Datamuseum-DK/R1000.HwDoc/BackgroundImages/FIU/0029/projected_75_light.png

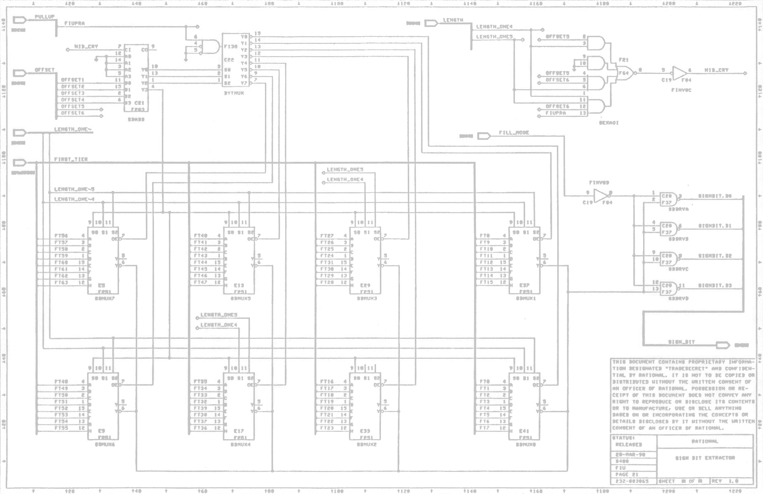
BackgroundImages/FIU/0029/projected_75_light.png
