Datamuseum-DK/R1000.HwDoc/BackgroundImages/FIU/0073/projected_75_light.png

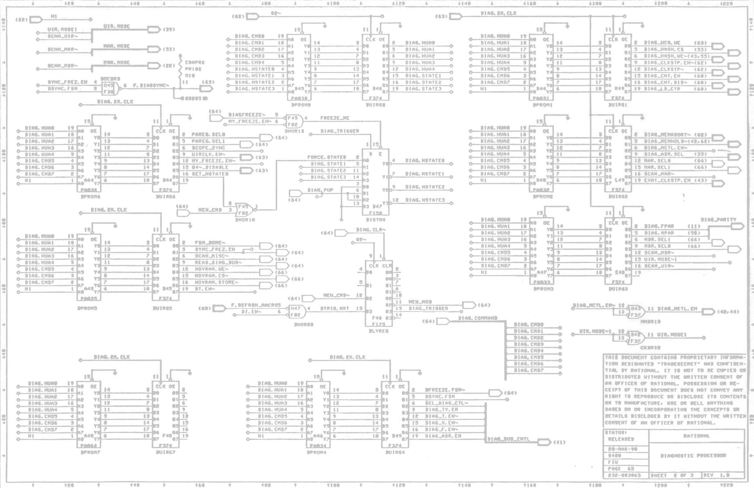
BackgroundImages/FIU/0073/projected_75_light.png
