Datamuseum-DK/R1000.HwDoc/BackgroundImages/IOC/0033/projected_75_light.png

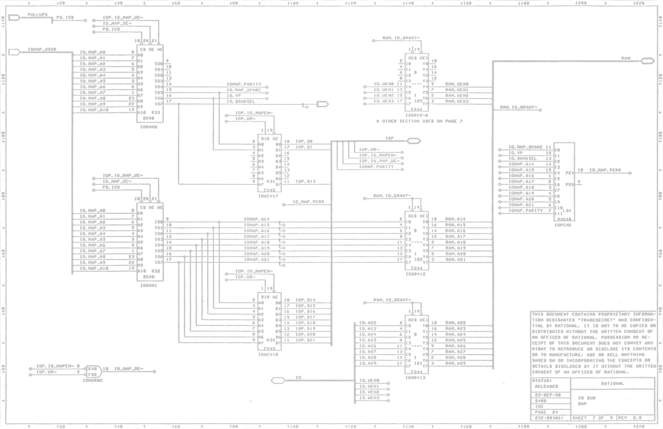
BackgroundImages/IOC/0033/projected_75_light.png
