Datamuseum-DK/R1000.HwDoc/BackgroundImages/IOC/0056/projected_75_light.png

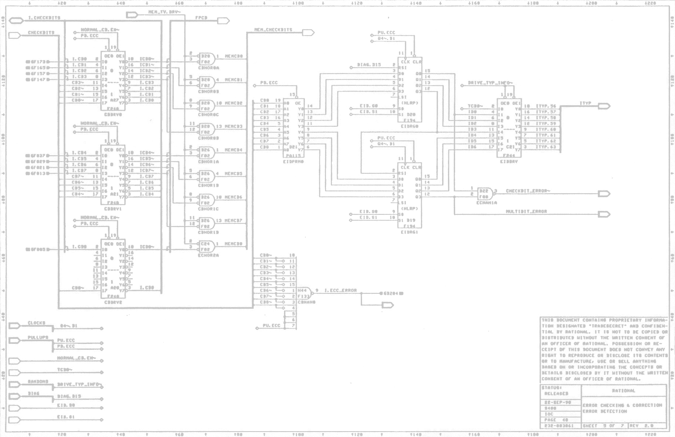
BackgroundImages/IOC/0056/projected_75_light.png
