Datamuseum-DK/R1000.HwDoc/BackgroundImages/MEM32/0014/projected_75_light.png

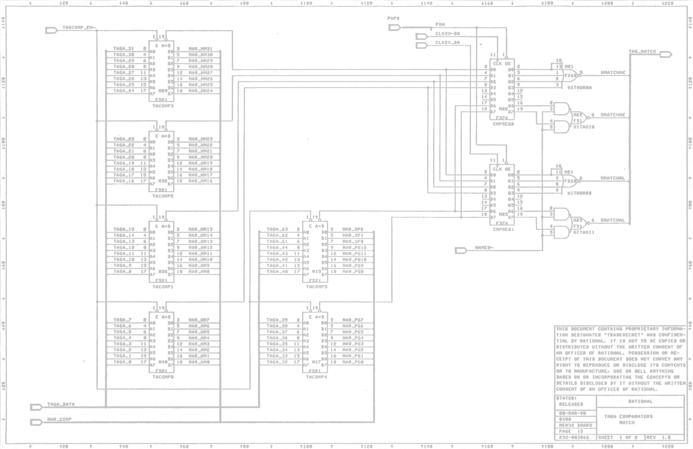
BackgroundImages/MEM32/0014/projected_75_light.png
