Datamuseum-DK/R1000.HwDoc/BackgroundImages/RESHA/0002/projected_75_light.png

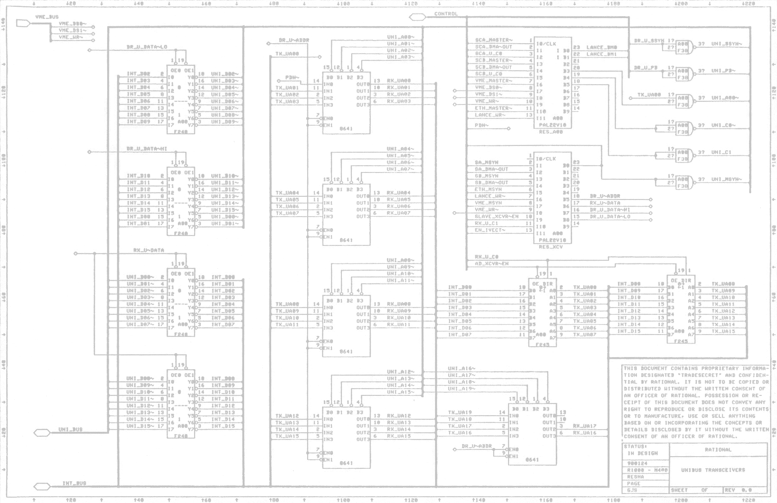
BackgroundImages/RESHA/0002/projected_75_light.png
