Datamuseum-DK/R1000.HwDoc/BackgroundImages/RESHA/0003/projected_75_light.png

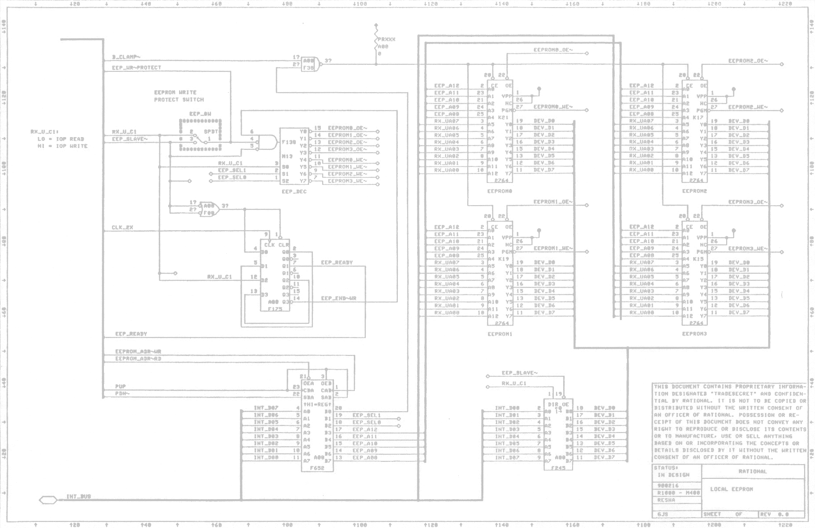
BackgroundImages/RESHA/0003/projected_75_light.png
