Datamuseum-DK/R1000.HwDoc/BackgroundImages/SEQ/0014/projected_75_light.png

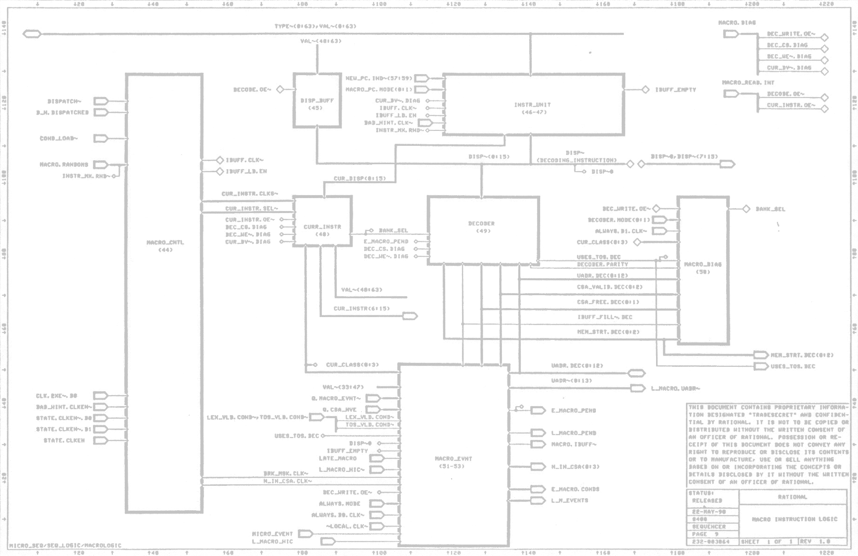
BackgroundImages/SEQ/0014/projected_75_light.png
