Datamuseum-DK/R1000.HwDoc/BackgroundImages/TYP/0014/projected_75_light.png

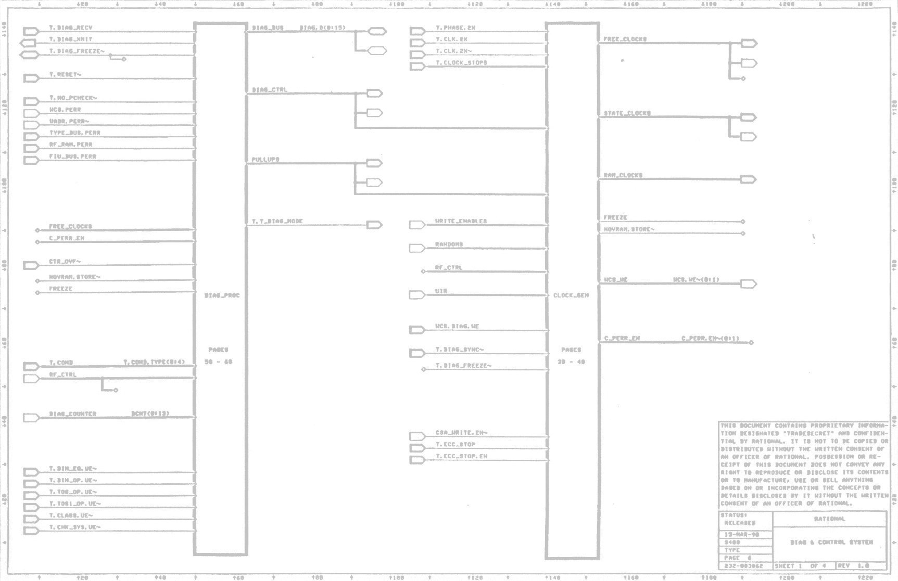
BackgroundImages/TYP/0014/projected_75_light.png
