Datamuseum-DK/R1000.HwDoc/BackgroundImages/TYP/0031/projected_75_light.png

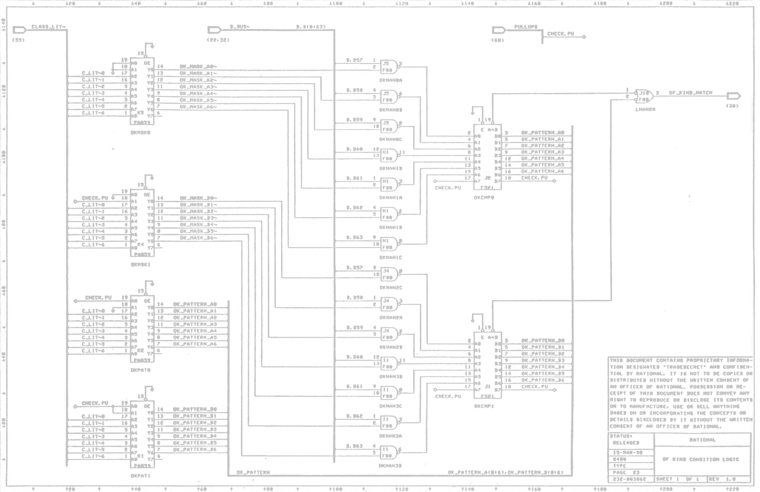
BackgroundImages/TYP/0031/projected_75_light.png
