Datamuseum-DK/R1000.HwDoc/BackgroundImages/VAL/0010/projected_75_light.png

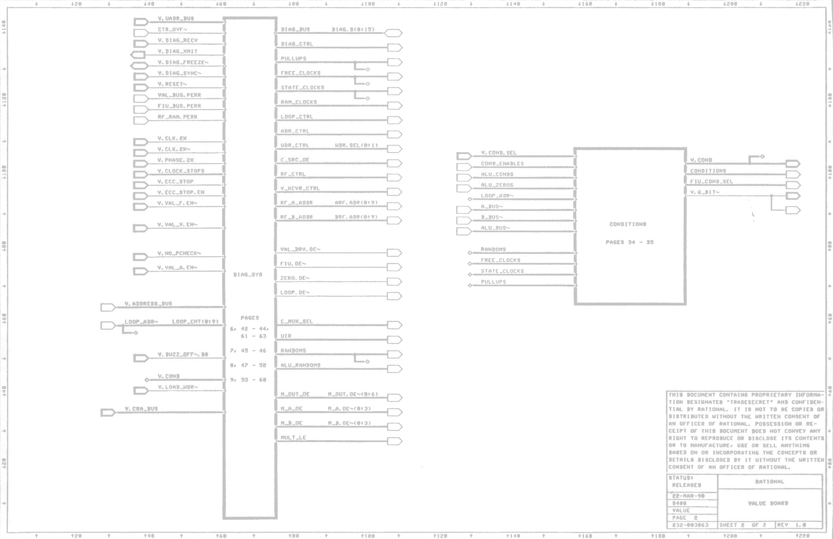
BackgroundImages/VAL/0010/projected_75_light.png
