Datamuseum-DK/R1000.HwDoc/Schematics/EMU/EMU.kicad_sch

## KiCad design Schematics/EMU/EMU.kicad_sch (2022-07-08)

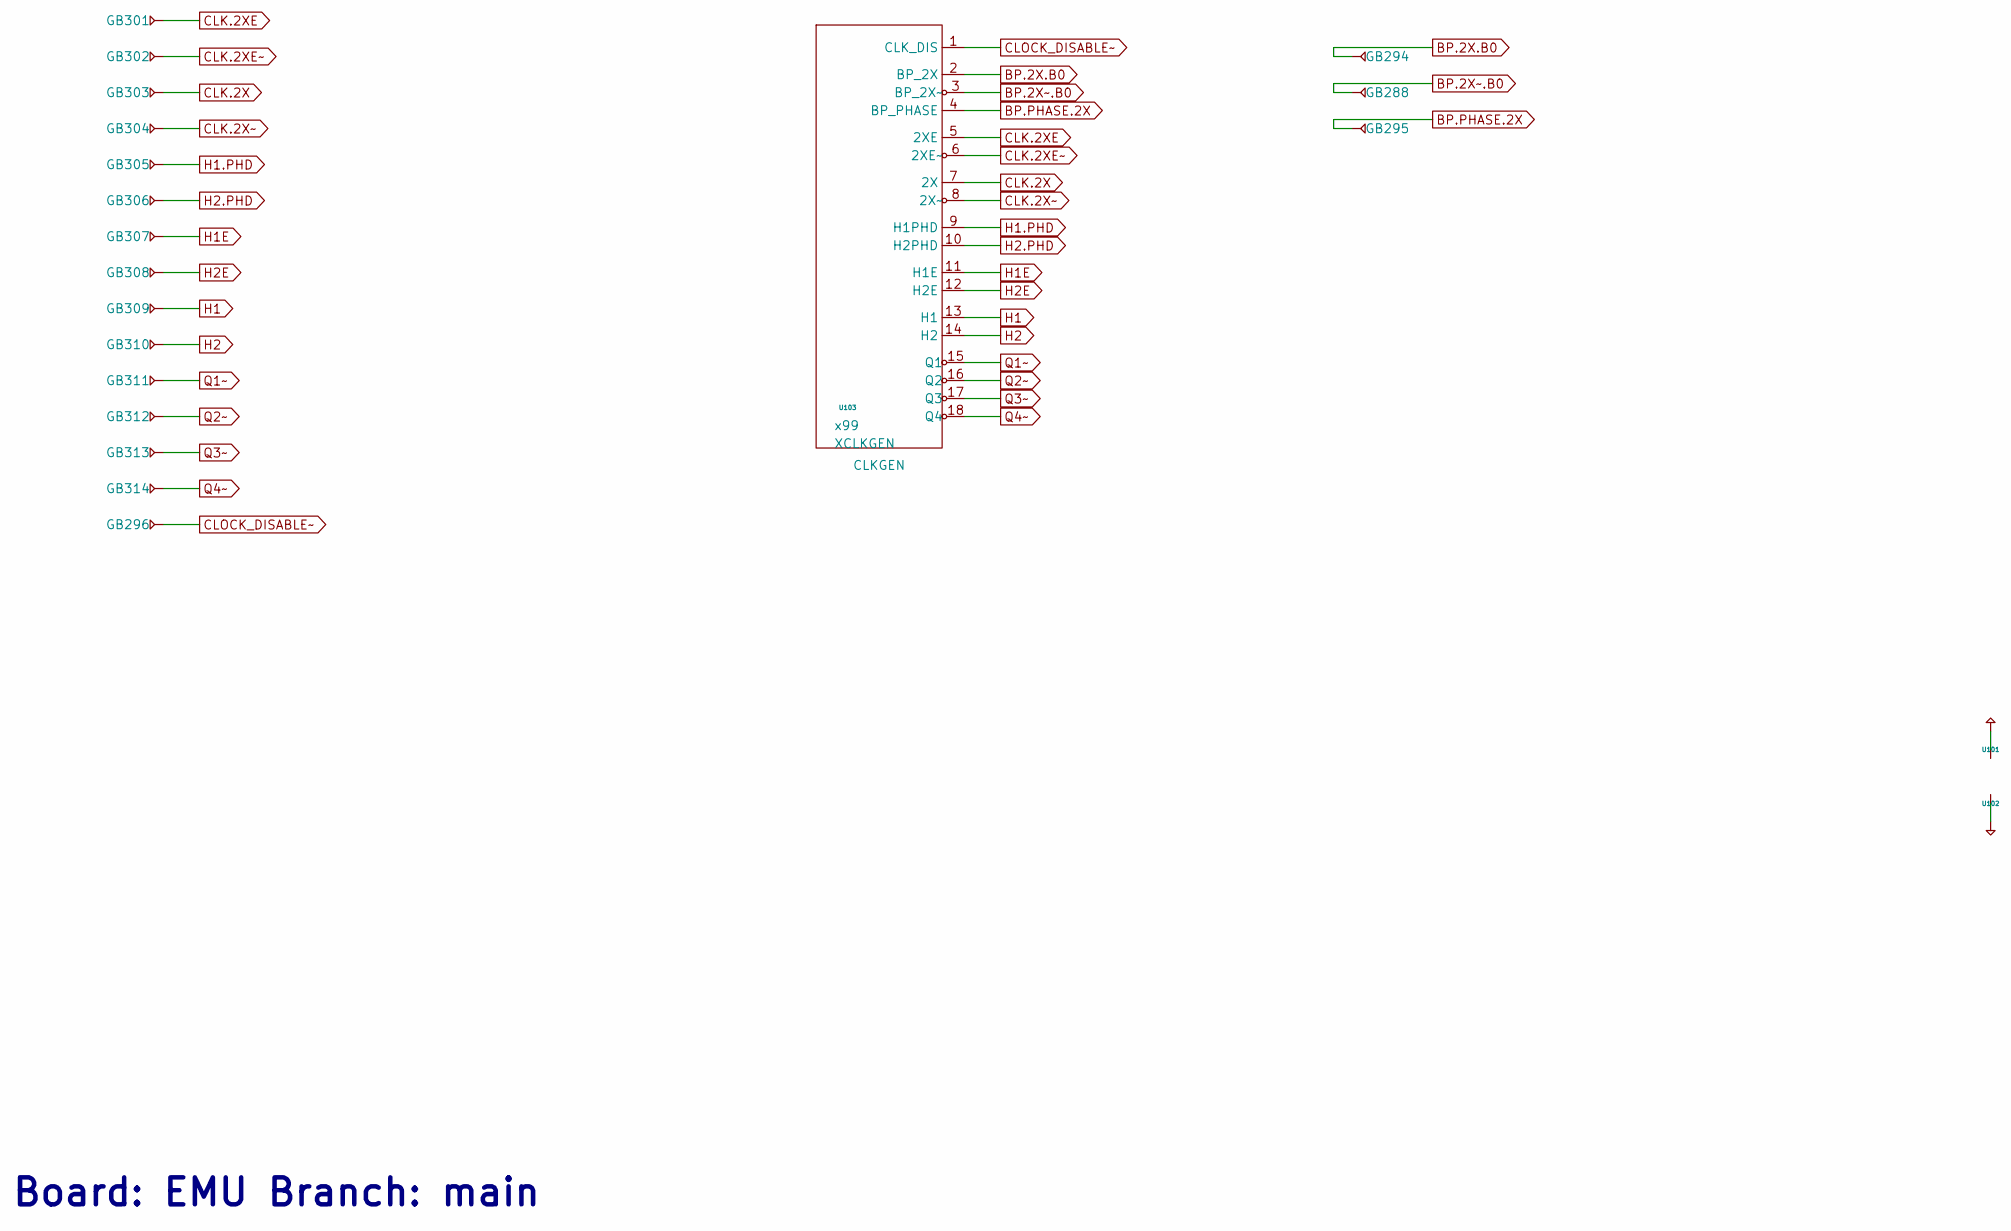
[picture p290: schematic EMU.kicad_sch]

Parts:
GB288, GB294, GB295, GB296, GB301, GB302, GB303, GB304, GB305, GB306, GB307, GB308, GB309, GB310, GB311, GB312, GB313, GB314: GB
U101, U102: (no value)
U103: XCLKGEN

Connections:
BP.2X.B0: GB294.1, U103.2 (BP_2X)
BP.2X~.B0: GB288.1, U103.3 (BP_2X~)
BP.PHASE.2X: GB295.1, U103.4 (BP_PHASE)
CLK.2X: GB303.1, U103.7 (2X)
CLK.2XE: GB301.1, U103.5 (2XE)
CLK.2XE~: GB302.1, U103.6 (2XE~)
CLK.2X~: GB304.1, U103.8 (2X~)
CLOCK_DISABLE~: GB296.1, U103.1 (CLK_DIS)
H1: GB309.1, U103.13 (H1)
H1.PHD: GB305.1, U103.9 (H1PHD)
H1E: GB307.1, U103.11 (H1E)
H2: GB310.1, U103.14 (H2)
H2.PHD: GB306.1, U103.10 (H2PHD)
H2E: GB308.1, U103.12 (H2E)
Q1~: GB311.1, U103.15 (Q1)
Q2~: GB312.1, U103.16 (Q2)
Q3~: GB313.1, U103.17 (Q3)
Q4~: GB314.1, U103.18 (Q4)
~: U101.1, U102.1

Notes on the sheet:
Board: EMU Branch: main
