Datamuseum-DK/R1000.HwDoc/Schematics/FIU/FIU.kicad_sch

## KiCad design Schematics/FIU/FIU.kicad_sch (2023-01-10)

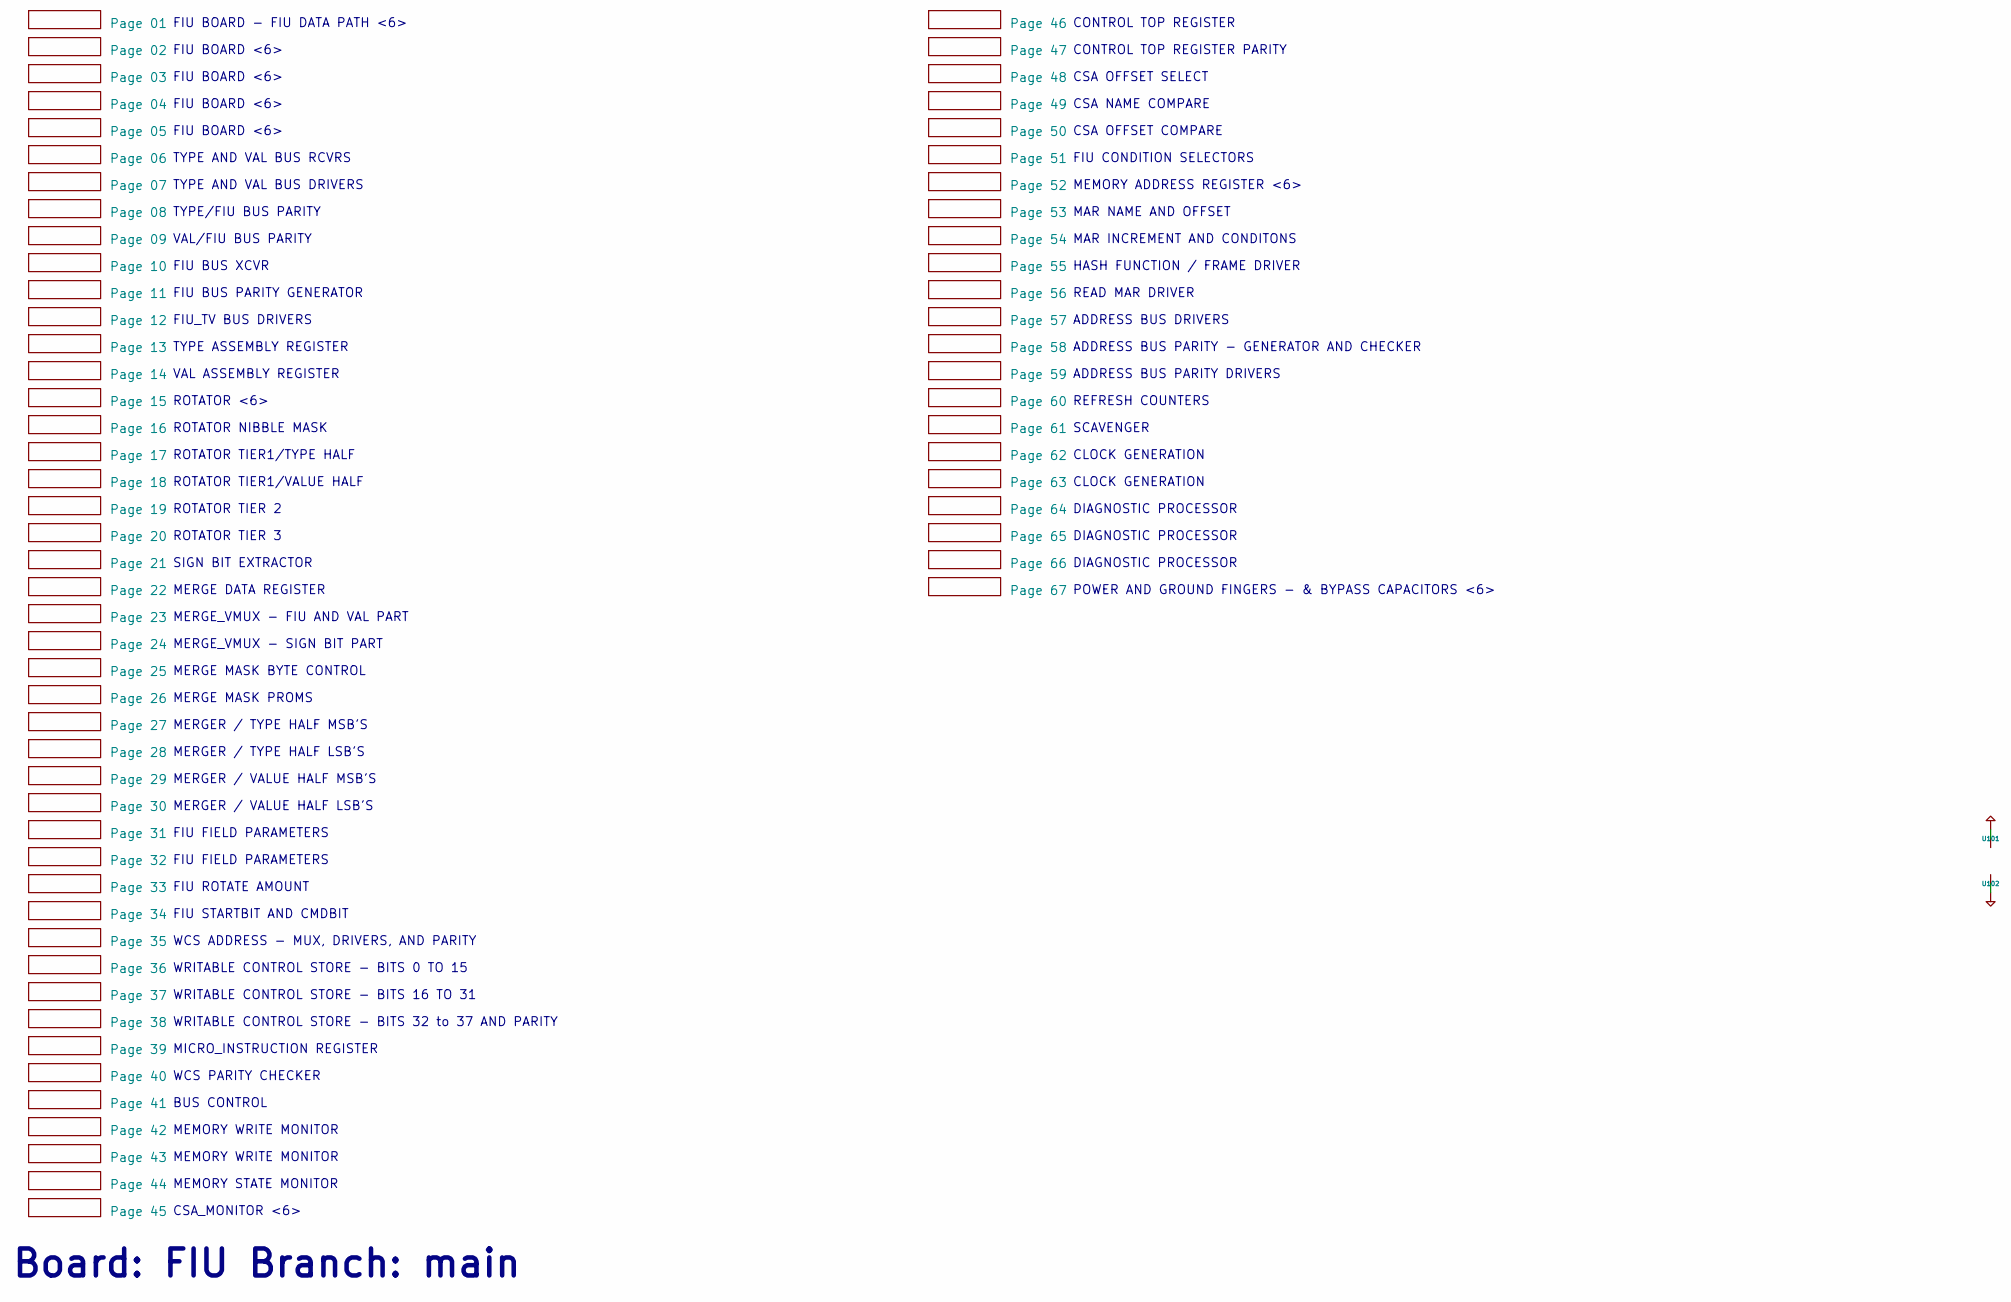
[picture p291: schematic FIU.kicad_sch]

Parts:
U101, U102: (no value)

Connections:
~: U101.1, U102.1

Notes on the sheet:
DIAGNOSTIC PROCESSOR
Board: FIU Branch: main
FIU ROTATE AMOUNT
FIU BOARD <6>
MERGE_VMUX - FIU AND VAL PART
ROTATOR <6>
WRITABLE CONTROL STORE - BITS 32 to 37 AND PARITY
MERGE_VMUX - SIGN BIT PART
MERGER / TYPE HALF LSB'S
MERGER / VALUE HALF LSB'S
REFRESH COUNTERS
FIU BUS PARITY GENERATOR
TYPE AND VAL BUS DRIVERS
WRITABLE CONTROL STORE - BITS 0 TO 15
CSA NAME COMPARE
ROTATOR TIER 2
FIU FIELD PARAMETERS
ROTATOR TIER 3
CSA OFFSET COMPARE
MEMORY WRITE MONITOR
POWER AND GROUND FINGERS - & BYPASS CAPACITORS <6>
HASH FUNCTION / FRAME DRIVER
READ MAR DRIVER
SIGN BIT EXTRACTOR
ADDRESS BUS DRIVERS
CSA OFFSET SELECT
MICRO_INSTRUCTION REGISTER
FIU BOARD - FIU DATA PATH <6>
MERGE MASK BYTE CONTROL
MAR INCREMENT AND CONDITONS
WCS ADDRESS - MUX, DRIVERS, AND PARITY
MERGE MASK PROMS
TYPE/FIU BUS PARITY
FIU BUS XCVR
CLOCK GENERATION
CSA_MONITOR <6>
TYPE ASSEMBLY REGISTER
ROTATOR TIER1/VALUE HALF
WCS PARITY CHECKER
ROTATOR NIBBLE MASK
MERGER / VALUE HALF MSB'S
TYPE AND VAL BUS RCVRS
MEMORY STATE MONITOR
FIU_TV BUS DRIVERS
MERGER / TYPE HALF MSB'S
CONTROL TOP REGISTER
ROTATOR TIER1/TYPE HALF
MAR NAME AND OFFSET
VAL/FIU BUS PARITY
WRITABLE CONTROL STORE - BITS 16 TO 31
MERGE DATA REGISTER
ADDRESS BUS PARITY DRIVERS
CONTROL TOP REGISTER PARITY
VAL ASSEMBLY REGISTER
SCAVENGER
ADDRESS BUS PARITY - GENERATOR AND CHECKER
FIU CONDITION SELECTORS
BUS CONTROL
MEMORY ADDRESS REGISTER <6>
FIU STARTBIT AND CMDBIT
