Datamuseum-DK/R1000.HwDoc/Schematics/FIU/pg_06.kicad_sch

## KiCad design Schematics/FIU/pg_06.kicad_sch (2023-01-10)

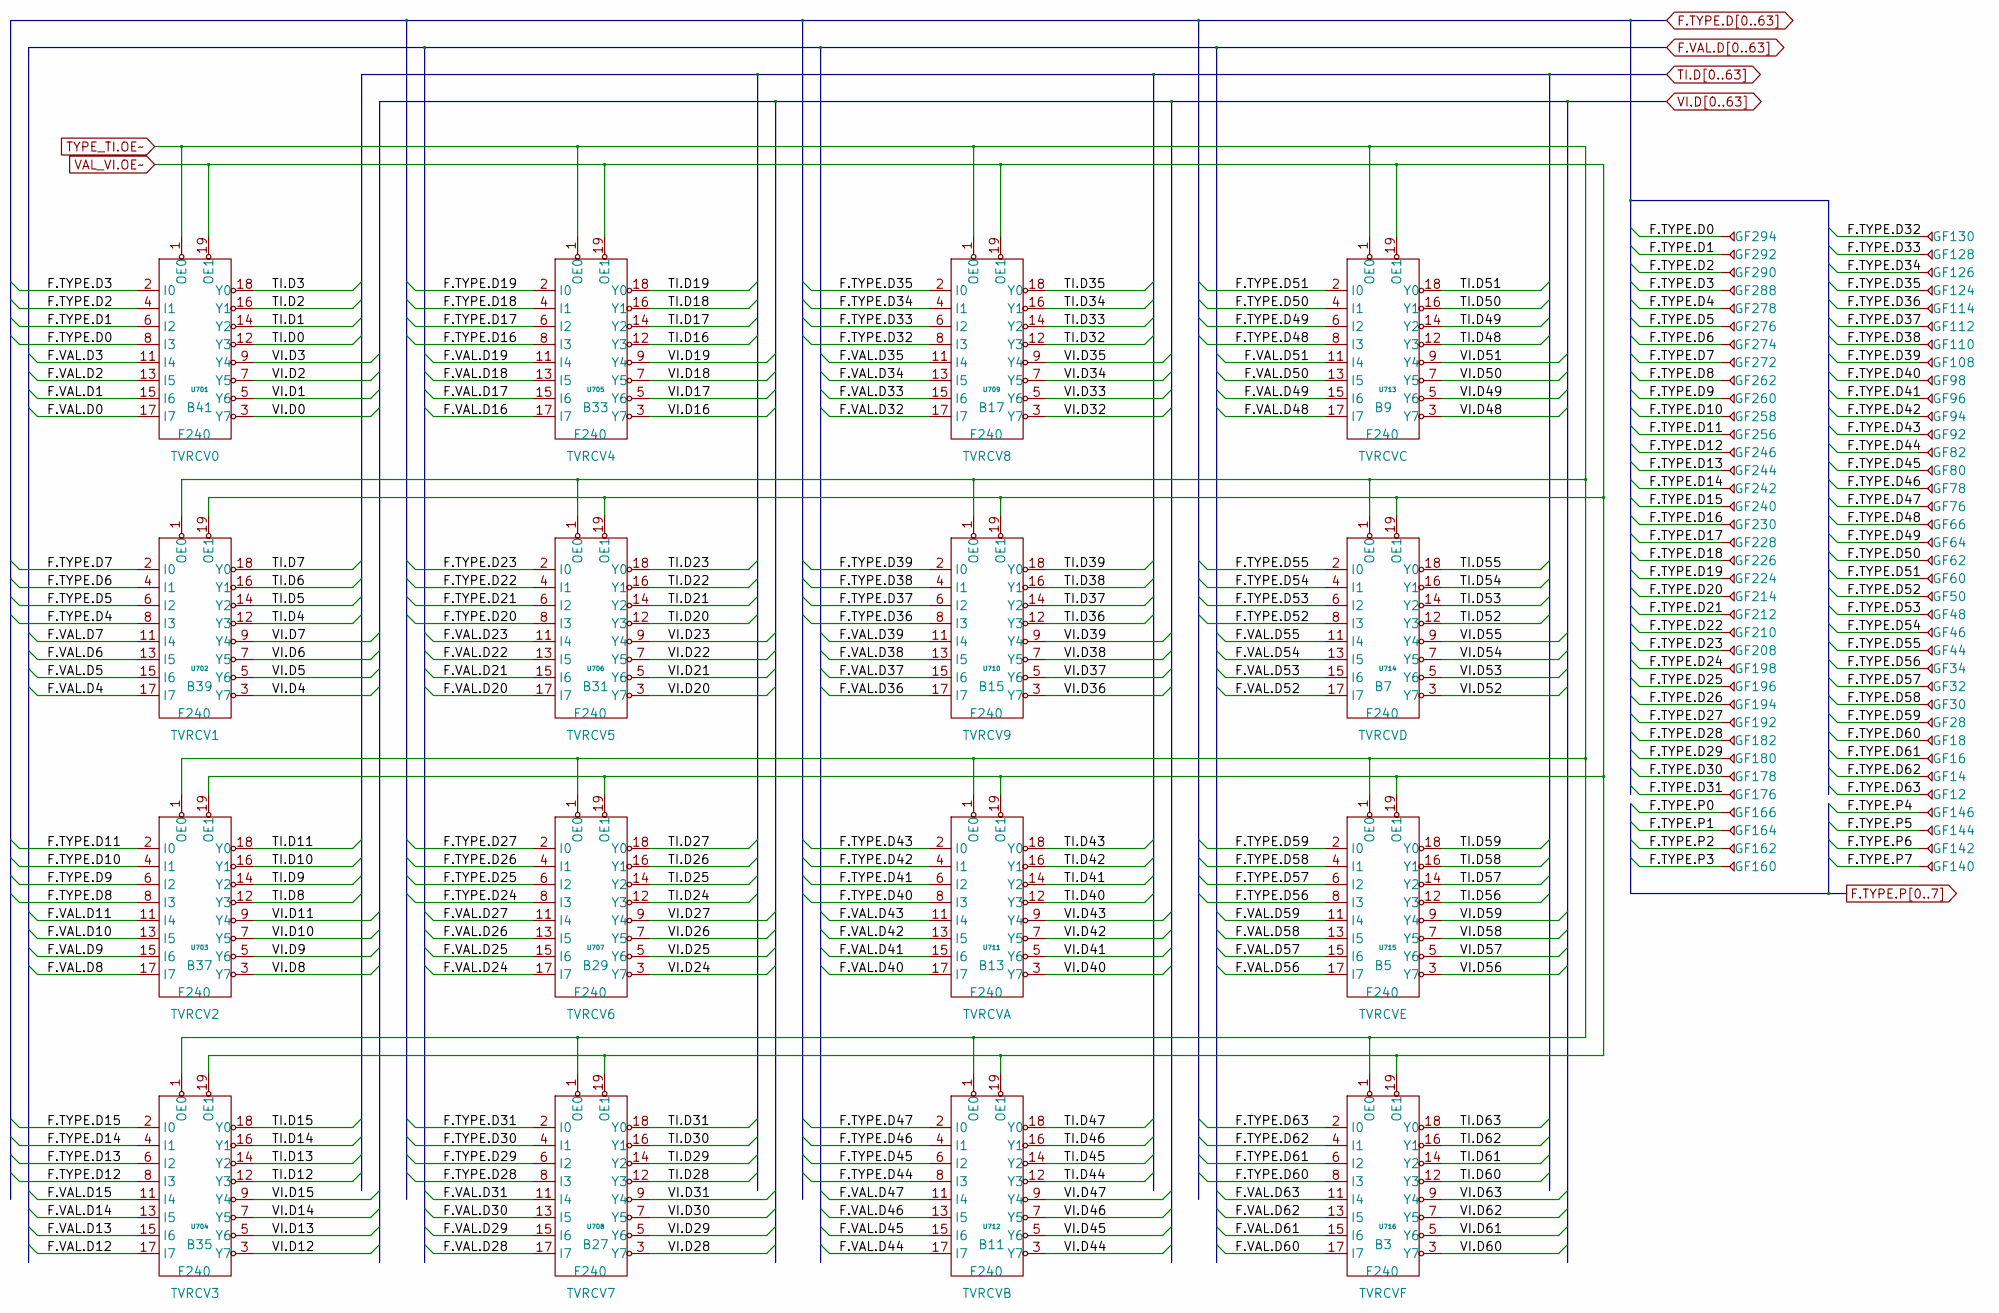
[picture p292: schematic pg_06.kicad_sch]

Parts:
GF12, GF14, GF16, GF18, GF28, GF30, GF32, GF34, GF44, GF46, GF48, GF50, GF60, GF62, GF64, GF66, GF76, GF78, GF80, GF82, GF92, GF94, GF96, GF98, GF108, GF110, GF112, GF114, GF124, GF126, GF128, GF130, GF140, GF142, GF144, GF146, GF160, GF162, GF164, GF166, GF176, GF178, GF180, GF182, GF192, GF194, GF196, GF198, GF208, GF210, GF212, GF214, GF224, GF226, GF228, GF230, GF240, GF242, GF244, GF246, GF256, GF258, GF260, GF262, GF272, GF274, GF276, GF278, GF288, GF290, GF292, GF294: GF
U701, U702, U703, U704, U705, U706, U707, U708, U709, U710, U711, U712, U713, U714, U715, U716: F240

Connections:
F.TYPE.D0: GF294.1, U701.8 (I3)
F.TYPE.D1: GF292.1, U701.6 (I2)
F.TYPE.D2: GF290.1, U701.4 (I1)
F.TYPE.D3: GF288.1, U701.2 (I0)
F.TYPE.D4: GF278.1, U702.8 (I3)
F.TYPE.D5: GF276.1, U702.6 (I2)
F.TYPE.D6: GF274.1, U702.4 (I1)
F.TYPE.D7: GF272.1, U702.2 (I0)
F.TYPE.D8: GF262.1, U703.8 (I3)
F.TYPE.D9: GF260.1, U703.6 (I2)
F.TYPE.D10: GF258.1, U703.4 (I1)
F.TYPE.D11: GF256.1, U703.2 (I0)
F.TYPE.D12: GF246.1, U704.8 (I3)
F.TYPE.D13: GF244.1, U704.6 (I2)
F.TYPE.D14: GF242.1, U704.4 (I1)
F.TYPE.D15: GF240.1, U704.2 (I0)
F.TYPE.D16: GF230.1, U705.8 (I3)
F.TYPE.D17: GF228.1, U705.6 (I2)
F.TYPE.D18: GF226.1, U705.4 (I1)
F.TYPE.D19: GF224.1, U705.2 (I0)
F.TYPE.D20: GF214.1, U706.8 (I3)
F.TYPE.D21: GF212.1, U706.6 (I2)
F.TYPE.D22: GF210.1, U706.4 (I1)
F.TYPE.D23: GF208.1, U706.2 (I0)
F.TYPE.D24: GF198.1, U707.8 (I3)
F.TYPE.D25: GF196.1, U707.6 (I2)
F.TYPE.D26: GF194.1, U707.4 (I1)
F.TYPE.D27: GF192.1, U707.2 (I0)
F.TYPE.D28: GF182.1, U708.8 (I3)
F.TYPE.D29: GF180.1, U708.6 (I2)
F.TYPE.D30: GF178.1, U708.4 (I1)
F.TYPE.D31: GF176.1, U708.2 (I0)
F.TYPE.D32: GF130.1, U709.8 (I3)
F.TYPE.D33: GF128.1, U709.6 (I2)
F.TYPE.D34: GF126.1, U709.4 (I1)
F.TYPE.D35: GF124.1, U709.2 (I0)
F.TYPE.D36: GF114.1, U710.8 (I3)
F.TYPE.D37: GF112.1, U710.6 (I2)
F.TYPE.D38: GF110.1, U710.4 (I1)
F.TYPE.D39: GF108.1, U710.2 (I0)
F.TYPE.D40: GF98.1, U711.8 (I3)
F.TYPE.D41: GF96.1, U711.6 (I2)
F.TYPE.D42: GF94.1, U711.4 (I1)
F.TYPE.D43: GF92.1, U711.2 (I0)
F.TYPE.D44: GF82.1, U712.8 (I3)
F.TYPE.D45: GF80.1, U712.6 (I2)
F.TYPE.D46: GF78.1, U712.4 (I1)
F.TYPE.D47: GF76.1, U712.2 (I0)
F.TYPE.D48: GF66.1, U713.8 (I3)
F.TYPE.D49: GF64.1, U713.6 (I2)
F.TYPE.D50: GF62.1, U713.4 (I1)
F.TYPE.D51: GF60.1, U713.2 (I0)
F.TYPE.D52: GF50.1, U714.8 (I3)
F.TYPE.D53: GF48.1, U714.6 (I2)
F.TYPE.D54: GF46.1, U714.4 (I1)
F.TYPE.D55: GF44.1, U714.2 (I0)
F.TYPE.D56: GF34.1, U715.8 (I3)
F.TYPE.D57: GF32.1, U715.6 (I2)
F.TYPE.D58: GF30.1, U715.4 (I1)
F.TYPE.D59: GF28.1, U715.2 (I0)
F.TYPE.D60: GF18.1, U716.8 (I3)
F.TYPE.D61: GF16.1, U716.6 (I2)
F.TYPE.D62: GF14.1, U716.4 (I1)
F.TYPE.D63: GF12.1, U716.2 (I0)
F.TYPE.P0: GF166.1
F.TYPE.P1: GF164.1
F.TYPE.P2: GF162.1
F.TYPE.P3: GF160.1
F.TYPE.P4: GF146.1
F.TYPE.P5: GF144.1
F.TYPE.P6: GF142.1
F.TYPE.P7: GF140.1
F.VAL.D0: U701.17 (I7)
F.VAL.D1: U701.15 (I6)
F.VAL.D2: U701.13 (I5)
F.VAL.D3: U701.11 (I4)
F.VAL.D4: U702.17 (I7)
F.VAL.D5: U702.15 (I6)
F.VAL.D6: U702.13 (I5)
F.VAL.D7: U702.11 (I4)
F.VAL.D8: U703.17 (I7)
F.VAL.D9: U703.15 (I6)
F.VAL.D10: U703.13 (I5)
F.VAL.D11: U703.11 (I4)
F.VAL.D12: U704.17 (I7)
F.VAL.D13: U704.15 (I6)
F.VAL.D14: U704.13 (I5)
F.VAL.D15: U704.11 (I4)
F.VAL.D16: U705.17 (I7)
F.VAL.D17: U705.15 (I6)
F.VAL.D18: U705.13 (I5)
F.VAL.D19: U705.11 (I4)
F.VAL.D20: U706.17 (I7)
F.VAL.D21: U706.15 (I6)
F.VAL.D22: U706.13 (I5)
F.VAL.D23: U706.11 (I4)
F.VAL.D24: U707.17 (I7)
F.VAL.D25: U707.15 (I6)
F.VAL.D26: U707.13 (I5)
F.VAL.D27: U707.11 (I4)
F.VAL.D28: U708.17 (I7)
F.VAL.D29: U708.15 (I6)
F.VAL.D30: U708.13 (I5)
F.VAL.D31: U708.11 (I4)
F.VAL.D32: U709.17 (I7)
F.VAL.D33: U709.15 (I6)
F.VAL.D34: U709.13 (I5)
F.VAL.D35: U709.11 (I4)
F.VAL.D36: U710.17 (I7)
F.VAL.D37: U710.15 (I6)
F.VAL.D38: U710.13 (I5)
F.VAL.D39: U710.11 (I4)
F.VAL.D40: U711.17 (I7)
F.VAL.D41: U711.15 (I6)
F.VAL.D42: U711.13 (I5)
F.VAL.D43: U711.11 (I4)
F.VAL.D44: U712.17 (I7)
F.VAL.D45: U712.15 (I6)
F.VAL.D46: U712.13 (I5)
F.VAL.D47: U712.11 (I4)
F.VAL.D48: U713.17 (I7)
F.VAL.D49: U713.15 (I6)
F.VAL.D50: U713.13 (I5)
F.VAL.D51: U713.11 (I4)
F.VAL.D52: U714.17 (I7)
F.VAL.D53: U714.15 (I6)
F.VAL.D54: U714.13 (I5)
F.VAL.D55: U714.11 (I4)
F.VAL.D56: U715.17 (I7)
F.VAL.D57: U715.15 (I6)
F.VAL.D58: U715.13 (I5)
F.VAL.D59: U715.11 (I4)
F.VAL.D60: U716.17 (I7)
F.VAL.D61: U716.15 (I6)
F.VAL.D62: U716.13 (I5)
F.VAL.D63: U716.11 (I4)
TI.D0: U701.12 (Y3)
TI.D1: U701.14 (Y2)
TI.D2: U701.16 (Y1)
TI.D3: U701.18 (Y0)
TI.D4: U702.12 (Y3)
TI.D5: U702.14 (Y2)
TI.D6: U702.16 (Y1)
TI.D7: U702.18 (Y0)
TI.D8: U703.12 (Y3)
TI.D9: U703.14 (Y2)
TI.D10: U703.16 (Y1)
TI.D11: U703.18 (Y0)
TI.D12: U704.12 (Y3)
TI.D13: U704.14 (Y2)
TI.D14: U704.16 (Y1)
TI.D15: U704.18 (Y0)
TI.D16: U705.12 (Y3)
TI.D17: U705.14 (Y2)
TI.D18: U705.16 (Y1)
TI.D19: U705.18 (Y0)
TI.D20: U706.12 (Y3)
TI.D21: U706.14 (Y2)
TI.D22: U706.16 (Y1)
TI.D23: U706.18 (Y0)
TI.D24: U707.12 (Y3)
TI.D25: U707.14 (Y2)
TI.D26: U707.16 (Y1)
TI.D27: U707.18 (Y0)
TI.D28: U708.12 (Y3)
TI.D29: U708.14 (Y2)
TI.D30: U708.16 (Y1)
TI.D31: U708.18 (Y0)
TI.D32: U709.12 (Y3)
TI.D33: U709.14 (Y2)
TI.D34: U709.16 (Y1)
TI.D35: U709.18 (Y0)
TI.D36: U710.12 (Y3)
TI.D37: U710.14 (Y2)
TI.D38: U710.16 (Y1)
TI.D39: U710.18 (Y0)
TI.D40: U711.12 (Y3)
TI.D41: U711.14 (Y2)
TI.D42: U711.16 (Y1)
TI.D43: U711.18 (Y0)
TI.D44: U712.12 (Y3)
TI.D45: U712.14 (Y2)
TI.D46: U712.16 (Y1)
TI.D47: U712.18 (Y0)
TI.D48: U713.12 (Y3)
TI.D49: U713.14 (Y2)
TI.D50: U713.16 (Y1)
TI.D51: U713.18 (Y0)
TI.D52: U714.12 (Y3)
TI.D53: U714.14 (Y2)
TI.D54: U714.16 (Y1)
TI.D55: U714.18 (Y0)
TI.D56: U715.12 (Y3)
TI.D57: U715.14 (Y2)
TI.D58: U715.16 (Y1)
TI.D59: U715.18 (Y0)
TI.D60: U716.12 (Y3)
TI.D61: U716.14 (Y2)
TI.D62: U716.16 (Y1)
TI.D63: U716.18 (Y0)
TYPE_TI.OE~: U701.1 (OE0), U702.1 (OE0), U703.1 (OE0), U704.1 (OE0), U705.1 (OE0), U706.1 (OE0), U707.1 (OE0), U708.1 (OE0), U709.1 (OE0), U710.1 (OE0), U711.1 (OE0), U712.1 (OE0), U713.1 (OE0), U714.1 (OE0), U715.1 (OE0), U716.1 (OE0)
VAL_VI.OE~: U701.19 (OE1), U702.19 (OE1), U703.19 (OE1), U704.19 (OE1), U705.19 (OE1), U706.19 (OE1), U707.19 (OE1), U708.19 (OE1), U709.19 (OE1), U710.19 (OE1), U711.19 (OE1), U712.19 (OE1), U713.19 (OE1), U714.19 (OE1), U715.19 (OE1), U716.19 (OE1)
VI.D0: U701.3 (Y7)
VI.D1: U701.5 (Y6)
VI.D2: U701.7 (Y5)
VI.D3: U701.9 (Y4)
VI.D4: U702.3 (Y7)
VI.D5: U702.5 (Y6)
VI.D6: U702.7 (Y5)
VI.D7: U702.9 (Y4)
VI.D8: U703.3 (Y7)
VI.D9: U703.5 (Y6)
VI.D10: U703.7 (Y5)
VI.D11: U703.9 (Y4)
VI.D12: U704.3 (Y7)
VI.D13: U704.5 (Y6)
VI.D14: U704.7 (Y5)
VI.D15: U704.9 (Y4)
VI.D16: U705.3 (Y7)
VI.D17: U705.5 (Y6)
VI.D18: U705.7 (Y5)
VI.D19: U705.9 (Y4)
VI.D20: U706.3 (Y7)
VI.D21: U706.5 (Y6)
VI.D22: U706.7 (Y5)
VI.D23: U706.9 (Y4)
VI.D24: U707.3 (Y7)
VI.D25: U707.5 (Y6)
VI.D26: U707.7 (Y5)
VI.D27: U707.9 (Y4)
VI.D28: U708.3 (Y7)
VI.D29: U708.5 (Y6)
VI.D30: U708.7 (Y5)
VI.D31: U708.9 (Y4)
VI.D32: U709.3 (Y7)
VI.D33: U709.5 (Y6)
VI.D34: U709.7 (Y5)
VI.D35: U709.9 (Y4)
VI.D36: U710.3 (Y7)
VI.D37: U710.5 (Y6)
VI.D38: U710.7 (Y5)
VI.D39: U710.9 (Y4)
VI.D40: U711.3 (Y7)
VI.D41: U711.5 (Y6)
VI.D42: U711.7 (Y5)
VI.D43: U711.9 (Y4)
VI.D44: U712.3 (Y7)
VI.D45: U712.5 (Y6)
VI.D46: U712.7 (Y5)
VI.D47: U712.9 (Y4)
VI.D48: U713.3 (Y7)
VI.D49: U713.5 (Y6)
VI.D50: U713.7 (Y5)
VI.D51: U713.9 (Y4)
VI.D52: U714.3 (Y7)
VI.D53: U714.5 (Y6)
VI.D54: U714.7 (Y5)
VI.D55: U714.9 (Y4)
VI.D56: U715.3 (Y7)
VI.D57: U715.5 (Y6)
VI.D58: U715.7 (Y5)
VI.D59: U715.9 (Y4)
VI.D60: U716.3 (Y7)
VI.D61: U716.5 (Y6)
VI.D62: U716.7 (Y5)
VI.D63: U716.9 (Y4)
