Datamuseum-DK/R1000.HwDoc/Schematics/FIU/pg_07.kicad_sch

## KiCad design Schematics/FIU/pg_07.kicad_sch (2023-01-10)

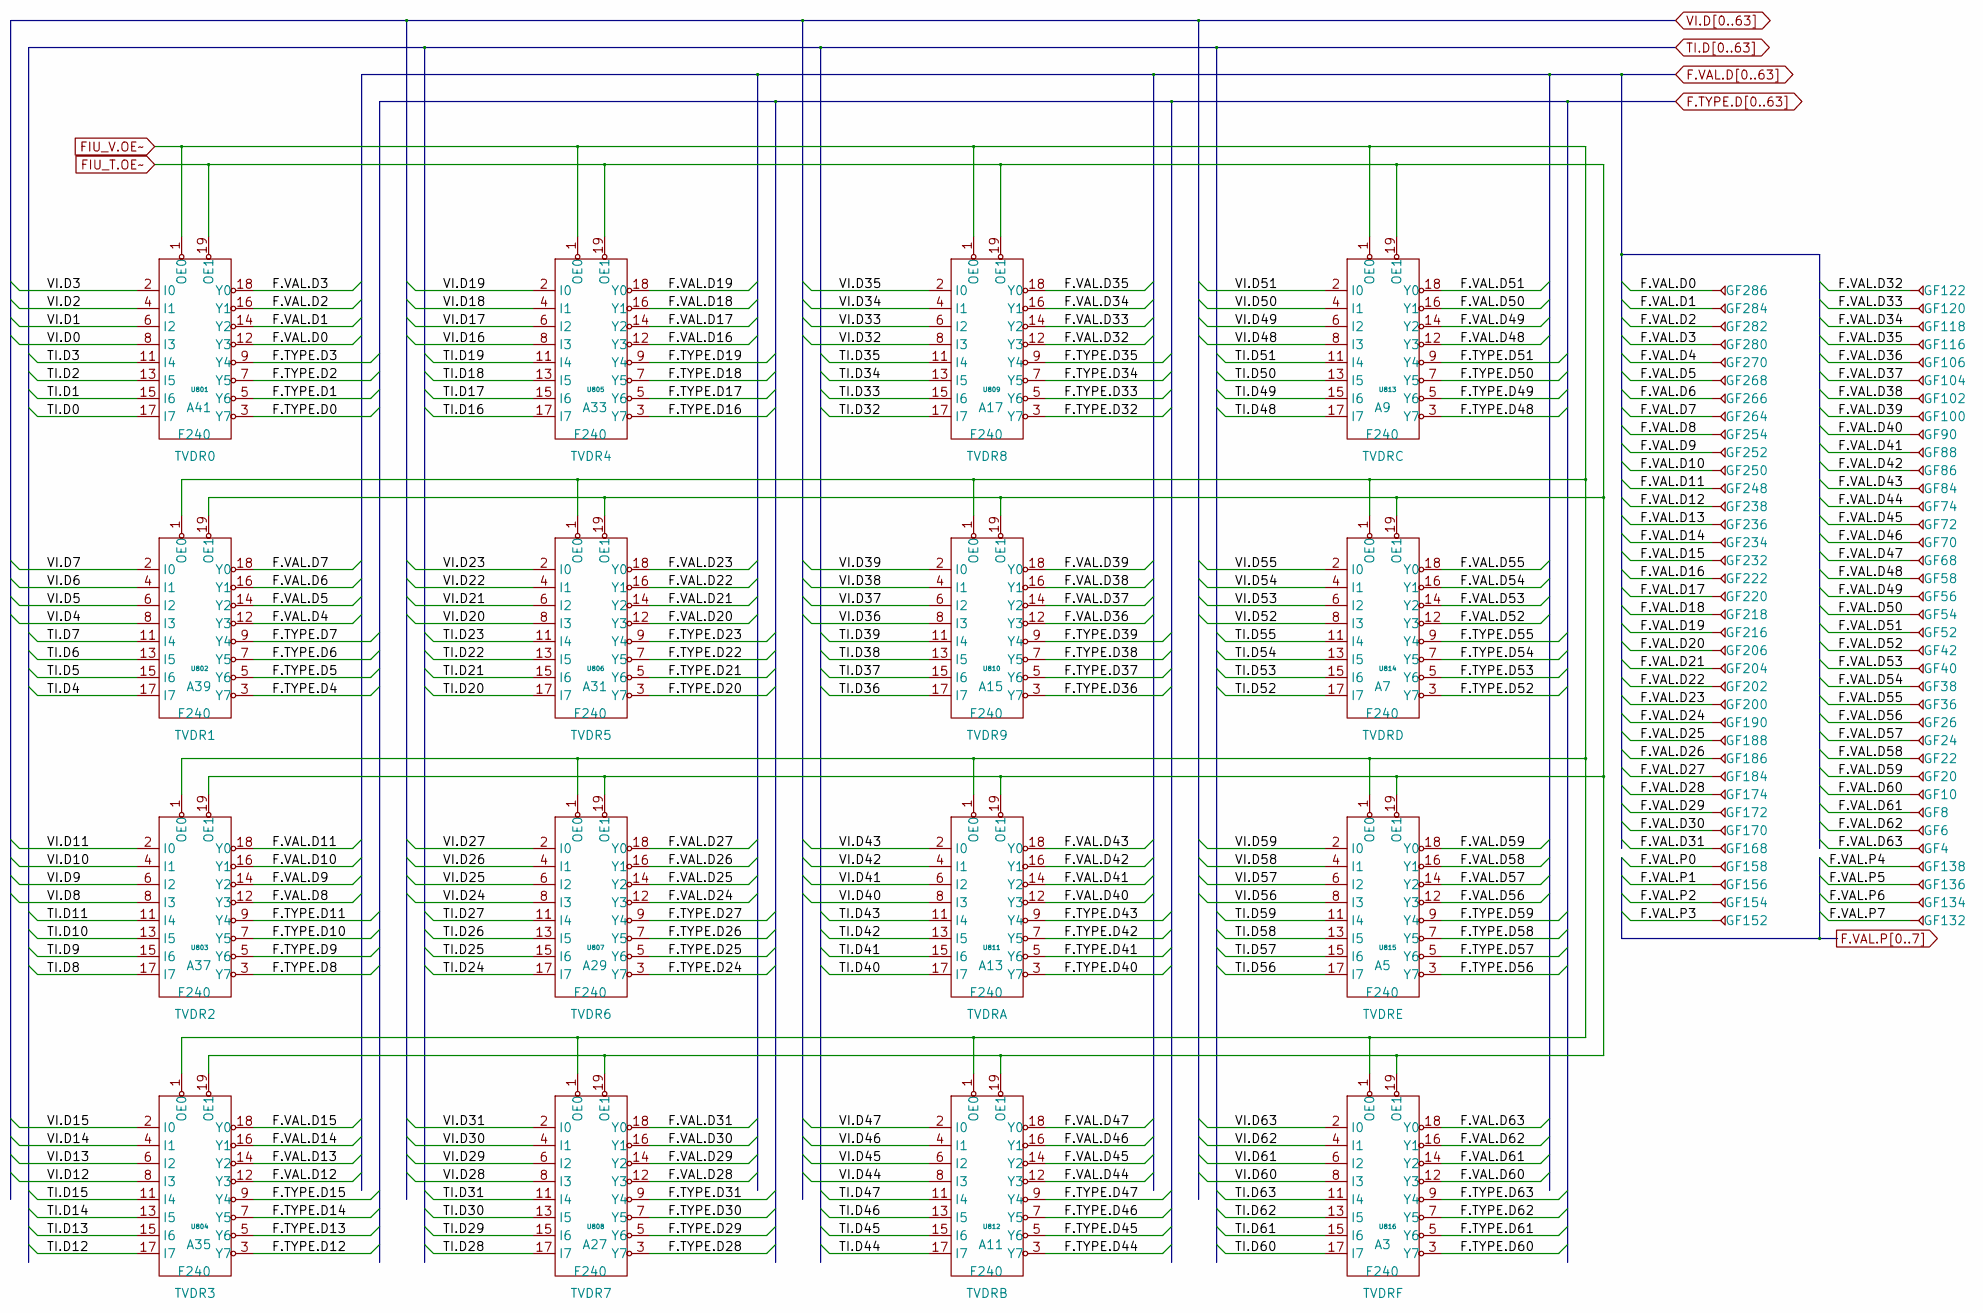
[picture p293: schematic pg_07.kicad_sch]

Parts:
GF4, GF6, GF8, GF10, GF20, GF22, GF24, GF26, GF36, GF38, GF40, GF42, GF52, GF54, GF56, GF58, GF68, GF70, GF72, GF74, GF84, GF86, GF88, GF90, GF100, GF102, GF104, GF106, GF116, GF118, GF120, GF122, GF132, GF134, GF136, GF138, GF152, GF154, GF156, GF158, GF168, GF170, GF172, GF174, GF184, GF186, GF188, GF190, GF200, GF202, GF204, GF206, GF216, GF218, GF220, GF222, GF232, GF234, GF236, GF238, GF248, GF250, GF252, GF254, GF264, GF266, GF268, GF270, GF280, GF282, GF284, GF286: GF
U801, U802, U803, U804, U805, U806, U807, U808, U809, U810, U811, U812, U813, U814, U815, U816: F240

Connections:
F.TYPE.D0: U801.3 (Y7)
F.TYPE.D1: U801.5 (Y6)
F.TYPE.D2: U801.7 (Y5)
F.TYPE.D3: U801.9 (Y4)
F.TYPE.D4: U802.3 (Y7)
F.TYPE.D5: U802.5 (Y6)
F.TYPE.D6: U802.7 (Y5)
F.TYPE.D7: U802.9 (Y4)
F.TYPE.D8: U803.3 (Y7)
F.TYPE.D9: U803.5 (Y6)
F.TYPE.D10: U803.7 (Y5)
F.TYPE.D11: U803.9 (Y4)
F.TYPE.D12: U804.3 (Y7)
F.TYPE.D13: U804.5 (Y6)
F.TYPE.D14: U804.7 (Y5)
F.TYPE.D15: U804.9 (Y4)
F.TYPE.D16: U805.3 (Y7)
F.TYPE.D17: U805.5 (Y6)
F.TYPE.D18: U805.7 (Y5)
F.TYPE.D19: U805.9 (Y4)
F.TYPE.D20: U806.3 (Y7)
F.TYPE.D21: U806.5 (Y6)
F.TYPE.D22: U806.7 (Y5)
F.TYPE.D23: U806.9 (Y4)
F.TYPE.D24: U807.3 (Y7)
F.TYPE.D25: U807.5 (Y6)
F.TYPE.D26: U807.7 (Y5)
F.TYPE.D27: U807.9 (Y4)
F.TYPE.D28: U808.3 (Y7)
F.TYPE.D29: U808.5 (Y6)
F.TYPE.D30: U808.7 (Y5)
F.TYPE.D31: U808.9 (Y4)
F.TYPE.D32: U809.3 (Y7)
F.TYPE.D33: U809.5 (Y6)
F.TYPE.D34: U809.7 (Y5)
F.TYPE.D35: U809.9 (Y4)
F.TYPE.D36: U810.3 (Y7)
F.TYPE.D37: U810.5 (Y6)
F.TYPE.D38: U810.7 (Y5)
F.TYPE.D39: U810.9 (Y4)
F.TYPE.D40: U811.3 (Y7)
F.TYPE.D41: U811.5 (Y6)
F.TYPE.D42: U811.7 (Y5)
F.TYPE.D43: U811.9 (Y4)
F.TYPE.D44: U812.3 (Y7)
F.TYPE.D45: U812.5 (Y6)
F.TYPE.D46: U812.7 (Y5)
F.TYPE.D47: U812.9 (Y4)
F.TYPE.D48: U813.3 (Y7)
F.TYPE.D49: U813.5 (Y6)
F.TYPE.D50: U813.7 (Y5)
F.TYPE.D51: U813.9 (Y4)
F.TYPE.D52: U814.3 (Y7)
F.TYPE.D53: U814.5 (Y6)
F.TYPE.D54: U814.7 (Y5)
F.TYPE.D55: U814.9 (Y4)
F.TYPE.D56: U815.3 (Y7)
F.TYPE.D57: U815.5 (Y6)
F.TYPE.D58: U815.7 (Y5)
F.TYPE.D59: U815.9 (Y4)
F.TYPE.D60: U816.3 (Y7)
F.TYPE.D61: U816.5 (Y6)
F.TYPE.D62: U816.7 (Y5)
F.TYPE.D63: U816.9 (Y4)
F.VAL.D0: GF286.1, U801.12 (Y3)
F.VAL.D1: GF284.1, U801.14 (Y2)
F.VAL.D2: GF282.1, U801.16 (Y1)
F.VAL.D3: GF280.1, U801.18 (Y0)
F.VAL.D4: GF270.1, U802.12 (Y3)
F.VAL.D5: GF268.1, U802.14 (Y2)
F.VAL.D6: GF266.1, U802.16 (Y1)
F.VAL.D7: GF264.1, U802.18 (Y0)
F.VAL.D8: GF254.1, U803.12 (Y3)
F.VAL.D9: GF252.1, U803.14 (Y2)
F.VAL.D10: GF250.1, U803.16 (Y1)
F.VAL.D11: GF248.1, U803.18 (Y0)
F.VAL.D12: GF238.1, U804.12 (Y3)
F.VAL.D13: GF236.1, U804.14 (Y2)
F.VAL.D14: GF234.1, U804.16 (Y1)
F.VAL.D15: GF232.1, U804.18 (Y0)
F.VAL.D16: GF222.1, U805.12 (Y3)
F.VAL.D17: GF220.1, U805.14 (Y2)
F.VAL.D18: GF218.1, U805.16 (Y1)
F.VAL.D19: GF216.1, U805.18 (Y0)
F.VAL.D20: GF206.1, U806.12 (Y3)
F.VAL.D21: GF204.1, U806.14 (Y2)
F.VAL.D22: GF202.1, U806.16 (Y1)
F.VAL.D23: GF200.1, U806.18 (Y0)
F.VAL.D24: GF190.1, U807.12 (Y3)
F.VAL.D25: GF188.1, U807.14 (Y2)
F.VAL.D26: GF186.1, U807.16 (Y1)
F.VAL.D27: GF184.1, U807.18 (Y0)
F.VAL.D28: GF174.1, U808.12 (Y3)
F.VAL.D29: GF172.1, U808.14 (Y2)
F.VAL.D30: GF170.1, U808.16 (Y1)
F.VAL.D31: GF168.1, U808.18 (Y0)
F.VAL.D32: GF122.1, U809.12 (Y3)
F.VAL.D33: GF120.1, U809.14 (Y2)
F.VAL.D34: GF118.1, U809.16 (Y1)
F.VAL.D35: GF116.1, U809.18 (Y0)
F.VAL.D36: GF106.1, U810.12 (Y3)
F.VAL.D37: GF104.1, U810.14 (Y2)
F.VAL.D38: GF102.1, U810.16 (Y1)
F.VAL.D39: GF100.1, U810.18 (Y0)
F.VAL.D40: GF90.1, U811.12 (Y3)
F.VAL.D41: GF88.1, U811.14 (Y2)
F.VAL.D42: GF86.1, U811.16 (Y1)
F.VAL.D43: GF84.1, U811.18 (Y0)
F.VAL.D44: GF74.1, U812.12 (Y3)
F.VAL.D45: GF72.1, U812.14 (Y2)
F.VAL.D46: GF70.1, U812.16 (Y1)
F.VAL.D47: GF68.1, U812.18 (Y0)
F.VAL.D48: GF58.1, U813.12 (Y3)
F.VAL.D49: GF56.1, U813.14 (Y2)
F.VAL.D50: GF54.1, U813.16 (Y1)
F.VAL.D51: GF52.1, U813.18 (Y0)
F.VAL.D52: GF42.1, U814.12 (Y3)
F.VAL.D53: GF40.1, U814.14 (Y2)
F.VAL.D54: GF38.1, U814.16 (Y1)
F.VAL.D55: GF36.1, U814.18 (Y0)
F.VAL.D56: GF26.1, U815.12 (Y3)
F.VAL.D57: GF24.1, U815.14 (Y2)
F.VAL.D58: GF22.1, U815.16 (Y1)
F.VAL.D59: GF20.1, U815.18 (Y0)
F.VAL.D60: GF10.1, U816.12 (Y3)
F.VAL.D61: GF8.1, U816.14 (Y2)
F.VAL.D62: GF6.1, U816.16 (Y1)
F.VAL.D63: GF4.1, U816.18 (Y0)
F.VAL.P0: GF158.1
F.VAL.P1: GF156.1
F.VAL.P2: GF154.1
F.VAL.P3: GF152.1
F.VAL.P4: GF138.1
F.VAL.P5: GF136.1
F.VAL.P6: GF134.1
F.VAL.P7: GF132.1
FIU_T.OE~: U801.19 (OE1), U802.19 (OE1), U803.19 (OE1), U804.19 (OE1), U805.19 (OE1), U806.19 (OE1), U807.19 (OE1), U808.19 (OE1), U809.19 (OE1), U810.19 (OE1), U811.19 (OE1), U812.19 (OE1), U813.19 (OE1), U814.19 (OE1), U815.19 (OE1), U816.19 (OE1)
FIU_V.OE~: U801.1 (OE0), U802.1 (OE0), U803.1 (OE0), U804.1 (OE0), U805.1 (OE0), U806.1 (OE0), U807.1 (OE0), U808.1 (OE0), U809.1 (OE0), U810.1 (OE0), U811.1 (OE0), U812.1 (OE0), U813.1 (OE0), U814.1 (OE0), U815.1 (OE0), U816.1 (OE0)
TI.D0: U801.17 (I7)
TI.D1: U801.15 (I6)
TI.D2: U801.13 (I5)
TI.D3: U801.11 (I4)
TI.D4: U802.17 (I7)
TI.D5: U802.15 (I6)
TI.D6: U802.13 (I5)
TI.D7: U802.11 (I4)
TI.D8: U803.17 (I7)
TI.D9: U803.15 (I6)
TI.D10: U803.13 (I5)
TI.D11: U803.11 (I4)
TI.D12: U804.17 (I7)
TI.D13: U804.15 (I6)
TI.D14: U804.13 (I5)
TI.D15: U804.11 (I4)
TI.D16: U805.17 (I7)
TI.D17: U805.15 (I6)
TI.D18: U805.13 (I5)
TI.D19: U805.11 (I4)
TI.D20: U806.17 (I7)
TI.D21: U806.15 (I6)
TI.D22: U806.13 (I5)
TI.D23: U806.11 (I4)
TI.D24: U807.17 (I7)
TI.D25: U807.15 (I6)
TI.D26: U807.13 (I5)
TI.D27: U807.11 (I4)
TI.D28: U808.17 (I7)
TI.D29: U808.15 (I6)
TI.D30: U808.13 (I5)
TI.D31: U808.11 (I4)
TI.D32: U809.17 (I7)
TI.D33: U809.15 (I6)
TI.D34: U809.13 (I5)
TI.D35: U809.11 (I4)
TI.D36: U810.17 (I7)
TI.D37: U810.15 (I6)
TI.D38: U810.13 (I5)
TI.D39: U810.11 (I4)
TI.D40: U811.17 (I7)
TI.D41: U811.15 (I6)
TI.D42: U811.13 (I5)
TI.D43: U811.11 (I4)
TI.D44: U812.17 (I7)
TI.D45: U812.15 (I6)
TI.D46: U812.13 (I5)
TI.D47: U812.11 (I4)
TI.D48: U813.17 (I7)
TI.D49: U813.15 (I6)
TI.D50: U813.13 (I5)
TI.D51: U813.11 (I4)
TI.D52: U814.17 (I7)
TI.D53: U814.15 (I6)
TI.D54: U814.13 (I5)
TI.D55: U814.11 (I4)
TI.D56: U815.17 (I7)
TI.D57: U815.15 (I6)
TI.D58: U815.13 (I5)
TI.D59: U815.11 (I4)
TI.D60: U816.17 (I7)
TI.D61: U816.15 (I6)
TI.D62: U816.13 (I5)
TI.D63: U816.11 (I4)
VI.D0: U801.8 (I3)
VI.D1: U801.6 (I2)
VI.D2: U801.4 (I1)
VI.D3: U801.2 (I0)
VI.D4: U802.8 (I3)
VI.D5: U802.6 (I2)
VI.D6: U802.4 (I1)
VI.D7: U802.2 (I0)
VI.D8: U803.8 (I3)
VI.D9: U803.6 (I2)
VI.D10: U803.4 (I1)
VI.D11: U803.2 (I0)
VI.D12: U804.8 (I3)
VI.D13: U804.6 (I2)
VI.D14: U804.4 (I1)
VI.D15: U804.2 (I0)
VI.D16: U805.8 (I3)
VI.D17: U805.6 (I2)
VI.D18: U805.4 (I1)
VI.D19: U805.2 (I0)
VI.D20: U806.8 (I3)
VI.D21: U806.6 (I2)
VI.D22: U806.4 (I1)
VI.D23: U806.2 (I0)
VI.D24: U807.8 (I3)
VI.D25: U807.6 (I2)
VI.D26: U807.4 (I1)
VI.D27: U807.2 (I0)
VI.D28: U808.8 (I3)
VI.D29: U808.6 (I2)
VI.D30: U808.4 (I1)
VI.D31: U808.2 (I0)
VI.D32: U809.8 (I3)
VI.D33: U809.6 (I2)
VI.D34: U809.4 (I1)
VI.D35: U809.2 (I0)
VI.D36: U810.8 (I3)
VI.D37: U810.6 (I2)
VI.D38: U810.4 (I1)
VI.D39: U810.2 (I0)
VI.D40: U811.8 (I3)
VI.D41: U811.6 (I2)
VI.D42: U811.4 (I1)
VI.D43: U811.2 (I0)
VI.D44: U812.8 (I3)
VI.D45: U812.6 (I2)
VI.D46: U812.4 (I1)
VI.D47: U812.2 (I0)
VI.D48: U813.8 (I3)
VI.D49: U813.6 (I2)
VI.D50: U813.4 (I1)
VI.D51: U813.2 (I0)
VI.D52: U814.8 (I3)
VI.D53: U814.6 (I2)
VI.D54: U814.4 (I1)
VI.D55: U814.2 (I0)
VI.D56: U815.8 (I3)
VI.D57: U815.6 (I2)
VI.D58: U815.4 (I1)
VI.D59: U815.2 (I0)
VI.D60: U816.8 (I3)
VI.D61: U816.6 (I2)
VI.D62: U816.4 (I1)
VI.D63: U816.2 (I0)
