Datamuseum-DK/R1000.HwDoc/Schematics/FIU/pg_08.kicad_sch

## KiCad design Schematics/FIU/pg_08.kicad_sch (2023-01-10)

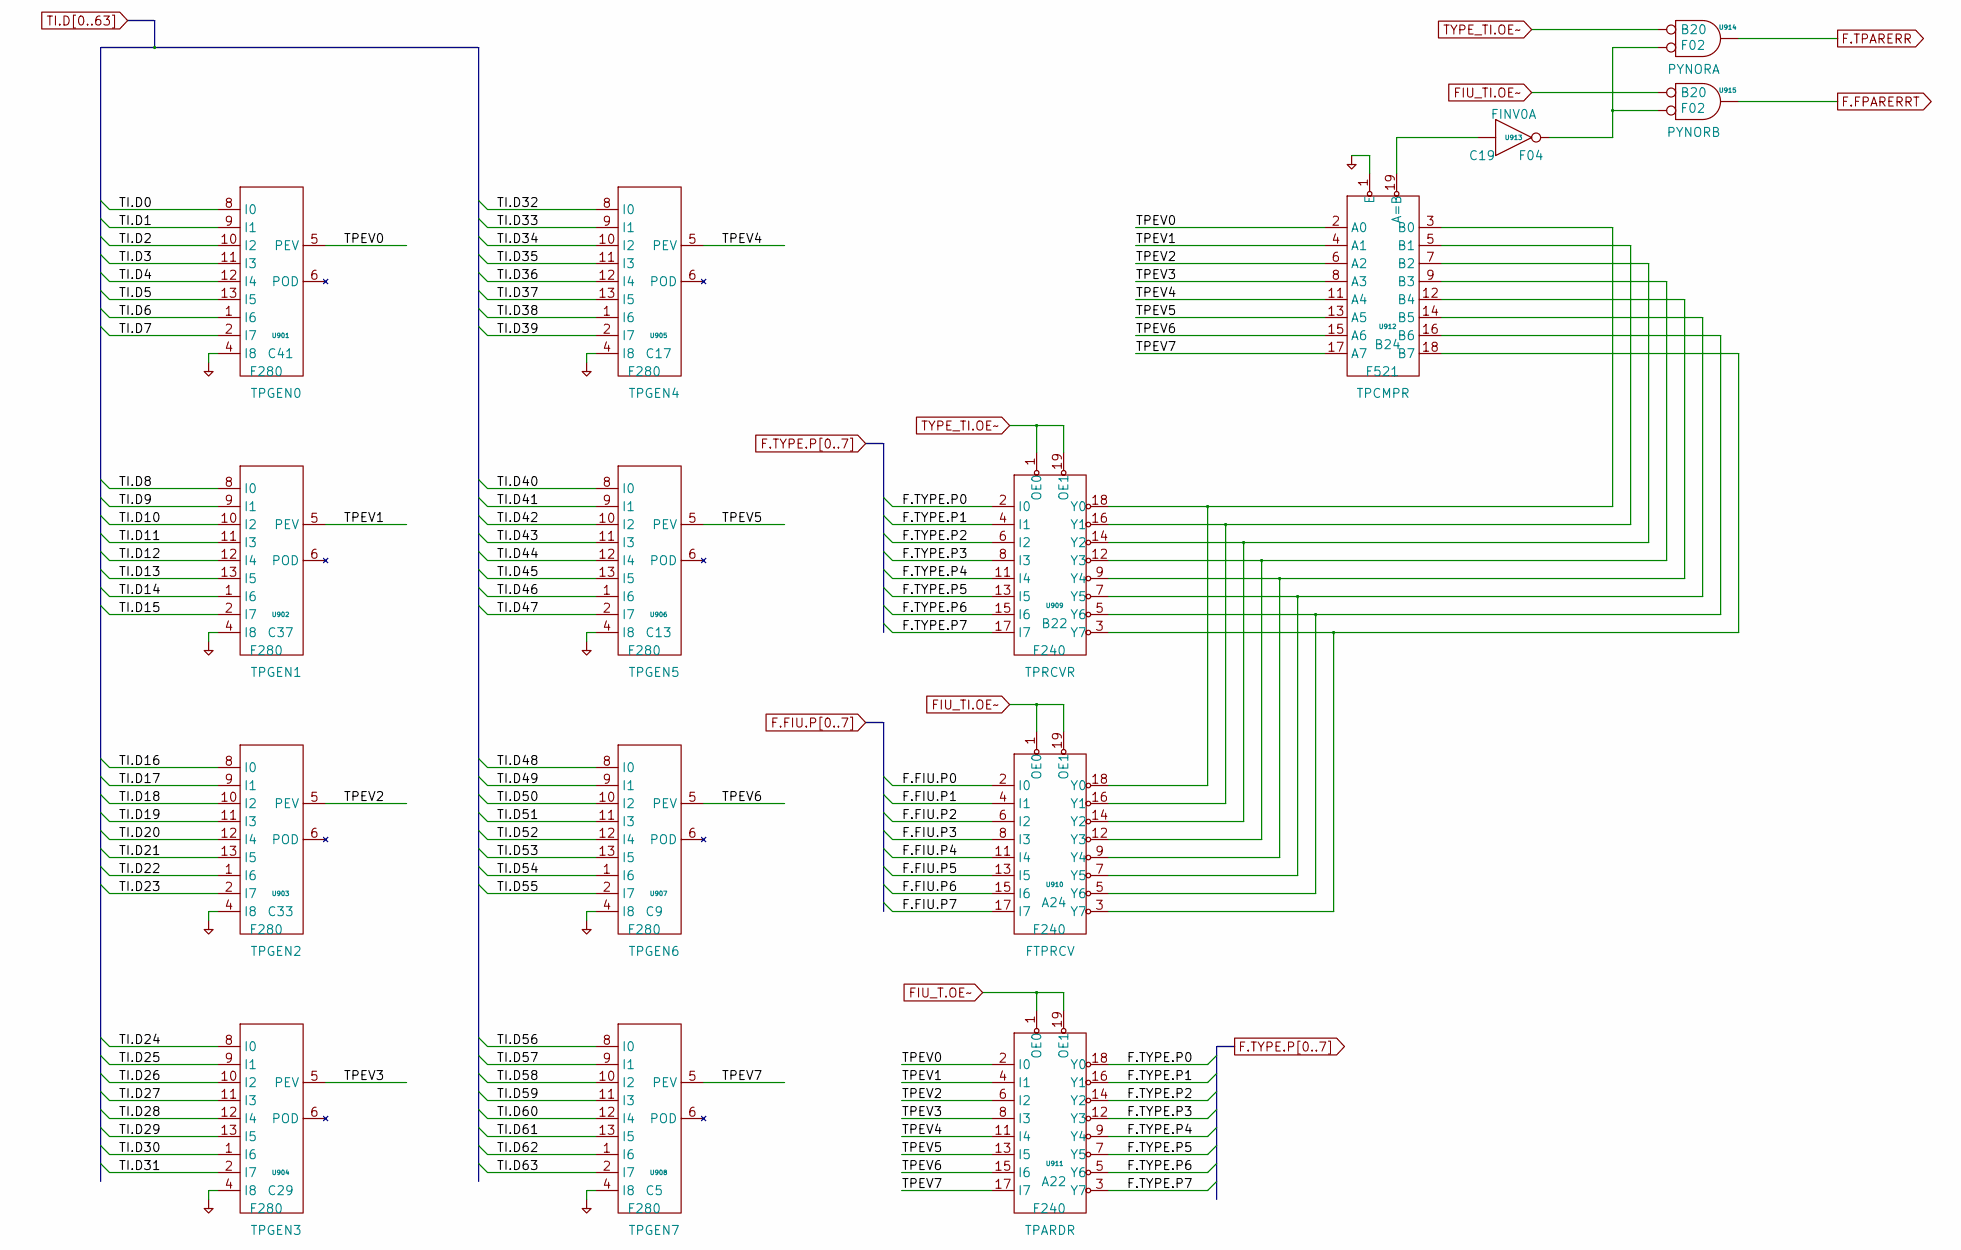
[picture p294: schematic pg_08.kicad_sch]

Parts:
U901, U902, U903, U904, U905, U906, U907, U908: F280
U909, U910, U911: F240
U912: F521
U913: F04
U914, U915: F02

Connections:
F.FIU.P0: U910.2 (I0)
F.FIU.P1: U910.4 (I1)
F.FIU.P2: U910.6 (I2)
F.FIU.P3: U910.8 (I3)
F.FIU.P4: U910.11 (I4)
F.FIU.P5: U910.13 (I5)
F.FIU.P6: U910.15 (I6)
F.FIU.P7: U910.17 (I7)
F.FPARERRT: U915.3 (Q)
F.TPARERR: U914.3 (Q)
F.TYPE.P0: U909.2 (I0), U911.18 (Y0)
F.TYPE.P1: U909.4 (I1), U911.16 (Y1)
F.TYPE.P2: U909.6 (I2), U911.14 (Y2)
F.TYPE.P3: U909.8 (I3), U911.12 (Y3)
F.TYPE.P4: U909.11 (I4), U911.9 (Y4)
F.TYPE.P5: U909.13 (I5), U911.7 (Y5)
F.TYPE.P6: U909.15 (I6), U911.5 (Y6)
F.TYPE.P7: U909.17 (I7), U911.3 (Y7)
FIU_T.OE~: U911.1 (OE0), U911.19 (OE1)
FIU_TI.OE~: U910.1 (OE0), U910.19 (OE1), U915.1 (D0)
unnamed: U909.3 (Y7), U910.3 (Y7), U912.18 (B7)
unnamed: U909.5 (Y6), U910.5 (Y6), U912.16 (B6)
unnamed: U909.7 (Y5), U910.7 (Y5), U912.14 (B5)
unnamed: U909.9 (Y4), U910.9 (Y4), U912.12 (B4)
unnamed: U909.12 (Y3), U910.12 (Y3), U912.9 (B3)
unnamed: U909.14 (Y2), U910.14 (Y2), U912.7 (B2)
unnamed: U909.16 (Y1), U910.16 (Y1), U912.5 (B1)
unnamed: U909.18 (Y0), U910.18 (Y0), U912.3 (B0)
unnamed: U912.19 (A=B), U913.1 (D0)
unnamed: U913.2 (Q), U914.2 (D1), U915.2 (D1)
PD: U901.4 (I8), U902.4 (I8), U903.4 (I8), U904.4 (I8), U905.4 (I8), U906.4 (I8), U907.4 (I8), U908.4 (I8), U912.1 (E)
TI.D0: U901.8 (I0)
TI.D1: U901.9 (I1)
TI.D2: U901.10 (I2)
TI.D3: U901.11 (I3)
TI.D4: U901.12 (I4)
TI.D5: U901.13 (I5)
TI.D6: U901.1 (I6)
TI.D7: U901.2 (I7)
TI.D8: U902.8 (I0)
TI.D9: U902.9 (I1)
TI.D10: U902.10 (I2)
TI.D11: U902.11 (I3)
TI.D12: U902.12 (I4)
TI.D13: U902.13 (I5)
TI.D14: U902.1 (I6)
TI.D15: U902.2 (I7)
TI.D16: U903.8 (I0)
TI.D17: U903.9 (I1)
TI.D18: U903.10 (I2)
TI.D19: U903.11 (I3)
TI.D20: U903.12 (I4)
TI.D21: U903.13 (I5)
TI.D22: U903.1 (I6)
TI.D23: U903.2 (I7)
TI.D24: U904.8 (I0)
TI.D25: U904.9 (I1)
TI.D26: U904.10 (I2)
TI.D27: U904.11 (I3)
TI.D28: U904.12 (I4)
TI.D29: U904.13 (I5)
TI.D30: U904.1 (I6)
TI.D31: U904.2 (I7)
TI.D32: U905.8 (I0)
TI.D33: U905.9 (I1)
TI.D34: U905.10 (I2)
TI.D35: U905.11 (I3)
TI.D36: U905.12 (I4)
TI.D37: U905.13 (I5)
TI.D38: U905.1 (I6)
TI.D39: U905.2 (I7)
TI.D40: U906.8 (I0)
TI.D41: U906.9 (I1)
TI.D42: U906.10 (I2)
TI.D43: U906.11 (I3)
TI.D44: U906.12 (I4)
TI.D45: U906.13 (I5)
TI.D46: U906.1 (I6)
TI.D47: U906.2 (I7)
TI.D48: U907.8 (I0)
TI.D49: U907.9 (I1)
TI.D50: U907.10 (I2)
TI.D51: U907.11 (I3)
TI.D52: U907.12 (I4)
TI.D53: U907.13 (I5)
TI.D54: U907.1 (I6)
TI.D55: U907.2 (I7)
TI.D56: U908.8 (I0)
TI.D57: U908.9 (I1)
TI.D58: U908.10 (I2)
TI.D59: U908.11 (I3)
TI.D60: U908.12 (I4)
TI.D61: U908.13 (I5)
TI.D62: U908.1 (I6)
TI.D63: U908.2 (I7)
TPEV0: U901.5 (PEV), U911.2 (I0), U912.2 (A0)
TPEV1: U902.5 (PEV), U911.4 (I1), U912.4 (A1)
TPEV2: U903.5 (PEV), U911.6 (I2), U912.6 (A2)
TPEV3: U904.5 (PEV), U911.8 (I3), U912.8 (A3)
TPEV4: U905.5 (PEV), U911.11 (I4), U912.11 (A4)
TPEV5: U906.5 (PEV), U911.13 (I5), U912.13 (A5)
TPEV6: U907.5 (PEV), U911.15 (I6), U912.15 (A6)
TPEV7: U908.5 (PEV), U911.17 (I7), U912.17 (A7)
TYPE_TI.OE~: U909.1 (OE0), U909.19 (OE1), U914.1 (D0)
