Datamuseum-DK/R1000.HwDoc/Schematics/FIU/pg_09.kicad_sch

## KiCad design Schematics/FIU/pg_09.kicad_sch (2023-01-10)

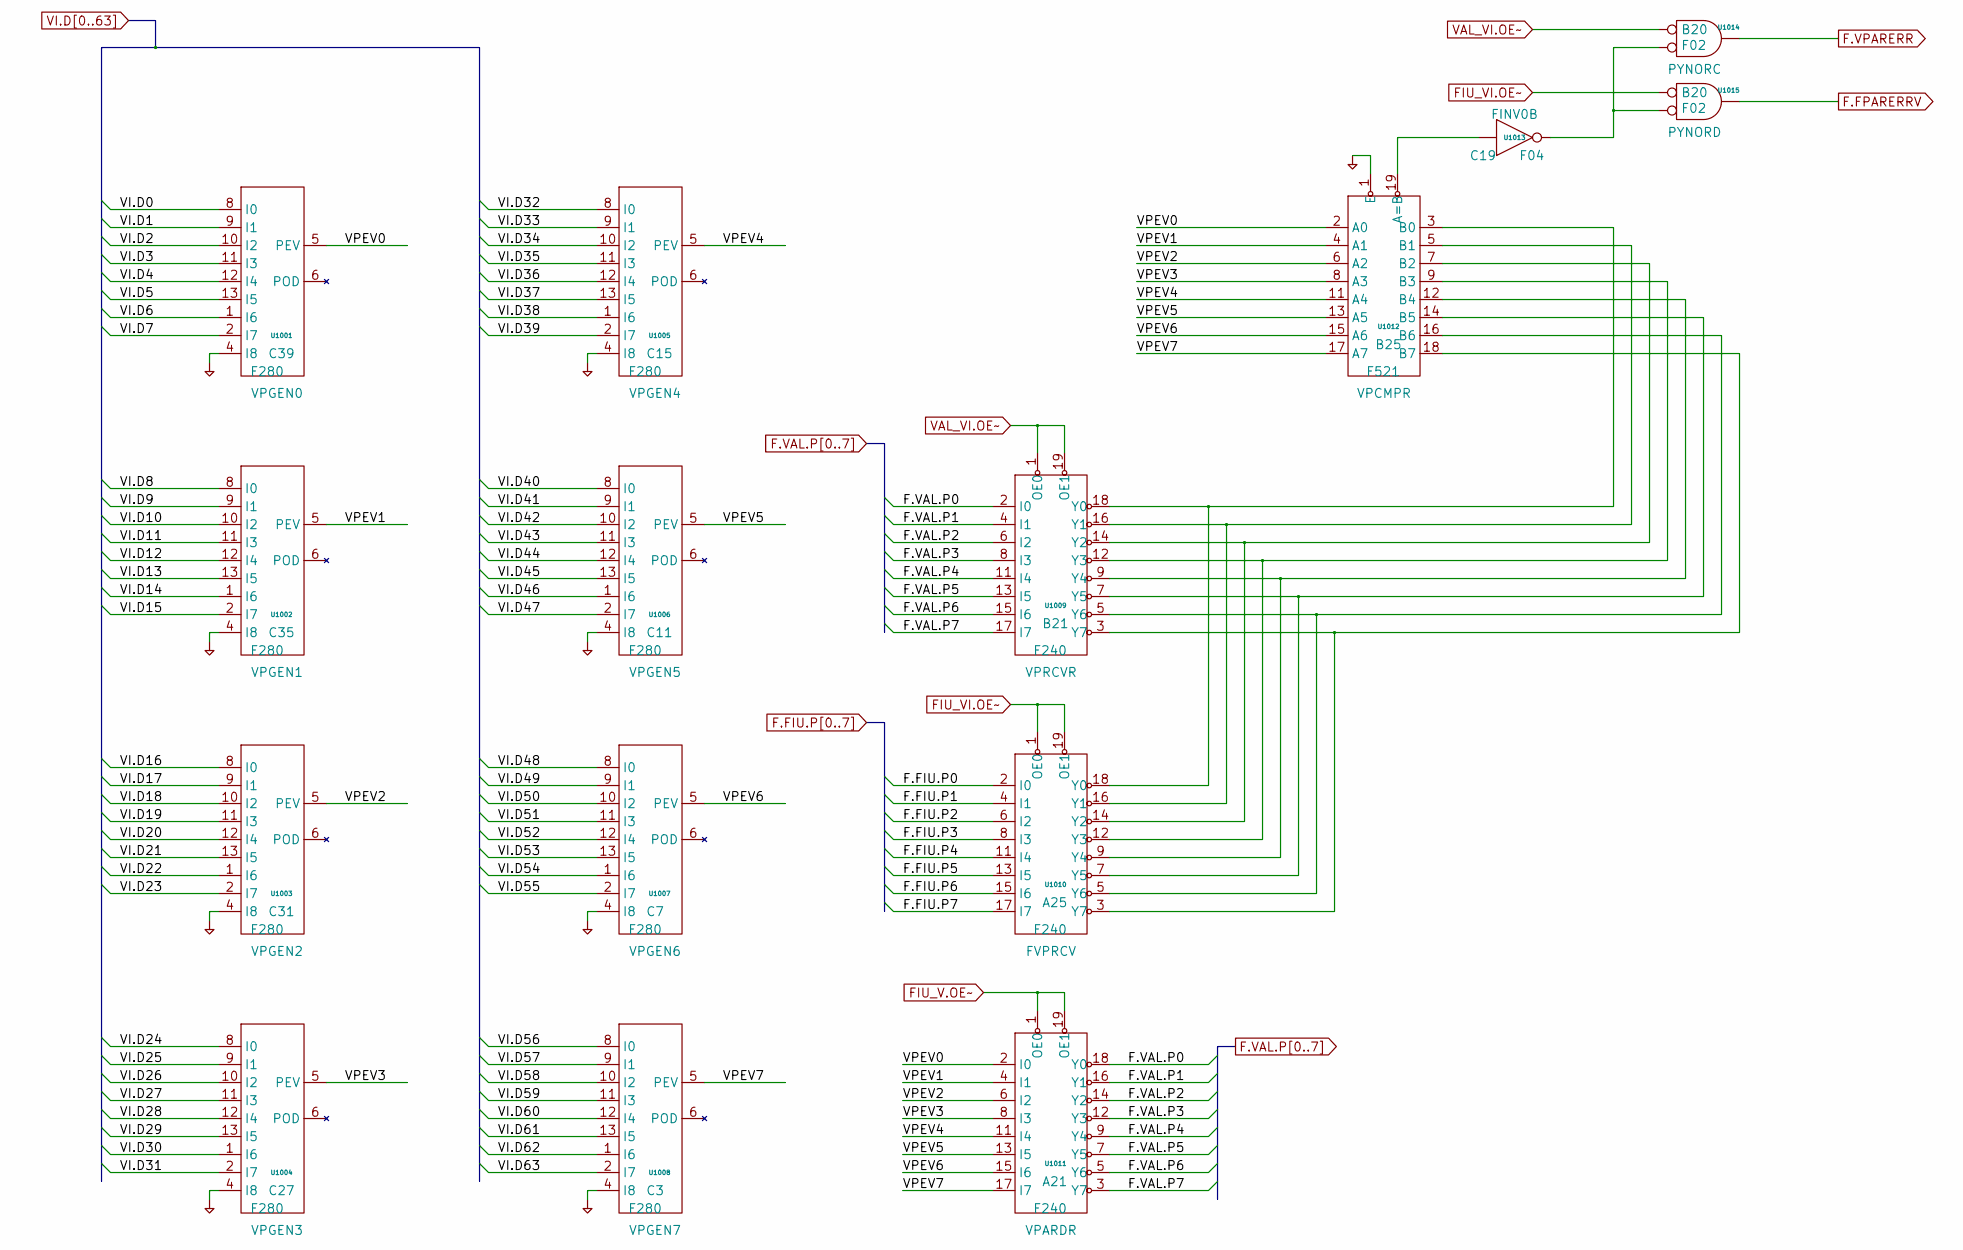
[picture p295: schematic pg_09.kicad_sch]

Parts:
U1001, U1002, U1003, U1004, U1005, U1006, U1007, U1008: F280
U1009, U1010, U1011: F240
U1012: F521
U1013: F04
U1014, U1015: F02

Connections:
F.FIU.P0: U1010.2 (I0)
F.FIU.P1: U1010.4 (I1)
F.FIU.P2: U1010.6 (I2)
F.FIU.P3: U1010.8 (I3)
F.FIU.P4: U1010.11 (I4)
F.FIU.P5: U1010.13 (I5)
F.FIU.P6: U1010.15 (I6)
F.FIU.P7: U1010.17 (I7)
F.FPARERRV: U1015.3 (Q)
F.VAL.P0: U1009.2 (I0), U1011.18 (Y0)
F.VAL.P1: U1009.4 (I1), U1011.16 (Y1)
F.VAL.P2: U1009.6 (I2), U1011.14 (Y2)
F.VAL.P3: U1009.8 (I3), U1011.12 (Y3)
F.VAL.P4: U1009.11 (I4), U1011.9 (Y4)
F.VAL.P5: U1009.13 (I5), U1011.7 (Y5)
F.VAL.P6: U1009.15 (I6), U1011.5 (Y6)
F.VAL.P7: U1009.17 (I7), U1011.3 (Y7)
F.VPARERR: U1014.3 (Q)
FIU_V.OE~: U1011.1 (OE0), U1011.19 (OE1)
FIU_VI.OE~: U1010.1 (OE0), U1010.19 (OE1), U1015.1 (D0)
unnamed: U1009.3 (Y7), U1010.3 (Y7), U1012.18 (B7)
unnamed: U1009.5 (Y6), U1010.5 (Y6), U1012.16 (B6)
unnamed: U1009.7 (Y5), U1010.7 (Y5), U1012.14 (B5)
unnamed: U1009.9 (Y4), U1010.9 (Y4), U1012.12 (B4)
unnamed: U1009.12 (Y3), U1010.12 (Y3), U1012.9 (B3)
unnamed: U1009.14 (Y2), U1010.14 (Y2), U1012.7 (B2)
unnamed: U1009.16 (Y1), U1010.16 (Y1), U1012.5 (B1)
unnamed: U1009.18 (Y0), U1010.18 (Y0), U1012.3 (B0)
unnamed: U1012.19 (A=B), U1013.1 (D0)
unnamed: U1013.2 (Q), U1014.2 (D1), U1015.2 (D1)
PD: U1001.4 (I8), U1002.4 (I8), U1003.4 (I8), U1004.4 (I8), U1005.4 (I8), U1006.4 (I8), U1007.4 (I8), U1008.4 (I8), U1012.1 (E)
VAL_VI.OE~: U1009.1 (OE0), U1009.19 (OE1), U1014.1 (D0)
VI.D0: U1001.8 (I0)
VI.D1: U1001.9 (I1)
VI.D2: U1001.10 (I2)
VI.D3: U1001.11 (I3)
VI.D4: U1001.12 (I4)
VI.D5: U1001.13 (I5)
VI.D6: U1001.1 (I6)
VI.D7: U1001.2 (I7)
VI.D8: U1002.8 (I0)
VI.D9: U1002.9 (I1)
VI.D10: U1002.10 (I2)
VI.D11: U1002.11 (I3)
VI.D12: U1002.12 (I4)
VI.D13: U1002.13 (I5)
VI.D14: U1002.1 (I6)
VI.D15: U1002.2 (I7)
VI.D16: U1003.8 (I0)
VI.D17: U1003.9 (I1)
VI.D18: U1003.10 (I2)
VI.D19: U1003.11 (I3)
VI.D20: U1003.12 (I4)
VI.D21: U1003.13 (I5)
VI.D22: U1003.1 (I6)
VI.D23: U1003.2 (I7)
VI.D24: U1004.8 (I0)
VI.D25: U1004.9 (I1)
VI.D26: U1004.10 (I2)
VI.D27: U1004.11 (I3)
VI.D28: U1004.12 (I4)
VI.D29: U1004.13 (I5)
VI.D30: U1004.1 (I6)
VI.D31: U1004.2 (I7)
VI.D32: U1005.8 (I0)
VI.D33: U1005.9 (I1)
VI.D34: U1005.10 (I2)
VI.D35: U1005.11 (I3)
VI.D36: U1005.12 (I4)
VI.D37: U1005.13 (I5)
VI.D38: U1005.1 (I6)
VI.D39: U1005.2 (I7)
VI.D40: U1006.8 (I0)
VI.D41: U1006.9 (I1)
VI.D42: U1006.10 (I2)
VI.D43: U1006.11 (I3)
VI.D44: U1006.12 (I4)
VI.D45: U1006.13 (I5)
VI.D46: U1006.1 (I6)
VI.D47: U1006.2 (I7)
VI.D48: U1007.8 (I0)
VI.D49: U1007.9 (I1)
VI.D50: U1007.10 (I2)
VI.D51: U1007.11 (I3)
VI.D52: U1007.12 (I4)
VI.D53: U1007.13 (I5)
VI.D54: U1007.1 (I6)
VI.D55: U1007.2 (I7)
VI.D56: U1008.8 (I0)
VI.D57: U1008.9 (I1)
VI.D58: U1008.10 (I2)
VI.D59: U1008.11 (I3)
VI.D60: U1008.12 (I4)
VI.D61: U1008.13 (I5)
VI.D62: U1008.1 (I6)
VI.D63: U1008.2 (I7)
VPEV0: U1001.5 (PEV), U1011.2 (I0), U1012.2 (A0)
VPEV1: U1002.5 (PEV), U1011.4 (I1), U1012.4 (A1)
VPEV2: U1003.5 (PEV), U1011.6 (I2), U1012.6 (A2)
VPEV3: U1004.5 (PEV), U1011.8 (I3), U1012.8 (A3)
VPEV4: U1005.5 (PEV), U1011.11 (I4), U1012.11 (A4)
VPEV5: U1006.5 (PEV), U1011.13 (I5), U1012.13 (A5)
VPEV6: U1007.5 (PEV), U1011.15 (I6), U1012.15 (A6)
VPEV7: U1008.5 (PEV), U1011.17 (I7), U1012.17 (A7)
