Datamuseum-DK/R1000.HwDoc/Schematics/FIU/pg_10.kicad_sch

## KiCad design Schematics/FIU/pg_10.kicad_sch (2023-01-10)

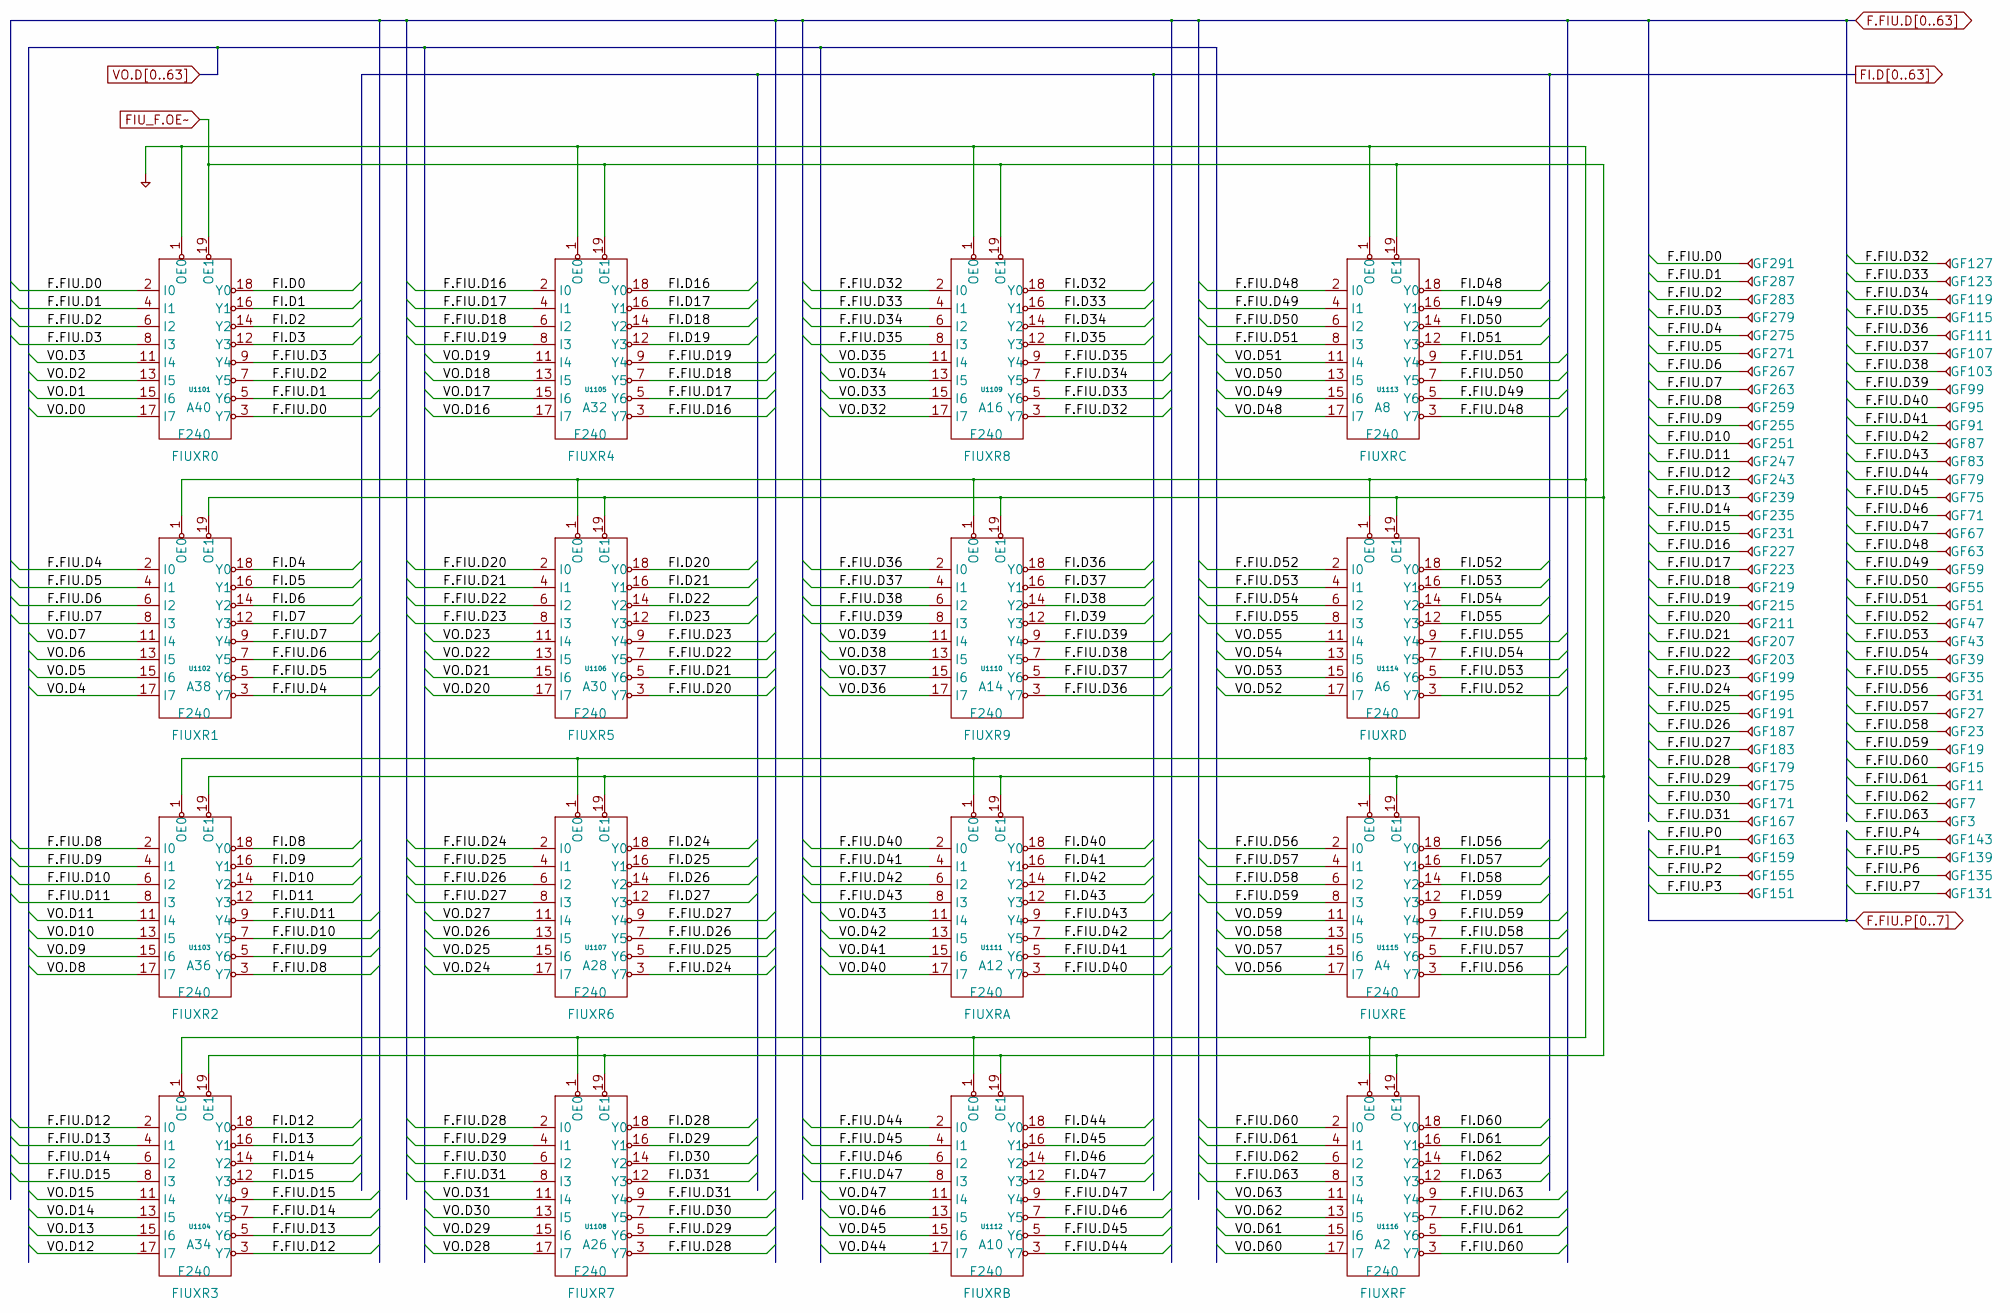
[picture p296: schematic pg_10.kicad_sch]

Parts:
GF3, GF7, GF11, GF15, GF19, GF23, GF27, GF31, GF35, GF39, GF43, GF47, GF51, GF55, GF59, GF63, GF67, GF71, GF75, GF79, GF83, GF87, GF91, GF95, GF99, GF103, GF107, GF111, GF115, GF119, GF123, GF127, GF131, GF135, GF139, GF143, GF151, GF155, GF159, GF163, GF167, GF171, GF175, GF179, GF183, GF187, GF191, GF195, GF199, GF203, GF207, GF211, GF215, GF219, GF223, GF227, GF231, GF235, GF239, GF243, GF247, GF251, GF255, GF259, GF263, GF267, GF271, GF275, GF279, GF283, GF287, GF291: GF
U1101, U1102, U1103, U1104, U1105, U1106, U1107, U1108, U1109, U1110, U1111, U1112, U1113, U1114, U1115, U1116: F240

Connections:
F.FIU.D0: GF291.1, U1101.2 (I0), U1101.3 (Y7)
F.FIU.D1: GF287.1, U1101.4 (I1), U1101.5 (Y6)
F.FIU.D2: GF283.1, U1101.6 (I2), U1101.7 (Y5)
F.FIU.D3: GF279.1, U1101.8 (I3), U1101.9 (Y4)
F.FIU.D4: GF275.1, U1102.2 (I0), U1102.3 (Y7)
F.FIU.D5: GF271.1, U1102.4 (I1), U1102.5 (Y6)
F.FIU.D6: GF267.1, U1102.6 (I2), U1102.7 (Y5)
F.FIU.D7: GF263.1, U1102.8 (I3), U1102.9 (Y4)
F.FIU.D8: GF259.1, U1103.2 (I0), U1103.3 (Y7)
F.FIU.D9: GF255.1, U1103.4 (I1), U1103.5 (Y6)
F.FIU.D10: GF251.1, U1103.6 (I2), U1103.7 (Y5)
F.FIU.D11: GF247.1, U1103.8 (I3), U1103.9 (Y4)
F.FIU.D12: GF243.1, U1104.2 (I0), U1104.3 (Y7)
F.FIU.D13: GF239.1, U1104.4 (I1), U1104.5 (Y6)
F.FIU.D14: GF235.1, U1104.6 (I2), U1104.7 (Y5)
F.FIU.D15: GF231.1, U1104.8 (I3), U1104.9 (Y4)
F.FIU.D16: GF227.1, U1105.2 (I0), U1105.3 (Y7)
F.FIU.D17: GF223.1, U1105.4 (I1), U1105.5 (Y6)
F.FIU.D18: GF219.1, U1105.6 (I2), U1105.7 (Y5)
F.FIU.D19: GF215.1, U1105.8 (I3), U1105.9 (Y4)
F.FIU.D20: GF211.1, U1106.2 (I0), U1106.3 (Y7)
F.FIU.D21: GF207.1, U1106.4 (I1), U1106.5 (Y6)
F.FIU.D22: GF203.1, U1106.6 (I2), U1106.7 (Y5)
F.FIU.D23: GF199.1, U1106.8 (I3), U1106.9 (Y4)
F.FIU.D24: GF195.1, U1107.2 (I0), U1107.3 (Y7)
F.FIU.D25: GF191.1, U1107.4 (I1), U1107.5 (Y6)
F.FIU.D26: GF187.1, U1107.6 (I2), U1107.7 (Y5)
F.FIU.D27: GF183.1, U1107.8 (I3), U1107.9 (Y4)
F.FIU.D28: GF179.1, U1108.2 (I0), U1108.3 (Y7)
F.FIU.D29: GF175.1, U1108.4 (I1), U1108.5 (Y6)
F.FIU.D30: GF171.1, U1108.6 (I2), U1108.7 (Y5)
F.FIU.D31: GF167.1, U1108.8 (I3), U1108.9 (Y4)
F.FIU.D32: GF127.1, U1109.2 (I0), U1109.3 (Y7)
F.FIU.D33: GF123.1, U1109.4 (I1), U1109.5 (Y6)
F.FIU.D34: GF119.1, U1109.6 (I2), U1109.7 (Y5)
F.FIU.D35: GF115.1, U1109.8 (I3), U1109.9 (Y4)
F.FIU.D36: GF111.1, U1110.2 (I0), U1110.3 (Y7)
F.FIU.D37: GF107.1, U1110.4 (I1), U1110.5 (Y6)
F.FIU.D38: GF103.1, U1110.6 (I2), U1110.7 (Y5)
F.FIU.D39: GF99.1, U1110.8 (I3), U1110.9 (Y4)
F.FIU.D40: GF95.1, U1111.2 (I0), U1111.3 (Y7)
F.FIU.D41: GF91.1, U1111.4 (I1), U1111.5 (Y6)
F.FIU.D42: GF87.1, U1111.6 (I2), U1111.7 (Y5)
F.FIU.D43: GF83.1, U1111.8 (I3), U1111.9 (Y4)
F.FIU.D44: GF79.1, U1112.2 (I0), U1112.3 (Y7)
F.FIU.D45: GF75.1, U1112.4 (I1), U1112.5 (Y6)
F.FIU.D46: GF71.1, U1112.6 (I2), U1112.7 (Y5)
F.FIU.D47: GF67.1, U1112.8 (I3), U1112.9 (Y4)
F.FIU.D48: GF63.1, U1113.2 (I0), U1113.3 (Y7)
F.FIU.D49: GF59.1, U1113.4 (I1), U1113.5 (Y6)
F.FIU.D50: GF55.1, U1113.6 (I2), U1113.7 (Y5)
F.FIU.D51: GF51.1, U1113.8 (I3), U1113.9 (Y4)
F.FIU.D52: GF47.1, U1114.2 (I0), U1114.3 (Y7)
F.FIU.D53: GF43.1, U1114.4 (I1), U1114.5 (Y6)
F.FIU.D54: GF39.1, U1114.6 (I2), U1114.7 (Y5)
F.FIU.D55: GF35.1, U1114.8 (I3), U1114.9 (Y4)
F.FIU.D56: GF31.1, U1115.2 (I0), U1115.3 (Y7)
F.FIU.D57: GF27.1, U1115.4 (I1), U1115.5 (Y6)
F.FIU.D58: GF23.1, U1115.6 (I2), U1115.7 (Y5)
F.FIU.D59: GF19.1, U1115.8 (I3), U1115.9 (Y4)
F.FIU.D60: GF15.1, U1116.2 (I0), U1116.3 (Y7)
F.FIU.D61: GF11.1, U1116.4 (I1), U1116.5 (Y6)
F.FIU.D62: GF7.1, U1116.6 (I2), U1116.7 (Y5)
F.FIU.D63: GF3.1, U1116.8 (I3), U1116.9 (Y4)
F.FIU.P0: GF163.1
F.FIU.P1: GF159.1
F.FIU.P2: GF155.1
F.FIU.P3: GF151.1
F.FIU.P4: GF143.1
F.FIU.P5: GF139.1
F.FIU.P6: GF135.1
F.FIU.P7: GF131.1
FI.D0: U1101.18 (Y0)
FI.D1: U1101.16 (Y1)
FI.D2: U1101.14 (Y2)
FI.D3: U1101.12 (Y3)
FI.D4: U1102.18 (Y0)
FI.D5: U1102.16 (Y1)
FI.D6: U1102.14 (Y2)
FI.D7: U1102.12 (Y3)
FI.D8: U1103.18 (Y0)
FI.D9: U1103.16 (Y1)
FI.D10: U1103.14 (Y2)
FI.D11: U1103.12 (Y3)
FI.D12: U1104.18 (Y0)
FI.D13: U1104.16 (Y1)
FI.D14: U1104.14 (Y2)
FI.D15: U1104.12 (Y3)
FI.D16: U1105.18 (Y0)
FI.D17: U1105.16 (Y1)
FI.D18: U1105.14 (Y2)
FI.D19: U1105.12 (Y3)
FI.D20: U1106.18 (Y0)
FI.D21: U1106.16 (Y1)
FI.D22: U1106.14 (Y2)
FI.D23: U1106.12 (Y3)
FI.D24: U1107.18 (Y0)
FI.D25: U1107.16 (Y1)
FI.D26: U1107.14 (Y2)
FI.D27: U1107.12 (Y3)
FI.D28: U1108.18 (Y0)
FI.D29: U1108.16 (Y1)
FI.D30: U1108.14 (Y2)
FI.D31: U1108.12 (Y3)
FI.D32: U1109.18 (Y0)
FI.D33: U1109.16 (Y1)
FI.D34: U1109.14 (Y2)
FI.D35: U1109.12 (Y3)
FI.D36: U1110.18 (Y0)
FI.D37: U1110.16 (Y1)
FI.D38: U1110.14 (Y2)
FI.D39: U1110.12 (Y3)
FI.D40: U1111.18 (Y0)
FI.D41: U1111.16 (Y1)
FI.D42: U1111.14 (Y2)
FI.D43: U1111.12 (Y3)
FI.D44: U1112.18 (Y0)
FI.D45: U1112.16 (Y1)
FI.D46: U1112.14 (Y2)
FI.D47: U1112.12 (Y3)
FI.D48: U1113.18 (Y0)
FI.D49: U1113.16 (Y1)
FI.D50: U1113.14 (Y2)
FI.D51: U1113.12 (Y3)
FI.D52: U1114.18 (Y0)
FI.D53: U1114.16 (Y1)
FI.D54: U1114.14 (Y2)
FI.D55: U1114.12 (Y3)
FI.D56: U1115.18 (Y0)
FI.D57: U1115.16 (Y1)
FI.D58: U1115.14 (Y2)
FI.D59: U1115.12 (Y3)
FI.D60: U1116.18 (Y0)
FI.D61: U1116.16 (Y1)
FI.D62: U1116.14 (Y2)
FI.D63: U1116.12 (Y3)
FIU_F.OE~: U1101.19 (OE1), U1102.19 (OE1), U1103.19 (OE1), U1104.19 (OE1), U1105.19 (OE1), U1106.19 (OE1), U1107.19 (OE1), U1108.19 (OE1), U1109.19 (OE1), U1110.19 (OE1), U1111.19 (OE1), U1112.19 (OE1), U1113.19 (OE1), U1114.19 (OE1), U1115.19 (OE1), U1116.19 (OE1)
PD: U1101.1 (OE0), U1102.1 (OE0), U1103.1 (OE0), U1104.1 (OE0), U1105.1 (OE0), U1106.1 (OE0), U1107.1 (OE0), U1108.1 (OE0), U1109.1 (OE0), U1110.1 (OE0), U1111.1 (OE0), U1112.1 (OE0), U1113.1 (OE0), U1114.1 (OE0), U1115.1 (OE0), U1116.1 (OE0)
VO.D0: U1101.17 (I7)
VO.D1: U1101.15 (I6)
VO.D2: U1101.13 (I5)
VO.D3: U1101.11 (I4)
VO.D4: U1102.17 (I7)
VO.D5: U1102.15 (I6)
VO.D6: U1102.13 (I5)
VO.D7: U1102.11 (I4)
VO.D8: U1103.17 (I7)
VO.D9: U1103.15 (I6)
VO.D10: U1103.13 (I5)
VO.D11: U1103.11 (I4)
VO.D12: U1104.17 (I7)
VO.D13: U1104.15 (I6)
VO.D14: U1104.13 (I5)
VO.D15: U1104.11 (I4)
VO.D16: U1105.17 (I7)
VO.D17: U1105.15 (I6)
VO.D18: U1105.13 (I5)
VO.D19: U1105.11 (I4)
VO.D20: U1106.17 (I7)
VO.D21: U1106.15 (I6)
VO.D22: U1106.13 (I5)
VO.D23: U1106.11 (I4)
VO.D24: U1107.17 (I7)
VO.D25: U1107.15 (I6)
VO.D26: U1107.13 (I5)
VO.D27: U1107.11 (I4)
VO.D28: U1108.17 (I7)
VO.D29: U1108.15 (I6)
VO.D30: U1108.13 (I5)
VO.D31: U1108.11 (I4)
VO.D32: U1109.17 (I7)
VO.D33: U1109.15 (I6)
VO.D34: U1109.13 (I5)
VO.D35: U1109.11 (I4)
VO.D36: U1110.17 (I7)
VO.D37: U1110.15 (I6)
VO.D38: U1110.13 (I5)
VO.D39: U1110.11 (I4)
VO.D40: U1111.17 (I7)
VO.D41: U1111.15 (I6)
VO.D42: U1111.13 (I5)
VO.D43: U1111.11 (I4)
VO.D44: U1112.17 (I7)
VO.D45: U1112.15 (I6)
VO.D46: U1112.13 (I5)
VO.D47: U1112.11 (I4)
VO.D48: U1113.17 (I7)
VO.D49: U1113.15 (I6)
VO.D50: U1113.13 (I5)
VO.D51: U1113.11 (I4)
VO.D52: U1114.17 (I7)
VO.D53: U1114.15 (I6)
VO.D54: U1114.13 (I5)
VO.D55: U1114.11 (I4)
VO.D56: U1115.17 (I7)
VO.D57: U1115.15 (I6)
VO.D58: U1115.13 (I5)
VO.D59: U1115.11 (I4)
VO.D60: U1116.17 (I7)
VO.D61: U1116.15 (I6)
VO.D62: U1116.13 (I5)
VO.D63: U1116.11 (I4)
