Datamuseum-DK/R1000.HwDoc/Schematics/FIU/pg_11.kicad_sch

## KiCad design Schematics/FIU/pg_11.kicad_sch (2023-01-10)

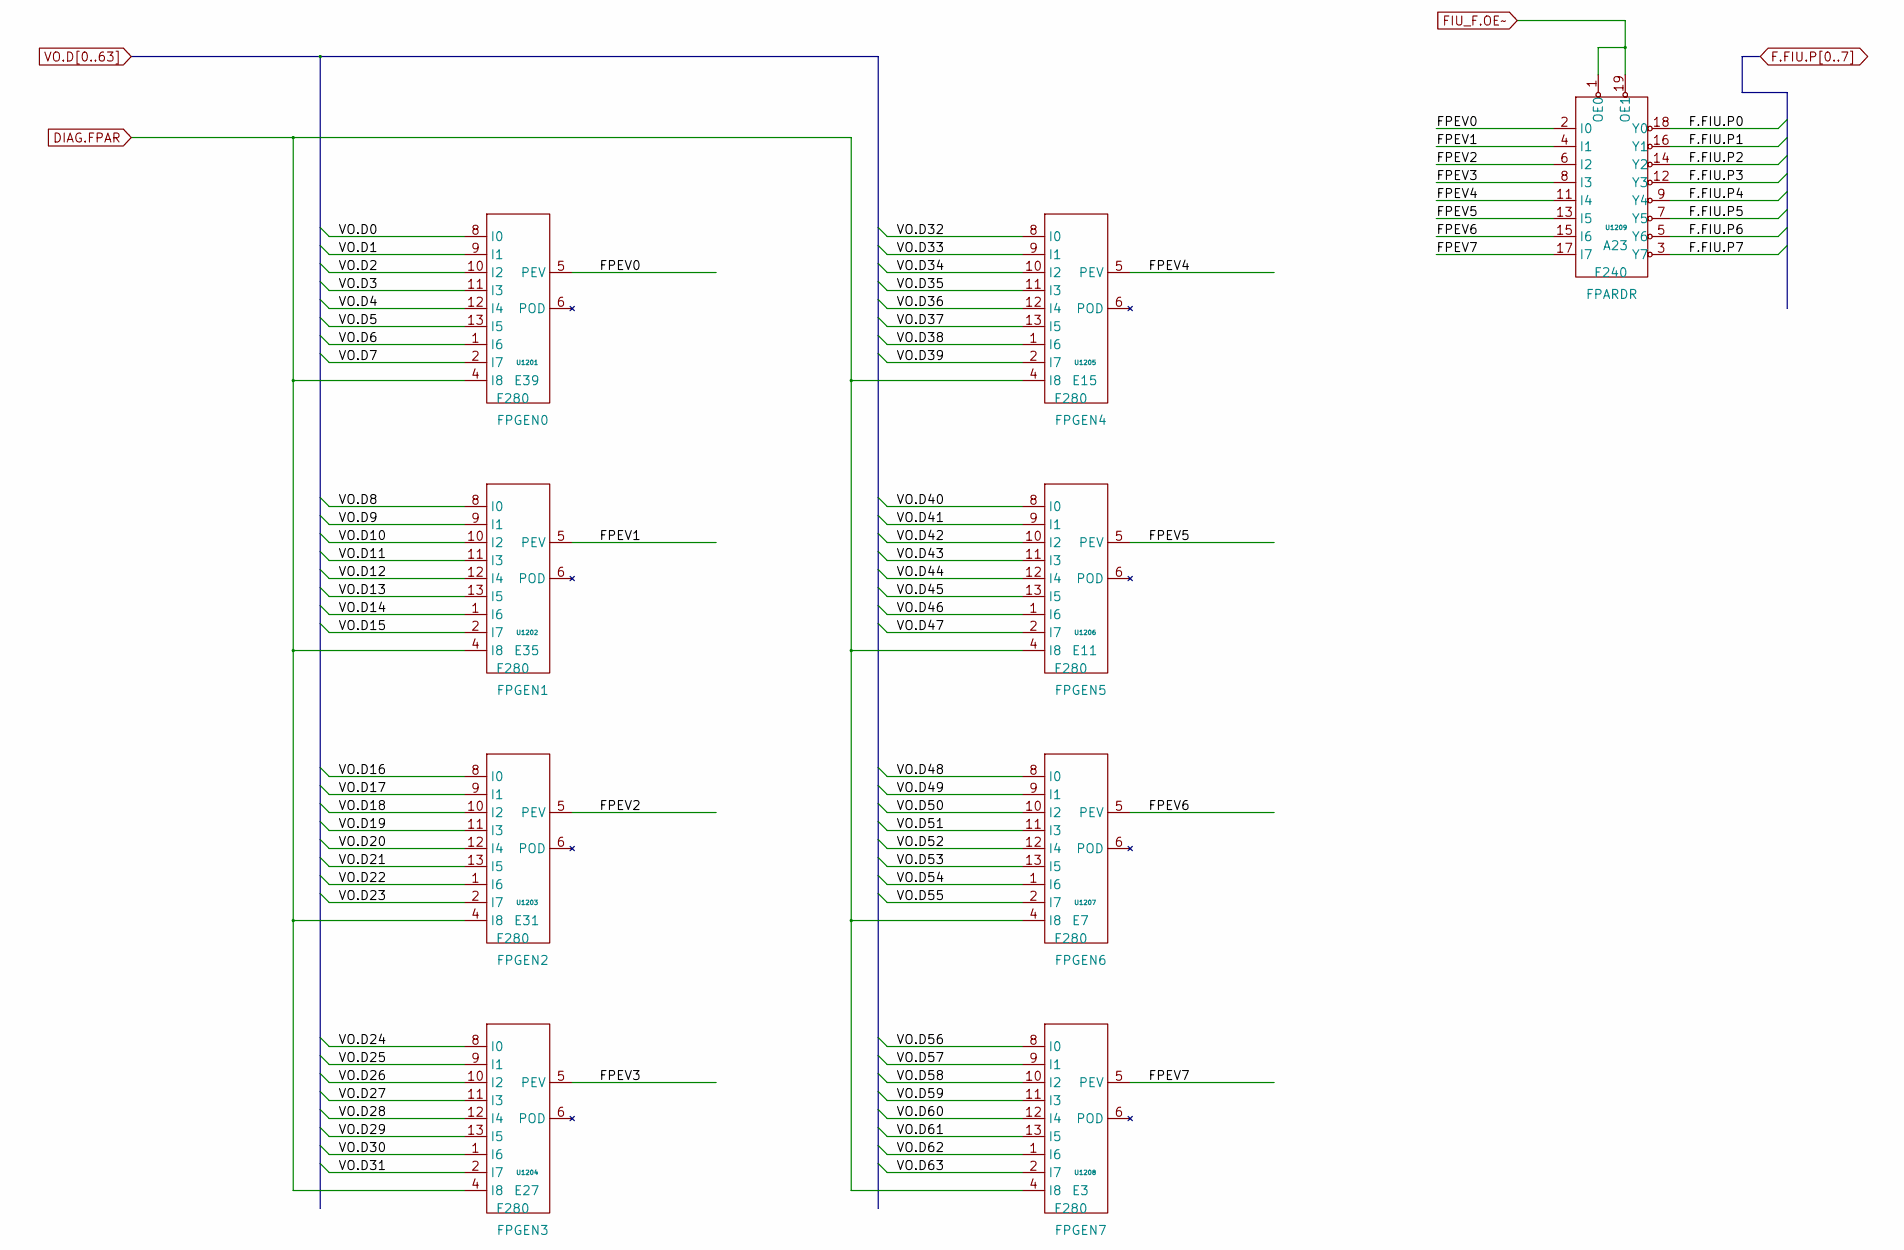
[picture p297: schematic pg_11.kicad_sch]

Parts:
U1201, U1202, U1203, U1204, U1205, U1206, U1207, U1208: F280
U1209: F240

Connections:
DIAG.FPAR: U1201.4 (I8), U1202.4 (I8), U1203.4 (I8), U1204.4 (I8), U1205.4 (I8), U1206.4 (I8), U1207.4 (I8), U1208.4 (I8)
F.FIU.P0: U1209.18 (Y0)
F.FIU.P1: U1209.16 (Y1)
F.FIU.P2: U1209.14 (Y2)
F.FIU.P3: U1209.12 (Y3)
F.FIU.P4: U1209.9 (Y4)
F.FIU.P5: U1209.7 (Y5)
F.FIU.P6: U1209.5 (Y6)
F.FIU.P7: U1209.3 (Y7)
FIU_F.OE~: U1209.1 (OE0), U1209.19 (OE1)
FPEV0: U1201.5 (PEV), U1209.2 (I0)
FPEV1: U1202.5 (PEV), U1209.4 (I1)
FPEV2: U1203.5 (PEV), U1209.6 (I2)
FPEV3: U1204.5 (PEV), U1209.8 (I3)
FPEV4: U1205.5 (PEV), U1209.11 (I4)
FPEV5: U1206.5 (PEV), U1209.13 (I5)
FPEV6: U1207.5 (PEV), U1209.15 (I6)
FPEV7: U1208.5 (PEV), U1209.17 (I7)
VO.D0: U1201.8 (I0)
VO.D1: U1201.9 (I1)
VO.D2: U1201.10 (I2)
VO.D3: U1201.11 (I3)
VO.D4: U1201.12 (I4)
VO.D5: U1201.13 (I5)
VO.D6: U1201.1 (I6)
VO.D7: U1201.2 (I7)
VO.D8: U1202.8 (I0)
VO.D9: U1202.9 (I1)
VO.D10: U1202.10 (I2)
VO.D11: U1202.11 (I3)
VO.D12: U1202.12 (I4)
VO.D13: U1202.13 (I5)
VO.D14: U1202.1 (I6)
VO.D15: U1202.2 (I7)
VO.D16: U1203.8 (I0)
VO.D17: U1203.9 (I1)
VO.D18: U1203.10 (I2)
VO.D19: U1203.11 (I3)
VO.D20: U1203.12 (I4)
VO.D21: U1203.13 (I5)
VO.D22: U1203.1 (I6)
VO.D23: U1203.2 (I7)
VO.D24: U1204.8 (I0)
VO.D25: U1204.9 (I1)
VO.D26: U1204.10 (I2)
VO.D27: U1204.11 (I3)
VO.D28: U1204.12 (I4)
VO.D29: U1204.13 (I5)
VO.D30: U1204.1 (I6)
VO.D31: U1204.2 (I7)
VO.D32: U1205.8 (I0)
VO.D33: U1205.9 (I1)
VO.D34: U1205.10 (I2)
VO.D35: U1205.11 (I3)
VO.D36: U1205.12 (I4)
VO.D37: U1205.13 (I5)
VO.D38: U1205.1 (I6)
VO.D39: U1205.2 (I7)
VO.D40: U1206.8 (I0)
VO.D41: U1206.9 (I1)
VO.D42: U1206.10 (I2)
VO.D43: U1206.11 (I3)
VO.D44: U1206.12 (I4)
VO.D45: U1206.13 (I5)
VO.D46: U1206.1 (I6)
VO.D47: U1206.2 (I7)
VO.D48: U1207.8 (I0)
VO.D49: U1207.9 (I1)
VO.D50: U1207.10 (I2)
VO.D51: U1207.11 (I3)
VO.D52: U1207.12 (I4)
VO.D53: U1207.13 (I5)
VO.D54: U1207.1 (I6)
VO.D55: U1207.2 (I7)
VO.D56: U1208.8 (I0)
VO.D57: U1208.9 (I1)
VO.D58: U1208.10 (I2)
VO.D59: U1208.11 (I3)
VO.D60: U1208.12 (I4)
VO.D61: U1208.13 (I5)
VO.D62: U1208.1 (I6)
VO.D63: U1208.2 (I7)
