Datamuseum-DK/R1000.HwDoc/Schematics/FIU/pg_12.kicad_sch

## KiCad design Schematics/FIU/pg_12.kicad_sch (2023-01-10)

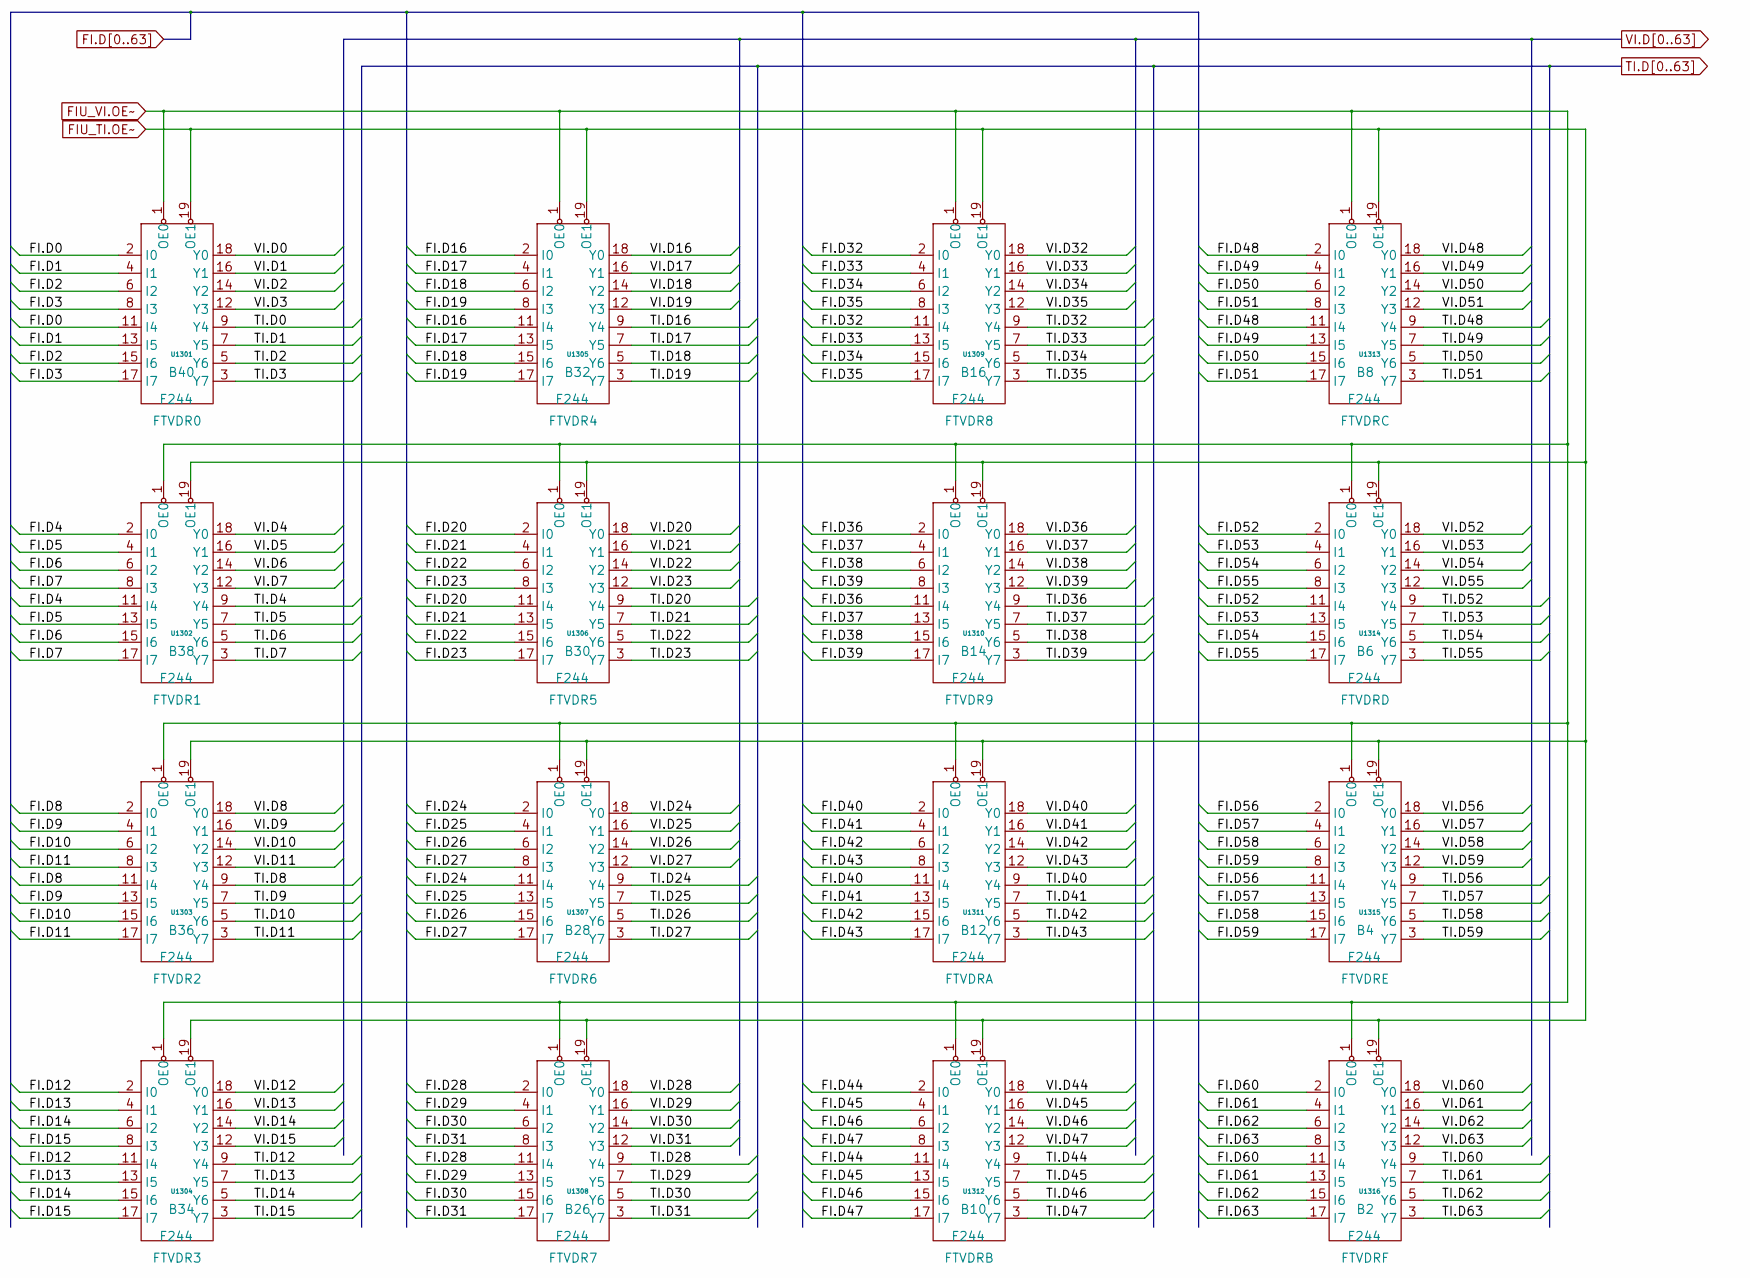
[picture p298: schematic pg_12.kicad_sch]

Parts:
U1301, U1302, U1303, U1304, U1305, U1306, U1307, U1308, U1309, U1310, U1311, U1312, U1313, U1314, U1315, U1316: F244

Connections:
FI.D0: U1301.2 (I0), U1301.11 (I4)
FI.D1: U1301.4 (I1), U1301.13 (I5)
FI.D2: U1301.6 (I2), U1301.15 (I6)
FI.D3: U1301.8 (I3), U1301.17 (I7)
FI.D4: U1302.2 (I0), U1302.11 (I4)
FI.D5: U1302.4 (I1), U1302.13 (I5)
FI.D6: U1302.6 (I2), U1302.15 (I6)
FI.D7: U1302.8 (I3), U1302.17 (I7)
FI.D8: U1303.2 (I0), U1303.11 (I4)
FI.D9: U1303.4 (I1), U1303.13 (I5)
FI.D10: U1303.6 (I2), U1303.15 (I6)
FI.D11: U1303.8 (I3), U1303.17 (I7)
FI.D12: U1304.2 (I0), U1304.11 (I4)
FI.D13: U1304.4 (I1), U1304.13 (I5)
FI.D14: U1304.6 (I2), U1304.15 (I6)
FI.D15: U1304.8 (I3), U1304.17 (I7)
FI.D16: U1305.2 (I0), U1305.11 (I4)
FI.D17: U1305.4 (I1), U1305.13 (I5)
FI.D18: U1305.6 (I2), U1305.15 (I6)
FI.D19: U1305.8 (I3), U1305.17 (I7)
FI.D20: U1306.2 (I0), U1306.11 (I4)
FI.D21: U1306.4 (I1), U1306.13 (I5)
FI.D22: U1306.6 (I2), U1306.15 (I6)
FI.D23: U1306.8 (I3), U1306.17 (I7)
FI.D24: U1307.2 (I0), U1307.11 (I4)
FI.D25: U1307.4 (I1), U1307.13 (I5)
FI.D26: U1307.6 (I2), U1307.15 (I6)
FI.D27: U1307.8 (I3), U1307.17 (I7)
FI.D28: U1308.2 (I0), U1308.11 (I4)
FI.D29: U1308.4 (I1), U1308.13 (I5)
FI.D30: U1308.6 (I2), U1308.15 (I6)
FI.D31: U1308.8 (I3), U1308.17 (I7)
FI.D32: U1309.2 (I0), U1309.11 (I4)
FI.D33: U1309.4 (I1), U1309.13 (I5)
FI.D34: U1309.6 (I2), U1309.15 (I6)
FI.D35: U1309.8 (I3), U1309.17 (I7)
FI.D36: U1310.2 (I0), U1310.11 (I4)
FI.D37: U1310.4 (I1), U1310.13 (I5)
FI.D38: U1310.6 (I2), U1310.15 (I6)
FI.D39: U1310.8 (I3), U1310.17 (I7)
FI.D40: U1311.2 (I0), U1311.11 (I4)
FI.D41: U1311.4 (I1), U1311.13 (I5)
FI.D42: U1311.6 (I2), U1311.15 (I6)
FI.D43: U1311.8 (I3), U1311.17 (I7)
FI.D44: U1312.2 (I0), U1312.11 (I4)
FI.D45: U1312.4 (I1), U1312.13 (I5)
FI.D46: U1312.6 (I2), U1312.15 (I6)
FI.D47: U1312.8 (I3), U1312.17 (I7)
FI.D48: U1313.2 (I0), U1313.11 (I4)
FI.D49: U1313.4 (I1), U1313.13 (I5)
FI.D50: U1313.6 (I2), U1313.15 (I6)
FI.D51: U1313.8 (I3), U1313.17 (I7)
FI.D52: U1314.2 (I0), U1314.11 (I4)
FI.D53: U1314.4 (I1), U1314.13 (I5)
FI.D54: U1314.6 (I2), U1314.15 (I6)
FI.D55: U1314.8 (I3), U1314.17 (I7)
FI.D56: U1315.2 (I0), U1315.11 (I4)
FI.D57: U1315.4 (I1), U1315.13 (I5)
FI.D58: U1315.6 (I2), U1315.15 (I6)
FI.D59: U1315.8 (I3), U1315.17 (I7)
FI.D60: U1316.2 (I0), U1316.11 (I4)
FI.D61: U1316.4 (I1), U1316.13 (I5)
FI.D62: U1316.6 (I2), U1316.15 (I6)
FI.D63: U1316.8 (I3), U1316.17 (I7)
FIU_TI.OE~: U1301.19 (OE1), U1302.19 (OE1), U1303.19 (OE1), U1304.19 (OE1), U1305.19 (OE1), U1306.19 (OE1), U1307.19 (OE1), U1308.19 (OE1), U1309.19 (OE1), U1310.19 (OE1), U1311.19 (OE1), U1312.19 (OE1), U1313.19 (OE1), U1314.19 (OE1), U1315.19 (OE1), U1316.19 (OE1)
FIU_VI.OE~: U1301.1 (OE0), U1302.1 (OE0), U1303.1 (OE0), U1304.1 (OE0), U1305.1 (OE0), U1306.1 (OE0), U1307.1 (OE0), U1308.1 (OE0), U1309.1 (OE0), U1310.1 (OE0), U1311.1 (OE0), U1312.1 (OE0), U1313.1 (OE0), U1314.1 (OE0), U1315.1 (OE0), U1316.1 (OE0)
TI.D0: U1301.9 (Y4)
TI.D1: U1301.7 (Y5)
TI.D2: U1301.5 (Y6)
TI.D3: U1301.3 (Y7)
TI.D4: U1302.9 (Y4)
TI.D5: U1302.7 (Y5)
TI.D6: U1302.5 (Y6)
TI.D7: U1302.3 (Y7)
TI.D8: U1303.9 (Y4)
TI.D9: U1303.7 (Y5)
TI.D10: U1303.5 (Y6)
TI.D11: U1303.3 (Y7)
TI.D12: U1304.9 (Y4)
TI.D13: U1304.7 (Y5)
TI.D14: U1304.5 (Y6)
TI.D15: U1304.3 (Y7)
TI.D16: U1305.9 (Y4)
TI.D17: U1305.7 (Y5)
TI.D18: U1305.5 (Y6)
TI.D19: U1305.3 (Y7)
TI.D20: U1306.9 (Y4)
TI.D21: U1306.7 (Y5)
TI.D22: U1306.5 (Y6)
TI.D23: U1306.3 (Y7)
TI.D24: U1307.9 (Y4)
TI.D25: U1307.7 (Y5)
TI.D26: U1307.5 (Y6)
TI.D27: U1307.3 (Y7)
TI.D28: U1308.9 (Y4)
TI.D29: U1308.7 (Y5)
TI.D30: U1308.5 (Y6)
TI.D31: U1308.3 (Y7)
TI.D32: U1309.9 (Y4)
TI.D33: U1309.7 (Y5)
TI.D34: U1309.5 (Y6)
TI.D35: U1309.3 (Y7)
TI.D36: U1310.9 (Y4)
TI.D37: U1310.7 (Y5)
TI.D38: U1310.5 (Y6)
TI.D39: U1310.3 (Y7)
TI.D40: U1311.9 (Y4)
TI.D41: U1311.7 (Y5)
TI.D42: U1311.5 (Y6)
TI.D43: U1311.3 (Y7)
TI.D44: U1312.9 (Y4)
TI.D45: U1312.7 (Y5)
TI.D46: U1312.5 (Y6)
TI.D47: U1312.3 (Y7)
TI.D48: U1313.9 (Y4)
TI.D49: U1313.7 (Y5)
TI.D50: U1313.5 (Y6)
TI.D51: U1313.3 (Y7)
TI.D52: U1314.9 (Y4)
TI.D53: U1314.7 (Y5)
TI.D54: U1314.5 (Y6)
TI.D55: U1314.3 (Y7)
TI.D56: U1315.9 (Y4)
TI.D57: U1315.7 (Y5)
TI.D58: U1315.5 (Y6)
TI.D59: U1315.3 (Y7)
TI.D60: U1316.9 (Y4)
TI.D61: U1316.7 (Y5)
TI.D62: U1316.5 (Y6)
TI.D63: U1316.3 (Y7)
VI.D0: U1301.18 (Y0)
VI.D1: U1301.16 (Y1)
VI.D2: U1301.14 (Y2)
VI.D3: U1301.12 (Y3)
VI.D4: U1302.18 (Y0)
VI.D5: U1302.16 (Y1)
VI.D6: U1302.14 (Y2)
VI.D7: U1302.12 (Y3)
VI.D8: U1303.18 (Y0)
VI.D9: U1303.16 (Y1)
VI.D10: U1303.14 (Y2)
VI.D11: U1303.12 (Y3)
VI.D12: U1304.18 (Y0)
VI.D13: U1304.16 (Y1)
VI.D14: U1304.14 (Y2)
VI.D15: U1304.12 (Y3)
VI.D16: U1305.18 (Y0)
VI.D17: U1305.16 (Y1)
VI.D18: U1305.14 (Y2)
VI.D19: U1305.12 (Y3)
VI.D20: U1306.18 (Y0)
VI.D21: U1306.16 (Y1)
VI.D22: U1306.14 (Y2)
VI.D23: U1306.12 (Y3)
VI.D24: U1307.18 (Y0)
VI.D25: U1307.16 (Y1)
VI.D26: U1307.14 (Y2)
VI.D27: U1307.12 (Y3)
VI.D28: U1308.18 (Y0)
VI.D29: U1308.16 (Y1)
VI.D30: U1308.14 (Y2)
VI.D31: U1308.12 (Y3)
VI.D32: U1309.18 (Y0)
VI.D33: U1309.16 (Y1)
VI.D34: U1309.14 (Y2)
VI.D35: U1309.12 (Y3)
VI.D36: U1310.18 (Y0)
VI.D37: U1310.16 (Y1)
VI.D38: U1310.14 (Y2)
VI.D39: U1310.12 (Y3)
VI.D40: U1311.18 (Y0)
VI.D41: U1311.16 (Y1)
VI.D42: U1311.14 (Y2)
VI.D43: U1311.12 (Y3)
VI.D44: U1312.18 (Y0)
VI.D45: U1312.16 (Y1)
VI.D46: U1312.14 (Y2)
VI.D47: U1312.12 (Y3)
VI.D48: U1313.18 (Y0)
VI.D49: U1313.16 (Y1)
VI.D50: U1313.14 (Y2)
VI.D51: U1313.12 (Y3)
VI.D52: U1314.18 (Y0)
VI.D53: U1314.16 (Y1)
VI.D54: U1314.14 (Y2)
VI.D55: U1314.12 (Y3)
VI.D56: U1315.18 (Y0)
VI.D57: U1315.16 (Y1)
VI.D58: U1315.14 (Y2)
VI.D59: U1315.12 (Y3)
VI.D60: U1316.18 (Y0)
VI.D61: U1316.16 (Y1)
VI.D62: U1316.14 (Y2)
VI.D63: U1316.12 (Y3)
