Datamuseum-DK/R1000.HwDoc/Schematics/FIU/pg_13.kicad_sch

## KiCad design Schematics/FIU/pg_13.kicad_sch (2023-01-10)

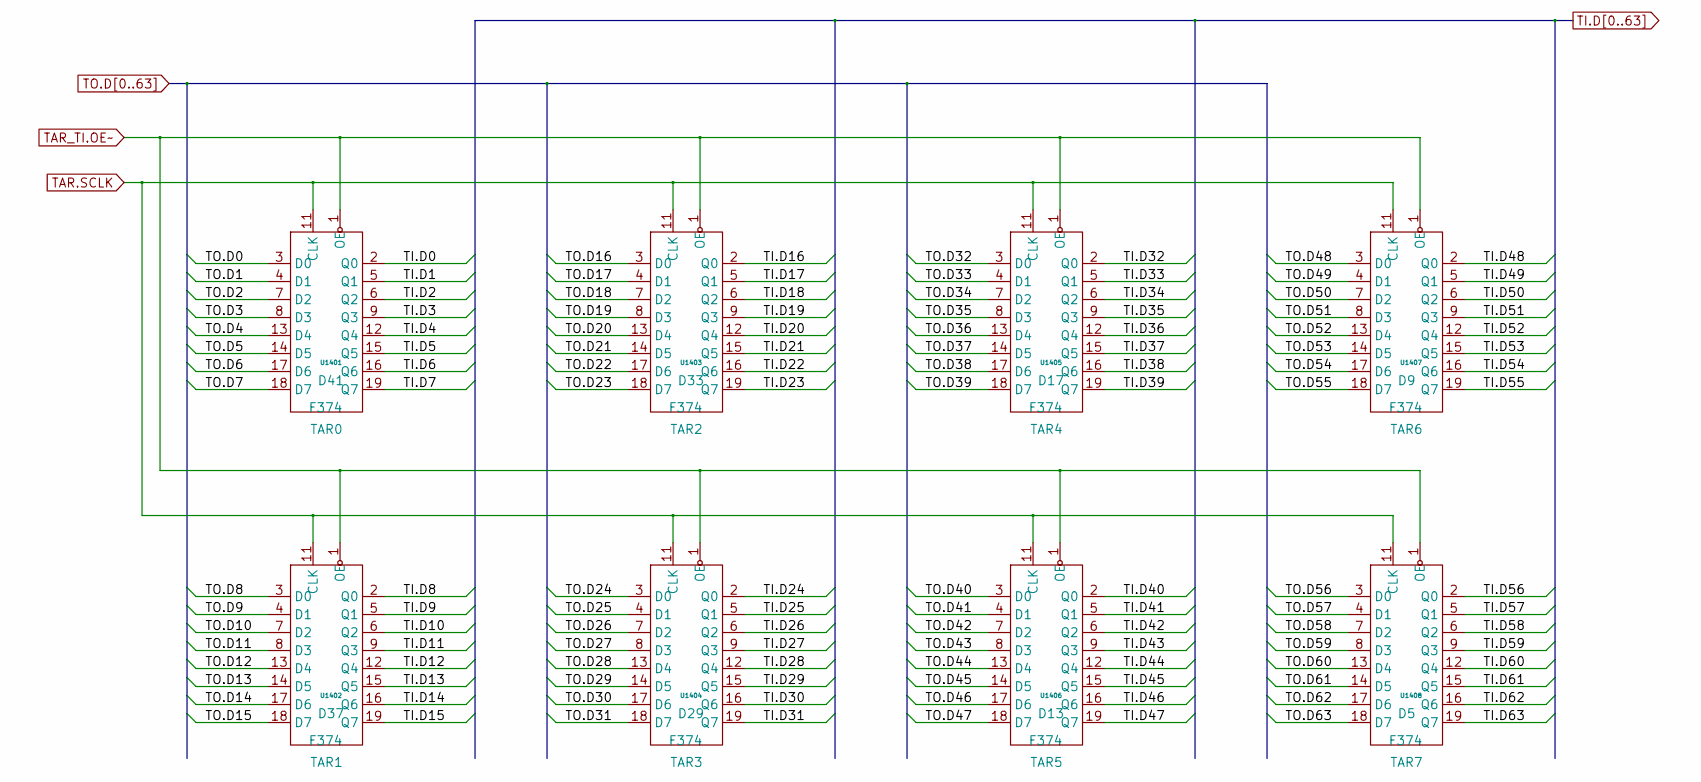
[picture p299: schematic pg_13.kicad_sch]

Parts:
U1401, U1402, U1403, U1404, U1405, U1406, U1407, U1408: F374

Connections:
TAR.SCLK: U1401.11 (CLK), U1402.11 (CLK), U1403.11 (CLK), U1404.11 (CLK), U1405.11 (CLK), U1406.11 (CLK), U1407.11 (CLK), U1408.11 (CLK)
TAR_TI.OE~: U1401.1 (OE), U1402.1 (OE), U1403.1 (OE), U1404.1 (OE), U1405.1 (OE), U1406.1 (OE), U1407.1 (OE), U1408.1 (OE)
TI.D0: U1401.2 (Q0)
TI.D1: U1401.5 (Q1)
TI.D2: U1401.6 (Q2)
TI.D3: U1401.9 (Q3)
TI.D4: U1401.12 (Q4)
TI.D5: U1401.15 (Q5)
TI.D6: U1401.16 (Q6)
TI.D7: U1401.19 (Q7)
TI.D8: U1402.2 (Q0)
TI.D9: U1402.5 (Q1)
TI.D10: U1402.6 (Q2)
TI.D11: U1402.9 (Q3)
TI.D12: U1402.12 (Q4)
TI.D13: U1402.15 (Q5)
TI.D14: U1402.16 (Q6)
TI.D15: U1402.19 (Q7)
TI.D16: U1403.2 (Q0)
TI.D17: U1403.5 (Q1)
TI.D18: U1403.6 (Q2)
TI.D19: U1403.9 (Q3)
TI.D20: U1403.12 (Q4)
TI.D21: U1403.15 (Q5)
TI.D22: U1403.16 (Q6)
TI.D23: U1403.19 (Q7)
TI.D24: U1404.2 (Q0)
TI.D25: U1404.5 (Q1)
TI.D26: U1404.6 (Q2)
TI.D27: U1404.9 (Q3)
TI.D28: U1404.12 (Q4)
TI.D29: U1404.15 (Q5)
TI.D30: U1404.16 (Q6)
TI.D31: U1404.19 (Q7)
TI.D32: U1405.2 (Q0)
TI.D33: U1405.5 (Q1)
TI.D34: U1405.6 (Q2)
TI.D35: U1405.9 (Q3)
TI.D36: U1405.12 (Q4)
TI.D37: U1405.15 (Q5)
TI.D38: U1405.16 (Q6)
TI.D39: U1405.19 (Q7)
TI.D40: U1406.2 (Q0)
TI.D41: U1406.5 (Q1)
TI.D42: U1406.6 (Q2)
TI.D43: U1406.9 (Q3)
TI.D44: U1406.12 (Q4)
TI.D45: U1406.15 (Q5)
TI.D46: U1406.16 (Q6)
TI.D47: U1406.19 (Q7)
TI.D48: U1407.2 (Q0)
TI.D49: U1407.5 (Q1)
TI.D50: U1407.6 (Q2)
TI.D51: U1407.9 (Q3)
TI.D52: U1407.12 (Q4)
TI.D53: U1407.15 (Q5)
TI.D54: U1407.16 (Q6)
TI.D55: U1407.19 (Q7)
TI.D56: U1408.2 (Q0)
TI.D57: U1408.5 (Q1)
TI.D58: U1408.6 (Q2)
TI.D59: U1408.9 (Q3)
TI.D60: U1408.12 (Q4)
TI.D61: U1408.15 (Q5)
TI.D62: U1408.16 (Q6)
TI.D63: U1408.19 (Q7)
TO.D0: U1401.3 (D0)
TO.D1: U1401.4 (D1)
TO.D2: U1401.7 (D2)
TO.D3: U1401.8 (D3)
TO.D4: U1401.13 (D4)
TO.D5: U1401.14 (D5)
TO.D6: U1401.17 (D6)
TO.D7: U1401.18 (D7)
TO.D8: U1402.3 (D0)
TO.D9: U1402.4 (D1)
TO.D10: U1402.7 (D2)
TO.D11: U1402.8 (D3)
TO.D12: U1402.13 (D4)
TO.D13: U1402.14 (D5)
TO.D14: U1402.17 (D6)
TO.D15: U1402.18 (D7)
TO.D16: U1403.3 (D0)
TO.D17: U1403.4 (D1)
TO.D18: U1403.7 (D2)
TO.D19: U1403.8 (D3)
TO.D20: U1403.13 (D4)
TO.D21: U1403.14 (D5)
TO.D22: U1403.17 (D6)
TO.D23: U1403.18 (D7)
TO.D24: U1404.3 (D0)
TO.D25: U1404.4 (D1)
TO.D26: U1404.7 (D2)
TO.D27: U1404.8 (D3)
TO.D28: U1404.13 (D4)
TO.D29: U1404.14 (D5)
TO.D30: U1404.17 (D6)
TO.D31: U1404.18 (D7)
TO.D32: U1405.3 (D0)
TO.D33: U1405.4 (D1)
TO.D34: U1405.7 (D2)
TO.D35: U1405.8 (D3)
TO.D36: U1405.13 (D4)
TO.D37: U1405.14 (D5)
TO.D38: U1405.17 (D6)
TO.D39: U1405.18 (D7)
TO.D40: U1406.3 (D0)
TO.D41: U1406.4 (D1)
TO.D42: U1406.7 (D2)
TO.D43: U1406.8 (D3)
TO.D44: U1406.13 (D4)
TO.D45: U1406.14 (D5)
TO.D46: U1406.17 (D6)
TO.D47: U1406.18 (D7)
TO.D48: U1407.3 (D0)
TO.D49: U1407.4 (D1)
TO.D50: U1407.7 (D2)
TO.D51: U1407.8 (D3)
TO.D52: U1407.13 (D4)
TO.D53: U1407.14 (D5)
TO.D54: U1407.17 (D6)
TO.D55: U1407.18 (D7)
TO.D56: U1408.3 (D0)
TO.D57: U1408.4 (D1)
TO.D58: U1408.7 (D2)
TO.D59: U1408.8 (D3)
TO.D60: U1408.13 (D4)
TO.D61: U1408.14 (D5)
TO.D62: U1408.17 (D6)
TO.D63: U1408.18 (D7)
