Datamuseum-DK/R1000.HwDoc/Schematics/FIU/pg_14.kicad_sch

## KiCad design Schematics/FIU/pg_14.kicad_sch (2023-01-10)

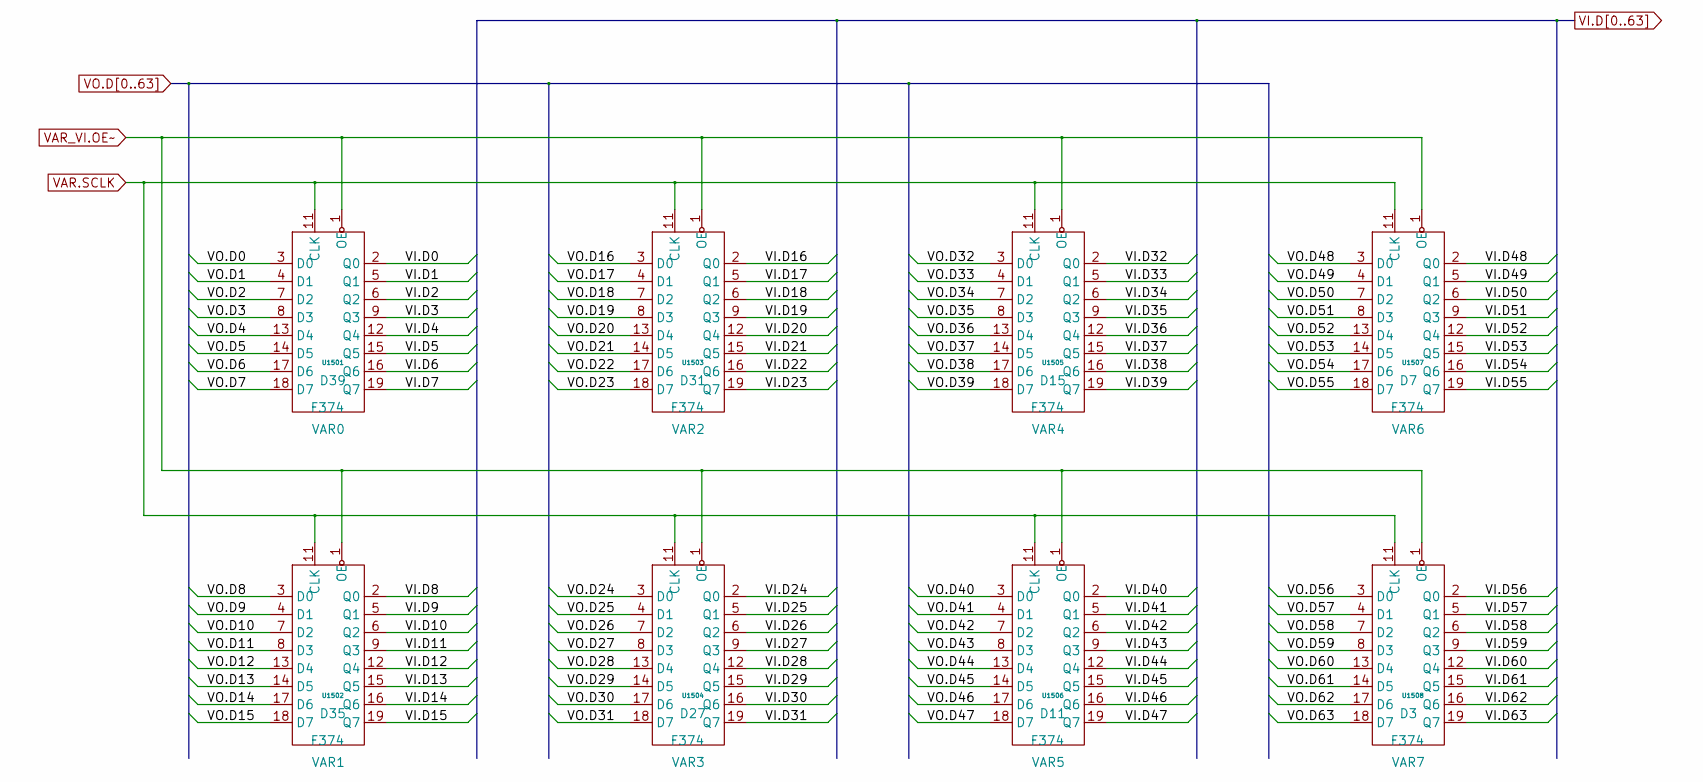
[picture p300: schematic pg_14.kicad_sch]

Parts:
U1501, U1502, U1503, U1504, U1505, U1506, U1507, U1508: F374

Connections:
VAR.SCLK: U1501.11 (CLK), U1502.11 (CLK), U1503.11 (CLK), U1504.11 (CLK), U1505.11 (CLK), U1506.11 (CLK), U1507.11 (CLK), U1508.11 (CLK)
VAR_VI.OE~: U1501.1 (OE), U1502.1 (OE), U1503.1 (OE), U1504.1 (OE), U1505.1 (OE), U1506.1 (OE), U1507.1 (OE), U1508.1 (OE)
VI.D0: U1501.2 (Q0)
VI.D1: U1501.5 (Q1)
VI.D2: U1501.6 (Q2)
VI.D3: U1501.9 (Q3)
VI.D4: U1501.12 (Q4)
VI.D5: U1501.15 (Q5)
VI.D6: U1501.16 (Q6)
VI.D7: U1501.19 (Q7)
VI.D8: U1502.2 (Q0)
VI.D9: U1502.5 (Q1)
VI.D10: U1502.6 (Q2)
VI.D11: U1502.9 (Q3)
VI.D12: U1502.12 (Q4)
VI.D13: U1502.15 (Q5)
VI.D14: U1502.16 (Q6)
VI.D15: U1502.19 (Q7)
VI.D16: U1503.2 (Q0)
VI.D17: U1503.5 (Q1)
VI.D18: U1503.6 (Q2)
VI.D19: U1503.9 (Q3)
VI.D20: U1503.12 (Q4)
VI.D21: U1503.15 (Q5)
VI.D22: U1503.16 (Q6)
VI.D23: U1503.19 (Q7)
VI.D24: U1504.2 (Q0)
VI.D25: U1504.5 (Q1)
VI.D26: U1504.6 (Q2)
VI.D27: U1504.9 (Q3)
VI.D28: U1504.12 (Q4)
VI.D29: U1504.15 (Q5)
VI.D30: U1504.16 (Q6)
VI.D31: U1504.19 (Q7)
VI.D32: U1505.2 (Q0)
VI.D33: U1505.5 (Q1)
VI.D34: U1505.6 (Q2)
VI.D35: U1505.9 (Q3)
VI.D36: U1505.12 (Q4)
VI.D37: U1505.15 (Q5)
VI.D38: U1505.16 (Q6)
VI.D39: U1505.19 (Q7)
VI.D40: U1506.2 (Q0)
VI.D41: U1506.5 (Q1)
VI.D42: U1506.6 (Q2)
VI.D43: U1506.9 (Q3)
VI.D44: U1506.12 (Q4)
VI.D45: U1506.15 (Q5)
VI.D46: U1506.16 (Q6)
VI.D47: U1506.19 (Q7)
VI.D48: U1507.2 (Q0)
VI.D49: U1507.5 (Q1)
VI.D50: U1507.6 (Q2)
VI.D51: U1507.9 (Q3)
VI.D52: U1507.12 (Q4)
VI.D53: U1507.15 (Q5)
VI.D54: U1507.16 (Q6)
VI.D55: U1507.19 (Q7)
VI.D56: U1508.2 (Q0)
VI.D57: U1508.5 (Q1)
VI.D58: U1508.6 (Q2)
VI.D59: U1508.9 (Q3)
VI.D60: U1508.12 (Q4)
VI.D61: U1508.15 (Q5)
VI.D62: U1508.16 (Q6)
VI.D63: U1508.19 (Q7)
VO.D0: U1501.3 (D0)
VO.D1: U1501.4 (D1)
VO.D2: U1501.7 (D2)
VO.D3: U1501.8 (D3)
VO.D4: U1501.13 (D4)
VO.D5: U1501.14 (D5)
VO.D6: U1501.17 (D6)
VO.D7: U1501.18 (D7)
VO.D8: U1502.3 (D0)
VO.D9: U1502.4 (D1)
VO.D10: U1502.7 (D2)
VO.D11: U1502.8 (D3)
VO.D12: U1502.13 (D4)
VO.D13: U1502.14 (D5)
VO.D14: U1502.17 (D6)
VO.D15: U1502.18 (D7)
VO.D16: U1503.3 (D0)
VO.D17: U1503.4 (D1)
VO.D18: U1503.7 (D2)
VO.D19: U1503.8 (D3)
VO.D20: U1503.13 (D4)
VO.D21: U1503.14 (D5)
VO.D22: U1503.17 (D6)
VO.D23: U1503.18 (D7)
VO.D24: U1504.3 (D0)
VO.D25: U1504.4 (D1)
VO.D26: U1504.7 (D2)
VO.D27: U1504.8 (D3)
VO.D28: U1504.13 (D4)
VO.D29: U1504.14 (D5)
VO.D30: U1504.17 (D6)
VO.D31: U1504.18 (D7)
VO.D32: U1505.3 (D0)
VO.D33: U1505.4 (D1)
VO.D34: U1505.7 (D2)
VO.D35: U1505.8 (D3)
VO.D36: U1505.13 (D4)
VO.D37: U1505.14 (D5)
VO.D38: U1505.17 (D6)
VO.D39: U1505.18 (D7)
VO.D40: U1506.3 (D0)
VO.D41: U1506.4 (D1)
VO.D42: U1506.7 (D2)
VO.D43: U1506.8 (D3)
VO.D44: U1506.13 (D4)
VO.D45: U1506.14 (D5)
VO.D46: U1506.17 (D6)
VO.D47: U1506.18 (D7)
VO.D48: U1507.3 (D0)
VO.D49: U1507.4 (D1)
VO.D50: U1507.7 (D2)
VO.D51: U1507.8 (D3)
VO.D52: U1507.13 (D4)
VO.D53: U1507.14 (D5)
VO.D54: U1507.17 (D6)
VO.D55: U1507.18 (D7)
VO.D56: U1508.3 (D0)
VO.D57: U1508.4 (D1)
VO.D58: U1508.7 (D2)
VO.D59: U1508.8 (D3)
VO.D60: U1508.13 (D4)
VO.D61: U1508.14 (D5)
VO.D62: U1508.17 (D6)
VO.D63: U1508.18 (D7)
