Datamuseum-DK/R1000.HwDoc/Schematics/FIU/pg_16.kicad_sch

## KiCad design Schematics/FIU/pg_16.kicad_sch (2023-01-10)

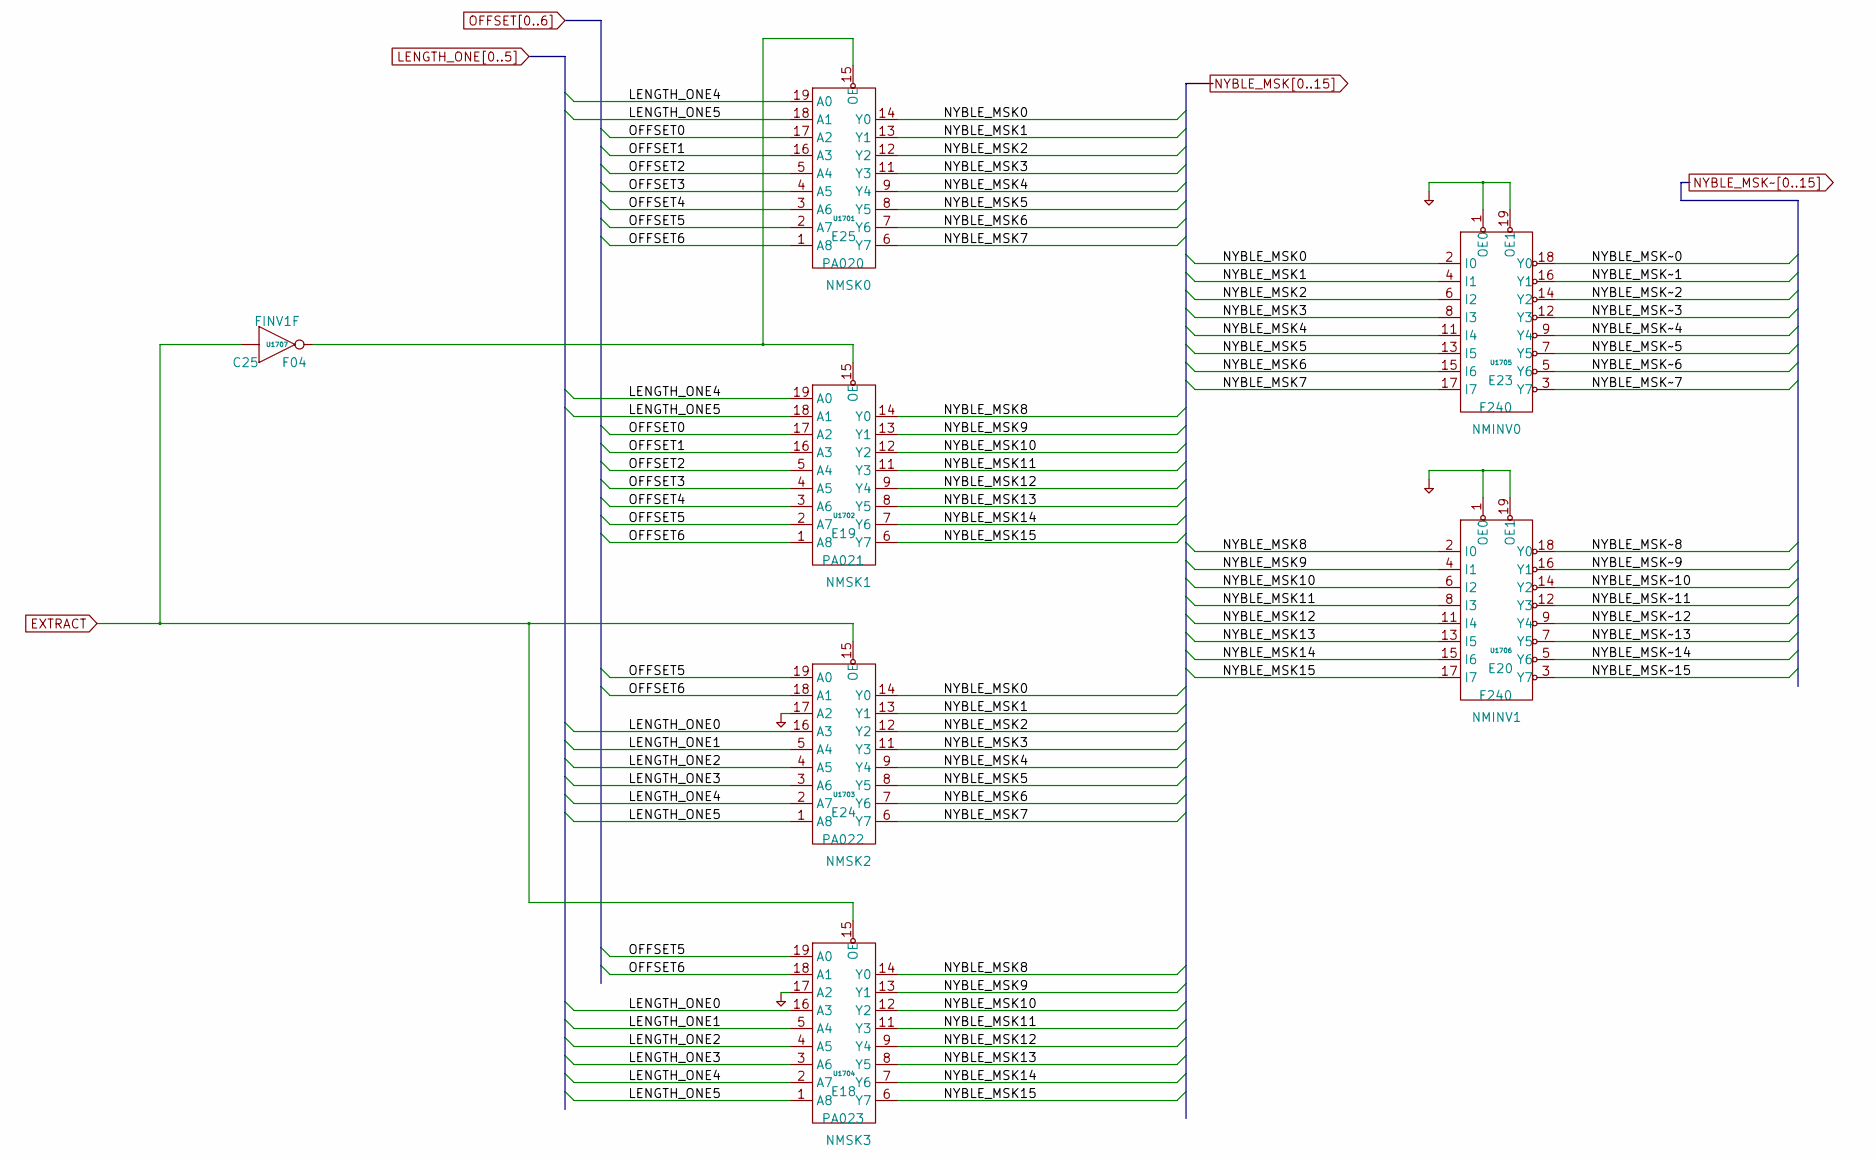
[picture p301: schematic pg_16.kicad_sch]

Parts:
U1701: PA020
U1702: PA021
U1703: PA022
U1704: PA023
U1705, U1706: F240
U1707: F04

Connections:
EXTRACT: U1703.15 (OE), U1704.15 (OE), U1707.1 (D0)
LENGTH_ONE0: U1703.16 (A3), U1704.16 (A3)
LENGTH_ONE1: U1703.5 (A4), U1704.5 (A4)
LENGTH_ONE2: U1703.4 (A5), U1704.4 (A5)
LENGTH_ONE3: U1703.3 (A6), U1704.3 (A6)
LENGTH_ONE4: U1701.19 (A0), U1702.19 (A0), U1703.2 (A7), U1704.2 (A7)
LENGTH_ONE5: U1701.18 (A1), U1702.18 (A1), U1703.1 (A8), U1704.1 (A8)
NYBLE_MSK0: U1701.14 (Y0), U1703.14 (Y0), U1705.2 (I0)
NYBLE_MSK1: U1701.13 (Y1), U1703.13 (Y1), U1705.4 (I1)
NYBLE_MSK2: U1701.12 (Y2), U1703.12 (Y2), U1705.6 (I2)
NYBLE_MSK3: U1701.11 (Y3), U1703.11 (Y3), U1705.8 (I3)
NYBLE_MSK4: U1701.9 (Y4), U1703.9 (Y4), U1705.11 (I4)
NYBLE_MSK5: U1701.8 (Y5), U1703.8 (Y5), U1705.13 (I5)
NYBLE_MSK6: U1701.7 (Y6), U1703.7 (Y6), U1705.15 (I6)
NYBLE_MSK7: U1701.6 (Y7), U1703.6 (Y7), U1705.17 (I7)
NYBLE_MSK8: U1702.14 (Y0), U1704.14 (Y0), U1706.2 (I0)
NYBLE_MSK9: U1702.13 (Y1), U1704.13 (Y1), U1706.4 (I1)
NYBLE_MSK10: U1702.12 (Y2), U1704.12 (Y2), U1706.6 (I2)
NYBLE_MSK11: U1702.11 (Y3), U1704.11 (Y3), U1706.8 (I3)
NYBLE_MSK12: U1702.9 (Y4), U1704.9 (Y4), U1706.11 (I4)
NYBLE_MSK13: U1702.8 (Y5), U1704.8 (Y5), U1706.13 (I5)
NYBLE_MSK14: U1702.7 (Y6), U1704.7 (Y6), U1706.15 (I6)
NYBLE_MSK15: U1702.6 (Y7), U1704.6 (Y7), U1706.17 (I7)
NYBLE_MSK~0: U1705.18 (Y0)
NYBLE_MSK~1: U1705.16 (Y1)
NYBLE_MSK~2: U1705.14 (Y2)
NYBLE_MSK~3: U1705.12 (Y3)
NYBLE_MSK~4: U1705.9 (Y4)
NYBLE_MSK~5: U1705.7 (Y5)
NYBLE_MSK~6: U1705.5 (Y6)
NYBLE_MSK~7: U1705.3 (Y7)
NYBLE_MSK~8: U1706.18 (Y0)
NYBLE_MSK~9: U1706.16 (Y1)
NYBLE_MSK~10: U1706.14 (Y2)
NYBLE_MSK~11: U1706.12 (Y3)
NYBLE_MSK~12: U1706.9 (Y4)
NYBLE_MSK~13: U1706.7 (Y5)
NYBLE_MSK~14: U1706.5 (Y6)
NYBLE_MSK~15: U1706.3 (Y7)
unnamed: U1701.15 (OE), U1702.15 (OE), U1707.2 (Q)
OFFSET0: U1701.17 (A2), U1702.17 (A2)
OFFSET1: U1701.16 (A3), U1702.16 (A3)
OFFSET2: U1701.5 (A4), U1702.5 (A4)
OFFSET3: U1701.4 (A5), U1702.4 (A5)
OFFSET4: U1701.3 (A6), U1702.3 (A6)
OFFSET5: U1701.2 (A7), U1702.2 (A7), U1703.19 (A0), U1704.19 (A0)
OFFSET6: U1701.1 (A8), U1702.1 (A8), U1703.18 (A1), U1704.18 (A1)
PD: U1703.17 (A2), U1704.17 (A2), U1705.1 (OE0), U1705.19 (OE1), U1706.1 (OE0), U1706.19 (OE1)
