Datamuseum-DK/R1000.HwDoc/Schematics/FIU/pg_17.kicad_sch

## KiCad design Schematics/FIU/pg_17.kicad_sch (2023-01-10)

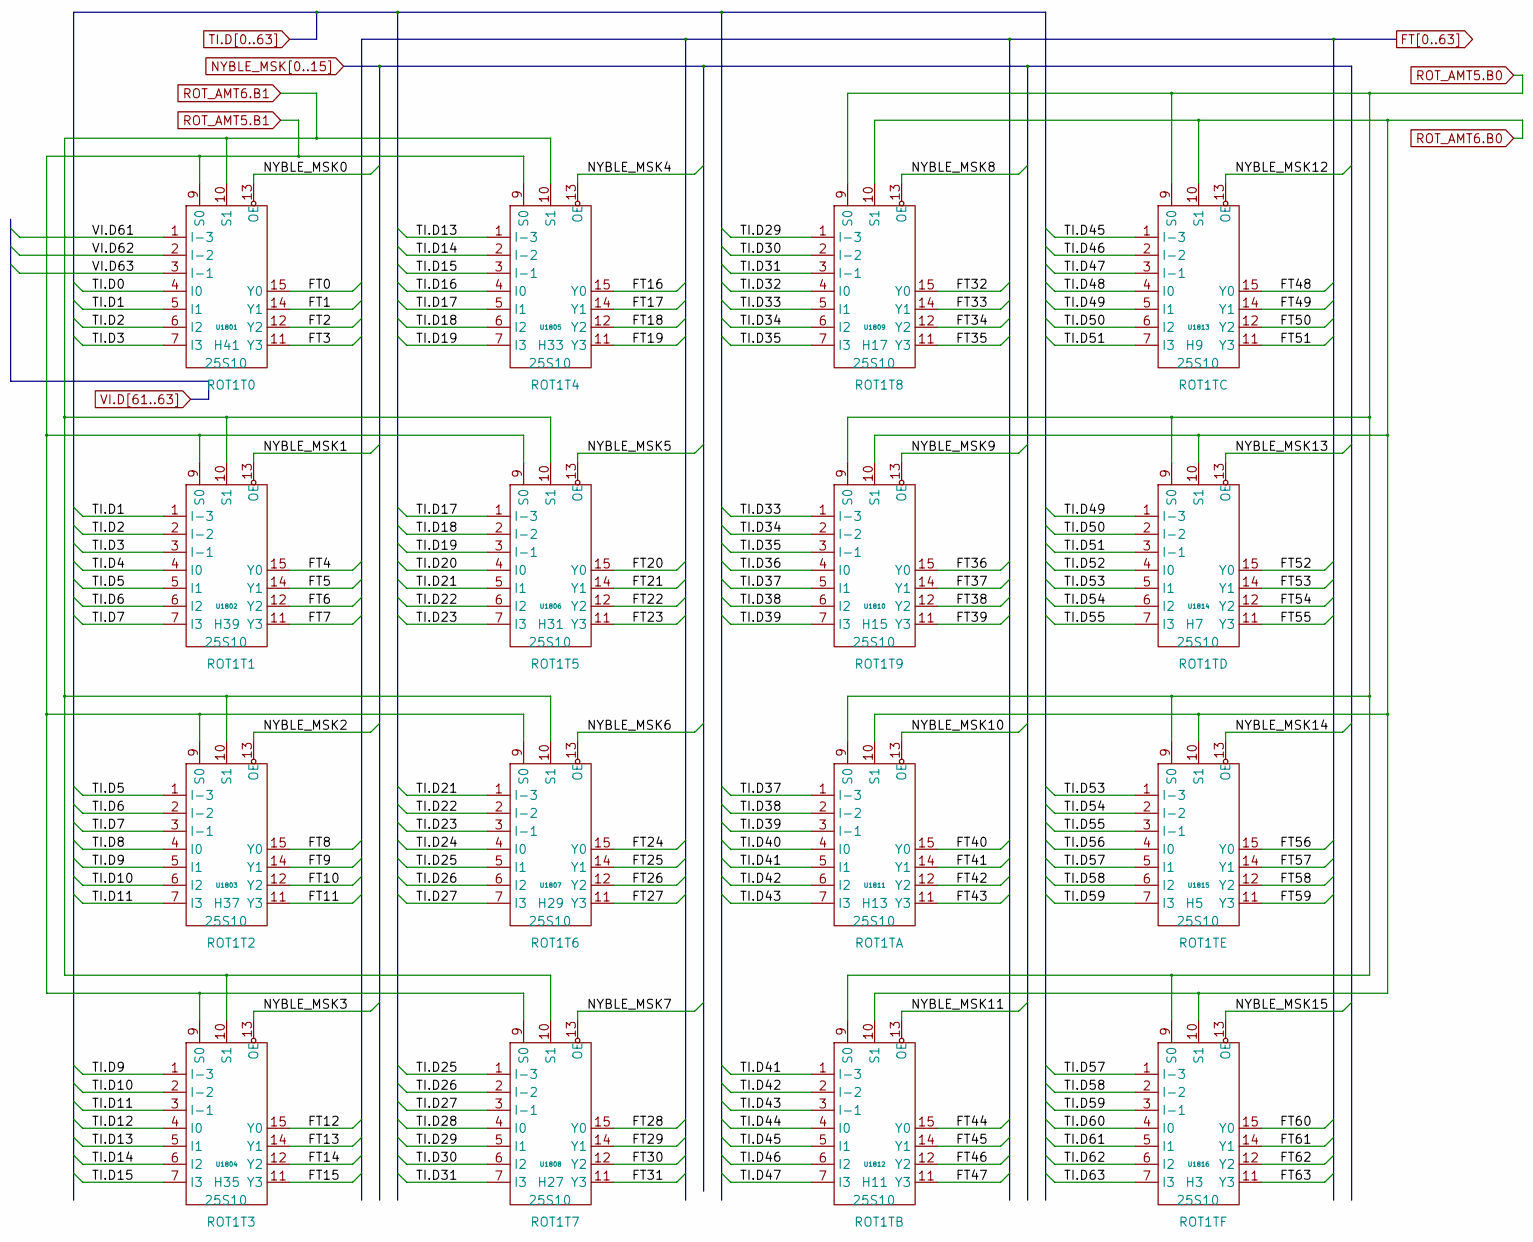
[picture p302: schematic pg_17.kicad_sch]

Parts:
U1801, U1802, U1803, U1804, U1805, U1806, U1807, U1808, U1809, U1810, U1811, U1812, U1813, U1814, U1815, U1816: 25S10

Connections:
FT0: U1801.15 (Y0)
FT1: U1801.14 (Y1)
FT2: U1801.12 (Y2)
FT3: U1801.11 (Y3)
FT4: U1802.15 (Y0)
FT5: U1802.14 (Y1)
FT6: U1802.12 (Y2)
FT7: U1802.11 (Y3)
FT8: U1803.15 (Y0)
FT9: U1803.14 (Y1)
FT10: U1803.12 (Y2)
FT11: U1803.11 (Y3)
FT12: U1804.15 (Y0)
FT13: U1804.14 (Y1)
FT14: U1804.12 (Y2)
FT15: U1804.11 (Y3)
FT16: U1805.15 (Y0)
FT17: U1805.14 (Y1)
FT18: U1805.12 (Y2)
FT19: U1805.11 (Y3)
FT20: U1806.15 (Y0)
FT21: U1806.14 (Y1)
FT22: U1806.12 (Y2)
FT23: U1806.11 (Y3)
FT24: U1807.15 (Y0)
FT25: U1807.14 (Y1)
FT26: U1807.12 (Y2)
FT27: U1807.11 (Y3)
FT28: U1808.15 (Y0)
FT29: U1808.14 (Y1)
FT30: U1808.12 (Y2)
FT31: U1808.11 (Y3)
FT32: U1809.15 (Y0)
FT33: U1809.14 (Y1)
FT34: U1809.12 (Y2)
FT35: U1809.11 (Y3)
FT36: U1810.15 (Y0)
FT37: U1810.14 (Y1)
FT38: U1810.12 (Y2)
FT39: U1810.11 (Y3)
FT40: U1811.15 (Y0)
FT41: U1811.14 (Y1)
FT42: U1811.12 (Y2)
FT43: U1811.11 (Y3)
FT44: U1812.15 (Y0)
FT45: U1812.14 (Y1)
FT46: U1812.12 (Y2)
FT47: U1812.11 (Y3)
FT48: U1813.15 (Y0)
FT49: U1813.14 (Y1)
FT50: U1813.12 (Y2)
FT51: U1813.11 (Y3)
FT52: U1814.15 (Y0)
FT53: U1814.14 (Y1)
FT54: U1814.12 (Y2)
FT55: U1814.11 (Y3)
FT56: U1815.15 (Y0)
FT57: U1815.14 (Y1)
FT58: U1815.12 (Y2)
FT59: U1815.11 (Y3)
FT60: U1816.15 (Y0)
FT61: U1816.14 (Y1)
FT62: U1816.12 (Y2)
FT63: U1816.11 (Y3)
NYBLE_MSK0: U1801.13 (OE)
NYBLE_MSK1: U1802.13 (OE)
NYBLE_MSK2: U1803.13 (OE)
NYBLE_MSK3: U1804.13 (OE)
NYBLE_MSK4: U1805.13 (OE)
NYBLE_MSK5: U1806.13 (OE)
NYBLE_MSK6: U1807.13 (OE)
NYBLE_MSK7: U1808.13 (OE)
NYBLE_MSK8: U1809.13 (OE)
NYBLE_MSK9: U1810.13 (OE)
NYBLE_MSK10: U1811.13 (OE)
NYBLE_MSK11: U1812.13 (OE)
NYBLE_MSK12: U1813.13 (OE)
NYBLE_MSK13: U1814.13 (OE)
NYBLE_MSK14: U1815.13 (OE)
NYBLE_MSK15: U1816.13 (OE)
ROT_AMT5.B0: U1809.9 (S0), U1810.9 (S0), U1811.9 (S0), U1812.9 (S0), U1813.9 (S0), U1814.9 (S0), U1815.9 (S0), U1816.9 (S0)
ROT_AMT5.B1: U1801.9 (S0), U1802.9 (S0), U1803.9 (S0), U1804.9 (S0), U1805.9 (S0), U1806.9 (S0), U1807.9 (S0), U1808.9 (S0)
ROT_AMT6.B0: U1809.10 (S1), U1810.10 (S1), U1811.10 (S1), U1812.10 (S1), U1813.10 (S1), U1814.10 (S1), U1815.10 (S1), U1816.10 (S1)
ROT_AMT6.B1: U1801.10 (S1), U1802.10 (S1), U1803.10 (S1), U1804.10 (S1), U1805.10 (S1), U1806.10 (S1), U1807.10 (S1), U1808.10 (S1)
TI.D0: U1801.4 (I0)
TI.D1: U1801.5 (I1), U1802.1 (I-3)
TI.D2: U1801.6 (I2), U1802.2 (I-2)
TI.D3: U1801.7 (I3), U1802.3 (I-1)
TI.D4: U1802.4 (I0)
TI.D5: U1802.5 (I1), U1803.1 (I-3)
TI.D6: U1802.6 (I2), U1803.2 (I-2)
TI.D7: U1802.7 (I3), U1803.3 (I-1)
TI.D8: U1803.4 (I0)
TI.D9: U1803.5 (I1), U1804.1 (I-3)
TI.D10: U1803.6 (I2), U1804.2 (I-2)
TI.D11: U1803.7 (I3), U1804.3 (I-1)
TI.D12: U1804.4 (I0)
TI.D13: U1804.5 (I1), U1805.1 (I-3)
TI.D14: U1804.6 (I2), U1805.2 (I-2)
TI.D15: U1804.7 (I3), U1805.3 (I-1)
TI.D16: U1805.4 (I0)
TI.D17: U1805.5 (I1), U1806.1 (I-3)
TI.D18: U1805.6 (I2), U1806.2 (I-2)
TI.D19: U1805.7 (I3), U1806.3 (I-1)
TI.D20: U1806.4 (I0)
TI.D21: U1806.5 (I1), U1807.1 (I-3)
TI.D22: U1806.6 (I2), U1807.2 (I-2)
TI.D23: U1806.7 (I3), U1807.3 (I-1)
TI.D24: U1807.4 (I0)
TI.D25: U1807.5 (I1), U1808.1 (I-3)
TI.D26: U1807.6 (I2), U1808.2 (I-2)
TI.D27: U1807.7 (I3), U1808.3 (I-1)
TI.D28: U1808.4 (I0)
TI.D29: U1808.5 (I1), U1809.1 (I-3)
TI.D30: U1808.6 (I2), U1809.2 (I-2)
TI.D31: U1808.7 (I3), U1809.3 (I-1)
TI.D32: U1809.4 (I0)
TI.D33: U1809.5 (I1), U1810.1 (I-3)
TI.D34: U1809.6 (I2), U1810.2 (I-2)
TI.D35: U1809.7 (I3), U1810.3 (I-1)
TI.D36: U1810.4 (I0)
TI.D37: U1810.5 (I1), U1811.1 (I-3)
TI.D38: U1810.6 (I2), U1811.2 (I-2)
TI.D39: U1810.7 (I3), U1811.3 (I-1)
TI.D40: U1811.4 (I0)
TI.D41: U1811.5 (I1), U1812.1 (I-3)
TI.D42: U1811.6 (I2), U1812.2 (I-2)
TI.D43: U1811.7 (I3), U1812.3 (I-1)
TI.D44: U1812.4 (I0)
TI.D45: U1812.5 (I1), U1813.1 (I-3)
TI.D46: U1812.6 (I2), U1813.2 (I-2)
TI.D47: U1812.7 (I3), U1813.3 (I-1)
TI.D48: U1813.4 (I0)
TI.D49: U1813.5 (I1), U1814.1 (I-3)
TI.D50: U1813.6 (I2), U1814.2 (I-2)
TI.D51: U1813.7 (I3), U1814.3 (I-1)
TI.D52: U1814.4 (I0)
TI.D53: U1814.5 (I1), U1815.1 (I-3)
TI.D54: U1814.6 (I2), U1815.2 (I-2)
TI.D55: U1814.7 (I3), U1815.3 (I-1)
TI.D56: U1815.4 (I0)
TI.D57: U1815.5 (I1), U1816.1 (I-3)
TI.D58: U1815.6 (I2), U1816.2 (I-2)
TI.D59: U1815.7 (I3), U1816.3 (I-1)
TI.D60: U1816.4 (I0)
TI.D61: U1816.5 (I1)
TI.D62: U1816.6 (I2)
TI.D63: U1816.7 (I3)
VI.D61: U1801.1 (I-3)
VI.D62: U1801.2 (I-2)
VI.D63: U1801.3 (I-1)
