Datamuseum-DK/R1000.HwDoc/Schematics/FIU/pg_18.kicad_sch

## KiCad design Schematics/FIU/pg_18.kicad_sch (2023-01-10)

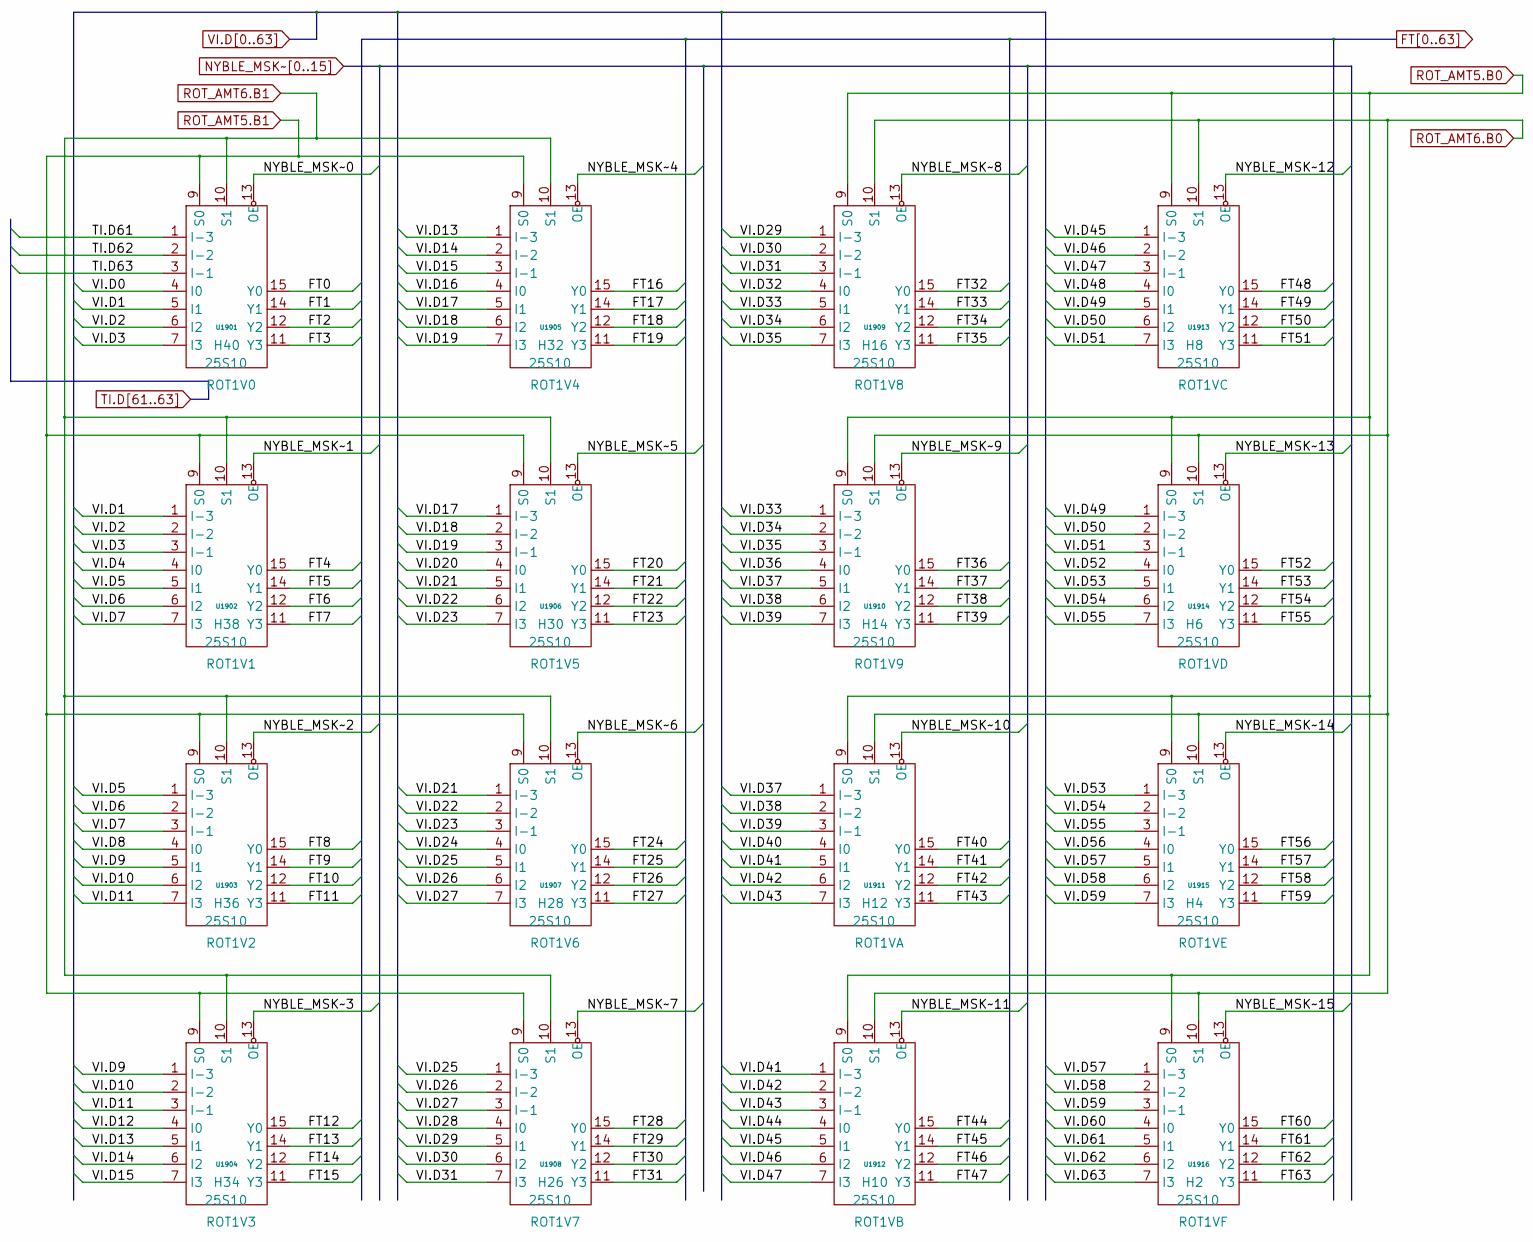
[picture p303: schematic pg_18.kicad_sch]

Parts:
U1901, U1902, U1903, U1904, U1905, U1906, U1907, U1908, U1909, U1910, U1911, U1912, U1913, U1914, U1915, U1916: 25S10

Connections:
FT0: U1901.15 (Y0)
FT1: U1901.14 (Y1)
FT2: U1901.12 (Y2)
FT3: U1901.11 (Y3)
FT4: U1902.15 (Y0)
FT5: U1902.14 (Y1)
FT6: U1902.12 (Y2)
FT7: U1902.11 (Y3)
FT8: U1903.15 (Y0)
FT9: U1903.14 (Y1)
FT10: U1903.12 (Y2)
FT11: U1903.11 (Y3)
FT12: U1904.15 (Y0)
FT13: U1904.14 (Y1)
FT14: U1904.12 (Y2)
FT15: U1904.11 (Y3)
FT16: U1905.15 (Y0)
FT17: U1905.14 (Y1)
FT18: U1905.12 (Y2)
FT19: U1905.11 (Y3)
FT20: U1906.15 (Y0)
FT21: U1906.14 (Y1)
FT22: U1906.12 (Y2)
FT23: U1906.11 (Y3)
FT24: U1907.15 (Y0)
FT25: U1907.14 (Y1)
FT26: U1907.12 (Y2)
FT27: U1907.11 (Y3)
FT28: U1908.15 (Y0)
FT29: U1908.14 (Y1)
FT30: U1908.12 (Y2)
FT31: U1908.11 (Y3)
FT32: U1909.15 (Y0)
FT33: U1909.14 (Y1)
FT34: U1909.12 (Y2)
FT35: U1909.11 (Y3)
FT36: U1910.15 (Y0)
FT37: U1910.14 (Y1)
FT38: U1910.12 (Y2)
FT39: U1910.11 (Y3)
FT40: U1911.15 (Y0)
FT41: U1911.14 (Y1)
FT42: U1911.12 (Y2)
FT43: U1911.11 (Y3)
FT44: U1912.15 (Y0)
FT45: U1912.14 (Y1)
FT46: U1912.12 (Y2)
FT47: U1912.11 (Y3)
FT48: U1913.15 (Y0)
FT49: U1913.14 (Y1)
FT50: U1913.12 (Y2)
FT51: U1913.11 (Y3)
FT52: U1914.15 (Y0)
FT53: U1914.14 (Y1)
FT54: U1914.12 (Y2)
FT55: U1914.11 (Y3)
FT56: U1915.15 (Y0)
FT57: U1915.14 (Y1)
FT58: U1915.12 (Y2)
FT59: U1915.11 (Y3)
FT60: U1916.15 (Y0)
FT61: U1916.14 (Y1)
FT62: U1916.12 (Y2)
FT63: U1916.11 (Y3)
NYBLE_MSK~0: U1901.13 (OE)
NYBLE_MSK~1: U1902.13 (OE)
NYBLE_MSK~2: U1903.13 (OE)
NYBLE_MSK~3: U1904.13 (OE)
NYBLE_MSK~4: U1905.13 (OE)
NYBLE_MSK~5: U1906.13 (OE)
NYBLE_MSK~6: U1907.13 (OE)
NYBLE_MSK~7: U1908.13 (OE)
NYBLE_MSK~8: U1909.13 (OE)
NYBLE_MSK~9: U1910.13 (OE)
NYBLE_MSK~10: U1911.13 (OE)
NYBLE_MSK~11: U1912.13 (OE)
NYBLE_MSK~12: U1913.13 (OE)
NYBLE_MSK~13: U1914.13 (OE)
NYBLE_MSK~14: U1915.13 (OE)
NYBLE_MSK~15: U1916.13 (OE)
ROT_AMT5.B0: U1909.9 (S0), U1910.9 (S0), U1911.9 (S0), U1912.9 (S0), U1913.9 (S0), U1914.9 (S0), U1915.9 (S0), U1916.9 (S0)
ROT_AMT5.B1: U1901.9 (S0), U1902.9 (S0), U1903.9 (S0), U1904.9 (S0), U1905.9 (S0), U1906.9 (S0), U1907.9 (S0), U1908.9 (S0)
ROT_AMT6.B0: U1909.10 (S1), U1910.10 (S1), U1911.10 (S1), U1912.10 (S1), U1913.10 (S1), U1914.10 (S1), U1915.10 (S1), U1916.10 (S1)
ROT_AMT6.B1: U1901.10 (S1), U1902.10 (S1), U1903.10 (S1), U1904.10 (S1), U1905.10 (S1), U1906.10 (S1), U1907.10 (S1), U1908.10 (S1)
TI.D61: U1901.1 (I-3)
TI.D62: U1901.2 (I-2)
TI.D63: U1901.3 (I-1)
VI.D0: U1901.4 (I0)
VI.D1: U1901.5 (I1), U1902.1 (I-3)
VI.D2: U1901.6 (I2), U1902.2 (I-2)
VI.D3: U1901.7 (I3), U1902.3 (I-1)
VI.D4: U1902.4 (I0)
VI.D5: U1902.5 (I1), U1903.1 (I-3)
VI.D6: U1902.6 (I2), U1903.2 (I-2)
VI.D7: U1902.7 (I3), U1903.3 (I-1)
VI.D8: U1903.4 (I0)
VI.D9: U1903.5 (I1), U1904.1 (I-3)
VI.D10: U1903.6 (I2), U1904.2 (I-2)
VI.D11: U1903.7 (I3), U1904.3 (I-1)
VI.D12: U1904.4 (I0)
VI.D13: U1904.5 (I1), U1905.1 (I-3)
VI.D14: U1904.6 (I2), U1905.2 (I-2)
VI.D15: U1904.7 (I3), U1905.3 (I-1)
VI.D16: U1905.4 (I0)
VI.D17: U1905.5 (I1), U1906.1 (I-3)
VI.D18: U1905.6 (I2), U1906.2 (I-2)
VI.D19: U1905.7 (I3), U1906.3 (I-1)
VI.D20: U1906.4 (I0)
VI.D21: U1906.5 (I1), U1907.1 (I-3)
VI.D22: U1906.6 (I2), U1907.2 (I-2)
VI.D23: U1906.7 (I3), U1907.3 (I-1)
VI.D24: U1907.4 (I0)
VI.D25: U1907.5 (I1), U1908.1 (I-3)
VI.D26: U1907.6 (I2), U1908.2 (I-2)
VI.D27: U1907.7 (I3), U1908.3 (I-1)
VI.D28: U1908.4 (I0)
VI.D29: U1908.5 (I1), U1909.1 (I-3)
VI.D30: U1908.6 (I2), U1909.2 (I-2)
VI.D31: U1908.7 (I3), U1909.3 (I-1)
VI.D32: U1909.4 (I0)
VI.D33: U1909.5 (I1), U1910.1 (I-3)
VI.D34: U1909.6 (I2), U1910.2 (I-2)
VI.D35: U1909.7 (I3), U1910.3 (I-1)
VI.D36: U1910.4 (I0)
VI.D37: U1910.5 (I1), U1911.1 (I-3)
VI.D38: U1910.6 (I2), U1911.2 (I-2)
VI.D39: U1910.7 (I3), U1911.3 (I-1)
VI.D40: U1911.4 (I0)
VI.D41: U1911.5 (I1), U1912.1 (I-3)
VI.D42: U1911.6 (I2), U1912.2 (I-2)
VI.D43: U1911.7 (I3), U1912.3 (I-1)
VI.D44: U1912.4 (I0)
VI.D45: U1912.5 (I1), U1913.1 (I-3)
VI.D46: U1912.6 (I2), U1913.2 (I-2)
VI.D47: U1912.7 (I3), U1913.3 (I-1)
VI.D48: U1913.4 (I0)
VI.D49: U1913.5 (I1), U1914.1 (I-3)
VI.D50: U1913.6 (I2), U1914.2 (I-2)
VI.D51: U1913.7 (I3), U1914.3 (I-1)
VI.D52: U1914.4 (I0)
VI.D53: U1914.5 (I1), U1915.1 (I-3)
VI.D54: U1914.6 (I2), U1915.2 (I-2)
VI.D55: U1914.7 (I3), U1915.3 (I-1)
VI.D56: U1915.4 (I0)
VI.D57: U1915.5 (I1), U1916.1 (I-3)
VI.D58: U1915.6 (I2), U1916.2 (I-2)
VI.D59: U1915.7 (I3), U1916.3 (I-1)
VI.D60: U1916.4 (I0)
VI.D61: U1916.5 (I1)
VI.D62: U1916.6 (I2)
VI.D63: U1916.7 (I3)
