Datamuseum-DK/R1000.HwDoc/Schematics/FIU/pg_19.kicad_sch

## KiCad design Schematics/FIU/pg_19.kicad_sch (2023-01-10)

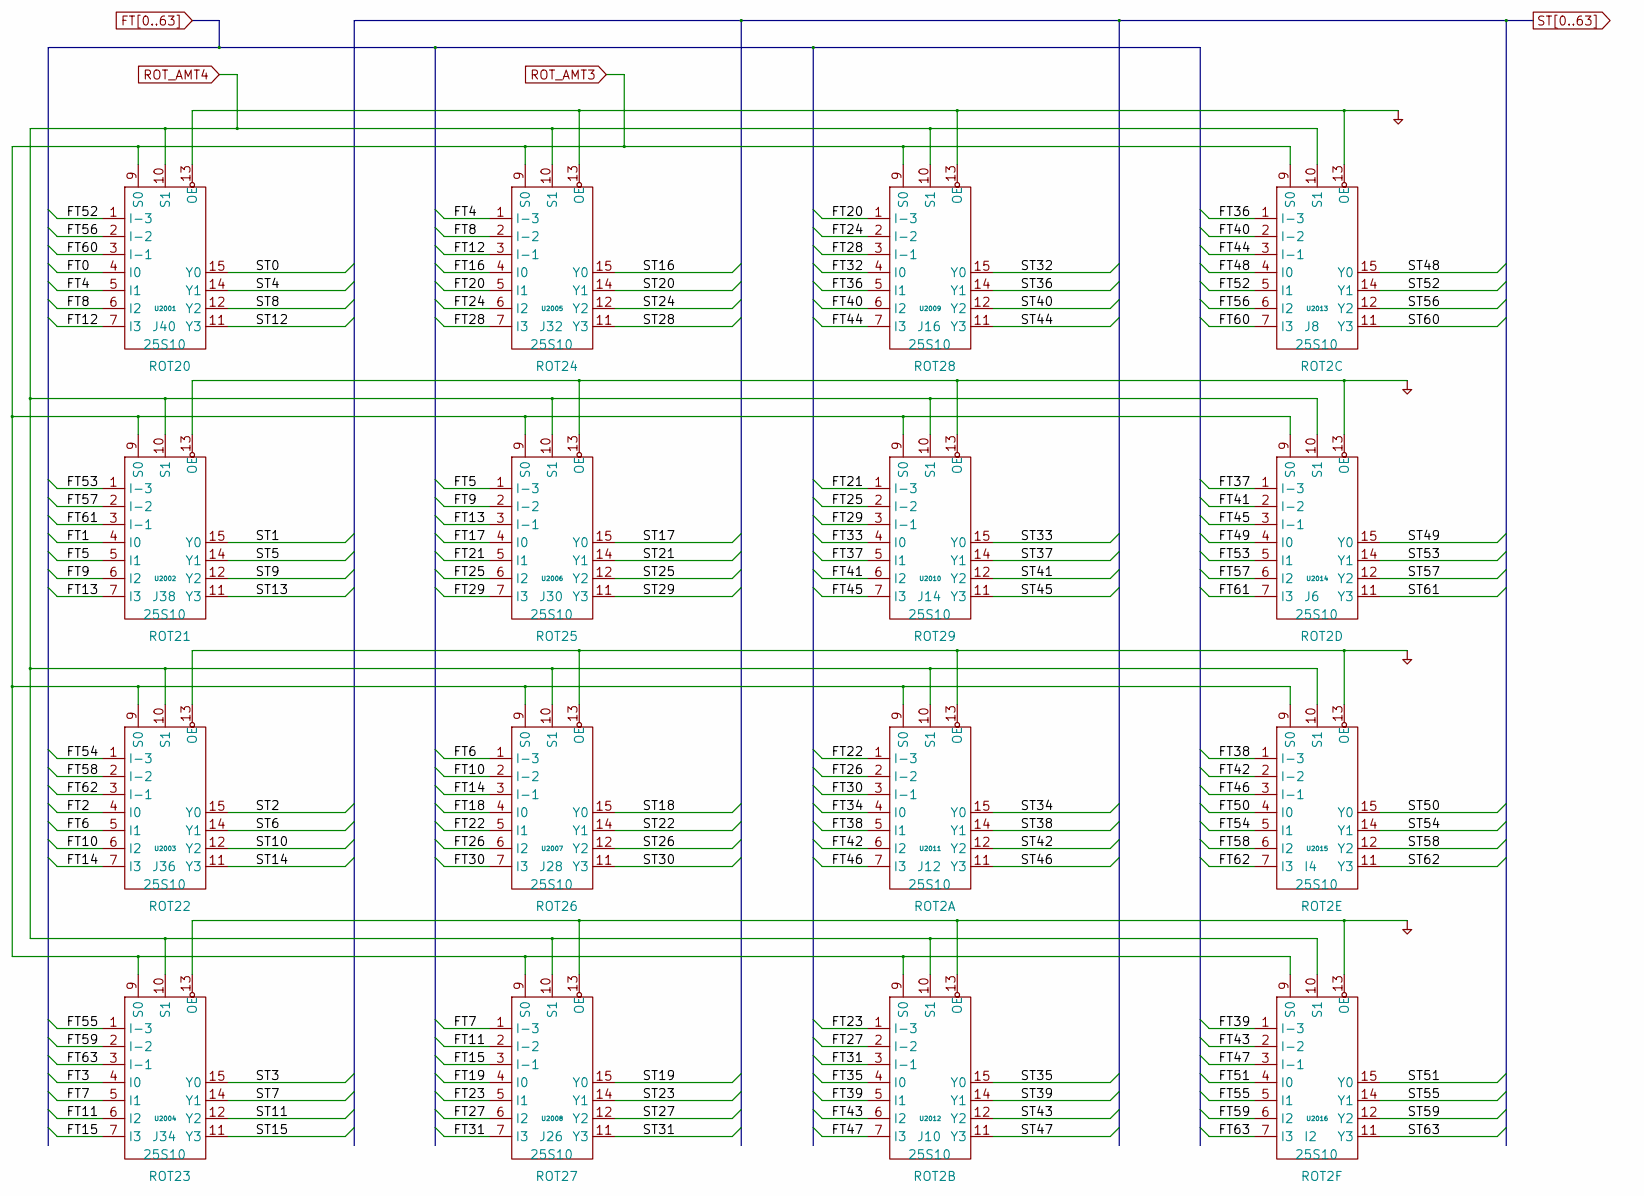
[picture p304: schematic pg_19.kicad_sch]

Parts:
U2001, U2002, U2003, U2004, U2005, U2006, U2007, U2008, U2009, U2010, U2011, U2012, U2013, U2014, U2015, U2016: 25S10

Connections:
FT0: U2001.4 (I0)
FT1: U2002.4 (I0)
FT2: U2003.4 (I0)
FT3: U2004.4 (I0)
FT4: U2001.5 (I1), U2005.1 (I-3)
FT5: U2002.5 (I1), U2006.1 (I-3)
FT6: U2003.5 (I1), U2007.1 (I-3)
FT7: U2004.5 (I1), U2008.1 (I-3)
FT8: U2001.6 (I2), U2005.2 (I-2)
FT9: U2002.6 (I2), U2006.2 (I-2)
FT10: U2003.6 (I2), U2007.2 (I-2)
FT11: U2004.6 (I2), U2008.2 (I-2)
FT12: U2001.7 (I3), U2005.3 (I-1)
FT13: U2002.7 (I3), U2006.3 (I-1)
FT14: U2003.7 (I3), U2007.3 (I-1)
FT15: U2004.7 (I3), U2008.3 (I-1)
FT16: U2005.4 (I0)
FT17: U2006.4 (I0)
FT18: U2007.4 (I0)
FT19: U2008.4 (I0)
FT20: U2005.5 (I1), U2009.1 (I-3)
FT21: U2006.5 (I1), U2010.1 (I-3)
FT22: U2007.5 (I1), U2011.1 (I-3)
FT23: U2008.5 (I1), U2012.1 (I-3)
FT24: U2005.6 (I2), U2009.2 (I-2)
FT25: U2006.6 (I2), U2010.2 (I-2)
FT26: U2007.6 (I2), U2011.2 (I-2)
FT27: U2008.6 (I2), U2012.2 (I-2)
FT28: U2005.7 (I3), U2009.3 (I-1)
FT29: U2006.7 (I3), U2010.3 (I-1)
FT30: U2007.7 (I3), U2011.3 (I-1)
FT31: U2008.7 (I3), U2012.3 (I-1)
FT32: U2009.4 (I0)
FT33: U2010.4 (I0)
FT34: U2011.4 (I0)
FT35: U2012.4 (I0)
FT36: U2009.5 (I1), U2013.1 (I-3)
FT37: U2010.5 (I1), U2014.1 (I-3)
FT38: U2011.5 (I1), U2015.1 (I-3)
FT39: U2012.5 (I1), U2016.1 (I-3)
FT40: U2009.6 (I2), U2013.2 (I-2)
FT41: U2010.6 (I2), U2014.2 (I-2)
FT42: U2011.6 (I2), U2015.2 (I-2)
FT43: U2012.6 (I2), U2016.2 (I-2)
FT44: U2009.7 (I3), U2013.3 (I-1)
FT45: U2010.7 (I3), U2014.3 (I-1)
FT46: U2011.7 (I3), U2015.3 (I-1)
FT47: U2012.7 (I3), U2016.3 (I-1)
FT48: U2013.4 (I0)
FT49: U2014.4 (I0)
FT50: U2015.4 (I0)
FT51: U2016.4 (I0)
FT52: U2001.1 (I-3), U2013.5 (I1)
FT53: U2002.1 (I-3), U2014.5 (I1)
FT54: U2003.1 (I-3), U2015.5 (I1)
FT55: U2004.1 (I-3), U2016.5 (I1)
FT56: U2001.2 (I-2), U2013.6 (I2)
FT57: U2002.2 (I-2), U2014.6 (I2)
FT58: U2003.2 (I-2), U2015.6 (I2)
FT59: U2004.2 (I-2), U2016.6 (I2)
FT60: U2001.3 (I-1), U2013.7 (I3)
FT61: U2002.3 (I-1), U2014.7 (I3)
FT62: U2003.3 (I-1), U2015.7 (I3)
FT63: U2004.3 (I-1), U2016.7 (I3)
PD: U2001.13 (OE), U2002.13 (OE), U2003.13 (OE), U2004.13 (OE), U2005.13 (OE), U2006.13 (OE), U2007.13 (OE), U2008.13 (OE), U2009.13 (OE), U2010.13 (OE), U2011.13 (OE), U2012.13 (OE), U2013.13 (OE), U2014.13 (OE), U2015.13 (OE), U2016.13 (OE)
ROT_AMT3: U2001.9 (S0), U2002.9 (S0), U2003.9 (S0), U2004.9 (S0), U2005.9 (S0), U2006.9 (S0), U2007.9 (S0), U2008.9 (S0), U2009.9 (S0), U2010.9 (S0), U2011.9 (S0), U2012.9 (S0), U2013.9 (S0), U2014.9 (S0), U2015.9 (S0), U2016.9 (S0)
ROT_AMT4: U2001.10 (S1), U2002.10 (S1), U2003.10 (S1), U2004.10 (S1), U2005.10 (S1), U2006.10 (S1), U2007.10 (S1), U2008.10 (S1), U2009.10 (S1), U2010.10 (S1), U2011.10 (S1), U2012.10 (S1), U2013.10 (S1), U2014.10 (S1), U2015.10 (S1), U2016.10 (S1)
ST0: U2001.15 (Y0)
ST1: U2002.15 (Y0)
ST2: U2003.15 (Y0)
ST3: U2004.15 (Y0)
ST4: U2001.14 (Y1)
ST5: U2002.14 (Y1)
ST6: U2003.14 (Y1)
ST7: U2004.14 (Y1)
ST8: U2001.12 (Y2)
ST9: U2002.12 (Y2)
ST10: U2003.12 (Y2)
ST11: U2004.12 (Y2)
ST12: U2001.11 (Y3)
ST13: U2002.11 (Y3)
ST14: U2003.11 (Y3)
ST15: U2004.11 (Y3)
ST16: U2005.15 (Y0)
ST17: U2006.15 (Y0)
ST18: U2007.15 (Y0)
ST19: U2008.15 (Y0)
ST20: U2005.14 (Y1)
ST21: U2006.14 (Y1)
ST22: U2007.14 (Y1)
ST23: U2008.14 (Y1)
ST24: U2005.12 (Y2)
ST25: U2006.12 (Y2)
ST26: U2007.12 (Y2)
ST27: U2008.12 (Y2)
ST28: U2005.11 (Y3)
ST29: U2006.11 (Y3)
ST30: U2007.11 (Y3)
ST31: U2008.11 (Y3)
ST32: U2009.15 (Y0)
ST33: U2010.15 (Y0)
ST34: U2011.15 (Y0)
ST35: U2012.15 (Y0)
ST36: U2009.14 (Y1)
ST37: U2010.14 (Y1)
ST38: U2011.14 (Y1)
ST39: U2012.14 (Y1)
ST40: U2009.12 (Y2)
ST41: U2010.12 (Y2)
ST42: U2011.12 (Y2)
ST43: U2012.12 (Y2)
ST44: U2009.11 (Y3)
ST45: U2010.11 (Y3)
ST46: U2011.11 (Y3)
ST47: U2012.11 (Y3)
ST48: U2013.15 (Y0)
ST49: U2014.15 (Y0)
ST50: U2015.15 (Y0)
ST51: U2016.15 (Y0)
ST52: U2013.14 (Y1)
ST53: U2014.14 (Y1)
ST54: U2015.14 (Y1)
ST55: U2016.14 (Y1)
ST56: U2013.12 (Y2)
ST57: U2014.12 (Y2)
ST58: U2015.12 (Y2)
ST59: U2016.12 (Y2)
ST60: U2013.11 (Y3)
ST61: U2014.11 (Y3)
ST62: U2015.11 (Y3)
ST63: U2016.11 (Y3)
