Datamuseum-DK/R1000.HwDoc/Schematics/FIU/pg_20.kicad_sch

## KiCad design Schematics/FIU/pg_20.kicad_sch (2023-01-10)

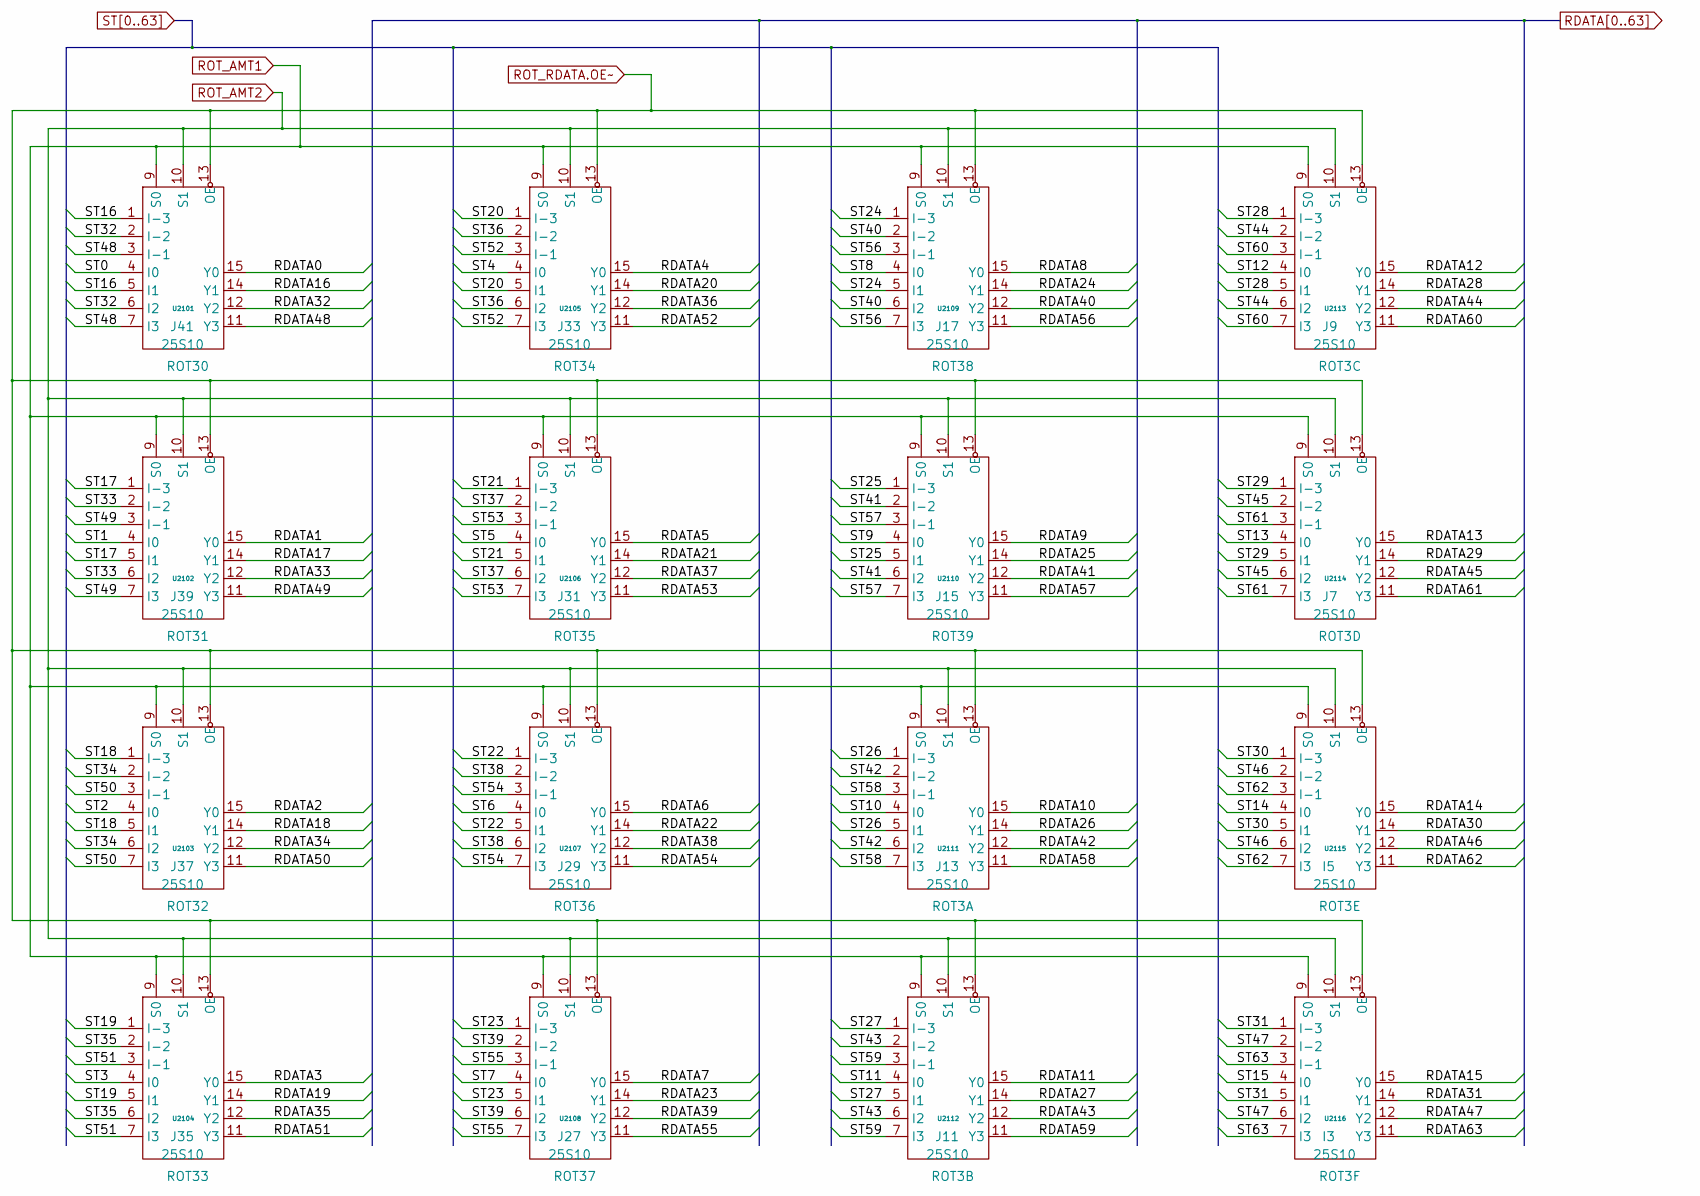
[picture p305: schematic pg_20.kicad_sch]

Parts:
U2101, U2102, U2103, U2104, U2105, U2106, U2107, U2108, U2109, U2110, U2111, U2112, U2113, U2114, U2115, U2116: 25S10

Connections:
RDATA0: U2101.15 (Y0)
RDATA1: U2102.15 (Y0)
RDATA2: U2103.15 (Y0)
RDATA3: U2104.15 (Y0)
RDATA4: U2105.15 (Y0)
RDATA5: U2106.15 (Y0)
RDATA6: U2107.15 (Y0)
RDATA7: U2108.15 (Y0)
RDATA8: U2109.15 (Y0)
RDATA9: U2110.15 (Y0)
RDATA10: U2111.15 (Y0)
RDATA11: U2112.15 (Y0)
RDATA12: U2113.15 (Y0)
RDATA13: U2114.15 (Y0)
RDATA14: U2115.15 (Y0)
RDATA15: U2116.15 (Y0)
RDATA16: U2101.14 (Y1)
RDATA17: U2102.14 (Y1)
RDATA18: U2103.14 (Y1)
RDATA19: U2104.14 (Y1)
RDATA20: U2105.14 (Y1)
RDATA21: U2106.14 (Y1)
RDATA22: U2107.14 (Y1)
RDATA23: U2108.14 (Y1)
RDATA24: U2109.14 (Y1)
RDATA25: U2110.14 (Y1)
RDATA26: U2111.14 (Y1)
RDATA27: U2112.14 (Y1)
RDATA28: U2113.14 (Y1)
RDATA29: U2114.14 (Y1)
RDATA30: U2115.14 (Y1)
RDATA31: U2116.14 (Y1)
RDATA32: U2101.12 (Y2)
RDATA33: U2102.12 (Y2)
RDATA34: U2103.12 (Y2)
RDATA35: U2104.12 (Y2)
RDATA36: U2105.12 (Y2)
RDATA37: U2106.12 (Y2)
RDATA38: U2107.12 (Y2)
RDATA39: U2108.12 (Y2)
RDATA40: U2109.12 (Y2)
RDATA41: U2110.12 (Y2)
RDATA42: U2111.12 (Y2)
RDATA43: U2112.12 (Y2)
RDATA44: U2113.12 (Y2)
RDATA45: U2114.12 (Y2)
RDATA46: U2115.12 (Y2)
RDATA47: U2116.12 (Y2)
RDATA48: U2101.11 (Y3)
RDATA49: U2102.11 (Y3)
RDATA50: U2103.11 (Y3)
RDATA51: U2104.11 (Y3)
RDATA52: U2105.11 (Y3)
RDATA53: U2106.11 (Y3)
RDATA54: U2107.11 (Y3)
RDATA55: U2108.11 (Y3)
RDATA56: U2109.11 (Y3)
RDATA57: U2110.11 (Y3)
RDATA58: U2111.11 (Y3)
RDATA59: U2112.11 (Y3)
RDATA60: U2113.11 (Y3)
RDATA61: U2114.11 (Y3)
RDATA62: U2115.11 (Y3)
RDATA63: U2116.11 (Y3)
ROT_AMT1: U2101.9 (S0), U2102.9 (S0), U2103.9 (S0), U2104.9 (S0), U2105.9 (S0), U2106.9 (S0), U2107.9 (S0), U2108.9 (S0), U2109.9 (S0), U2110.9 (S0), U2111.9 (S0), U2112.9 (S0), U2113.9 (S0), U2114.9 (S0), U2115.9 (S0), U2116.9 (S0)
ROT_AMT2: U2101.10 (S1), U2102.10 (S1), U2103.10 (S1), U2104.10 (S1), U2105.10 (S1), U2106.10 (S1), U2107.10 (S1), U2108.10 (S1), U2109.10 (S1), U2110.10 (S1), U2111.10 (S1), U2112.10 (S1), U2113.10 (S1), U2114.10 (S1), U2115.10 (S1), U2116.10 (S1)
ROT_RDATA.OE~: U2101.13 (OE), U2102.13 (OE), U2103.13 (OE), U2104.13 (OE), U2105.13 (OE), U2106.13 (OE), U2107.13 (OE), U2108.13 (OE), U2109.13 (OE), U2110.13 (OE), U2111.13 (OE), U2112.13 (OE), U2113.13 (OE), U2114.13 (OE), U2115.13 (OE), U2116.13 (OE)
ST0: U2101.4 (I0)
ST1: U2102.4 (I0)
ST2: U2103.4 (I0)
ST3: U2104.4 (I0)
ST4: U2105.4 (I0)
ST5: U2106.4 (I0)
ST6: U2107.4 (I0)
ST7: U2108.4 (I0)
ST8: U2109.4 (I0)
ST9: U2110.4 (I0)
ST10: U2111.4 (I0)
ST11: U2112.4 (I0)
ST12: U2113.4 (I0)
ST13: U2114.4 (I0)
ST14: U2115.4 (I0)
ST15: U2116.4 (I0)
ST16: U2101.1 (I-3), U2101.5 (I1)
ST17: U2102.1 (I-3), U2102.5 (I1)
ST18: U2103.1 (I-3), U2103.5 (I1)
ST19: U2104.1 (I-3), U2104.5 (I1)
ST20: U2105.1 (I-3), U2105.5 (I1)
ST21: U2106.1 (I-3), U2106.5 (I1)
ST22: U2107.1 (I-3), U2107.5 (I1)
ST23: U2108.1 (I-3), U2108.5 (I1)
ST24: U2109.1 (I-3), U2109.5 (I1)
ST25: U2110.1 (I-3), U2110.5 (I1)
ST26: U2111.1 (I-3), U2111.5 (I1)
ST27: U2112.1 (I-3), U2112.5 (I1)
ST28: U2113.1 (I-3), U2113.5 (I1)
ST29: U2114.1 (I-3), U2114.5 (I1)
ST30: U2115.1 (I-3), U2115.5 (I1)
ST31: U2116.1 (I-3), U2116.5 (I1)
ST32: U2101.2 (I-2), U2101.6 (I2)
ST33: U2102.2 (I-2), U2102.6 (I2)
ST34: U2103.2 (I-2), U2103.6 (I2)
ST35: U2104.2 (I-2), U2104.6 (I2)
ST36: U2105.2 (I-2), U2105.6 (I2)
ST37: U2106.2 (I-2), U2106.6 (I2)
ST38: U2107.2 (I-2), U2107.6 (I2)
ST39: U2108.2 (I-2), U2108.6 (I2)
ST40: U2109.2 (I-2), U2109.6 (I2)
ST41: U2110.2 (I-2), U2110.6 (I2)
ST42: U2111.2 (I-2), U2111.6 (I2)
ST43: U2112.2 (I-2), U2112.6 (I2)
ST44: U2113.2 (I-2), U2113.6 (I2)
ST45: U2114.2 (I-2), U2114.6 (I2)
ST46: U2115.2 (I-2), U2115.6 (I2)
ST47: U2116.2 (I-2), U2116.6 (I2)
ST48: U2101.3 (I-1), U2101.7 (I3)
ST49: U2102.3 (I-1), U2102.7 (I3)
ST50: U2103.3 (I-1), U2103.7 (I3)
ST51: U2104.3 (I-1), U2104.7 (I3)
ST52: U2105.3 (I-1), U2105.7 (I3)
ST53: U2106.3 (I-1), U2106.7 (I3)
ST54: U2107.3 (I-1), U2107.7 (I3)
ST55: U2108.3 (I-1), U2108.7 (I3)
ST56: U2109.3 (I-1), U2109.7 (I3)
ST57: U2110.3 (I-1), U2110.7 (I3)
ST58: U2111.3 (I-1), U2111.7 (I3)
ST59: U2112.3 (I-1), U2112.7 (I3)
ST60: U2113.3 (I-1), U2113.7 (I3)
ST61: U2114.3 (I-1), U2114.7 (I3)
ST62: U2115.3 (I-1), U2115.7 (I3)
ST63: U2116.3 (I-1), U2116.7 (I3)
