Datamuseum-DK/R1000.HwDoc/Schematics/FIU/pg_21.kicad_sch

## KiCad design Schematics/FIU/pg_21.kicad_sch (2023-01-10)

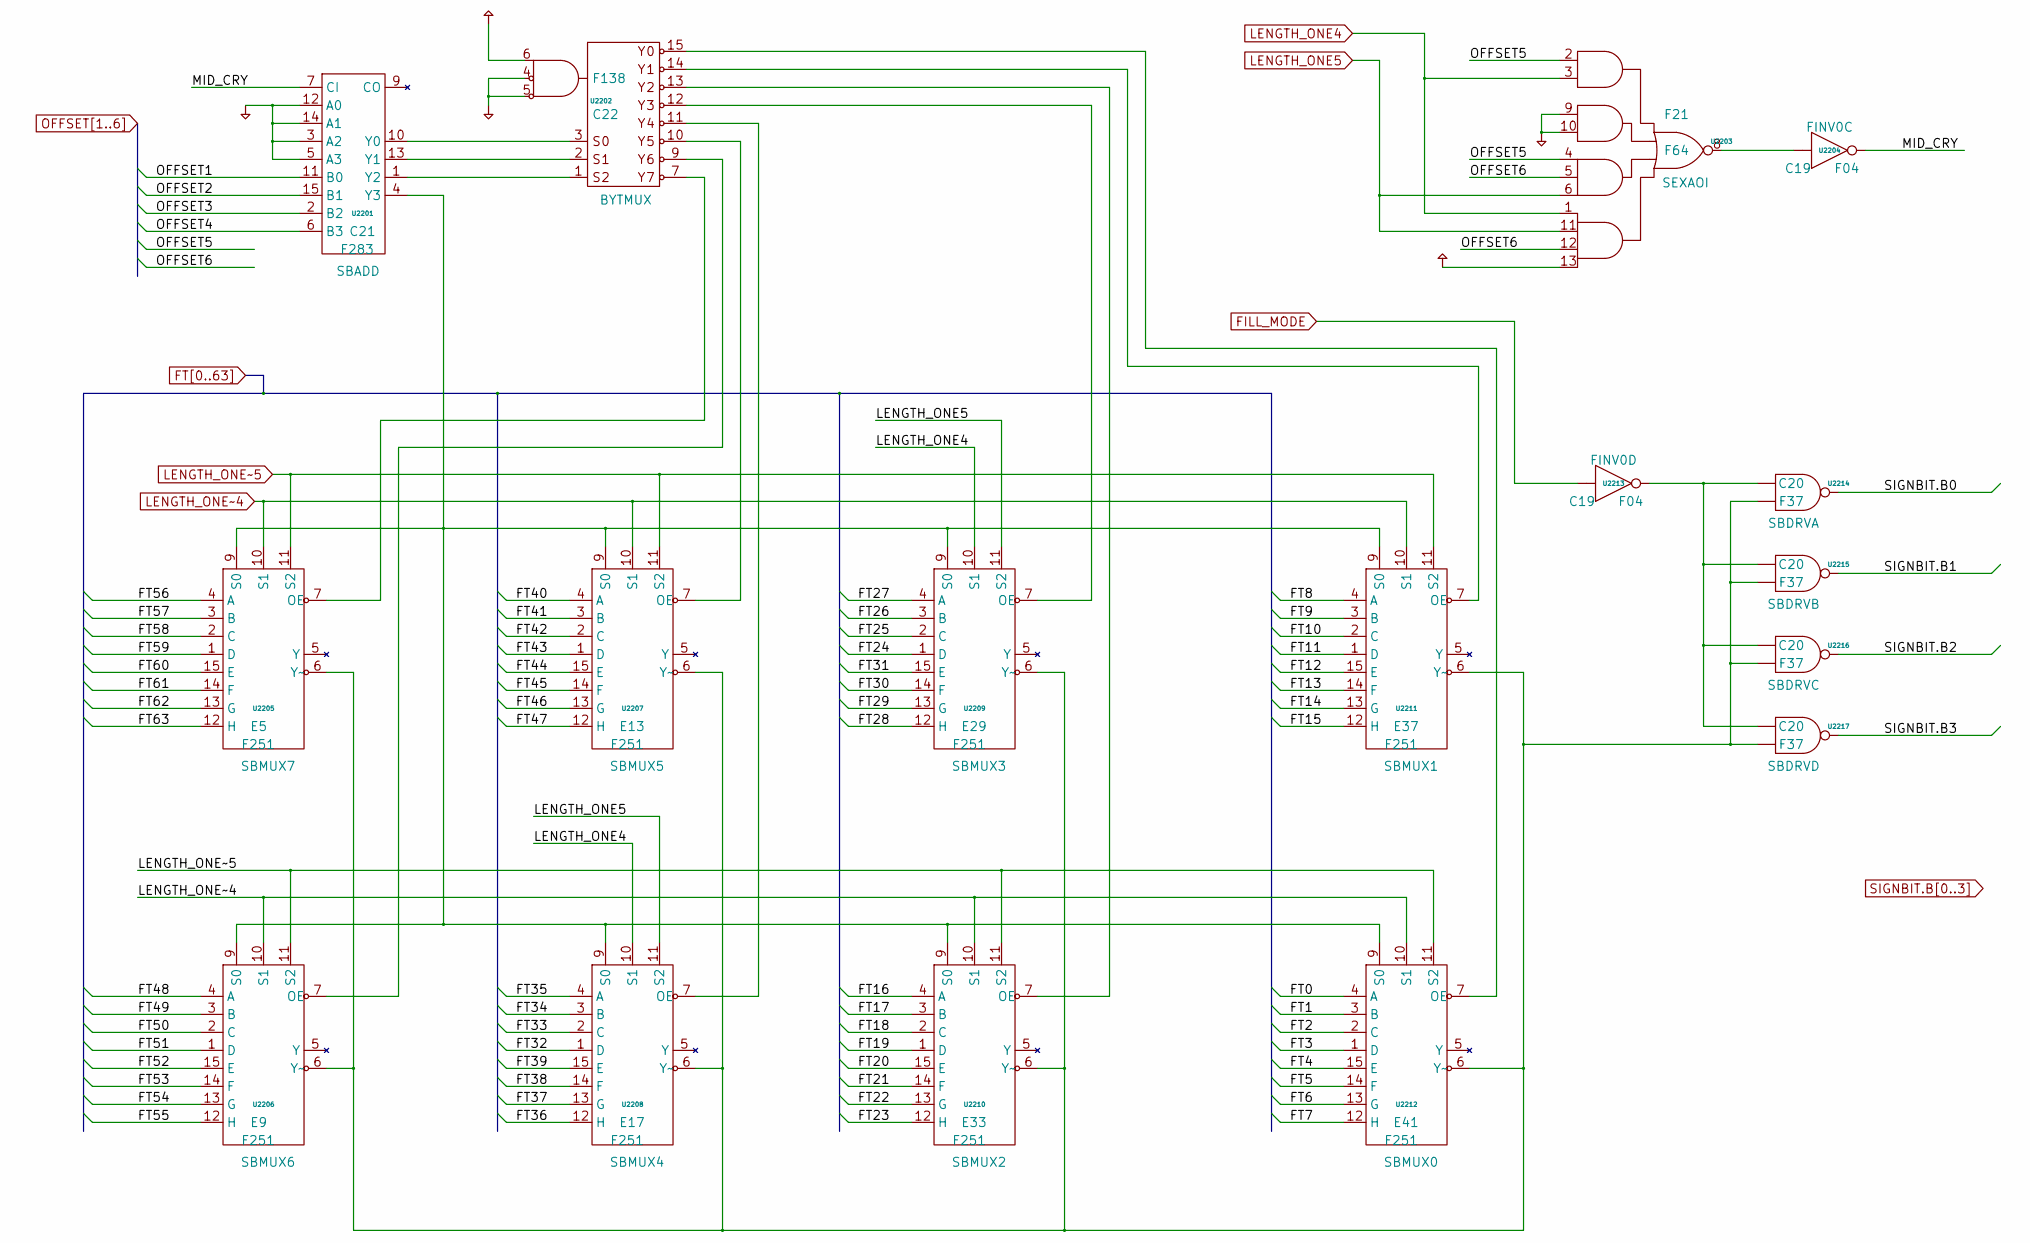
[picture p306: schematic pg_21.kicad_sch]

Parts:
U2201: F283
U2202: F138
U2203: F64
U2204, U2213: F04
U2205, U2206, U2207, U2208, U2209, U2210, U2211, U2212: F251
U2214, U2215, U2216, U2217: F37

Connections:
FILL_MODE: U2213.1 (D0)
FT0: U2212.4 (A)
FT1: U2212.3 (B)
FT2: U2212.2 (C)
FT3: U2212.1 (D)
FT4: U2212.15 (E)
FT5: U2212.14 (F)
FT6: U2212.13 (G)
FT7: U2212.12 (H)
FT8: U2211.4 (A)
FT9: U2211.3 (B)
FT10: U2211.2 (C)
FT11: U2211.1 (D)
FT12: U2211.15 (E)
FT13: U2211.14 (F)
FT14: U2211.13 (G)
FT15: U2211.12 (H)
FT16: U2210.4 (A)
FT17: U2210.3 (B)
FT18: U2210.2 (C)
FT19: U2210.1 (D)
FT20: U2210.15 (E)
FT21: U2210.14 (F)
FT22: U2210.13 (G)
FT23: U2210.12 (H)
FT24: U2209.1 (D)
FT25: U2209.2 (C)
FT26: U2209.3 (B)
FT27: U2209.4 (A)
FT28: U2209.12 (H)
FT29: U2209.13 (G)
FT30: U2209.14 (F)
FT31: U2209.15 (E)
FT32: U2208.1 (D)
FT33: U2208.2 (C)
FT34: U2208.3 (B)
FT35: U2208.4 (A)
FT36: U2208.12 (H)
FT37: U2208.13 (G)
FT38: U2208.14 (F)
FT39: U2208.15 (E)
FT40: U2207.4 (A)
FT41: U2207.3 (B)
FT42: U2207.2 (C)
FT43: U2207.1 (D)
FT44: U2207.15 (E)
FT45: U2207.14 (F)
FT46: U2207.13 (G)
FT47: U2207.12 (H)
FT48: U2206.4 (A)
FT49: U2206.3 (B)
FT50: U2206.2 (C)
FT51: U2206.1 (D)
FT52: U2206.15 (E)
FT53: U2206.14 (F)
FT54: U2206.13 (G)
FT55: U2206.12 (H)
FT56: U2205.4 (A)
FT57: U2205.3 (B)
FT58: U2205.2 (C)
FT59: U2205.1 (D)
FT60: U2205.15 (E)
FT61: U2205.14 (F)
FT62: U2205.13 (G)
FT63: U2205.12 (H)
LENGTH_ONE4: U2203.1 (D0), U2203.3 (A1), U2208.10 (S1), U2209.10 (S1)
LENGTH_ONE5: U2203.6 (C2), U2203.11 (D1), U2208.11 (S2), U2209.11 (S2)
LENGTH_ONE~4: U2205.10 (S1), U2206.10 (S1), U2207.10 (S1), U2210.10 (S1), U2211.10 (S1), U2212.10 (S1)
LENGTH_ONE~5: U2205.11 (S2), U2206.11 (S2), U2207.11 (S2), U2210.11 (S2), U2211.11 (S2), U2212.11 (S2)
MID_CRY: U2201.7 (CI), U2204.2 (Q)
unnamed: U2201.1 (Y2), U2202.1 (S2)
unnamed: U2201.4 (Y3), U2205.9 (S0), U2206.9 (S0), U2207.9 (S0), U2208.9 (S0), U2209.9 (S0), U2210.9 (S0), U2211.9 (S0), U2212.9 (S0)
unnamed: U2201.10 (Y0), U2202.3 (S0)
unnamed: U2201.13 (Y1), U2202.2 (S1)
unnamed: U2202.7 (Y7_), U2205.7 (OE)
unnamed: U2202.9 (Y6_), U2206.7 (OE)
unnamed: U2202.10 (Y5_), U2207.7 (OE)
unnamed: U2202.11 (Y4_), U2208.7 (OE)
unnamed: U2202.12 (Y3_), U2209.7 (OE)
unnamed: U2202.13 (Y2_), U2210.7 (OE)
unnamed: U2202.14 (Y1_), U2211.7 (OE)
unnamed: U2202.15 (Y0_), U2212.7 (OE)
unnamed: U2203.8 (Q), U2204.1 (D0)
unnamed: U2205.6 (Y~), U2206.6 (Y~), U2207.6 (Y~), U2208.6 (Y~), U2209.6 (Y~), U2210.6 (Y~), U2211.6 (Y~), U2212.6 (Y~), U2214.2 (D1), U2215.2 (D1), U2216.2 (D1), U2217.2 (D1)
unnamed: U2213.2 (Q), U2214.1 (D0), U2215.1 (D0), U2216.1 (D0), U2217.1 (D0)
OFFSET1: U2201.11 (B0)
OFFSET2: U2201.15 (B1)
OFFSET3: U2201.2 (B2)
OFFSET4: U2201.6 (B3)
OFFSET5: U2203.2 (A0), U2203.4 (C0)
OFFSET6: U2203.5 (C1), U2203.12 (D2)
PD: U2201.3 (A2), U2201.5 (A3), U2201.12 (A0), U2201.14 (A1), U2202.4 (D1), U2202.5 (D2), U2203.9 (B0), U2203.10 (B1)
PU: U2202.6 (D0), U2203.13 (D3)
SIGNBIT.B0: U2214.3 (Q)
SIGNBIT.B1: U2215.3 (Q)
SIGNBIT.B2: U2216.3 (Q)
SIGNBIT.B3: U2217.3 (Q)
