Datamuseum-DK/R1000.HwDoc/Schematics/FIU/pg_22.kicad_sch

## KiCad design Schematics/FIU/pg_22.kicad_sch (2023-01-10)

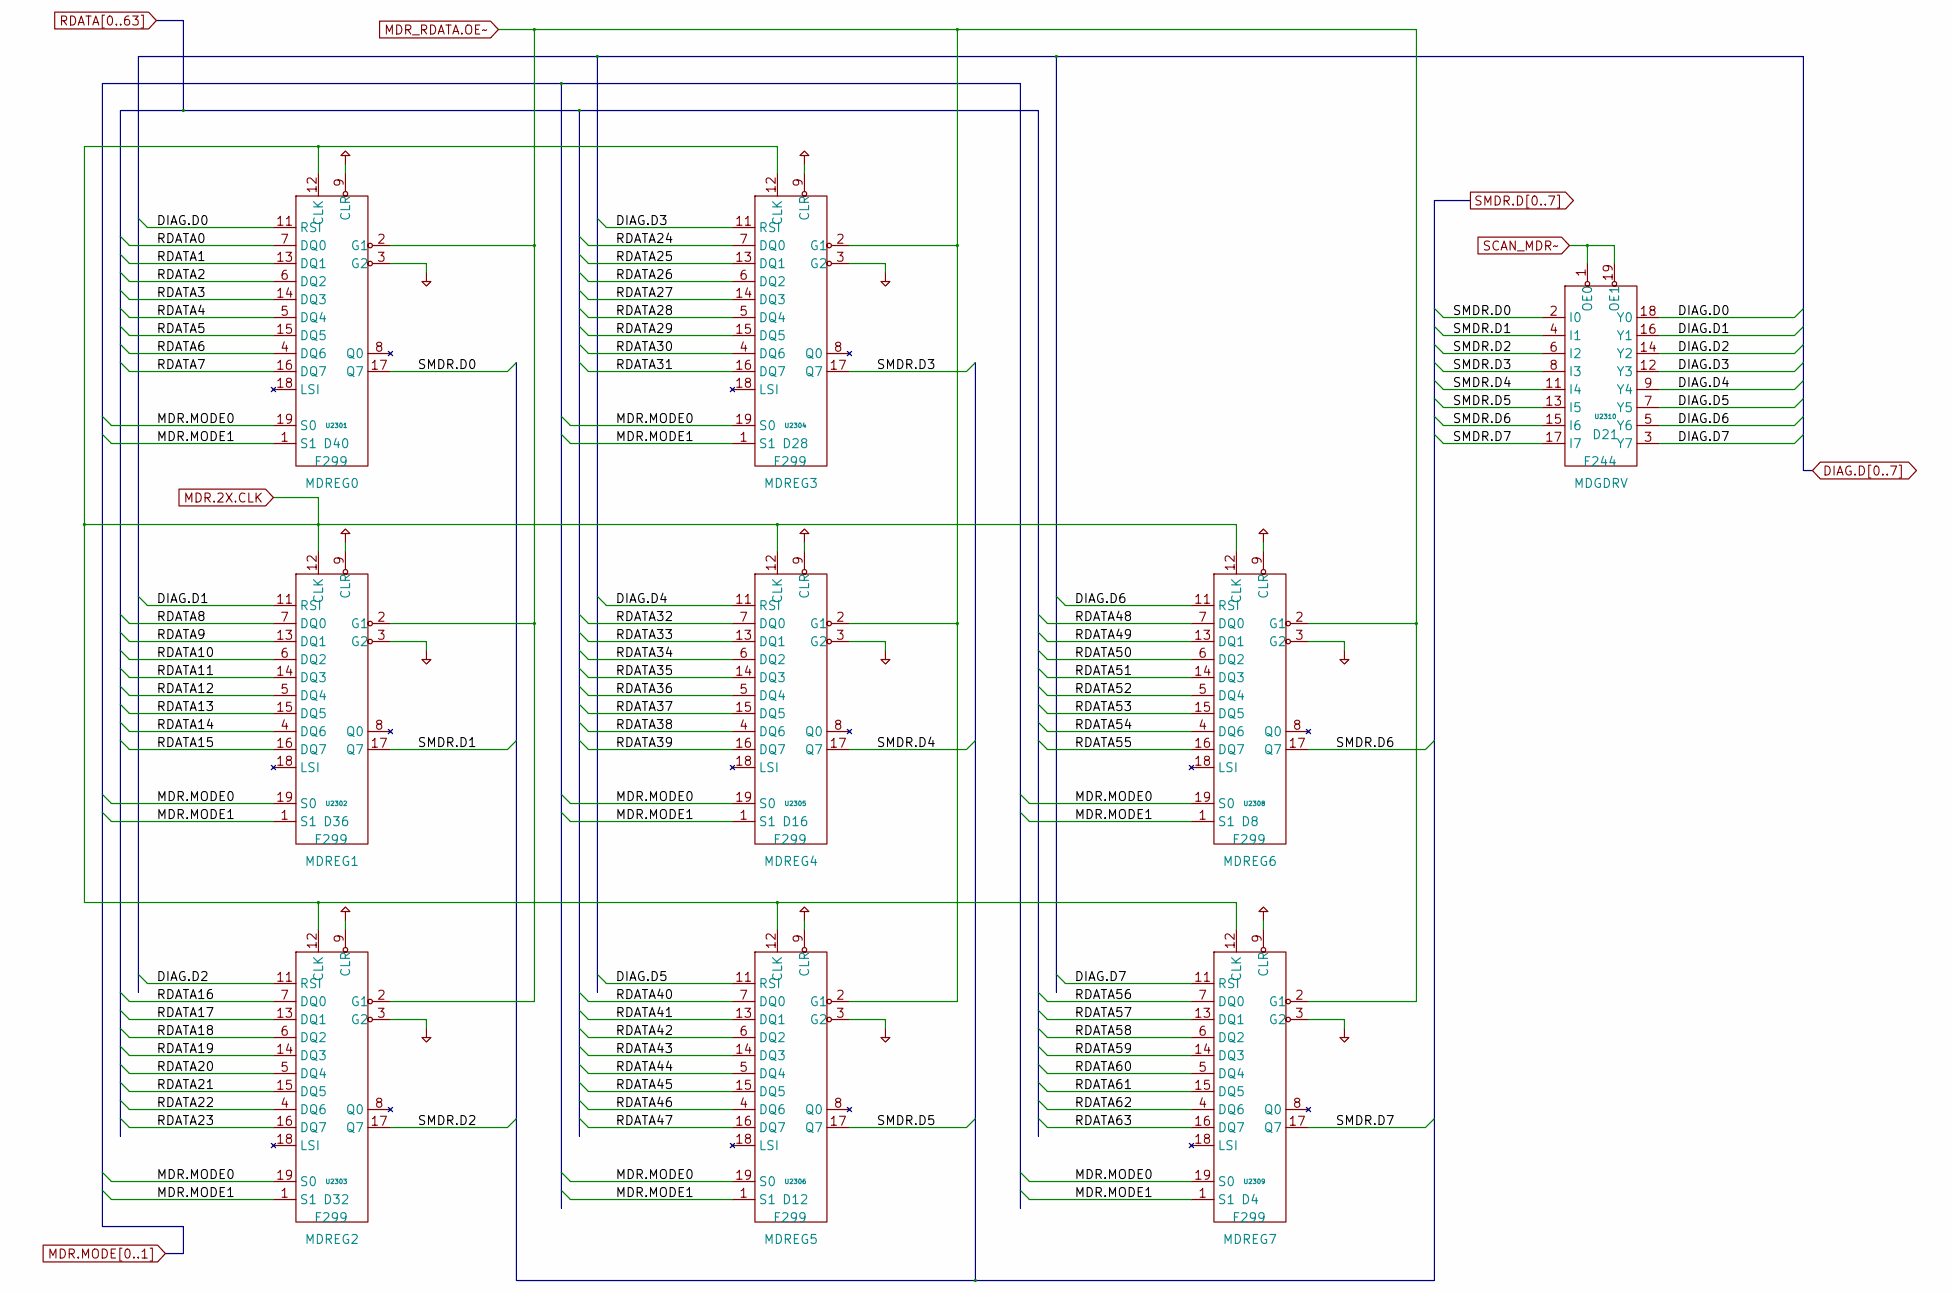
[picture p307: schematic pg_22.kicad_sch]

Parts:
U2301, U2302, U2303, U2304, U2305, U2306, U2308, U2309: F299
U2310: F244

Connections:
DIAG.D0: U2301.11 (RSI), U2310.18 (Y0)
DIAG.D1: U2302.11 (RSI), U2310.16 (Y1)
DIAG.D2: U2303.11 (RSI), U2310.14 (Y2)
DIAG.D3: U2304.11 (RSI), U2310.12 (Y3)
DIAG.D4: U2305.11 (RSI), U2310.9 (Y4)
DIAG.D5: U2306.11 (RSI), U2310.7 (Y5)
DIAG.D6: U2308.11 (RSI), U2310.5 (Y6)
DIAG.D7: U2309.11 (RSI), U2310.3 (Y7)
MDR.2X.CLK: U2301.12 (CLK), U2302.12 (CLK), U2303.12 (CLK), U2304.12 (CLK), U2305.12 (CLK), U2306.12 (CLK), U2308.12 (CLK), U2309.12 (CLK)
MDR.MODE0: U2301.19 (S0), U2302.19 (S0), U2303.19 (S0), U2304.19 (S0), U2305.19 (S0), U2306.19 (S0), U2308.19 (S0), U2309.19 (S0)
MDR.MODE1: U2301.1 (S1), U2302.1 (S1), U2303.1 (S1), U2304.1 (S1), U2305.1 (S1), U2306.1 (S1), U2308.1 (S1), U2309.1 (S1)
MDR_RDATA.OE~: U2301.2 (G1), U2302.2 (G1), U2303.2 (G1), U2304.2 (G1), U2305.2 (G1), U2306.2 (G1), U2308.2 (G1), U2309.2 (G1)
PD: U2301.3 (G2), U2302.3 (G2), U2303.3 (G2), U2304.3 (G2), U2305.3 (G2), U2306.3 (G2), U2308.3 (G2), U2309.3 (G2)
PU: U2301.9 (CLR), U2302.9 (CLR), U2303.9 (CLR), U2304.9 (CLR), U2305.9 (CLR), U2306.9 (CLR), U2308.9 (CLR), U2309.9 (CLR)
RDATA0: U2301.7 (DQ0)
RDATA1: U2301.13 (DQ1)
RDATA2: U2301.6 (DQ2)
RDATA3: U2301.14 (DQ3)
RDATA4: U2301.5 (DQ4)
RDATA5: U2301.15 (DQ5)
RDATA6: U2301.4 (DQ6)
RDATA7: U2301.16 (DQ7)
RDATA8: U2302.7 (DQ0)
RDATA9: U2302.13 (DQ1)
RDATA10: U2302.6 (DQ2)
RDATA11: U2302.14 (DQ3)
RDATA12: U2302.5 (DQ4)
RDATA13: U2302.15 (DQ5)
RDATA14: U2302.4 (DQ6)
RDATA15: U2302.16 (DQ7)
RDATA16: U2303.7 (DQ0)
RDATA17: U2303.13 (DQ1)
RDATA18: U2303.6 (DQ2)
RDATA19: U2303.14 (DQ3)
RDATA20: U2303.5 (DQ4)
RDATA21: U2303.15 (DQ5)
RDATA22: U2303.4 (DQ6)
RDATA23: U2303.16 (DQ7)
RDATA24: U2304.7 (DQ0)
RDATA25: U2304.13 (DQ1)
RDATA26: U2304.6 (DQ2)
RDATA27: U2304.14 (DQ3)
RDATA28: U2304.5 (DQ4)
RDATA29: U2304.15 (DQ5)
RDATA30: U2304.4 (DQ6)
RDATA31: U2304.16 (DQ7)
RDATA32: U2305.7 (DQ0)
RDATA33: U2305.13 (DQ1)
RDATA34: U2305.6 (DQ2)
RDATA35: U2305.14 (DQ3)
RDATA36: U2305.5 (DQ4)
RDATA37: U2305.15 (DQ5)
RDATA38: U2305.4 (DQ6)
RDATA39: U2305.16 (DQ7)
RDATA40: U2306.7 (DQ0)
RDATA41: U2306.13 (DQ1)
RDATA42: U2306.6 (DQ2)
RDATA43: U2306.14 (DQ3)
RDATA44: U2306.5 (DQ4)
RDATA45: U2306.15 (DQ5)
RDATA46: U2306.4 (DQ6)
RDATA47: U2306.16 (DQ7)
RDATA48: U2308.7 (DQ0)
RDATA49: U2308.13 (DQ1)
RDATA50: U2308.6 (DQ2)
RDATA51: U2308.14 (DQ3)
RDATA52: U2308.5 (DQ4)
RDATA53: U2308.15 (DQ5)
RDATA54: U2308.4 (DQ6)
RDATA55: U2308.16 (DQ7)
RDATA56: U2309.7 (DQ0)
RDATA57: U2309.13 (DQ1)
RDATA58: U2309.6 (DQ2)
RDATA59: U2309.14 (DQ3)
RDATA60: U2309.5 (DQ4)
RDATA61: U2309.15 (DQ5)
RDATA62: U2309.4 (DQ6)
RDATA63: U2309.16 (DQ7)
SCAN_MDR~: U2310.1 (OE0), U2310.19 (OE1)
SMDR.D0: U2301.17 (Q7), U2310.2 (I0)
SMDR.D1: U2302.17 (Q7), U2310.4 (I1)
SMDR.D2: U2303.17 (Q7), U2310.6 (I2)
SMDR.D3: U2304.17 (Q7), U2310.8 (I3)
SMDR.D4: U2305.17 (Q7), U2310.11 (I4)
SMDR.D5: U2306.17 (Q7), U2310.13 (I5)
SMDR.D6: U2308.17 (Q7), U2310.15 (I6)
SMDR.D7: U2309.17 (Q7), U2310.17 (I7)
