Datamuseum-DK/R1000.HwDoc/Schematics/FIU/pg_23.kicad_sch

## KiCad design Schematics/FIU/pg_23.kicad_sch (2023-01-10)

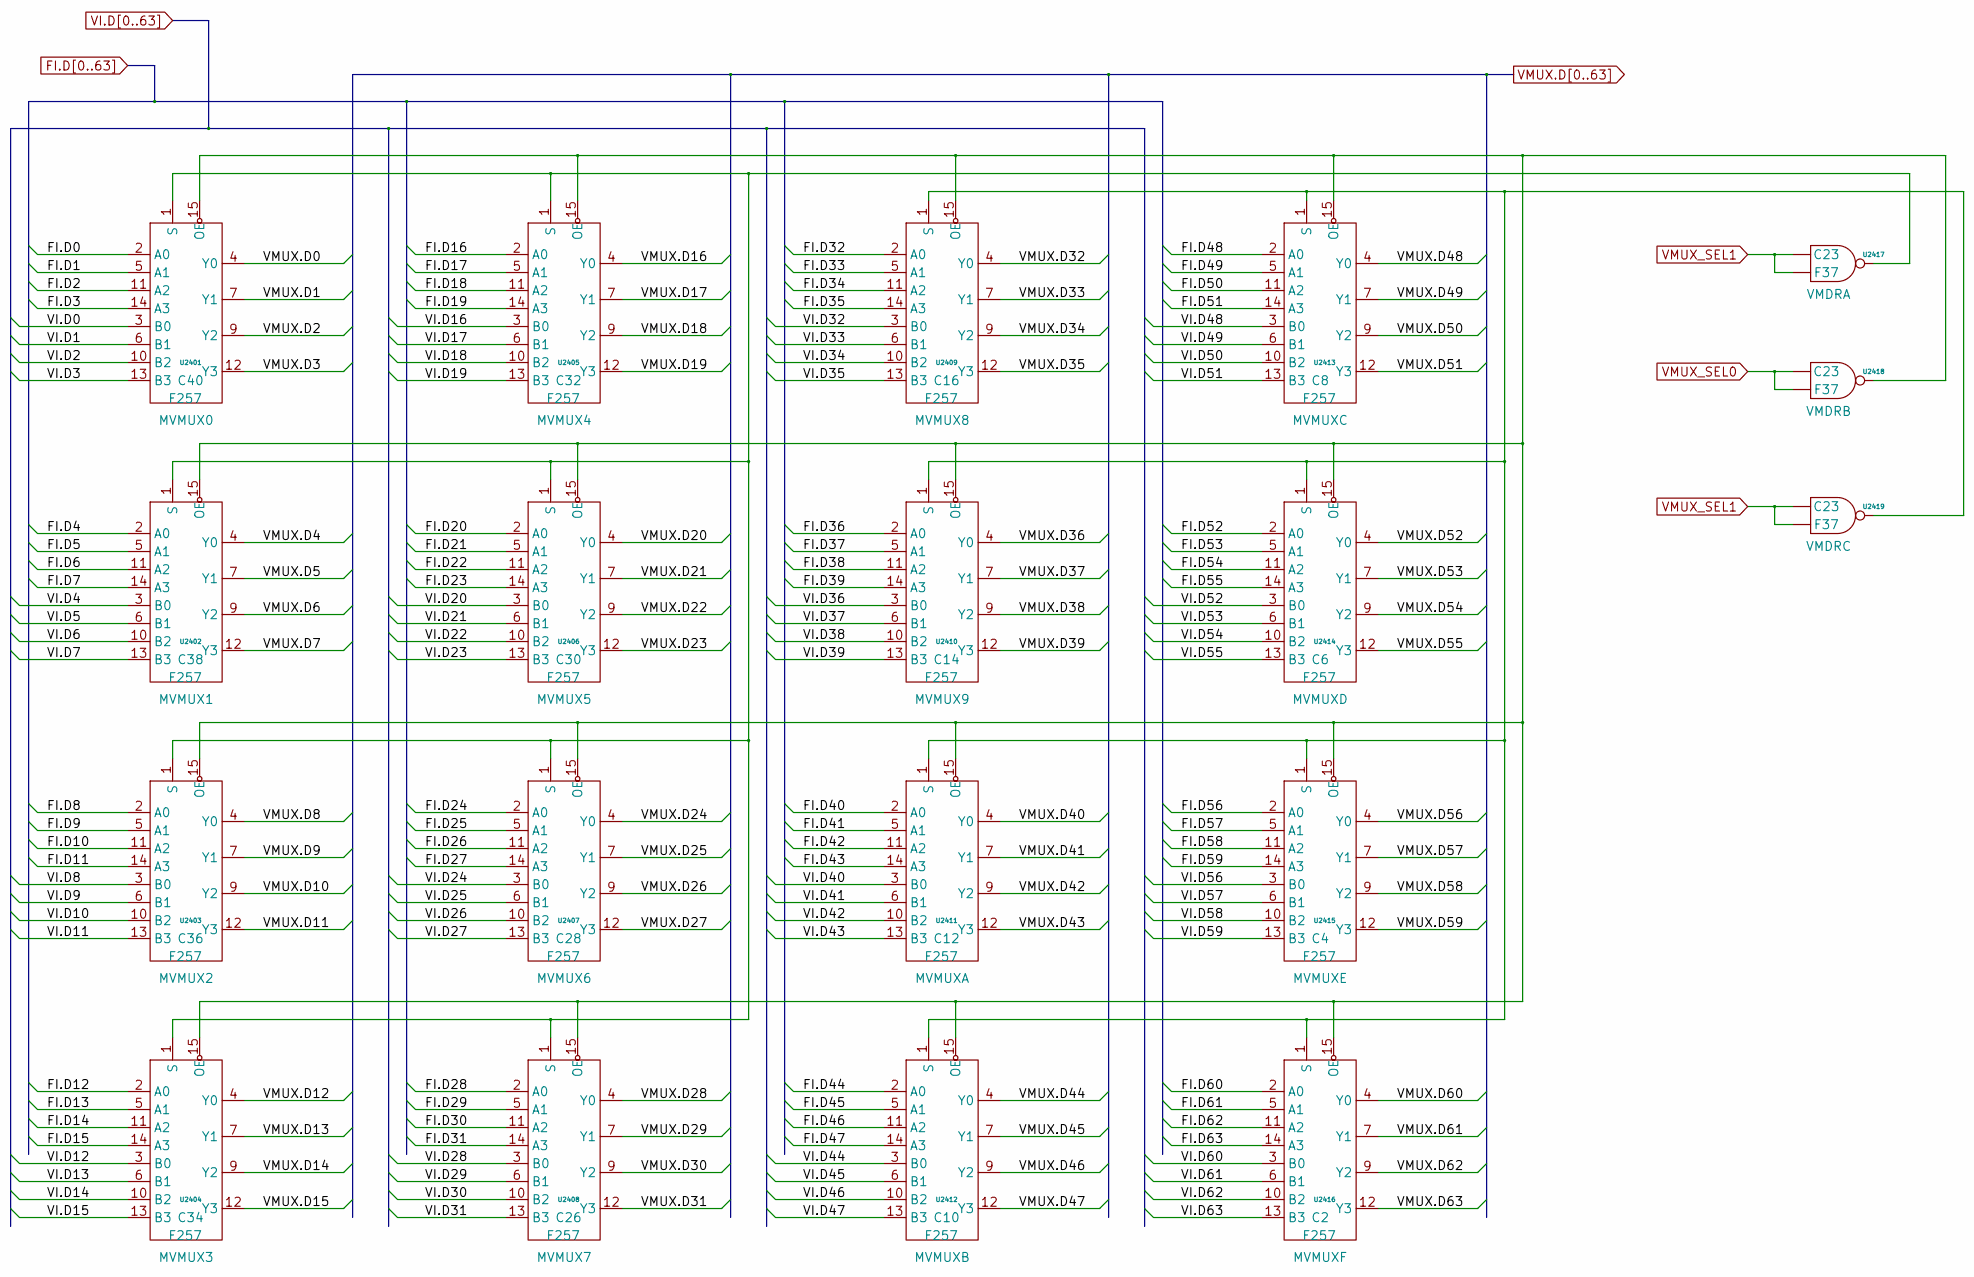
[picture p308: schematic pg_23.kicad_sch]

Parts:
U2401, U2402, U2403, U2404, U2405, U2406, U2407, U2408, U2409, U2410, U2411, U2412, U2413, U2414, U2415, U2416: F257
U2417, U2418, U2419: F37

Connections:
FI.D0: U2401.2 (A0)
FI.D1: U2401.5 (A1)
FI.D2: U2401.11 (A2)
FI.D3: U2401.14 (A3)
FI.D4: U2402.2 (A0)
FI.D5: U2402.5 (A1)
FI.D6: U2402.11 (A2)
FI.D7: U2402.14 (A3)
FI.D8: U2403.2 (A0)
FI.D9: U2403.5 (A1)
FI.D10: U2403.11 (A2)
FI.D11: U2403.14 (A3)
FI.D12: U2404.2 (A0)
FI.D13: U2404.5 (A1)
FI.D14: U2404.11 (A2)
FI.D15: U2404.14 (A3)
FI.D16: U2405.2 (A0)
FI.D17: U2405.5 (A1)
FI.D18: U2405.11 (A2)
FI.D19: U2405.14 (A3)
FI.D20: U2406.2 (A0)
FI.D21: U2406.5 (A1)
FI.D22: U2406.11 (A2)
FI.D23: U2406.14 (A3)
FI.D24: U2407.2 (A0)
FI.D25: U2407.5 (A1)
FI.D26: U2407.11 (A2)
FI.D27: U2407.14 (A3)
FI.D28: U2408.2 (A0)
FI.D29: U2408.5 (A1)
FI.D30: U2408.11 (A2)
FI.D31: U2408.14 (A3)
FI.D32: U2409.2 (A0)
FI.D33: U2409.5 (A1)
FI.D34: U2409.11 (A2)
FI.D35: U2409.14 (A3)
FI.D36: U2410.2 (A0)
FI.D37: U2410.5 (A1)
FI.D38: U2410.11 (A2)
FI.D39: U2410.14 (A3)
FI.D40: U2411.2 (A0)
FI.D41: U2411.5 (A1)
FI.D42: U2411.11 (A2)
FI.D43: U2411.14 (A3)
FI.D44: U2412.2 (A0)
FI.D45: U2412.5 (A1)
FI.D46: U2412.11 (A2)
FI.D47: U2412.14 (A3)
FI.D48: U2413.2 (A0)
FI.D49: U2413.5 (A1)
FI.D50: U2413.11 (A2)
FI.D51: U2413.14 (A3)
FI.D52: U2414.2 (A0)
FI.D53: U2414.5 (A1)
FI.D54: U2414.11 (A2)
FI.D55: U2414.14 (A3)
FI.D56: U2415.2 (A0)
FI.D57: U2415.5 (A1)
FI.D58: U2415.11 (A2)
FI.D59: U2415.14 (A3)
FI.D60: U2416.2 (A0)
FI.D61: U2416.5 (A1)
FI.D62: U2416.11 (A2)
FI.D63: U2416.14 (A3)
unnamed: U2401.1 (S), U2402.1 (S), U2403.1 (S), U2404.1 (S), U2405.1 (S), U2406.1 (S), U2407.1 (S), U2408.1 (S), U2417.3 (Q)
unnamed: U2401.15 (OE), U2402.15 (OE), U2403.15 (OE), U2404.15 (OE), U2405.15 (OE), U2406.15 (OE), U2407.15 (OE), U2408.15 (OE), U2409.15 (OE), U2410.15 (OE), U2411.15 (OE), U2412.15 (OE), U2413.15 (OE), U2414.15 (OE), U2415.15 (OE), U2416.15 (OE), U2418.3 (Q)
unnamed: U2409.1 (S), U2410.1 (S), U2411.1 (S), U2412.1 (S), U2413.1 (S), U2414.1 (S), U2415.1 (S), U2416.1 (S), U2419.3 (Q)
VI.D0: U2401.3 (B0)
VI.D1: U2401.6 (B1)
VI.D2: U2401.10 (B2)
VI.D3: U2401.13 (B3)
VI.D4: U2402.3 (B0)
VI.D5: U2402.6 (B1)
VI.D6: U2402.10 (B2)
VI.D7: U2402.13 (B3)
VI.D8: U2403.3 (B0)
VI.D9: U2403.6 (B1)
VI.D10: U2403.10 (B2)
VI.D11: U2403.13 (B3)
VI.D12: U2404.3 (B0)
VI.D13: U2404.6 (B1)
VI.D14: U2404.10 (B2)
VI.D15: U2404.13 (B3)
VI.D16: U2405.3 (B0)
VI.D17: U2405.6 (B1)
VI.D18: U2405.10 (B2)
VI.D19: U2405.13 (B3)
VI.D20: U2406.3 (B0)
VI.D21: U2406.6 (B1)
VI.D22: U2406.10 (B2)
VI.D23: U2406.13 (B3)
VI.D24: U2407.3 (B0)
VI.D25: U2407.6 (B1)
VI.D26: U2407.10 (B2)
VI.D27: U2407.13 (B3)
VI.D28: U2408.3 (B0)
VI.D29: U2408.6 (B1)
VI.D30: U2408.10 (B2)
VI.D31: U2408.13 (B3)
VI.D32: U2409.3 (B0)
VI.D33: U2409.6 (B1)
VI.D34: U2409.10 (B2)
VI.D35: U2409.13 (B3)
VI.D36: U2410.3 (B0)
VI.D37: U2410.6 (B1)
VI.D38: U2410.10 (B2)
VI.D39: U2410.13 (B3)
VI.D40: U2411.3 (B0)
VI.D41: U2411.6 (B1)
VI.D42: U2411.10 (B2)
VI.D43: U2411.13 (B3)
VI.D44: U2412.3 (B0)
VI.D45: U2412.6 (B1)
VI.D46: U2412.10 (B2)
VI.D47: U2412.13 (B3)
VI.D48: U2413.3 (B0)
VI.D49: U2413.6 (B1)
VI.D50: U2413.10 (B2)
VI.D51: U2413.13 (B3)
VI.D52: U2414.3 (B0)
VI.D53: U2414.6 (B1)
VI.D54: U2414.10 (B2)
VI.D55: U2414.13 (B3)
VI.D56: U2415.3 (B0)
VI.D57: U2415.6 (B1)
VI.D58: U2415.10 (B2)
VI.D59: U2415.13 (B3)
VI.D60: U2416.3 (B0)
VI.D61: U2416.6 (B1)
VI.D62: U2416.10 (B2)
VI.D63: U2416.13 (B3)
VMUX.D0: U2401.4 (Y0)
VMUX.D1: U2401.7 (Y1)
VMUX.D2: U2401.9 (Y2)
VMUX.D3: U2401.12 (Y3)
VMUX.D4: U2402.4 (Y0)
VMUX.D5: U2402.7 (Y1)
VMUX.D6: U2402.9 (Y2)
VMUX.D7: U2402.12 (Y3)
VMUX.D8: U2403.4 (Y0)
VMUX.D9: U2403.7 (Y1)
VMUX.D10: U2403.9 (Y2)
VMUX.D11: U2403.12 (Y3)
VMUX.D12: U2404.4 (Y0)
VMUX.D13: U2404.7 (Y1)
VMUX.D14: U2404.9 (Y2)
VMUX.D15: U2404.12 (Y3)
VMUX.D16: U2405.4 (Y0)
VMUX.D17: U2405.7 (Y1)
VMUX.D18: U2405.9 (Y2)
VMUX.D19: U2405.12 (Y3)
VMUX.D20: U2406.4 (Y0)
VMUX.D21: U2406.7 (Y1)
VMUX.D22: U2406.9 (Y2)
VMUX.D23: U2406.12 (Y3)
VMUX.D24: U2407.4 (Y0)
VMUX.D25: U2407.7 (Y1)
VMUX.D26: U2407.9 (Y2)
VMUX.D27: U2407.12 (Y3)
VMUX.D28: U2408.4 (Y0)
VMUX.D29: U2408.7 (Y1)
VMUX.D30: U2408.9 (Y2)
VMUX.D31: U2408.12 (Y3)
VMUX.D32: U2409.4 (Y0)
VMUX.D33: U2409.7 (Y1)
VMUX.D34: U2409.9 (Y2)
VMUX.D35: U2409.12 (Y3)
VMUX.D36: U2410.4 (Y0)
VMUX.D37: U2410.7 (Y1)
VMUX.D38: U2410.9 (Y2)
VMUX.D39: U2410.12 (Y3)
VMUX.D40: U2411.4 (Y0)
VMUX.D41: U2411.7 (Y1)
VMUX.D42: U2411.9 (Y2)
VMUX.D43: U2411.12 (Y3)
VMUX.D44: U2412.4 (Y0)
VMUX.D45: U2412.7 (Y1)
VMUX.D46: U2412.9 (Y2)
VMUX.D47: U2412.12 (Y3)
VMUX.D48: U2413.4 (Y0)
VMUX.D49: U2413.7 (Y1)
VMUX.D50: U2413.9 (Y2)
VMUX.D51: U2413.12 (Y3)
VMUX.D52: U2414.4 (Y0)
VMUX.D53: U2414.7 (Y1)
VMUX.D54: U2414.9 (Y2)
VMUX.D55: U2414.12 (Y3)
VMUX.D56: U2415.4 (Y0)
VMUX.D57: U2415.7 (Y1)
VMUX.D58: U2415.9 (Y2)
VMUX.D59: U2415.12 (Y3)
VMUX.D60: U2416.4 (Y0)
VMUX.D61: U2416.7 (Y1)
VMUX.D62: U2416.9 (Y2)
VMUX.D63: U2416.12 (Y3)
VMUX_SEL0: U2418.1 (D0), U2418.2 (D1)
VMUX_SEL1: U2417.1 (D0), U2417.2 (D1), U2419.1 (D0), U2419.2 (D1)
