Datamuseum-DK/R1000.HwDoc/Schematics/FIU/pg_24.kicad_sch

## KiCad design Schematics/FIU/pg_24.kicad_sch (2023-01-10)

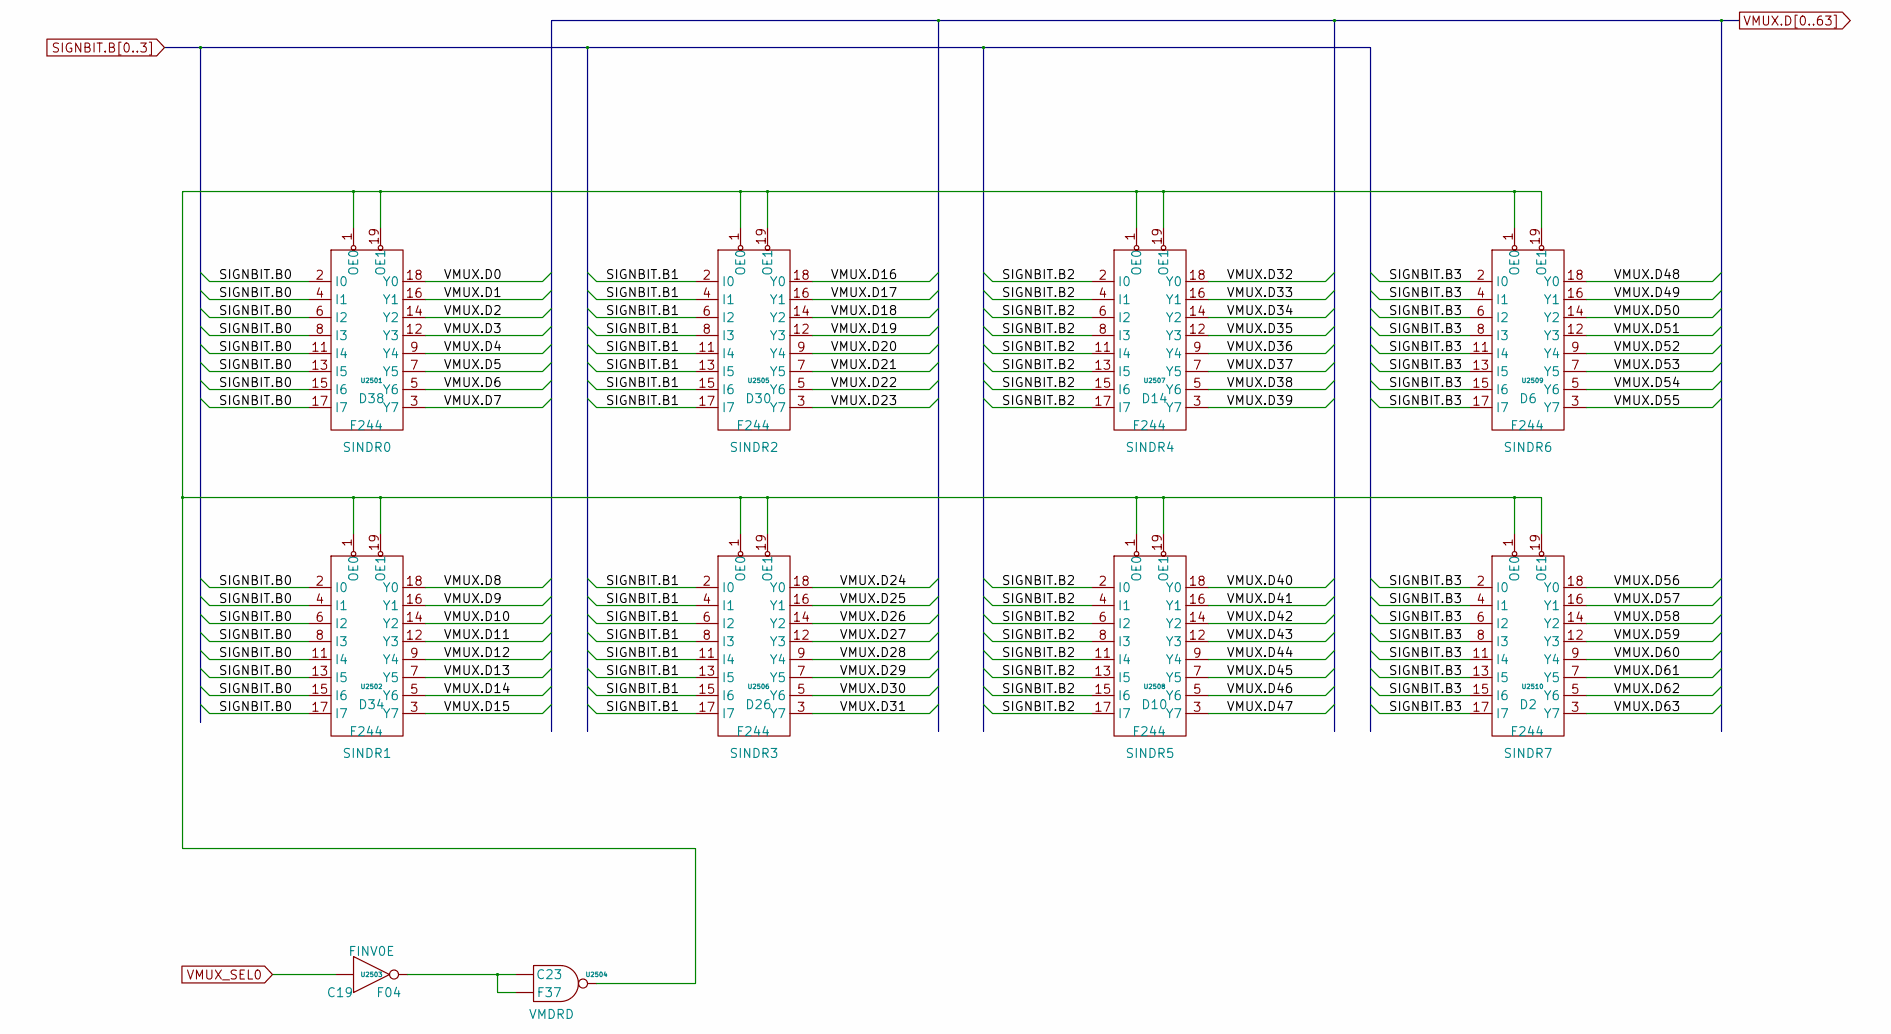
[picture p309: schematic pg_24.kicad_sch]

Parts:
U2501, U2502, U2505, U2506, U2507, U2508, U2509, U2510: F244
U2503: F04
U2504: F37

Connections:
unnamed: U2501.1 (OE0), U2501.19 (OE1), U2502.1 (OE0), U2502.19 (OE1), U2504.3 (Q), U2505.1 (OE0), U2505.19 (OE1), U2506.1 (OE0), U2506.19 (OE1), U2507.1 (OE0), U2507.19 (OE1), U2508.1 (OE0), U2508.19 (OE1), U2509.1 (OE0), U2509.19 (OE1), U2510.1 (OE0), U2510.19 (OE1)
unnamed: U2503.2 (Q), U2504.1 (D0), U2504.2 (D1)
SIGNBIT.B0: U2501.2 (I0), U2501.4 (I1), U2501.6 (I2), U2501.8 (I3), U2501.11 (I4), U2501.13 (I5), U2501.15 (I6), U2501.17 (I7), U2502.2 (I0), U2502.4 (I1), U2502.6 (I2), U2502.8 (I3), U2502.11 (I4), U2502.13 (I5), U2502.15 (I6), U2502.17 (I7)
SIGNBIT.B1: U2505.2 (I0), U2505.4 (I1), U2505.6 (I2), U2505.8 (I3), U2505.11 (I4), U2505.13 (I5), U2505.15 (I6), U2505.17 (I7), U2506.2 (I0), U2506.4 (I1), U2506.6 (I2), U2506.8 (I3), U2506.11 (I4), U2506.13 (I5), U2506.15 (I6), U2506.17 (I7)
SIGNBIT.B2: U2507.2 (I0), U2507.4 (I1), U2507.6 (I2), U2507.8 (I3), U2507.11 (I4), U2507.13 (I5), U2507.15 (I6), U2507.17 (I7), U2508.2 (I0), U2508.4 (I1), U2508.6 (I2), U2508.8 (I3), U2508.11 (I4), U2508.13 (I5), U2508.15 (I6), U2508.17 (I7)
SIGNBIT.B3: U2509.2 (I0), U2509.4 (I1), U2509.6 (I2), U2509.8 (I3), U2509.11 (I4), U2509.13 (I5), U2509.15 (I6), U2509.17 (I7), U2510.2 (I0), U2510.4 (I1), U2510.6 (I2), U2510.8 (I3), U2510.11 (I4), U2510.13 (I5), U2510.15 (I6), U2510.17 (I7)
VMUX.D0: U2501.18 (Y0)
VMUX.D1: U2501.16 (Y1)
VMUX.D2: U2501.14 (Y2)
VMUX.D3: U2501.12 (Y3)
VMUX.D4: U2501.9 (Y4)
VMUX.D5: U2501.7 (Y5)
VMUX.D6: U2501.5 (Y6)
VMUX.D7: U2501.3 (Y7)
VMUX.D8: U2502.18 (Y0)
VMUX.D9: U2502.16 (Y1)
VMUX.D10: U2502.14 (Y2)
VMUX.D11: U2502.12 (Y3)
VMUX.D12: U2502.9 (Y4)
VMUX.D13: U2502.7 (Y5)
VMUX.D14: U2502.5 (Y6)
VMUX.D15: U2502.3 (Y7)
VMUX.D16: U2505.18 (Y0)
VMUX.D17: U2505.16 (Y1)
VMUX.D18: U2505.14 (Y2)
VMUX.D19: U2505.12 (Y3)
VMUX.D20: U2505.9 (Y4)
VMUX.D21: U2505.7 (Y5)
VMUX.D22: U2505.5 (Y6)
VMUX.D23: U2505.3 (Y7)
VMUX.D24: U2506.18 (Y0)
VMUX.D25: U2506.16 (Y1)
VMUX.D26: U2506.14 (Y2)
VMUX.D27: U2506.12 (Y3)
VMUX.D28: U2506.9 (Y4)
VMUX.D29: U2506.7 (Y5)
VMUX.D30: U2506.5 (Y6)
VMUX.D31: U2506.3 (Y7)
VMUX.D32: U2507.18 (Y0)
VMUX.D33: U2507.16 (Y1)
VMUX.D34: U2507.14 (Y2)
VMUX.D35: U2507.12 (Y3)
VMUX.D36: U2507.9 (Y4)
VMUX.D37: U2507.7 (Y5)
VMUX.D38: U2507.5 (Y6)
VMUX.D39: U2507.3 (Y7)
VMUX.D40: U2508.18 (Y0)
VMUX.D41: U2508.16 (Y1)
VMUX.D42: U2508.14 (Y2)
VMUX.D43: U2508.12 (Y3)
VMUX.D44: U2508.9 (Y4)
VMUX.D45: U2508.7 (Y5)
VMUX.D46: U2508.5 (Y6)
VMUX.D47: U2508.3 (Y7)
VMUX.D48: U2509.18 (Y0)
VMUX.D49: U2509.16 (Y1)
VMUX.D50: U2509.14 (Y2)
VMUX.D51: U2509.12 (Y3)
VMUX.D52: U2509.9 (Y4)
VMUX.D53: U2509.7 (Y5)
VMUX.D54: U2509.5 (Y6)
VMUX.D55: U2509.3 (Y7)
VMUX.D56: U2510.18 (Y0)
VMUX.D57: U2510.16 (Y1)
VMUX.D58: U2510.14 (Y2)
VMUX.D59: U2510.12 (Y3)
VMUX.D60: U2510.9 (Y4)
VMUX.D61: U2510.7 (Y5)
VMUX.D62: U2510.5 (Y6)
VMUX.D63: U2510.3 (Y7)
VMUX_SEL0: U2503.1 (D0)
