Datamuseum-DK/R1000.HwDoc/Schematics/FIU/pg_25.kicad_sch

## KiCad design Schematics/FIU/pg_25.kicad_sch (2023-01-10)

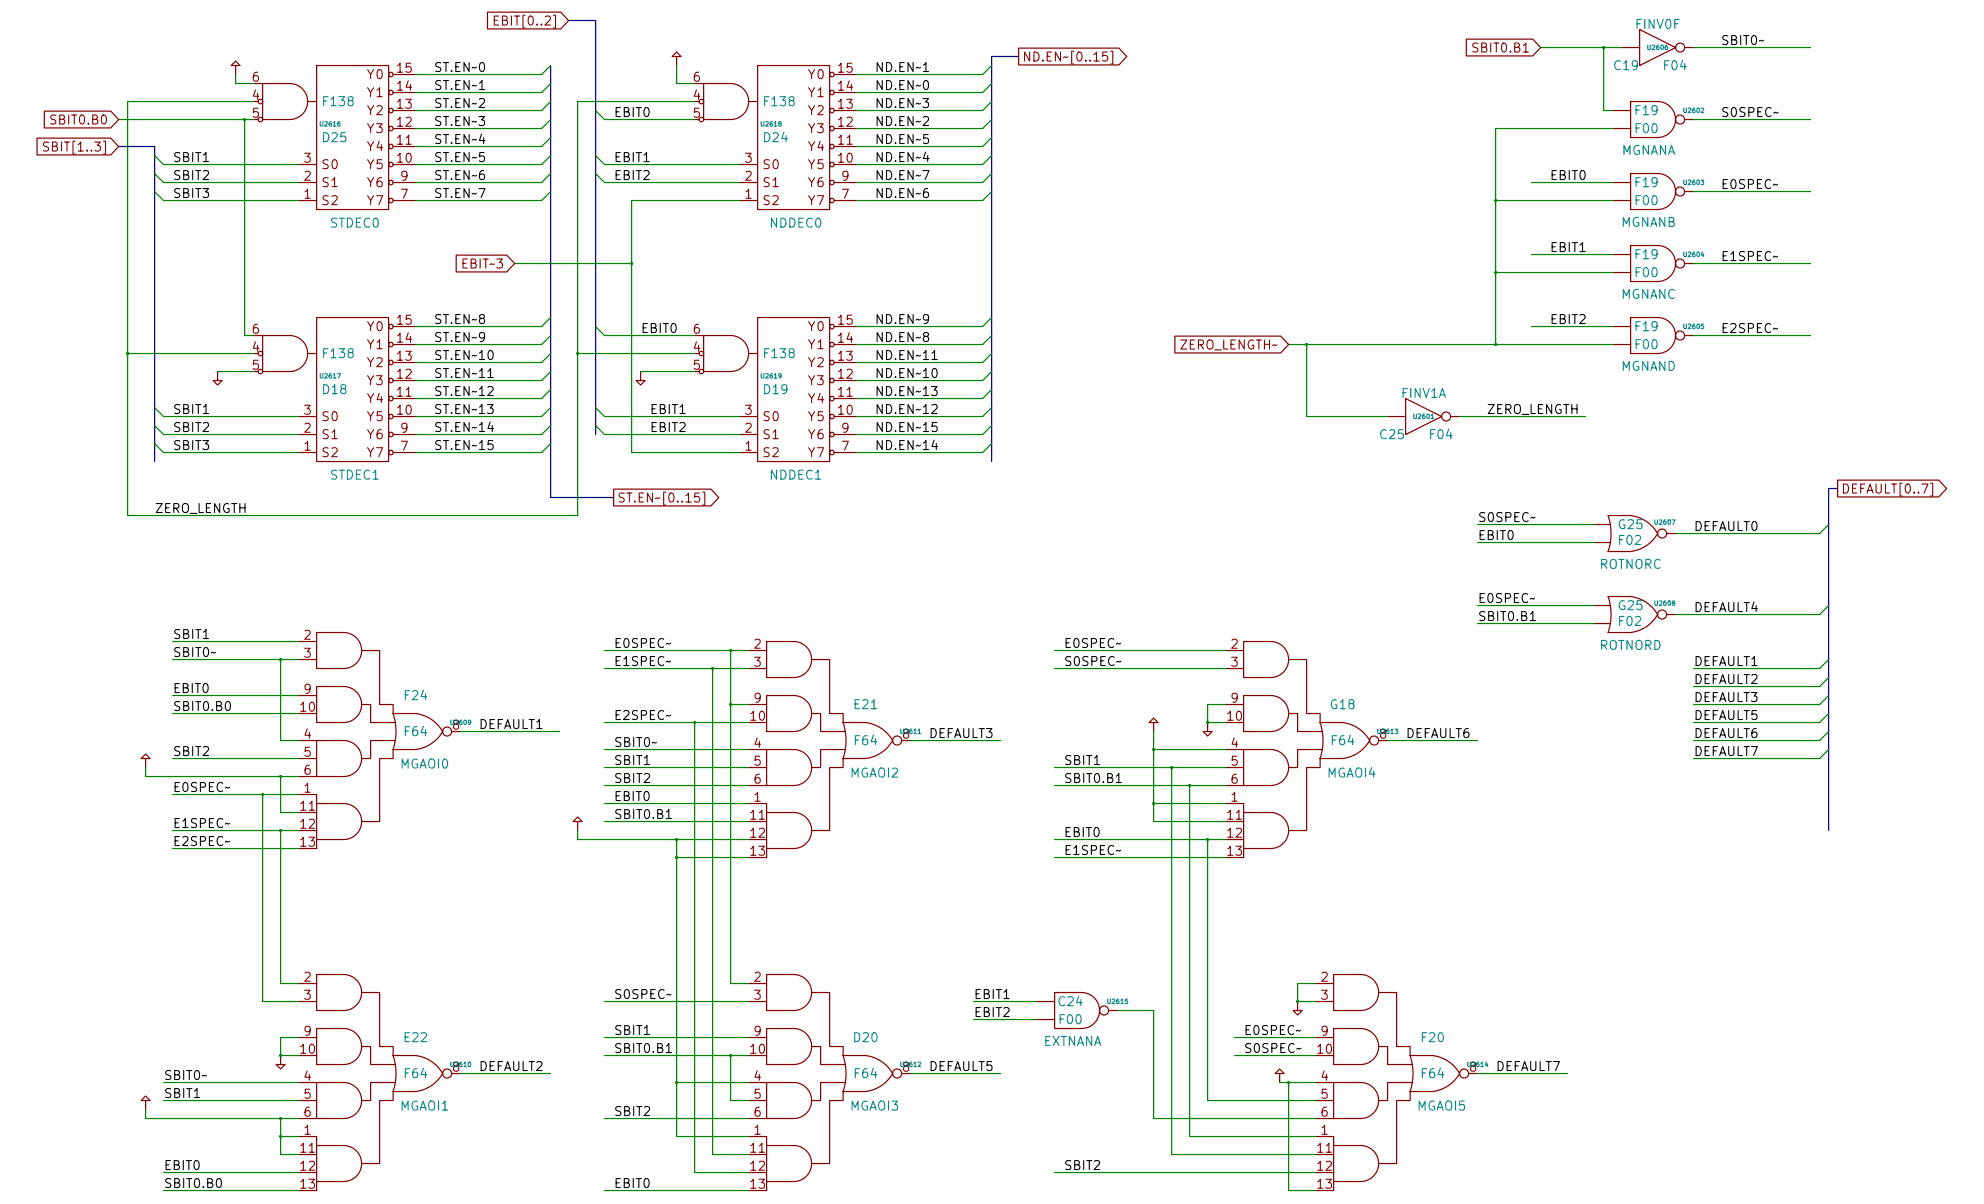
[picture p310: schematic pg_25.kicad_sch]

Parts:
U2601, U2606: F04
U2602, U2603, U2604, U2605, U2615: F00
U2607, U2608: F02
U2609, U2610, U2611, U2612, U2613, U2614: F64
U2616, U2617, U2618, U2619: F138

Connections:
DEFAULT0: U2607.3 (Q)
DEFAULT1: U2609.8 (Q)
DEFAULT2: U2610.8 (Q)
DEFAULT3: U2611.8 (Q)
DEFAULT4: U2608.3 (Q)
DEFAULT5: U2612.8 (Q)
DEFAULT6: U2613.8 (Q)
DEFAULT7: U2614.8 (Q)
E0SPEC~: U2603.3 (Q), U2608.1 (D0), U2609.1 (D0), U2610.3 (A1), U2611.2 (A0), U2611.9 (B0), U2612.2 (A0), U2613.2 (A0), U2614.9 (B0)
E1SPEC~: U2604.3 (Q), U2609.12 (D2), U2610.2 (A0), U2611.3 (A1), U2612.11 (D1), U2613.13 (D3)
E2SPEC~: U2605.3 (Q), U2609.13 (D3), U2611.10 (B1), U2612.12 (D2)
EBIT0: U2603.1 (D0), U2607.2 (D1), U2609.9 (B0), U2610.12 (D2), U2611.1 (D0), U2612.13 (D3), U2613.12 (D2), U2614.5 (C1), U2618.5 (D2), U2619.6 (D0)
EBIT1: U2604.1 (D0), U2615.1 (D0), U2618.3 (S0), U2619.3 (S0)
EBIT2: U2605.1 (D0), U2615.2 (D1), U2618.2 (S1), U2619.2 (S1)
EBIT~3: U2618.1 (S2), U2619.1 (S2)
ND.EN~0: U2618.14 (Y1_)
ND.EN~1: U2618.15 (Y0_)
ND.EN~2: U2618.12 (Y3_)
ND.EN~3: U2618.13 (Y2_)
ND.EN~4: U2618.10 (Y5_)
ND.EN~5: U2618.11 (Y4_)
ND.EN~6: U2618.7 (Y7_)
ND.EN~7: U2618.9 (Y6_)
ND.EN~8: U2619.14 (Y1_)
ND.EN~9: U2619.15 (Y0_)
ND.EN~10: U2619.12 (Y3_)
ND.EN~11: U2619.13 (Y2_)
ND.EN~12: U2619.10 (Y5_)
ND.EN~13: U2619.11 (Y4_)
ND.EN~14: U2619.7 (Y7_)
ND.EN~15: U2619.9 (Y6_)
unnamed: U2614.6 (C2), U2615.3 (Q)
PD: U2610.9 (B0), U2610.10 (B1), U2613.9 (B0), U2613.10 (B1), U2614.2 (A0), U2614.3 (A1), U2617.5 (D2), U2619.5 (D2)
PU: U2609.6 (C2), U2609.11 (D1), U2610.1 (D0), U2610.6 (C2), U2610.11 (D1), U2611.12 (D2), U2611.13 (D3), U2612.1 (D0), U2612.4 (C0), U2613.1 (D0), U2613.4 (C0), U2613.11 (D1), U2614.4 (C0), U2614.13 (D3), U2616.6 (D0), U2618.6 (D0)
S0SPEC~: U2602.3 (Q), U2607.1 (D0), U2612.3 (A1), U2613.3 (A1), U2614.10 (B1)
SBIT0.B0: U2609.10 (B1), U2610.13 (D3), U2616.5 (D2), U2617.6 (D0)
SBIT0.B1: U2602.1 (D0), U2606.1 (D0), U2608.2 (D1), U2611.11 (D1), U2612.5 (C1), U2612.10 (B1), U2613.6 (C2), U2614.1 (D0)
SBIT0~: U2606.2 (Q), U2609.3 (A1), U2609.4 (C0), U2610.4 (C0), U2611.4 (C0)
SBIT1: U2609.2 (A0), U2610.5 (C1), U2611.5 (C1), U2612.9 (B0), U2613.5 (C1), U2614.11 (D1), U2616.3 (S0), U2617.3 (S0)
SBIT2: U2609.5 (C1), U2611.6 (C2), U2612.6 (C2), U2614.12 (D2), U2616.2 (S1), U2617.2 (S1)
SBIT3: U2616.1 (S2), U2617.1 (S2)
ST.EN~0: U2616.15 (Y0_)
ST.EN~1: U2616.14 (Y1_)
ST.EN~2: U2616.13 (Y2_)
ST.EN~3: U2616.12 (Y3_)
ST.EN~4: U2616.11 (Y4_)
ST.EN~5: U2616.10 (Y5_)
ST.EN~6: U2616.9 (Y6_)
ST.EN~7: U2616.7 (Y7_)
ST.EN~8: U2617.15 (Y0_)
ST.EN~9: U2617.14 (Y1_)
ST.EN~10: U2617.13 (Y2_)
ST.EN~11: U2617.12 (Y3_)
ST.EN~12: U2617.11 (Y4_)
ST.EN~13: U2617.10 (Y5_)
ST.EN~14: U2617.9 (Y6_)
ST.EN~15: U2617.7 (Y7_)
ZERO_LENGTH: U2601.2 (Q), U2616.4 (D1), U2617.4 (D1), U2618.4 (D1), U2619.4 (D1)
ZERO_LENGTH~: U2601.1 (D0), U2602.2 (D1), U2603.2 (D1), U2604.2 (D1), U2605.2 (D1)
