Datamuseum-DK/R1000.HwDoc/Schematics/FIU/pg_26.kicad_sch

## KiCad design Schematics/FIU/pg_26.kicad_sch (2023-01-10)

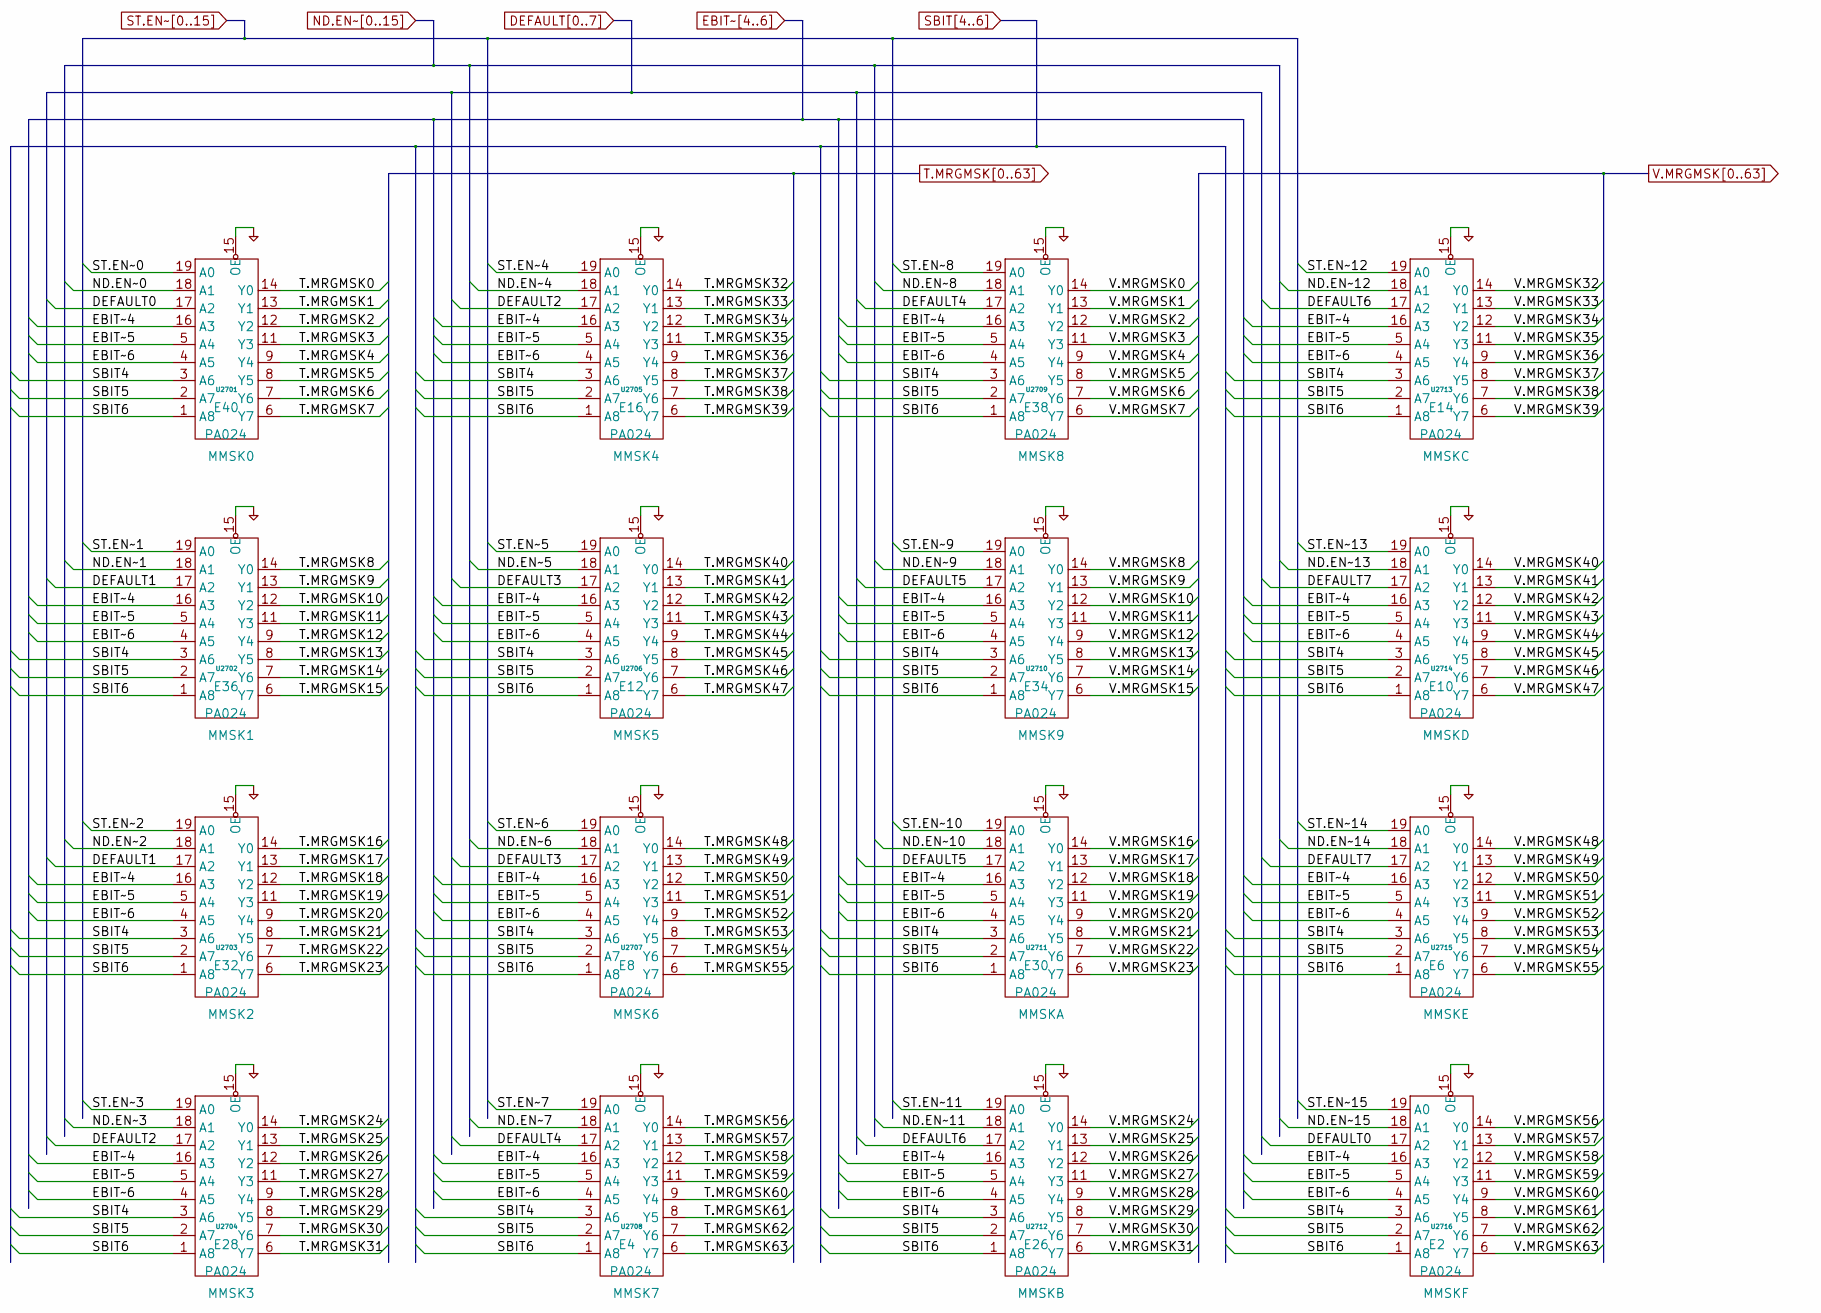
[picture p311: schematic pg_26.kicad_sch]

Parts:
U2701, U2702, U2703, U2704, U2705, U2706, U2707, U2708, U2709, U2710, U2711, U2712, U2713, U2714, U2715, U2716: PA024

Connections:
DEFAULT0: U2701.17 (A2), U2716.17 (A2)
DEFAULT1: U2702.17 (A2), U2703.17 (A2)
DEFAULT2: U2704.17 (A2), U2705.17 (A2)
DEFAULT3: U2706.17 (A2), U2707.17 (A2)
DEFAULT4: U2708.17 (A2), U2709.17 (A2)
DEFAULT5: U2710.17 (A2), U2711.17 (A2)
DEFAULT6: U2712.17 (A2), U2713.17 (A2)
DEFAULT7: U2714.17 (A2), U2715.17 (A2)
EBIT~4: U2701.16 (A3), U2702.16 (A3), U2703.16 (A3), U2704.16 (A3), U2705.16 (A3), U2706.16 (A3), U2707.16 (A3), U2708.16 (A3), U2709.16 (A3), U2710.16 (A3), U2711.16 (A3), U2712.16 (A3), U2713.16 (A3), U2714.16 (A3), U2715.16 (A3), U2716.16 (A3)
EBIT~5: U2701.5 (A4), U2702.5 (A4), U2703.5 (A4), U2704.5 (A4), U2705.5 (A4), U2706.5 (A4), U2707.5 (A4), U2708.5 (A4), U2709.5 (A4), U2710.5 (A4), U2711.5 (A4), U2712.5 (A4), U2713.5 (A4), U2714.5 (A4), U2715.5 (A4), U2716.5 (A4)
EBIT~6: U2701.4 (A5), U2702.4 (A5), U2703.4 (A5), U2704.4 (A5), U2705.4 (A5), U2706.4 (A5), U2707.4 (A5), U2708.4 (A5), U2709.4 (A5), U2710.4 (A5), U2711.4 (A5), U2712.4 (A5), U2713.4 (A5), U2714.4 (A5), U2715.4 (A5), U2716.4 (A5)
ND.EN~0: U2701.18 (A1)
ND.EN~1: U2702.18 (A1)
ND.EN~2: U2703.18 (A1)
ND.EN~3: U2704.18 (A1)
ND.EN~4: U2705.18 (A1)
ND.EN~5: U2706.18 (A1)
ND.EN~6: U2707.18 (A1)
ND.EN~7: U2708.18 (A1)
ND.EN~8: U2709.18 (A1)
ND.EN~9: U2710.18 (A1)
ND.EN~10: U2711.18 (A1)
ND.EN~11: U2712.18 (A1)
ND.EN~12: U2713.18 (A1)
ND.EN~13: U2714.18 (A1)
ND.EN~14: U2715.18 (A1)
ND.EN~15: U2716.18 (A1)
PD: U2701.15 (OE), U2702.15 (OE), U2703.15 (OE), U2704.15 (OE), U2705.15 (OE), U2706.15 (OE), U2707.15 (OE), U2708.15 (OE), U2709.15 (OE), U2710.15 (OE), U2711.15 (OE), U2712.15 (OE), U2713.15 (OE), U2714.15 (OE), U2715.15 (OE), U2716.15 (OE)
SBIT4: U2701.3 (A6), U2702.3 (A6), U2703.3 (A6), U2704.3 (A6), U2705.3 (A6), U2706.3 (A6), U2707.3 (A6), U2708.3 (A6), U2709.3 (A6), U2710.3 (A6), U2711.3 (A6), U2712.3 (A6), U2713.3 (A6), U2714.3 (A6), U2715.3 (A6), U2716.3 (A6)
SBIT5: U2701.2 (A7), U2702.2 (A7), U2703.2 (A7), U2704.2 (A7), U2705.2 (A7), U2706.2 (A7), U2707.2 (A7), U2708.2 (A7), U2709.2 (A7), U2710.2 (A7), U2711.2 (A7), U2712.2 (A7), U2713.2 (A7), U2714.2 (A7), U2715.2 (A7), U2716.2 (A7)
SBIT6: U2701.1 (A8), U2702.1 (A8), U2703.1 (A8), U2704.1 (A8), U2705.1 (A8), U2706.1 (A8), U2707.1 (A8), U2708.1 (A8), U2709.1 (A8), U2710.1 (A8), U2711.1 (A8), U2712.1 (A8), U2713.1 (A8), U2714.1 (A8), U2715.1 (A8), U2716.1 (A8)
ST.EN~0: U2701.19 (A0)
ST.EN~1: U2702.19 (A0)
ST.EN~2: U2703.19 (A0)
ST.EN~3: U2704.19 (A0)
ST.EN~4: U2705.19 (A0)
ST.EN~5: U2706.19 (A0)
ST.EN~6: U2707.19 (A0)
ST.EN~7: U2708.19 (A0)
ST.EN~8: U2709.19 (A0)
ST.EN~9: U2710.19 (A0)
ST.EN~10: U2711.19 (A0)
ST.EN~11: U2712.19 (A0)
ST.EN~12: U2713.19 (A0)
ST.EN~13: U2714.19 (A0)
ST.EN~14: U2715.19 (A0)
ST.EN~15: U2716.19 (A0)
T.MRGMSK0: U2701.14 (Y0)
T.MRGMSK1: U2701.13 (Y1)
T.MRGMSK2: U2701.12 (Y2)
T.MRGMSK3: U2701.11 (Y3)
T.MRGMSK4: U2701.9 (Y4)
T.MRGMSK5: U2701.8 (Y5)
T.MRGMSK6: U2701.7 (Y6)
T.MRGMSK7: U2701.6 (Y7)
T.MRGMSK8: U2702.14 (Y0)
T.MRGMSK9: U2702.13 (Y1)
T.MRGMSK10: U2702.12 (Y2)
T.MRGMSK11: U2702.11 (Y3)
T.MRGMSK12: U2702.9 (Y4)
T.MRGMSK13: U2702.8 (Y5)
T.MRGMSK14: U2702.7 (Y6)
T.MRGMSK15: U2702.6 (Y7)
T.MRGMSK16: U2703.14 (Y0)
T.MRGMSK17: U2703.13 (Y1)
T.MRGMSK18: U2703.12 (Y2)
T.MRGMSK19: U2703.11 (Y3)
T.MRGMSK20: U2703.9 (Y4)
T.MRGMSK21: U2703.8 (Y5)
T.MRGMSK22: U2703.7 (Y6)
T.MRGMSK23: U2703.6 (Y7)
T.MRGMSK24: U2704.14 (Y0)
T.MRGMSK25: U2704.13 (Y1)
T.MRGMSK26: U2704.12 (Y2)
T.MRGMSK27: U2704.11 (Y3)
T.MRGMSK28: U2704.9 (Y4)
T.MRGMSK29: U2704.8 (Y5)
T.MRGMSK30: U2704.7 (Y6)
T.MRGMSK31: U2704.6 (Y7)
T.MRGMSK32: U2705.14 (Y0)
T.MRGMSK33: U2705.13 (Y1)
T.MRGMSK34: U2705.12 (Y2)
T.MRGMSK35: U2705.11 (Y3)
T.MRGMSK36: U2705.9 (Y4)
T.MRGMSK37: U2705.8 (Y5)
T.MRGMSK38: U2705.7 (Y6)
T.MRGMSK39: U2705.6 (Y7)
T.MRGMSK40: U2706.14 (Y0)
T.MRGMSK41: U2706.13 (Y1)
T.MRGMSK42: U2706.12 (Y2)
T.MRGMSK43: U2706.11 (Y3)
T.MRGMSK44: U2706.9 (Y4)
T.MRGMSK45: U2706.8 (Y5)
T.MRGMSK46: U2706.7 (Y6)
T.MRGMSK47: U2706.6 (Y7)
T.MRGMSK48: U2707.14 (Y0)
T.MRGMSK49: U2707.13 (Y1)
T.MRGMSK50: U2707.12 (Y2)
T.MRGMSK51: U2707.11 (Y3)
T.MRGMSK52: U2707.9 (Y4)
T.MRGMSK53: U2707.8 (Y5)
T.MRGMSK54: U2707.7 (Y6)
T.MRGMSK55: U2707.6 (Y7)
T.MRGMSK56: U2708.14 (Y0)
T.MRGMSK57: U2708.13 (Y1)
T.MRGMSK58: U2708.12 (Y2)
T.MRGMSK59: U2708.11 (Y3)
T.MRGMSK60: U2708.9 (Y4)
T.MRGMSK61: U2708.8 (Y5)
T.MRGMSK62: U2708.7 (Y6)
T.MRGMSK63: U2708.6 (Y7)
V.MRGMSK0: U2709.14 (Y0)
V.MRGMSK1: U2709.13 (Y1)
V.MRGMSK2: U2709.12 (Y2)
V.MRGMSK3: U2709.11 (Y3)
V.MRGMSK4: U2709.9 (Y4)
V.MRGMSK5: U2709.8 (Y5)
V.MRGMSK6: U2709.7 (Y6)
V.MRGMSK7: U2709.6 (Y7)
V.MRGMSK8: U2710.14 (Y0)
V.MRGMSK9: U2710.13 (Y1)
V.MRGMSK10: U2710.12 (Y2)
V.MRGMSK11: U2710.11 (Y3)
V.MRGMSK12: U2710.9 (Y4)
V.MRGMSK13: U2710.8 (Y5)
V.MRGMSK14: U2710.7 (Y6)
V.MRGMSK15: U2710.6 (Y7)
V.MRGMSK16: U2711.14 (Y0)
V.MRGMSK17: U2711.13 (Y1)
V.MRGMSK18: U2711.12 (Y2)
V.MRGMSK19: U2711.11 (Y3)
V.MRGMSK20: U2711.9 (Y4)
V.MRGMSK21: U2711.8 (Y5)
V.MRGMSK22: U2711.7 (Y6)
V.MRGMSK23: U2711.6 (Y7)
V.MRGMSK24: U2712.14 (Y0)
V.MRGMSK25: U2712.13 (Y1)
V.MRGMSK26: U2712.12 (Y2)
V.MRGMSK27: U2712.11 (Y3)
V.MRGMSK28: U2712.9 (Y4)
V.MRGMSK29: U2712.8 (Y5)
V.MRGMSK30: U2712.7 (Y6)
V.MRGMSK31: U2712.6 (Y7)
V.MRGMSK32: U2713.14 (Y0)
V.MRGMSK33: U2713.13 (Y1)
V.MRGMSK34: U2713.12 (Y2)
V.MRGMSK35: U2713.11 (Y3)
V.MRGMSK36: U2713.9 (Y4)
V.MRGMSK37: U2713.8 (Y5)
V.MRGMSK38: U2713.7 (Y6)
V.MRGMSK39: U2713.6 (Y7)
V.MRGMSK40: U2714.14 (Y0)
V.MRGMSK41: U2714.13 (Y1)
V.MRGMSK42: U2714.12 (Y2)
V.MRGMSK43: U2714.11 (Y3)
V.MRGMSK44: U2714.9 (Y4)
V.MRGMSK45: U2714.8 (Y5)
V.MRGMSK46: U2714.7 (Y6)
V.MRGMSK47: U2714.6 (Y7)
V.MRGMSK48: U2715.14 (Y0)
V.MRGMSK49: U2715.13 (Y1)
V.MRGMSK50: U2715.12 (Y2)
V.MRGMSK51: U2715.11 (Y3)
V.MRGMSK52: U2715.9 (Y4)
V.MRGMSK53: U2715.8 (Y5)
V.MRGMSK54: U2715.7 (Y6)
V.MRGMSK55: U2715.6 (Y7)
V.MRGMSK56: U2716.14 (Y0)
V.MRGMSK57: U2716.13 (Y1)
V.MRGMSK58: U2716.12 (Y2)
V.MRGMSK59: U2716.11 (Y3)
V.MRGMSK60: U2716.9 (Y4)
V.MRGMSK61: U2716.8 (Y5)
V.MRGMSK62: U2716.7 (Y6)
V.MRGMSK63: U2716.6 (Y7)
