Datamuseum-DK/R1000.HwDoc/Schematics/FIU/pg_27.kicad_sch

## KiCad design Schematics/FIU/pg_27.kicad_sch (2023-01-10)

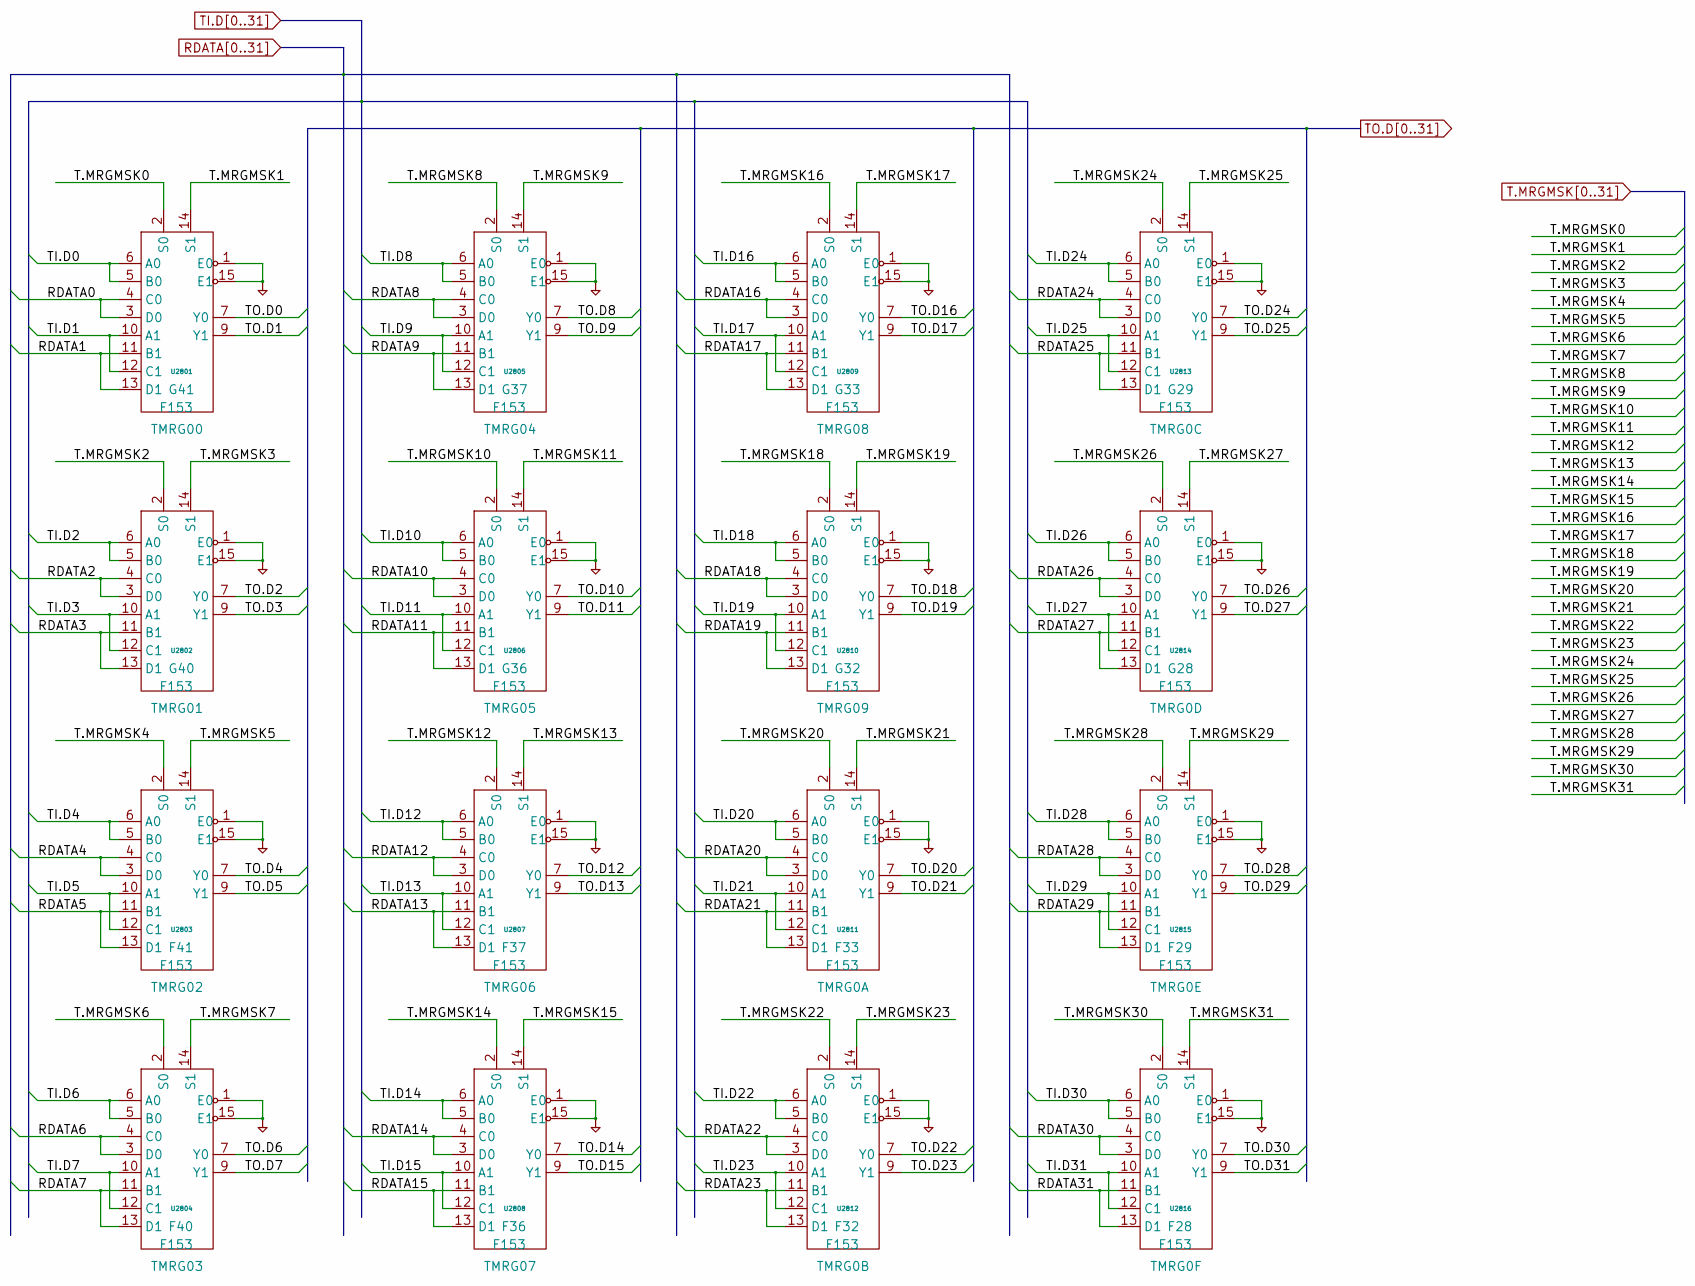
[picture p312: schematic pg_27.kicad_sch]

Parts:
U2801, U2802, U2803, U2804, U2805, U2806, U2807, U2808, U2809, U2810, U2811, U2812, U2813, U2814, U2815, U2816: F153

Connections:
PD: U2801.1 (E0), U2801.15 (E1), U2802.1 (E0), U2802.15 (E1), U2803.1 (E0), U2803.15 (E1), U2804.1 (E0), U2804.15 (E1), U2805.1 (E0), U2805.15 (E1), U2806.1 (E0), U2806.15 (E1), U2807.1 (E0), U2807.15 (E1), U2808.1 (E0), U2808.15 (E1), U2809.1 (E0), U2809.15 (E1), U2810.1 (E0), U2810.15 (E1), U2811.1 (E0), U2811.15 (E1), U2812.1 (E0), U2812.15 (E1), U2813.1 (E0), U2813.15 (E1), U2814.1 (E0), U2814.15 (E1), U2815.1 (E0), U2815.15 (E1), U2816.1 (E0), U2816.15 (E1)
RDATA0: U2801.3 (D0), U2801.4 (C0)
RDATA1: U2801.11 (B1), U2801.13 (D1)
RDATA2: U2802.3 (D0), U2802.4 (C0)
RDATA3: U2802.11 (B1), U2802.13 (D1)
RDATA4: U2803.3 (D0), U2803.4 (C0)
RDATA5: U2803.11 (B1), U2803.13 (D1)
RDATA6: U2804.3 (D0), U2804.4 (C0)
RDATA7: U2804.11 (B1), U2804.13 (D1)
RDATA8: U2805.3 (D0), U2805.4 (C0)
RDATA9: U2805.11 (B1), U2805.13 (D1)
RDATA10: U2806.3 (D0), U2806.4 (C0)
RDATA11: U2806.11 (B1), U2806.13 (D1)
RDATA12: U2807.3 (D0), U2807.4 (C0)
RDATA13: U2807.11 (B1), U2807.13 (D1)
RDATA14: U2808.3 (D0), U2808.4 (C0)
RDATA15: U2808.11 (B1), U2808.13 (D1)
RDATA16: U2809.3 (D0), U2809.4 (C0)
RDATA17: U2809.11 (B1), U2809.13 (D1)
RDATA18: U2810.3 (D0), U2810.4 (C0)
RDATA19: U2810.11 (B1), U2810.13 (D1)
RDATA20: U2811.3 (D0), U2811.4 (C0)
RDATA21: U2811.11 (B1), U2811.13 (D1)
RDATA22: U2812.3 (D0), U2812.4 (C0)
RDATA23: U2812.11 (B1), U2812.13 (D1)
RDATA24: U2813.3 (D0), U2813.4 (C0)
RDATA25: U2813.11 (B1), U2813.13 (D1)
RDATA26: U2814.3 (D0), U2814.4 (C0)
RDATA27: U2814.11 (B1), U2814.13 (D1)
RDATA28: U2815.3 (D0), U2815.4 (C0)
RDATA29: U2815.11 (B1), U2815.13 (D1)
RDATA30: U2816.3 (D0), U2816.4 (C0)
RDATA31: U2816.11 (B1), U2816.13 (D1)
T.MRGMSK0: U2801.2 (S0)
T.MRGMSK1: U2801.14 (S1)
T.MRGMSK2: U2802.2 (S0)
T.MRGMSK3: U2802.14 (S1)
T.MRGMSK4: U2803.2 (S0)
T.MRGMSK5: U2803.14 (S1)
T.MRGMSK6: U2804.2 (S0)
T.MRGMSK7: U2804.14 (S1)
T.MRGMSK8: U2805.2 (S0)
T.MRGMSK9: U2805.14 (S1)
T.MRGMSK10: U2806.2 (S0)
T.MRGMSK11: U2806.14 (S1)
T.MRGMSK12: U2807.2 (S0)
T.MRGMSK13: U2807.14 (S1)
T.MRGMSK14: U2808.2 (S0)
T.MRGMSK15: U2808.14 (S1)
T.MRGMSK16: U2809.2 (S0)
T.MRGMSK17: U2809.14 (S1)
T.MRGMSK18: U2810.2 (S0)
T.MRGMSK19: U2810.14 (S1)
T.MRGMSK20: U2811.2 (S0)
T.MRGMSK21: U2811.14 (S1)
T.MRGMSK22: U2812.2 (S0)
T.MRGMSK23: U2812.14 (S1)
T.MRGMSK24: U2813.2 (S0)
T.MRGMSK25: U2813.14 (S1)
T.MRGMSK26: U2814.2 (S0)
T.MRGMSK27: U2814.14 (S1)
T.MRGMSK28: U2815.2 (S0)
T.MRGMSK29: U2815.14 (S1)
T.MRGMSK30: U2816.2 (S0)
T.MRGMSK31: U2816.14 (S1)
TI.D0: U2801.5 (B0), U2801.6 (A0)
TI.D1: U2801.10 (A1), U2801.12 (C1)
TI.D2: U2802.5 (B0), U2802.6 (A0)
TI.D3: U2802.10 (A1), U2802.12 (C1)
TI.D4: U2803.5 (B0), U2803.6 (A0)
TI.D5: U2803.10 (A1), U2803.12 (C1)
TI.D6: U2804.5 (B0), U2804.6 (A0)
TI.D7: U2804.10 (A1), U2804.12 (C1)
TI.D8: U2805.5 (B0), U2805.6 (A0)
TI.D9: U2805.10 (A1), U2805.12 (C1)
TI.D10: U2806.5 (B0), U2806.6 (A0)
TI.D11: U2806.10 (A1), U2806.12 (C1)
TI.D12: U2807.5 (B0), U2807.6 (A0)
TI.D13: U2807.10 (A1), U2807.12 (C1)
TI.D14: U2808.5 (B0), U2808.6 (A0)
TI.D15: U2808.10 (A1), U2808.12 (C1)
TI.D16: U2809.5 (B0), U2809.6 (A0)
TI.D17: U2809.10 (A1), U2809.12 (C1)
TI.D18: U2810.5 (B0), U2810.6 (A0)
TI.D19: U2810.10 (A1), U2810.12 (C1)
TI.D20: U2811.5 (B0), U2811.6 (A0)
TI.D21: U2811.10 (A1), U2811.12 (C1)
TI.D22: U2812.5 (B0), U2812.6 (A0)
TI.D23: U2812.10 (A1), U2812.12 (C1)
TI.D24: U2813.5 (B0), U2813.6 (A0)
TI.D25: U2813.10 (A1), U2813.12 (C1)
TI.D26: U2814.5 (B0), U2814.6 (A0)
TI.D27: U2814.10 (A1), U2814.12 (C1)
TI.D28: U2815.5 (B0), U2815.6 (A0)
TI.D29: U2815.10 (A1), U2815.12 (C1)
TI.D30: U2816.5 (B0), U2816.6 (A0)
TI.D31: U2816.10 (A1), U2816.12 (C1)
TO.D0: U2801.7 (Y0)
TO.D1: U2801.9 (Y1)
TO.D2: U2802.7 (Y0)
TO.D3: U2802.9 (Y1)
TO.D4: U2803.7 (Y0)
TO.D5: U2803.9 (Y1)
TO.D6: U2804.7 (Y0)
TO.D7: U2804.9 (Y1)
TO.D8: U2805.7 (Y0)
TO.D9: U2805.9 (Y1)
TO.D10: U2806.7 (Y0)
TO.D11: U2806.9 (Y1)
TO.D12: U2807.7 (Y0)
TO.D13: U2807.9 (Y1)
TO.D14: U2808.7 (Y0)
TO.D15: U2808.9 (Y1)
TO.D16: U2809.7 (Y0)
TO.D17: U2809.9 (Y1)
TO.D18: U2810.7 (Y0)
TO.D19: U2810.9 (Y1)
TO.D20: U2811.7 (Y0)
TO.D21: U2811.9 (Y1)
TO.D22: U2812.7 (Y0)
TO.D23: U2812.9 (Y1)
TO.D24: U2813.7 (Y0)
TO.D25: U2813.9 (Y1)
TO.D26: U2814.7 (Y0)
TO.D27: U2814.9 (Y1)
TO.D28: U2815.7 (Y0)
TO.D29: U2815.9 (Y1)
TO.D30: U2816.7 (Y0)
TO.D31: U2816.9 (Y1)
