Datamuseum-DK/R1000.HwDoc/Schematics/FIU/pg_28.kicad_sch

## KiCad design Schematics/FIU/pg_28.kicad_sch (2023-01-10)

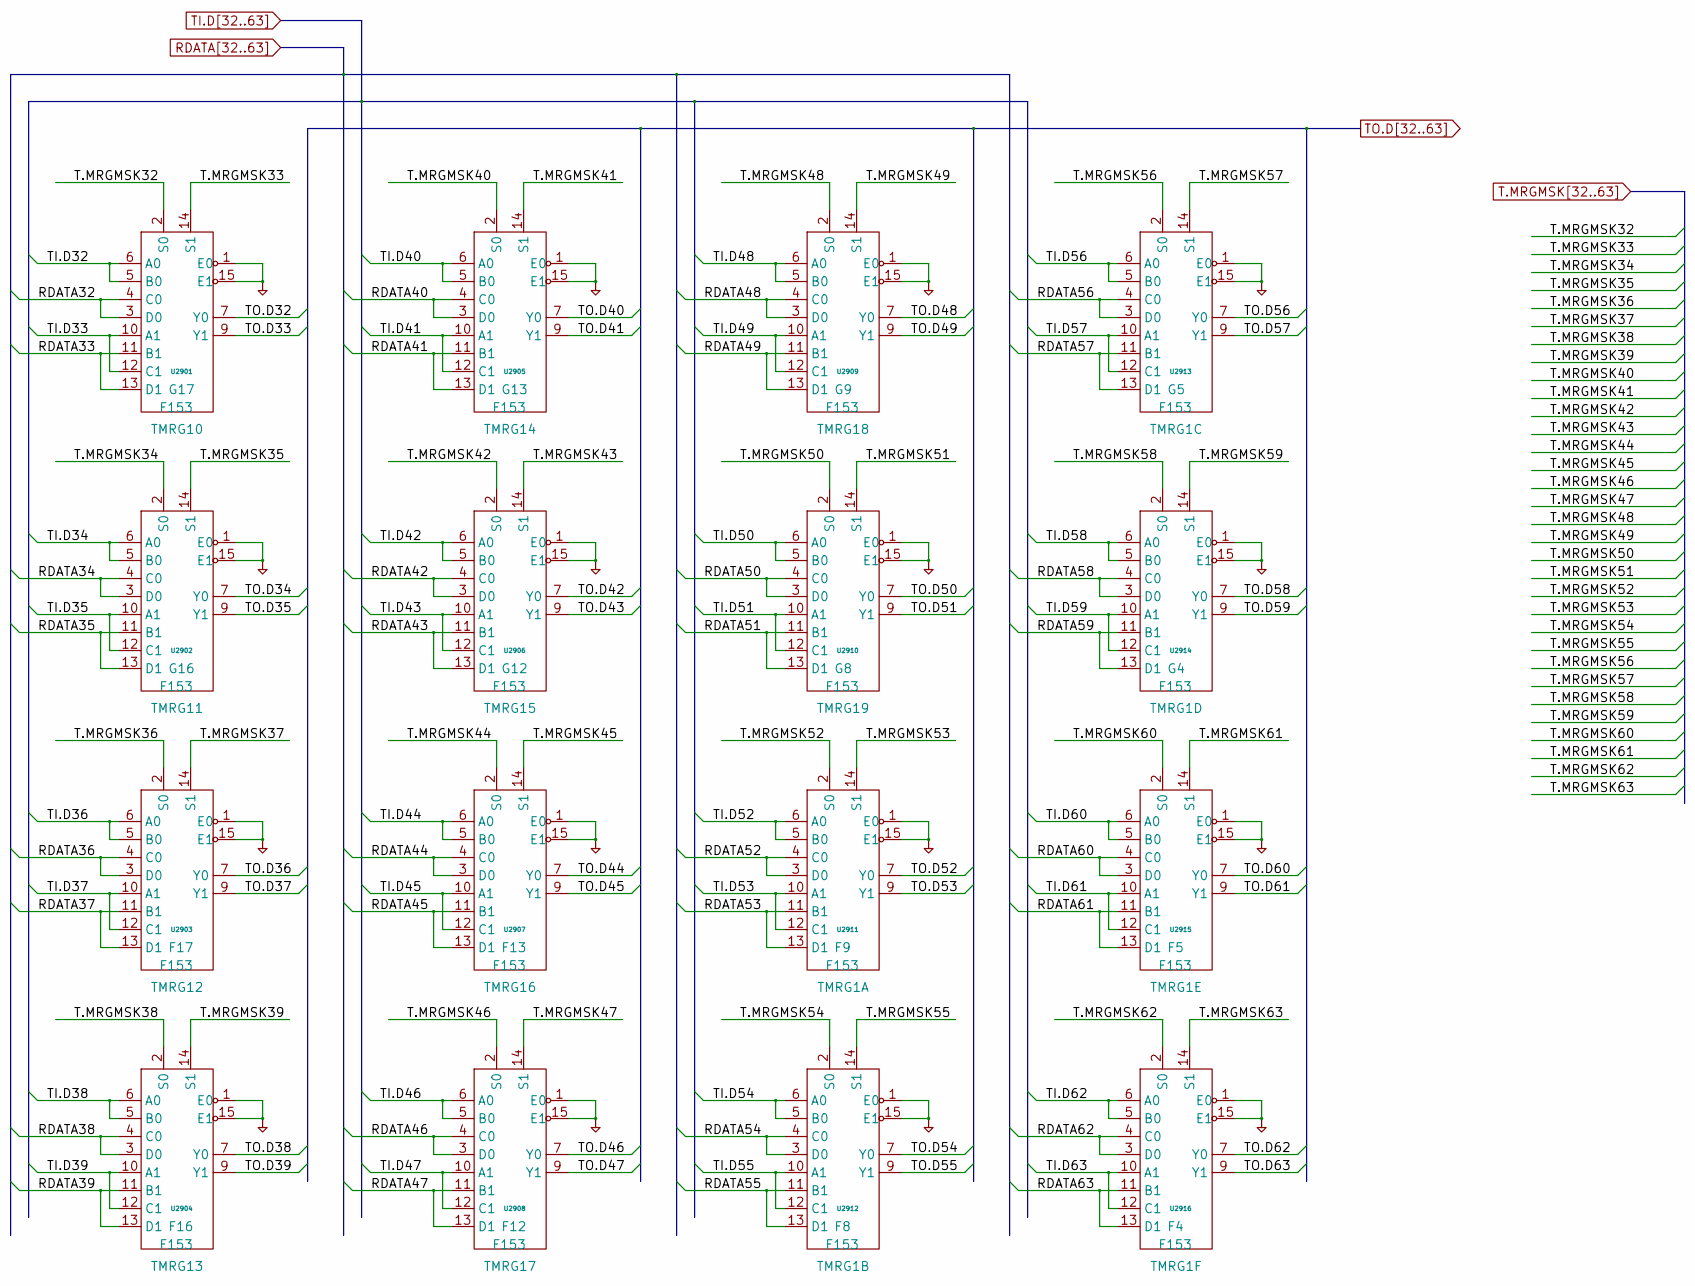
[picture p313: schematic pg_28.kicad_sch]

Parts:
U2901, U2902, U2903, U2904, U2905, U2906, U2907, U2908, U2909, U2910, U2911, U2912, U2913, U2914, U2915, U2916: F153

Connections:
PD: U2901.1 (E0), U2901.15 (E1), U2902.1 (E0), U2902.15 (E1), U2903.1 (E0), U2903.15 (E1), U2904.1 (E0), U2904.15 (E1), U2905.1 (E0), U2905.15 (E1), U2906.1 (E0), U2906.15 (E1), U2907.1 (E0), U2907.15 (E1), U2908.1 (E0), U2908.15 (E1), U2909.1 (E0), U2909.15 (E1), U2910.1 (E0), U2910.15 (E1), U2911.1 (E0), U2911.15 (E1), U2912.1 (E0), U2912.15 (E1), U2913.1 (E0), U2913.15 (E1), U2914.1 (E0), U2914.15 (E1), U2915.1 (E0), U2915.15 (E1), U2916.1 (E0), U2916.15 (E1)
RDATA32: U2901.3 (D0), U2901.4 (C0)
RDATA33: U2901.11 (B1), U2901.13 (D1)
RDATA34: U2902.3 (D0), U2902.4 (C0)
RDATA35: U2902.11 (B1), U2902.13 (D1)
RDATA36: U2903.3 (D0), U2903.4 (C0)
RDATA37: U2903.11 (B1), U2903.13 (D1)
RDATA38: U2904.3 (D0), U2904.4 (C0)
RDATA39: U2904.11 (B1), U2904.13 (D1)
RDATA40: U2905.3 (D0), U2905.4 (C0)
RDATA41: U2905.11 (B1), U2905.13 (D1)
RDATA42: U2906.3 (D0), U2906.4 (C0)
RDATA43: U2906.11 (B1), U2906.13 (D1)
RDATA44: U2907.3 (D0), U2907.4 (C0)
RDATA45: U2907.11 (B1), U2907.13 (D1)
RDATA46: U2908.3 (D0), U2908.4 (C0)
RDATA47: U2908.11 (B1), U2908.13 (D1)
RDATA48: U2909.3 (D0), U2909.4 (C0)
RDATA49: U2909.11 (B1), U2909.13 (D1)
RDATA50: U2910.3 (D0), U2910.4 (C0)
RDATA51: U2910.11 (B1), U2910.13 (D1)
RDATA52: U2911.3 (D0), U2911.4 (C0)
RDATA53: U2911.11 (B1), U2911.13 (D1)
RDATA54: U2912.3 (D0), U2912.4 (C0)
RDATA55: U2912.11 (B1), U2912.13 (D1)
RDATA56: U2913.3 (D0), U2913.4 (C0)
RDATA57: U2913.11 (B1), U2913.13 (D1)
RDATA58: U2914.3 (D0), U2914.4 (C0)
RDATA59: U2914.11 (B1), U2914.13 (D1)
RDATA60: U2915.3 (D0), U2915.4 (C0)
RDATA61: U2915.11 (B1), U2915.13 (D1)
RDATA62: U2916.3 (D0), U2916.4 (C0)
RDATA63: U2916.11 (B1), U2916.13 (D1)
T.MRGMSK32: U2901.2 (S0)
T.MRGMSK33: U2901.14 (S1)
T.MRGMSK34: U2902.2 (S0)
T.MRGMSK35: U2902.14 (S1)
T.MRGMSK36: U2903.2 (S0)
T.MRGMSK37: U2903.14 (S1)
T.MRGMSK38: U2904.2 (S0)
T.MRGMSK39: U2904.14 (S1)
T.MRGMSK40: U2905.2 (S0)
T.MRGMSK41: U2905.14 (S1)
T.MRGMSK42: U2906.2 (S0)
T.MRGMSK43: U2906.14 (S1)
T.MRGMSK44: U2907.2 (S0)
T.MRGMSK45: U2907.14 (S1)
T.MRGMSK46: U2908.2 (S0)
T.MRGMSK47: U2908.14 (S1)
T.MRGMSK48: U2909.2 (S0)
T.MRGMSK49: U2909.14 (S1)
T.MRGMSK50: U2910.2 (S0)
T.MRGMSK51: U2910.14 (S1)
T.MRGMSK52: U2911.2 (S0)
T.MRGMSK53: U2911.14 (S1)
T.MRGMSK54: U2912.2 (S0)
T.MRGMSK55: U2912.14 (S1)
T.MRGMSK56: U2913.2 (S0)
T.MRGMSK57: U2913.14 (S1)
T.MRGMSK58: U2914.2 (S0)
T.MRGMSK59: U2914.14 (S1)
T.MRGMSK60: U2915.2 (S0)
T.MRGMSK61: U2915.14 (S1)
T.MRGMSK62: U2916.2 (S0)
T.MRGMSK63: U2916.14 (S1)
TI.D32: U2901.5 (B0), U2901.6 (A0)
TI.D33: U2901.10 (A1), U2901.12 (C1)
TI.D34: U2902.5 (B0), U2902.6 (A0)
TI.D35: U2902.10 (A1), U2902.12 (C1)
TI.D36: U2903.5 (B0), U2903.6 (A0)
TI.D37: U2903.10 (A1), U2903.12 (C1)
TI.D38: U2904.5 (B0), U2904.6 (A0)
TI.D39: U2904.10 (A1), U2904.12 (C1)
TI.D40: U2905.5 (B0), U2905.6 (A0)
TI.D41: U2905.10 (A1), U2905.12 (C1)
TI.D42: U2906.5 (B0), U2906.6 (A0)
TI.D43: U2906.10 (A1), U2906.12 (C1)
TI.D44: U2907.5 (B0), U2907.6 (A0)
TI.D45: U2907.10 (A1), U2907.12 (C1)
TI.D46: U2908.5 (B0), U2908.6 (A0)
TI.D47: U2908.10 (A1), U2908.12 (C1)
TI.D48: U2909.5 (B0), U2909.6 (A0)
TI.D49: U2909.10 (A1), U2909.12 (C1)
TI.D50: U2910.5 (B0), U2910.6 (A0)
TI.D51: U2910.10 (A1), U2910.12 (C1)
TI.D52: U2911.5 (B0), U2911.6 (A0)
TI.D53: U2911.10 (A1), U2911.12 (C1)
TI.D54: U2912.5 (B0), U2912.6 (A0)
TI.D55: U2912.10 (A1), U2912.12 (C1)
TI.D56: U2913.5 (B0), U2913.6 (A0)
TI.D57: U2913.10 (A1), U2913.12 (C1)
TI.D58: U2914.5 (B0), U2914.6 (A0)
TI.D59: U2914.10 (A1), U2914.12 (C1)
TI.D60: U2915.5 (B0), U2915.6 (A0)
TI.D61: U2915.10 (A1), U2915.12 (C1)
TI.D62: U2916.5 (B0), U2916.6 (A0)
TI.D63: U2916.10 (A1), U2916.12 (C1)
TO.D32: U2901.7 (Y0)
TO.D33: U2901.9 (Y1)
TO.D34: U2902.7 (Y0)
TO.D35: U2902.9 (Y1)
TO.D36: U2903.7 (Y0)
TO.D37: U2903.9 (Y1)
TO.D38: U2904.7 (Y0)
TO.D39: U2904.9 (Y1)
TO.D40: U2905.7 (Y0)
TO.D41: U2905.9 (Y1)
TO.D42: U2906.7 (Y0)
TO.D43: U2906.9 (Y1)
TO.D44: U2907.7 (Y0)
TO.D45: U2907.9 (Y1)
TO.D46: U2908.7 (Y0)
TO.D47: U2908.9 (Y1)
TO.D48: U2909.7 (Y0)
TO.D49: U2909.9 (Y1)
TO.D50: U2910.7 (Y0)
TO.D51: U2910.9 (Y1)
TO.D52: U2911.7 (Y0)
TO.D53: U2911.9 (Y1)
TO.D54: U2912.7 (Y0)
TO.D55: U2912.9 (Y1)
TO.D56: U2913.7 (Y0)
TO.D57: U2913.9 (Y1)
TO.D58: U2914.7 (Y0)
TO.D59: U2914.9 (Y1)
TO.D60: U2915.7 (Y0)
TO.D61: U2915.9 (Y1)
TO.D62: U2916.7 (Y0)
TO.D63: U2916.9 (Y1)
