Datamuseum-DK/R1000.HwDoc/Schematics/FIU/pg_29.kicad_sch

## KiCad design Schematics/FIU/pg_29.kicad_sch (2023-01-10)

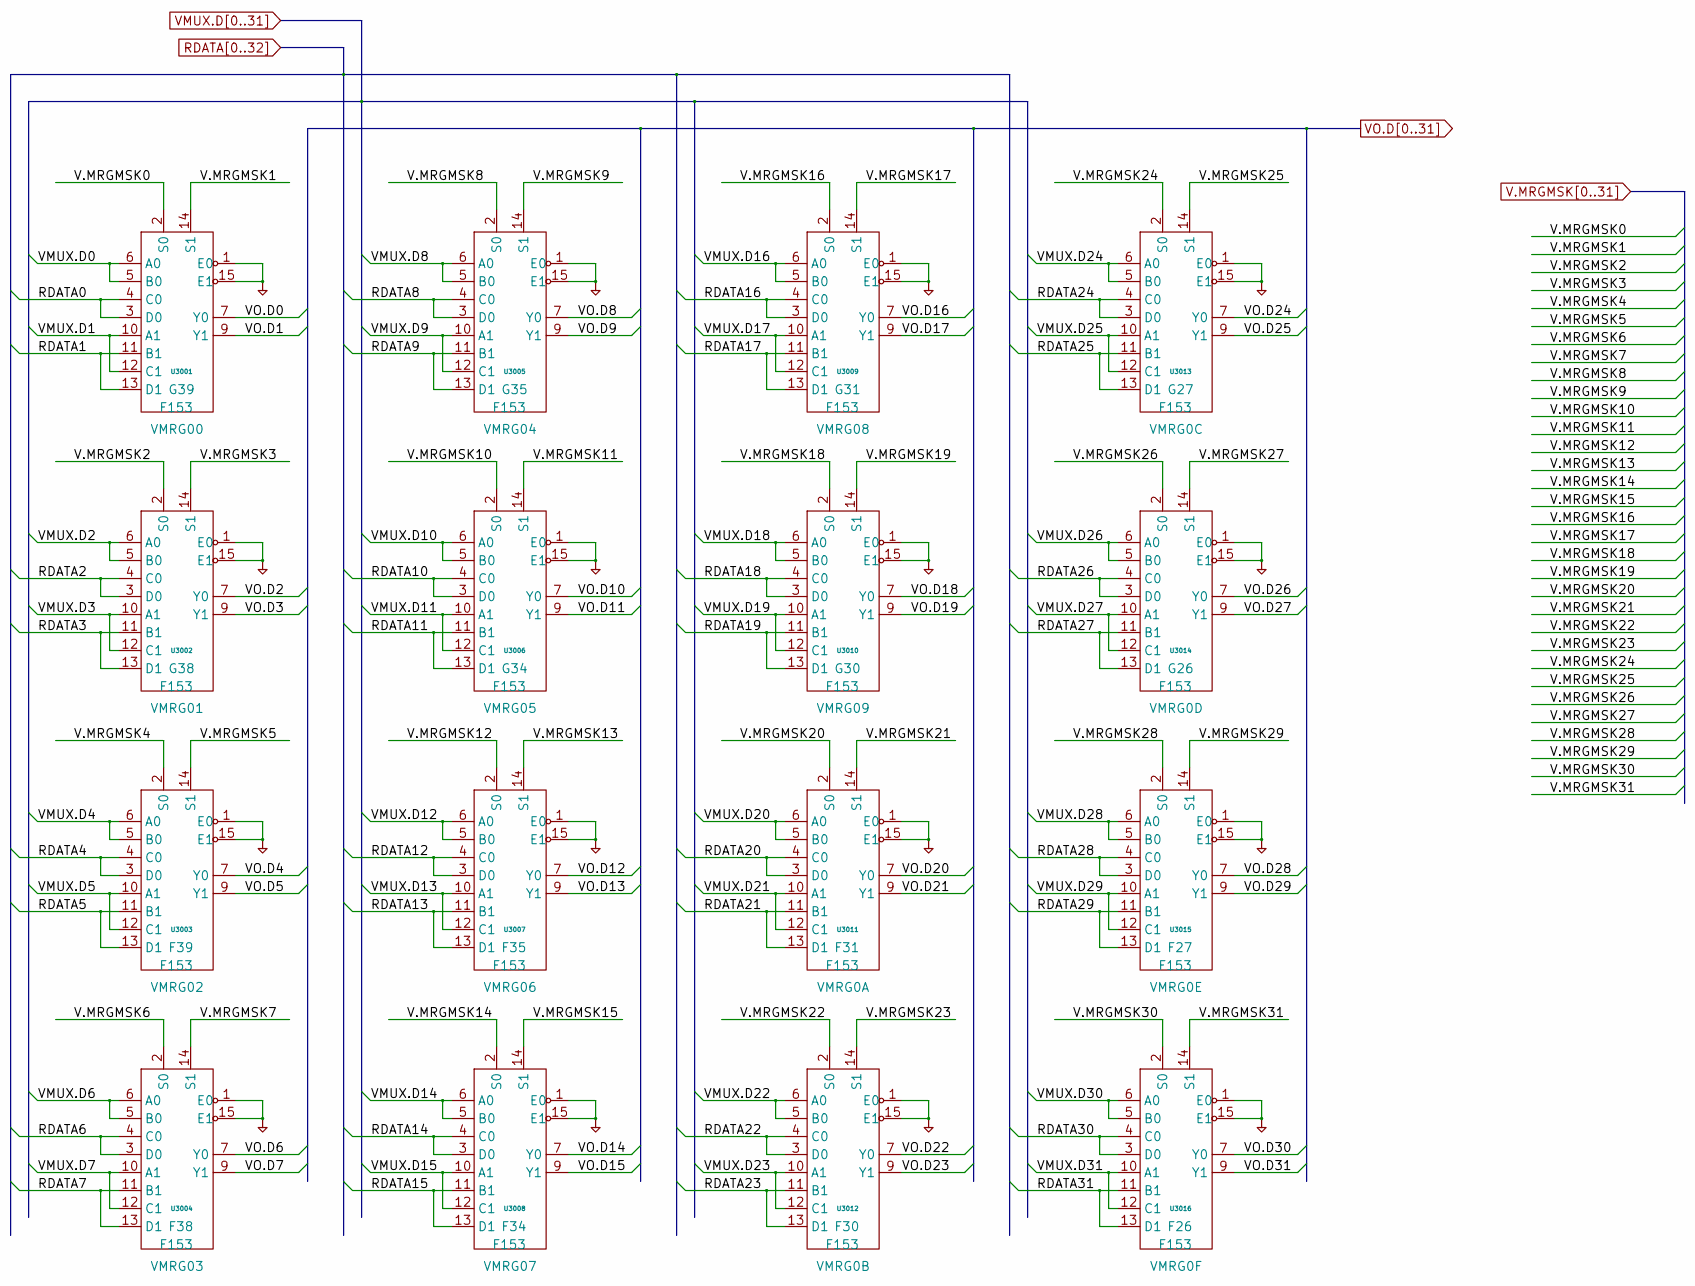
[picture p314: schematic pg_29.kicad_sch]

Parts:
U3001, U3002, U3003, U3004, U3005, U3006, U3007, U3008, U3009, U3010, U3011, U3012, U3013, U3014, U3015, U3016: F153

Connections:
PD: U3001.1 (E0), U3001.15 (E1), U3002.1 (E0), U3002.15 (E1), U3003.1 (E0), U3003.15 (E1), U3004.1 (E0), U3004.15 (E1), U3005.1 (E0), U3005.15 (E1), U3006.1 (E0), U3006.15 (E1), U3007.1 (E0), U3007.15 (E1), U3008.1 (E0), U3008.15 (E1), U3009.1 (E0), U3009.15 (E1), U3010.1 (E0), U3010.15 (E1), U3011.1 (E0), U3011.15 (E1), U3012.1 (E0), U3012.15 (E1), U3013.1 (E0), U3013.15 (E1), U3014.1 (E0), U3014.15 (E1), U3015.1 (E0), U3015.15 (E1), U3016.1 (E0), U3016.15 (E1)
RDATA0: U3001.3 (D0), U3001.4 (C0)
RDATA1: U3001.11 (B1), U3001.13 (D1)
RDATA2: U3002.3 (D0), U3002.4 (C0)
RDATA3: U3002.11 (B1), U3002.13 (D1)
RDATA4: U3003.3 (D0), U3003.4 (C0)
RDATA5: U3003.11 (B1), U3003.13 (D1)
RDATA6: U3004.3 (D0), U3004.4 (C0)
RDATA7: U3004.11 (B1), U3004.13 (D1)
RDATA8: U3005.3 (D0), U3005.4 (C0)
RDATA9: U3005.11 (B1), U3005.13 (D1)
RDATA10: U3006.3 (D0), U3006.4 (C0)
RDATA11: U3006.11 (B1), U3006.13 (D1)
RDATA12: U3007.3 (D0), U3007.4 (C0)
RDATA13: U3007.11 (B1), U3007.13 (D1)
RDATA14: U3008.3 (D0), U3008.4 (C0)
RDATA15: U3008.11 (B1), U3008.13 (D1)
RDATA16: U3009.3 (D0), U3009.4 (C0)
RDATA17: U3009.11 (B1), U3009.13 (D1)
RDATA18: U3010.3 (D0), U3010.4 (C0)
RDATA19: U3010.11 (B1), U3010.13 (D1)
RDATA20: U3011.3 (D0), U3011.4 (C0)
RDATA21: U3011.11 (B1), U3011.13 (D1)
RDATA22: U3012.3 (D0), U3012.4 (C0)
RDATA23: U3012.11 (B1), U3012.13 (D1)
RDATA24: U3013.3 (D0), U3013.4 (C0)
RDATA25: U3013.11 (B1), U3013.13 (D1)
RDATA26: U3014.3 (D0), U3014.4 (C0)
RDATA27: U3014.11 (B1), U3014.13 (D1)
RDATA28: U3015.3 (D0), U3015.4 (C0)
RDATA29: U3015.11 (B1), U3015.13 (D1)
RDATA30: U3016.3 (D0), U3016.4 (C0)
RDATA31: U3016.11 (B1), U3016.13 (D1)
V.MRGMSK0: U3001.2 (S0)
V.MRGMSK1: U3001.14 (S1)
V.MRGMSK2: U3002.2 (S0)
V.MRGMSK3: U3002.14 (S1)
V.MRGMSK4: U3003.2 (S0)
V.MRGMSK5: U3003.14 (S1)
V.MRGMSK6: U3004.2 (S0)
V.MRGMSK7: U3004.14 (S1)
V.MRGMSK8: U3005.2 (S0)
V.MRGMSK9: U3005.14 (S1)
V.MRGMSK10: U3006.2 (S0)
V.MRGMSK11: U3006.14 (S1)
V.MRGMSK12: U3007.2 (S0)
V.MRGMSK13: U3007.14 (S1)
V.MRGMSK14: U3008.2 (S0)
V.MRGMSK15: U3008.14 (S1)
V.MRGMSK16: U3009.2 (S0)
V.MRGMSK17: U3009.14 (S1)
V.MRGMSK18: U3010.2 (S0)
V.MRGMSK19: U3010.14 (S1)
V.MRGMSK20: U3011.2 (S0)
V.MRGMSK21: U3011.14 (S1)
V.MRGMSK22: U3012.2 (S0)
V.MRGMSK23: U3012.14 (S1)
V.MRGMSK24: U3013.2 (S0)
V.MRGMSK25: U3013.14 (S1)
V.MRGMSK26: U3014.2 (S0)
V.MRGMSK27: U3014.14 (S1)
V.MRGMSK28: U3015.2 (S0)
V.MRGMSK29: U3015.14 (S1)
V.MRGMSK30: U3016.2 (S0)
V.MRGMSK31: U3016.14 (S1)
VMUX.D0: U3001.5 (B0), U3001.6 (A0)
VMUX.D1: U3001.10 (A1), U3001.12 (C1)
VMUX.D2: U3002.5 (B0), U3002.6 (A0)
VMUX.D3: U3002.10 (A1), U3002.12 (C1)
VMUX.D4: U3003.5 (B0), U3003.6 (A0)
VMUX.D5: U3003.10 (A1), U3003.12 (C1)
VMUX.D6: U3004.5 (B0), U3004.6 (A0)
VMUX.D7: U3004.10 (A1), U3004.12 (C1)
VMUX.D8: U3005.5 (B0), U3005.6 (A0)
VMUX.D9: U3005.10 (A1), U3005.12 (C1)
VMUX.D10: U3006.5 (B0), U3006.6 (A0)
VMUX.D11: U3006.10 (A1), U3006.12 (C1)
VMUX.D12: U3007.5 (B0), U3007.6 (A0)
VMUX.D13: U3007.10 (A1), U3007.12 (C1)
VMUX.D14: U3008.5 (B0), U3008.6 (A0)
VMUX.D15: U3008.10 (A1), U3008.12 (C1)
VMUX.D16: U3009.5 (B0), U3009.6 (A0)
VMUX.D17: U3009.10 (A1), U3009.12 (C1)
VMUX.D18: U3010.5 (B0), U3010.6 (A0)
VMUX.D19: U3010.10 (A1), U3010.12 (C1)
VMUX.D20: U3011.5 (B0), U3011.6 (A0)
VMUX.D21: U3011.10 (A1), U3011.12 (C1)
VMUX.D22: U3012.5 (B0), U3012.6 (A0)
VMUX.D23: U3012.10 (A1), U3012.12 (C1)
VMUX.D24: U3013.5 (B0), U3013.6 (A0)
VMUX.D25: U3013.10 (A1), U3013.12 (C1)
VMUX.D26: U3014.5 (B0), U3014.6 (A0)
VMUX.D27: U3014.10 (A1), U3014.12 (C1)
VMUX.D28: U3015.5 (B0), U3015.6 (A0)
VMUX.D29: U3015.10 (A1), U3015.12 (C1)
VMUX.D30: U3016.5 (B0), U3016.6 (A0)
VMUX.D31: U3016.10 (A1), U3016.12 (C1)
VO.D0: U3001.7 (Y0)
VO.D1: U3001.9 (Y1)
VO.D2: U3002.7 (Y0)
VO.D3: U3002.9 (Y1)
VO.D4: U3003.7 (Y0)
VO.D5: U3003.9 (Y1)
VO.D6: U3004.7 (Y0)
VO.D7: U3004.9 (Y1)
VO.D8: U3005.7 (Y0)
VO.D9: U3005.9 (Y1)
VO.D10: U3006.7 (Y0)
VO.D11: U3006.9 (Y1)
VO.D12: U3007.7 (Y0)
VO.D13: U3007.9 (Y1)
VO.D14: U3008.7 (Y0)
VO.D15: U3008.9 (Y1)
VO.D16: U3009.7 (Y0)
VO.D17: U3009.9 (Y1)
VO.D18: U3010.7 (Y0)
VO.D19: U3010.9 (Y1)
VO.D20: U3011.7 (Y0)
VO.D21: U3011.9 (Y1)
VO.D22: U3012.7 (Y0)
VO.D23: U3012.9 (Y1)
VO.D24: U3013.7 (Y0)
VO.D25: U3013.9 (Y1)
VO.D26: U3014.7 (Y0)
VO.D27: U3014.9 (Y1)
VO.D28: U3015.7 (Y0)
VO.D29: U3015.9 (Y1)
VO.D30: U3016.7 (Y0)
VO.D31: U3016.9 (Y1)
