Datamuseum-DK/R1000.HwDoc/Schematics/FIU/pg_30.kicad_sch

## KiCad design Schematics/FIU/pg_30.kicad_sch (2023-01-10)

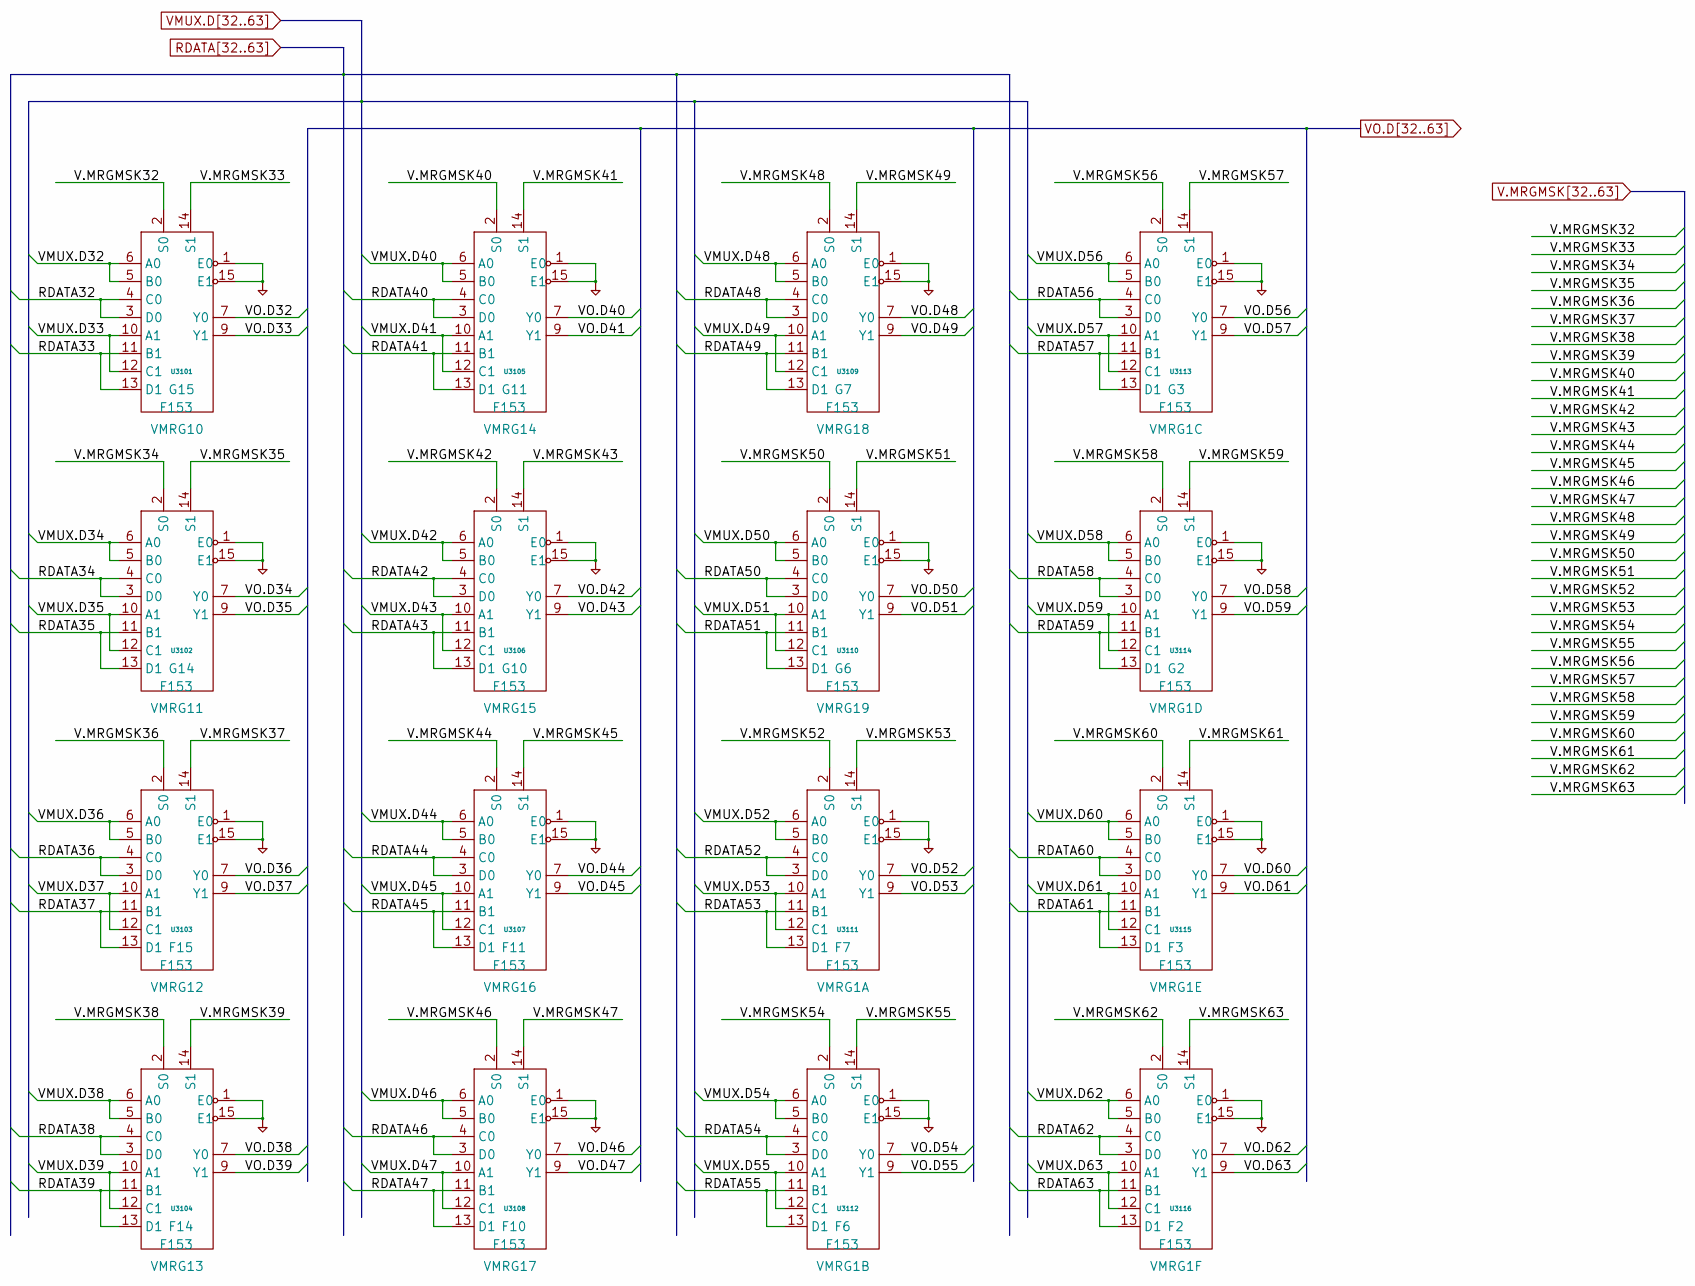
[picture p315: schematic pg_30.kicad_sch]

Parts:
U3101, U3102, U3103, U3104, U3105, U3106, U3107, U3108, U3109, U3110, U3111, U3112, U3113, U3114, U3115, U3116: F153

Connections:
PD: U3101.1 (E0), U3101.15 (E1), U3102.1 (E0), U3102.15 (E1), U3103.1 (E0), U3103.15 (E1), U3104.1 (E0), U3104.15 (E1), U3105.1 (E0), U3105.15 (E1), U3106.1 (E0), U3106.15 (E1), U3107.1 (E0), U3107.15 (E1), U3108.1 (E0), U3108.15 (E1), U3109.1 (E0), U3109.15 (E1), U3110.1 (E0), U3110.15 (E1), U3111.1 (E0), U3111.15 (E1), U3112.1 (E0), U3112.15 (E1), U3113.1 (E0), U3113.15 (E1), U3114.1 (E0), U3114.15 (E1), U3115.1 (E0), U3115.15 (E1), U3116.1 (E0), U3116.15 (E1)
RDATA32: U3101.3 (D0), U3101.4 (C0)
RDATA33: U3101.11 (B1), U3101.13 (D1)
RDATA34: U3102.3 (D0), U3102.4 (C0)
RDATA35: U3102.11 (B1), U3102.13 (D1)
RDATA36: U3103.3 (D0), U3103.4 (C0)
RDATA37: U3103.11 (B1), U3103.13 (D1)
RDATA38: U3104.3 (D0), U3104.4 (C0)
RDATA39: U3104.11 (B1), U3104.13 (D1)
RDATA40: U3105.3 (D0), U3105.4 (C0)
RDATA41: U3105.11 (B1), U3105.13 (D1)
RDATA42: U3106.3 (D0), U3106.4 (C0)
RDATA43: U3106.11 (B1), U3106.13 (D1)
RDATA44: U3107.3 (D0), U3107.4 (C0)
RDATA45: U3107.11 (B1), U3107.13 (D1)
RDATA46: U3108.3 (D0), U3108.4 (C0)
RDATA47: U3108.11 (B1), U3108.13 (D1)
RDATA48: U3109.3 (D0), U3109.4 (C0)
RDATA49: U3109.11 (B1), U3109.13 (D1)
RDATA50: U3110.3 (D0), U3110.4 (C0)
RDATA51: U3110.11 (B1), U3110.13 (D1)
RDATA52: U3111.3 (D0), U3111.4 (C0)
RDATA53: U3111.11 (B1), U3111.13 (D1)
RDATA54: U3112.3 (D0), U3112.4 (C0)
RDATA55: U3112.11 (B1), U3112.13 (D1)
RDATA56: U3113.3 (D0), U3113.4 (C0)
RDATA57: U3113.11 (B1), U3113.13 (D1)
RDATA58: U3114.3 (D0), U3114.4 (C0)
RDATA59: U3114.11 (B1), U3114.13 (D1)
RDATA60: U3115.3 (D0), U3115.4 (C0)
RDATA61: U3115.11 (B1), U3115.13 (D1)
RDATA62: U3116.3 (D0), U3116.4 (C0)
RDATA63: U3116.11 (B1), U3116.13 (D1)
V.MRGMSK32: U3101.2 (S0)
V.MRGMSK33: U3101.14 (S1)
V.MRGMSK34: U3102.2 (S0)
V.MRGMSK35: U3102.14 (S1)
V.MRGMSK36: U3103.2 (S0)
V.MRGMSK37: U3103.14 (S1)
V.MRGMSK38: U3104.2 (S0)
V.MRGMSK39: U3104.14 (S1)
V.MRGMSK40: U3105.2 (S0)
V.MRGMSK41: U3105.14 (S1)
V.MRGMSK42: U3106.2 (S0)
V.MRGMSK43: U3106.14 (S1)
V.MRGMSK44: U3107.2 (S0)
V.MRGMSK45: U3107.14 (S1)
V.MRGMSK46: U3108.2 (S0)
V.MRGMSK47: U3108.14 (S1)
V.MRGMSK48: U3109.2 (S0)
V.MRGMSK49: U3109.14 (S1)
V.MRGMSK50: U3110.2 (S0)
V.MRGMSK51: U3110.14 (S1)
V.MRGMSK52: U3111.2 (S0)
V.MRGMSK53: U3111.14 (S1)
V.MRGMSK54: U3112.2 (S0)
V.MRGMSK55: U3112.14 (S1)
V.MRGMSK56: U3113.2 (S0)
V.MRGMSK57: U3113.14 (S1)
V.MRGMSK58: U3114.2 (S0)
V.MRGMSK59: U3114.14 (S1)
V.MRGMSK60: U3115.2 (S0)
V.MRGMSK61: U3115.14 (S1)
V.MRGMSK62: U3116.2 (S0)
V.MRGMSK63: U3116.14 (S1)
VMUX.D32: U3101.5 (B0), U3101.6 (A0)
VMUX.D33: U3101.10 (A1), U3101.12 (C1)
VMUX.D34: U3102.5 (B0), U3102.6 (A0)
VMUX.D35: U3102.10 (A1), U3102.12 (C1)
VMUX.D36: U3103.5 (B0), U3103.6 (A0)
VMUX.D37: U3103.10 (A1), U3103.12 (C1)
VMUX.D38: U3104.5 (B0), U3104.6 (A0)
VMUX.D39: U3104.10 (A1), U3104.12 (C1)
VMUX.D40: U3105.5 (B0), U3105.6 (A0)
VMUX.D41: U3105.10 (A1), U3105.12 (C1)
VMUX.D42: U3106.5 (B0), U3106.6 (A0)
VMUX.D43: U3106.10 (A1), U3106.12 (C1)
VMUX.D44: U3107.5 (B0), U3107.6 (A0)
VMUX.D45: U3107.10 (A1), U3107.12 (C1)
VMUX.D46: U3108.5 (B0), U3108.6 (A0)
VMUX.D47: U3108.10 (A1), U3108.12 (C1)
VMUX.D48: U3109.5 (B0), U3109.6 (A0)
VMUX.D49: U3109.10 (A1), U3109.12 (C1)
VMUX.D50: U3110.5 (B0), U3110.6 (A0)
VMUX.D51: U3110.10 (A1), U3110.12 (C1)
VMUX.D52: U3111.5 (B0), U3111.6 (A0)
VMUX.D53: U3111.10 (A1), U3111.12 (C1)
VMUX.D54: U3112.5 (B0), U3112.6 (A0)
VMUX.D55: U3112.10 (A1), U3112.12 (C1)
VMUX.D56: U3113.5 (B0), U3113.6 (A0)
VMUX.D57: U3113.10 (A1), U3113.12 (C1)
VMUX.D58: U3114.5 (B0), U3114.6 (A0)
VMUX.D59: U3114.10 (A1), U3114.12 (C1)
VMUX.D60: U3115.5 (B0), U3115.6 (A0)
VMUX.D61: U3115.10 (A1), U3115.12 (C1)
VMUX.D62: U3116.5 (B0), U3116.6 (A0)
VMUX.D63: U3116.10 (A1), U3116.12 (C1)
VO.D32: U3101.7 (Y0)
VO.D33: U3101.9 (Y1)
VO.D34: U3102.7 (Y0)
VO.D35: U3102.9 (Y1)
VO.D36: U3103.7 (Y0)
VO.D37: U3103.9 (Y1)
VO.D38: U3104.7 (Y0)
VO.D39: U3104.9 (Y1)
VO.D40: U3105.7 (Y0)
VO.D41: U3105.9 (Y1)
VO.D42: U3106.7 (Y0)
VO.D43: U3106.9 (Y1)
VO.D44: U3107.7 (Y0)
VO.D45: U3107.9 (Y1)
VO.D46: U3108.7 (Y0)
VO.D47: U3108.9 (Y1)
VO.D48: U3109.7 (Y0)
VO.D49: U3109.9 (Y1)
VO.D50: U3110.7 (Y0)
VO.D51: U3110.9 (Y1)
VO.D52: U3111.7 (Y0)
VO.D53: U3111.9 (Y1)
VO.D54: U3112.7 (Y0)
VO.D55: U3112.9 (Y1)
VO.D56: U3113.7 (Y0)
VO.D57: U3113.9 (Y1)
VO.D58: U3114.7 (Y0)
VO.D59: U3114.9 (Y1)
VO.D60: U3115.7 (Y0)
VO.D61: U3115.9 (Y1)
VO.D62: U3116.7 (Y0)
VO.D63: U3116.9 (Y1)
