Datamuseum-DK/R1000.HwDoc/Schematics/FIU/pg_31.kicad_sch

## KiCad design Schematics/FIU/pg_31.kicad_sch (2023-01-10)

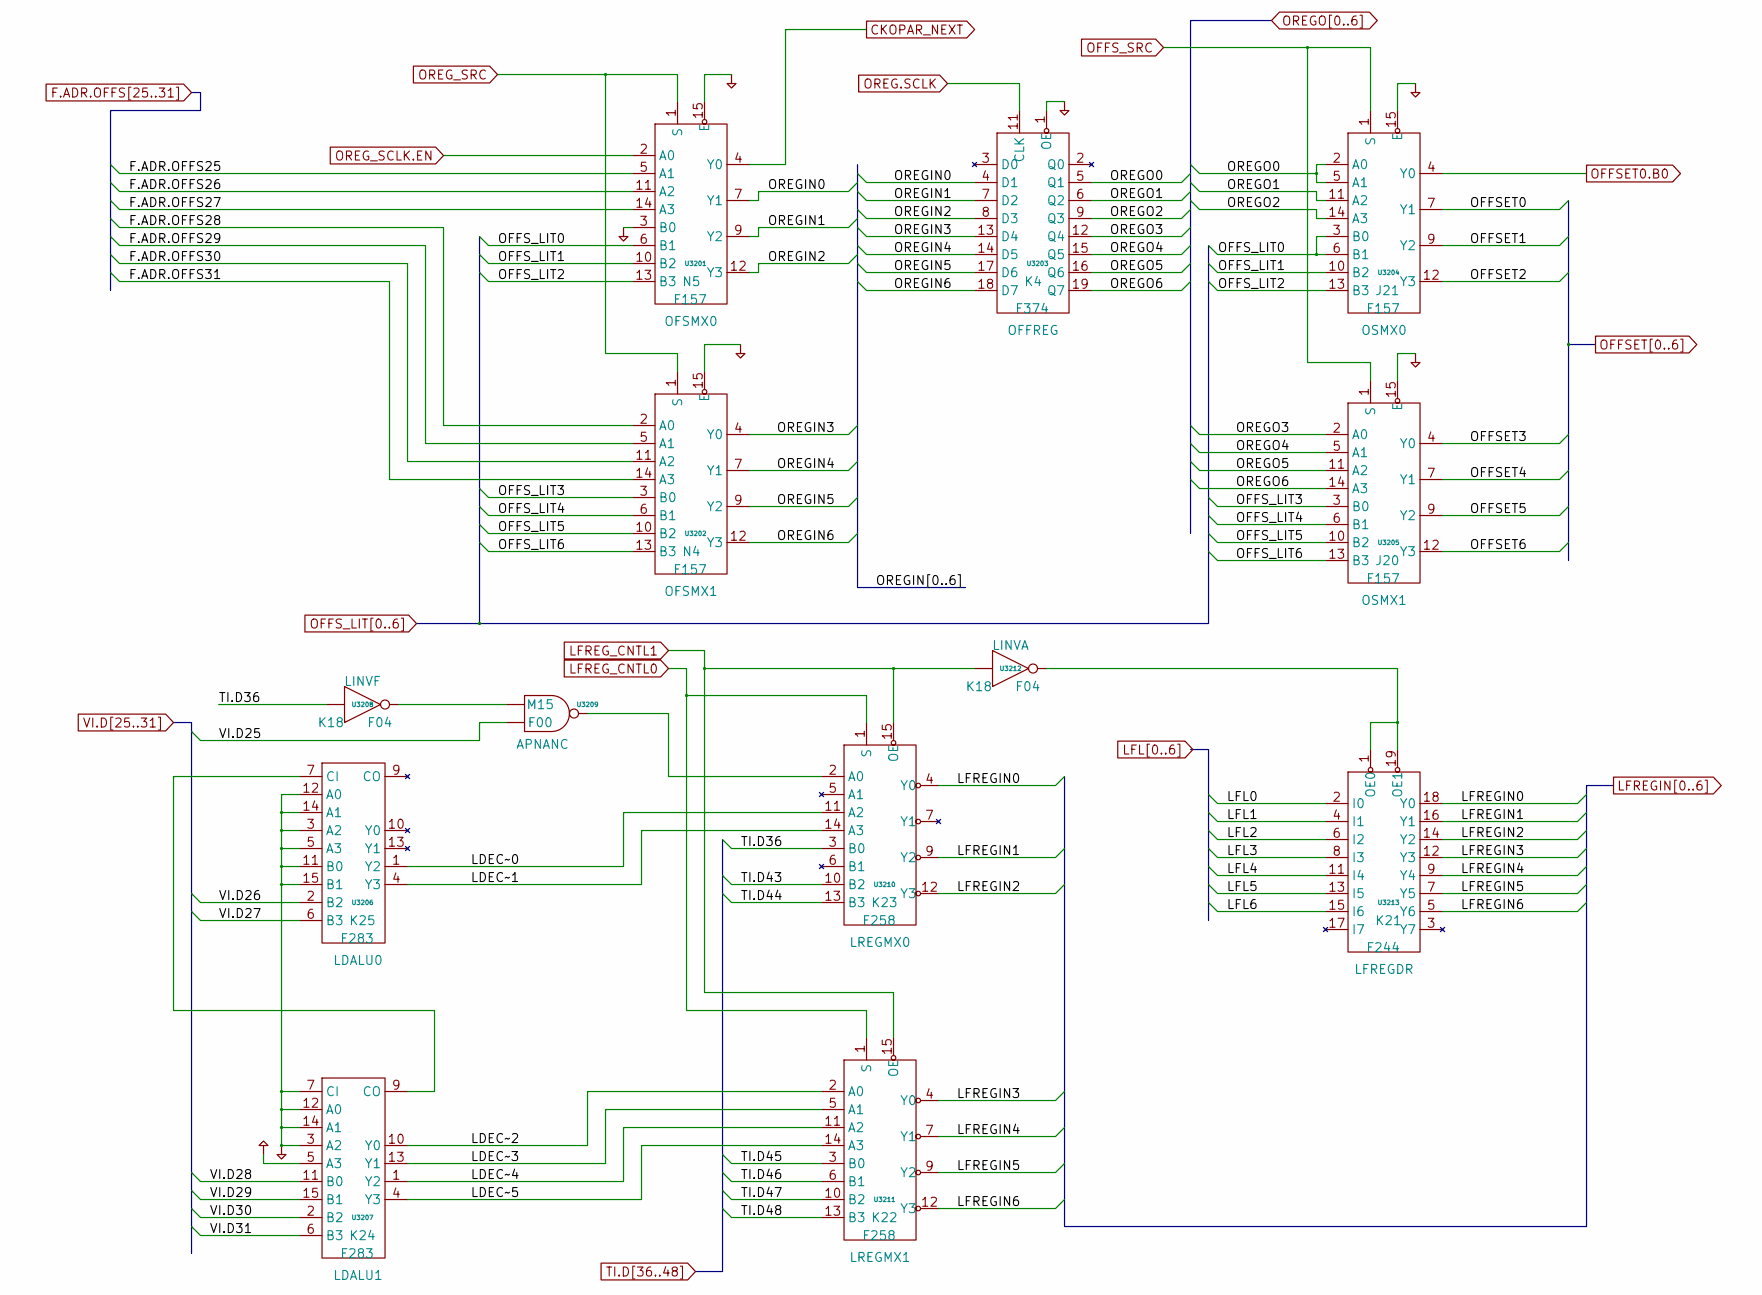
[picture p316: schematic pg_31.kicad_sch]

Parts:
U3201, U3202, U3204, U3205: F157
U3203: F374
U3206, U3207: F283
U3208, U3212: F04
U3209: F00
U3210, U3211: F258
U3213: F244

Connections:
CKOPAR_NEXT: U3201.4 (Y0)
F.ADR.OFFS25: U3201.5 (A1)
F.ADR.OFFS26: U3201.11 (A2)
F.ADR.OFFS27: U3201.14 (A3)
F.ADR.OFFS28: U3202.2 (A0)
F.ADR.OFFS29: U3202.5 (A1)
F.ADR.OFFS30: U3202.11 (A2)
F.ADR.OFFS31: U3202.14 (A3)
LDEC~0: U3206.1 (Y2), U3210.11 (A2)
LDEC~1: U3206.4 (Y3), U3210.14 (A3)
LDEC~2: U3207.10 (Y0), U3211.2 (A0)
LDEC~3: U3207.13 (Y1), U3211.5 (A1)
LDEC~4: U3207.1 (Y2), U3211.11 (A2)
LDEC~5: U3207.4 (Y3), U3211.14 (A3)
LFL0: U3213.2 (I0)
LFL1: U3213.4 (I1)
LFL2: U3213.6 (I2)
LFL3: U3213.8 (I3)
LFL4: U3213.11 (I4)
LFL5: U3213.13 (I5)
LFL6: U3213.15 (I6)
LFREGIN0: U3210.4 (Y0), U3213.18 (Y0)
LFREGIN1: U3210.9 (Y2), U3213.16 (Y1)
LFREGIN2: U3210.12 (Y3), U3213.14 (Y2)
LFREGIN3: U3211.4 (Y0), U3213.12 (Y3)
LFREGIN4: U3211.7 (Y1), U3213.9 (Y4)
LFREGIN5: U3211.9 (Y2), U3213.7 (Y5)
LFREGIN6: U3211.12 (Y3), U3213.5 (Y6)
LFREG_CNTL0: U3210.1 (S), U3211.1 (S)
LFREG_CNTL1: U3210.15 (OE), U3211.15 (OE), U3212.1 (D0)
unnamed: U3206.7 (CI), U3207.9 (CO)
unnamed: U3208.2 (Q), U3209.1 (D0)
unnamed: U3209.3 (Q), U3210.2 (A0)
unnamed: U3212.2 (Q), U3213.1 (OE0), U3213.19 (OE1)
OFFSET0: U3204.7 (Y1)
OFFSET0.B0: U3204.4 (Y0)
OFFSET1: U3204.9 (Y2)
OFFSET2: U3204.12 (Y3)
OFFSET3: U3205.4 (Y0)
OFFSET4: U3205.7 (Y1)
OFFSET5: U3205.9 (Y2)
OFFSET6: U3205.12 (Y3)
OFFS_LIT0: U3201.6 (B1), U3204.3 (B0), U3204.6 (B1)
OFFS_LIT1: U3201.10 (B2), U3204.10 (B2)
OFFS_LIT2: U3201.13 (B3), U3204.13 (B3)
OFFS_LIT3: U3202.3 (B0), U3205.3 (B0)
OFFS_LIT4: U3202.6 (B1), U3205.6 (B1)
OFFS_LIT5: U3202.10 (B2), U3205.10 (B2)
OFFS_LIT6: U3202.13 (B3), U3205.13 (B3)
OFFS_SRC: U3204.1 (S), U3205.1 (S)
OREG.SCLK: U3203.11 (CLK)
OREGIN0: U3201.7 (Y1), U3203.4 (D1)
OREGIN1: U3201.9 (Y2), U3203.7 (D2)
OREGIN2: U3201.12 (Y3), U3203.8 (D3)
OREGIN3: U3202.4 (Y0), U3203.13 (D4)
OREGIN4: U3202.7 (Y1), U3203.14 (D5)
OREGIN5: U3202.9 (Y2), U3203.17 (D6)
OREGIN6: U3202.12 (Y3), U3203.18 (D7)
OREGO0: U3203.5 (Q1), U3204.2 (A0), U3204.5 (A1)
OREGO1: U3203.6 (Q2), U3204.11 (A2)
OREGO2: U3203.9 (Q3), U3204.14 (A3)
OREGO3: U3203.12 (Q4), U3205.2 (A0)
OREGO4: U3203.15 (Q5), U3205.5 (A1)
OREGO5: U3203.16 (Q6), U3205.11 (A2)
OREGO6: U3203.19 (Q7), U3205.14 (A3)
OREG_SCLK.EN: U3201.2 (A0)
OREG_SRC: U3201.1 (S), U3202.1 (S)
PD: U3201.3 (B0), U3201.15 (E), U3202.15 (E), U3203.1 (OE), U3204.15 (E), U3205.15 (E), U3206.3 (A2), U3206.5 (A3), U3206.11 (B0), U3206.12 (A0), U3206.14 (A1), U3206.15 (B1), U3207.3 (A2), U3207.7 (CI), U3207.12 (A0), U3207.14 (A1)
PU: U3207.5 (A3)
TI.D36: U3208.1 (D0), U3210.3 (B0)
TI.D43: U3210.10 (B2)
TI.D44: U3210.13 (B3)
TI.D45: U3211.3 (B0)
TI.D46: U3211.6 (B1)
TI.D47: U3211.10 (B2)
TI.D48: U3211.13 (B3)
VI.D25: U3209.2 (D1)
VI.D26: U3206.2 (B2)
VI.D27: U3206.6 (B3)
VI.D28: U3207.11 (B0)
VI.D29: U3207.15 (B1)
VI.D30: U3207.2 (B2)
VI.D31: U3207.6 (B3)
