Datamuseum-DK/R1000.HwDoc/Schematics/FIU/pg_32.kicad_sch

## KiCad design Schematics/FIU/pg_32.kicad_sch (2023-01-10)

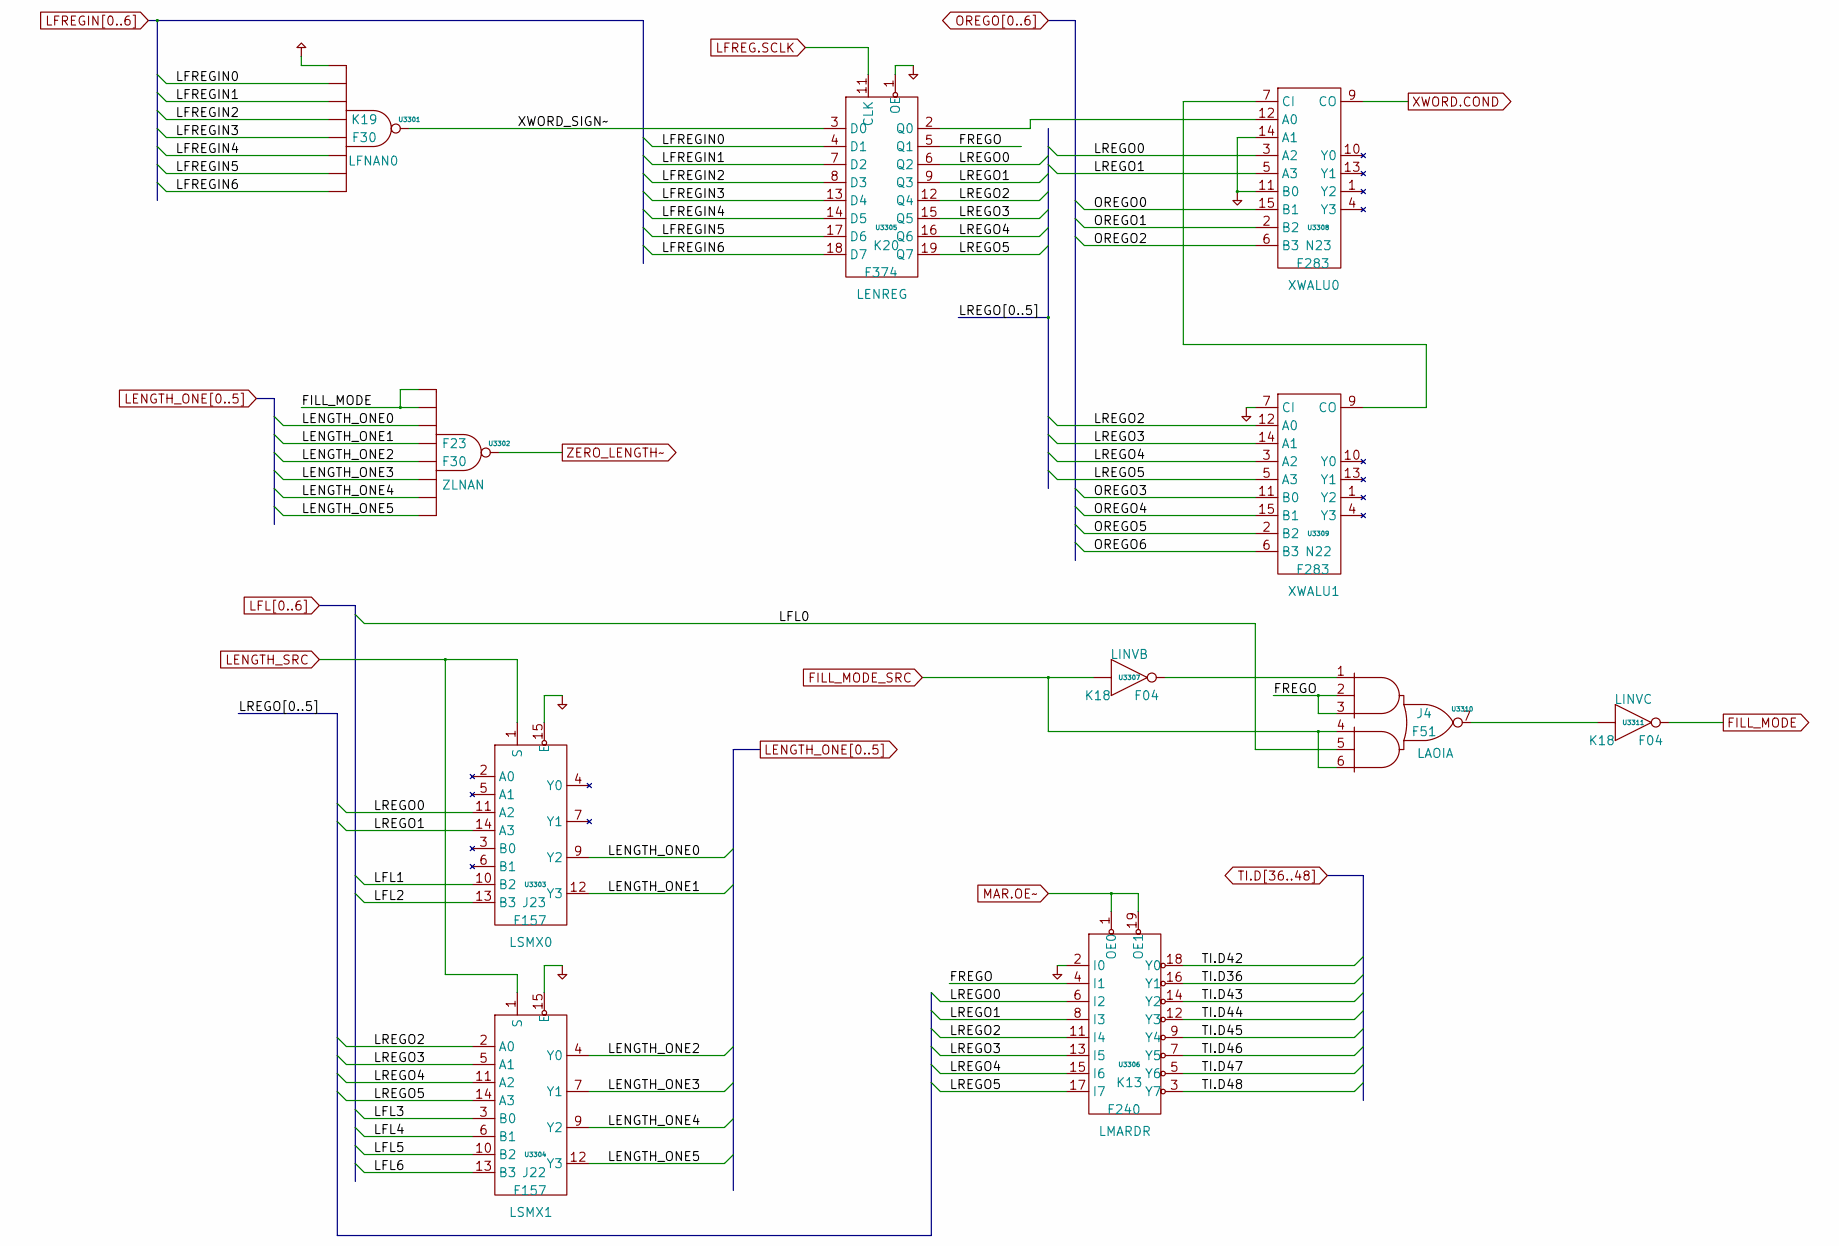
[picture p317: schematic pg_32.kicad_sch]

Parts:
U3301, U3302: F30
U3303, U3304: F157
U3305: F374
U3306: F240
U3307, U3311: F04
U3308, U3309: F283
U3310: F51

Connections:
FILL_MODE: U3302.11 (D0), U3302.12 (D1), U3311.2 (Q)
FILL_MODE_SRC: U3307.1 (D0), U3310.4 (B1), U3310.6 (B3)
FREGO: U3305.5 (Q1), U3306.4 (I1), U3310.2 (A2), U3310.3 (A3)
LENGTH_ONE0: U3302.1 (D2), U3303.9 (Y2)
LENGTH_ONE1: U3302.2 (D3), U3303.12 (Y3)
LENGTH_ONE2: U3302.3 (D4), U3304.4 (Y0)
LENGTH_ONE3: U3302.4 (D5), U3304.7 (Y1)
LENGTH_ONE4: U3302.5 (D6), U3304.9 (Y2)
LENGTH_ONE5: U3302.6 (D7), U3304.12 (Y3)
LENGTH_SRC: U3303.1 (S), U3304.1 (S)
LFL0: U3310.5 (B2)
LFL1: U3303.10 (B2)
LFL2: U3303.13 (B3)
LFL3: U3304.3 (B0)
LFL4: U3304.6 (B1)
LFL5: U3304.10 (B2)
LFL6: U3304.13 (B3)
LFREG.SCLK: U3305.11 (CLK)
LFREGIN0: U3301.12 (D1), U3305.4 (D1)
LFREGIN1: U3301.1 (D2), U3305.7 (D2)
LFREGIN2: U3301.2 (D3), U3305.8 (D3)
LFREGIN3: U3301.3 (D4), U3305.13 (D4)
LFREGIN4: U3301.4 (D5), U3305.14 (D5)
LFREGIN5: U3301.5 (D6), U3305.17 (D6)
LFREGIN6: U3301.6 (D7), U3305.18 (D7)
LREGO0: U3303.11 (A2), U3305.6 (Q2), U3306.6 (I2), U3308.3 (A2)
LREGO1: U3303.14 (A3), U3305.9 (Q3), U3306.8 (I3), U3308.5 (A3)
LREGO2: U3304.2 (A0), U3305.12 (Q4), U3306.11 (I4), U3309.12 (A0)
LREGO3: U3304.5 (A1), U3305.15 (Q5), U3306.13 (I5), U3309.14 (A1)
LREGO4: U3304.11 (A2), U3305.16 (Q6), U3306.15 (I6), U3309.3 (A2)
LREGO5: U3304.14 (A3), U3305.19 (Q7), U3306.17 (I7), U3309.5 (A3)
MAR.OE~: U3306.1 (OE0), U3306.19 (OE1)
unnamed: U3305.2 (Q0), U3308.12 (A0)
unnamed: U3307.2 (Q), U3310.1 (A1)
unnamed: U3308.7 (CI), U3309.9 (CO)
unnamed: U3310.7 (Q), U3311.1 (D0)
OREGO0: U3308.15 (B1)
OREGO1: U3308.2 (B2)
OREGO2: U3308.6 (B3)
OREGO3: U3309.11 (B0)
OREGO4: U3309.15 (B1)
OREGO5: U3309.2 (B2)
OREGO6: U3309.6 (B3)
PD: U3303.15 (E), U3304.15 (E), U3305.1 (OE), U3306.2 (I0), U3308.11 (B0), U3308.14 (A1), U3309.7 (CI)
PU: U3301.11 (D0)
TI.D36: U3306.16 (Y1)
TI.D42: U3306.18 (Y0)
TI.D43: U3306.14 (Y2)
TI.D44: U3306.12 (Y3)
TI.D45: U3306.9 (Y4)
TI.D46: U3306.7 (Y5)
TI.D47: U3306.5 (Y6)
TI.D48: U3306.3 (Y7)
XWORD.COND: U3308.9 (CO)
XWORD_SIGN~: U3301.8 (Q), U3305.3 (D0)
ZERO_LENGTH~: U3302.8 (Q)
