Datamuseum-DK/R1000.HwDoc/Schematics/FIU/pg_33.kicad_sch

## KiCad design Schematics/FIU/pg_33.kicad_sch (2023-01-10)

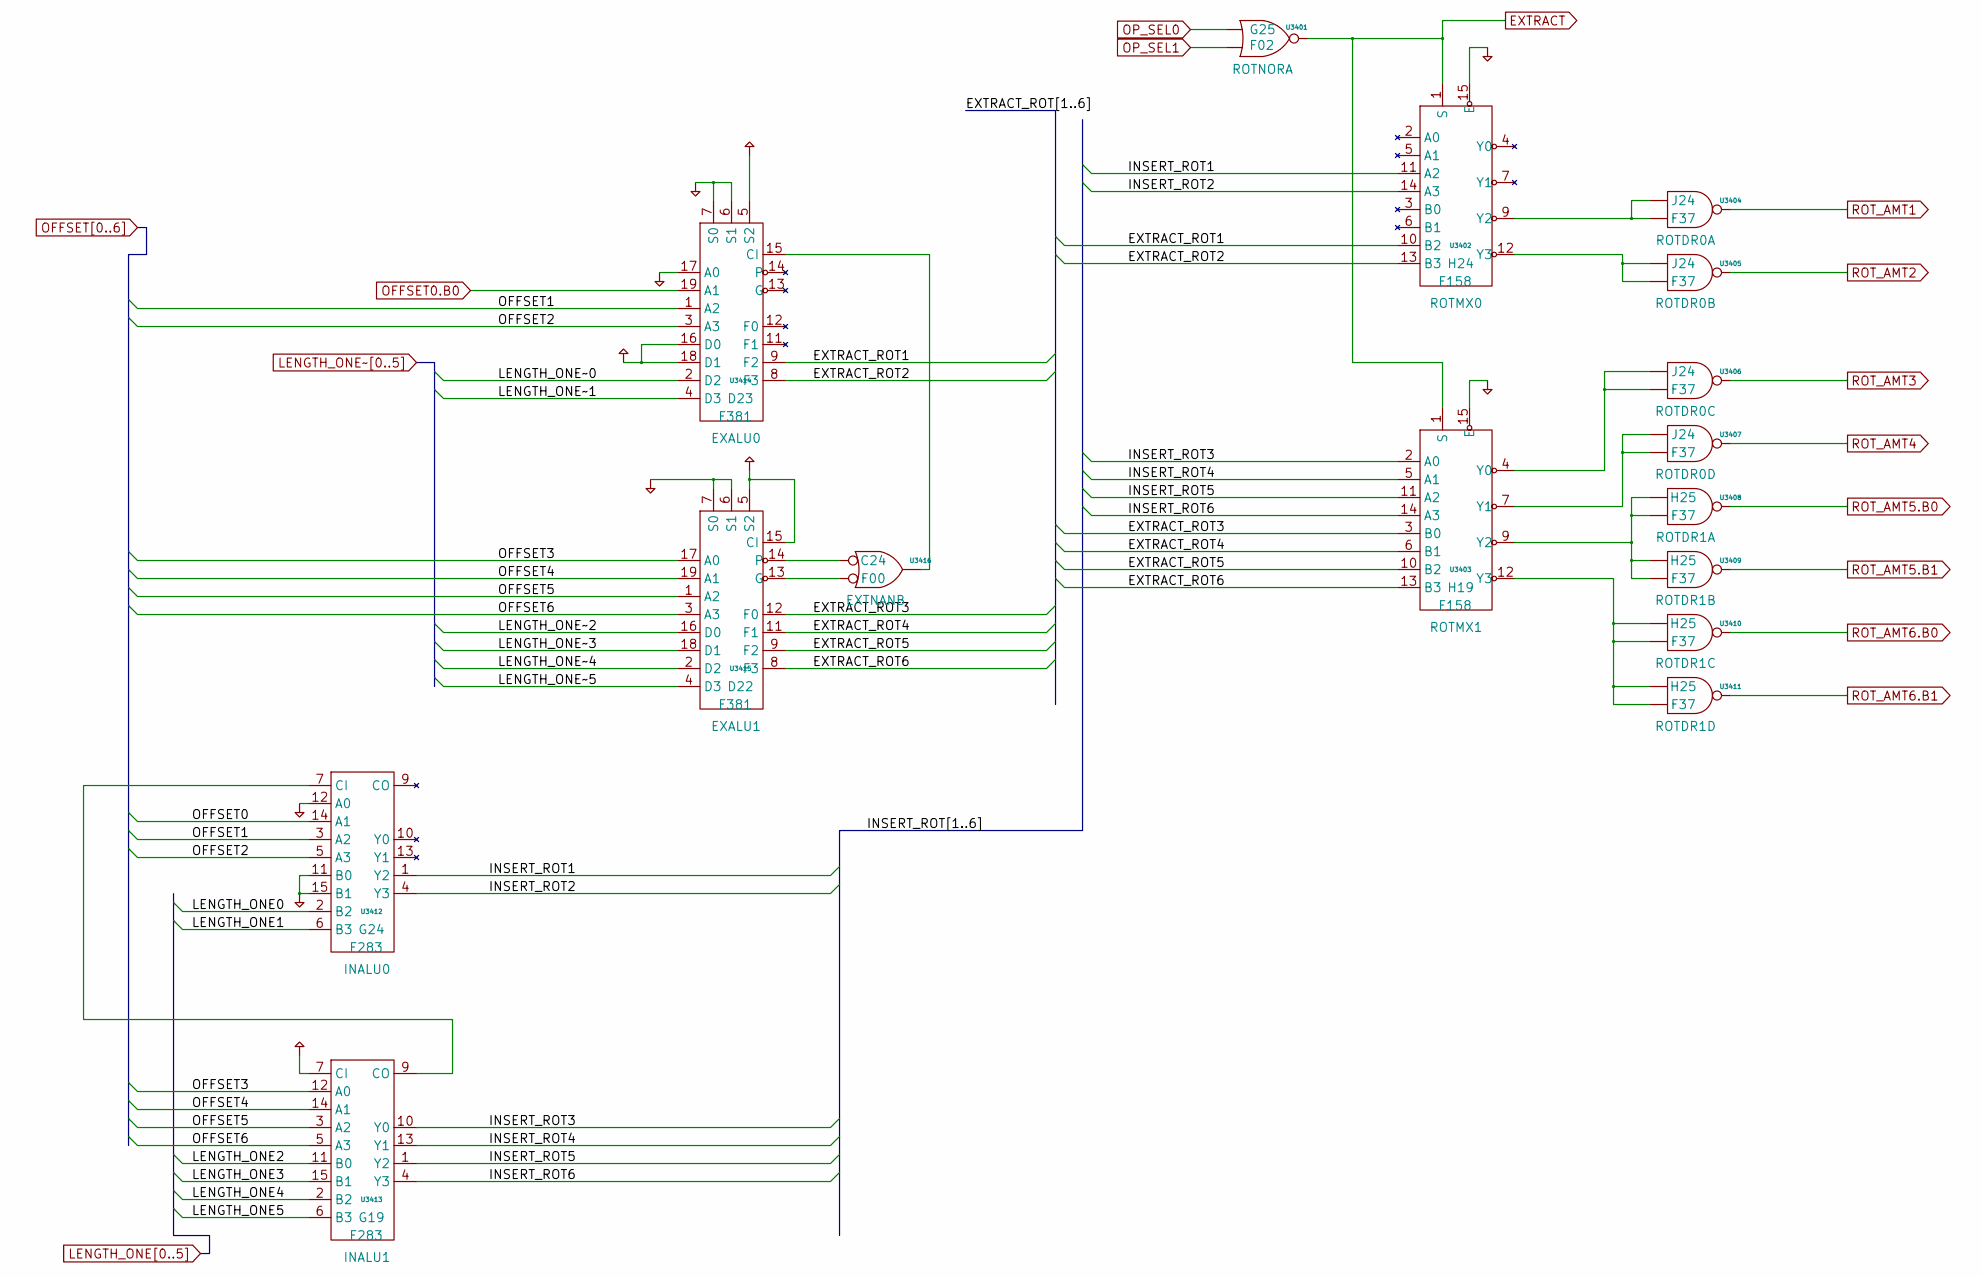
[picture p318: schematic pg_33.kicad_sch]

Parts:
U3401: F02
U3402, U3403: F158
U3404, U3405, U3406, U3407, U3408, U3409, U3410, U3411: F37
U3412, U3413: F283
U3414, U3415: F381
U3416: F00

Connections:
EXTRACT: U3401.3 (Q), U3402.1 (S), U3403.1 (S)
EXTRACT_ROT1: U3402.10 (B2), U3414.9 (F2)
EXTRACT_ROT2: U3402.13 (B3), U3414.8 (F3)
EXTRACT_ROT3: U3403.3 (B0), U3415.12 (F0)
EXTRACT_ROT4: U3403.6 (B1), U3415.11 (F1)
EXTRACT_ROT5: U3403.10 (B2), U3415.9 (F2)
EXTRACT_ROT6: U3403.13 (B3), U3415.8 (F3)
INSERT_ROT1: U3402.11 (A2), U3412.1 (Y2)
INSERT_ROT2: U3402.14 (A3), U3412.4 (Y3)
INSERT_ROT3: U3403.2 (A0), U3413.10 (Y0)
INSERT_ROT4: U3403.5 (A1), U3413.13 (Y1)
INSERT_ROT5: U3403.11 (A2), U3413.1 (Y2)
INSERT_ROT6: U3403.14 (A3), U3413.4 (Y3)
LENGTH_ONE0: U3412.2 (B2)
LENGTH_ONE1: U3412.6 (B3)
LENGTH_ONE2: U3413.11 (B0)
LENGTH_ONE3: U3413.15 (B1)
LENGTH_ONE4: U3413.2 (B2)
LENGTH_ONE5: U3413.6 (B3)
LENGTH_ONE~0: U3414.2 (D2)
LENGTH_ONE~1: U3414.4 (D3)
LENGTH_ONE~2: U3415.16 (D0)
LENGTH_ONE~3: U3415.18 (D1)
LENGTH_ONE~4: U3415.2 (D2)
LENGTH_ONE~5: U3415.4 (D3)
unnamed: U3402.9 (Y2), U3404.1 (D0), U3404.2 (D1)
unnamed: U3402.12 (Y3), U3405.1 (D0), U3405.2 (D1)
unnamed: U3403.4 (Y0), U3406.1 (D0), U3406.2 (D1)
unnamed: U3403.7 (Y1), U3407.1 (D0), U3407.2 (D1)
unnamed: U3403.9 (Y2), U3408.1 (D0), U3408.2 (D1), U3409.1 (D0), U3409.2 (D1)
unnamed: U3403.12 (Y3), U3410.1 (D0), U3410.2 (D1), U3411.1 (D0), U3411.2 (D1)
unnamed: U3412.7 (CI), U3413.9 (CO)
unnamed: U3414.15 (CI), U3416.3 (Q)
unnamed: U3415.13 (G), U3416.2 (D1)
unnamed: U3415.14, U3416.1 (D0)
OFFSET0: U3412.14 (A1)
OFFSET0.B0: U3414.19 (A1)
OFFSET1: U3412.3 (A2), U3414.1 (A2)
OFFSET2: U3412.5 (A3), U3414.3 (A3)
OFFSET3: U3413.12 (A0), U3415.17 (A0)
OFFSET4: U3413.14 (A1), U3415.19 (A1)
OFFSET5: U3413.3 (A2), U3415.1 (A2)
OFFSET6: U3413.5 (A3), U3415.3 (A3)
OP_SEL0: U3401.1 (D0)
OP_SEL1: U3401.2 (D1)
PD: U3402.15 (E), U3403.15 (E), U3412.11 (B0), U3412.12 (A0), U3412.15 (B1), U3414.6 (S1), U3414.7 (S0), U3414.17 (A0), U3415.6 (S1), U3415.7 (S0)
PU: U3413.7 (CI), U3414.5 (S2), U3414.16 (D0), U3414.18 (D1), U3415.5 (S2), U3415.15 (CI)
ROT_AMT1: U3404.3 (Q)
ROT_AMT2: U3405.3 (Q)
ROT_AMT3: U3406.3 (Q)
ROT_AMT4: U3407.3 (Q)
ROT_AMT5.B0: U3408.3 (Q)
ROT_AMT5.B1: U3409.3 (Q)
ROT_AMT6.B0: U3410.3 (Q)
ROT_AMT6.B1: U3411.3 (Q)
