Datamuseum-DK/R1000.HwDoc/Schematics/FIU/pg_34.kicad_sch

## KiCad design Schematics/FIU/pg_34.kicad_sch (2023-01-10)

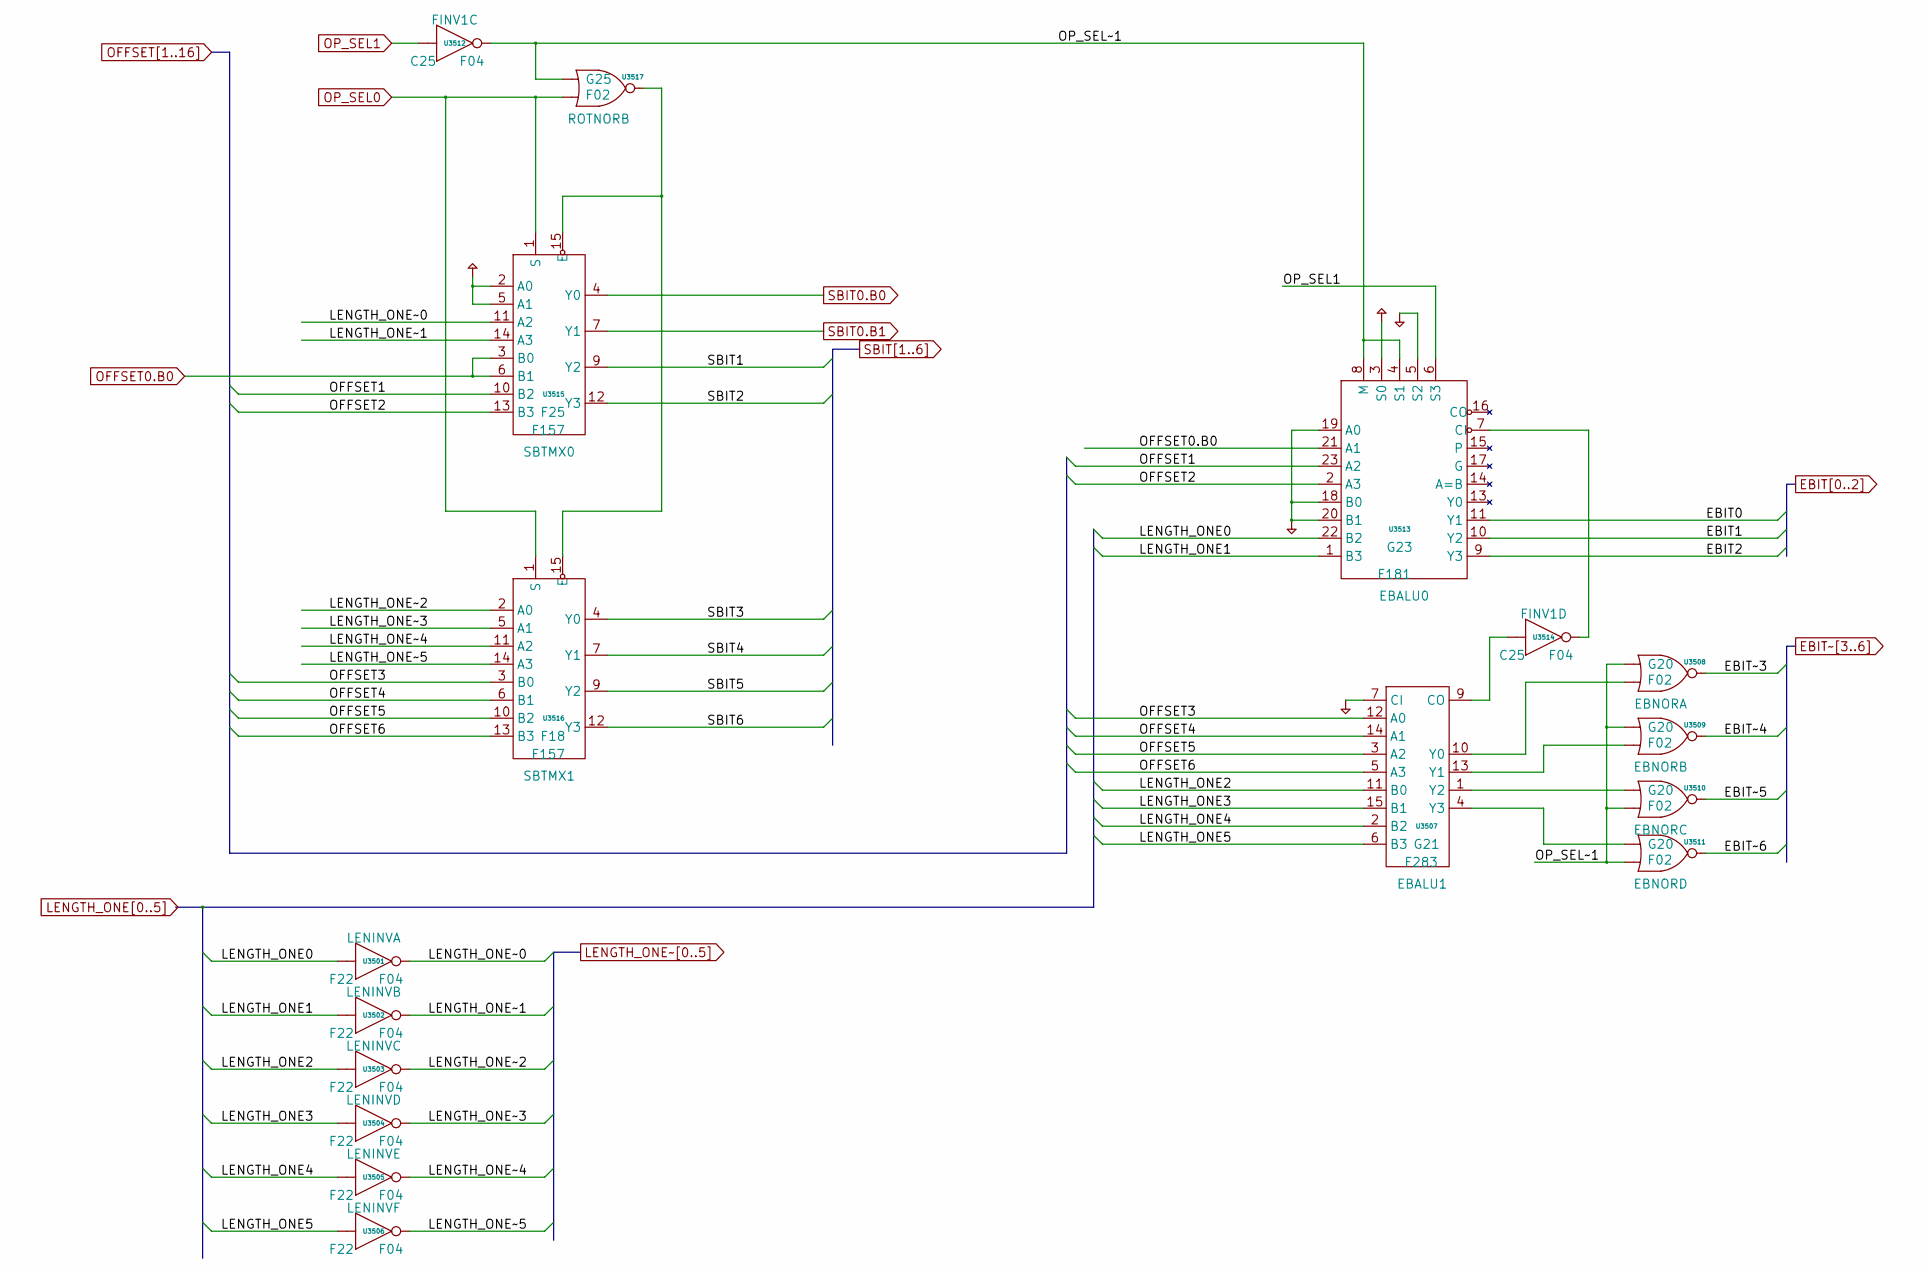
[picture p319: schematic pg_34.kicad_sch]

Parts:
U3501, U3502, U3503, U3504, U3505, U3506, U3512, U3514: F04
U3507: F283
U3508, U3509, U3510, U3511, U3517: F02
U3513: F181
U3515, U3516: F157

Connections:
EBIT0: U3513.11 (Y1)
EBIT1: U3513.10 (Y2)
EBIT2: U3513.9 (Y3)
EBIT~3: U3508.3 (Q)
EBIT~4: U3509.3 (Q)
EBIT~5: U3510.3 (Q)
EBIT~6: U3511.3 (Q)
LENGTH_ONE0: U3501.1 (D0), U3513.22 (B2)
LENGTH_ONE1: U3502.1 (D0), U3513.1 (B3)
LENGTH_ONE2: U3503.1 (D0), U3507.11 (B0)
LENGTH_ONE3: U3504.1 (D0), U3507.15 (B1)
LENGTH_ONE4: U3505.1 (D0), U3507.2 (B2)
LENGTH_ONE5: U3506.1 (D0), U3507.6 (B3)
LENGTH_ONE~0: U3501.2 (Q), U3515.11 (A2)
LENGTH_ONE~1: U3502.2 (Q), U3515.14 (A3)
LENGTH_ONE~2: U3503.2 (Q), U3516.2 (A0)
LENGTH_ONE~3: U3504.2 (Q), U3516.5 (A1)
LENGTH_ONE~4: U3505.2 (Q), U3516.11 (A2)
LENGTH_ONE~5: U3506.2 (Q), U3516.14 (A3)
unnamed: U3507.1 (Y2), U3510.1 (D0)
unnamed: U3507.4 (Y3), U3511.1 (D0)
unnamed: U3507.9 (CO), U3514.1 (D0)
unnamed: U3507.10 (Y0), U3508.2 (D1)
unnamed: U3507.13 (Y1), U3509.2 (D1)
unnamed: U3513.7 (CI), U3514.2 (Q)
unnamed: U3515.15 (E), U3516.15 (E), U3517.3 (Q)
OFFSET0.B0: U3513.21 (A1), U3515.3 (B0), U3515.6 (B1)
OFFSET1: U3513.23 (A2), U3515.10 (B2)
OFFSET2: U3513.2 (A3), U3515.13 (B3)
OFFSET3: U3507.12 (A0), U3516.3 (B0)
OFFSET4: U3507.14 (A1), U3516.6 (B1)
OFFSET5: U3507.3 (A2), U3516.10 (B2)
OFFSET6: U3507.5 (A3), U3516.13 (B3)
OP_SEL0: U3515.1 (S), U3516.1 (S), U3517.2 (D1)
OP_SEL1: U3512.1 (D0), U3513.6 (S3)
OP_SEL~1: U3508.1 (D0), U3509.1 (D0), U3510.2 (D1), U3511.2 (D1), U3512.2 (Q), U3513.4 (S1), U3513.8 (M), U3517.1 (D0)
PD: U3507.7 (CI), U3513.5 (S2), U3513.18 (B0), U3513.19 (A0), U3513.20 (B1)
PU: U3513.3 (S0), U3515.2 (A0), U3515.5 (A1)
SBIT0.B0: U3515.4 (Y0)
SBIT0.B1: U3515.7 (Y1)
SBIT1: U3515.9 (Y2)
SBIT2: U3515.12 (Y3)
SBIT3: U3516.4 (Y0)
SBIT4: U3516.7 (Y1)
SBIT5: U3516.9 (Y2)
SBIT6: U3516.12 (Y3)
