Datamuseum-DK/R1000.HwDoc/Schematics/FIU/pg_35.kicad_sch

## KiCad design Schematics/FIU/pg_35.kicad_sch (2023-01-10)

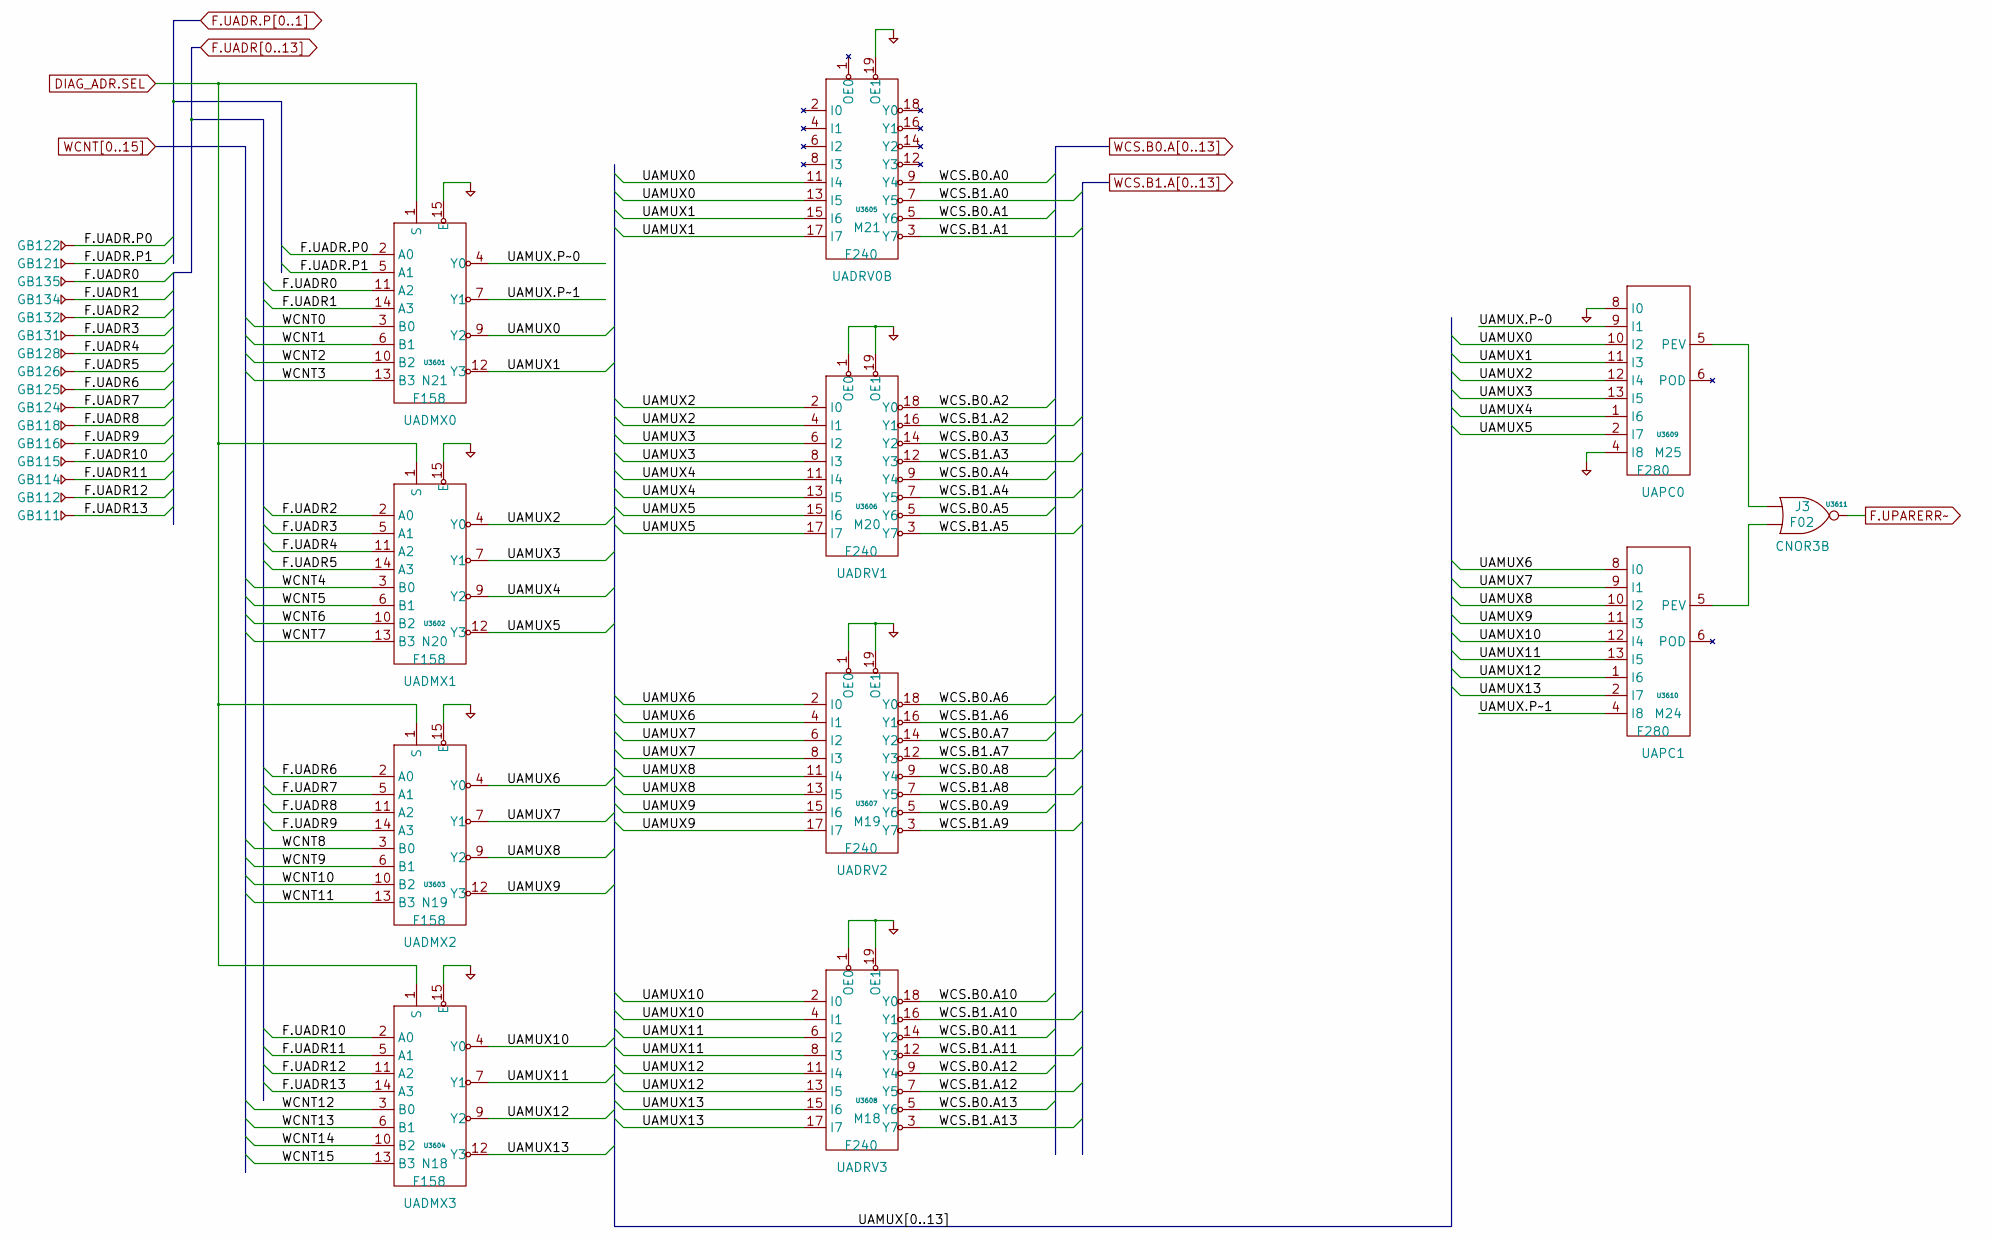
[picture p320: schematic pg_35.kicad_sch]

Parts:
GB111, GB112, GB114, GB115, GB116, GB118, GB121, GB122, GB124, GB125, GB126, GB128, GB131, GB132, GB134, GB135: GB
U3601, U3602, U3603, U3604: F158
U3605, U3606, U3607, U3608: F240
U3609, U3610: F280
U3611: F02

Connections:
DIAG_ADR.SEL: U3601.1 (S), U3602.1 (S), U3603.1 (S), U3604.1 (S)
F.UADR0: GB135.1, U3601.11 (A2)
F.UADR1: GB134.1, U3601.14 (A3)
F.UADR2: GB132.1, U3602.2 (A0)
F.UADR3: GB131.1, U3602.5 (A1)
F.UADR4: GB128.1, U3602.11 (A2)
F.UADR5: GB126.1, U3602.14 (A3)
F.UADR6: GB125.1, U3603.2 (A0)
F.UADR7: GB124.1, U3603.5 (A1)
F.UADR8: GB118.1, U3603.11 (A2)
F.UADR9: GB116.1, U3603.14 (A3)
F.UADR10: GB115.1, U3604.2 (A0)
F.UADR11: GB114.1, U3604.5 (A1)
F.UADR12: GB112.1, U3604.11 (A2)
F.UADR13: GB111.1, U3604.14 (A3)
F.UADR.P0: GB122.1, U3601.2 (A0)
F.UADR.P1: GB121.1, U3601.5 (A1)
F.UPARERR~: U3611.3 (Q)
unnamed: U3609.5 (PEV), U3611.1 (D0)
unnamed: U3610.5 (PEV), U3611.2 (D1)
PD: U3601.15 (E), U3602.15 (E), U3603.15 (E), U3604.15 (E), U3605.19 (OE1), U3606.1 (OE0), U3606.19 (OE1), U3607.1 (OE0), U3607.19 (OE1), U3608.1 (OE0), U3608.19 (OE1), U3609.4 (I8), U3609.8 (I0)
UAMUX0: U3601.9 (Y2), U3605.11 (I4), U3605.13 (I5), U3609.10 (I2)
UAMUX1: U3601.12 (Y3), U3605.15 (I6), U3605.17 (I7), U3609.11 (I3)
UAMUX2: U3602.4 (Y0), U3606.2 (I0), U3606.4 (I1), U3609.12 (I4)
UAMUX3: U3602.7 (Y1), U3606.6 (I2), U3606.8 (I3), U3609.13 (I5)
UAMUX4: U3602.9 (Y2), U3606.11 (I4), U3606.13 (I5), U3609.1 (I6)
UAMUX5: U3602.12 (Y3), U3606.15 (I6), U3606.17 (I7), U3609.2 (I7)
UAMUX6: U3603.4 (Y0), U3607.2 (I0), U3607.4 (I1), U3610.8 (I0)
UAMUX7: U3603.7 (Y1), U3607.6 (I2), U3607.8 (I3), U3610.9 (I1)
UAMUX8: U3603.9 (Y2), U3607.11 (I4), U3607.13 (I5), U3610.10 (I2)
UAMUX9: U3603.12 (Y3), U3607.15 (I6), U3607.17 (I7), U3610.11 (I3)
UAMUX10: U3604.4 (Y0), U3608.2 (I0), U3608.4 (I1), U3610.12 (I4)
UAMUX11: U3604.7 (Y1), U3608.6 (I2), U3608.8 (I3), U3610.13 (I5)
UAMUX12: U3604.9 (Y2), U3608.11 (I4), U3608.13 (I5), U3610.1 (I6)
UAMUX13: U3604.12 (Y3), U3608.15 (I6), U3608.17 (I7), U3610.2 (I7)
UAMUX.P~0: U3601.4 (Y0), U3609.9 (I1)
UAMUX.P~1: U3601.7 (Y1), U3610.4 (I8)
WCNT0: U3601.3 (B0)
WCNT1: U3601.6 (B1)
WCNT2: U3601.10 (B2)
WCNT3: U3601.13 (B3)
WCNT4: U3602.3 (B0)
WCNT5: U3602.6 (B1)
WCNT6: U3602.10 (B2)
WCNT7: U3602.13 (B3)
WCNT8: U3603.3 (B0)
WCNT9: U3603.6 (B1)
WCNT10: U3603.10 (B2)
WCNT11: U3603.13 (B3)
WCNT12: U3604.3 (B0)
WCNT13: U3604.6 (B1)
WCNT14: U3604.10 (B2)
WCNT15: U3604.13 (B3)
WCS.B0.A0: U3605.9 (Y4)
WCS.B0.A1: U3605.5 (Y6)
WCS.B0.A2: U3606.18 (Y0)
WCS.B0.A3: U3606.14 (Y2)
WCS.B0.A4: U3606.9 (Y4)
WCS.B0.A5: U3606.5 (Y6)
WCS.B0.A6: U3607.18 (Y0)
WCS.B0.A7: U3607.14 (Y2)
WCS.B0.A8: U3607.9 (Y4)
WCS.B0.A9: U3607.5 (Y6)
WCS.B0.A10: U3608.18 (Y0)
WCS.B0.A11: U3608.14 (Y2)
WCS.B0.A12: U3608.9 (Y4)
WCS.B0.A13: U3608.5 (Y6)
WCS.B1.A0: U3605.7 (Y5)
WCS.B1.A1: U3605.3 (Y7)
WCS.B1.A2: U3606.16 (Y1)
WCS.B1.A3: U3606.12 (Y3)
WCS.B1.A4: U3606.7 (Y5)
WCS.B1.A5: U3606.3 (Y7)
WCS.B1.A6: U3607.16 (Y1)
WCS.B1.A7: U3607.12 (Y3)
WCS.B1.A8: U3607.7 (Y5)
WCS.B1.A9: U3607.3 (Y7)
WCS.B1.A10: U3608.16 (Y1)
WCS.B1.A11: U3608.12 (Y3)
WCS.B1.A12: U3608.7 (Y5)
WCS.B1.A13: U3608.3 (Y7)
