Datamuseum-DK/R1000.HwDoc/Schematics/FIU/pg_36.kicad_sch

## KiCad design Schematics/FIU/pg_36.kicad_sch (2023-01-10)

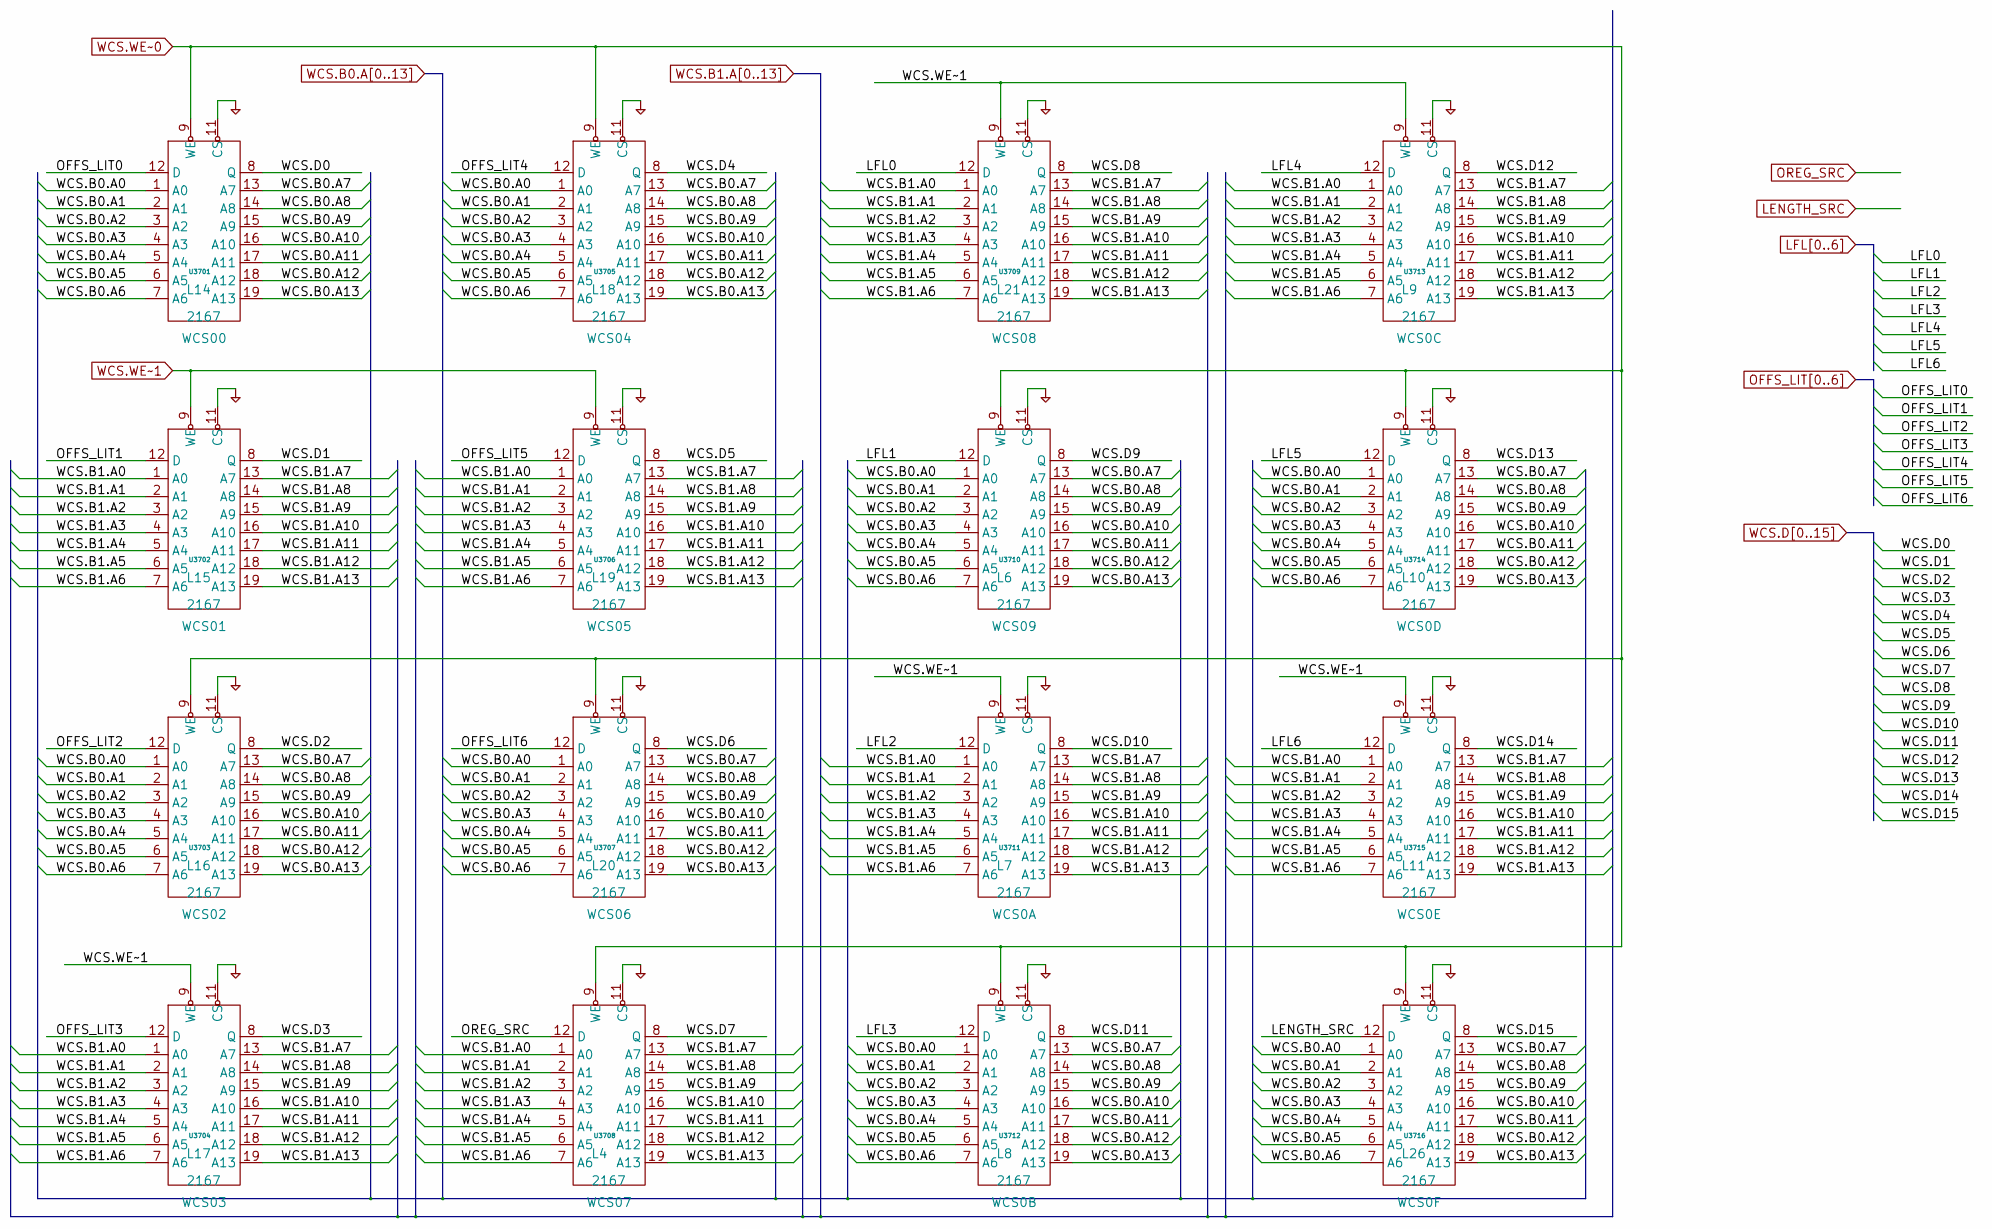
[picture p321: schematic pg_36.kicad_sch]

Parts:
U3701, U3702, U3703, U3704, U3705, U3706, U3707, U3708, U3709, U3710, U3711, U3712, U3713, U3714, U3715, U3716: 2167

Connections:
LENGTH_SRC: U3716.12 (D)
LFL0: U3709.12 (D)
LFL1: U3710.12 (D)
LFL2: U3711.12 (D)
LFL3: U3712.12 (D)
LFL4: U3713.12 (D)
LFL5: U3714.12 (D)
LFL6: U3715.12 (D)
OFFS_LIT0: U3701.12 (D)
OFFS_LIT1: U3702.12 (D)
OFFS_LIT2: U3703.12 (D)
OFFS_LIT3: U3704.12 (D)
OFFS_LIT4: U3705.12 (D)
OFFS_LIT5: U3706.12 (D)
OFFS_LIT6: U3707.12 (D)
OREG_SRC: U3708.12 (D)
PD: U3701.11 (CS), U3702.11 (CS), U3703.11 (CS), U3704.11 (CS), U3705.11 (CS), U3706.11 (CS), U3707.11 (CS), U3708.11 (CS), U3709.11 (CS), U3710.11 (CS), U3711.11 (CS), U3712.11 (CS), U3713.11 (CS), U3714.11 (CS), U3715.11 (CS), U3716.11 (CS)
WCS.B0.A0: U3701.1 (A0), U3703.1 (A0), U3705.1 (A0), U3707.1 (A0), U3710.1 (A0), U3712.1 (A0), U3714.1 (A0), U3716.1 (A0)
WCS.B0.A1: U3701.2 (A1), U3703.2 (A1), U3705.2 (A1), U3707.2 (A1), U3710.2 (A1), U3712.2 (A1), U3714.2 (A1), U3716.2 (A1)
WCS.B0.A2: U3701.3 (A2), U3703.3 (A2), U3705.3 (A2), U3707.3 (A2), U3710.3 (A2), U3712.3 (A2), U3714.3 (A2), U3716.3 (A2)
WCS.B0.A3: U3701.4 (A3), U3703.4 (A3), U3705.4 (A3), U3707.4 (A3), U3710.4 (A3), U3712.4 (A3), U3714.4 (A3), U3716.4 (A3)
WCS.B0.A4: U3701.5 (A4), U3703.5 (A4), U3705.5 (A4), U3707.5 (A4), U3710.5 (A4), U3712.5 (A4), U3714.5 (A4), U3716.5 (A4)
WCS.B0.A5: U3701.6 (A5), U3703.6 (A5), U3705.6 (A5), U3707.6 (A5), U3710.6 (A5), U3712.6 (A5), U3714.6 (A5), U3716.6 (A5)
WCS.B0.A6: U3701.7 (A6), U3703.7 (A6), U3705.7 (A6), U3707.7 (A6), U3710.7 (A6), U3712.7 (A6), U3714.7 (A6), U3716.7 (A6)
WCS.B0.A7: U3701.13 (A7), U3703.13 (A7), U3705.13 (A7), U3707.13 (A7), U3710.13 (A7), U3712.13 (A7), U3714.13 (A7), U3716.13 (A7)
WCS.B0.A8: U3701.14 (A8), U3703.14 (A8), U3705.14 (A8), U3707.14 (A8), U3710.14 (A8), U3712.14 (A8), U3714.14 (A8), U3716.14 (A8)
WCS.B0.A9: U3701.15 (A9), U3703.15 (A9), U3705.15 (A9), U3707.15 (A9), U3710.15 (A9), U3712.15 (A9), U3714.15 (A9), U3716.15 (A9)
WCS.B0.A10: U3701.16 (A10), U3703.16 (A10), U3705.16 (A10), U3707.16 (A10), U3710.16 (A10), U3712.16 (A10), U3714.16 (A10), U3716.16 (A10)
WCS.B0.A11: U3701.17 (A11), U3703.17 (A11), U3705.17 (A11), U3707.17 (A11), U3710.17 (A11), U3712.17 (A11), U3714.17 (A11), U3716.17 (A11)
WCS.B0.A12: U3701.18 (A12), U3703.18 (A12), U3705.18 (A12), U3707.18 (A12), U3710.18 (A12), U3712.18 (A12), U3714.18 (A12), U3716.18 (A12)
WCS.B0.A13: U3701.19 (A13), U3703.19 (A13), U3705.19 (A13), U3707.19 (A13), U3710.19 (A13), U3712.19 (A13), U3714.19 (A13), U3716.19 (A13)
WCS.B1.A0: U3702.1 (A0), U3704.1 (A0), U3706.1 (A0), U3708.1 (A0), U3709.1 (A0), U3711.1 (A0), U3713.1 (A0), U3715.1 (A0)
WCS.B1.A1: U3702.2 (A1), U3704.2 (A1), U3706.2 (A1), U3708.2 (A1), U3709.2 (A1), U3711.2 (A1), U3713.2 (A1), U3715.2 (A1)
WCS.B1.A2: U3702.3 (A2), U3704.3 (A2), U3706.3 (A2), U3708.3 (A2), U3709.3 (A2), U3711.3 (A2), U3713.3 (A2), U3715.3 (A2)
WCS.B1.A3: U3702.4 (A3), U3704.4 (A3), U3706.4 (A3), U3708.4 (A3), U3709.4 (A3), U3711.4 (A3), U3713.4 (A3), U3715.4 (A3)
WCS.B1.A4: U3702.5 (A4), U3704.5 (A4), U3706.5 (A4), U3708.5 (A4), U3709.5 (A4), U3711.5 (A4), U3713.5 (A4), U3715.5 (A4)
WCS.B1.A5: U3702.6 (A5), U3704.6 (A5), U3706.6 (A5), U3708.6 (A5), U3709.6 (A5), U3711.6 (A5), U3713.6 (A5), U3715.6 (A5)
WCS.B1.A6: U3702.7 (A6), U3704.7 (A6), U3706.7 (A6), U3708.7 (A6), U3709.7 (A6), U3711.7 (A6), U3713.7 (A6), U3715.7 (A6)
WCS.B1.A7: U3702.13 (A7), U3704.13 (A7), U3706.13 (A7), U3708.13 (A7), U3709.13 (A7), U3711.13 (A7), U3713.13 (A7), U3715.13 (A7)
WCS.B1.A8: U3702.14 (A8), U3704.14 (A8), U3706.14 (A8), U3708.14 (A8), U3709.14 (A8), U3711.14 (A8), U3713.14 (A8), U3715.14 (A8)
WCS.B1.A9: U3702.15 (A9), U3704.15 (A9), U3706.15 (A9), U3708.15 (A9), U3709.15 (A9), U3711.15 (A9), U3713.15 (A9), U3715.15 (A9)
WCS.B1.A10: U3702.16 (A10), U3704.16 (A10), U3706.16 (A10), U3708.16 (A10), U3709.16 (A10), U3711.16 (A10), U3713.16 (A10), U3715.16 (A10)
WCS.B1.A11: U3702.17 (A11), U3704.17 (A11), U3706.17 (A11), U3708.17 (A11), U3709.17 (A11), U3711.17 (A11), U3713.17 (A11), U3715.17 (A11)
WCS.B1.A12: U3702.18 (A12), U3704.18 (A12), U3706.18 (A12), U3708.18 (A12), U3709.18 (A12), U3711.18 (A12), U3713.18 (A12), U3715.18 (A12)
WCS.B1.A13: U3702.19 (A13), U3704.19 (A13), U3706.19 (A13), U3708.19 (A13), U3709.19 (A13), U3711.19 (A13), U3713.19 (A13), U3715.19 (A13)
WCS.D0: U3701.8 (Q)
WCS.D1: U3702.8 (Q)
WCS.D2: U3703.8 (Q)
WCS.D3: U3704.8 (Q)
WCS.D4: U3705.8 (Q)
WCS.D5: U3706.8 (Q)
WCS.D6: U3707.8 (Q)
WCS.D7: U3708.8 (Q)
WCS.D8: U3709.8 (Q)
WCS.D9: U3710.8 (Q)
WCS.D10: U3711.8 (Q)
WCS.D11: U3712.8 (Q)
WCS.D12: U3713.8 (Q)
WCS.D13: U3714.8 (Q)
WCS.D14: U3715.8 (Q)
WCS.D15: U3716.8 (Q)
WCS.WE~0: U3701.9 (WE), U3703.9 (WE), U3705.9 (WE), U3707.9 (WE), U3708.9 (WE), U3710.9 (WE), U3712.9 (WE), U3714.9 (WE), U3716.9 (WE)
WCS.WE~1: U3702.9 (WE), U3704.9 (WE), U3706.9 (WE), U3709.9 (WE), U3711.9 (WE), U3713.9 (WE), U3715.9 (WE)
