Datamuseum-DK/R1000.HwDoc/Schematics/FIU/pg_37.kicad_sch

## KiCad design Schematics/FIU/pg_37.kicad_sch (2023-01-10)

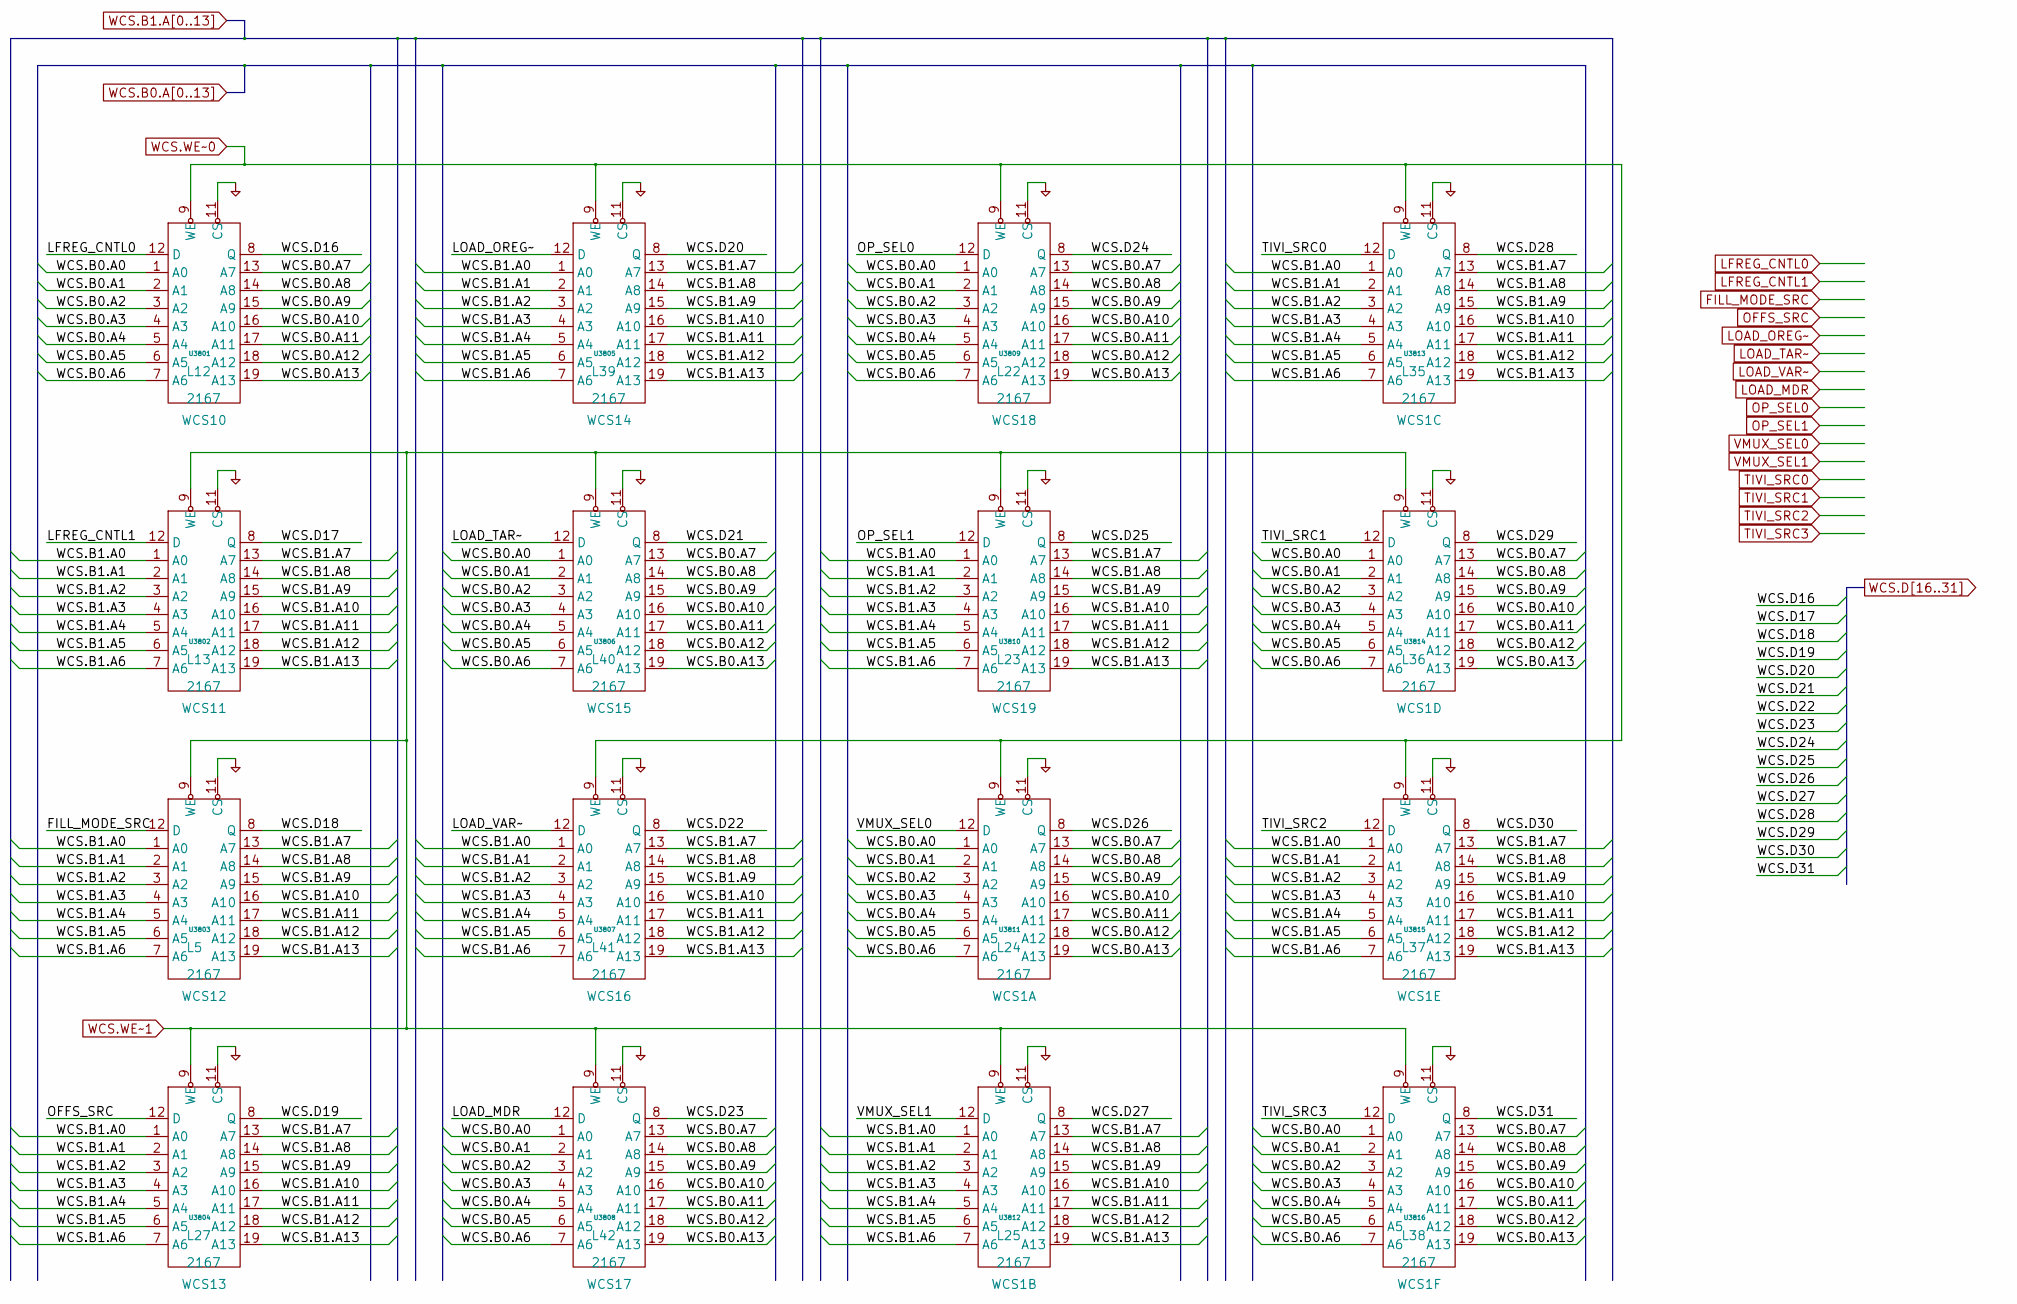
[picture p322: schematic pg_37.kicad_sch]

Parts:
U3801, U3802, U3803, U3804, U3805, U3806, U3807, U3808, U3809, U3810, U3811, U3812, U3813, U3814, U3815, U3816: 2167

Connections:
FILL_MODE_SRC: U3803.12 (D)
LFREG_CNTL0: U3801.12 (D)
LFREG_CNTL1: U3802.12 (D)
LOAD_MDR: U3808.12 (D)
LOAD_OREG~: U3805.12 (D)
LOAD_TAR~: U3806.12 (D)
LOAD_VAR~: U3807.12 (D)
OFFS_SRC: U3804.12 (D)
OP_SEL0: U3809.12 (D)
OP_SEL1: U3810.12 (D)
PD: U3801.11 (CS), U3802.11 (CS), U3803.11 (CS), U3804.11 (CS), U3805.11 (CS), U3806.11 (CS), U3807.11 (CS), U3808.11 (CS), U3809.11 (CS), U3810.11 (CS), U3811.11 (CS), U3812.11 (CS), U3813.11 (CS), U3814.11 (CS), U3815.11 (CS), U3816.11 (CS)
TIVI_SRC0: U3813.12 (D)
TIVI_SRC1: U3814.12 (D)
TIVI_SRC2: U3815.12 (D)
TIVI_SRC3: U3816.12 (D)
VMUX_SEL0: U3811.12 (D)
VMUX_SEL1: U3812.12 (D)
WCS.B0.A0: U3801.1 (A0), U3806.1 (A0), U3808.1 (A0), U3809.1 (A0), U3811.1 (A0), U3814.1 (A0), U3816.1 (A0)
WCS.B0.A1: U3801.2 (A1), U3806.2 (A1), U3808.2 (A1), U3809.2 (A1), U3811.2 (A1), U3814.2 (A1), U3816.2 (A1)
WCS.B0.A2: U3801.3 (A2), U3806.3 (A2), U3808.3 (A2), U3809.3 (A2), U3811.3 (A2), U3814.3 (A2), U3816.3 (A2)
WCS.B0.A3: U3801.4 (A3), U3806.4 (A3), U3808.4 (A3), U3809.4 (A3), U3811.4 (A3), U3814.4 (A3), U3816.4 (A3)
WCS.B0.A4: U3801.5 (A4), U3806.5 (A4), U3808.5 (A4), U3809.5 (A4), U3811.5 (A4), U3814.5 (A4), U3816.5 (A4)
WCS.B0.A5: U3801.6 (A5), U3806.6 (A5), U3808.6 (A5), U3809.6 (A5), U3811.6 (A5), U3814.6 (A5), U3816.6 (A5)
WCS.B0.A6: U3801.7 (A6), U3806.7 (A6), U3808.7 (A6), U3809.7 (A6), U3811.7 (A6), U3814.7 (A6), U3816.7 (A6)
WCS.B0.A7: U3801.13 (A7), U3806.13 (A7), U3808.13 (A7), U3809.13 (A7), U3811.13 (A7), U3814.13 (A7), U3816.13 (A7)
WCS.B0.A8: U3801.14 (A8), U3806.14 (A8), U3808.14 (A8), U3809.14 (A8), U3811.14 (A8), U3814.14 (A8), U3816.14 (A8)
WCS.B0.A9: U3801.15 (A9), U3806.15 (A9), U3808.15 (A9), U3809.15 (A9), U3811.15 (A9), U3814.15 (A9), U3816.15 (A9)
WCS.B0.A10: U3801.16 (A10), U3806.16 (A10), U3808.16 (A10), U3809.16 (A10), U3811.16 (A10), U3814.16 (A10), U3816.16 (A10)
WCS.B0.A11: U3801.17 (A11), U3806.17 (A11), U3808.17 (A11), U3809.17 (A11), U3811.17 (A11), U3814.17 (A11), U3816.17 (A11)
WCS.B0.A12: U3801.18 (A12), U3806.18 (A12), U3808.18 (A12), U3809.18 (A12), U3811.18 (A12), U3814.18 (A12), U3816.18 (A12)
WCS.B0.A13: U3801.19 (A13), U3806.19 (A13), U3808.19 (A13), U3809.19 (A13), U3811.19 (A13), U3814.19 (A13), U3816.19 (A13)
WCS.B1.A0: U3802.1 (A0), U3803.1 (A0), U3804.1 (A0), U3805.1 (A0), U3807.1 (A0), U3810.1 (A0), U3812.1 (A0), U3813.1 (A0), U3815.1 (A0)
WCS.B1.A1: U3802.2 (A1), U3803.2 (A1), U3804.2 (A1), U3805.2 (A1), U3807.2 (A1), U3810.2 (A1), U3812.2 (A1), U3813.2 (A1), U3815.2 (A1)
WCS.B1.A2: U3802.3 (A2), U3803.3 (A2), U3804.3 (A2), U3805.3 (A2), U3807.3 (A2), U3810.3 (A2), U3812.3 (A2), U3813.3 (A2), U3815.3 (A2)
WCS.B1.A3: U3802.4 (A3), U3803.4 (A3), U3804.4 (A3), U3805.4 (A3), U3807.4 (A3), U3810.4 (A3), U3812.4 (A3), U3813.4 (A3), U3815.4 (A3)
WCS.B1.A4: U3802.5 (A4), U3803.5 (A4), U3804.5 (A4), U3805.5 (A4), U3807.5 (A4), U3810.5 (A4), U3812.5 (A4), U3813.5 (A4), U3815.5 (A4)
WCS.B1.A5: U3802.6 (A5), U3803.6 (A5), U3804.6 (A5), U3805.6 (A5), U3807.6 (A5), U3810.6 (A5), U3812.6 (A5), U3813.6 (A5), U3815.6 (A5)
WCS.B1.A6: U3802.7 (A6), U3803.7 (A6), U3804.7 (A6), U3805.7 (A6), U3807.7 (A6), U3810.7 (A6), U3812.7 (A6), U3813.7 (A6), U3815.7 (A6)
WCS.B1.A7: U3802.13 (A7), U3803.13 (A7), U3804.13 (A7), U3805.13 (A7), U3807.13 (A7), U3810.13 (A7), U3812.13 (A7), U3813.13 (A7), U3815.13 (A7)
WCS.B1.A8: U3802.14 (A8), U3803.14 (A8), U3804.14 (A8), U3805.14 (A8), U3807.14 (A8), U3810.14 (A8), U3812.14 (A8), U3813.14 (A8), U3815.14 (A8)
WCS.B1.A9: U3802.15 (A9), U3803.15 (A9), U3804.15 (A9), U3805.15 (A9), U3807.15 (A9), U3810.15 (A9), U3812.15 (A9), U3813.15 (A9), U3815.15 (A9)
WCS.B1.A10: U3802.16 (A10), U3803.16 (A10), U3804.16 (A10), U3805.16 (A10), U3807.16 (A10), U3810.16 (A10), U3812.16 (A10), U3813.16 (A10), U3815.16 (A10)
WCS.B1.A11: U3802.17 (A11), U3803.17 (A11), U3804.17 (A11), U3805.17 (A11), U3807.17 (A11), U3810.17 (A11), U3812.17 (A11), U3813.17 (A11), U3815.17 (A11)
WCS.B1.A12: U3802.18 (A12), U3803.18 (A12), U3804.18 (A12), U3805.18 (A12), U3807.18 (A12), U3810.18 (A12), U3812.18 (A12), U3813.18 (A12), U3815.18 (A12)
WCS.B1.A13: U3802.19 (A13), U3803.19 (A13), U3804.19 (A13), U3805.19 (A13), U3807.19 (A13), U3810.19 (A13), U3812.19 (A13), U3813.19 (A13), U3815.19 (A13)
WCS.D16: U3801.8 (Q)
WCS.D17: U3802.8 (Q)
WCS.D18: U3803.8 (Q)
WCS.D19: U3804.8 (Q)
WCS.D20: U3805.8 (Q)
WCS.D21: U3806.8 (Q)
WCS.D22: U3807.8 (Q)
WCS.D23: U3808.8 (Q)
WCS.D24: U3809.8 (Q)
WCS.D25: U3810.8 (Q)
WCS.D26: U3811.8 (Q)
WCS.D27: U3812.8 (Q)
WCS.D28: U3813.8 (Q)
WCS.D29: U3814.8 (Q)
WCS.D30: U3815.8 (Q)
WCS.D31: U3816.8 (Q)
WCS.WE~0: U3801.9 (WE), U3805.9 (WE), U3807.9 (WE), U3809.9 (WE), U3811.9 (WE), U3813.9 (WE), U3815.9 (WE)
WCS.WE~1: U3802.9 (WE), U3803.9 (WE), U3804.9 (WE), U3806.9 (WE), U3808.9 (WE), U3810.9 (WE), U3812.9 (WE), U3814.9 (WE), U3816.9 (WE)
