Datamuseum-DK/R1000.HwDoc/Schematics/FIU/pg_38.kicad_sch

## KiCad design Schematics/FIU/pg_38.kicad_sch (2023-01-10)

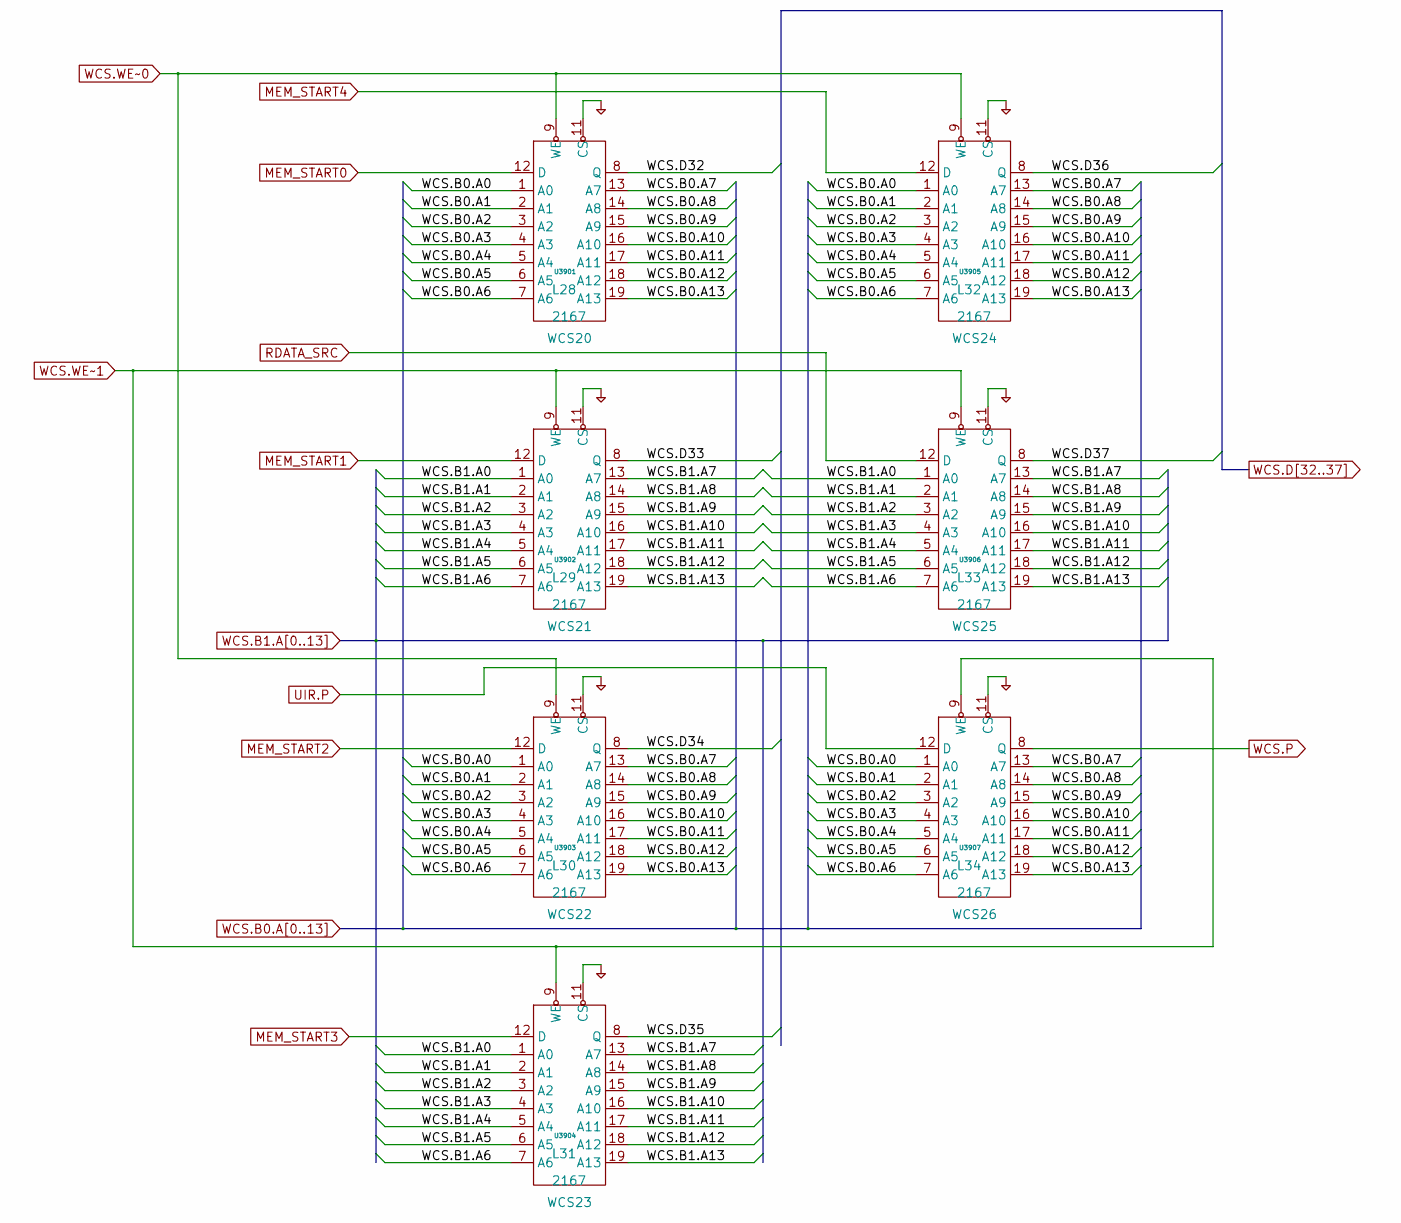
[picture p323: schematic pg_38.kicad_sch]

Parts:
U3901, U3902, U3903, U3904, U3905, U3906, U3907: 2167

Connections:
MEM_START0: U3901.12 (D)
MEM_START1: U3902.12 (D)
MEM_START2: U3903.12 (D)
MEM_START3: U3904.12 (D)
MEM_START4: U3905.12 (D)
PD: U3901.11 (CS), U3902.11 (CS), U3903.11 (CS), U3904.11 (CS), U3905.11 (CS), U3906.11 (CS), U3907.11 (CS)
RDATA_SRC: U3906.12 (D)
UIR.P: U3907.12 (D)
WCS.B0.A0: U3901.1 (A0), U3903.1 (A0), U3905.1 (A0), U3907.1 (A0)
WCS.B0.A1: U3901.2 (A1), U3903.2 (A1), U3905.2 (A1), U3907.2 (A1)
WCS.B0.A2: U3901.3 (A2), U3903.3 (A2), U3905.3 (A2), U3907.3 (A2)
WCS.B0.A3: U3901.4 (A3), U3903.4 (A3), U3905.4 (A3), U3907.4 (A3)
WCS.B0.A4: U3901.5 (A4), U3903.5 (A4), U3905.5 (A4), U3907.5 (A4)
WCS.B0.A5: U3901.6 (A5), U3903.6 (A5), U3905.6 (A5), U3907.6 (A5)
WCS.B0.A6: U3901.7 (A6), U3903.7 (A6), U3905.7 (A6), U3907.7 (A6)
WCS.B0.A7: U3901.13 (A7), U3903.13 (A7), U3905.13 (A7), U3907.13 (A7)
WCS.B0.A8: U3901.14 (A8), U3903.14 (A8), U3905.14 (A8), U3907.14 (A8)
WCS.B0.A9: U3901.15 (A9), U3903.15 (A9), U3905.15 (A9), U3907.15 (A9)
WCS.B0.A10: U3901.16 (A10), U3903.16 (A10), U3905.16 (A10), U3907.16 (A10)
WCS.B0.A11: U3901.17 (A11), U3903.17 (A11), U3905.17 (A11), U3907.17 (A11)
WCS.B0.A12: U3901.18 (A12), U3903.18 (A12), U3905.18 (A12), U3907.18 (A12)
WCS.B0.A13: U3901.19 (A13), U3903.19 (A13), U3905.19 (A13), U3907.19 (A13)
WCS.B1.A0: U3902.1 (A0), U3904.1 (A0), U3906.1 (A0)
WCS.B1.A1: U3902.2 (A1), U3904.2 (A1), U3906.2 (A1)
WCS.B1.A2: U3902.3 (A2), U3904.3 (A2), U3906.3 (A2)
WCS.B1.A3: U3902.4 (A3), U3904.4 (A3), U3906.4 (A3)
WCS.B1.A4: U3902.5 (A4), U3904.5 (A4), U3906.5 (A4)
WCS.B1.A5: U3902.6 (A5), U3904.6 (A5), U3906.6 (A5)
WCS.B1.A6: U3902.7 (A6), U3904.7 (A6), U3906.7 (A6)
WCS.B1.A7: U3902.13 (A7), U3904.13 (A7), U3906.13 (A7)
WCS.B1.A8: U3902.14 (A8), U3904.14 (A8), U3906.14 (A8)
WCS.B1.A9: U3902.15 (A9), U3904.15 (A9), U3906.15 (A9)
WCS.B1.A10: U3902.16 (A10), U3904.16 (A10), U3906.16 (A10)
WCS.B1.A11: U3902.17 (A11), U3904.17 (A11), U3906.17 (A11)
WCS.B1.A12: U3902.18 (A12), U3904.18 (A12), U3906.18 (A12)
WCS.B1.A13: U3902.19 (A13), U3904.19 (A13), U3906.19 (A13)
WCS.D32: U3901.8 (Q)
WCS.D33: U3902.8 (Q)
WCS.D34: U3903.8 (Q)
WCS.D35: U3904.8 (Q)
WCS.D36: U3905.8 (Q)
WCS.D37: U3906.8 (Q)
WCS.P: U3907.8 (Q)
WCS.WE~0: U3901.9 (WE), U3903.9 (WE), U3905.9 (WE)
WCS.WE~1: U3902.9 (WE), U3904.9 (WE), U3906.9 (WE), U3907.9 (WE)
