Datamuseum-DK/R1000.HwDoc/Schematics/FIU/pg_39.kicad_sch

## KiCad design Schematics/FIU/pg_39.kicad_sch (2023-01-10)

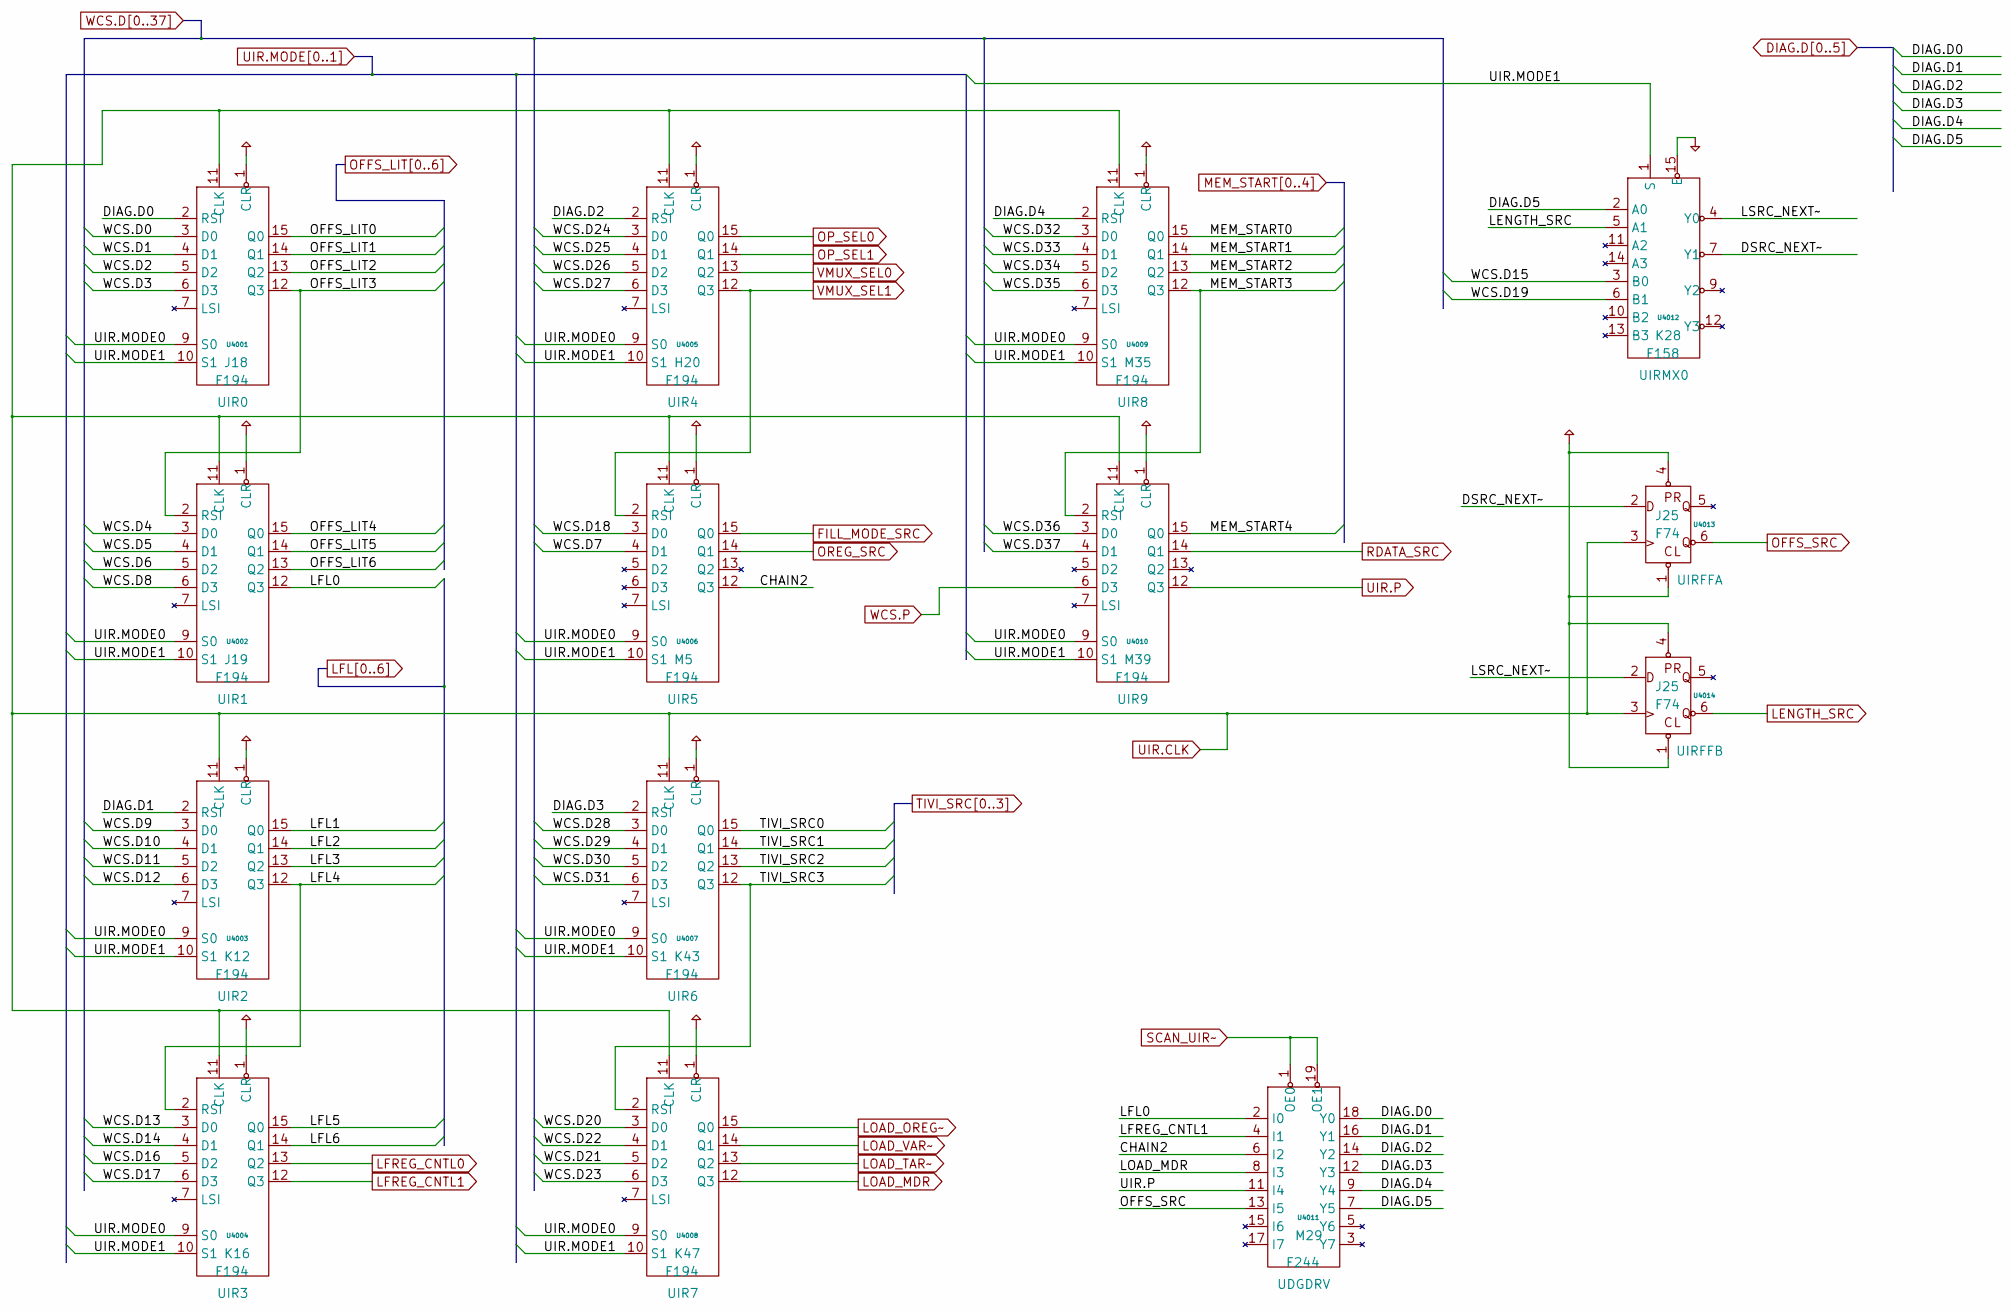
[picture p324: schematic pg_39.kicad_sch]

Parts:
U4001, U4002, U4003, U4004, U4005, U4006, U4007, U4008, U4009, U4010: F194
U4011: F244
U4012: F158
U4013, U4014: F74

Connections:
CHAIN2: U4006.12 (Q3), U4011.6 (I2)
DIAG.D0: U4001.2 (RSI), U4011.18 (Y0)
DIAG.D1: U4003.2 (RSI), U4011.16 (Y1)
DIAG.D2: U4005.2 (RSI), U4011.14 (Y2)
DIAG.D3: U4007.2 (RSI), U4011.12 (Y3)
DIAG.D4: U4009.2 (RSI), U4011.9 (Y4)
DIAG.D5: U4011.7 (Y5), U4012.2 (A0)
DSRC_NEXT~: U4012.7 (Y1), U4013.2 (D)
FILL_MODE_SRC: U4006.15 (Q0)
LENGTH_SRC: U4012.5 (A1), U4014.6 (Q_)
LFL0: U4002.12 (Q3), U4011.2 (I0)
LFL1: U4003.15 (Q0)
LFL2: U4003.14 (Q1)
LFL3: U4003.13 (Q2)
LFL4: U4003.12 (Q3), U4004.2 (RSI)
LFL5: U4004.15 (Q0)
LFL6: U4004.14 (Q1)
LFREG_CNTL0: U4004.13 (Q2)
LFREG_CNTL1: U4004.12 (Q3), U4011.4 (I1)
LOAD_MDR: U4008.12 (Q3), U4011.8 (I3)
LOAD_OREG~: U4008.15 (Q0)
LOAD_TAR~: U4008.13 (Q2)
LOAD_VAR~: U4008.14 (Q1)
LSRC_NEXT~: U4012.4 (Y0), U4014.2 (D)
MEM_START0: U4009.15 (Q0)
MEM_START1: U4009.14 (Q1)
MEM_START2: U4009.13 (Q2)
MEM_START3: U4009.12 (Q3), U4010.2 (RSI)
MEM_START4: U4010.15 (Q0)
OFFS_LIT0: U4001.15 (Q0)
OFFS_LIT1: U4001.14 (Q1)
OFFS_LIT2: U4001.13 (Q2)
OFFS_LIT3: U4001.12 (Q3), U4002.2 (RSI)
OFFS_LIT4: U4002.15 (Q0)
OFFS_LIT5: U4002.14 (Q1)
OFFS_LIT6: U4002.13 (Q2)
OFFS_SRC: U4011.13 (I5), U4013.6 (Q_)
OP_SEL0: U4005.15 (Q0)
OP_SEL1: U4005.14 (Q1)
OREG_SRC: U4006.14 (Q1)
PD: U4012.15 (E)
PU: U4001.1 (CLR), U4002.1 (CLR), U4003.1 (CLR), U4004.1 (CLR), U4005.1 (CLR), U4006.1 (CLR), U4007.1 (CLR), U4008.1 (CLR), U4009.1 (CLR), U4010.1 (CLR), U4013.1 (CL_), U4013.4 (PR_), U4014.1 (CL_), U4014.4 (PR_)
RDATA_SRC: U4010.14 (Q1)
SCAN_UIR~: U4011.1 (OE0), U4011.19 (OE1)
TIVI_SRC0: U4007.15 (Q0)
TIVI_SRC1: U4007.14 (Q1)
TIVI_SRC2: U4007.13 (Q2)
TIVI_SRC3: U4007.12 (Q3), U4008.2 (RSI)
UIR.CLK: U4001.11 (CLK), U4002.11 (CLK), U4003.11 (CLK), U4004.11 (CLK), U4005.11 (CLK), U4006.11 (CLK), U4007.11 (CLK), U4008.11 (CLK), U4009.11 (CLK), U4010.11 (CLK), U4013.3 (CLK), U4014.3 (CLK)
UIR.MODE0: U4001.9 (S0), U4002.9 (S0), U4003.9 (S0), U4004.9 (S0), U4005.9 (S0), U4006.9 (S0), U4007.9 (S0), U4008.9 (S0), U4009.9 (S0), U4010.9 (S0)
UIR.MODE1: U4001.10 (S1), U4002.10 (S1), U4003.10 (S1), U4004.10 (S1), U4005.10 (S1), U4006.10 (S1), U4007.10 (S1), U4008.10 (S1), U4009.10 (S1), U4010.10 (S1), U4012.1 (S)
UIR.P: U4010.12 (Q3), U4011.11 (I4)
VMUX_SEL0: U4005.13 (Q2)
VMUX_SEL1: U4005.12 (Q3), U4006.2 (RSI)
WCS.D0: U4001.3 (D0)
WCS.D1: U4001.4 (D1)
WCS.D2: U4001.5 (D2)
WCS.D3: U4001.6 (D3)
WCS.D4: U4002.3 (D0)
WCS.D5: U4002.4 (D1)
WCS.D6: U4002.5 (D2)
WCS.D7: U4006.4 (D1)
WCS.D8: U4002.6 (D3)
WCS.D9: U4003.3 (D0)
WCS.D10: U4003.4 (D1)
WCS.D11: U4003.5 (D2)
WCS.D12: U4003.6 (D3)
WCS.D13: U4004.3 (D0)
WCS.D14: U4004.4 (D1)
WCS.D15: U4012.3 (B0)
WCS.D16: U4004.5 (D2)
WCS.D17: U4004.6 (D3)
WCS.D18: U4006.3 (D0)
WCS.D19: U4012.6 (B1)
WCS.D20: U4008.3 (D0)
WCS.D21: U4008.5 (D2)
WCS.D22: U4008.4 (D1)
WCS.D23: U4008.6 (D3)
WCS.D24: U4005.3 (D0)
WCS.D25: U4005.4 (D1)
WCS.D26: U4005.5 (D2)
WCS.D27: U4005.6 (D3)
WCS.D28: U4007.3 (D0)
WCS.D29: U4007.4 (D1)
WCS.D30: U4007.5 (D2)
WCS.D31: U4007.6 (D3)
WCS.D32: U4009.3 (D0)
WCS.D33: U4009.4 (D1)
WCS.D34: U4009.5 (D2)
WCS.D35: U4009.6 (D3)
WCS.D36: U4010.3 (D0)
WCS.D37: U4010.4 (D1)
WCS.P: U4010.6 (D3)
