Datamuseum-DK/R1000.HwDoc/Schematics/FIU/pg_40.kicad_sch

## KiCad design Schematics/FIU/pg_40.kicad_sch (2023-01-10)

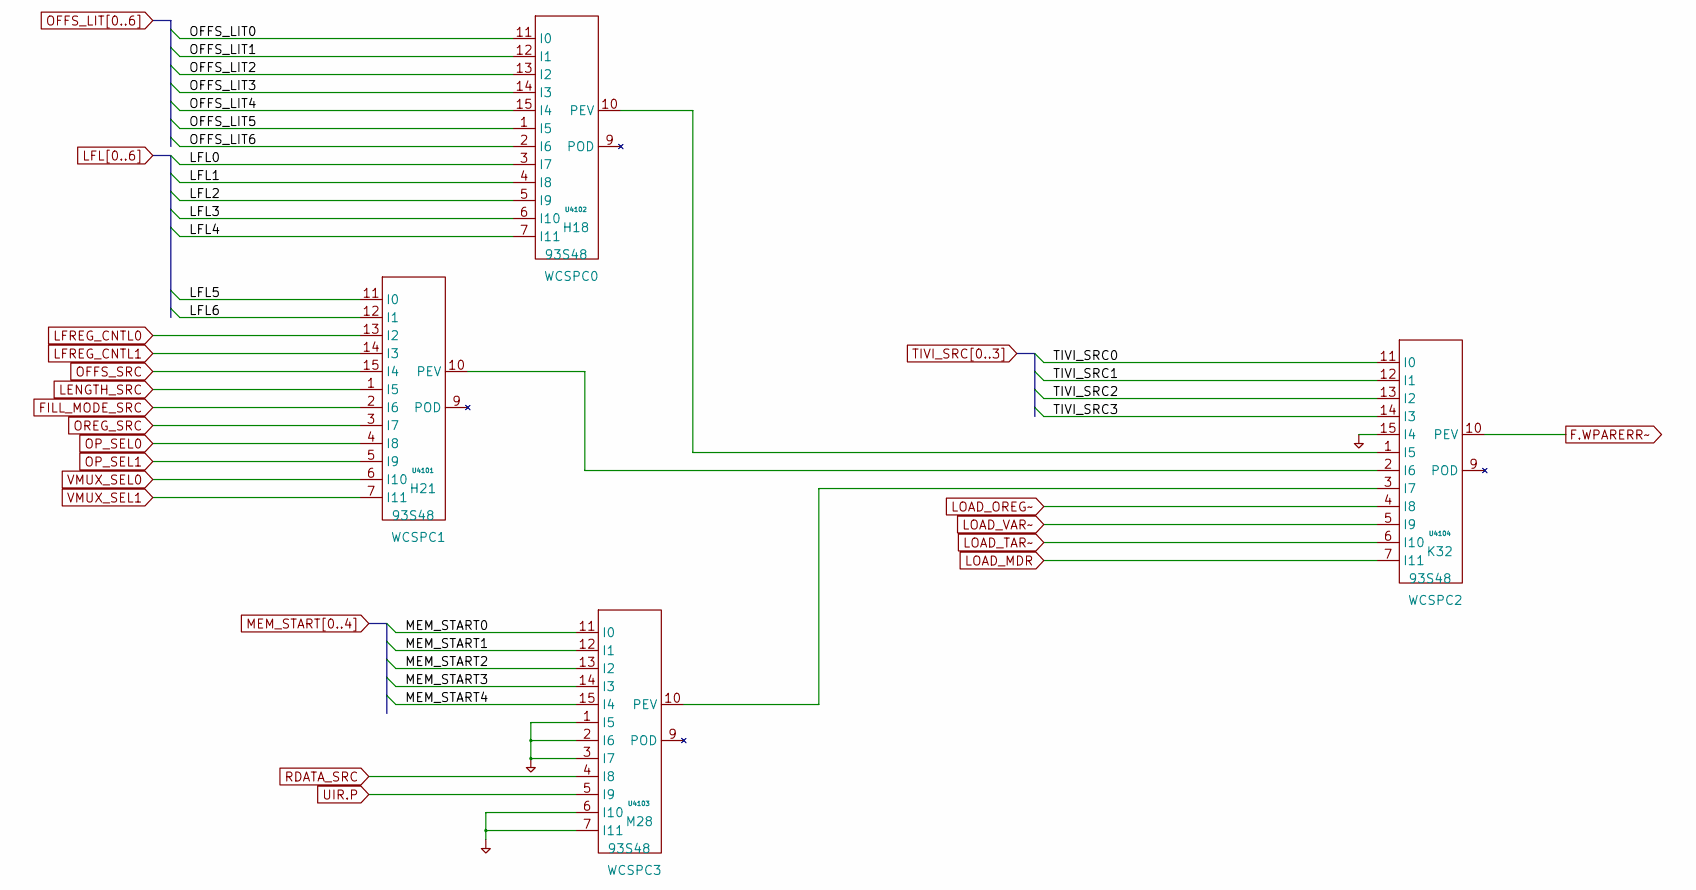
[picture p325: schematic pg_40.kicad_sch]

Parts:
U4101, U4102, U4103, U4104: 93S48

Connections:
F.WPARERR~: U4104.10 (PEV)
FILL_MODE_SRC: U4101.2 (I6)
LENGTH_SRC: U4101.1 (I5)
LFL0: U4102.3 (I7)
LFL1: U4102.4 (I8)
LFL2: U4102.5 (I9)
LFL3: U4102.6 (I10)
LFL4: U4102.7 (I11)
LFL5: U4101.11 (I0)
LFL6: U4101.12 (I1)
LFREG_CNTL0: U4101.13 (I2)
LFREG_CNTL1: U4101.14 (I3)
LOAD_MDR: U4104.7 (I11)
LOAD_OREG~: U4104.4 (I8)
LOAD_TAR~: U4104.6 (I10)
LOAD_VAR~: U4104.5 (I9)
MEM_START0: U4103.11 (I0)
MEM_START1: U4103.12 (I1)
MEM_START2: U4103.13 (I2)
MEM_START3: U4103.14 (I3)
MEM_START4: U4103.15 (I4)
unnamed: U4101.10 (PEV), U4104.2 (I6)
unnamed: U4102.10 (PEV), U4104.1 (I5)
unnamed: U4103.10 (PEV), U4104.3 (I7)
OFFS_LIT0: U4102.11 (I0)
OFFS_LIT1: U4102.12 (I1)
OFFS_LIT2: U4102.13 (I2)
OFFS_LIT3: U4102.14 (I3)
OFFS_LIT4: U4102.15 (I4)
OFFS_LIT5: U4102.1 (I5)
OFFS_LIT6: U4102.2 (I6)
OFFS_SRC: U4101.15 (I4)
OP_SEL0: U4101.4 (I8)
OP_SEL1: U4101.5 (I9)
OREG_SRC: U4101.3 (I7)
PD: U4103.1 (I5), U4103.2 (I6), U4103.3 (I7), U4103.6 (I10), U4103.7 (I11), U4104.15 (I4)
RDATA_SRC: U4103.4 (I8)
TIVI_SRC0: U4104.11 (I0)
TIVI_SRC1: U4104.12 (I1)
TIVI_SRC2: U4104.13 (I2)
TIVI_SRC3: U4104.14 (I3)
UIR.P: U4103.5 (I9)
VMUX_SEL0: U4101.6 (I10)
VMUX_SEL1: U4101.7 (I11)
