Datamuseum-DK/R1000.HwDoc/Schematics/FIU/pg_41.kicad_sch

## KiCad design Schematics/FIU/pg_41.kicad_sch (2023-01-10)

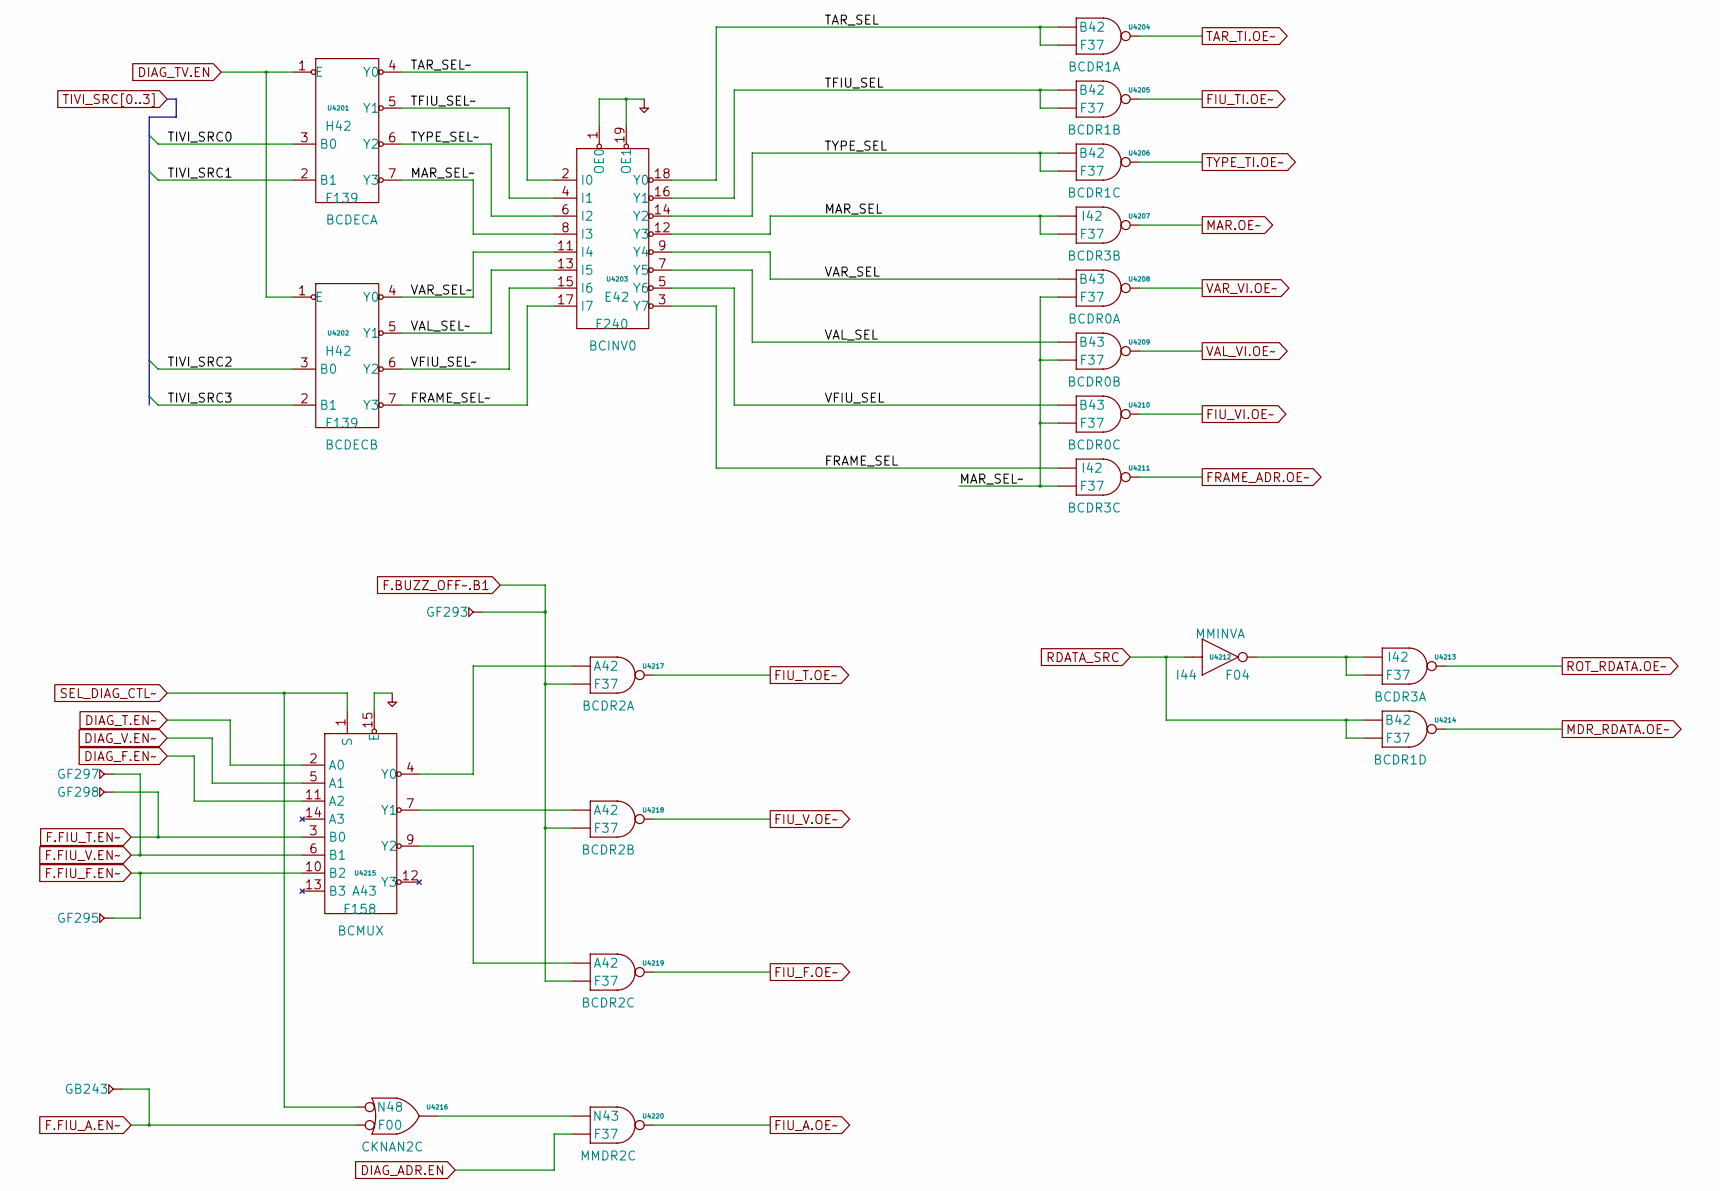
[picture p326: schematic pg_41.kicad_sch]

Parts:
GB243: GB
GF293, GF295, GF297, GF298: GF
U4201, U4202: F139
U4203: F240
U4204, U4205, U4206, U4207, U4208, U4209, U4210, U4211, U4213, U4214, U4217, U4218, U4219, U4220: F37
U4212: F04
U4215: F158
U4216: F00

Connections:
DIAG_ADR.EN: U4220.2 (D1)
DIAG_F.EN~: U4215.11 (A2)
DIAG_T.EN~: U4215.2 (A0)
DIAG_TV.EN: U4201.1 (E), U4202.1 (E)
DIAG_V.EN~: U4215.5 (A1)
F.BUZZ_OFF~.B1: GF293.1, U4217.2 (D1), U4218.2 (D1), U4219.2 (D1)
F.FIU_A.EN~: GB243.1, U4216.2 (D1)
F.FIU_F.EN~: GF295.1, U4215.10 (B2)
F.FIU_T.EN~: GF298.1, U4215.3 (B0)
F.FIU_V.EN~: GF297.1, U4215.6 (B1)
FIU_A.OE~: U4220.3 (Q)
FIU_F.OE~: U4219.3 (Q)
FIU_T.OE~: U4217.3 (Q)
FIU_TI.OE~: U4205.3 (Q)
FIU_V.OE~: U4218.3 (Q)
FIU_VI.OE~: U4210.3 (Q)
FRAME_ADR.OE~: U4211.3 (Q)
FRAME_SEL: U4203.3 (Y7), U4211.1 (D0)
FRAME_SEL~: U4202.7 (Y3), U4203.17 (I7)
MAR.OE~: U4207.3 (Q)
MAR_SEL: U4203.12 (Y3), U4207.1 (D0), U4207.2 (D1)
MAR_SEL~: U4201.7 (Y3), U4203.8 (I3), U4208.2 (D1), U4209.2 (D1), U4210.2 (D1), U4211.2 (D1)
MDR_RDATA.OE~: U4214.3 (Q)
unnamed: U4212.2 (Q), U4213.1 (D0), U4213.2 (D1)
unnamed: U4215.4 (Y0), U4217.1 (D0)
unnamed: U4215.7 (Y1), U4218.1 (D0)
unnamed: U4215.9 (Y2), U4219.1 (D0)
unnamed: U4216.3 (Q), U4220.1 (D0)
PD: U4203.1 (OE0), U4203.19 (OE1), U4215.15 (E)
RDATA_SRC: U4212.1 (D0), U4214.1 (D0), U4214.2 (D1)
ROT_RDATA.OE~: U4213.3 (Q)
SEL_DIAG_CTL~: U4215.1 (S), U4216.1 (D0)
TAR_SEL: U4203.18 (Y0), U4204.1 (D0), U4204.2 (D1)
TAR_SEL~: U4201.4 (Y0), U4203.2 (I0)
TAR_TI.OE~: U4204.3 (Q)
TFIU_SEL: U4203.16 (Y1), U4205.1 (D0), U4205.2 (D1)
TFIU_SEL~: U4201.5 (Y1), U4203.4 (I1)
TIVI_SRC0: U4201.3 (B0)
TIVI_SRC1: U4201.2 (B1)
TIVI_SRC2: U4202.3 (B0)
TIVI_SRC3: U4202.2 (B1)
TYPE_SEL: U4203.14 (Y2), U4206.1 (D0), U4206.2 (D1)
TYPE_SEL~: U4201.6 (Y2), U4203.6 (I2)
TYPE_TI.OE~: U4206.3 (Q)
VAL_SEL: U4203.7 (Y5), U4209.1 (D0)
VAL_SEL~: U4202.5 (Y1), U4203.13 (I5)
VAL_VI.OE~: U4209.3 (Q)
VAR_SEL: U4203.9 (Y4), U4208.1 (D0)
VAR_SEL~: U4202.4 (Y0), U4203.11 (I4)
VAR_VI.OE~: U4208.3 (Q)
VFIU_SEL: U4203.5 (Y6), U4210.1 (D0)
VFIU_SEL~: U4202.6 (Y2), U4203.15 (I6)
