Datamuseum-DK/R1000.HwDoc/Schematics/FIU/pg_42.kicad_sch

## KiCad design Schematics/FIU/pg_42.kicad_sch (2023-01-10)

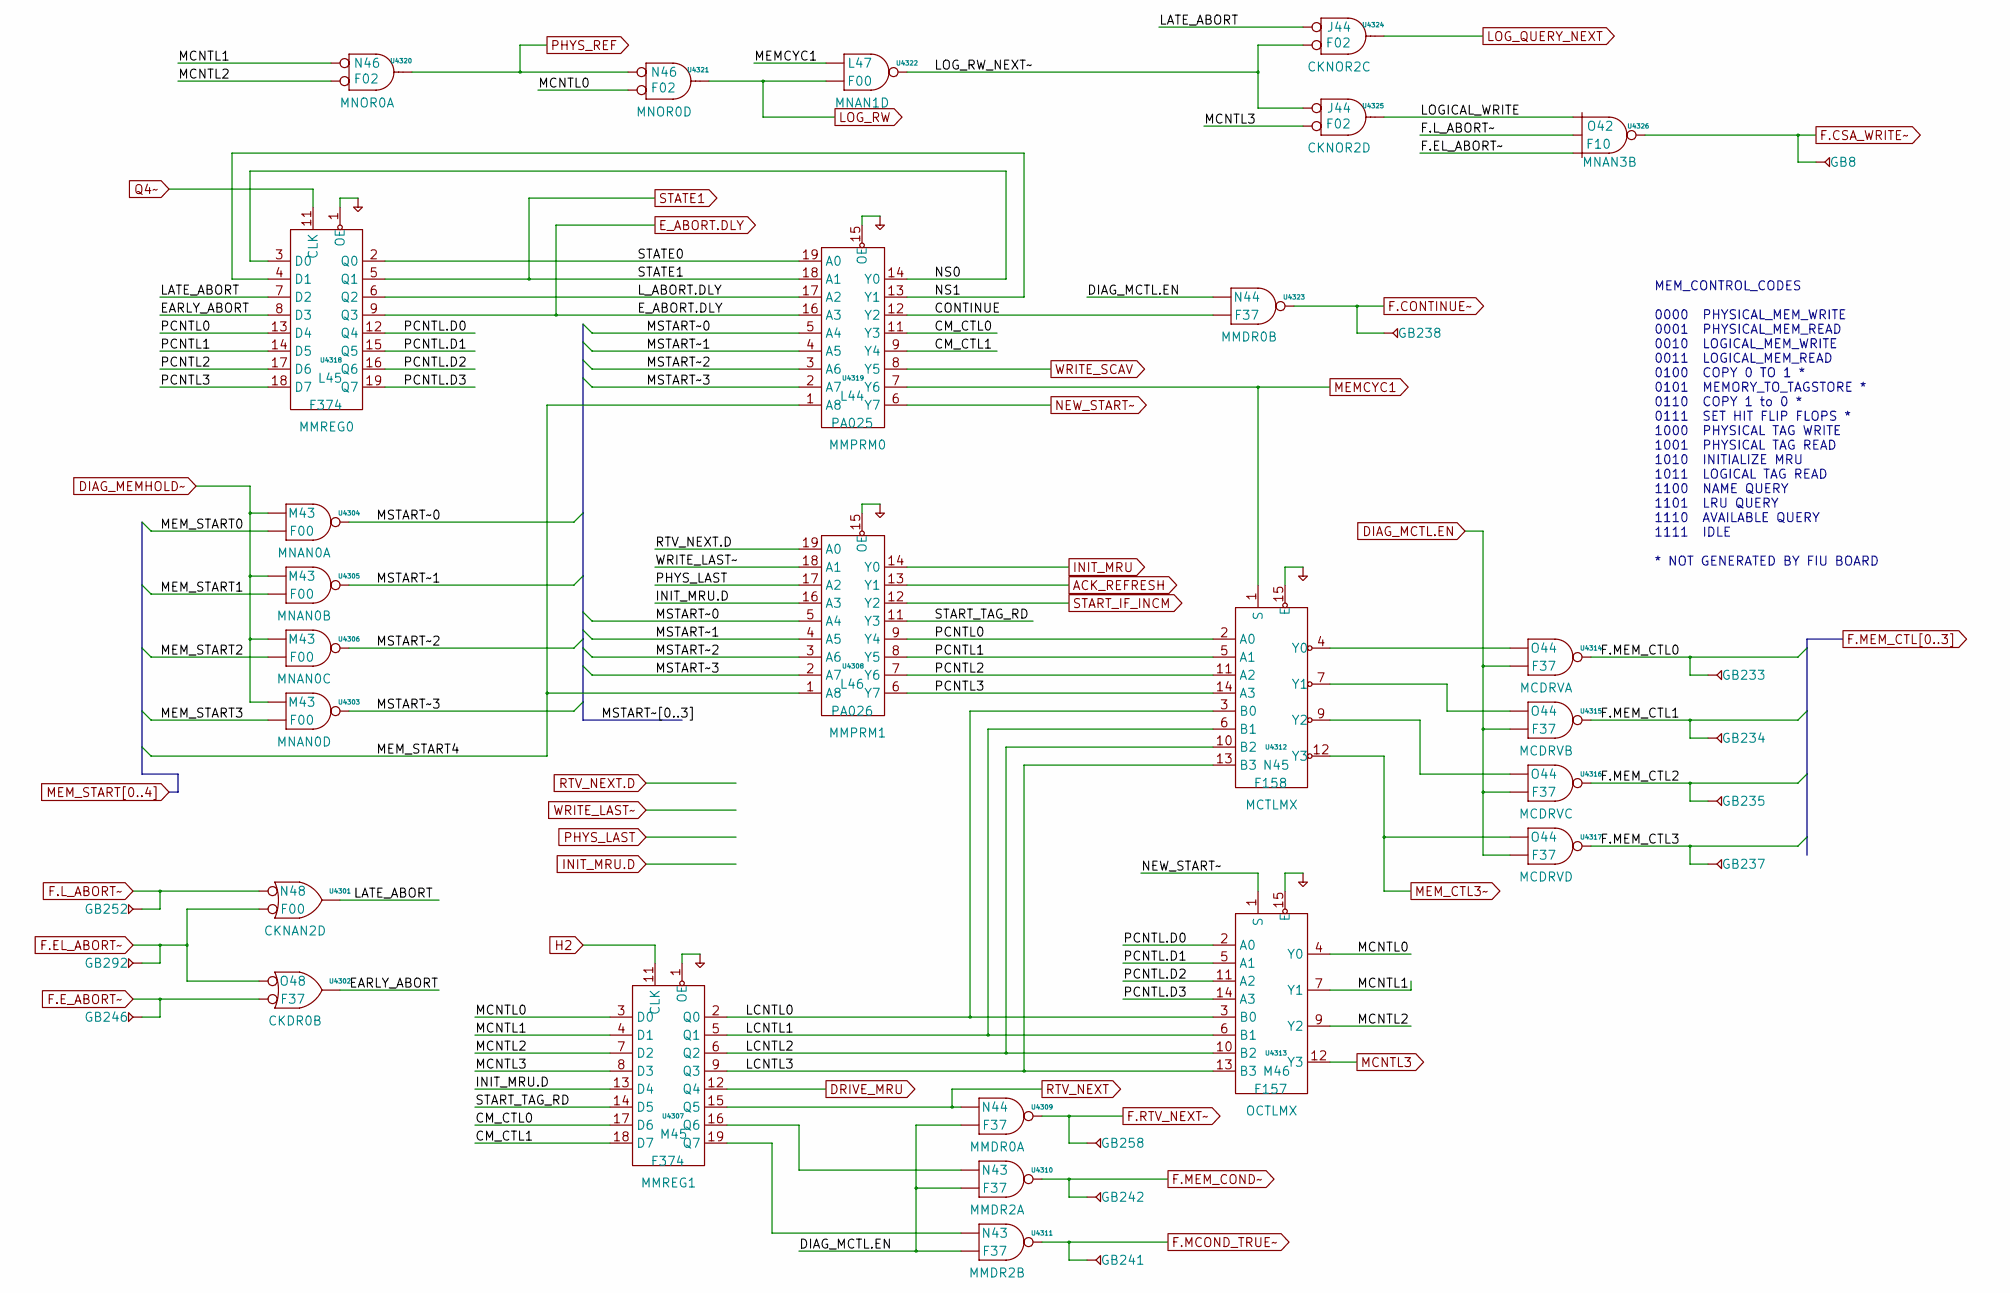
[picture p327: schematic pg_42.kicad_sch]

Parts:
GB8, GB233, GB234, GB235, GB237, GB238, GB241, GB242, GB246, GB252, GB258, GB292: GB
U4301, U4303, U4304, U4305, U4306, U4322: F00
U4302, U4309, U4310, U4311, U4314, U4315, U4316, U4317, U4323: F37
U4307, U4318: F374
U4308: PA026
U4312: F158
U4313: F157
U4319: PA025
U4320, U4321, U4324, U4325: F02
U4326: F10

Connections:
ACK_REFRESH: U4308.13 (Y1)
CM_CTL0: U4307.17 (D6), U4319.11 (Y3)
CM_CTL1: U4307.18 (D7), U4319.9 (Y4)
CONTINUE: U4319.12 (Y2), U4323.2 (D1)
DIAG_MCTL.EN: U4309.2 (D1), U4310.2 (D1), U4311.2 (D1), U4314.2 (D1), U4315.2 (D1), U4316.2 (D1), U4317.2 (D1), U4323.1 (D0)
DIAG_MEMHOLD~: U4303.1 (D0), U4304.1 (D0), U4305.1 (D0), U4306.1 (D0)
DRIVE_MRU: U4307.12 (Q4)
EARLY_ABORT: U4302.3 (Q), U4318.8 (D3)
E_ABORT.DLY: U4318.9 (Q3), U4319.16 (A3)
F.CONTINUE~: GB238.1, U4323.3 (Q)
F.CSA_WRITE~: GB8.1, U4326.4 (Q)
F.EL_ABORT~: GB292.1, U4301.2 (D1), U4302.1 (D0), U4326.3 (D2)
F.E_ABORT~: GB246.1, U4302.2 (D1)
F.L_ABORT~: GB252.1, U4301.1 (D0), U4326.2 (D1)
F.MCOND_TRUE~: GB241.1, U4311.3 (Q)
F.MEM_COND~: GB242.1, U4310.3 (Q)
F.MEM_CTL0: GB233.1, U4314.3 (Q)
F.MEM_CTL1: GB234.1, U4315.3 (Q)
F.MEM_CTL2: GB235.1, U4316.3 (Q)
F.MEM_CTL3: GB237.1, U4317.3 (Q)
F.RTV_NEXT~: GB258.1, U4309.3 (Q)
H2: U4307.11 (CLK)
INIT_MRU: U4308.14 (Y0)
INIT_MRU.D: U4307.13 (D4), U4308.16 (A3)
LATE_ABORT: U4301.3 (Q), U4318.7 (D2), U4324.1 (D0)
LCNTL0: U4307.2 (Q0), U4312.3 (B0), U4313.3 (B0)
LCNTL1: U4307.5 (Q1), U4312.6 (B1), U4313.6 (B1)
LCNTL2: U4307.6 (Q2), U4312.10 (B2), U4313.10 (B2)
LCNTL3: U4307.9 (Q3), U4312.13 (B3), U4313.13 (B3)
LOGICAL_WRITE: U4325.3 (Q), U4326.1 (D0)
LOG_QUERY_NEXT: U4324.3 (Q)
LOG_RW: U4321.3 (Q), U4322.2 (D1)
LOG_RW_NEXT~: U4322.3 (Q), U4324.2 (D1), U4325.1 (D0)
L_ABORT.DLY: U4318.6 (Q2), U4319.17 (A2)
MCNTL0: U4307.3 (D0), U4313.4 (Y0), U4321.2 (D1)
MCNTL1: U4307.4 (D1), U4313.7 (Y1), U4320.1 (D0)
MCNTL2: U4307.7 (D2), U4313.9 (Y2), U4320.2 (D1)
MCNTL3: U4307.8 (D3), U4313.12 (Y3), U4325.2 (D1)
MEMCYC1: U4312.1 (S), U4319.7 (Y6), U4322.1 (D0)
MEM_CTL3~: U4312.12 (Y3), U4317.1 (D0)
MEM_START0: U4304.2 (D1)
MEM_START1: U4305.2 (D1)
MEM_START2: U4306.2 (D1)
MEM_START3: U4303.2 (D1)
MEM_START4: U4308.1 (A8), U4319.1 (A8)
MSTART~0: U4304.3 (Q), U4308.5 (A4), U4319.5 (A4)
MSTART~1: U4305.3 (Q), U4308.4 (A5), U4319.4 (A5)
MSTART~2: U4306.3 (Q), U4308.3 (A6), U4319.3 (A6)
MSTART~3: U4303.3 (Q), U4308.2 (A7), U4319.2 (A7)
NEW_START~: U4313.1 (S), U4319.6 (Y7)
NS0: U4318.3 (D0), U4319.14 (Y0)
NS1: U4318.4 (D1), U4319.13 (Y1)
unnamed: U4307.16 (Q6), U4310.1 (D0)
unnamed: U4307.19 (Q7), U4311.1 (D0)
unnamed: U4312.4 (Y0), U4314.1 (D0)
unnamed: U4312.7 (Y1), U4315.1 (D0)
unnamed: U4312.9 (Y2), U4316.1 (D0)
PCNTL0: U4308.9 (Y4), U4312.2 (A0), U4318.13 (D4)
PCNTL1: U4308.8 (Y5), U4312.5 (A1), U4318.14 (D5)
PCNTL2: U4308.7 (Y6), U4312.11 (A2), U4318.17 (D6)
PCNTL3: U4308.6 (Y7), U4312.14 (A3), U4318.18 (D7)
PCNTL.D0: U4313.2 (A0), U4318.12 (Q4)
PCNTL.D1: U4313.5 (A1), U4318.15 (Q5)
PCNTL.D2: U4313.11 (A2), U4318.16 (Q6)
PCNTL.D3: U4313.14 (A3), U4318.19 (Q7)
PD: U4307.1 (OE), U4308.15 (OE), U4312.15 (E), U4313.15 (E), U4318.1 (OE), U4319.15 (OE)
PHYS_LAST: U4308.17 (A2)
PHYS_REF: U4320.3 (Q), U4321.1 (D0)
Q4~: U4318.11 (CLK)
RTV_NEXT: U4307.15 (Q5), U4309.1 (D0)
RTV_NEXT.D: U4308.19 (A0)
START_IF_INCM: U4308.12 (Y2)
START_TAG_RD: U4307.14 (D5), U4308.11 (Y3)
STATE0: U4318.2 (Q0), U4319.19 (A0)
STATE1: U4318.5 (Q1), U4319.18 (A1)
WRITE_LAST~: U4308.18 (A1)
WRITE_SCAV: U4319.8 (Y5)

Notes on the sheet:
MEM_CONTROL_CODES 0000 PHYSICAL_MEM_WRITE 0001 PHYSICAL_MEM_READ 0010 LOGICAL_MEM_WRITE 0011 LOGICAL_MEM_READ 0100 COPY 0 TO 1 * 0101 MEMORY_TO_TAGSTORE * 0110 COPY 1 to 0 * 0111 SET HIT FLIP FLOPS * 1000 PHYSICAL TAG WRITE 1001 PHYSICAL TAG READ 1010 INITIALIZE MRU 1011 LOGICAL TAG READ 1100 NAME 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
