Datamuseum-DK/R1000.HwDoc/Schematics/FIU/pg_43.kicad_sch

## KiCad design Schematics/FIU/pg_43.kicad_sch (2023-01-10)

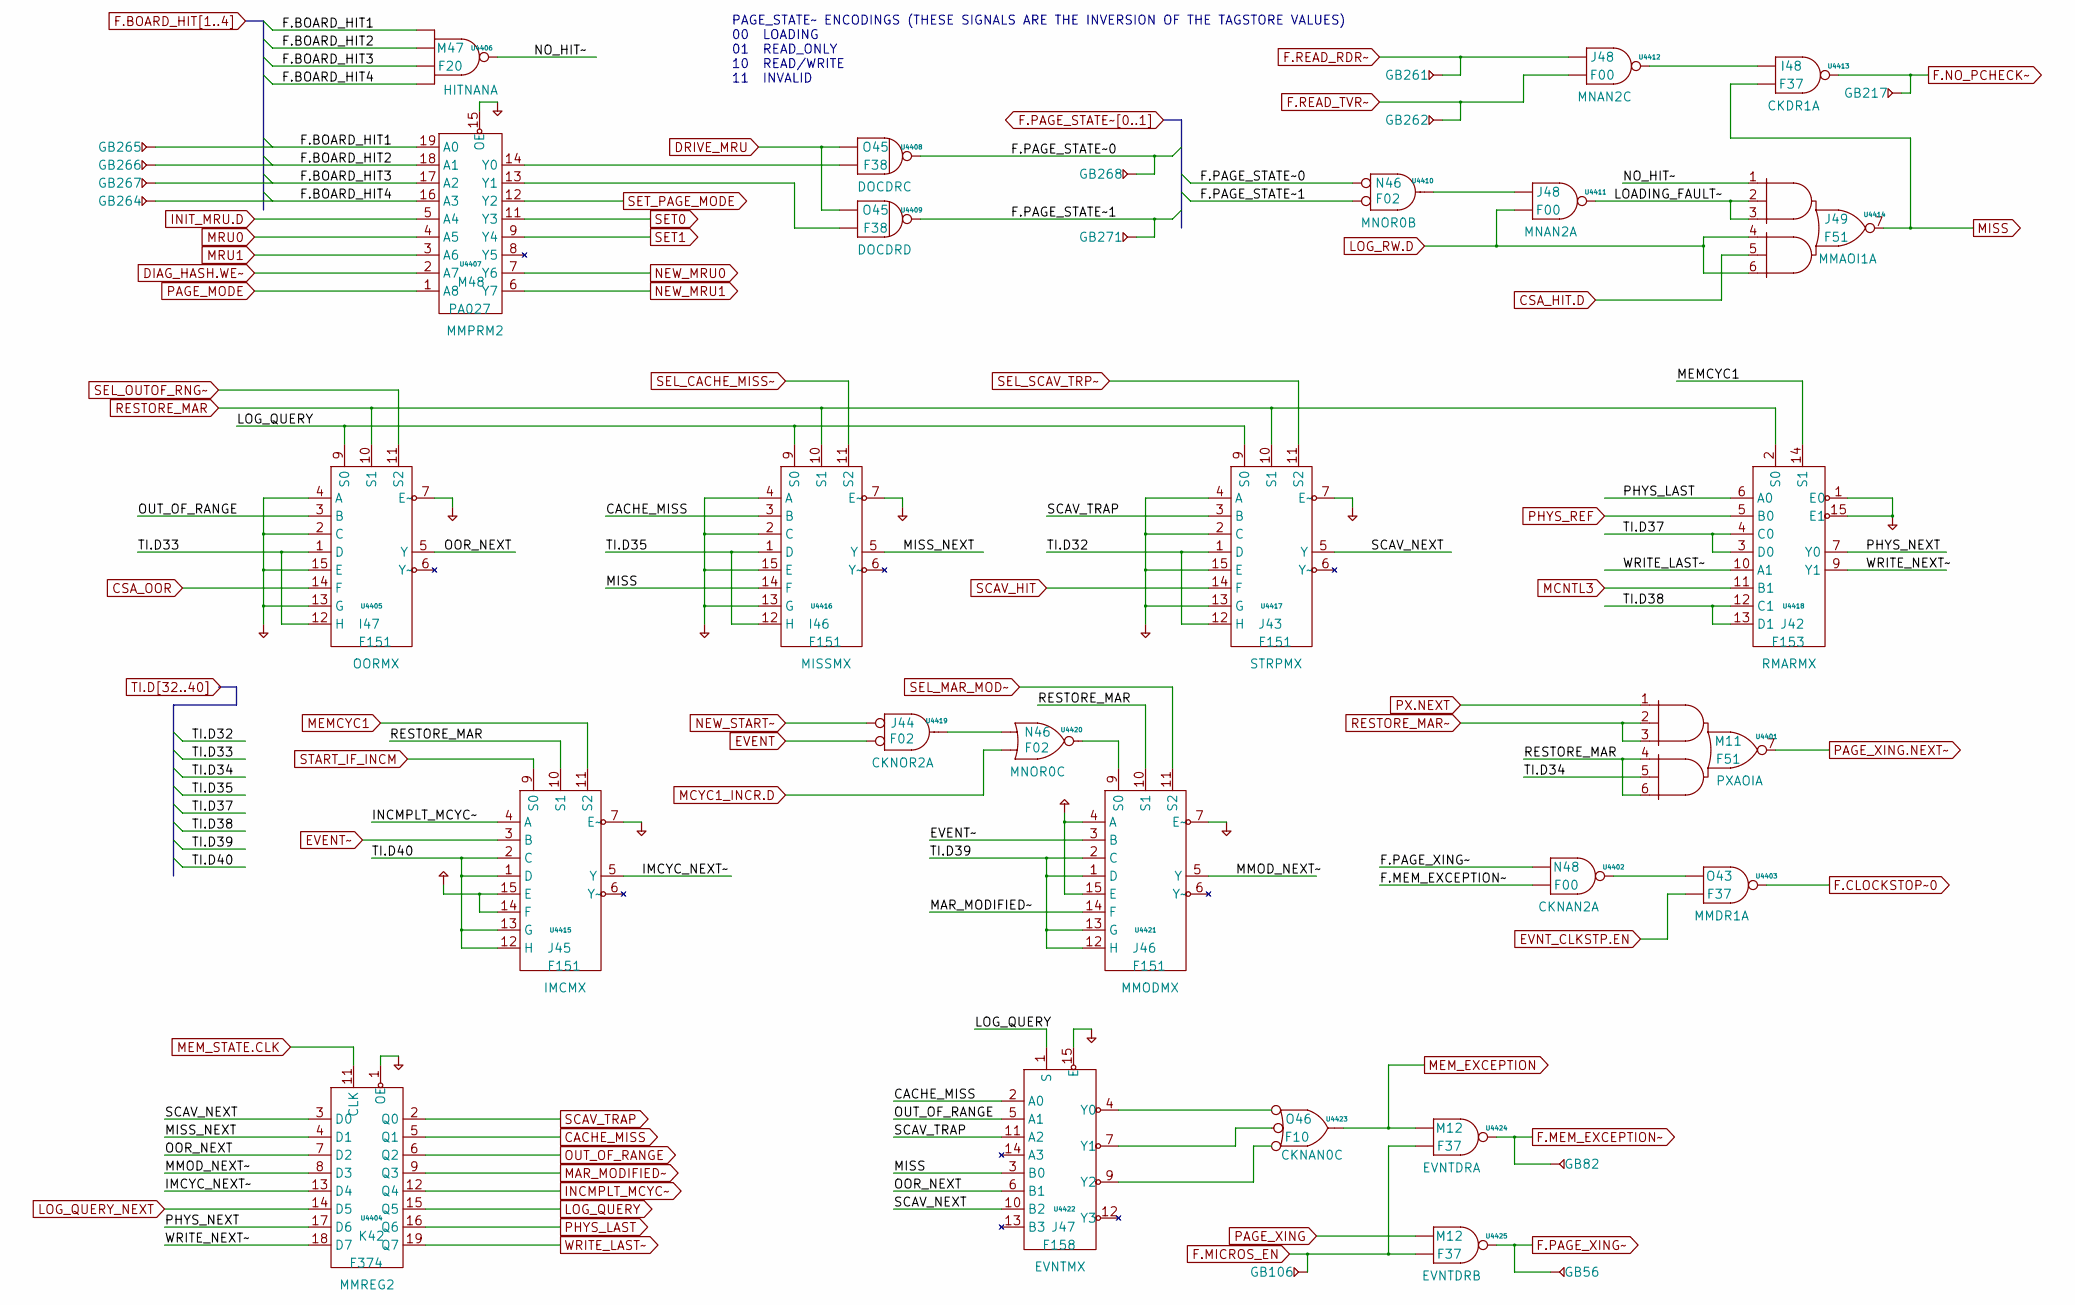
[picture p328: schematic pg_43.kicad_sch]

Parts:
GB56, GB82, GB106, GB217, GB261, GB262, GB264, GB265, GB266, GB267, GB268, GB271: GB
U4401, U4414: F51
U4402, U4411, U4412: F00
U4403, U4413, U4424, U4425: F37
U4404: F374
U4405, U4415, U4416, U4417, U4421: F151
U4406: F20
U4407: PA027
U4408, U4409: F38
U4410, U4419, U4420: F02
U4418: F153
U4422: F158
U4423: F10

Connections:
CACHE_MISS: U4404.5 (Q1), U4416.3 (B), U4422.2 (A0)
CSA_HIT.D: U4414.5 (B2)
CSA_OOR: U4405.14 (F)
DIAG_HASH.WE~: U4407.2 (A7)
DRIVE_MRU: U4408.1 (D0), U4409.1 (D0)
EVENT: U4419.2 (D1)
EVENT~: U4415.3 (B), U4421.3 (B)
EVNT_CLKSTP.EN: U4403.2 (D1)
F.BOARD_HIT1: GB265.1, U4406.1 (D0), U4407.19 (A0)
F.BOARD_HIT2: GB266.1, U4406.2 (D1), U4407.18 (A1)
F.BOARD_HIT3: GB267.1, U4406.4 (D2), U4407.17 (A2)
F.BOARD_HIT4: GB264.1, U4406.5 (D3), U4407.16 (A3)
F.CLOCKSTOP~0: U4403.3 (Q)
F.MEM_EXCEPTION~: GB82.1, U4402.2 (D1), U4424.3 (Q)
F.MICROS_EN: GB106.1, U4424.2 (D1), U4425.2 (D1)
F.NO_PCHECK~: GB217.1, U4413.3 (Q)
F.PAGE_STATE~0: GB268.1, U4408.3 (Q), U4410.1 (D0)
F.PAGE_STATE~1: GB271.1, U4409.3 (Q), U4410.2 (D1)
F.PAGE_XING~: GB56.1, U4402.1 (D0), U4425.3 (Q)
F.READ_RDR~: GB261.1, U4412.1 (D0)
F.READ_TVR~: GB262.1, U4412.2 (D1)
IMCYC_NEXT~: U4404.13 (D4), U4415.5 (Y)
INCMPLT_MCYC~: U4404.12 (Q4), U4415.4 (A)
INIT_MRU.D: U4407.5 (A4)
LOADING_FAULT~: U4411.3 (Q), U4414.2 (A2), U4414.3 (A3)
LOG_QUERY: U4404.15 (Q5), U4405.9 (S0), U4416.9 (S0), U4417.9 (S0), U4422.1 (S)
LOG_QUERY_NEXT: U4404.14 (D5)
LOG_RW.D: U4411.2 (D1), U4414.4 (B1), U4414.6 (B3)
MAR_MODIFIED~: U4404.9 (Q3), U4421.14 (F)
MCNTL3: U4418.11 (B1)
MCYC1_INCR.D: U4420.2 (D1)
MEMCYC1: U4415.11 (S2), U4418.14 (S1)
MEM_EXCEPTION: U4423.4 (Q), U4424.1 (D0)
MEM_STATE.CLK: U4404.11 (CLK)
MISS: U4413.2 (D1), U4414.7 (Q), U4416.14 (F), U4422.3 (B0)
MISS_NEXT: U4404.4 (D1), U4416.5 (Y)
MMOD_NEXT~: U4404.8 (D3), U4421.5 (Y)
MRU0: U4407.4 (A5)
MRU1: U4407.3 (A6)
NEW_MRU0: U4407.7 (Y6)
NEW_MRU1: U4407.6 (Y7)
NEW_START~: U4419.1 (D0)
NO_HIT~: U4406.6 (Q), U4414.1 (A1)
unnamed: U4402.3 (Q), U4403.1 (D0)
unnamed: U4407.13 (Y1), U4409.2 (D1)
unnamed: U4407.14 (Y0), U4408.2 (D1)
unnamed: U4410.3 (Q), U4411.1 (D0)
unnamed: U4412.3 (Q), U4413.1 (D0)
unnamed: U4419.3 (Q), U4420.1 (D0)
unnamed: U4420.3 (Q), U4421.9 (S0)
unnamed: U4422.4 (Y0), U4423.1 (D0)
unnamed: U4422.7 (Y1), U4423.2 (D1)
unnamed: U4422.9 (Y2), U4423.3 (D2)
OOR_NEXT: U4404.7 (D2), U4405.5 (Y), U4422.6 (B1)
OUT_OF_RANGE: U4404.6 (Q2), U4405.3 (B), U4422.5 (A1)
PAGE_MODE: U4407.1 (A8)
PAGE_XING: U4425.1 (D0)
PAGE_XING.NEXT~: U4401.7 (Q)
PD: U4404.1 (OE), U4405.2 (C), U4405.4 (A), U4405.7 (E~), U4405.13 (G), U4405.15 (E), U4407.15 (OE), U4415.7 (E~), U4416.2 (C), U4416.4 (A), U4416.7 (E~), U4416.13 (G), U4416.15 (E), U4417.2 (C), U4417.4 (A), U4417.7 (E~), U4417.13 (G), U4417.15 (E), U4418.1 (E0), U4418.15 (E1), U4421.7 (E~), U4422.15 (E)
PHYS_LAST: U4404.16 (Q6), U4418.6 (A0)
PHYS_NEXT: U4404.17 (D6), U4418.7 (Y0)
PHYS_REF: U4418.5 (B0)
PU: U4415.14 (F), U4415.15 (E), U4421.4 (A), U4421.15 (E)
PX.NEXT: U4401.1 (A1)
RESTORE_MAR: U4401.4 (B1), U4401.6 (B3), U4405.10 (S1), U4415.10 (S1), U4416.10 (S1), U4417.10 (S1), U4418.2 (S0), U4421.10 (S1)
RESTORE_MAR~: U4401.2 (A2), U4401.3 (A3)
SCAV_HIT: U4417.14 (F)
SCAV_NEXT: U4404.3 (D0), U4417.5 (Y), U4422.10 (B2)
SCAV_TRAP: U4404.2 (Q0), U4417.3 (B), U4422.11 (A2)
SEL_CACHE_MISS~: U4416.11 (S2)
SEL_MAR_MOD~: U4421.11 (S2)
SEL_OUTOF_RNG~: U4405.11 (S2)
SEL_SCAV_TRP~: U4417.11 (S2)
SET0: U4407.11 (Y3)
SET1: U4407.9 (Y4)
SET_PAGE_MODE: U4407.12 (Y2)
START_IF_INCM: U4415.9 (S0)
TI.D32: U4417.1 (D), U4417.12 (H)
TI.D33: U4405.1 (D), U4405.12 (H)
TI.D34: U4401.5 (B2)
TI.D35: U4416.1 (D), U4416.12 (H)
TI.D37: U4418.3 (D0), U4418.4 (C0)
TI.D38: U4418.12 (C1), U4418.13 (D1)
TI.D39: U4421.1 (D), U4421.2 (C), U4421.12 (H), U4421.13 (G)
TI.D40: U4415.1 (D), U4415.2 (C), U4415.12 (H), U4415.13 (G)
WRITE_LAST~: U4404.19 (Q7), U4418.10 (A1)
WRITE_NEXT~: U4404.18 (D7), U4418.9 (Y1)

Notes on the sheet:
PAGE_STATE~ ENCODINGS (THESE SIGNALS ARE THE INVERSION OF THE TAGSTORE VALUES) 00 LOADING 01 READ_ONLY 10 READ/WRITE 11 INVALID
