Datamuseum-DK/R1000.HwDoc/Schematics/FIU/pg_44.kicad_sch

## KiCad design Schematics/FIU/pg_44.kicad_sch (2023-01-10)

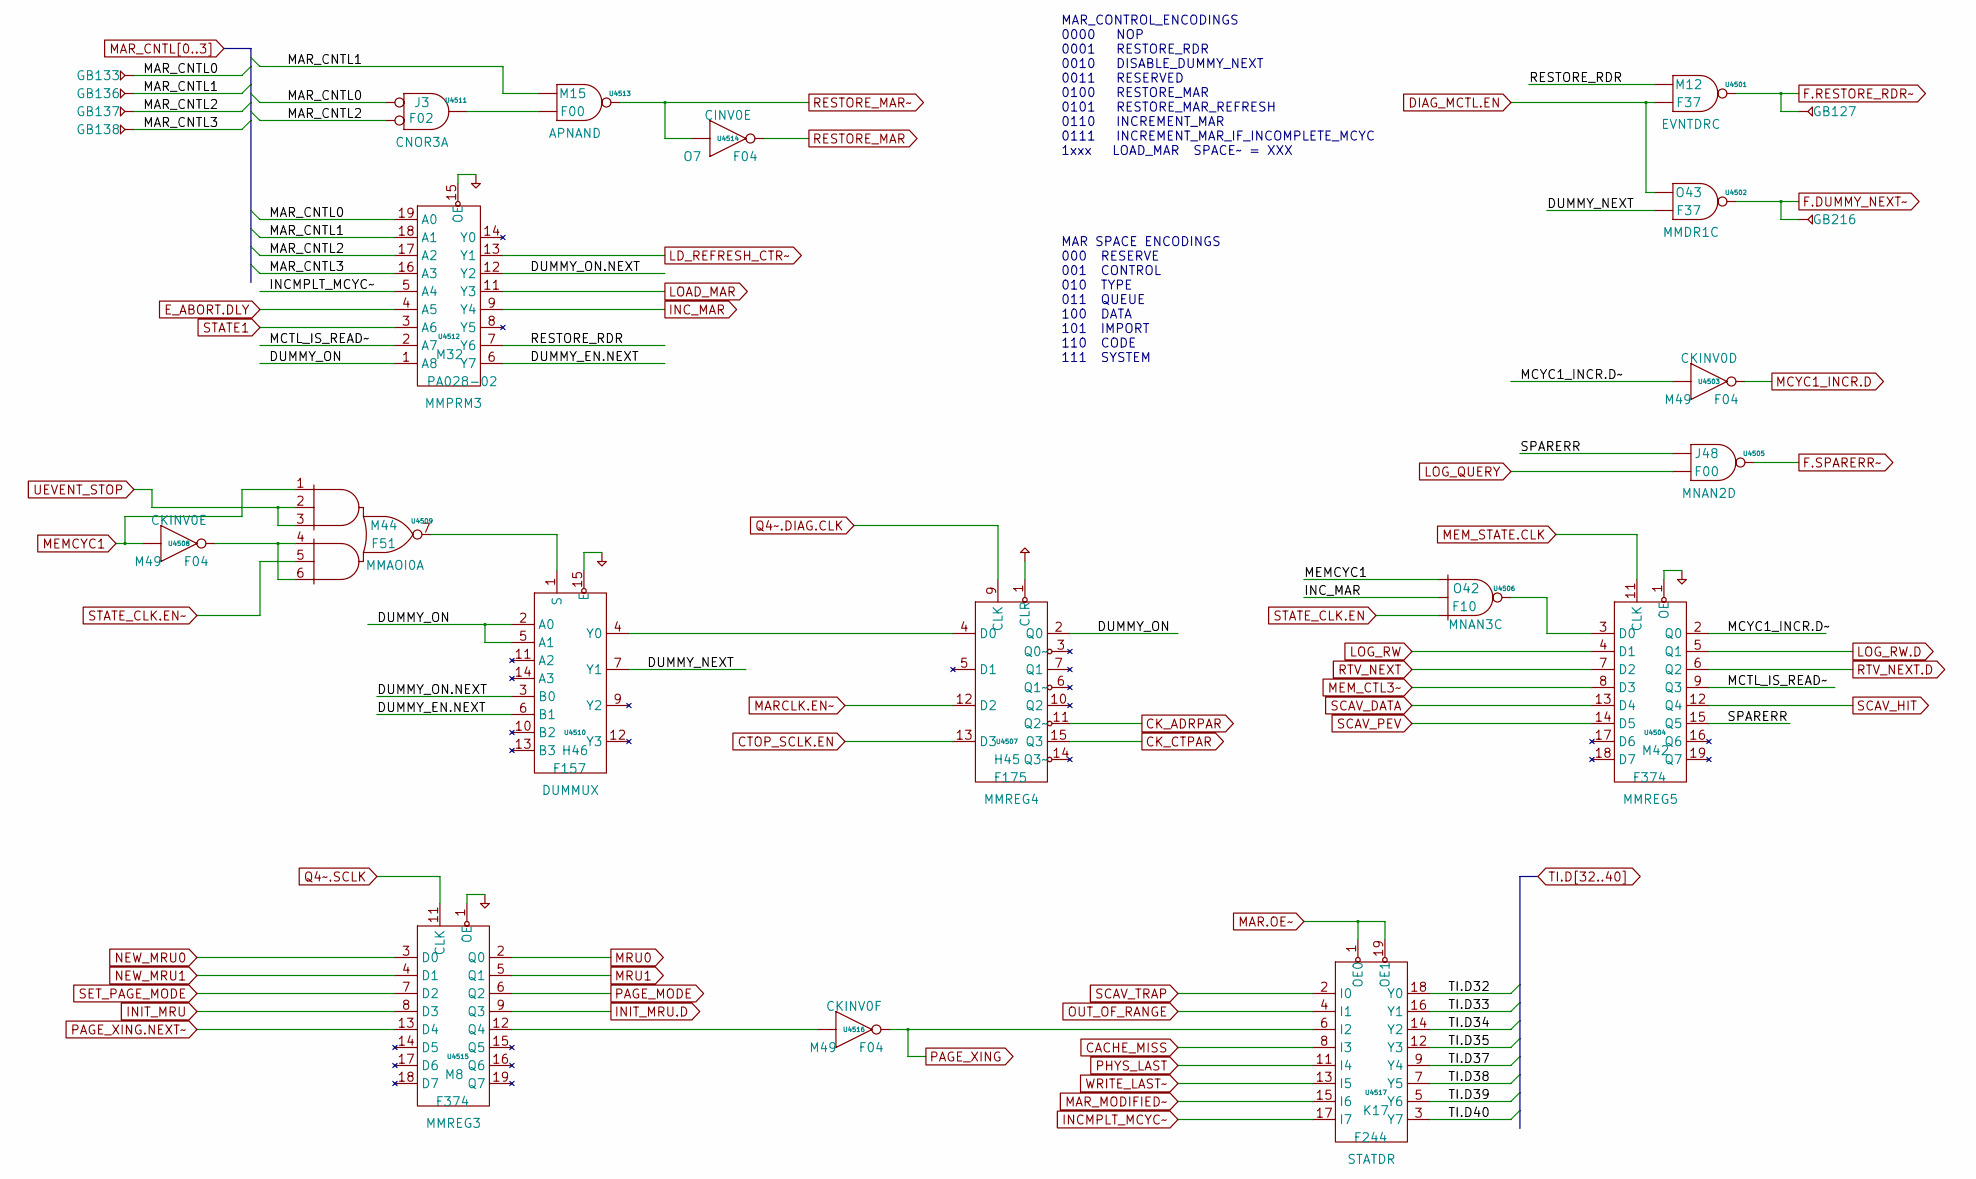
[picture p329: schematic pg_44.kicad_sch]

Parts:
GB127, GB133, GB136, GB137, GB138, GB216: GB
U4501, U4502: F37
U4503, U4508, U4514, U4516: F04
U4504, U4515: F374
U4505, U4513: F00
U4506: F10
U4507: F175
U4509: F51
U4510: F157
U4511: F02
U4512: PA028-02
U4517: F244

Connections:
CACHE_MISS: U4517.8 (I3)
CK_ADRPAR: U4507.11 (Q2~)
CK_CTPAR: U4507.15 (Q3)
CTOP_SCLK.EN: U4507.13 (D3)
DIAG_MCTL.EN: U4501.2 (D1), U4502.1 (D0)
DUMMY_EN.NEXT: U4510.6 (B1), U4512.6 (Y7)
DUMMY_NEXT: U4502.2 (D1), U4510.7 (Y1)
DUMMY_ON: U4507.2 (Q0), U4510.2 (A0), U4510.5 (A1), U4512.1 (A8)
DUMMY_ON.NEXT: U4510.3 (B0), U4512.12 (Y2)
E_ABORT.DLY: U4512.4 (A5)
F.DUMMY_NEXT~: GB216.1, U4502.3 (Q)
F.RESTORE_RDR~: GB127.1, U4501.3 (Q)
F.SPARERR~: U4505.3 (Q)
INCMPLT_MCYC~: U4512.5 (A4), U4517.17 (I7)
INC_MAR: U4506.2 (D1), U4512.9 (Y4)
INIT_MRU: U4515.8 (D3)
INIT_MRU.D: U4515.9 (Q3)
LD_REFRESH_CTR~: U4512.13 (Y1)
LOAD_MAR: U4512.11 (Y3)
LOG_QUERY: U4505.2 (D1)
LOG_RW: U4504.4 (D1)
LOG_RW.D: U4504.5 (Q1)
MAR.OE~: U4517.1 (OE0), U4517.19 (OE1)
MARCLK.EN~: U4507.12 (D2)
MAR_CNTL0: GB133.1, U4511.1 (D0), U4512.19 (A0)
MAR_CNTL1: GB136.1, U4512.18 (A1), U4513.1 (D0)
MAR_CNTL2: GB137.1, U4511.2 (D1), U4512.17 (A2)
MAR_CNTL3: GB138.1, U4512.16 (A3)
MAR_MODIFIED~: U4517.15 (I6)
MCTL_IS_READ~: U4504.9 (Q3), U4512.2 (A7)
MCYC1_INCR.D: U4503.2 (Q)
MCYC1_INCR.D~: U4503.1 (D0), U4504.2 (Q0)
MEMCYC1: U4506.1 (D0), U4508.1 (D0), U4509.1 (A1)
MEM_CTL3~: U4504.8 (D3)
MEM_STATE.CLK: U4504.11 (CLK)
MRU0: U4515.2 (Q0)
MRU1: U4515.5 (Q1)
NEW_MRU0: U4515.3 (D0)
NEW_MRU1: U4515.4 (D1)
unnamed: U4504.3 (D0), U4506.4 (Q)
unnamed: U4507.4 (D0), U4510.4 (Y0)
unnamed: U4508.2 (Q), U4509.4 (B1), U4509.6 (B3)
unnamed: U4509.7 (Q), U4510.1 (S)
unnamed: U4511.3 (Q), U4513.2 (D1)
unnamed: U4515.12 (Q4), U4516.1 (D0)
OUT_OF_RANGE: U4517.4 (I1)
PAGE_MODE: U4515.6 (Q2)
PAGE_XING: U4516.2 (Q), U4517.6 (I2)
PAGE_XING.NEXT~: U4515.13 (D4)
PD: U4504.1 (OE), U4510.15 (E), U4512.15 (OE), U4515.1 (OE)
PHYS_LAST: U4517.11 (I4)
PU: U4507.1 (CLR)
Q4~.DIAG.CLK: U4507.9 (CLK)
Q4~.SCLK: U4515.11 (CLK)
RESTORE_MAR: U4514.2 (Q)
RESTORE_MAR~: U4513.3 (Q), U4514.1 (D0)
RESTORE_RDR: U4501.1 (D0), U4512.7 (Y6)
RTV_NEXT: U4504.7 (D2)
RTV_NEXT.D: U4504.6 (Q2)
SCAV_DATA: U4504.13 (D4)
SCAV_HIT: U4504.12 (Q4)
SCAV_PEV: U4504.14 (D5)
SCAV_TRAP: U4517.2 (I0)
SET_PAGE_MODE: U4515.7 (D2)
SPARERR: U4504.15 (Q5), U4505.1 (D0)
STATE1: U4512.3 (A6)
STATE_CLK.EN: U4506.3 (D2)
STATE_CLK.EN~: U4509.5 (B2)
TI.D32: U4517.18 (Y0)
TI.D33: U4517.16 (Y1)
TI.D34: U4517.14 (Y2)
TI.D35: U4517.12 (Y3)
TI.D37: U4517.9 (Y4)
TI.D38: U4517.7 (Y5)
TI.D39: U4517.5 (Y6)
TI.D40: U4517.3 (Y7)
UEVENT_STOP: U4509.2 (A2), U4509.3 (A3)
WRITE_LAST~: U4517.13 (I5)

Notes on the sheet:
MAR_CONTROL_ENCODINGS 0000 NOP 0001 RESTORE_RDR 0010 DISABLE_DUMMY_NEXT 0011 RESERVED 0100 RESTORE_MAR 0101 RESTORE_MAR_REFRESH 0110 INCREMENT_MAR 0111 INCREMENT_MAR_IF_INCOMPLETE_MCYC 1xxx LOAD_MAR SPACE~ = XXX
MAR SPACE ENCODINGS 000 RESERVE 001 CONTROL 010 TYPE 011 QUEUE 100 DATA 101 IMPORT 110 CODE 111 SYSTEM
