Datamuseum-DK/R1000.HwDoc/Schematics/FIU/pg_46.kicad_sch

## KiCad design Schematics/FIU/pg_46.kicad_sch (2023-01-10)

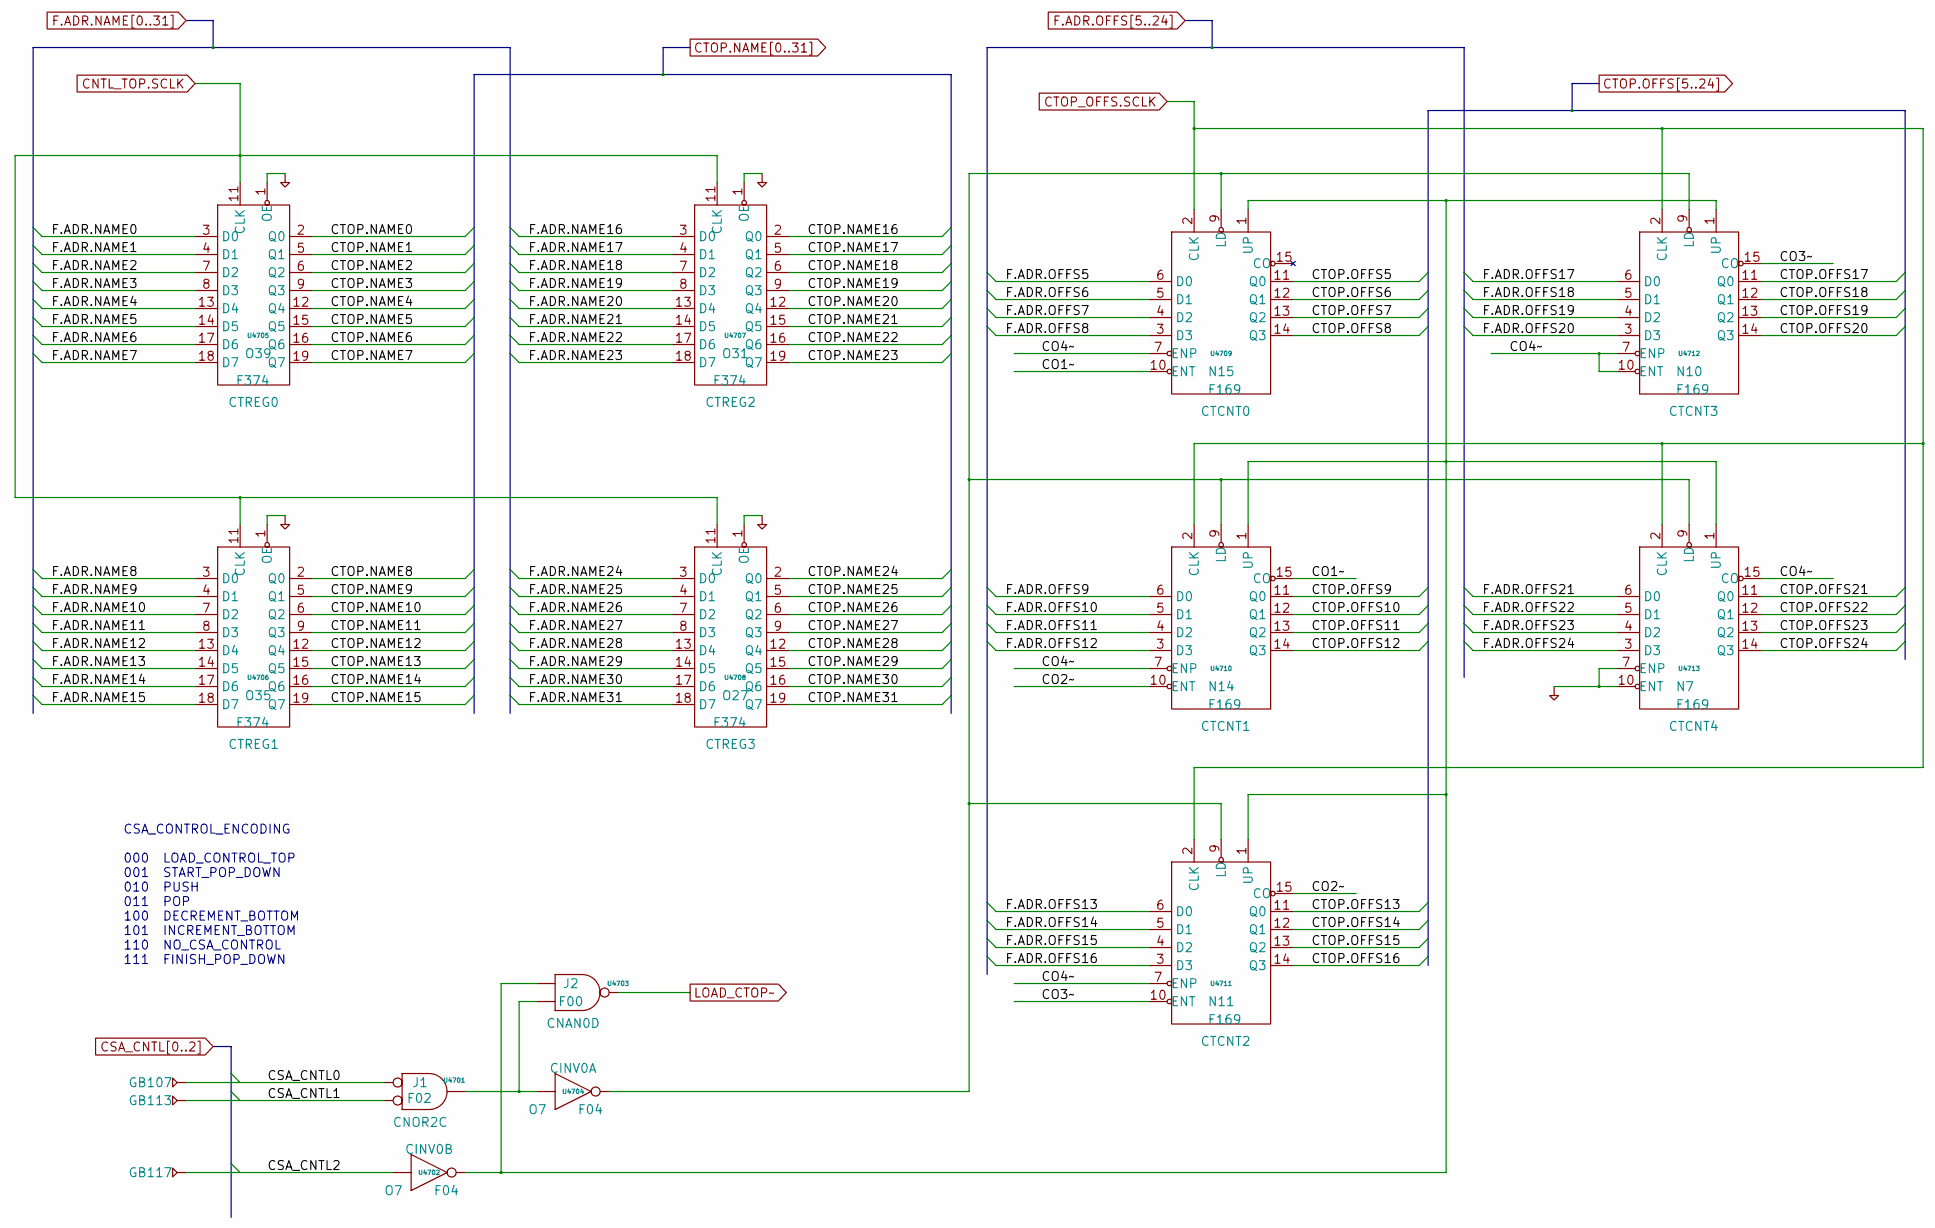
[picture p330: schematic pg_46.kicad_sch]

Parts:
GB107, GB113, GB117: GB
U4701: F02
U4702, U4704: F04
U4703: F00
U4705, U4706, U4707, U4708: F374
U4709, U4710, U4711, U4712, U4713: F169

Connections:
CNTL_TOP.SCLK: U4705.11 (CLK), U4706.11 (CLK), U4707.11 (CLK), U4708.11 (CLK)
CO1~: U4709.10 (ENT), U4710.15 (CO)
CO2~: U4710.10 (ENT), U4711.15 (CO)
CO3~: U4711.10 (ENT), U4712.15 (CO)
CO4~: U4709.7 (ENP), U4710.7 (ENP), U4711.7 (ENP), U4712.7 (ENP), U4712.10 (ENT), U4713.15 (CO)
CSA_CNTL0: GB107.1, U4701.1 (D0)
CSA_CNTL1: GB113.1, U4701.2 (D1)
CSA_CNTL2: GB117.1, U4702.1 (D0)
CTOP.NAME0: U4705.2 (Q0)
CTOP.NAME1: U4705.5 (Q1)
CTOP.NAME2: U4705.6 (Q2)
CTOP.NAME3: U4705.9 (Q3)
CTOP.NAME4: U4705.12 (Q4)
CTOP.NAME5: U4705.15 (Q5)
CTOP.NAME6: U4705.16 (Q6)
CTOP.NAME7: U4705.19 (Q7)
CTOP.NAME8: U4706.2 (Q0)
CTOP.NAME9: U4706.5 (Q1)
CTOP.NAME10: U4706.6 (Q2)
CTOP.NAME11: U4706.9 (Q3)
CTOP.NAME12: U4706.12 (Q4)
CTOP.NAME13: U4706.15 (Q5)
CTOP.NAME14: U4706.16 (Q6)
CTOP.NAME15: U4706.19 (Q7)
CTOP.NAME16: U4707.2 (Q0)
CTOP.NAME17: U4707.5 (Q1)
CTOP.NAME18: U4707.6 (Q2)
CTOP.NAME19: U4707.9 (Q3)
CTOP.NAME20: U4707.12 (Q4)
CTOP.NAME21: U4707.15 (Q5)
CTOP.NAME22: U4707.16 (Q6)
CTOP.NAME23: U4707.19 (Q7)
CTOP.NAME24: U4708.2 (Q0)
CTOP.NAME25: U4708.5 (Q1)
CTOP.NAME26: U4708.6 (Q2)
CTOP.NAME27: U4708.9 (Q3)
CTOP.NAME28: U4708.12 (Q4)
CTOP.NAME29: U4708.15 (Q5)
CTOP.NAME30: U4708.16 (Q6)
CTOP.NAME31: U4708.19 (Q7)
CTOP.OFFS5: U4709.11 (Q0)
CTOP.OFFS6: U4709.12 (Q1)
CTOP.OFFS7: U4709.13 (Q2)
CTOP.OFFS8: U4709.14 (Q3)
CTOP.OFFS9: U4710.11 (Q0)
CTOP.OFFS10: U4710.12 (Q1)
CTOP.OFFS11: U4710.13 (Q2)
CTOP.OFFS12: U4710.14 (Q3)
CTOP.OFFS13: U4711.11 (Q0)
CTOP.OFFS14: U4711.12 (Q1)
CTOP.OFFS15: U4711.13 (Q2)
CTOP.OFFS16: U4711.14 (Q3)
CTOP.OFFS17: U4712.11 (Q0)
CTOP.OFFS18: U4712.12 (Q1)
CTOP.OFFS19: U4712.13 (Q2)
CTOP.OFFS20: U4712.14 (Q3)
CTOP.OFFS21: U4713.11 (Q0)
CTOP.OFFS22: U4713.12 (Q1)
CTOP.OFFS23: U4713.13 (Q2)
CTOP.OFFS24: U4713.14 (Q3)
CTOP_OFFS.SCLK: U4709.2 (CLK), U4710.2 (CLK), U4711.2 (CLK), U4712.2 (CLK), U4713.2 (CLK)
F.ADR.NAME0: U4705.3 (D0)
F.ADR.NAME1: U4705.4 (D1)
F.ADR.NAME2: U4705.7 (D2)
F.ADR.NAME3: U4705.8 (D3)
F.ADR.NAME4: U4705.13 (D4)
F.ADR.NAME5: U4705.14 (D5)
F.ADR.NAME6: U4705.17 (D6)
F.ADR.NAME7: U4705.18 (D7)
F.ADR.NAME8: U4706.3 (D0)
F.ADR.NAME9: U4706.4 (D1)
F.ADR.NAME10: U4706.7 (D2)
F.ADR.NAME11: U4706.8 (D3)
F.ADR.NAME12: U4706.13 (D4)
F.ADR.NAME13: U4706.14 (D5)
F.ADR.NAME14: U4706.17 (D6)
F.ADR.NAME15: U4706.18 (D7)
F.ADR.NAME16: U4707.3 (D0)
F.ADR.NAME17: U4707.4 (D1)
F.ADR.NAME18: U4707.7 (D2)
F.ADR.NAME19: U4707.8 (D3)
F.ADR.NAME20: U4707.13 (D4)
F.ADR.NAME21: U4707.14 (D5)
F.ADR.NAME22: U4707.17 (D6)
F.ADR.NAME23: U4707.18 (D7)
F.ADR.NAME24: U4708.3 (D0)
F.ADR.NAME25: U4708.4 (D1)
F.ADR.NAME26: U4708.7 (D2)
F.ADR.NAME27: U4708.8 (D3)
F.ADR.NAME28: U4708.13 (D4)
F.ADR.NAME29: U4708.14 (D5)
F.ADR.NAME30: U4708.17 (D6)
F.ADR.NAME31: U4708.18 (D7)
F.ADR.OFFS5: U4709.6 (D0)
F.ADR.OFFS6: U4709.5 (D1)
F.ADR.OFFS7: U4709.4 (D2)
F.ADR.OFFS8: U4709.3 (D3)
F.ADR.OFFS9: U4710.6 (D0)
F.ADR.OFFS10: U4710.5 (D1)
F.ADR.OFFS11: U4710.4 (D2)
F.ADR.OFFS12: U4710.3 (D3)
F.ADR.OFFS13: U4711.6 (D0)
F.ADR.OFFS14: U4711.5 (D1)
F.ADR.OFFS15: U4711.4 (D2)
F.ADR.OFFS16: U4711.3 (D3)
F.ADR.OFFS17: U4712.6 (D0)
F.ADR.OFFS18: U4712.5 (D1)
F.ADR.OFFS19: U4712.4 (D2)
F.ADR.OFFS20: U4712.3 (D3)
F.ADR.OFFS21: U4713.6 (D0)
F.ADR.OFFS22: U4713.5 (D1)
F.ADR.OFFS23: U4713.4 (D2)
F.ADR.OFFS24: U4713.3 (D3)
LOAD_CTOP~: U4703.3 (Q)
unnamed: U4701.3 (Q), U4703.2 (D1), U4704.1 (D0)
unnamed: U4702.2 (Q), U4703.1 (D0), U4709.1 (UP), U4710.1 (UP), U4711.1 (UP), U4712.1 (UP), U4713.1 (UP)
unnamed: U4704.2 (Q), U4709.9 (LD), U4710.9 (LD), U4711.9 (LD), U4712.9 (LD), U4713.9 (LD)
PD: U4705.1 (OE), U4706.1 (OE), U4707.1 (OE), U4708.1 (OE), U4713.7 (ENP), U4713.10 (ENT)

Notes on the sheet:
CSA_CONTROL_ENCODING 000 LOAD_CONTROL_TOP 001 START_POP_DOWN 010 PUSH 011 POP 100 DECREMENT_BOTTOM 101 INCREMENT_BOTTOM 110 NO_CSA_CONTROL 111 FINISH_POP_DOWN
