Datamuseum-DK/R1000.HwDoc/Schematics/FIU/pg_47.kicad_sch

## KiCad design Schematics/FIU/pg_47.kicad_sch (2023-01-10)

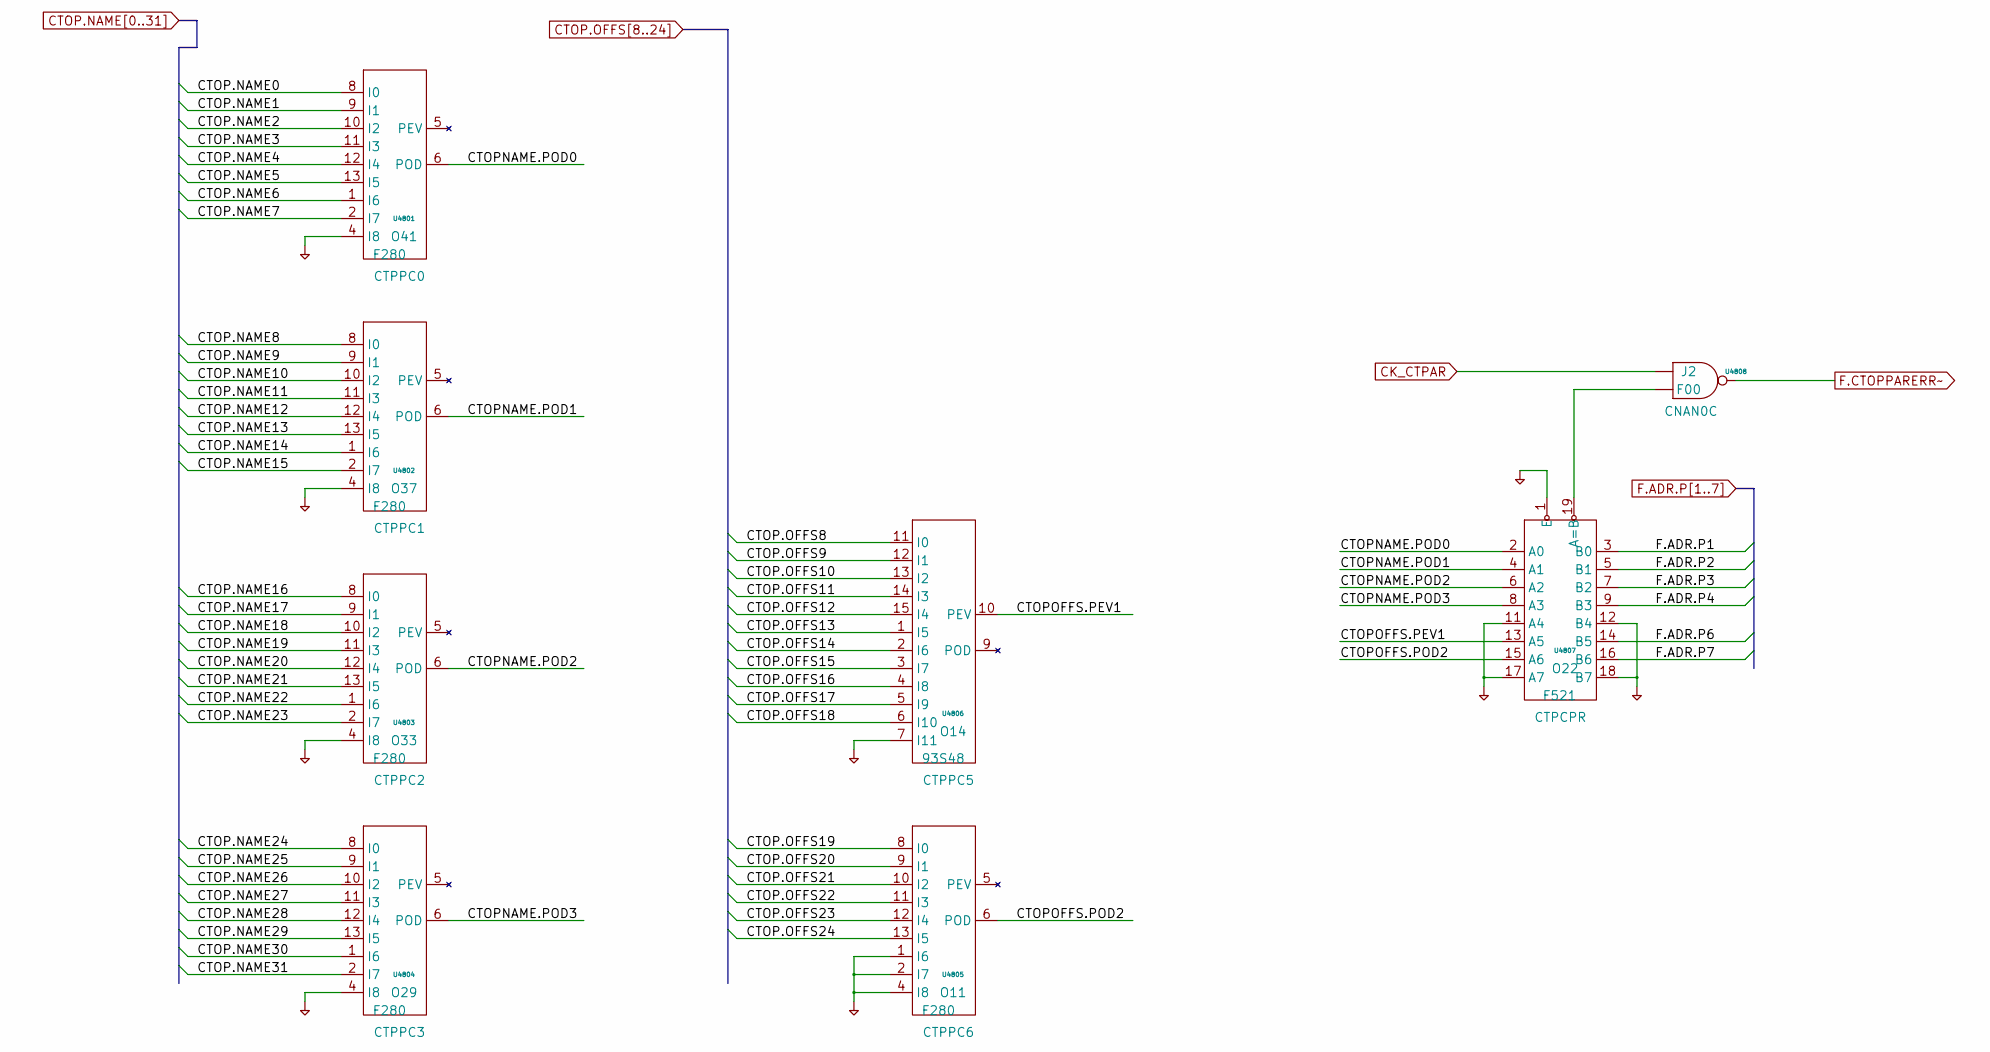
[picture p331: schematic pg_47.kicad_sch]

Parts:
U4801, U4802, U4803, U4804, U4805: F280
U4806: 93S48
U4807: F521
U4808: F00

Connections:
CK_CTPAR: U4808.1 (D0)
CTOP.NAME0: U4801.8 (I0)
CTOP.NAME1: U4801.9 (I1)
CTOP.NAME2: U4801.10 (I2)
CTOP.NAME3: U4801.11 (I3)
CTOP.NAME4: U4801.12 (I4)
CTOP.NAME5: U4801.13 (I5)
CTOP.NAME6: U4801.1 (I6)
CTOP.NAME7: U4801.2 (I7)
CTOP.NAME8: U4802.8 (I0)
CTOP.NAME9: U4802.9 (I1)
CTOP.NAME10: U4802.10 (I2)
CTOP.NAME11: U4802.11 (I3)
CTOP.NAME12: U4802.12 (I4)
CTOP.NAME13: U4802.13 (I5)
CTOP.NAME14: U4802.1 (I6)
CTOP.NAME15: U4802.2 (I7)
CTOP.NAME16: U4803.8 (I0)
CTOP.NAME17: U4803.9 (I1)
CTOP.NAME18: U4803.10 (I2)
CTOP.NAME19: U4803.11 (I3)
CTOP.NAME20: U4803.12 (I4)
CTOP.NAME21: U4803.13 (I5)
CTOP.NAME22: U4803.1 (I6)
CTOP.NAME23: U4803.2 (I7)
CTOP.NAME24: U4804.8 (I0)
CTOP.NAME25: U4804.9 (I1)
CTOP.NAME26: U4804.10 (I2)
CTOP.NAME27: U4804.11 (I3)
CTOP.NAME28: U4804.12 (I4)
CTOP.NAME29: U4804.13 (I5)
CTOP.NAME30: U4804.1 (I6)
CTOP.NAME31: U4804.2 (I7)
CTOP.OFFS8: U4806.11 (I0)
CTOP.OFFS9: U4806.12 (I1)
CTOP.OFFS10: U4806.13 (I2)
CTOP.OFFS11: U4806.14 (I3)
CTOP.OFFS12: U4806.15 (I4)
CTOP.OFFS13: U4806.1 (I5)
CTOP.OFFS14: U4806.2 (I6)
CTOP.OFFS15: U4806.3 (I7)
CTOP.OFFS16: U4806.4 (I8)
CTOP.OFFS17: U4806.5 (I9)
CTOP.OFFS18: U4806.6 (I10)
CTOP.OFFS19: U4805.8 (I0)
CTOP.OFFS20: U4805.9 (I1)
CTOP.OFFS21: U4805.10 (I2)
CTOP.OFFS22: U4805.11 (I3)
CTOP.OFFS23: U4805.12 (I4)
CTOP.OFFS24: U4805.13 (I5)
CTOPNAME.POD0: U4801.6 (POD), U4807.2 (A0)
CTOPNAME.POD1: U4802.6 (POD), U4807.4 (A1)
CTOPNAME.POD2: U4803.6 (POD), U4807.6 (A2)
CTOPNAME.POD3: U4804.6 (POD), U4807.8 (A3)
CTOPOFFS.PEV1: U4806.10 (PEV), U4807.13 (A5)
CTOPOFFS.POD2: U4805.6 (POD), U4807.15 (A6)
F.ADR.P1: U4807.3 (B0)
F.ADR.P2: U4807.5 (B1)
F.ADR.P3: U4807.7 (B2)
F.ADR.P4: U4807.9 (B3)
F.ADR.P6: U4807.14 (B5)
F.ADR.P7: U4807.16 (B6)
F.CTOPPARERR~: U4808.3 (Q)
unnamed: U4807.19 (A=B), U4808.2 (D1)
PD: U4801.4 (I8), U4802.4 (I8), U4803.4 (I8), U4804.4 (I8), U4805.1 (I6), U4805.2 (I7), U4805.4 (I8), U4806.7 (I11), U4807.1 (E), U4807.11 (A4), U4807.12 (B4), U4807.17 (A7), U4807.18 (B7)
