Datamuseum-DK/R1000.HwDoc/Schematics/FIU/pg_48.kicad_sch

## KiCad design Schematics/FIU/pg_48.kicad_sch (2023-01-10)

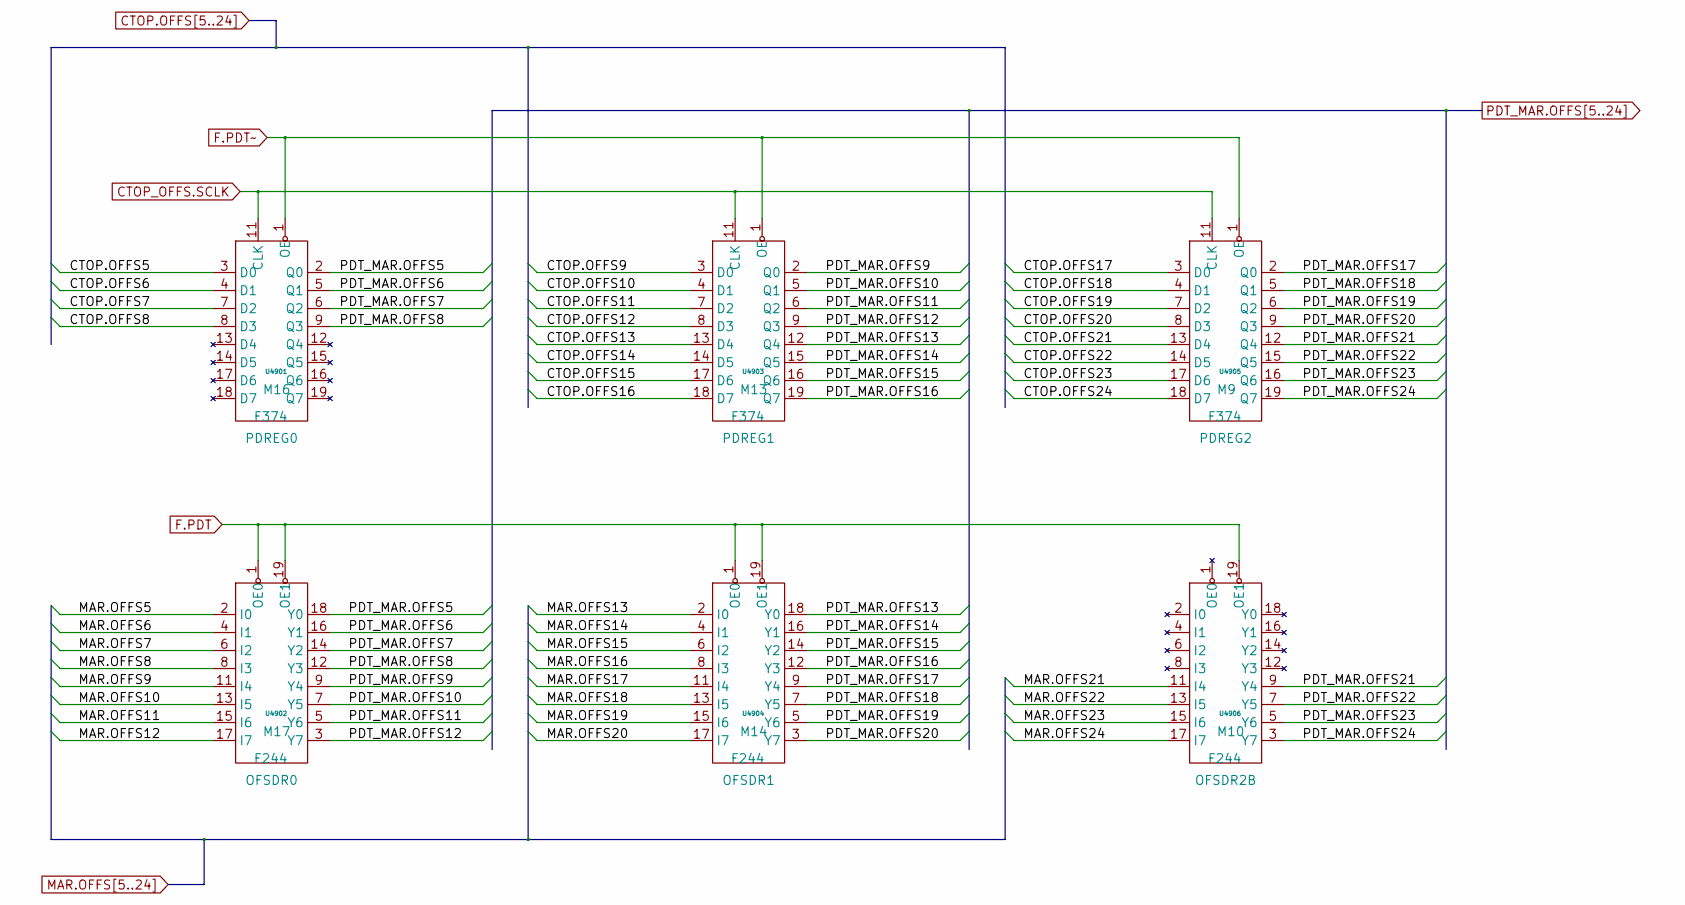
[picture p332: schematic pg_48.kicad_sch]

Parts:
U4901, U4903, U4905: F374
U4902, U4904, U4906: F244

Connections:
CTOP.OFFS5: U4901.3 (D0)
CTOP.OFFS6: U4901.4 (D1)
CTOP.OFFS7: U4901.7 (D2)
CTOP.OFFS8: U4901.8 (D3)
CTOP.OFFS9: U4903.3 (D0)
CTOP.OFFS10: U4903.4 (D1)
CTOP.OFFS11: U4903.7 (D2)
CTOP.OFFS12: U4903.8 (D3)
CTOP.OFFS13: U4903.13 (D4)
CTOP.OFFS14: U4903.14 (D5)
CTOP.OFFS15: U4903.17 (D6)
CTOP.OFFS16: U4903.18 (D7)
CTOP.OFFS17: U4905.3 (D0)
CTOP.OFFS18: U4905.4 (D1)
CTOP.OFFS19: U4905.7 (D2)
CTOP.OFFS20: U4905.8 (D3)
CTOP.OFFS21: U4905.13 (D4)
CTOP.OFFS22: U4905.14 (D5)
CTOP.OFFS23: U4905.17 (D6)
CTOP.OFFS24: U4905.18 (D7)
CTOP_OFFS.SCLK: U4901.11 (CLK), U4903.11 (CLK), U4905.11 (CLK)
F.PDT: U4902.1 (OE0), U4902.19 (OE1), U4904.1 (OE0), U4904.19 (OE1), U4906.19 (OE1)
F.PDT~: U4901.1 (OE), U4903.1 (OE), U4905.1 (OE)
MAR.OFFS5: U4902.2 (I0)
MAR.OFFS6: U4902.4 (I1)
MAR.OFFS7: U4902.6 (I2)
MAR.OFFS8: U4902.8 (I3)
MAR.OFFS9: U4902.11 (I4)
MAR.OFFS10: U4902.13 (I5)
MAR.OFFS11: U4902.15 (I6)
MAR.OFFS12: U4902.17 (I7)
MAR.OFFS13: U4904.2 (I0)
MAR.OFFS14: U4904.4 (I1)
MAR.OFFS15: U4904.6 (I2)
MAR.OFFS16: U4904.8 (I3)
MAR.OFFS17: U4904.11 (I4)
MAR.OFFS18: U4904.13 (I5)
MAR.OFFS19: U4904.15 (I6)
MAR.OFFS20: U4904.17 (I7)
MAR.OFFS21: U4906.11 (I4)
MAR.OFFS22: U4906.13 (I5)
MAR.OFFS23: U4906.15 (I6)
MAR.OFFS24: U4906.17 (I7)
PDT_MAR.OFFS5: U4901.2 (Q0), U4902.18 (Y0)
PDT_MAR.OFFS6: U4901.5 (Q1), U4902.16 (Y1)
PDT_MAR.OFFS7: U4901.6 (Q2), U4902.14 (Y2)
PDT_MAR.OFFS8: U4901.9 (Q3), U4902.12 (Y3)
PDT_MAR.OFFS9: U4902.9 (Y4), U4903.2 (Q0)
PDT_MAR.OFFS10: U4902.7 (Y5), U4903.5 (Q1)
PDT_MAR.OFFS11: U4902.5 (Y6), U4903.6 (Q2)
PDT_MAR.OFFS12: U4902.3 (Y7), U4903.9 (Q3)
PDT_MAR.OFFS13: U4903.12 (Q4), U4904.18 (Y0)
PDT_MAR.OFFS14: U4903.15 (Q5), U4904.16 (Y1)
PDT_MAR.OFFS15: U4903.16 (Q6), U4904.14 (Y2)
PDT_MAR.OFFS16: U4903.19 (Q7), U4904.12 (Y3)
PDT_MAR.OFFS17: U4904.9 (Y4), U4905.2 (Q0)
PDT_MAR.OFFS18: U4904.7 (Y5), U4905.5 (Q1)
PDT_MAR.OFFS19: U4904.5 (Y6), U4905.6 (Q2)
PDT_MAR.OFFS20: U4904.3 (Y7), U4905.9 (Q3)
PDT_MAR.OFFS21: U4905.12 (Q4), U4906.9 (Y4)
PDT_MAR.OFFS22: U4905.15 (Q5), U4906.7 (Y5)
PDT_MAR.OFFS23: U4905.16 (Q6), U4906.5 (Y6)
PDT_MAR.OFFS24: U4905.19 (Q7), U4906.3 (Y7)
