Datamuseum-DK/R1000.HwDoc/Schematics/FIU/pg_49.kicad_sch

## KiCad design Schematics/FIU/pg_49.kicad_sch (2023-01-10)

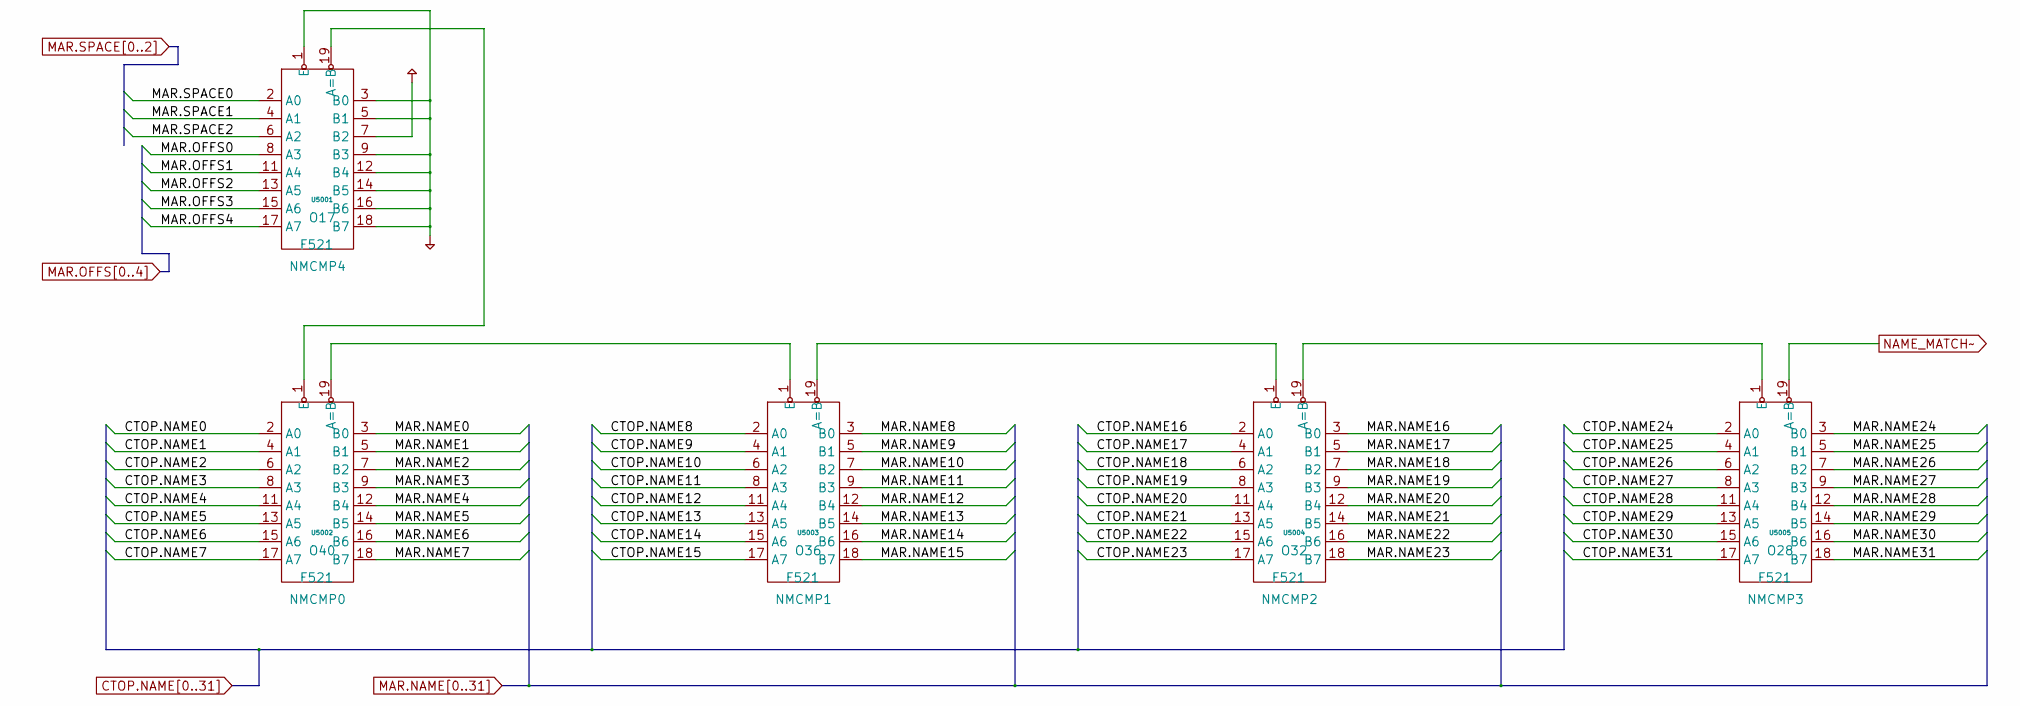
[picture p333: schematic pg_49.kicad_sch]

Parts:
U5001, U5002, U5003, U5004, U5005: F521

Connections:
CTOP.NAME0: U5002.2 (A0)
CTOP.NAME1: U5002.4 (A1)
CTOP.NAME2: U5002.6 (A2)
CTOP.NAME3: U5002.8 (A3)
CTOP.NAME4: U5002.11 (A4)
CTOP.NAME5: U5002.13 (A5)
CTOP.NAME6: U5002.15 (A6)
CTOP.NAME7: U5002.17 (A7)
CTOP.NAME8: U5003.2 (A0)
CTOP.NAME9: U5003.4 (A1)
CTOP.NAME10: U5003.6 (A2)
CTOP.NAME11: U5003.8 (A3)
CTOP.NAME12: U5003.11 (A4)
CTOP.NAME13: U5003.13 (A5)
CTOP.NAME14: U5003.15 (A6)
CTOP.NAME15: U5003.17 (A7)
CTOP.NAME16: U5004.2 (A0)
CTOP.NAME17: U5004.4 (A1)
CTOP.NAME18: U5004.6 (A2)
CTOP.NAME19: U5004.8 (A3)
CTOP.NAME20: U5004.11 (A4)
CTOP.NAME21: U5004.13 (A5)
CTOP.NAME22: U5004.15 (A6)
CTOP.NAME23: U5004.17 (A7)
CTOP.NAME24: U5005.2 (A0)
CTOP.NAME25: U5005.4 (A1)
CTOP.NAME26: U5005.6 (A2)
CTOP.NAME27: U5005.8 (A3)
CTOP.NAME28: U5005.11 (A4)
CTOP.NAME29: U5005.13 (A5)
CTOP.NAME30: U5005.15 (A6)
CTOP.NAME31: U5005.17 (A7)
MAR.NAME0: U5002.3 (B0)
MAR.NAME1: U5002.5 (B1)
MAR.NAME2: U5002.7 (B2)
MAR.NAME3: U5002.9 (B3)
MAR.NAME4: U5002.12 (B4)
MAR.NAME5: U5002.14 (B5)
MAR.NAME6: U5002.16 (B6)
MAR.NAME7: U5002.18 (B7)
MAR.NAME8: U5003.3 (B0)
MAR.NAME9: U5003.5 (B1)
MAR.NAME10: U5003.7 (B2)
MAR.NAME11: U5003.9 (B3)
MAR.NAME12: U5003.12 (B4)
MAR.NAME13: U5003.14 (B5)
MAR.NAME14: U5003.16 (B6)
MAR.NAME15: U5003.18 (B7)
MAR.NAME16: U5004.3 (B0)
MAR.NAME17: U5004.5 (B1)
MAR.NAME18: U5004.7 (B2)
MAR.NAME19: U5004.9 (B3)
MAR.NAME20: U5004.12 (B4)
MAR.NAME21: U5004.14 (B5)
MAR.NAME22: U5004.16 (B6)
MAR.NAME23: U5004.18 (B7)
MAR.NAME24: U5005.3 (B0)
MAR.NAME25: U5005.5 (B1)
MAR.NAME26: U5005.7 (B2)
MAR.NAME27: U5005.9 (B3)
MAR.NAME28: U5005.12 (B4)
MAR.NAME29: U5005.14 (B5)
MAR.NAME30: U5005.16 (B6)
MAR.NAME31: U5005.18 (B7)
MAR.OFFS0: U5001.8 (A3)
MAR.OFFS1: U5001.11 (A4)
MAR.OFFS2: U5001.13 (A5)
MAR.OFFS3: U5001.15 (A6)
MAR.OFFS4: U5001.17 (A7)
MAR.SPACE0: U5001.2 (A0)
MAR.SPACE1: U5001.4 (A1)
MAR.SPACE2: U5001.6 (A2)
NAME_MATCH~: U5005.19 (A=B)
unnamed: U5001.19 (A=B), U5002.1 (E)
unnamed: U5002.19 (A=B), U5003.1 (E)
unnamed: U5003.19 (A=B), U5004.1 (E)
unnamed: U5004.19 (A=B), U5005.1 (E)
PD: U5001.1 (E), U5001.3 (B0), U5001.5 (B1), U5001.9 (B3), U5001.12 (B4), U5001.14 (B5), U5001.16 (B6), U5001.18 (B7)
PU: U5001.7 (B2)
