Datamuseum-DK/R1000.HwDoc/Schematics/FIU/pg_50.kicad_sch

## KiCad design Schematics/FIU/pg_50.kicad_sch (2023-01-10)

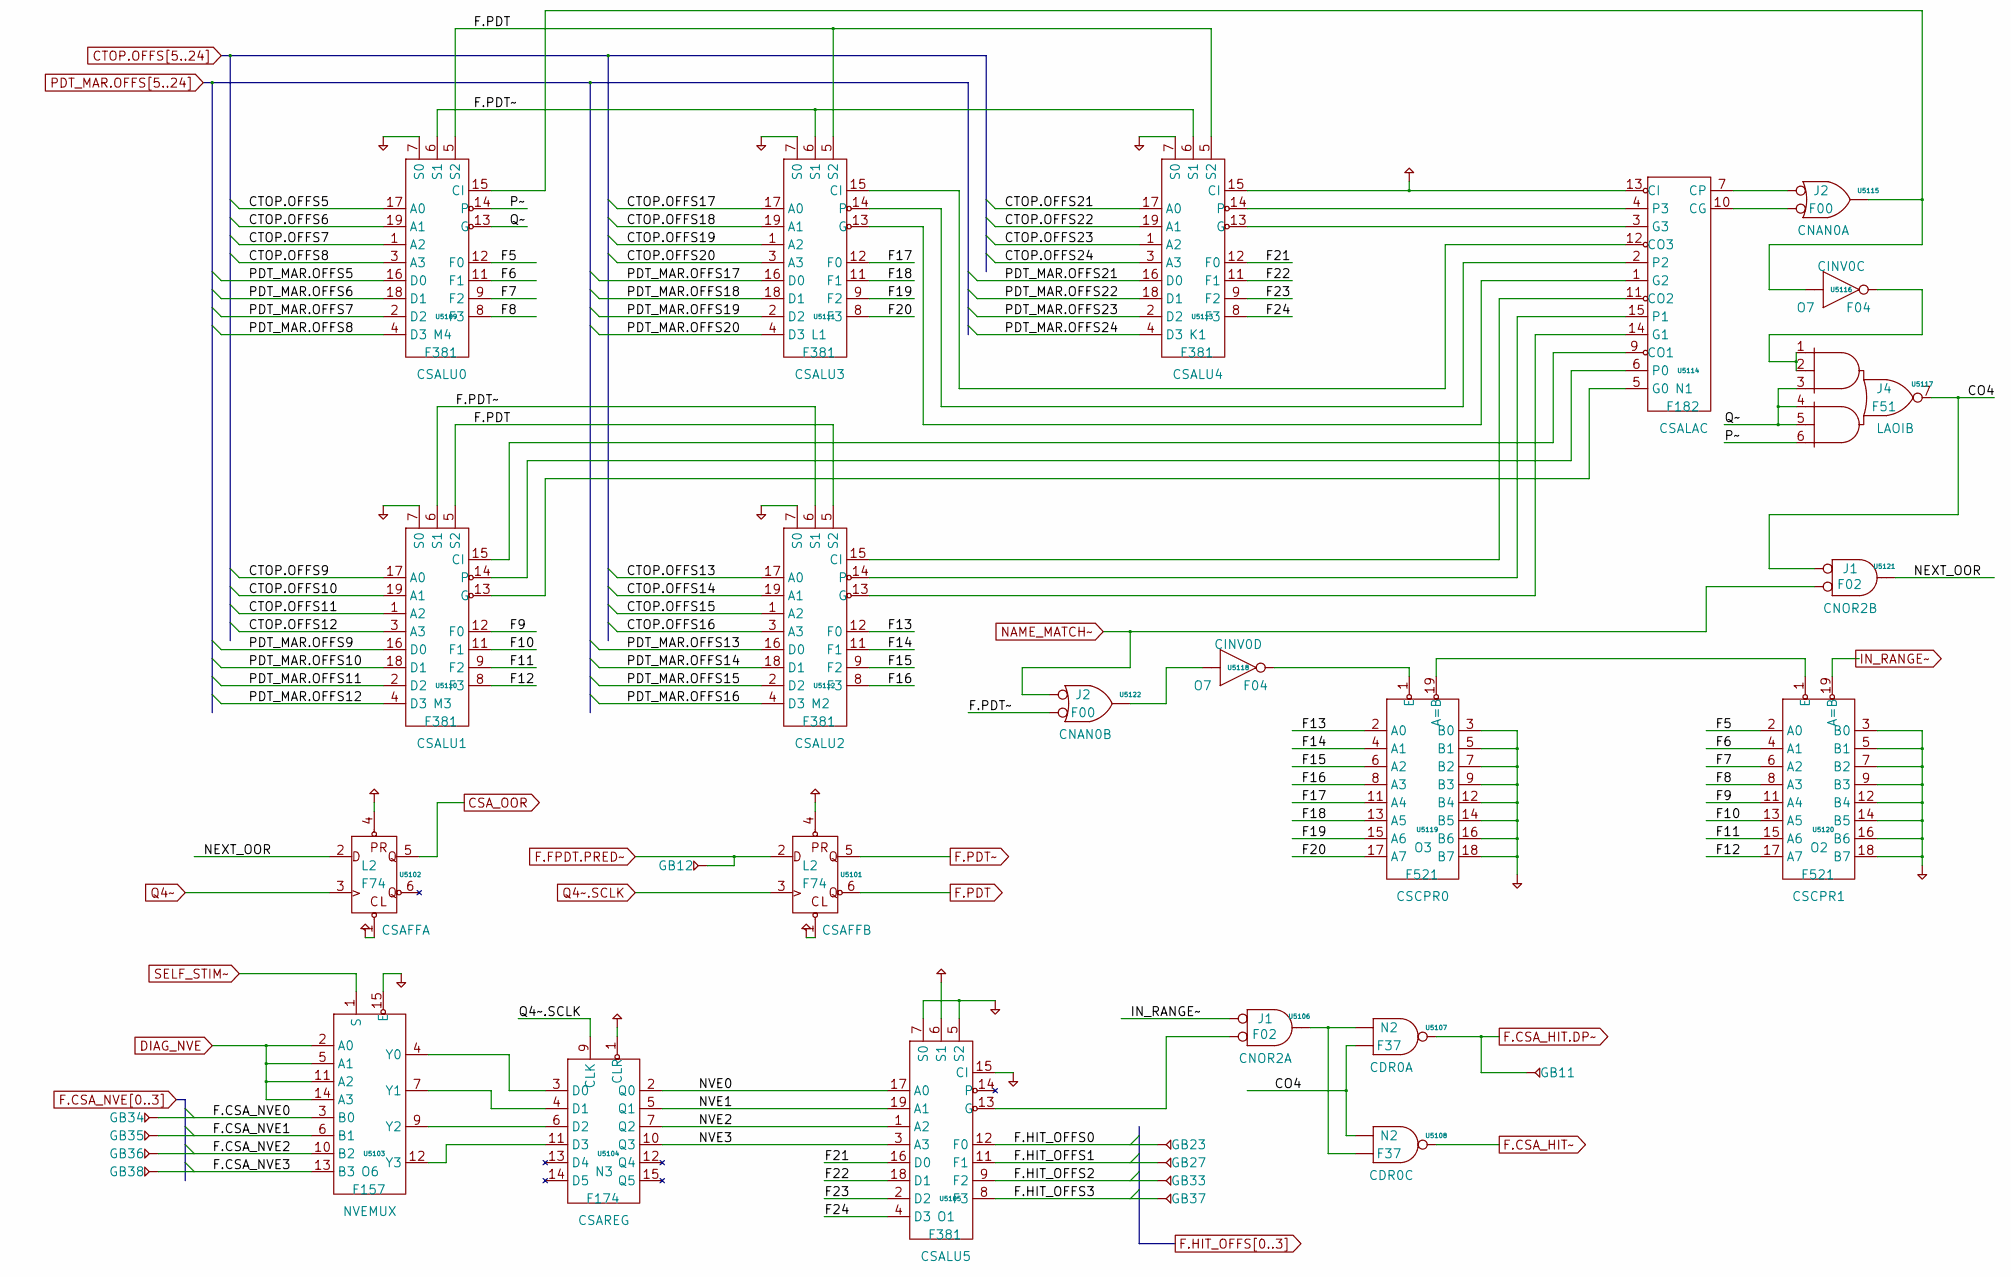
[picture p334: schematic pg_50.kicad_sch]

Parts:
GB11, GB12, GB23, GB27, GB33, GB34, GB35, GB36, GB37, GB38: GB
U5101, U5102: F74
U5103: F157
U5104: F174
U5105, U5109, U5110, U5111, U5112, U5113: F381
U5106, U5121: F02
U5107, U5108: F37
U5114: F182
U5115, U5122: F00
U5116, U5118: F04
U5117: F51
U5119, U5120: F521

Connections:
CO4: U5107.2 (D1), U5108.1 (D0), U5117.7 (Q), U5121.1 (D0)
CSA_OOR: U5102.5 (Q)
CTOP.OFFS5: U5109.17 (A0)
CTOP.OFFS6: U5109.19 (A1)
CTOP.OFFS7: U5109.1 (A2)
CTOP.OFFS8: U5109.3 (A3)
CTOP.OFFS9: U5110.17 (A0)
CTOP.OFFS10: U5110.19 (A1)
CTOP.OFFS11: U5110.1 (A2)
CTOP.OFFS12: U5110.3 (A3)
CTOP.OFFS13: U5112.17 (A0)
CTOP.OFFS14: U5112.19 (A1)
CTOP.OFFS15: U5112.1 (A2)
CTOP.OFFS16: U5112.3 (A3)
CTOP.OFFS17: U5111.17 (A0)
CTOP.OFFS18: U5111.19 (A1)
CTOP.OFFS19: U5111.1 (A2)
CTOP.OFFS20: U5111.3 (A3)
CTOP.OFFS21: U5113.17 (A0)
CTOP.OFFS22: U5113.19 (A1)
CTOP.OFFS23: U5113.1 (A2)
CTOP.OFFS24: U5113.3 (A3)
DIAG_NVE: U5103.2 (A0), U5103.5 (A1), U5103.11 (A2), U5103.14 (A3)
F5: U5109.12 (F0), U5120.2 (A0)
F6: U5109.11 (F1), U5120.4 (A1)
F7: U5109.9 (F2), U5120.6 (A2)
F8: U5109.8 (F3), U5120.8 (A3)
F9: U5110.12 (F0), U5120.11 (A4)
F10: U5110.11 (F1), U5120.13 (A5)
F11: U5110.9 (F2), U5120.15 (A6)
F12: U5110.8 (F3), U5120.17 (A7)
F13: U5112.12 (F0), U5119.2 (A0)
F14: U5112.11 (F1), U5119.4 (A1)
F15: U5112.9 (F2), U5119.6 (A2)
F16: U5112.8 (F3), U5119.8 (A3)
F17: U5111.12 (F0), U5119.11 (A4)
F18: U5111.11 (F1), U5119.13 (A5)
F19: U5111.9 (F2), U5119.15 (A6)
F20: U5111.8 (F3), U5119.17 (A7)
F21: U5105.16 (D0), U5113.12 (F0)
F22: U5105.18 (D1), U5113.11 (F1)
F23: U5105.2 (D2), U5113.9 (F2)
F24: U5105.4 (D3), U5113.8 (F3)
F.CSA_HIT.DP~: GB11.1, U5107.3 (Q)
F.CSA_HIT~: U5108.3 (Q)
F.CSA_NVE0: GB34.1, U5103.3 (B0)
F.CSA_NVE1: GB35.1, U5103.6 (B1)
F.CSA_NVE2: GB36.1, U5103.10 (B2)
F.CSA_NVE3: GB38.1, U5103.13 (B3)
F.FPDT.PRED~: GB12.1, U5101.2 (D)
F.HIT_OFFS0: GB23.1, U5105.12 (F0)
F.HIT_OFFS1: GB27.1, U5105.11 (F1)
F.HIT_OFFS2: GB33.1, U5105.9 (F2)
F.HIT_OFFS3: GB37.1, U5105.8 (F3)
F.PDT: U5101.6 (Q_), U5109.5 (S2), U5110.5 (S2), U5111.5 (S2), U5112.5 (S2), U5113.5 (S2)
F.PDT~: U5101.5 (Q), U5109.6 (S1), U5110.6 (S1), U5111.6 (S1), U5112.6 (S1), U5113.6 (S1), U5122.2 (D1)
IN_RANGE~: U5106.1 (D0), U5120.19 (A=B)
NAME_MATCH~: U5121.2 (D1), U5122.1 (D0)
NEXT_OOR: U5102.2 (D), U5121.3 (Q)
NVE0: U5104.2 (Q0), U5105.17 (A0)
NVE1: U5104.5 (Q1), U5105.19 (A1)
NVE2: U5104.7 (Q2), U5105.1 (A2)
NVE3: U5104.10 (Q3), U5105.3 (A3)
unnamed: U5103.4 (Y0), U5104.3 (D0)
unnamed: U5103.7 (Y1), U5104.4 (D1)
unnamed: U5103.9 (Y2), U5104.6 (D2)
unnamed: U5103.12 (Y3), U5104.11 (D3)
unnamed: U5105.13 (G), U5106.2 (D1)
unnamed: U5106.3 (Q), U5107.1 (D0), U5108.2 (D1)
unnamed: U5109.15 (CI), U5115.3 (Q), U5116.1 (D0)
unnamed: U5110.13 (G), U5114.5 (G0)
unnamed: U5110.14, U5114.6 (P0)
unnamed: U5110.15 (CI), U5114.9 (CO1)
unnamed: U5111.13 (G), U5114.1 (G2)
unnamed: U5111.14, U5114.2
unnamed: U5111.15 (CI), U5114.12 (CO3)
unnamed: U5112.13 (G), U5114.14 (G1)
unnamed: U5112.14, U5114.15 (P1)
unnamed: U5112.15 (CI), U5114.11 (CO2)
unnamed: U5113.13 (G), U5114.3 (G3)
unnamed: U5113.14, U5114.4 (P3)
unnamed: U5114.7 (CP), U5115.1 (D0)
unnamed: U5114.10 (CG), U5115.2 (D1)
unnamed: U5116.2 (Q), U5117.1 (A1), U5117.2 (A2)
unnamed: U5118.1 (D0), U5122.3 (Q)
unnamed: U5118.2 (Q), U5119.1 (E)
unnamed: U5119.19 (A=B), U5120.1 (E)
PD: U5103.15 (E), U5105.5 (S2), U5105.7 (S0), U5105.15 (CI), U5109.7 (S0), U5110.7 (S0), U5111.7 (S0), U5112.7 (S0), U5113.7 (S0), U5119.3 (B0), U5119.5 (B1), U5119.7 (B2), U5119.9 (B3), U5119.12 (B4), U5119.14 (B5), U5119.16 (B6), U5119.18 (B7), U5120.3 (B0), U5120.5 (B1), U5120.7 (B2), U5120.9 (B3), U5120.12 (B4), U5120.14 (B5), U5120.16 (B6), U5120.18 (B7)
PDT_MAR.OFFS5: U5109.16 (D0)
PDT_MAR.OFFS6: U5109.18 (D1)
PDT_MAR.OFFS7: U5109.2 (D2)
PDT_MAR.OFFS8: U5109.4 (D3)
PDT_MAR.OFFS9: U5110.16 (D0)
PDT_MAR.OFFS10: U5110.18 (D1)
PDT_MAR.OFFS11: U5110.2 (D2)
PDT_MAR.OFFS12: U5110.4 (D3)
PDT_MAR.OFFS13: U5112.16 (D0)
PDT_MAR.OFFS14: U5112.18 (D1)
PDT_MAR.OFFS15: U5112.2 (D2)
PDT_MAR.OFFS16: U5112.4 (D3)
PDT_MAR.OFFS17: U5111.16 (D0)
PDT_MAR.OFFS18: U5111.18 (D1)
PDT_MAR.OFFS19: U5111.2 (D2)
PDT_MAR.OFFS20: U5111.4 (D3)
PDT_MAR.OFFS21: U5113.16 (D0)
PDT_MAR.OFFS22: U5113.18 (D1)
PDT_MAR.OFFS23: U5113.2 (D2)
PDT_MAR.OFFS24: U5113.4 (D3)
PU: U5101.1 (CL_), U5101.4 (PR_), U5102.1 (CL_), U5102.4 (PR_), U5104.1 (CLR), U5105.6 (S1), U5113.15 (CI), U5114.13 (CI)
P~: U5109.14, U5117.6 (B3)
Q4~: U5102.3 (CLK)
Q4~.SCLK: U5101.3 (CLK), U5104.9 (CLK)
Q~: U5109.13 (G), U5117.3 (A3), U5117.4 (B1), U5117.5 (B2)
SELF_STIM~: U5103.1 (S)
