Datamuseum-DK/R1000.HwDoc/Schematics/FIU/pg_51.kicad_sch

## KiCad design Schematics/FIU/pg_51.kicad_sch (2023-01-10)

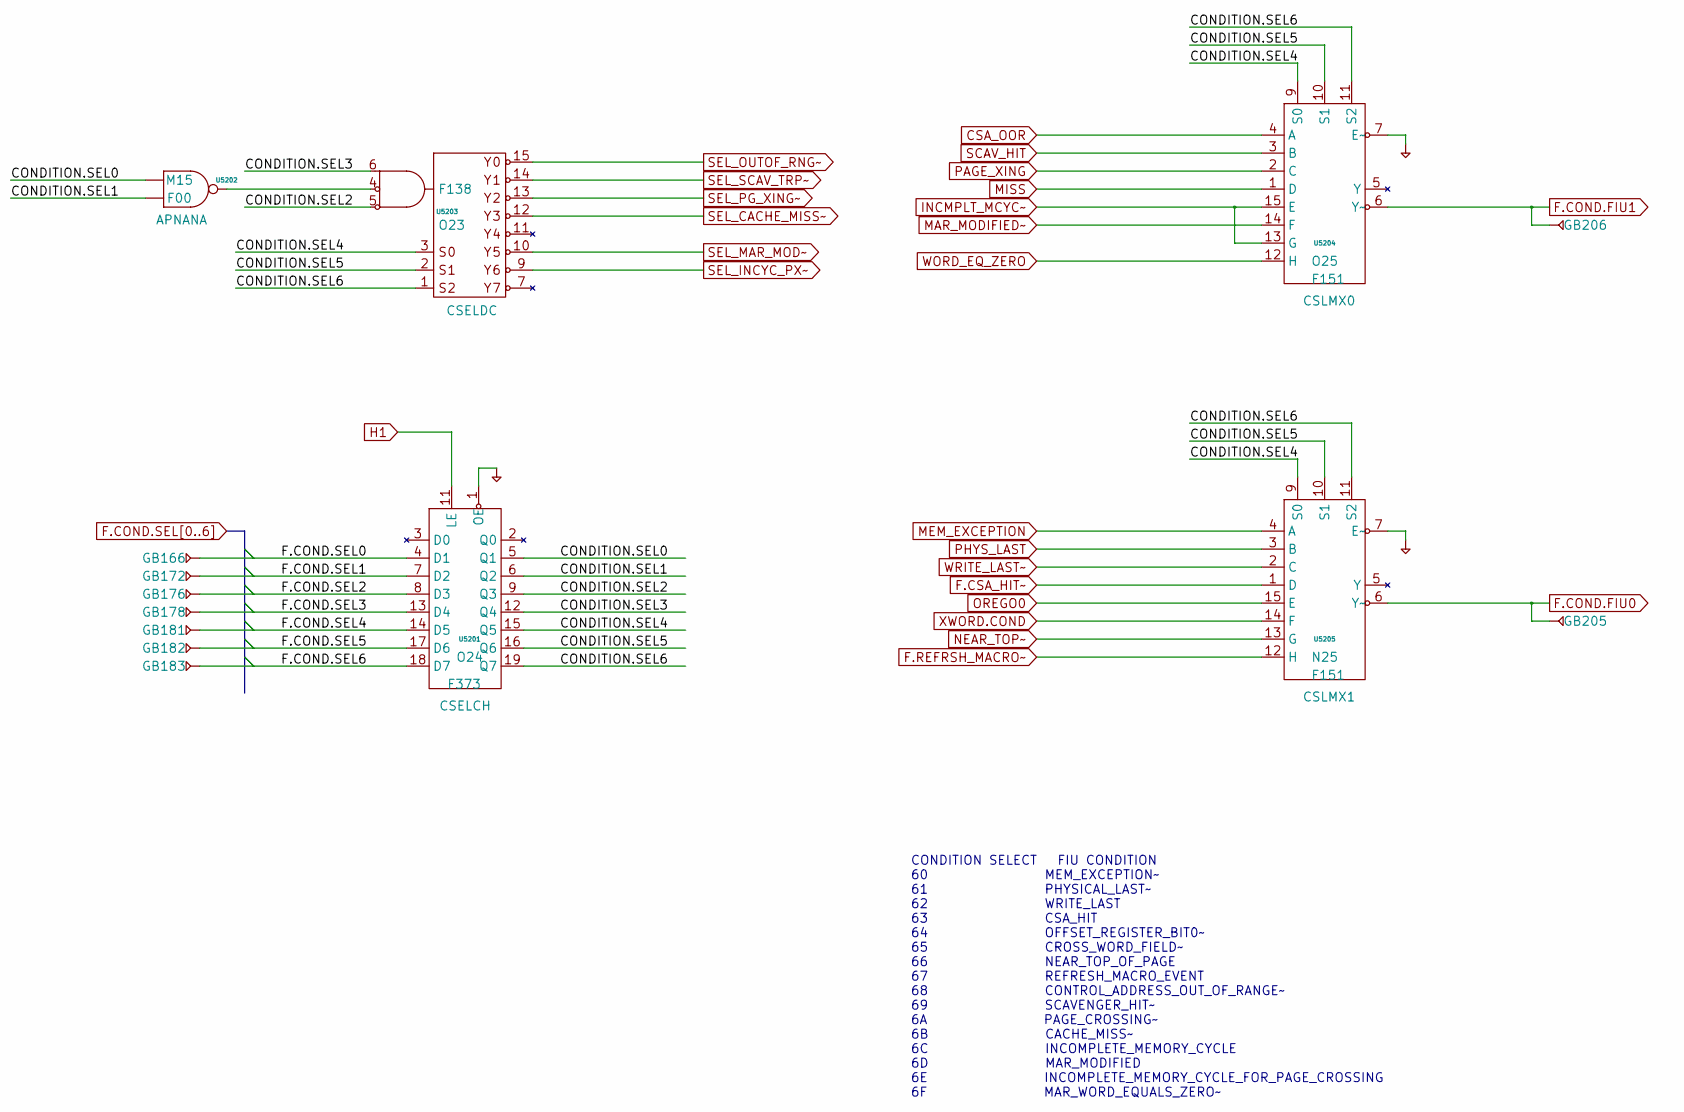
[picture p335: schematic pg_51.kicad_sch]

Parts:
GB166, GB172, GB176, GB178, GB181, GB182, GB183, GB205, GB206: GB
U5201: F373
U5202: F00
U5203: F138
U5204, U5205: F151

Connections:
CONDITION.SEL0: U5201.5 (Q1), U5202.1 (D0)
CONDITION.SEL1: U5201.6 (Q2), U5202.2 (D1)
CONDITION.SEL2: U5201.9 (Q3), U5203.5 (D2)
CONDITION.SEL3: U5201.12 (Q4), U5203.6 (D0)
CONDITION.SEL4: U5201.15 (Q5), U5203.3 (S0), U5204.9 (S0), U5205.9 (S0)
CONDITION.SEL5: U5201.16 (Q6), U5203.2 (S1), U5204.10 (S1), U5205.10 (S1)
CONDITION.SEL6: U5201.19 (Q7), U5203.1 (S2), U5204.11 (S2), U5205.11 (S2)
CSA_OOR: U5204.4 (A)
F.COND.FIU0: GB205.1, U5205.6 (Y~)
F.COND.FIU1: GB206.1, U5204.6 (Y~)
F.COND.SEL0: GB166.1, U5201.4 (D1)
F.COND.SEL1: GB172.1, U5201.7 (D2)
F.COND.SEL2: GB176.1, U5201.8 (D3)
F.COND.SEL3: GB178.1, U5201.13 (D4)
F.COND.SEL4: GB181.1, U5201.14 (D5)
F.COND.SEL5: GB182.1, U5201.17 (D6)
F.COND.SEL6: GB183.1, U5201.18 (D7)
F.CSA_HIT~: U5205.1 (D)
F.REFRSH_MACRO~: U5205.12 (H)
H1: U5201.11 (LE)
INCMPLT_MCYC~: U5204.13 (G), U5204.15 (E)
MAR_MODIFIED~: U5204.14 (F)
MEM_EXCEPTION: U5205.4 (A)
MISS: U5204.1 (D)
NEAR_TOP~: U5205.13 (G)
unnamed: U5202.3 (Q), U5203.4 (D1)
OREGO0: U5205.15 (E)
PAGE_XING: U5204.2 (C)
PD: U5201.1 (OE), U5204.7 (E~), U5205.7 (E~)
PHYS_LAST: U5205.3 (B)
SCAV_HIT: U5204.3 (B)
SEL_CACHE_MISS~: U5203.12 (Y3_)
SEL_INCYC_PX~: U5203.9 (Y6_)
SEL_MAR_MOD~: U5203.10 (Y5_)
SEL_OUTOF_RNG~: U5203.15 (Y0_)
SEL_PG_XING~: U5203.13 (Y2_)
SEL_SCAV_TRP~: U5203.14 (Y1_)
WORD_EQ_ZERO: U5204.12 (H)
WRITE_LAST~: U5205.2 (C)
XWORD.COND: U5205.14 (F)

Notes on the sheet:
CONDITION SELECT FIU CONDITION 60 MEM_EXCEPTION~ 61 PHYSICAL_LAST~ 62 WRITE_LAST 63 CSA_HIT 64 OFFSET_REGISTER_BIT0~ 65 CROSS_WORD_FIELD~ 66 NEAR_TOP_OF_PAGE 67 REFRESH_MACRO_EVENT 68 CONTROL_ADDRESS_OUT_OF_RANGE~ 69 SCAVENGER_HIT~ 6A PAGE_CROSSING~ 6B CACHE_MISS~ 6C INCOMPLETE_MEMORY_CYCLE 6D MAR_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
