Datamuseum-DK/R1000.HwDoc/Schematics/FIU/pg_53.kicad_sch

## KiCad design Schematics/FIU/pg_53.kicad_sch (2023-01-10)

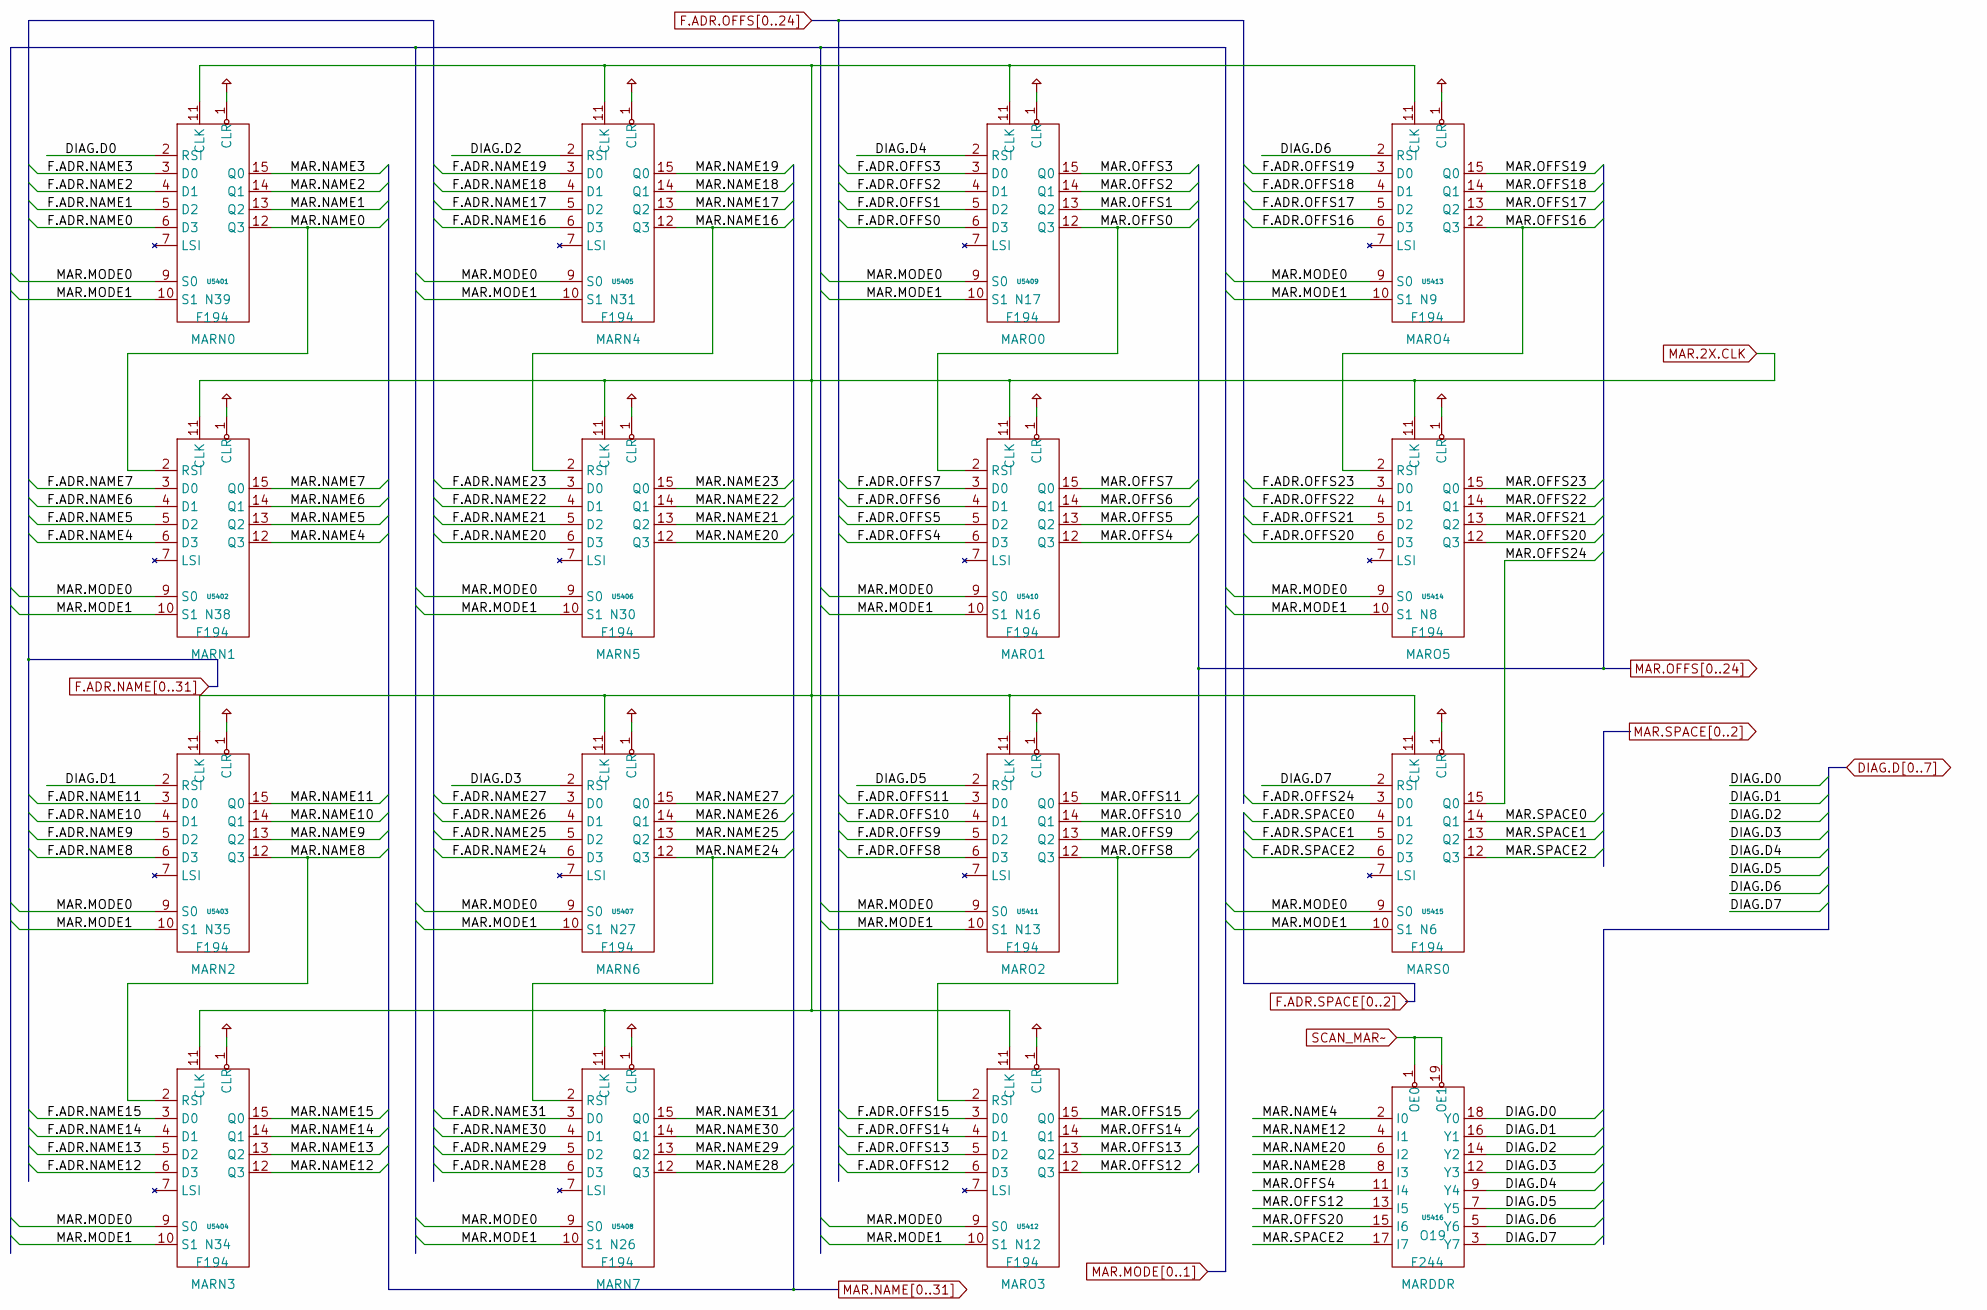
[picture p336: schematic pg_53.kicad_sch]

Parts:
U5401, U5402, U5403, U5404, U5405, U5406, U5407, U5408, U5409, U5410, U5411, U5412, U5413, U5414, U5415: F194
U5416: F244

Connections:
DIAG.D0: U5401.2 (RSI), U5416.18 (Y0)
DIAG.D1: U5403.2 (RSI), U5416.16 (Y1)
DIAG.D2: U5405.2 (RSI), U5416.14 (Y2)
DIAG.D3: U5407.2 (RSI), U5416.12 (Y3)
DIAG.D4: U5409.2 (RSI), U5416.9 (Y4)
DIAG.D5: U5411.2 (RSI), U5416.7 (Y5)
DIAG.D6: U5413.2 (RSI), U5416.5 (Y6)
DIAG.D7: U5415.2 (RSI), U5416.3 (Y7)
F.ADR.NAME0: U5401.6 (D3)
F.ADR.NAME1: U5401.5 (D2)
F.ADR.NAME2: U5401.4 (D1)
F.ADR.NAME3: U5401.3 (D0)
F.ADR.NAME4: U5402.6 (D3)
F.ADR.NAME5: U5402.5 (D2)
F.ADR.NAME6: U5402.4 (D1)
F.ADR.NAME7: U5402.3 (D0)
F.ADR.NAME8: U5403.6 (D3)
F.ADR.NAME9: U5403.5 (D2)
F.ADR.NAME10: U5403.4 (D1)
F.ADR.NAME11: U5403.3 (D0)
F.ADR.NAME12: U5404.6 (D3)
F.ADR.NAME13: U5404.5 (D2)
F.ADR.NAME14: U5404.4 (D1)
F.ADR.NAME15: U5404.3 (D0)
F.ADR.NAME16: U5405.6 (D3)
F.ADR.NAME17: U5405.5 (D2)
F.ADR.NAME18: U5405.4 (D1)
F.ADR.NAME19: U5405.3 (D0)
F.ADR.NAME20: U5406.6 (D3)
F.ADR.NAME21: U5406.5 (D2)
F.ADR.NAME22: U5406.4 (D1)
F.ADR.NAME23: U5406.3 (D0)
F.ADR.NAME24: U5407.6 (D3)
F.ADR.NAME25: U5407.5 (D2)
F.ADR.NAME26: U5407.4 (D1)
F.ADR.NAME27: U5407.3 (D0)
F.ADR.NAME28: U5408.6 (D3)
F.ADR.NAME29: U5408.5 (D2)
F.ADR.NAME30: U5408.4 (D1)
F.ADR.NAME31: U5408.3 (D0)
F.ADR.OFFS0: U5409.6 (D3)
F.ADR.OFFS1: U5409.5 (D2)
F.ADR.OFFS2: U5409.4 (D1)
F.ADR.OFFS3: U5409.3 (D0)
F.ADR.OFFS4: U5410.6 (D3)
F.ADR.OFFS5: U5410.5 (D2)
F.ADR.OFFS6: U5410.4 (D1)
F.ADR.OFFS7: U5410.3 (D0)
F.ADR.OFFS8: U5411.6 (D3)
F.ADR.OFFS9: U5411.5 (D2)
F.ADR.OFFS10: U5411.4 (D1)
F.ADR.OFFS11: U5411.3 (D0)
F.ADR.OFFS12: U5412.6 (D3)
F.ADR.OFFS13: U5412.5 (D2)
F.ADR.OFFS14: U5412.4 (D1)
F.ADR.OFFS15: U5412.3 (D0)
F.ADR.OFFS16: U5413.6 (D3)
F.ADR.OFFS17: U5413.5 (D2)
F.ADR.OFFS18: U5413.4 (D1)
F.ADR.OFFS19: U5413.3 (D0)
F.ADR.OFFS20: U5414.6 (D3)
F.ADR.OFFS21: U5414.5 (D2)
F.ADR.OFFS22: U5414.4 (D1)
F.ADR.OFFS23: U5414.3 (D0)
F.ADR.OFFS24: U5415.3 (D0)
F.ADR.SPACE0: U5415.4 (D1)
F.ADR.SPACE1: U5415.5 (D2)
F.ADR.SPACE2: U5415.6 (D3)
MAR.2X.CLK: U5401.11 (CLK), U5402.11 (CLK), U5403.11 (CLK), U5404.11 (CLK), U5405.11 (CLK), U5406.11 (CLK), U5407.11 (CLK), U5408.11 (CLK), U5409.11 (CLK), U5410.11 (CLK), U5411.11 (CLK), U5412.11 (CLK), U5413.11 (CLK), U5414.11 (CLK), U5415.11 (CLK)
MAR.MODE0: U5401.9 (S0), U5402.9 (S0), U5403.9 (S0), U5404.9 (S0), U5405.9 (S0), U5406.9 (S0), U5407.9 (S0), U5408.9 (S0), U5409.9 (S0), U5410.9 (S0), U5411.9 (S0), U5412.9 (S0), U5413.9 (S0), U5414.9 (S0), U5415.9 (S0)
MAR.MODE1: U5401.10 (S1), U5402.10 (S1), U5403.10 (S1), U5404.10 (S1), U5405.10 (S1), U5406.10 (S1), U5407.10 (S1), U5408.10 (S1), U5409.10 (S1), U5410.10 (S1), U5411.10 (S1), U5412.10 (S1), U5413.10 (S1), U5414.10 (S1), U5415.10 (S1)
MAR.NAME0: U5401.12 (Q3), U5402.2 (RSI)
MAR.NAME1: U5401.13 (Q2)
MAR.NAME2: U5401.14 (Q1)
MAR.NAME3: U5401.15 (Q0)
MAR.NAME4: U5402.12 (Q3), U5416.2 (I0)
MAR.NAME5: U5402.13 (Q2)
MAR.NAME6: U5402.14 (Q1)
MAR.NAME7: U5402.15 (Q0)
MAR.NAME8: U5403.12 (Q3), U5404.2 (RSI)
MAR.NAME9: U5403.13 (Q2)
MAR.NAME10: U5403.14 (Q1)
MAR.NAME11: U5403.15 (Q0)
MAR.NAME12: U5404.12 (Q3), U5416.4 (I1)
MAR.NAME13: U5404.13 (Q2)
MAR.NAME14: U5404.14 (Q1)
MAR.NAME15: U5404.15 (Q0)
MAR.NAME16: U5405.12 (Q3), U5406.2 (RSI)
MAR.NAME17: U5405.13 (Q2)
MAR.NAME18: U5405.14 (Q1)
MAR.NAME19: U5405.15 (Q0)
MAR.NAME20: U5406.12 (Q3), U5416.6 (I2)
MAR.NAME21: U5406.13 (Q2)
MAR.NAME22: U5406.14 (Q1)
MAR.NAME23: U5406.15 (Q0)
MAR.NAME24: U5407.12 (Q3), U5408.2 (RSI)
MAR.NAME25: U5407.13 (Q2)
MAR.NAME26: U5407.14 (Q1)
MAR.NAME27: U5407.15 (Q0)
MAR.NAME28: U5408.12 (Q3), U5416.8 (I3)
MAR.NAME29: U5408.13 (Q2)
MAR.NAME30: U5408.14 (Q1)
MAR.NAME31: U5408.15 (Q0)
MAR.OFFS0: U5409.12 (Q3), U5410.2 (RSI)
MAR.OFFS1: U5409.13 (Q2)
MAR.OFFS2: U5409.14 (Q1)
MAR.OFFS3: U5409.15 (Q0)
MAR.OFFS4: U5410.12 (Q3), U5416.11 (I4)
MAR.OFFS5: U5410.13 (Q2)
MAR.OFFS6: U5410.14 (Q1)
MAR.OFFS7: U5410.15 (Q0)
MAR.OFFS8: U5411.12 (Q3), U5412.2 (RSI)
MAR.OFFS9: U5411.13 (Q2)
MAR.OFFS10: U5411.14 (Q1)
MAR.OFFS11: U5411.15 (Q0)
MAR.OFFS12: U5412.12 (Q3), U5416.13 (I5)
MAR.OFFS13: U5412.13 (Q2)
MAR.OFFS14: U5412.14 (Q1)
MAR.OFFS15: U5412.15 (Q0)
MAR.OFFS16: U5413.12 (Q3), U5414.2 (RSI)
MAR.OFFS17: U5413.13 (Q2)
MAR.OFFS18: U5413.14 (Q1)
MAR.OFFS19: U5413.15 (Q0)
MAR.OFFS20: U5414.12 (Q3), U5416.15 (I6)
MAR.OFFS21: U5414.13 (Q2)
MAR.OFFS22: U5414.14 (Q1)
MAR.OFFS23: U5414.15 (Q0)
MAR.OFFS24: U5415.15 (Q0)
MAR.SPACE0: U5415.14 (Q1)
MAR.SPACE1: U5415.13 (Q2)
MAR.SPACE2: U5415.12 (Q3), U5416.17 (I7)
PU: U5401.1 (CLR), U5402.1 (CLR), U5403.1 (CLR), U5404.1 (CLR), U5405.1 (CLR), U5406.1 (CLR), U5407.1 (CLR), U5408.1 (CLR), U5409.1 (CLR), U5410.1 (CLR), U5411.1 (CLR), U5412.1 (CLR), U5413.1 (CLR), U5414.1 (CLR), U5415.1 (CLR)
SCAN_MAR~: U5416.1 (OE0), U5416.19 (OE1)
