Datamuseum-DK/R1000.HwDoc/Schematics/FIU/pg_54.kicad_sch

## KiCad design Schematics/FIU/pg_54.kicad_sch (2023-01-10)

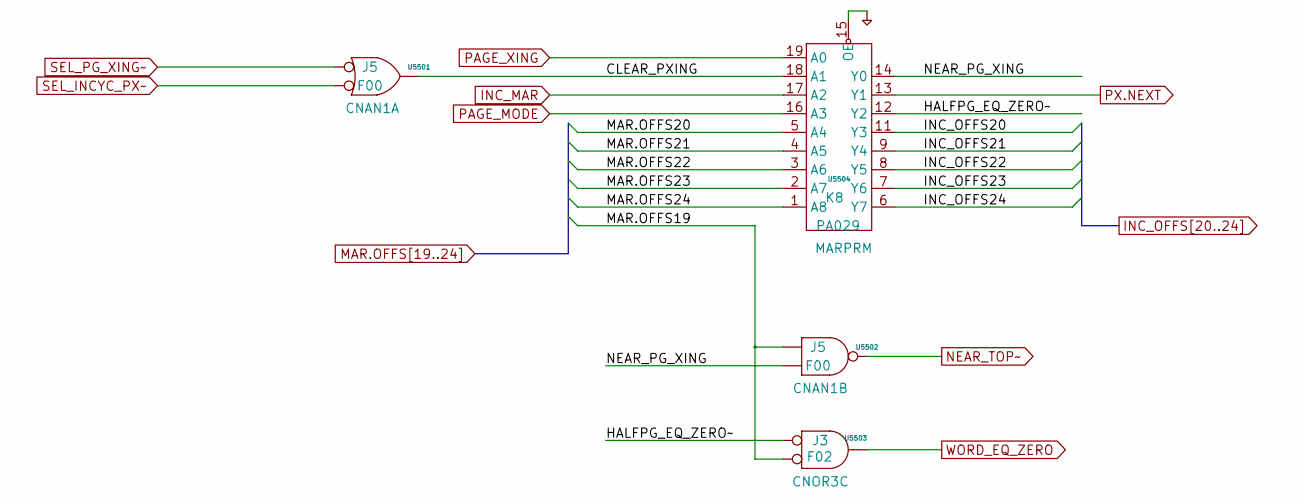
[picture p337: schematic pg_54.kicad_sch]

Parts:
U5501, U5502: F00
U5503: F02
U5504: PA029

Connections:
CLEAR_PXING: U5501.3 (Q), U5504.18 (A1)
HALFPG_EQ_ZERO~: U5503.1 (D0), U5504.12 (Y2)
INC_MAR: U5504.17 (A2)
INC_OFFS20: U5504.11 (Y3)
INC_OFFS21: U5504.9 (Y4)
INC_OFFS22: U5504.8 (Y5)
INC_OFFS23: U5504.7 (Y6)
INC_OFFS24: U5504.6 (Y7)
MAR.OFFS19: U5502.1 (D0), U5503.2 (D1)
MAR.OFFS20: U5504.5 (A4)
MAR.OFFS21: U5504.4 (A5)
MAR.OFFS22: U5504.3 (A6)
MAR.OFFS23: U5504.2 (A7)
MAR.OFFS24: U5504.1 (A8)
NEAR_PG_XING: U5502.2 (D1), U5504.14 (Y0)
NEAR_TOP~: U5502.3 (Q)
PAGE_MODE: U5504.16 (A3)
PAGE_XING: U5504.19 (A0)
PD: U5504.15 (OE)
PX.NEXT: U5504.13 (Y1)
SEL_INCYC_PX~: U5501.2 (D1)
SEL_PG_XING~: U5501.1 (D0)
WORD_EQ_ZERO: U5503.3 (Q)
