Datamuseum-DK/R1000.HwDoc/Schematics/FIU/pg_55.kicad_sch

## KiCad design Schematics/FIU/pg_55.kicad_sch (2023-01-10)

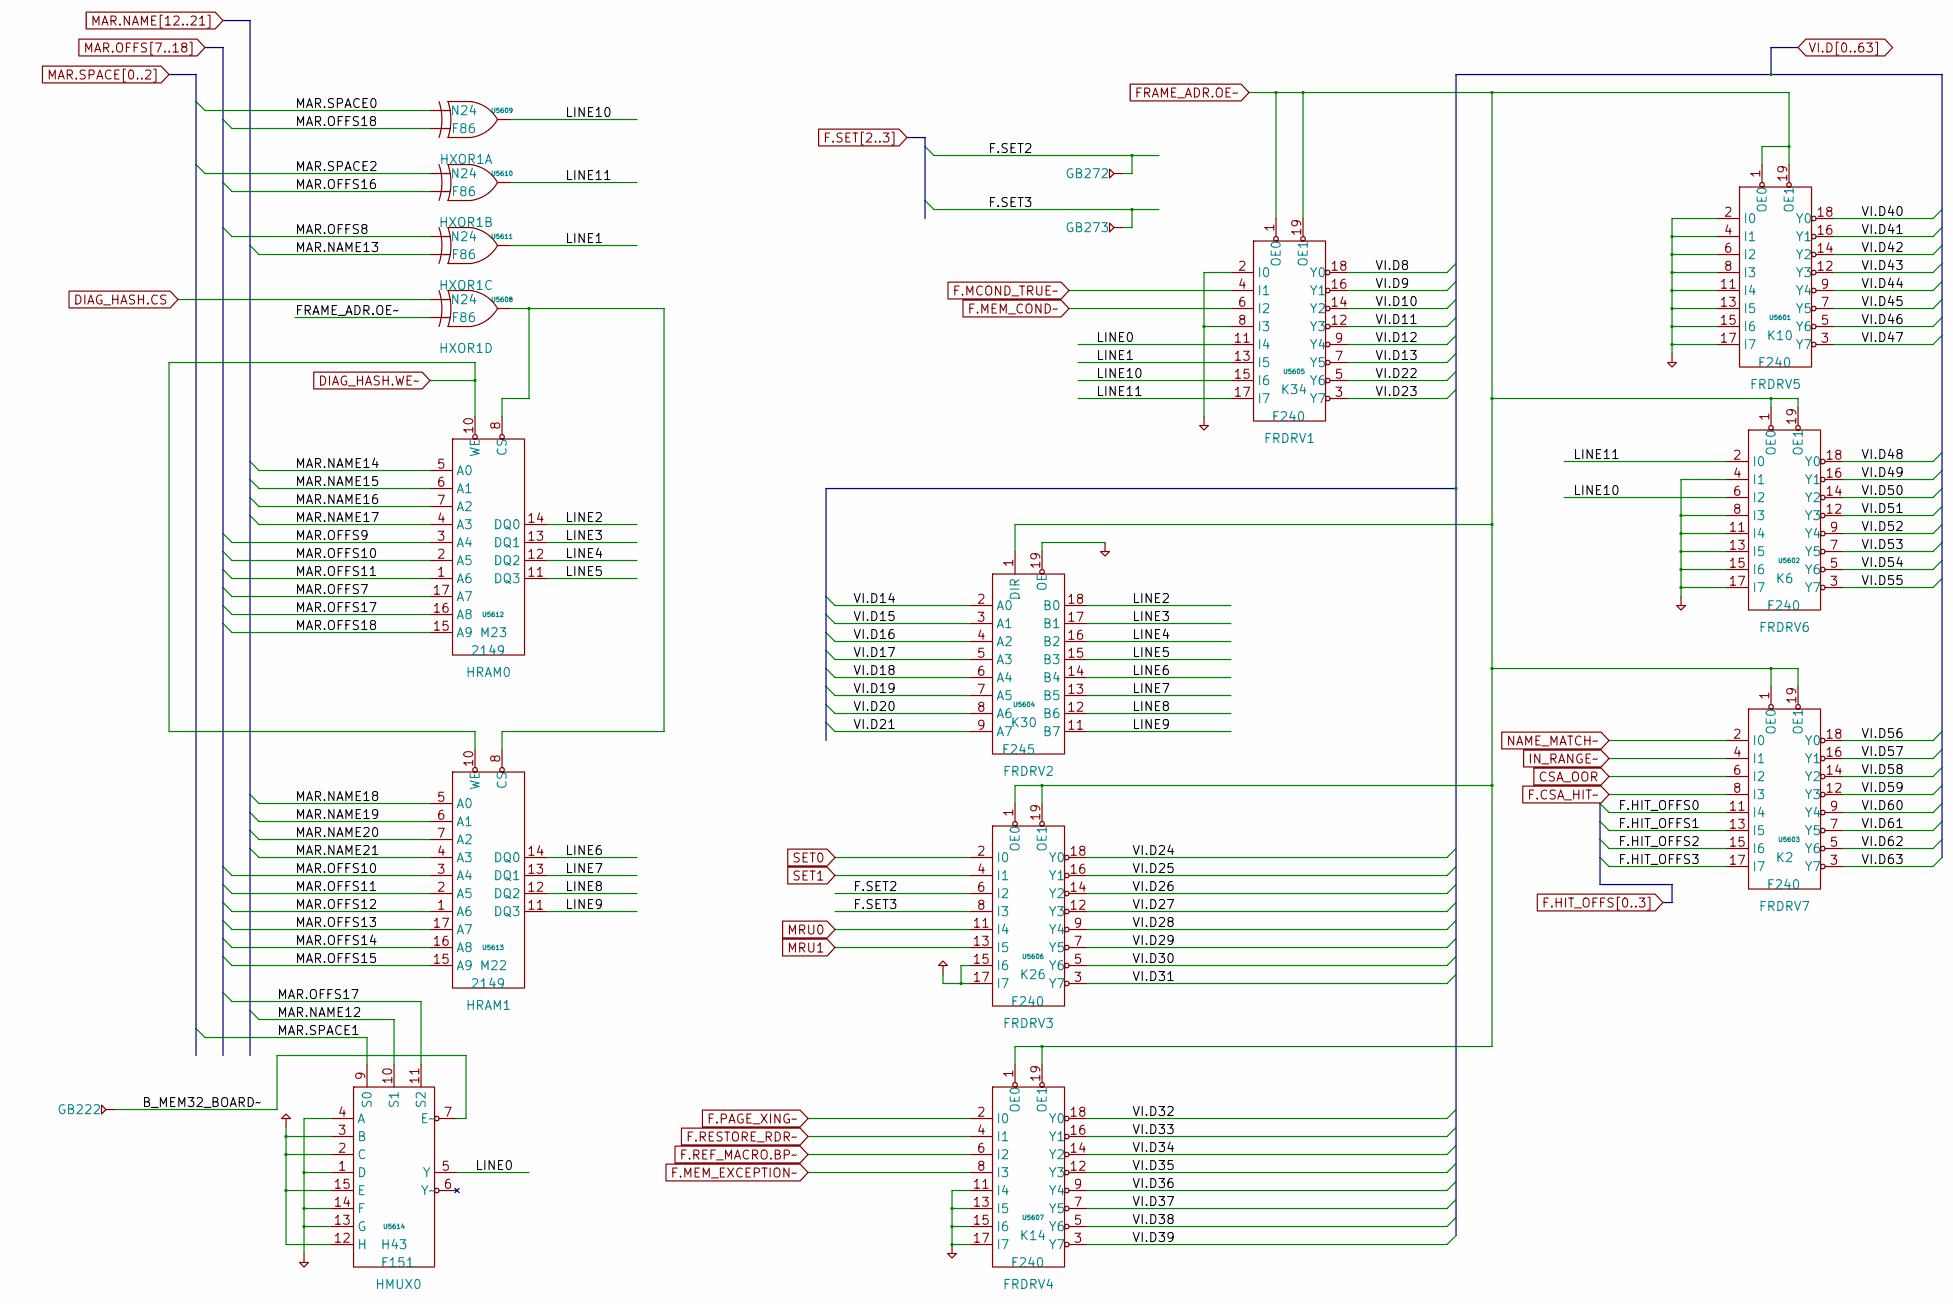
[picture p338: schematic pg_55.kicad_sch]

Parts:
GB222, GB272, GB273: GB
U5601, U5602, U5603, U5605, U5606, U5607: F240
U5604: F245
U5608, U5609, U5610, U5611: F86
U5612, U5613: 2149
U5614: F151

Connections:
B_MEM32_BOARD~: GB222.1, U5614.7 (E~)
CSA_OOR: U5603.6 (I2)
DIAG_HASH.CS: U5608.1 (D0)
DIAG_HASH.WE~: U5612.10 (WE), U5613.10 (WE)
F.CSA_HIT~: U5603.8 (I3)
F.HIT_OFFS0: U5603.11 (I4)
F.HIT_OFFS1: U5603.13 (I5)
F.HIT_OFFS2: U5603.15 (I6)
F.HIT_OFFS3: U5603.17 (I7)
F.MCOND_TRUE~: U5605.4 (I1)
F.MEM_COND~: U5605.6 (I2)
F.MEM_EXCEPTION~: U5607.8 (I3)
F.PAGE_XING~: U5607.2 (I0)
F.REF_MACRO.BP~: U5607.6 (I2)
F.RESTORE_RDR~: U5607.4 (I1)
F.SET2: GB272.1, U5606.6 (I2)
F.SET3: GB273.1, U5606.8 (I3)
FRAME_ADR.OE~: U5601.1 (OE0), U5601.19 (OE1), U5602.1 (OE0), U5602.19 (OE1), U5603.1 (OE0), U5603.19 (OE1), U5604.1 (DIR), U5605.1 (OE0), U5605.19 (OE1), U5606.1 (OE0), U5606.19 (OE1), U5607.1 (OE0), U5607.19 (OE1), U5608.2 (D1)
IN_RANGE~: U5603.4 (I1)
LINE0: U5605.11 (I4), U5614.5 (Y)
LINE1: U5605.13 (I5), U5611.3 (Q)
LINE2: U5604.18 (B0), U5612.14 (DQ0)
LINE3: U5604.17 (B1), U5612.13 (DQ1)
LINE4: U5604.16 (B2), U5612.12 (DQ2)
LINE5: U5604.15 (B3), U5612.11 (DQ3)
LINE6: U5604.14 (B4), U5613.14 (DQ0)
LINE7: U5604.13 (B5), U5613.13 (DQ1)
LINE8: U5604.12 (B6), U5613.12 (DQ2)
LINE9: U5604.11 (B7), U5613.11 (DQ3)
LINE10: U5602.6 (I2), U5605.15 (I6), U5609.3 (Q)
LINE11: U5602.2 (I0), U5605.17 (I7), U5610.3 (Q)
MAR.NAME12: U5614.10 (S1)
MAR.NAME13: U5611.2 (D1)
MAR.NAME14: U5612.5 (A0)
MAR.NAME15: U5612.6 (A1)
MAR.NAME16: U5612.7 (A2)
MAR.NAME17: U5612.4 (A3)
MAR.NAME18: U5613.5 (A0)
MAR.NAME19: U5613.6 (A1)
MAR.NAME20: U5613.7 (A2)
MAR.NAME21: U5613.4 (A3)
MAR.OFFS7: U5612.17 (A7)
MAR.OFFS8: U5611.1 (D0)
MAR.OFFS9: U5612.3 (A4)
MAR.OFFS10: U5612.2 (A5), U5613.3 (A4)
MAR.OFFS11: U5612.1 (A6), U5613.2 (A5)
MAR.OFFS12: U5613.1 (A6)
MAR.OFFS13: U5613.17 (A7)
MAR.OFFS14: U5613.16 (A8)
MAR.OFFS15: U5613.15 (A9)
MAR.OFFS16: U5610.2 (D1)
MAR.OFFS17: U5612.16 (A8), U5614.11 (S2)
MAR.OFFS18: U5609.2 (D1), U5612.15 (A9)
MAR.SPACE0: U5609.1 (D0)
MAR.SPACE1: U5614.9 (S0)
MAR.SPACE2: U5610.1 (D0)
MRU0: U5606.11 (I4)
MRU1: U5606.13 (I5)
NAME_MATCH~: U5603.2 (I0)
unnamed: U5608.3 (Q), U5612.8 (CS), U5613.8 (CS)
PD: U5601.2 (I0), U5601.4 (I1), U5601.6 (I2), U5601.8 (I3), U5601.11 (I4), U5601.13 (I5), U5601.15 (I6), U5601.17 (I7), U5602.4 (I1), U5602.8 (I3), U5602.11 (I4), U5602.13 (I5), U5602.15 (I6), U5602.17 (I7), U5604.19 (OE), U5605.2 (I0), U5605.8 (I3), U5607.11 (I4), U5607.13 (I5), U5607.15 (I6), U5607.17 (I7), U5614.1 (D), U5614.4 (A), U5614.13 (G), U5614.14 (F)
PU: U5606.15 (I6), U5606.17 (I7), U5614.2 (C), U5614.3 (B), U5614.12 (H), U5614.15 (E)
SET0: U5606.2 (I0)
SET1: U5606.4 (I1)
VI.D8: U5605.18 (Y0)
VI.D9: U5605.16 (Y1)
VI.D10: U5605.14 (Y2)
VI.D11: U5605.12 (Y3)
VI.D12: U5605.9 (Y4)
VI.D13: U5605.7 (Y5)
VI.D14: U5604.2 (A0)
VI.D15: U5604.3 (A1)
VI.D16: U5604.4 (A2)
VI.D17: U5604.5 (A3)
VI.D18: U5604.6 (A4)
VI.D19: U5604.7 (A5)
VI.D20: U5604.8 (A6)
VI.D21: U5604.9 (A7)
VI.D22: U5605.5 (Y6)
VI.D23: U5605.3 (Y7)
VI.D24: U5606.18 (Y0)
VI.D25: U5606.16 (Y1)
VI.D26: U5606.14 (Y2)
VI.D27: U5606.12 (Y3)
VI.D28: U5606.9 (Y4)
VI.D29: U5606.7 (Y5)
VI.D30: U5606.5 (Y6)
VI.D31: U5606.3 (Y7)
VI.D32: U5607.18 (Y0)
VI.D33: U5607.16 (Y1)
VI.D34: U5607.14 (Y2)
VI.D35: U5607.12 (Y3)
VI.D36: U5607.9 (Y4)
VI.D37: U5607.7 (Y5)
VI.D38: U5607.5 (Y6)
VI.D39: U5607.3 (Y7)
VI.D40: U5601.18 (Y0)
VI.D41: U5601.16 (Y1)
VI.D42: U5601.14 (Y2)
VI.D43: U5601.12 (Y3)
VI.D44: U5601.9 (Y4)
VI.D45: U5601.7 (Y5)
VI.D46: U5601.5 (Y6)
VI.D47: U5601.3 (Y7)
VI.D48: U5602.18 (Y0)
VI.D49: U5602.16 (Y1)
VI.D50: U5602.14 (Y2)
VI.D51: U5602.12 (Y3)
VI.D52: U5602.9 (Y4)
VI.D53: U5602.7 (Y5)
VI.D54: U5602.5 (Y6)
VI.D55: U5602.3 (Y7)
VI.D56: U5603.18 (Y0)
VI.D57: U5603.16 (Y1)
VI.D58: U5603.14 (Y2)
VI.D59: U5603.12 (Y3)
VI.D60: U5603.9 (Y4)
VI.D61: U5603.7 (Y5)
VI.D62: U5603.5 (Y6)
VI.D63: U5603.3 (Y7)
