Datamuseum-DK/R1000.HwDoc/Schematics/FIU/pg_56.kicad_sch

## KiCad design Schematics/FIU/pg_56.kicad_sch (2023-01-10)

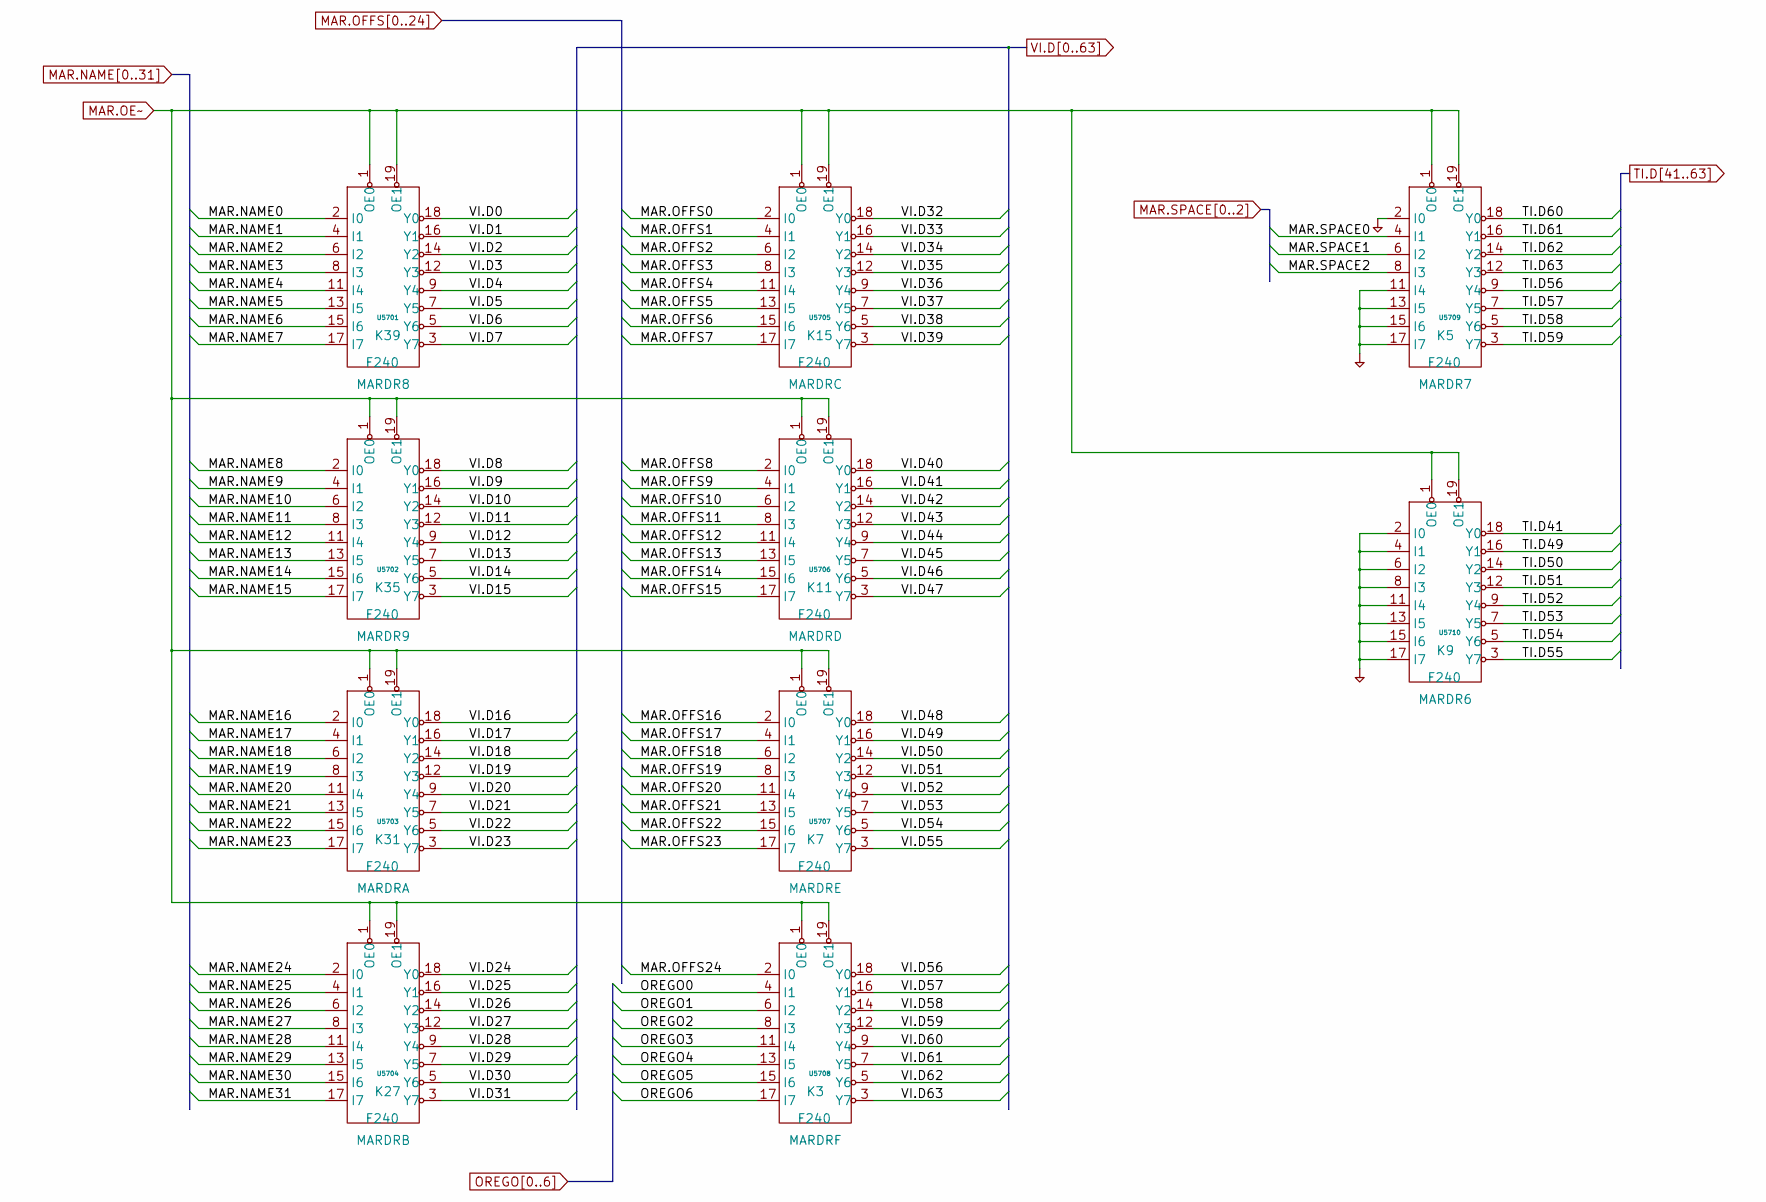
[picture p339: schematic pg_56.kicad_sch]

Parts:
U5701, U5702, U5703, U5704, U5705, U5706, U5707, U5708, U5709, U5710: F240

Connections:
MAR.NAME0: U5701.2 (I0)
MAR.NAME1: U5701.4 (I1)
MAR.NAME2: U5701.6 (I2)
MAR.NAME3: U5701.8 (I3)
MAR.NAME4: U5701.11 (I4)
MAR.NAME5: U5701.13 (I5)
MAR.NAME6: U5701.15 (I6)
MAR.NAME7: U5701.17 (I7)
MAR.NAME8: U5702.2 (I0)
MAR.NAME9: U5702.4 (I1)
MAR.NAME10: U5702.6 (I2)
MAR.NAME11: U5702.8 (I3)
MAR.NAME12: U5702.11 (I4)
MAR.NAME13: U5702.13 (I5)
MAR.NAME14: U5702.15 (I6)
MAR.NAME15: U5702.17 (I7)
MAR.NAME16: U5703.2 (I0)
MAR.NAME17: U5703.4 (I1)
MAR.NAME18: U5703.6 (I2)
MAR.NAME19: U5703.8 (I3)
MAR.NAME20: U5703.11 (I4)
MAR.NAME21: U5703.13 (I5)
MAR.NAME22: U5703.15 (I6)
MAR.NAME23: U5703.17 (I7)
MAR.NAME24: U5704.2 (I0)
MAR.NAME25: U5704.4 (I1)
MAR.NAME26: U5704.6 (I2)
MAR.NAME27: U5704.8 (I3)
MAR.NAME28: U5704.11 (I4)
MAR.NAME29: U5704.13 (I5)
MAR.NAME30: U5704.15 (I6)
MAR.NAME31: U5704.17 (I7)
MAR.OE~: U5701.1 (OE0), U5701.19 (OE1), U5702.1 (OE0), U5702.19 (OE1), U5703.1 (OE0), U5703.19 (OE1), U5704.1 (OE0), U5704.19 (OE1), U5705.1 (OE0), U5705.19 (OE1), U5706.1 (OE0), U5706.19 (OE1), U5707.1 (OE0), U5707.19 (OE1), U5708.1 (OE0), U5708.19 (OE1), U5709.1 (OE0), U5709.19 (OE1), U5710.1 (OE0), U5710.19 (OE1)
MAR.OFFS0: U5705.2 (I0)
MAR.OFFS1: U5705.4 (I1)
MAR.OFFS2: U5705.6 (I2)
MAR.OFFS3: U5705.8 (I3)
MAR.OFFS4: U5705.11 (I4)
MAR.OFFS5: U5705.13 (I5)
MAR.OFFS6: U5705.15 (I6)
MAR.OFFS7: U5705.17 (I7)
MAR.OFFS8: U5706.2 (I0)
MAR.OFFS9: U5706.4 (I1)
MAR.OFFS10: U5706.6 (I2)
MAR.OFFS11: U5706.8 (I3)
MAR.OFFS12: U5706.11 (I4)
MAR.OFFS13: U5706.13 (I5)
MAR.OFFS14: U5706.15 (I6)
MAR.OFFS15: U5706.17 (I7)
MAR.OFFS16: U5707.2 (I0)
MAR.OFFS17: U5707.4 (I1)
MAR.OFFS18: U5707.6 (I2)
MAR.OFFS19: U5707.8 (I3)
MAR.OFFS20: U5707.11 (I4)
MAR.OFFS21: U5707.13 (I5)
MAR.OFFS22: U5707.15 (I6)
MAR.OFFS23: U5707.17 (I7)
MAR.OFFS24: U5708.2 (I0)
MAR.SPACE0: U5709.4 (I1)
MAR.SPACE1: U5709.6 (I2)
MAR.SPACE2: U5709.8 (I3)
OREGO0: U5708.4 (I1)
OREGO1: U5708.6 (I2)
OREGO2: U5708.8 (I3)
OREGO3: U5708.11 (I4)
OREGO4: U5708.13 (I5)
OREGO5: U5708.15 (I6)
OREGO6: U5708.17 (I7)
PD: U5709.2 (I0), U5709.11 (I4), U5709.13 (I5), U5709.15 (I6), U5709.17 (I7), U5710.2 (I0), U5710.4 (I1), U5710.6 (I2), U5710.8 (I3), U5710.11 (I4), U5710.13 (I5), U5710.15 (I6), U5710.17 (I7)
TI.D41: U5710.18 (Y0)
TI.D49: U5710.16 (Y1)
TI.D50: U5710.14 (Y2)
TI.D51: U5710.12 (Y3)
TI.D52: U5710.9 (Y4)
TI.D53: U5710.7 (Y5)
TI.D54: U5710.5 (Y6)
TI.D55: U5710.3 (Y7)
TI.D56: U5709.9 (Y4)
TI.D57: U5709.7 (Y5)
TI.D58: U5709.5 (Y6)
TI.D59: U5709.3 (Y7)
TI.D60: U5709.18 (Y0)
TI.D61: U5709.16 (Y1)
TI.D62: U5709.14 (Y2)
TI.D63: U5709.12 (Y3)
VI.D0: U5701.18 (Y0)
VI.D1: U5701.16 (Y1)
VI.D2: U5701.14 (Y2)
VI.D3: U5701.12 (Y3)
VI.D4: U5701.9 (Y4)
VI.D5: U5701.7 (Y5)
VI.D6: U5701.5 (Y6)
VI.D7: U5701.3 (Y7)
VI.D8: U5702.18 (Y0)
VI.D9: U5702.16 (Y1)
VI.D10: U5702.14 (Y2)
VI.D11: U5702.12 (Y3)
VI.D12: U5702.9 (Y4)
VI.D13: U5702.7 (Y5)
VI.D14: U5702.5 (Y6)
VI.D15: U5702.3 (Y7)
VI.D16: U5703.18 (Y0)
VI.D17: U5703.16 (Y1)
VI.D18: U5703.14 (Y2)
VI.D19: U5703.12 (Y3)
VI.D20: U5703.9 (Y4)
VI.D21: U5703.7 (Y5)
VI.D22: U5703.5 (Y6)
VI.D23: U5703.3 (Y7)
VI.D24: U5704.18 (Y0)
VI.D25: U5704.16 (Y1)
VI.D26: U5704.14 (Y2)
VI.D27: U5704.12 (Y3)
VI.D28: U5704.9 (Y4)
VI.D29: U5704.7 (Y5)
VI.D30: U5704.5 (Y6)
VI.D31: U5704.3 (Y7)
VI.D32: U5705.18 (Y0)
VI.D33: U5705.16 (Y1)
VI.D34: U5705.14 (Y2)
VI.D35: U5705.12 (Y3)
VI.D36: U5705.9 (Y4)
VI.D37: U5705.7 (Y5)
VI.D38: U5705.5 (Y6)
VI.D39: U5705.3 (Y7)
VI.D40: U5706.18 (Y0)
VI.D41: U5706.16 (Y1)
VI.D42: U5706.14 (Y2)
VI.D43: U5706.12 (Y3)
VI.D44: U5706.9 (Y4)
VI.D45: U5706.7 (Y5)
VI.D46: U5706.5 (Y6)
VI.D47: U5706.3 (Y7)
VI.D48: U5707.18 (Y0)
VI.D49: U5707.16 (Y1)
VI.D50: U5707.14 (Y2)
VI.D51: U5707.12 (Y3)
VI.D52: U5707.9 (Y4)
VI.D53: U5707.7 (Y5)
VI.D54: U5707.5 (Y6)
VI.D55: U5707.3 (Y7)
VI.D56: U5708.18 (Y0)
VI.D57: U5708.16 (Y1)
VI.D58: U5708.14 (Y2)
VI.D59: U5708.12 (Y3)
VI.D60: U5708.9 (Y4)
VI.D61: U5708.7 (Y5)
VI.D62: U5708.5 (Y6)
VI.D63: U5708.3 (Y7)
