Datamuseum-DK/R1000.HwDoc/Schematics/FIU/pg_57.kicad_sch

## KiCad design Schematics/FIU/pg_57.kicad_sch (2023-01-10)

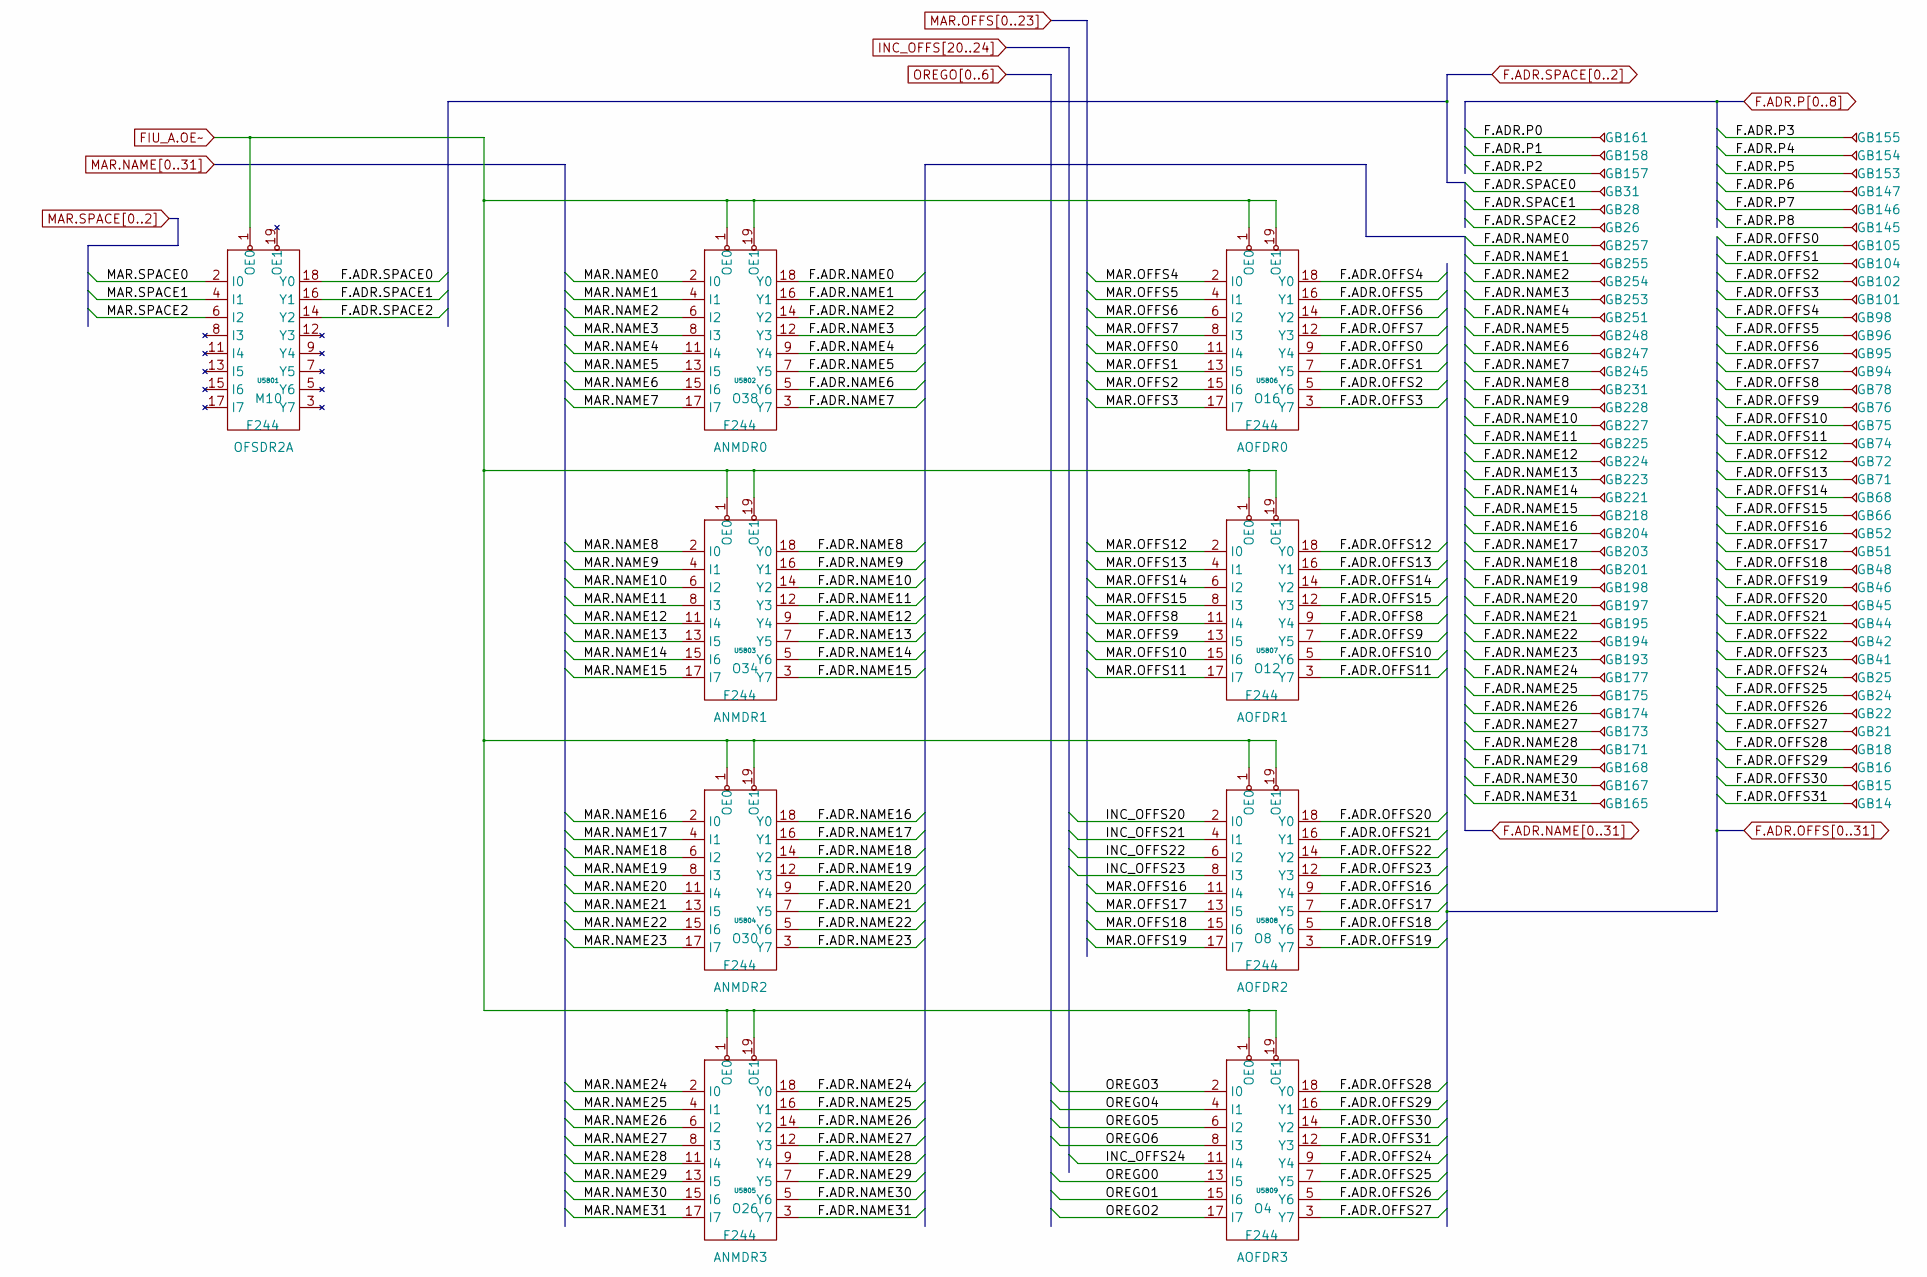
[picture p340: schematic pg_57.kicad_sch]

Parts:
GB14, GB15, GB16, GB18, GB21, GB22, GB24, GB25, GB26, GB28, GB31, GB41, GB42, GB44, GB45, GB46, GB48, GB51, GB52, GB66, GB68, GB71, GB72, GB74, GB75, GB76, GB78, GB94, GB95, GB96, GB98, GB101, GB102, GB104, GB105, GB145, GB146, GB147, GB153, GB154, GB155, GB157, GB158, GB161, GB165, GB167, GB168, GB171, GB173, GB174, GB175, GB177, GB193, GB194, GB195, GB197, GB198, GB201, GB203, GB204, GB218, GB221, GB223, GB224, GB225, GB227, GB228, GB231, GB245, GB247, GB248, GB251, GB253, GB254, GB255, GB257: GB
U5801, U5802, U5803, U5804, U5805, U5806, U5807, U5808, U5809: F244

Connections:
F.ADR.NAME0: GB257.1, U5802.18 (Y0)
F.ADR.NAME1: GB255.1, U5802.16 (Y1)
F.ADR.NAME2: GB254.1, U5802.14 (Y2)
F.ADR.NAME3: GB253.1, U5802.12 (Y3)
F.ADR.NAME4: GB251.1, U5802.9 (Y4)
F.ADR.NAME5: GB248.1, U5802.7 (Y5)
F.ADR.NAME6: GB247.1, U5802.5 (Y6)
F.ADR.NAME7: GB245.1, U5802.3 (Y7)
F.ADR.NAME8: GB231.1, U5803.18 (Y0)
F.ADR.NAME9: GB228.1, U5803.16 (Y1)
F.ADR.NAME10: GB227.1, U5803.14 (Y2)
F.ADR.NAME11: GB225.1, U5803.12 (Y3)
F.ADR.NAME12: GB224.1, U5803.9 (Y4)
F.ADR.NAME13: GB223.1, U5803.7 (Y5)
F.ADR.NAME14: GB221.1, U5803.5 (Y6)
F.ADR.NAME15: GB218.1, U5803.3 (Y7)
F.ADR.NAME16: GB204.1, U5804.18 (Y0)
F.ADR.NAME17: GB203.1, U5804.16 (Y1)
F.ADR.NAME18: GB201.1, U5804.14 (Y2)
F.ADR.NAME19: GB198.1, U5804.12 (Y3)
F.ADR.NAME20: GB197.1, U5804.9 (Y4)
F.ADR.NAME21: GB195.1, U5804.7 (Y5)
F.ADR.NAME22: GB194.1, U5804.5 (Y6)
F.ADR.NAME23: GB193.1, U5804.3 (Y7)
F.ADR.NAME24: GB177.1, U5805.18 (Y0)
F.ADR.NAME25: GB175.1, U5805.16 (Y1)
F.ADR.NAME26: GB174.1, U5805.14 (Y2)
F.ADR.NAME27: GB173.1, U5805.12 (Y3)
F.ADR.NAME28: GB171.1, U5805.9 (Y4)
F.ADR.NAME29: GB168.1, U5805.7 (Y5)
F.ADR.NAME30: GB167.1, U5805.5 (Y6)
F.ADR.NAME31: GB165.1, U5805.3 (Y7)
F.ADR.OFFS0: GB105.1, U5806.9 (Y4)
F.ADR.OFFS1: GB104.1, U5806.7 (Y5)
F.ADR.OFFS2: GB102.1, U5806.5 (Y6)
F.ADR.OFFS3: GB101.1, U5806.3 (Y7)
F.ADR.OFFS4: GB98.1, U5806.18 (Y0)
F.ADR.OFFS5: GB96.1, U5806.16 (Y1)
F.ADR.OFFS6: GB95.1, U5806.14 (Y2)
F.ADR.OFFS7: GB94.1, U5806.12 (Y3)
F.ADR.OFFS8: GB78.1, U5807.9 (Y4)
F.ADR.OFFS9: GB76.1, U5807.7 (Y5)
F.ADR.OFFS10: GB75.1, U5807.5 (Y6)
F.ADR.OFFS11: GB74.1, U5807.3 (Y7)
F.ADR.OFFS12: GB72.1, U5807.18 (Y0)
F.ADR.OFFS13: GB71.1, U5807.16 (Y1)
F.ADR.OFFS14: GB68.1, U5807.14 (Y2)
F.ADR.OFFS15: GB66.1, U5807.12 (Y3)
F.ADR.OFFS16: GB52.1, U5808.9 (Y4)
F.ADR.OFFS17: GB51.1, U5808.7 (Y5)
F.ADR.OFFS18: GB48.1, U5808.5 (Y6)
F.ADR.OFFS19: GB46.1, U5808.3 (Y7)
F.ADR.OFFS20: GB45.1, U5808.18 (Y0)
F.ADR.OFFS21: GB44.1, U5808.16 (Y1)
F.ADR.OFFS22: GB42.1, U5808.14 (Y2)
F.ADR.OFFS23: GB41.1, U5808.12 (Y3)
F.ADR.OFFS24: GB25.1, U5809.9 (Y4)
F.ADR.OFFS25: GB24.1, U5809.7 (Y5)
F.ADR.OFFS26: GB22.1, U5809.5 (Y6)
F.ADR.OFFS27: GB21.1, U5809.3 (Y7)
F.ADR.OFFS28: GB18.1, U5809.18 (Y0)
F.ADR.OFFS29: GB16.1, U5809.16 (Y1)
F.ADR.OFFS30: GB15.1, U5809.14 (Y2)
F.ADR.OFFS31: GB14.1, U5809.12 (Y3)
F.ADR.P0: GB161.1
F.ADR.P1: GB158.1
F.ADR.P2: GB157.1
F.ADR.P3: GB155.1
F.ADR.P4: GB154.1
F.ADR.P5: GB153.1
F.ADR.P6: GB147.1
F.ADR.P7: GB146.1
F.ADR.P8: GB145.1
F.ADR.SPACE0: GB31.1, U5801.18 (Y0)
F.ADR.SPACE1: GB28.1, U5801.16 (Y1)
F.ADR.SPACE2: GB26.1, U5801.14 (Y2)
FIU_A.OE~: U5801.1 (OE0), U5802.1 (OE0), U5802.19 (OE1), U5803.1 (OE0), U5803.19 (OE1), U5804.1 (OE0), U5804.19 (OE1), U5805.1 (OE0), U5805.19 (OE1), U5806.1 (OE0), U5806.19 (OE1), U5807.1 (OE0), U5807.19 (OE1), U5808.1 (OE0), U5808.19 (OE1), U5809.1 (OE0), U5809.19 (OE1)
INC_OFFS20: U5808.2 (I0)
INC_OFFS21: U5808.4 (I1)
INC_OFFS22: U5808.6 (I2)
INC_OFFS23: U5808.8 (I3)
INC_OFFS24: U5809.11 (I4)
MAR.NAME0: U5802.2 (I0)
MAR.NAME1: U5802.4 (I1)
MAR.NAME2: U5802.6 (I2)
MAR.NAME3: U5802.8 (I3)
MAR.NAME4: U5802.11 (I4)
MAR.NAME5: U5802.13 (I5)
MAR.NAME6: U5802.15 (I6)
MAR.NAME7: U5802.17 (I7)
MAR.NAME8: U5803.2 (I0)
MAR.NAME9: U5803.4 (I1)
MAR.NAME10: U5803.6 (I2)
MAR.NAME11: U5803.8 (I3)
MAR.NAME12: U5803.11 (I4)
MAR.NAME13: U5803.13 (I5)
MAR.NAME14: U5803.15 (I6)
MAR.NAME15: U5803.17 (I7)
MAR.NAME16: U5804.2 (I0)
MAR.NAME17: U5804.4 (I1)
MAR.NAME18: U5804.6 (I2)
MAR.NAME19: U5804.8 (I3)
MAR.NAME20: U5804.11 (I4)
MAR.NAME21: U5804.13 (I5)
MAR.NAME22: U5804.15 (I6)
MAR.NAME23: U5804.17 (I7)
MAR.NAME24: U5805.2 (I0)
MAR.NAME25: U5805.4 (I1)
MAR.NAME26: U5805.6 (I2)
MAR.NAME27: U5805.8 (I3)
MAR.NAME28: U5805.11 (I4)
MAR.NAME29: U5805.13 (I5)
MAR.NAME30: U5805.15 (I6)
MAR.NAME31: U5805.17 (I7)
MAR.OFFS0: U5806.11 (I4)
MAR.OFFS1: U5806.13 (I5)
MAR.OFFS2: U5806.15 (I6)
MAR.OFFS3: U5806.17 (I7)
MAR.OFFS4: U5806.2 (I0)
MAR.OFFS5: U5806.4 (I1)
MAR.OFFS6: U5806.6 (I2)
MAR.OFFS7: U5806.8 (I3)
MAR.OFFS8: U5807.11 (I4)
MAR.OFFS9: U5807.13 (I5)
MAR.OFFS10: U5807.15 (I6)
MAR.OFFS11: U5807.17 (I7)
MAR.OFFS12: U5807.2 (I0)
MAR.OFFS13: U5807.4 (I1)
MAR.OFFS14: U5807.6 (I2)
MAR.OFFS15: U5807.8 (I3)
MAR.OFFS16: U5808.11 (I4)
MAR.OFFS17: U5808.13 (I5)
MAR.OFFS18: U5808.15 (I6)
MAR.OFFS19: U5808.17 (I7)
MAR.SPACE0: U5801.2 (I0)
MAR.SPACE1: U5801.4 (I1)
MAR.SPACE2: U5801.6 (I2)
OREGO0: U5809.13 (I5)
OREGO1: U5809.15 (I6)
OREGO2: U5809.17 (I7)
OREGO3: U5809.2 (I0)
OREGO4: U5809.4 (I1)
OREGO5: U5809.6 (I2)
OREGO6: U5809.8 (I3)
