Datamuseum-DK/R1000.HwDoc/Schematics/FIU/pg_58.kicad_sch

## KiCad design Schematics/FIU/pg_58.kicad_sch (2023-01-10)

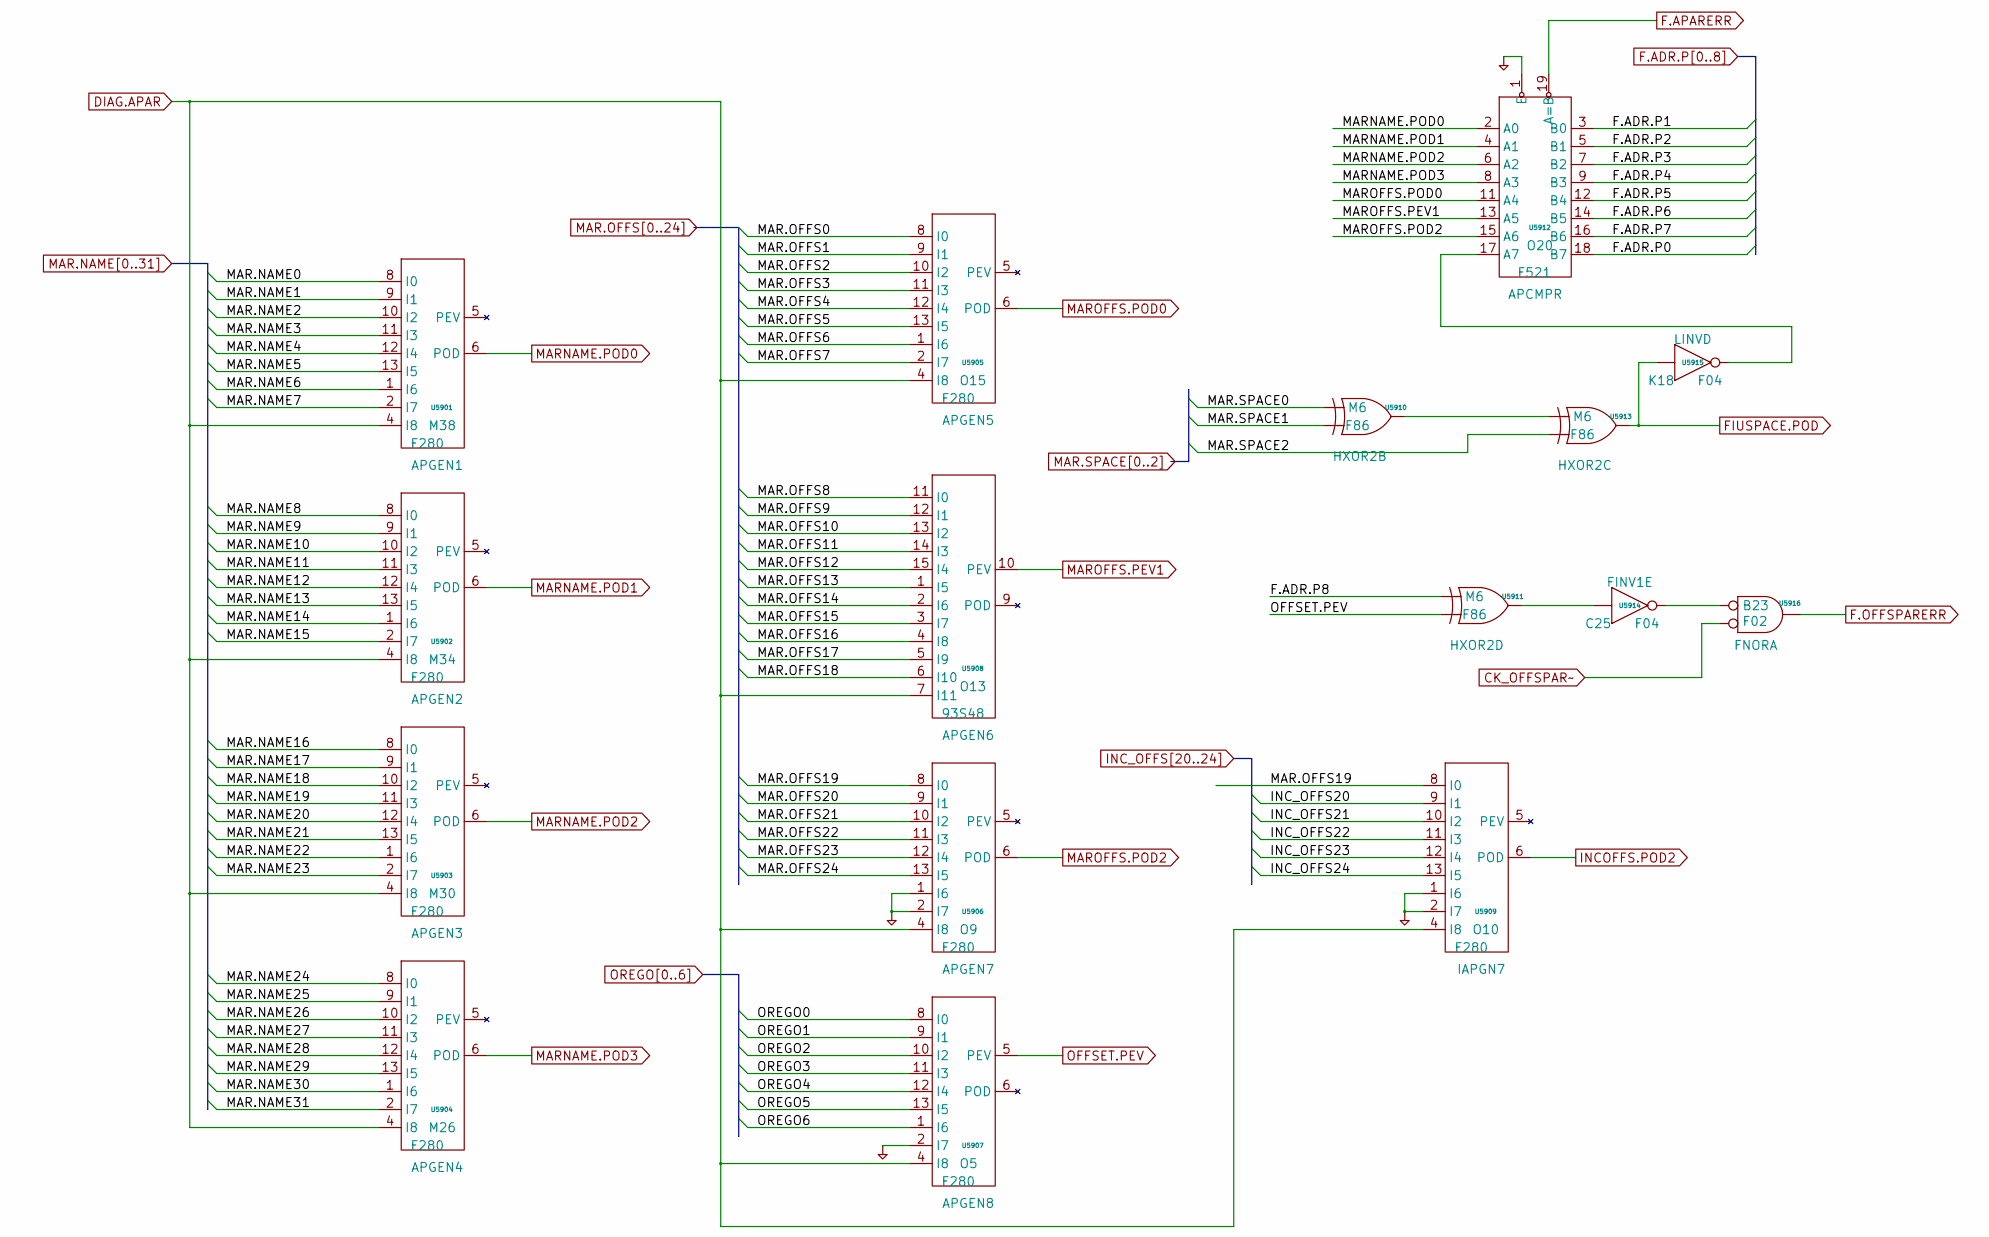
[picture p341: schematic pg_58.kicad_sch]

Parts:
U5901, U5902, U5903, U5904, U5905, U5906, U5907, U5909: F280
U5908: 93S48
U5910, U5911, U5913: F86
U5912: F521
U5914, U5915: F04
U5916: F02

Connections:
CK_OFFSPAR~: U5916.2 (D1)
DIAG.APAR: U5901.4 (I8), U5902.4 (I8), U5903.4 (I8), U5904.4 (I8), U5905.4 (I8), U5906.4 (I8), U5907.4 (I8), U5908.7 (I11), U5909.4 (I8)
F.ADR.P0: U5912.18 (B7)
F.ADR.P1: U5912.3 (B0)
F.ADR.P2: U5912.5 (B1)
F.ADR.P3: U5912.7 (B2)
F.ADR.P4: U5912.9 (B3)
F.ADR.P5: U5912.12 (B4)
F.ADR.P6: U5912.14 (B5)
F.ADR.P7: U5912.16 (B6)
F.ADR.P8: U5911.1 (D0)
F.APARERR: U5912.19 (A=B)
F.OFFSPARERR: U5916.3 (Q)
FIUSPACE.POD: U5913.3 (Q), U5915.1 (D0)
INCOFFS.POD2: U5909.6 (POD)
INC_OFFS20: U5909.9 (I1)
INC_OFFS21: U5909.10 (I2)
INC_OFFS22: U5909.11 (I3)
INC_OFFS23: U5909.12 (I4)
INC_OFFS24: U5909.13 (I5)
MAR.NAME0: U5901.8 (I0)
MAR.NAME1: U5901.9 (I1)
MAR.NAME2: U5901.10 (I2)
MAR.NAME3: U5901.11 (I3)
MAR.NAME4: U5901.12 (I4)
MAR.NAME5: U5901.13 (I5)
MAR.NAME6: U5901.1 (I6)
MAR.NAME7: U5901.2 (I7)
MAR.NAME8: U5902.8 (I0)
MAR.NAME9: U5902.9 (I1)
MAR.NAME10: U5902.10 (I2)
MAR.NAME11: U5902.11 (I3)
MAR.NAME12: U5902.12 (I4)
MAR.NAME13: U5902.13 (I5)
MAR.NAME14: U5902.1 (I6)
MAR.NAME15: U5902.2 (I7)
MAR.NAME16: U5903.8 (I0)
MAR.NAME17: U5903.9 (I1)
MAR.NAME18: U5903.10 (I2)
MAR.NAME19: U5903.11 (I3)
MAR.NAME20: U5903.12 (I4)
MAR.NAME21: U5903.13 (I5)
MAR.NAME22: U5903.1 (I6)
MAR.NAME23: U5903.2 (I7)
MAR.NAME24: U5904.8 (I0)
MAR.NAME25: U5904.9 (I1)
MAR.NAME26: U5904.10 (I2)
MAR.NAME27: U5904.11 (I3)
MAR.NAME28: U5904.12 (I4)
MAR.NAME29: U5904.13 (I5)
MAR.NAME30: U5904.1 (I6)
MAR.NAME31: U5904.2 (I7)
MAR.OFFS0: U5905.8 (I0)
MAR.OFFS1: U5905.9 (I1)
MAR.OFFS2: U5905.10 (I2)
MAR.OFFS3: U5905.11 (I3)
MAR.OFFS4: U5905.12 (I4)
MAR.OFFS5: U5905.13 (I5)
MAR.OFFS6: U5905.1 (I6)
MAR.OFFS7: U5905.2 (I7)
MAR.OFFS8: U5908.11 (I0)
MAR.OFFS9: U5908.12 (I1)
MAR.OFFS10: U5908.13 (I2)
MAR.OFFS11: U5908.14 (I3)
MAR.OFFS12: U5908.15 (I4)
MAR.OFFS13: U5908.1 (I5)
MAR.OFFS14: U5908.2 (I6)
MAR.OFFS15: U5908.3 (I7)
MAR.OFFS16: U5908.4 (I8)
MAR.OFFS17: U5908.5 (I9)
MAR.OFFS18: U5908.6 (I10)
MAR.OFFS19: U5906.8 (I0), U5909.8 (I0)
MAR.OFFS20: U5906.9 (I1)
MAR.OFFS21: U5906.10 (I2)
MAR.OFFS22: U5906.11 (I3)
MAR.OFFS23: U5906.12 (I4)
MAR.OFFS24: U5906.13 (I5)
MAR.SPACE0: U5910.1 (D0)
MAR.SPACE1: U5910.2 (D1)
MAR.SPACE2: U5913.2 (D1)
MARNAME.POD0: U5901.6 (POD), U5912.2 (A0)
MARNAME.POD1: U5902.6 (POD), U5912.4 (A1)
MARNAME.POD2: U5903.6 (POD), U5912.6 (A2)
MARNAME.POD3: U5904.6 (POD), U5912.8 (A3)
MAROFFS.PEV1: U5908.10 (PEV), U5912.13 (A5)
MAROFFS.POD0: U5905.6 (POD), U5912.11 (A4)
MAROFFS.POD2: U5906.6 (POD), U5912.15 (A6)
unnamed: U5910.3 (Q), U5913.1 (D0)
unnamed: U5911.3 (Q), U5914.1 (D0)
unnamed: U5912.17 (A7), U5915.2 (Q)
unnamed: U5914.2 (Q), U5916.1 (D0)
OFFSET.PEV: U5907.5 (PEV), U5911.2 (D1)
OREGO0: U5907.8 (I0)
OREGO1: U5907.9 (I1)
OREGO2: U5907.10 (I2)
OREGO3: U5907.11 (I3)
OREGO4: U5907.12 (I4)
OREGO5: U5907.13 (I5)
OREGO6: U5907.1 (I6)
PD: U5906.1 (I6), U5906.2 (I7), U5907.2 (I7), U5909.1 (I6), U5909.2 (I7), U5912.1 (E)
