Datamuseum-DK/R1000.HwDoc/Schematics/FIU/pg_59.kicad_sch

## KiCad design Schematics/FIU/pg_59.kicad_sch (2023-01-10)

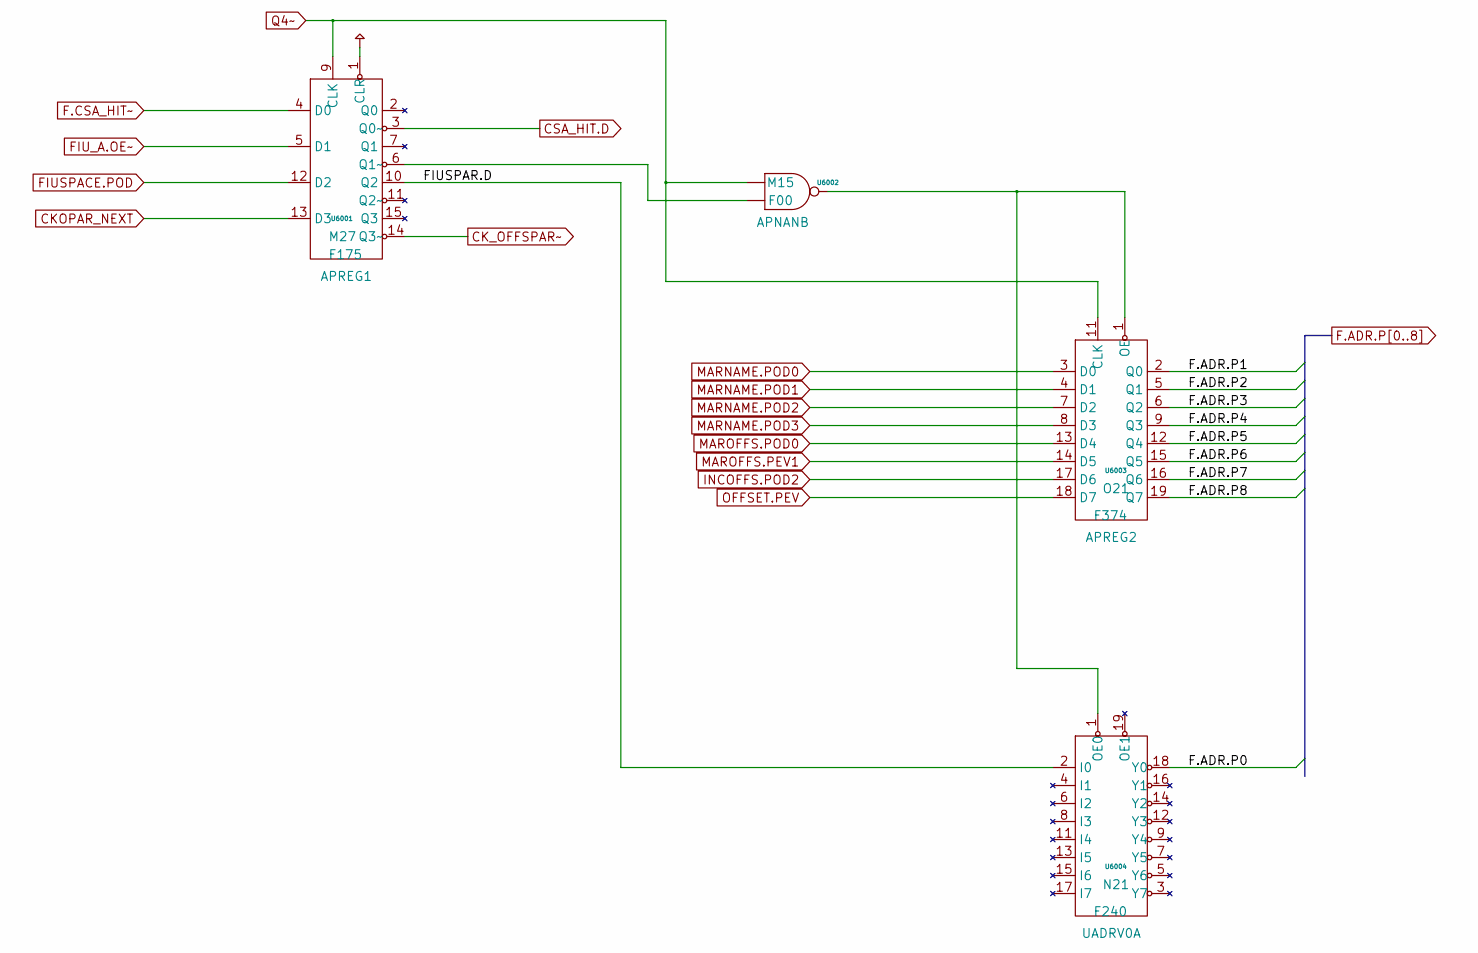
[picture p342: schematic pg_59.kicad_sch]

Parts:
U6001: F175
U6002: F00
U6003: F374
U6004: F240

Connections:
CKOPAR_NEXT: U6001.13 (D3)
CK_OFFSPAR~: U6001.14 (Q3~)
CSA_HIT.D: U6001.3 (Q0~)
F.ADR.P0: U6004.18 (Y0)
F.ADR.P1: U6003.2 (Q0)
F.ADR.P2: U6003.5 (Q1)
F.ADR.P3: U6003.6 (Q2)
F.ADR.P4: U6003.9 (Q3)
F.ADR.P5: U6003.12 (Q4)
F.ADR.P6: U6003.15 (Q5)
F.ADR.P7: U6003.16 (Q6)
F.ADR.P8: U6003.19 (Q7)
F.CSA_HIT~: U6001.4 (D0)
FIUSPACE.POD: U6001.12 (D2)
FIUSPAR.D: U6001.10 (Q2), U6004.2 (I0)
FIU_A.OE~: U6001.5 (D1)
INCOFFS.POD2: U6003.17 (D6)
MARNAME.POD0: U6003.3 (D0)
MARNAME.POD1: U6003.4 (D1)
MARNAME.POD2: U6003.7 (D2)
MARNAME.POD3: U6003.8 (D3)
MAROFFS.PEV1: U6003.14 (D5)
MAROFFS.POD0: U6003.13 (D4)
unnamed: U6001.6 (Q1~), U6002.2 (D1)
unnamed: U6002.3 (Q), U6003.1 (OE), U6004.1 (OE0)
OFFSET.PEV: U6003.18 (D7)
PU: U6001.1 (CLR)
Q4~: U6001.9 (CLK), U6002.1 (D0), U6003.11 (CLK)
