Datamuseum-DK/R1000.HwDoc/Schematics/FIU/pg_60.kicad_sch

## KiCad design Schematics/FIU/pg_60.kicad_sch (2023-01-10)

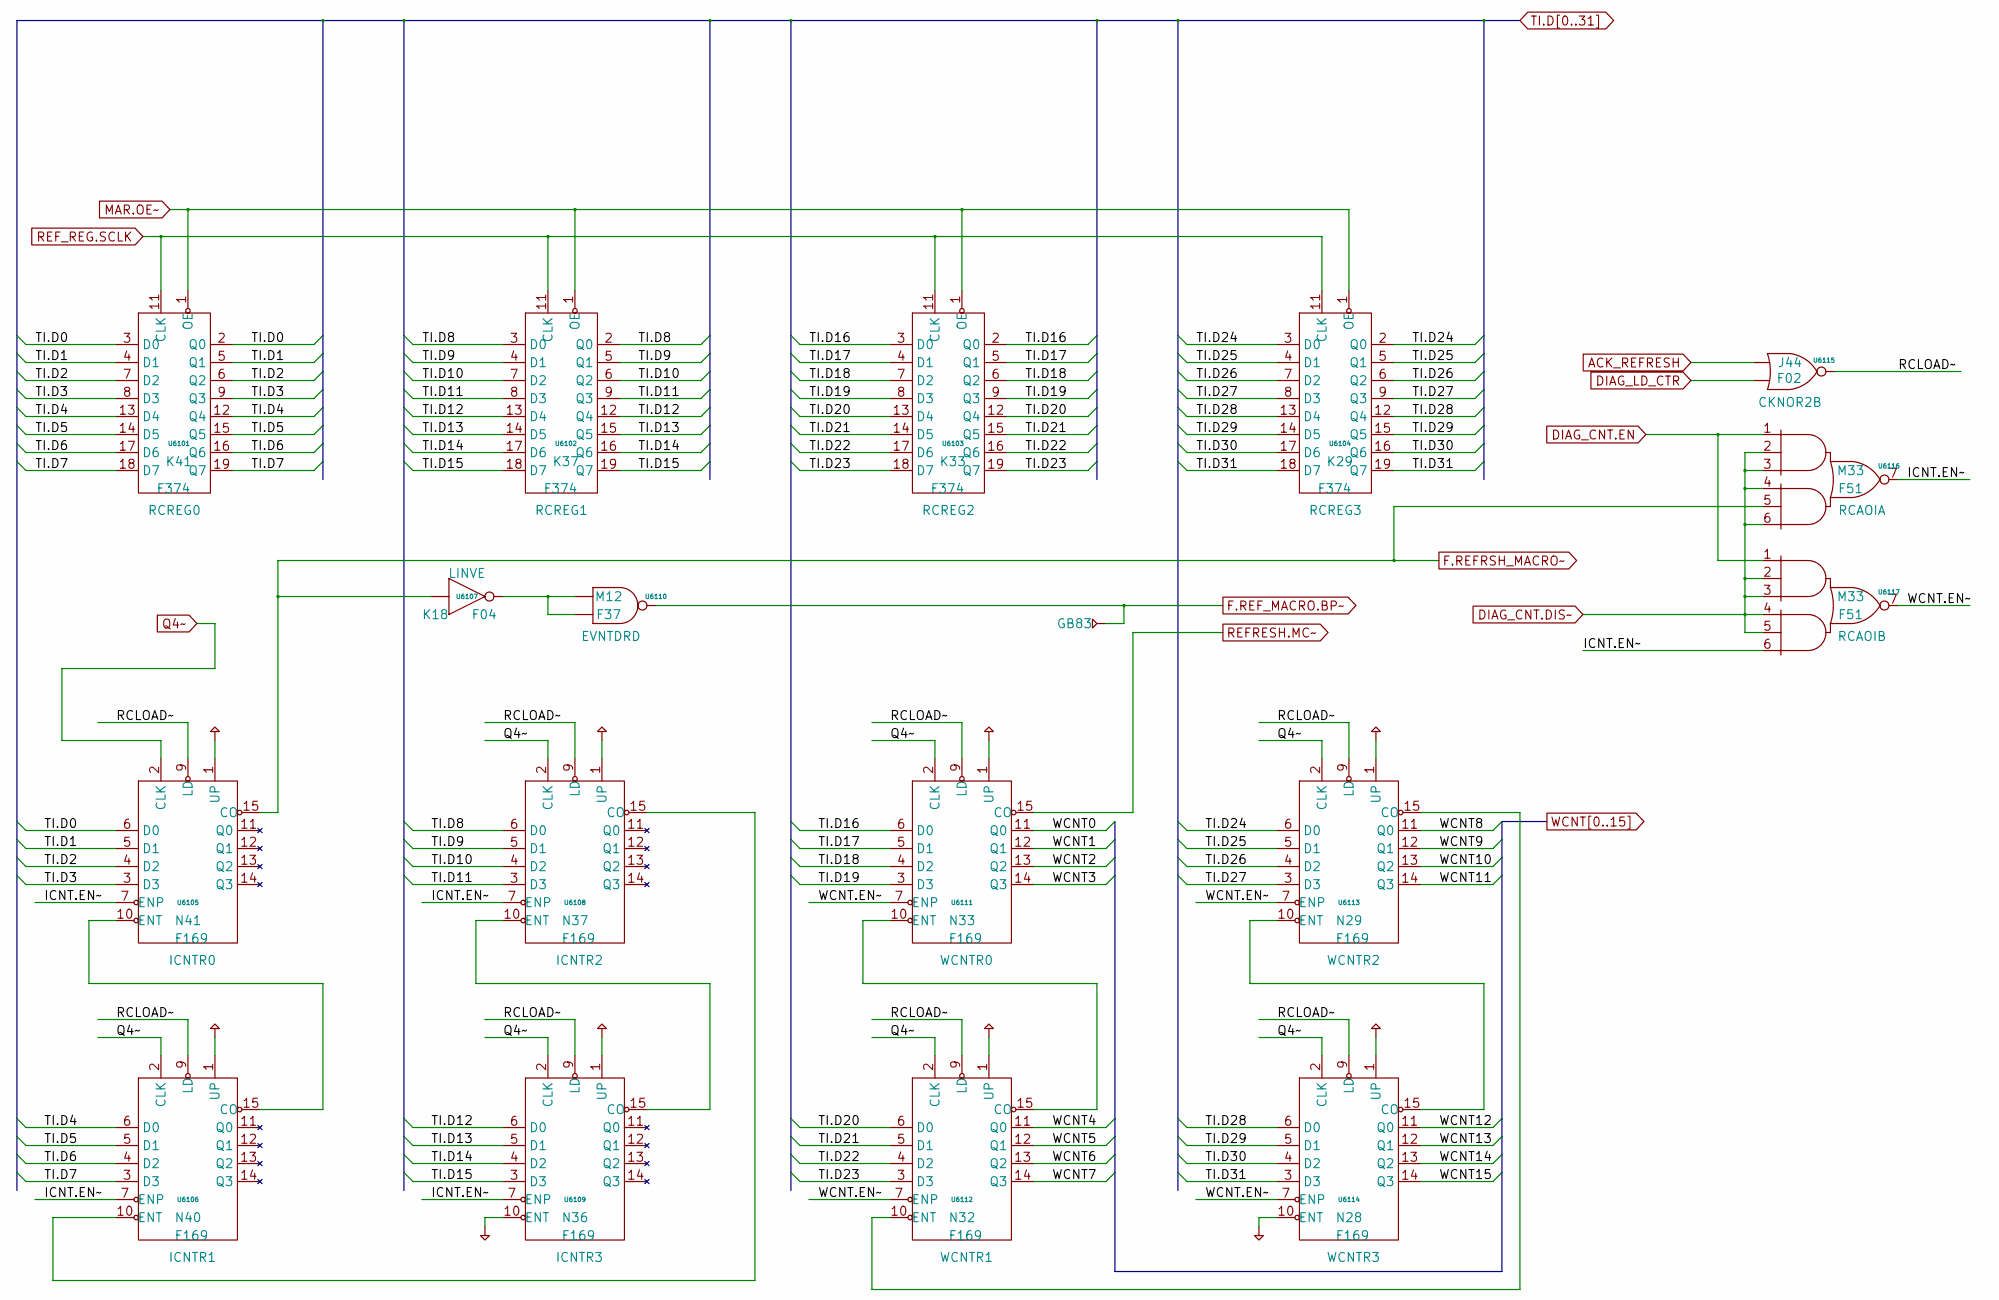
[picture p343: schematic pg_60.kicad_sch]

Parts:
GB83: GB
U6101, U6102, U6103, U6104: F374
U6105, U6106, U6108, U6109, U6111, U6112, U6113, U6114: F169
U6107: F04
U6110: F37
U6115: F02
U6116, U6117: F51

Connections:
ACK_REFRESH: U6115.1 (D0)
DIAG_CNT.DIS~: U6116.2 (A2), U6116.3 (A3), U6116.4 (B1), U6116.6 (B3), U6117.2 (A2), U6117.3 (A3), U6117.4 (B1), U6117.5 (B2)
DIAG_CNT.EN: U6116.1 (A1), U6117.1 (A1)
DIAG_LD_CTR: U6115.2 (D1)
F.REFRSH_MACRO~: U6105.15 (CO), U6107.1 (D0), U6116.5 (B2)
F.REF_MACRO.BP~: GB83.1, U6110.3 (Q)
ICNT.EN~: U6105.7 (ENP), U6106.7 (ENP), U6108.7 (ENP), U6109.7 (ENP), U6116.7 (Q), U6117.6 (B3)
MAR.OE~: U6101.1 (OE), U6102.1 (OE), U6103.1 (OE), U6104.1 (OE)
unnamed: U6105.10 (ENT), U6106.15 (CO)
unnamed: U6106.10 (ENT), U6108.15 (CO)
unnamed: U6107.2 (Q), U6110.1 (D0), U6110.2 (D1)
unnamed: U6108.10 (ENT), U6109.15 (CO)
unnamed: U6111.10 (ENT), U6112.15 (CO)
unnamed: U6112.10 (ENT), U6113.15 (CO)
unnamed: U6113.10 (ENT), U6114.15 (CO)
PD: U6109.10 (ENT), U6114.10 (ENT)
PU: U6105.1 (UP), U6106.1 (UP), U6108.1 (UP), U6109.1 (UP), U6111.1 (UP), U6112.1 (UP), U6113.1 (UP), U6114.1 (UP)
Q4~: U6105.2 (CLK), U6106.2 (CLK), U6108.2 (CLK), U6109.2 (CLK), U6111.2 (CLK), U6112.2 (CLK), U6113.2 (CLK), U6114.2 (CLK)
RCLOAD~: U6105.9 (LD), U6106.9 (LD), U6108.9 (LD), U6109.9 (LD), U6111.9 (LD), U6112.9 (LD), U6113.9 (LD), U6114.9 (LD), U6115.3 (Q)
REFRESH.MC~: U6111.15 (CO)
REF_REG.SCLK: U6101.11 (CLK), U6102.11 (CLK), U6103.11 (CLK), U6104.11 (CLK)
TI.D0: U6101.2 (Q0), U6101.3 (D0), U6105.6 (D0)
TI.D1: U6101.4 (D1), U6101.5 (Q1), U6105.5 (D1)
TI.D2: U6101.6 (Q2), U6101.7 (D2), U6105.4 (D2)
TI.D3: U6101.8 (D3), U6101.9 (Q3), U6105.3 (D3)
TI.D4: U6101.12 (Q4), U6101.13 (D4), U6106.6 (D0)
TI.D5: U6101.14 (D5), U6101.15 (Q5), U6106.5 (D1)
TI.D6: U6101.16 (Q6), U6101.17 (D6), U6106.4 (D2)
TI.D7: U6101.18 (D7), U6101.19 (Q7), U6106.3 (D3)
TI.D8: U6102.2 (Q0), U6102.3 (D0), U6108.6 (D0)
TI.D9: U6102.4 (D1), U6102.5 (Q1), U6108.5 (D1)
TI.D10: U6102.6 (Q2), U6102.7 (D2), U6108.4 (D2)
TI.D11: U6102.8 (D3), U6102.9 (Q3), U6108.3 (D3)
TI.D12: U6102.12 (Q4), U6102.13 (D4), U6109.6 (D0)
TI.D13: U6102.14 (D5), U6102.15 (Q5), U6109.5 (D1)
TI.D14: U6102.16 (Q6), U6102.17 (D6), U6109.4 (D2)
TI.D15: U6102.18 (D7), U6102.19 (Q7), U6109.3 (D3)
TI.D16: U6103.2 (Q0), U6103.3 (D0), U6111.6 (D0)
TI.D17: U6103.4 (D1), U6103.5 (Q1), U6111.5 (D1)
TI.D18: U6103.6 (Q2), U6103.7 (D2), U6111.4 (D2)
TI.D19: U6103.8 (D3), U6103.9 (Q3), U6111.3 (D3)
TI.D20: U6103.12 (Q4), U6103.13 (D4), U6112.6 (D0)
TI.D21: U6103.14 (D5), U6103.15 (Q5), U6112.5 (D1)
TI.D22: U6103.16 (Q6), U6103.17 (D6), U6112.4 (D2)
TI.D23: U6103.18 (D7), U6103.19 (Q7), U6112.3 (D3)
TI.D24: U6104.2 (Q0), U6104.3 (D0), U6113.6 (D0)
TI.D25: U6104.4 (D1), U6104.5 (Q1), U6113.5 (D1)
TI.D26: U6104.6 (Q2), U6104.7 (D2), U6113.4 (D2)
TI.D27: U6104.8 (D3), U6104.9 (Q3), U6113.3 (D3)
TI.D28: U6104.12 (Q4), U6104.13 (D4), U6114.6 (D0)
TI.D29: U6104.14 (D5), U6104.15 (Q5), U6114.5 (D1)
TI.D30: U6104.16 (Q6), U6104.17 (D6), U6114.4 (D2)
TI.D31: U6104.18 (D7), U6104.19 (Q7), U6114.3 (D3)
WCNT0: U6111.11 (Q0)
WCNT1: U6111.12 (Q1)
WCNT2: U6111.13 (Q2)
WCNT3: U6111.14 (Q3)
WCNT4: U6112.11 (Q0)
WCNT5: U6112.12 (Q1)
WCNT6: U6112.13 (Q2)
WCNT7: U6112.14 (Q3)
WCNT8: U6113.11 (Q0)
WCNT9: U6113.12 (Q1)
WCNT10: U6113.13 (Q2)
WCNT11: U6113.14 (Q3)
WCNT12: U6114.11 (Q0)
WCNT13: U6114.12 (Q1)
WCNT14: U6114.13 (Q2)
WCNT15: U6114.14 (Q3)
WCNT.EN~: U6111.7 (ENP), U6112.7 (ENP), U6113.7 (ENP), U6114.7 (ENP), U6117.7 (Q)
