Datamuseum-DK/R1000.HwDoc/Schematics/FIU/pg_61.kicad_sch

## KiCad design Schematics/FIU/pg_61.kicad_sch (2023-01-10)

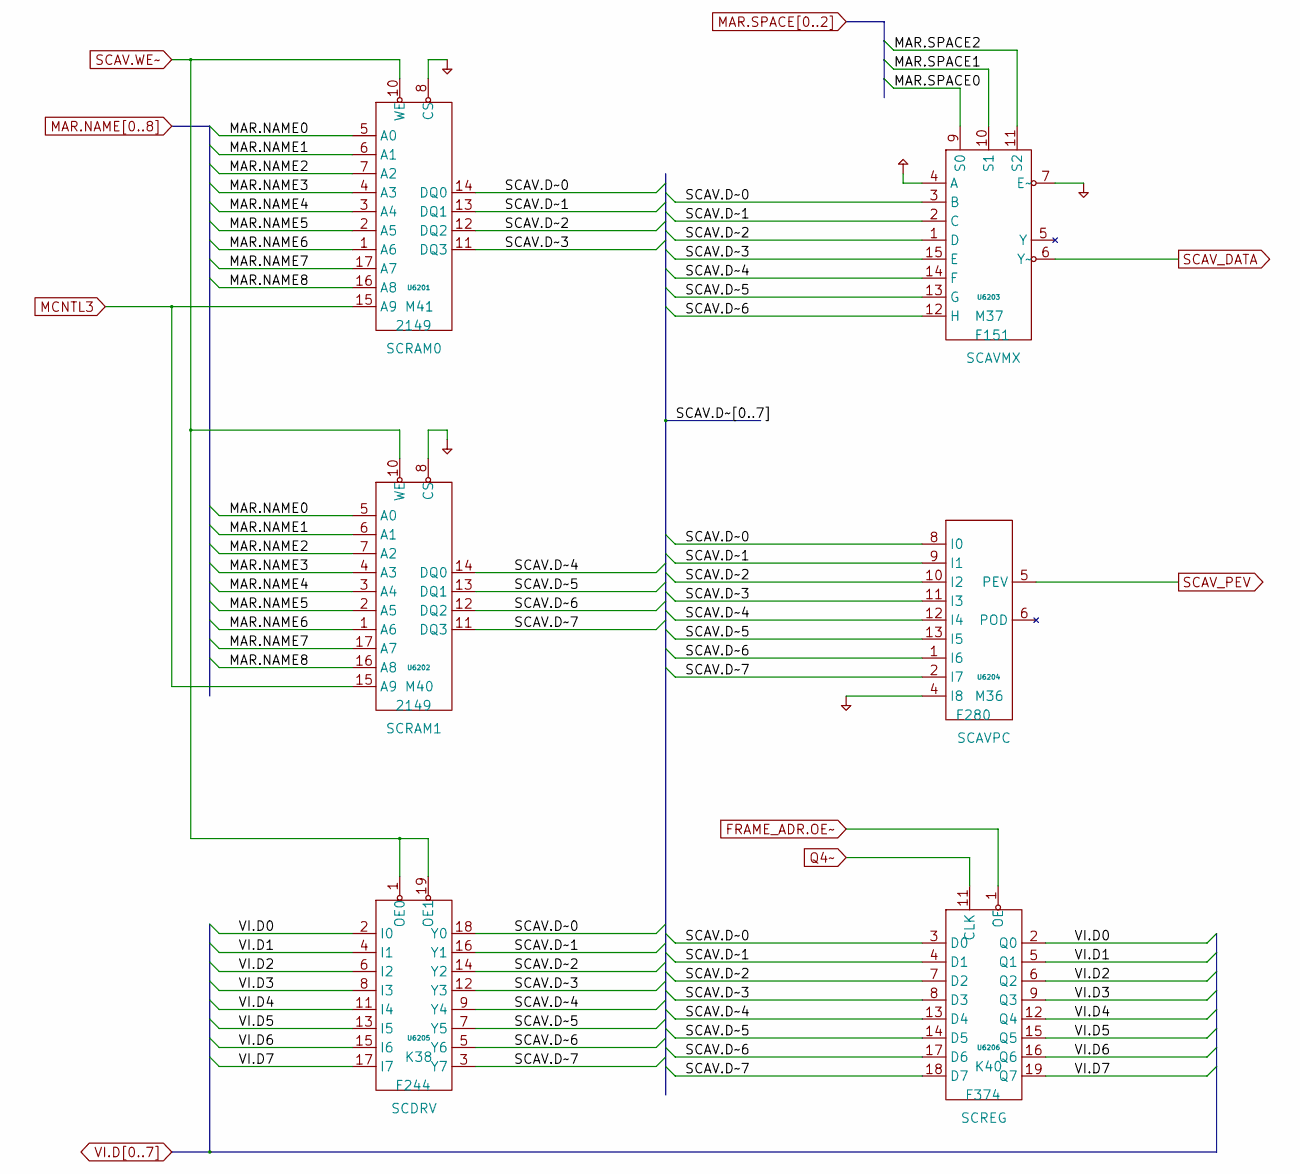
[picture p344: schematic pg_61.kicad_sch]

Parts:
U6201, U6202: 2149
U6203: F151
U6204: F280
U6205: F244
U6206: F374

Connections:
FRAME_ADR.OE~: U6206.1 (OE)
MAR.NAME0: U6201.5 (A0), U6202.5 (A0)
MAR.NAME1: U6201.6 (A1), U6202.6 (A1)
MAR.NAME2: U6201.7 (A2), U6202.7 (A2)
MAR.NAME3: U6201.4 (A3), U6202.4 (A3)
MAR.NAME4: U6201.3 (A4), U6202.3 (A4)
MAR.NAME5: U6201.2 (A5), U6202.2 (A5)
MAR.NAME6: U6201.1 (A6), U6202.1 (A6)
MAR.NAME7: U6201.17 (A7), U6202.17 (A7)
MAR.NAME8: U6201.16 (A8), U6202.16 (A8)
MAR.SPACE0: U6203.9 (S0)
MAR.SPACE1: U6203.10 (S1)
MAR.SPACE2: U6203.11 (S2)
MCNTL3: U6201.15 (A9), U6202.15 (A9)
PD: U6201.8 (CS), U6202.8 (CS), U6203.7 (E~), U6204.4 (I8)
PU: U6203.4 (A)
Q4~: U6206.11 (CLK)
SCAV.D~0: U6201.14 (DQ0), U6203.3 (B), U6204.8 (I0), U6205.18 (Y0), U6206.3 (D0)
SCAV.D~1: U6201.13 (DQ1), U6203.2 (C), U6204.9 (I1), U6205.16 (Y1), U6206.4 (D1)
SCAV.D~2: U6201.12 (DQ2), U6203.1 (D), U6204.10 (I2), U6205.14 (Y2), U6206.7 (D2)
SCAV.D~3: U6201.11 (DQ3), U6203.15 (E), U6204.11 (I3), U6205.12 (Y3), U6206.8 (D3)
SCAV.D~4: U6202.14 (DQ0), U6203.14 (F), U6204.12 (I4), U6205.9 (Y4), U6206.13 (D4)
SCAV.D~5: U6202.13 (DQ1), U6203.13 (G), U6204.13 (I5), U6205.7 (Y5), U6206.14 (D5)
SCAV.D~6: U6202.12 (DQ2), U6203.12 (H), U6204.1 (I6), U6205.5 (Y6), U6206.17 (D6)
SCAV.D~7: U6202.11 (DQ3), U6204.2 (I7), U6205.3 (Y7), U6206.18 (D7)
SCAV.WE~: U6201.10 (WE), U6202.10 (WE), U6205.1 (OE0), U6205.19 (OE1)
SCAV_DATA: U6203.6 (Y~)
SCAV_PEV: U6204.5 (PEV)
VI.D0: U6205.2 (I0), U6206.2 (Q0)
VI.D1: U6205.4 (I1), U6206.5 (Q1)
VI.D2: U6205.6 (I2), U6206.6 (Q2)
VI.D3: U6205.8 (I3), U6206.9 (Q3)
VI.D4: U6205.11 (I4), U6206.12 (Q4)
VI.D5: U6205.13 (I5), U6206.15 (Q5)
VI.D6: U6205.15 (I6), U6206.16 (Q6)
VI.D7: U6205.17 (I7), U6206.19 (Q7)
