Datamuseum-DK/R1000.HwDoc/Schematics/FIU/pg_62.kicad_sch

## KiCad design Schematics/FIU/pg_62.kicad_sch (2023-01-10)

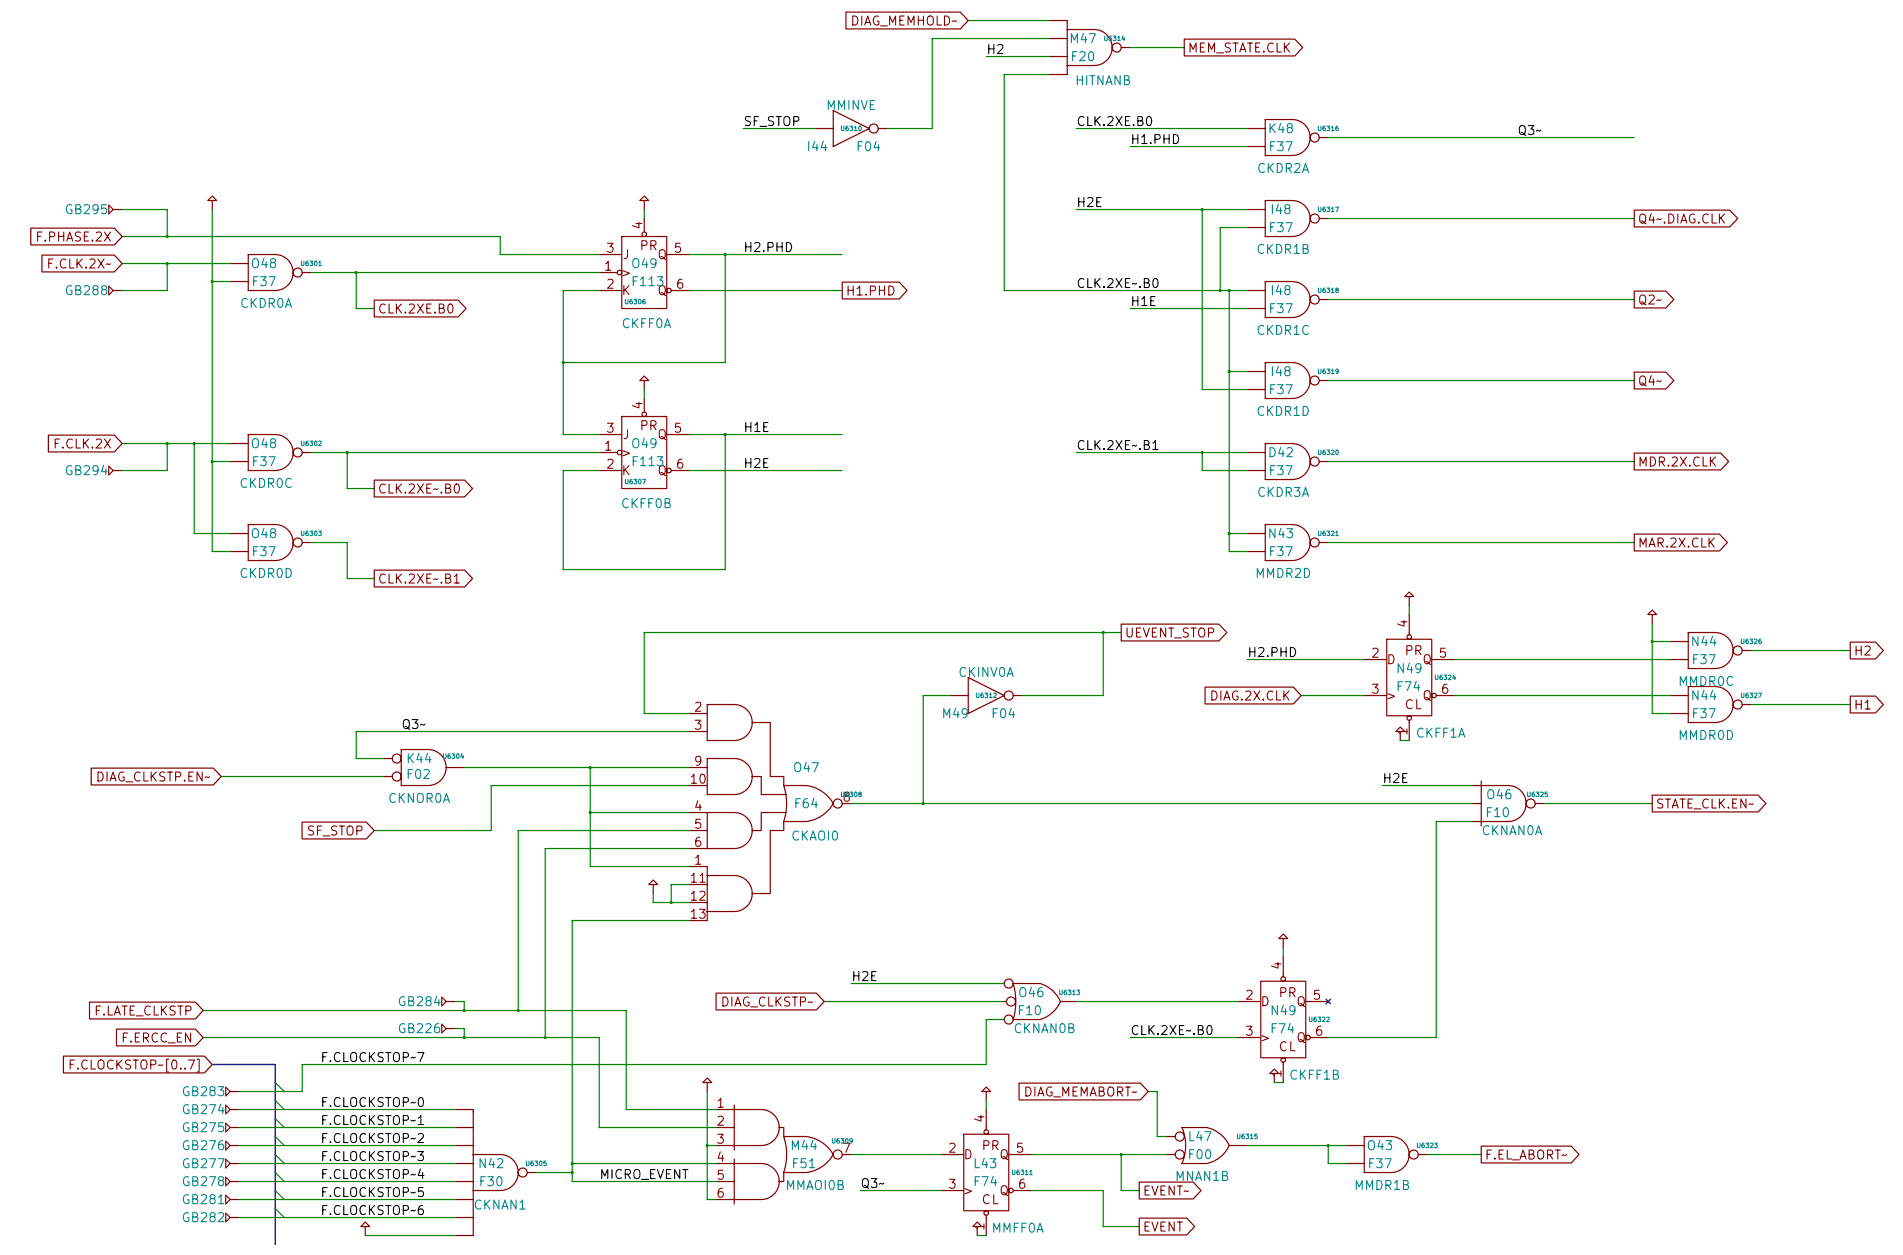
[picture p345: schematic pg_62.kicad_sch]

Parts:
GB226, GB274, GB275, GB276, GB277, GB278, GB281, GB282, GB283, GB284, GB288, GB294, GB295: GB
U6301, U6302, U6303, U6316, U6317, U6318, U6319, U6320, U6321, U6323, U6326, U6327: F37
U6304: F02
U6305: F30
U6306, U6307: F113
U6308: F64
U6309: F51
U6310, U6312: F04
U6311, U6322, U6324: F74
U6313, U6325: F10
U6314: F20
U6315: F00

Connections:
CLK.2XE.B0: U6301.3 (Q), U6306.1 (CLK_), U6316.1 (D0)
CLK.2XE~.B0: U6302.3 (Q), U6307.1 (CLK_), U6314.5 (D3), U6317.2 (D1), U6318.1 (D0), U6319.1 (D0), U6321.1 (D0), U6321.2 (D1), U6322.3 (CLK)
CLK.2XE~.B1: U6303.3 (Q), U6320.1 (D0), U6320.2 (D1)
DIAG.2X.CLK: U6324.3 (CLK)
DIAG_CLKSTP.EN~: U6304.2 (D1)
DIAG_CLKSTP~: U6313.2 (D1)
DIAG_MEMABORT~: U6315.1 (D0)
DIAG_MEMHOLD~: U6314.1 (D0)
EVENT: U6311.6 (Q_)
EVENT~: U6311.5 (Q), U6315.2 (D1)
F.CLK.2X: GB294.1, U6302.1 (D0), U6303.1 (D0)
F.CLK.2X~: GB288.1, U6301.1 (D0)
F.CLOCKSTOP~0: GB274.1, U6305.11 (D0)
F.CLOCKSTOP~1: GB275.1, U6305.12 (D1)
F.CLOCKSTOP~2: GB276.1, U6305.1 (D2)
F.CLOCKSTOP~3: GB277.1, U6305.2 (D3)
F.CLOCKSTOP~4: GB278.1, U6305.3 (D4)
F.CLOCKSTOP~5: GB281.1, U6305.4 (D5)
F.CLOCKSTOP~6: GB282.1, U6305.5 (D6)
F.CLOCKSTOP~7: GB283.1, U6313.3 (D2)
F.EL_ABORT~: U6323.3 (Q)
F.ERCC_EN: GB226.1, U6308.6 (C2), U6309.2 (A2)
F.LATE_CLKSTP: GB284.1, U6308.5 (C1), U6309.1 (A1)
F.PHASE.2X: GB295.1, U6306.3 (J)
H1: U6327.3 (Q)
H1.PHD: U6306.6 (Q_), U6316.2 (D1)
H1E: U6307.2 (K), U6307.5 (Q), U6318.2 (D1)
H2: U6314.4 (D2), U6326.3 (Q)
H2.PHD: U6306.2 (K), U6306.5 (Q), U6307.3 (J), U6324.2 (D)
H2E: U6307.6 (Q_), U6313.1 (D0), U6317.1 (D0), U6319.2 (D1), U6325.1 (D0)
MAR.2X.CLK: U6321.3 (Q)
MDR.2X.CLK: U6320.3 (Q)
MEM_STATE.CLK: U6314.6 (Q)
MICRO_EVENT: U6305.8 (Q), U6308.13 (D3), U6309.4 (B1), U6309.5 (B2)
unnamed: U6304.3 (Q), U6308.1 (D0), U6308.4 (C0), U6308.9 (B0)
unnamed: U6308.8 (Q), U6312.1 (D0), U6325.2 (D1)
unnamed: U6309.7 (Q), U6311.2 (D)
unnamed: U6310.2 (Q), U6314.2 (D1)
unnamed: U6313.4 (Q), U6322.2 (D)
unnamed: U6315.3 (Q), U6323.1 (D0), U6323.2 (D1)
unnamed: U6322.6 (Q_), U6325.3 (D2)
unnamed: U6324.5 (Q), U6326.2 (D1)
unnamed: U6324.6 (Q_), U6327.1 (D0)
PU: U6301.2 (D1), U6302.2 (D1), U6303.2 (D1), U6305.6 (D7), U6306.4 (PR_), U6307.4 (PR_), U6308.11 (D1), U6308.12 (D2), U6309.3 (A3), U6309.6 (B3), U6311.1 (CL_), U6311.4 (PR_), U6322.1 (CL_), U6322.4 (PR_), U6324.1 (CL_), U6324.4 (PR_), U6326.1 (D0), U6327.2 (D1)
Q2~: U6318.3 (Q)
Q3~: U6304.1 (D0), U6308.3 (A1), U6311.3 (CLK), U6316.3 (Q)
Q4~: U6319.3 (Q)
Q4~.DIAG.CLK: U6317.3 (Q)
SF_STOP: U6308.10 (B1), U6310.1 (D0)
STATE_CLK.EN~: U6325.4 (Q)
UEVENT_STOP: U6308.2 (A0), U6312.2 (Q)
