Datamuseum-DK/R1000.HwDoc/Schematics/FIU/pg_63.kicad_sch

## KiCad design Schematics/FIU/pg_63.kicad_sch (2023-01-10)

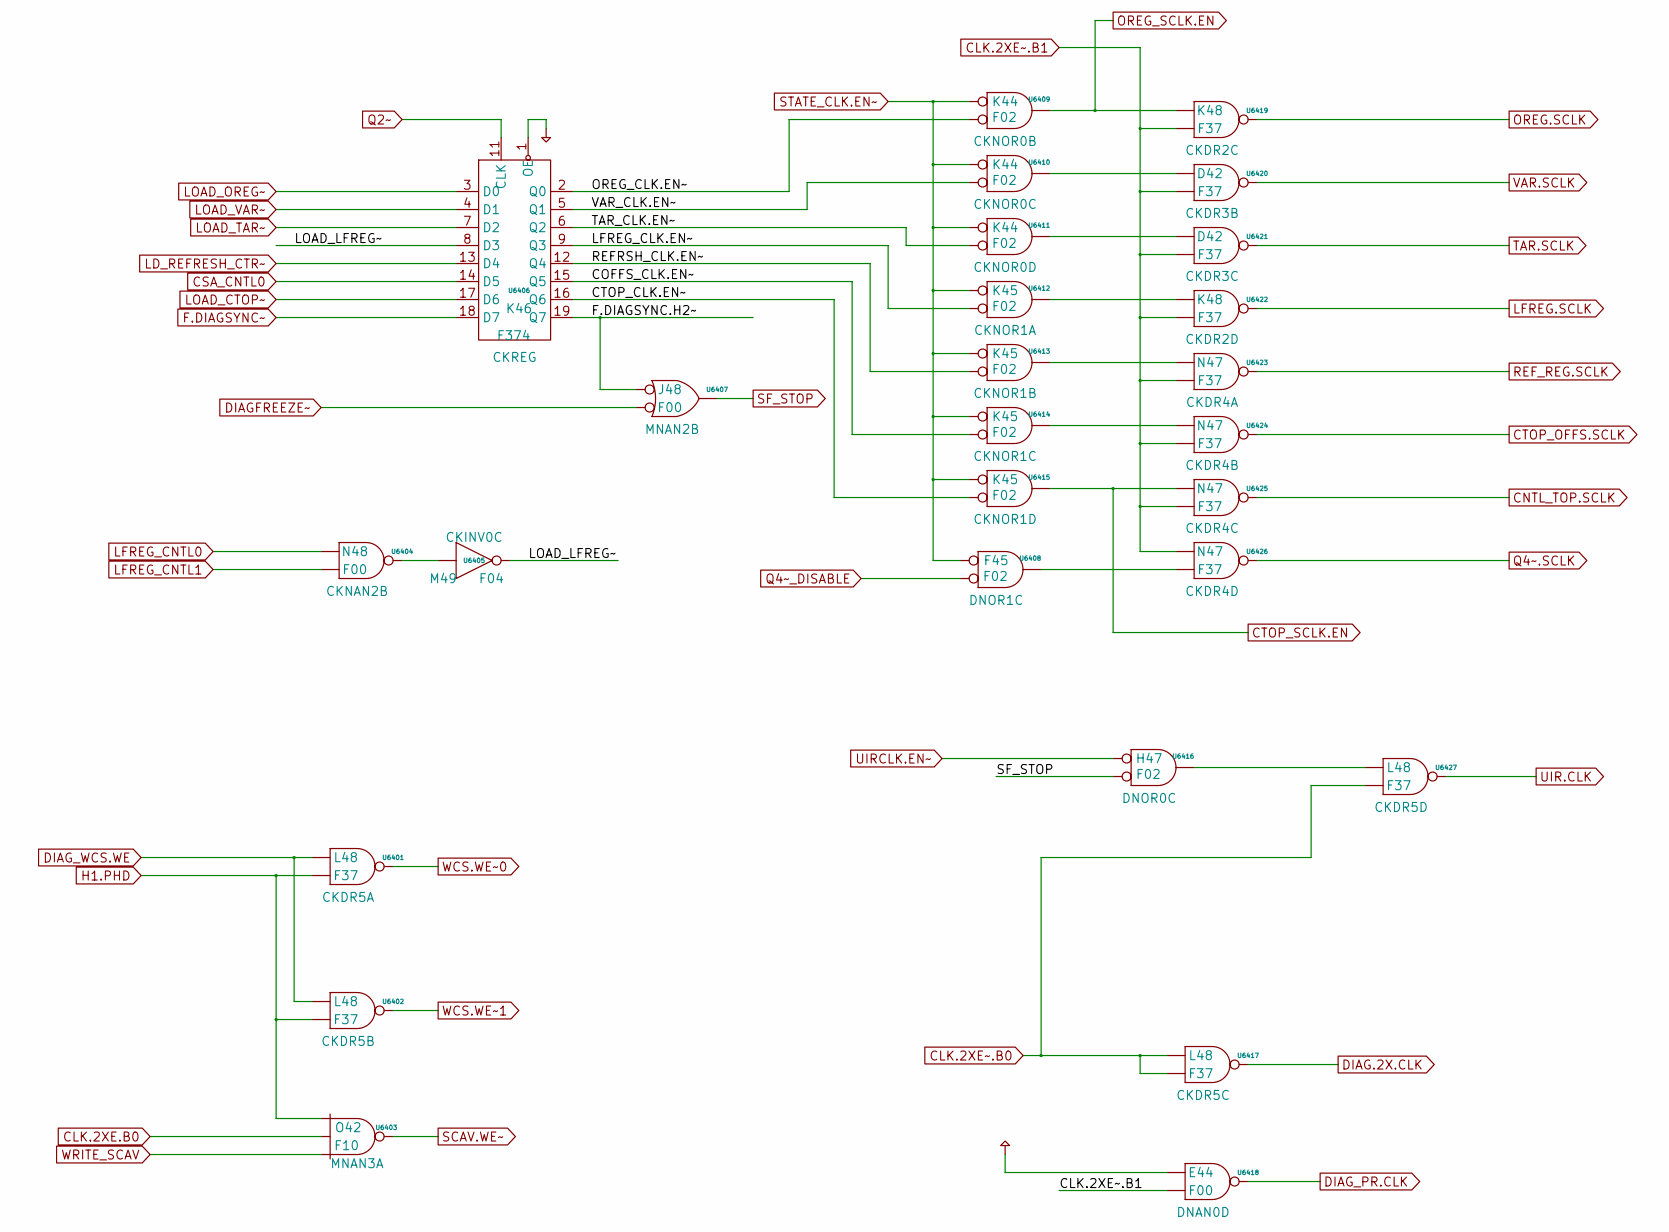
[picture p346: schematic pg_63.kicad_sch]

Parts:
U6401, U6402, U6417, U6419, U6420, U6421, U6422, U6423, U6424, U6425, U6426, U6427: F37
U6403: F10
U6404, U6407, U6418: F00
U6405: F04
U6406: F374
U6408, U6409, U6410, U6411, U6412, U6413, U6414, U6415, U6416: F02

Connections:
CLK.2XE.B0: U6403.2 (D1)
CLK.2XE~.B0: U6417.1 (D0), U6417.2 (D1), U6427.2 (D1)
CLK.2XE~.B1: U6418.2 (D1), U6419.2 (D1), U6420.2 (D1), U6421.2 (D1), U6422.2 (D1), U6423.2 (D1), U6424.2 (D1), U6425.2 (D1), U6426.1 (D0)
CNTL_TOP.SCLK: U6425.3 (Q)
COFFS_CLK.EN~: U6406.15 (Q5), U6414.2 (D1)
CSA_CNTL0: U6406.14 (D5)
CTOP_CLK.EN~: U6406.16 (Q6), U6415.2 (D1)
CTOP_OFFS.SCLK: U6424.3 (Q)
CTOP_SCLK.EN: U6415.3 (Q), U6425.1 (D0)
DIAG.2X.CLK: U6417.3 (Q)
DIAGFREEZE~: U6407.2 (D1)
DIAG_PR.CLK: U6418.3 (Q)
DIAG_WCS.WE: U6401.1 (D0), U6402.1 (D0)
F.DIAGSYNC.H2~: U6406.19 (Q7), U6407.1 (D0)
F.DIAGSYNC~: U6406.18 (D7)
H1.PHD: U6401.2 (D1), U6402.2 (D1), U6403.1 (D0)
LD_REFRESH_CTR~: U6406.13 (D4)
LFREG.SCLK: U6422.3 (Q)
LFREG_CLK.EN~: U6406.9 (Q3), U6412.2 (D1)
LFREG_CNTL0: U6404.1 (D0)
LFREG_CNTL1: U6404.2 (D1)
LOAD_CTOP~: U6406.17 (D6)
LOAD_LFREG~: U6405.2 (Q), U6406.8 (D3)
LOAD_OREG~: U6406.3 (D0)
LOAD_TAR~: U6406.7 (D2)
LOAD_VAR~: U6406.4 (D1)
unnamed: U6404.3 (Q), U6405.1 (D0)
unnamed: U6408.3 (Q), U6426.2 (D1)
unnamed: U6410.3 (Q), U6420.1 (D0)
unnamed: U6411.3 (Q), U6421.1 (D0)
unnamed: U6412.3 (Q), U6422.1 (D0)
unnamed: U6413.3 (Q), U6423.1 (D0)
unnamed: U6414.3 (Q), U6424.1 (D0)
unnamed: U6416.3 (Q), U6427.1 (D0)
OREG.SCLK: U6419.3 (Q)
OREG_CLK.EN~: U6406.2 (Q0), U6409.2 (D1)
OREG_SCLK.EN: U6409.3 (Q), U6419.1 (D0)
PD: U6406.1 (OE)
PU: U6418.1 (D0)
Q2~: U6406.11 (CLK)
Q4~.SCLK: U6426.3 (Q)
Q4~_DISABLE: U6408.2 (D1)
REFRSH_CLK.EN~: U6406.12 (Q4), U6413.2 (D1)
REF_REG.SCLK: U6423.3 (Q)
SCAV.WE~: U6403.4 (Q)
SF_STOP: U6407.3 (Q), U6416.2 (D1)
STATE_CLK.EN~: U6408.1 (D0), U6409.1 (D0), U6410.1 (D0), U6411.1 (D0), U6412.1 (D0), U6413.1 (D0), U6414.1 (D0), U6415.1 (D0)
TAR.SCLK: U6421.3 (Q)
TAR_CLK.EN~: U6406.6 (Q2), U6411.2 (D1)
UIR.CLK: U6427.3 (Q)
UIRCLK.EN~: U6416.1 (D0)
VAR.SCLK: U6420.3 (Q)
VAR_CLK.EN~: U6406.5 (Q1), U6410.2 (D1)
WCS.WE~0: U6401.3 (Q)
WCS.WE~1: U6402.3 (Q)
WRITE_SCAV: U6403.3 (D2)
