Datamuseum-DK/R1000.HwDoc/Schematics/FIU/pg_64.kicad_sch

## KiCad design Schematics/FIU/pg_64.kicad_sch (2023-01-10)

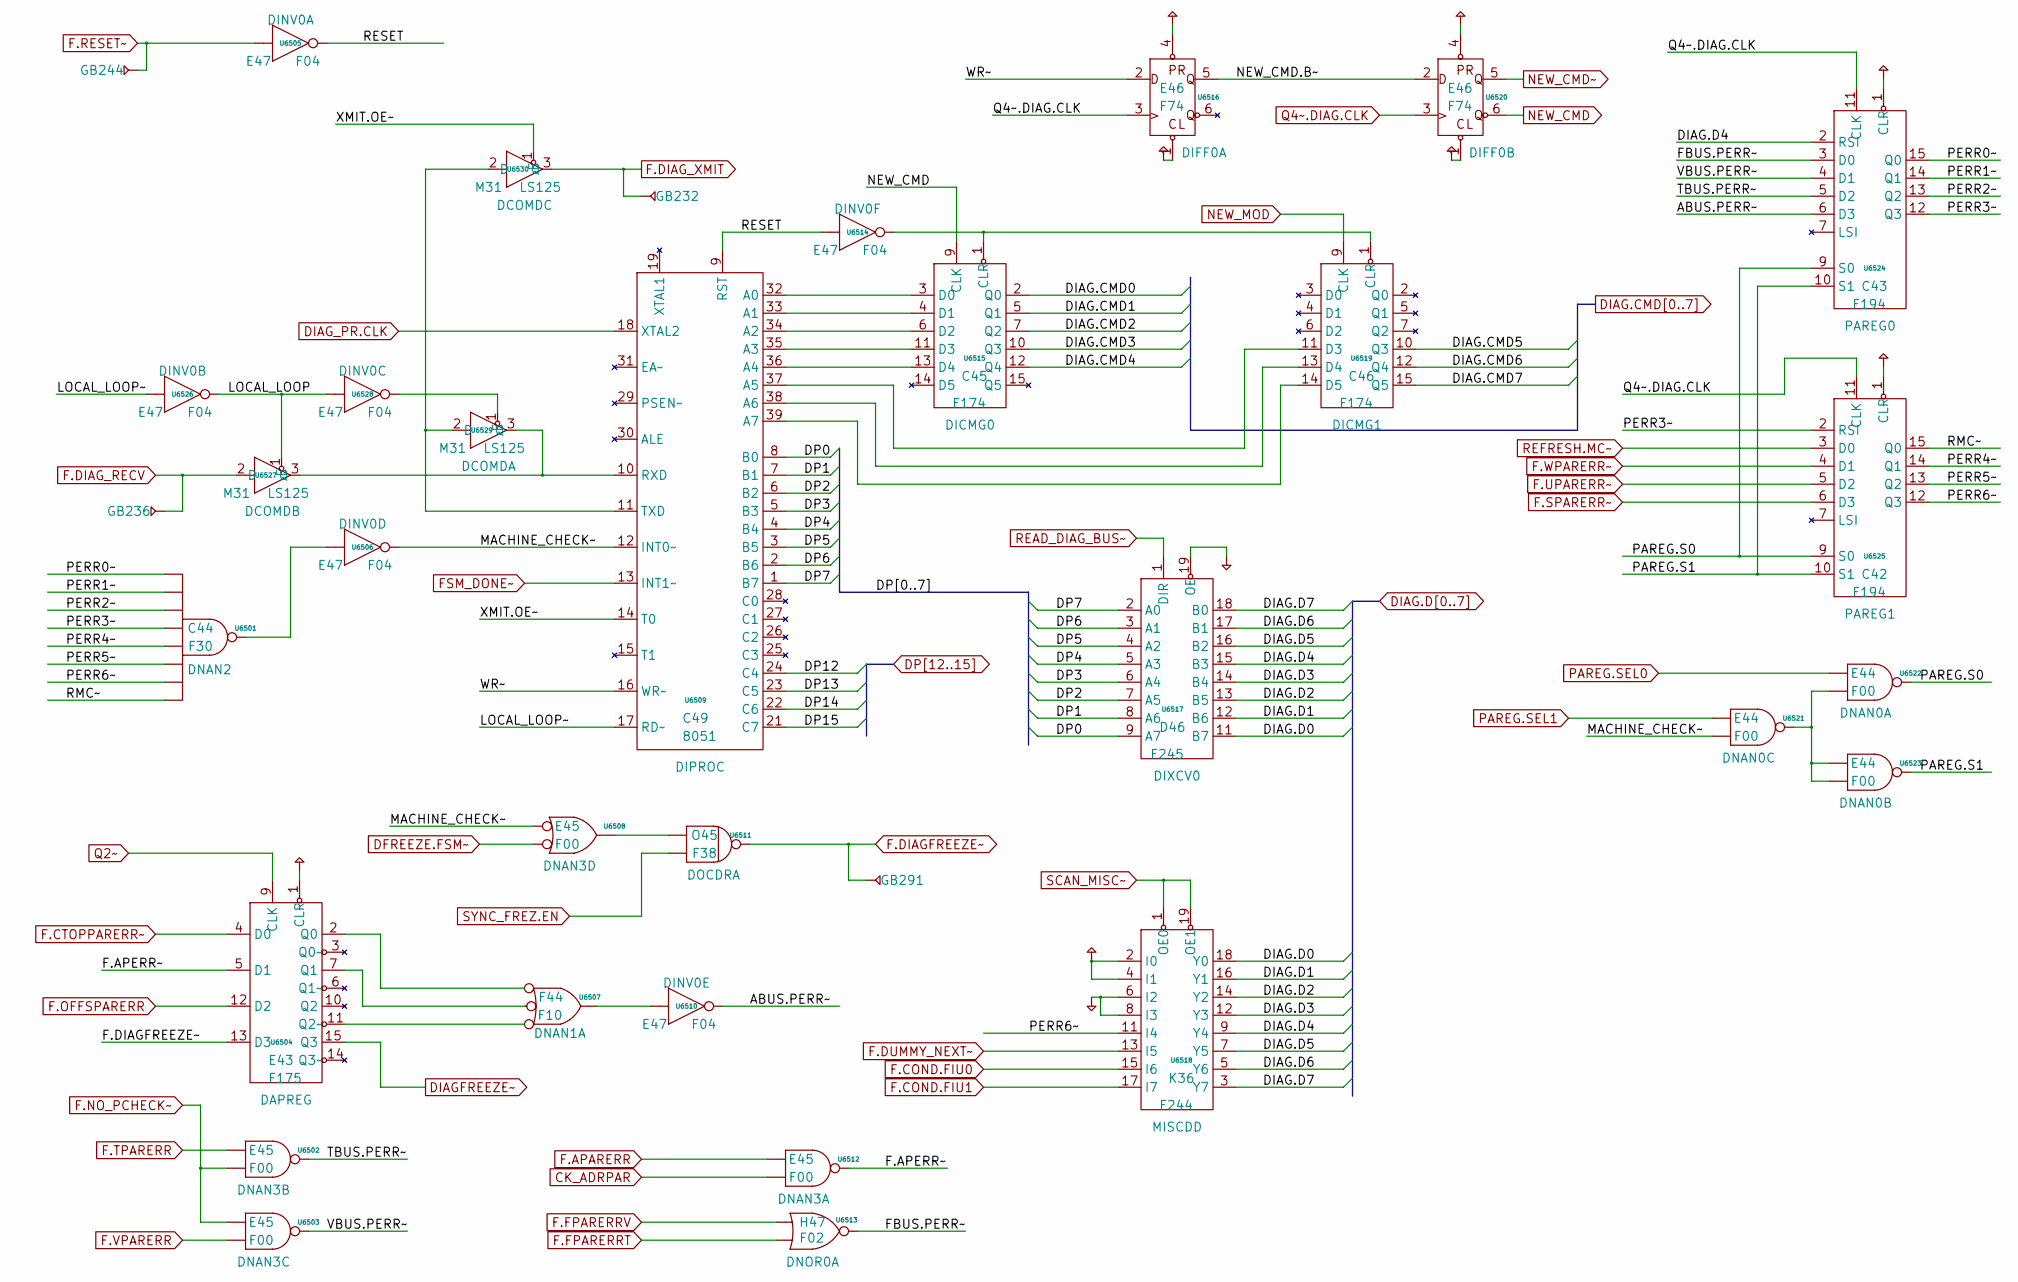
[picture p347: schematic pg_64.kicad_sch]

Parts:
GB232, GB236, GB244, GB291: GB
U6501: F30
U6502, U6503, U6508, U6512, U6521, U6522, U6523: F00
U6504: F175
U6505, U6506, U6510, U6514, U6526, U6528: F04
U6507: F10
U6509: 8051
U6511: F38
U6513: F02
U6515, U6519: F174
U6516, U6520: F74
U6517: F245
U6518: F244
U6524, U6525: F194
U6527, U6529, U6530: LS125

Connections:
ABUS.PERR~: U6510.2 (Q), U6524.6 (D3)
CK_ADRPAR: U6512.2 (D1)
DFREEZE.FSM~: U6508.2 (D1)
DIAG.CMD0: U6515.2 (Q0)
DIAG.CMD1: U6515.5 (Q1)
DIAG.CMD2: U6515.7 (Q2)
DIAG.CMD3: U6515.10 (Q3)
DIAG.CMD4: U6515.12 (Q4)
DIAG.CMD5: U6519.10 (Q3)
DIAG.CMD6: U6519.12 (Q4)
DIAG.CMD7: U6519.15 (Q5)
DIAG.D0: U6517.11 (B7), U6518.18 (Y0)
DIAG.D1: U6517.12 (B6), U6518.16 (Y1)
DIAG.D2: U6517.13 (B5), U6518.14 (Y2)
DIAG.D3: U6517.14 (B4), U6518.12 (Y3)
DIAG.D4: U6517.15 (B3), U6518.9 (Y4), U6524.2 (RSI)
DIAG.D5: U6517.16 (B2), U6518.7 (Y5)
DIAG.D6: U6517.17 (B1), U6518.5 (Y6)
DIAG.D7: U6517.18 (B0), U6518.3 (Y7)
DIAGFREEZE~: U6504.15 (Q3)
DIAG_PR.CLK: U6509.18 (XTAL2)
DP0: U6509.8 (B0), U6517.9 (A7)
DP1: U6509.7 (B1), U6517.8 (A6)
DP2: U6509.6 (B2), U6517.7 (A5)
DP3: U6509.5 (B3), U6517.6 (A4)
DP4: U6509.4 (B4), U6517.5 (A3)
DP5: U6509.3 (B5), U6517.4 (A2)
DP6: U6509.2 (B6), U6517.3 (A1)
DP7: U6509.1 (B7), U6517.2 (A0)
DP12: U6509.24 (C4)
DP13: U6509.23 (C5)
DP14: U6509.22 (C6)
DP15: U6509.21 (C7)
F.APARERR: U6512.1 (D0)
F.APERR~: U6504.5 (D1), U6512.3 (Q)
F.COND.FIU0: U6518.15 (I6)
F.COND.FIU1: U6518.17 (I7)
F.CTOPPARERR~: U6504.4 (D0)
F.DIAGFREEZE~: GB291.1, U6504.13 (D3), U6511.3 (Q)
F.DIAG_RECV: GB236.1, U6527.2 (D)
F.DIAG_XMIT: GB232.1, U6530.3 (Q)
F.DUMMY_NEXT~: U6518.13 (I5)
F.FPARERRT: U6513.2 (D1)
F.FPARERRV: U6513.1 (D0)
F.NO_PCHECK~: U6502.2 (D1), U6503.1 (D0)
F.OFFSPARERR: U6504.12 (D2)
F.RESET~: GB244.1, U6505.1 (D0)
F.SPARERR~: U6525.6 (D3)
F.TPARERR: U6502.1 (D0)
F.UPARERR~: U6525.5 (D2)
F.VPARERR: U6503.2 (D1)
F.WPARERR~: U6525.4 (D1)
FBUS.PERR~: U6513.3 (Q), U6524.3 (D0)
FSM_DONE~: U6509.13 (INT1~)
LOCAL_LOOP: U6526.2 (Q), U6527.1 (E), U6528.1 (D0)
LOCAL_LOOP~: U6509.17 (RD~), U6526.1 (D0)
MACHINE_CHECK~: U6506.2 (Q), U6508.1 (D0), U6509.12 (INT0~), U6521.2 (D1)
NEW_CMD: U6515.9 (CLK), U6520.6 (Q_)
NEW_CMD.B~: U6516.5 (Q), U6520.2 (D)
NEW_CMD~: U6520.5 (Q)
NEW_MOD: U6519.9 (CLK)
unnamed: U6501.8 (Q), U6506.1 (D0)
unnamed: U6504.2 (Q0), U6507.1 (D0)
unnamed: U6504.7 (Q1), U6507.2 (D1)
unnamed: U6504.11 (Q2~), U6507.3 (D2)
unnamed: U6507.4 (Q), U6510.1 (D0)
unnamed: U6508.3 (Q), U6511.1 (D0)
unnamed: U6509.10 (RXD), U6527.3 (Q), U6529.3 (Q)
unnamed: U6509.11 (TXD), U6529.2 (D), U6530.2 (D)
unnamed: U6509.32 (A0), U6515.3 (D0)
unnamed: U6509.33 (A1), U6515.4 (D1)
unnamed: U6509.34 (A2), U6515.6 (D2)
unnamed: U6509.35 (A3), U6515.11 (D3)
unnamed: U6509.36 (A4), U6515.13 (D4)
unnamed: U6509.37 (A5), U6519.11 (D3)
unnamed: U6509.38 (A6), U6519.13 (D4)
unnamed: U6509.39 (A7), U6519.14 (D5)
unnamed: U6514.2 (Q), U6515.1 (CLR), U6519.1 (CLR)
unnamed: U6521.3 (Q), U6522.2 (D1), U6523.1 (D0), U6523.2 (D1)
unnamed: U6528.2 (Q), U6529.1 (E)
PAREG.S0: U6522.3 (Q), U6524.9 (S0), U6525.9 (S0)
PAREG.S1: U6523.3 (Q), U6524.10 (S1), U6525.10 (S1)
PAREG.SEL0: U6522.1 (D0)
PAREG.SEL1: U6521.1 (D0)
PD: U6517.19 (OE), U6518.6 (I2), U6518.8 (I3)
PERR0~: U6501.11 (D0), U6524.15 (Q0)
PERR1~: U6501.12 (D1), U6524.14 (Q1)
PERR2~: U6501.1 (D2), U6524.13 (Q2)
PERR3~: U6501.2 (D3), U6524.12 (Q3), U6525.2 (RSI)
PERR4~: U6501.3 (D4), U6525.14 (Q1)
PERR5~: U6501.4 (D5), U6525.13 (Q2)
PERR6~: U6501.5 (D6), U6518.11 (I4), U6525.12 (Q3)
PU: U6504.1 (CLR), U6516.1 (CL_), U6516.4 (PR_), U6518.2 (I0), U6518.4 (I1), U6520.1 (CL_), U6520.4 (PR_), U6524.1 (CLR), U6525.1 (CLR)
Q2~: U6504.9 (CLK)
Q4~.DIAG.CLK: U6516.3 (CLK), U6520.3 (CLK), U6524.11 (CLK), U6525.11 (CLK)
READ_DIAG_BUS~: U6517.1 (DIR)
REFRESH.MC~: U6525.3 (D0)
RESET: U6505.2 (Q), U6509.9 (RST), U6514.1 (D0)
RMC~: U6501.6 (D7), U6525.15 (Q0)
SCAN_MISC~: U6518.1 (OE0), U6518.19 (OE1)
SYNC_FREZ.EN: U6511.2 (D1)
TBUS.PERR~: U6502.3 (Q), U6524.5 (D2)
VBUS.PERR~: U6503.3 (Q), U6524.4 (D1)
WR~: U6509.16 (WR~), U6516.2 (D)
XMIT.OE~: U6509.14 (T0), U6530.1 (E)
