Datamuseum-DK/R1000.HwDoc/Schematics/FIU/pg_65.kicad_sch

## KiCad design Schematics/FIU/pg_65.kicad_sch (2023-01-10)

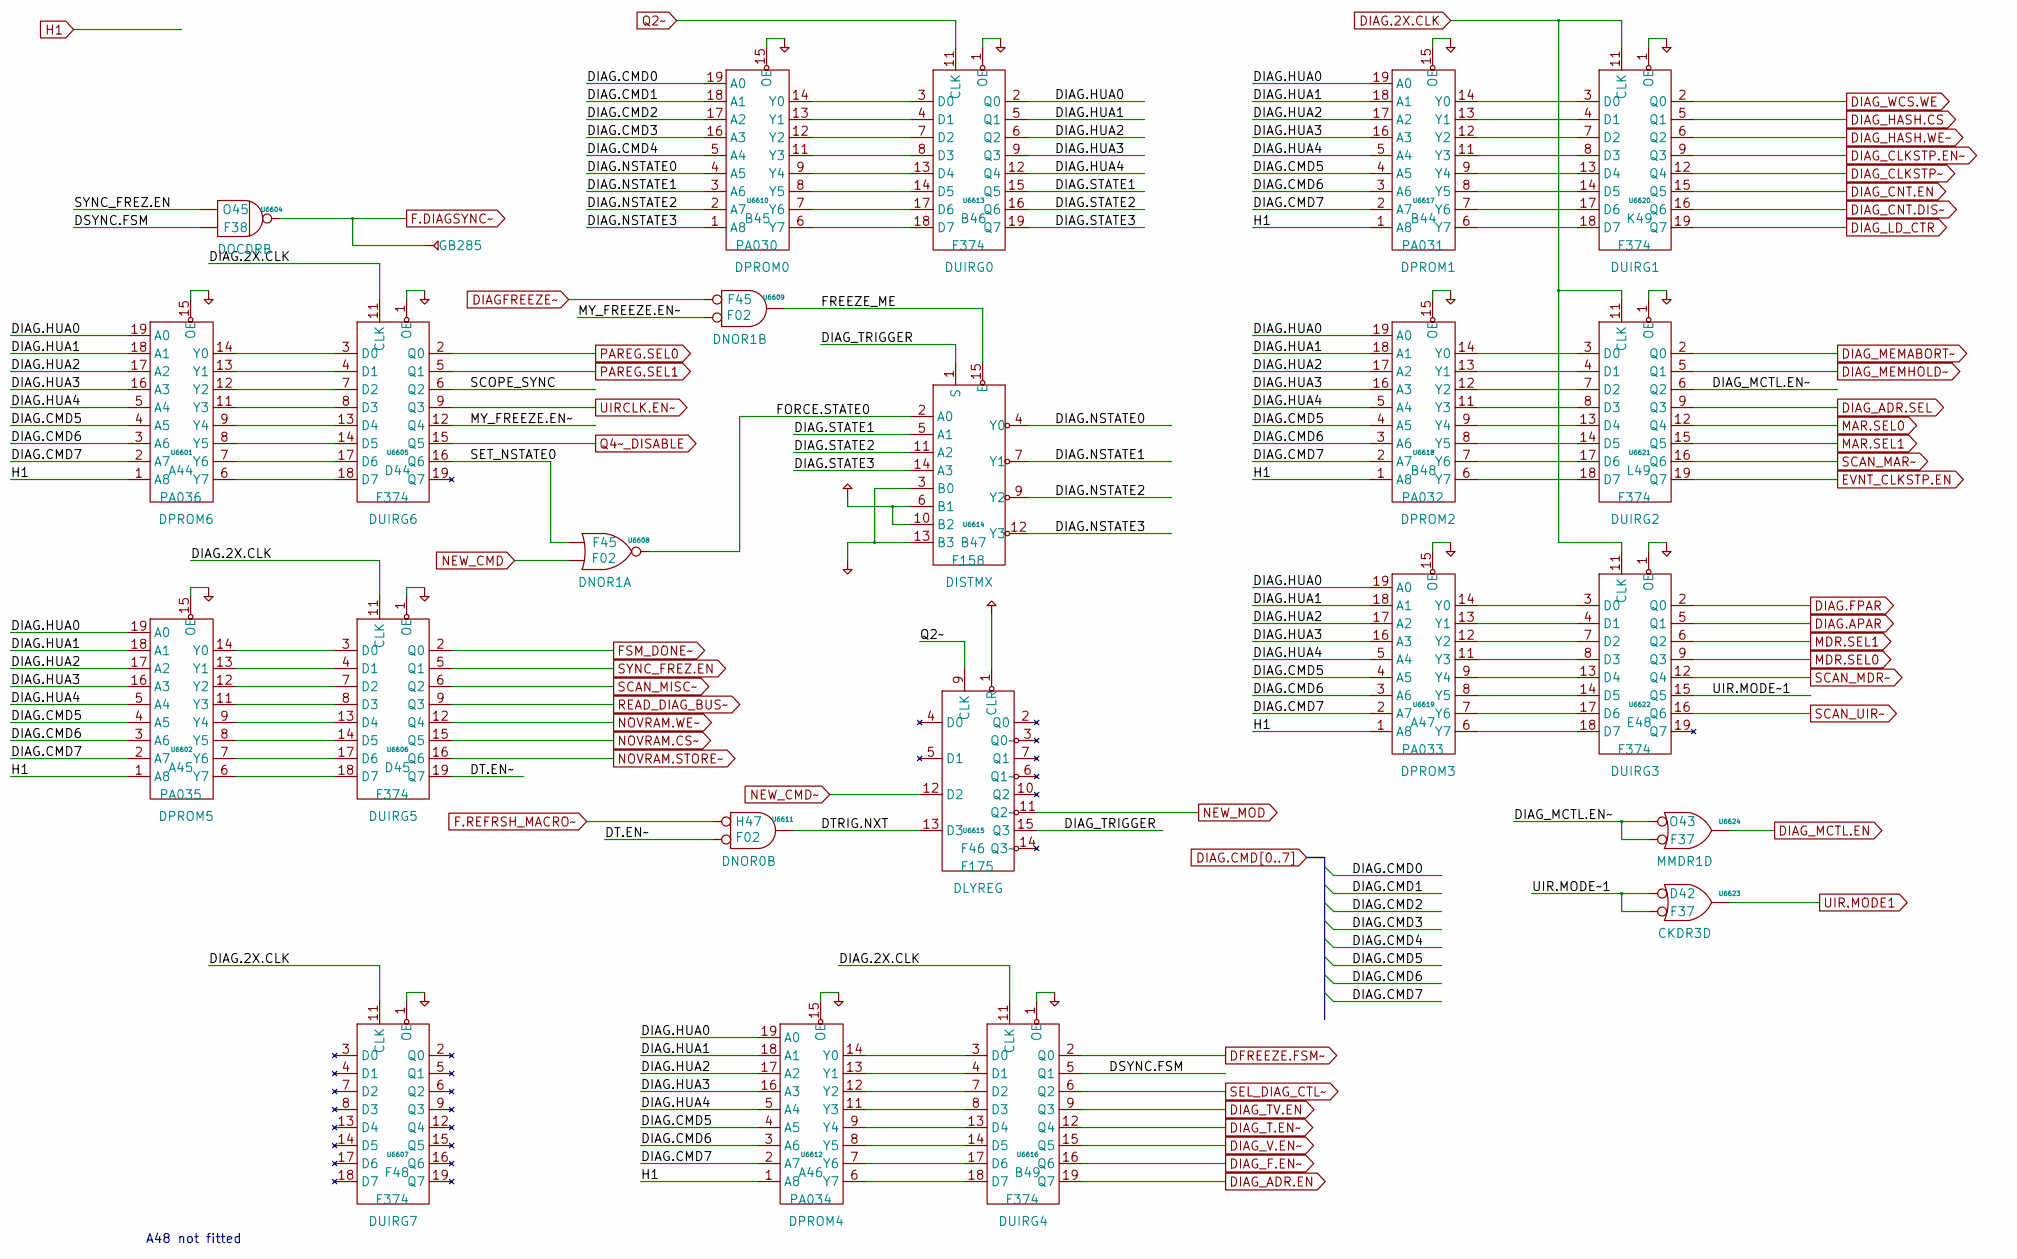
[picture p348: schematic pg_65.kicad_sch]

Parts:
GB285: GB
U6601: PA036
U6602: PA035
U6604: F38
U6605, U6606, U6607, U6613, U6616, U6620, U6621, U6622: F374
U6608, U6609, U6611: F02
U6610: PA030
U6612: PA034
U6614: F158
U6615: F175
U6617: PA031
U6618: PA032
U6619: PA033
U6623, U6624: F37

Connections:
DFREEZE.FSM~: U6616.2 (Q0)
DIAG.2X.CLK: U6605.11 (CLK), U6606.11 (CLK), U6607.11 (CLK), U6616.11 (CLK), U6620.11 (CLK), U6621.11 (CLK), U6622.11 (CLK)
DIAG.APAR: U6622.5 (Q1)
DIAG.CMD0: U6610.19 (A0)
DIAG.CMD1: U6610.18 (A1)
DIAG.CMD2: U6610.17 (A2)
DIAG.CMD3: U6610.16 (A3)
DIAG.CMD4: U6610.5 (A4)
DIAG.CMD5: U6601.4 (A5), U6602.4 (A5), U6612.4 (A5), U6617.4 (A5), U6618.4 (A5), U6619.4 (A5)
DIAG.CMD6: U6601.3 (A6), U6602.3 (A6), U6612.3 (A6), U6617.3 (A6), U6618.3 (A6), U6619.3 (A6)
DIAG.CMD7: U6601.2 (A7), U6602.2 (A7), U6612.2 (A7), U6617.2 (A7), U6618.2 (A7), U6619.2 (A7)
DIAG.FPAR: U6622.2 (Q0)
DIAG.HUA0: U6601.19 (A0), U6602.19 (A0), U6612.19 (A0), U6613.2 (Q0), U6617.19 (A0), U6618.19 (A0), U6619.19 (A0)
DIAG.HUA1: U6601.18 (A1), U6602.18 (A1), U6612.18 (A1), U6613.5 (Q1), U6617.18 (A1), U6618.18 (A1), U6619.18 (A1)
DIAG.HUA2: U6601.17 (A2), U6602.17 (A2), U6612.17 (A2), U6613.6 (Q2), U6617.17 (A2), U6618.17 (A2), U6619.17 (A2)
DIAG.HUA3: U6601.16 (A3), U6602.16 (A3), U6612.16 (A3), U6613.9 (Q3), U6617.16 (A3), U6618.16 (A3), U6619.16 (A3)
DIAG.HUA4: U6601.5 (A4), U6602.5 (A4), U6612.5 (A4), U6613.12 (Q4), U6617.5 (A4), U6618.5 (A4), U6619.5 (A4)
DIAG.NSTATE0: U6610.4 (A5), U6614.4 (Y0)
DIAG.NSTATE1: U6610.3 (A6), U6614.7 (Y1)
DIAG.NSTATE2: U6610.2 (A7), U6614.9 (Y2)
DIAG.NSTATE3: U6610.1 (A8), U6614.12 (Y3)
DIAG.STATE1: U6613.15 (Q5), U6614.5 (A1)
DIAG.STATE2: U6613.16 (Q6), U6614.11 (A2)
DIAG.STATE3: U6613.19 (Q7), U6614.14 (A3)
DIAGFREEZE~: U6609.1 (D0)
DIAG_ADR.EN: U6616.19 (Q7)
DIAG_ADR.SEL: U6621.9 (Q3)
DIAG_CLKSTP.EN~: U6620.9 (Q3)
DIAG_CLKSTP~: U6620.12 (Q4)
DIAG_CNT.DIS~: U6620.16 (Q6)
DIAG_CNT.EN: U6620.15 (Q5)
DIAG_F.EN~: U6616.16 (Q6)
DIAG_HASH.CS: U6620.5 (Q1)
DIAG_HASH.WE~: U6620.6 (Q2)
DIAG_LD_CTR: U6620.19 (Q7)
DIAG_MCTL.EN: U6624.3 (Q)
DIAG_MCTL.EN~: U6621.6 (Q2), U6624.1 (D0), U6624.2 (D1)
DIAG_MEMABORT~: U6621.2 (Q0)
DIAG_MEMHOLD~: U6621.5 (Q1)
DIAG_T.EN~: U6616.12 (Q4)
DIAG_TRIGGER: U6614.1 (S), U6615.15 (Q3)
DIAG_TV.EN: U6616.9 (Q3)
DIAG_V.EN~: U6616.15 (Q5)
DIAG_WCS.WE: U6620.2 (Q0)
DSYNC.FSM: U6604.2 (D1), U6616.5 (Q1)
DT.EN~: U6606.19 (Q7), U6611.2 (D1)
DTRIG.NXT: U6611.3 (Q), U6615.13 (D3)
EVNT_CLKSTP.EN: U6621.19 (Q7)
F.DIAGSYNC~: GB285.1, U6604.3 (Q)
F.REFRSH_MACRO~: U6611.1 (D0)
FORCE.STATE0: U6608.3 (Q), U6614.2 (A0)
FREEZE_ME: U6609.3 (Q), U6614.15 (E)
FSM_DONE~: U6606.2 (Q0)
H1: U6601.1 (A8), U6602.1 (A8), U6612.1 (A8), U6617.1 (A8), U6618.1 (A8), U6619.1 (A8)
MAR.SEL0: U6621.12 (Q4)
MAR.SEL1: U6621.15 (Q5)
MDR.SEL0: U6622.9 (Q3)
MDR.SEL1: U6622.6 (Q2)
MY_FREEZE.EN~: U6605.12 (Q4), U6609.2 (D1)
NEW_CMD: U6608.2 (D1)
NEW_CMD~: U6615.12 (D2)
NEW_MOD: U6615.11 (Q2~)
NOVRAM.CS~: U6606.15 (Q5)
NOVRAM.STORE~: U6606.16 (Q6)
NOVRAM.WE~: U6606.12 (Q4)
unnamed: U6601.6 (Y7), U6605.18 (D7)
unnamed: U6601.7 (Y6), U6605.17 (D6)
unnamed: U6601.8 (Y5), U6605.14 (D5)
unnamed: U6601.9 (Y4), U6605.13 (D4)
unnamed: U6601.11 (Y3), U6605.8 (D3)
unnamed: U6601.12 (Y2), U6605.7 (D2)
unnamed: U6601.13 (Y1), U6605.4 (D1)
unnamed: U6601.14 (Y0), U6605.3 (D0)
unnamed: U6602.6 (Y7), U6606.18 (D7)
unnamed: U6602.7 (Y6), U6606.17 (D6)
unnamed: U6602.8 (Y5), U6606.14 (D5)
unnamed: U6602.9 (Y4), U6606.13 (D4)
unnamed: U6602.11 (Y3), U6606.8 (D3)
unnamed: U6602.12 (Y2), U6606.7 (D2)
unnamed: U6602.13 (Y1), U6606.4 (D1)
unnamed: U6602.14 (Y0), U6606.3 (D0)
unnamed: U6610.6 (Y7), U6613.18 (D7)
unnamed: U6610.7 (Y6), U6613.17 (D6)
unnamed: U6610.8 (Y5), U6613.14 (D5)
unnamed: U6610.9 (Y4), U6613.13 (D4)
unnamed: U6610.11 (Y3), U6613.8 (D3)
unnamed: U6610.12 (Y2), U6613.7 (D2)
unnamed: U6610.13 (Y1), U6613.4 (D1)
unnamed: U6610.14 (Y0), U6613.3 (D0)
unnamed: U6612.6 (Y7), U6616.18 (D7)
unnamed: U6612.7 (Y6), U6616.17 (D6)
unnamed: U6612.8 (Y5), U6616.14 (D5)
unnamed: U6612.9 (Y4), U6616.13 (D4)
unnamed: U6612.11 (Y3), U6616.8 (D3)
unnamed: U6612.12 (Y2), U6616.7 (D2)
unnamed: U6612.13 (Y1), U6616.4 (D1)
unnamed: U6612.14 (Y0), U6616.3 (D0)
unnamed: U6617.6 (Y7), U6620.18 (D7)
unnamed: U6617.7 (Y6), U6620.17 (D6)
unnamed: U6617.8 (Y5), U6620.14 (D5)
unnamed: U6617.9 (Y4), U6620.13 (D4)
unnamed: U6617.11 (Y3), U6620.8 (D3)
unnamed: U6617.12 (Y2), U6620.7 (D2)
unnamed: U6617.13 (Y1), U6620.4 (D1)
unnamed: U6617.14 (Y0), U6620.3 (D0)
unnamed: U6618.6 (Y7), U6621.18 (D7)
unnamed: U6618.7 (Y6), U6621.17 (D6)
unnamed: U6618.8 (Y5), U6621.14 (D5)
unnamed: U6618.9 (Y4), U6621.13 (D4)
unnamed: U6618.11 (Y3), U6621.8 (D3)
unnamed: U6618.12 (Y2), U6621.7 (D2)
unnamed: U6618.13 (Y1), U6621.4 (D1)
unnamed: U6618.14 (Y0), U6621.3 (D0)
unnamed: U6619.6 (Y7), U6622.18 (D7)
unnamed: U6619.7 (Y6), U6622.17 (D6)
unnamed: U6619.8 (Y5), U6622.14 (D5)
unnamed: U6619.9 (Y4), U6622.13 (D4)
unnamed: U6619.11 (Y3), U6622.8 (D3)
unnamed: U6619.12 (Y2), U6622.7 (D2)
unnamed: U6619.13 (Y1), U6622.4 (D1)
unnamed: U6619.14 (Y0), U6622.3 (D0)
PAREG.SEL0: U6605.2 (Q0)
PAREG.SEL1: U6605.5 (Q1)
PD: U6601.15 (OE), U6602.15 (OE), U6605.1 (OE), U6606.1 (OE), U6607.1 (OE), U6610.15 (OE), U6612.15 (OE), U6613.1 (OE), U6614.3 (B0), U6614.13 (B3), U6616.1 (OE), U6617.15 (OE), U6618.15 (OE), U6619.15 (OE), U6620.1 (OE), U6621.1 (OE), U6622.1 (OE)
PU: U6614.6 (B1), U6614.10 (B2), U6615.1 (CLR)
Q2~: U6613.11 (CLK), U6615.9 (CLK)
Q4~_DISABLE: U6605.15 (Q5)
READ_DIAG_BUS~: U6606.9 (Q3)
SCAN_MAR~: U6621.16 (Q6)
SCAN_MDR~: U6622.12 (Q4)
SCAN_MISC~: U6606.6 (Q2)
SCAN_UIR~: U6622.16 (Q6)
SCOPE_SYNC: U6605.6 (Q2)
SEL_DIAG_CTL~: U6616.6 (Q2)
SET_NSTATE0: U6605.16 (Q6), U6608.1 (D0)
SYNC_FREZ.EN: U6604.1 (D0), U6606.5 (Q1)
UIR.MODE1: U6623.3 (Q)
UIR.MODE~1: U6622.15 (Q5), U6623.1 (D0), U6623.2 (D1)
UIRCLK.EN~: U6605.9 (Q3)

Notes on the sheet:
A48 not fitted
