Datamuseum-DK/R1000.HwDoc/Schematics/FIU/pg_66.kicad_sch

## KiCad design Schematics/FIU/pg_66.kicad_sch (2023-01-10)

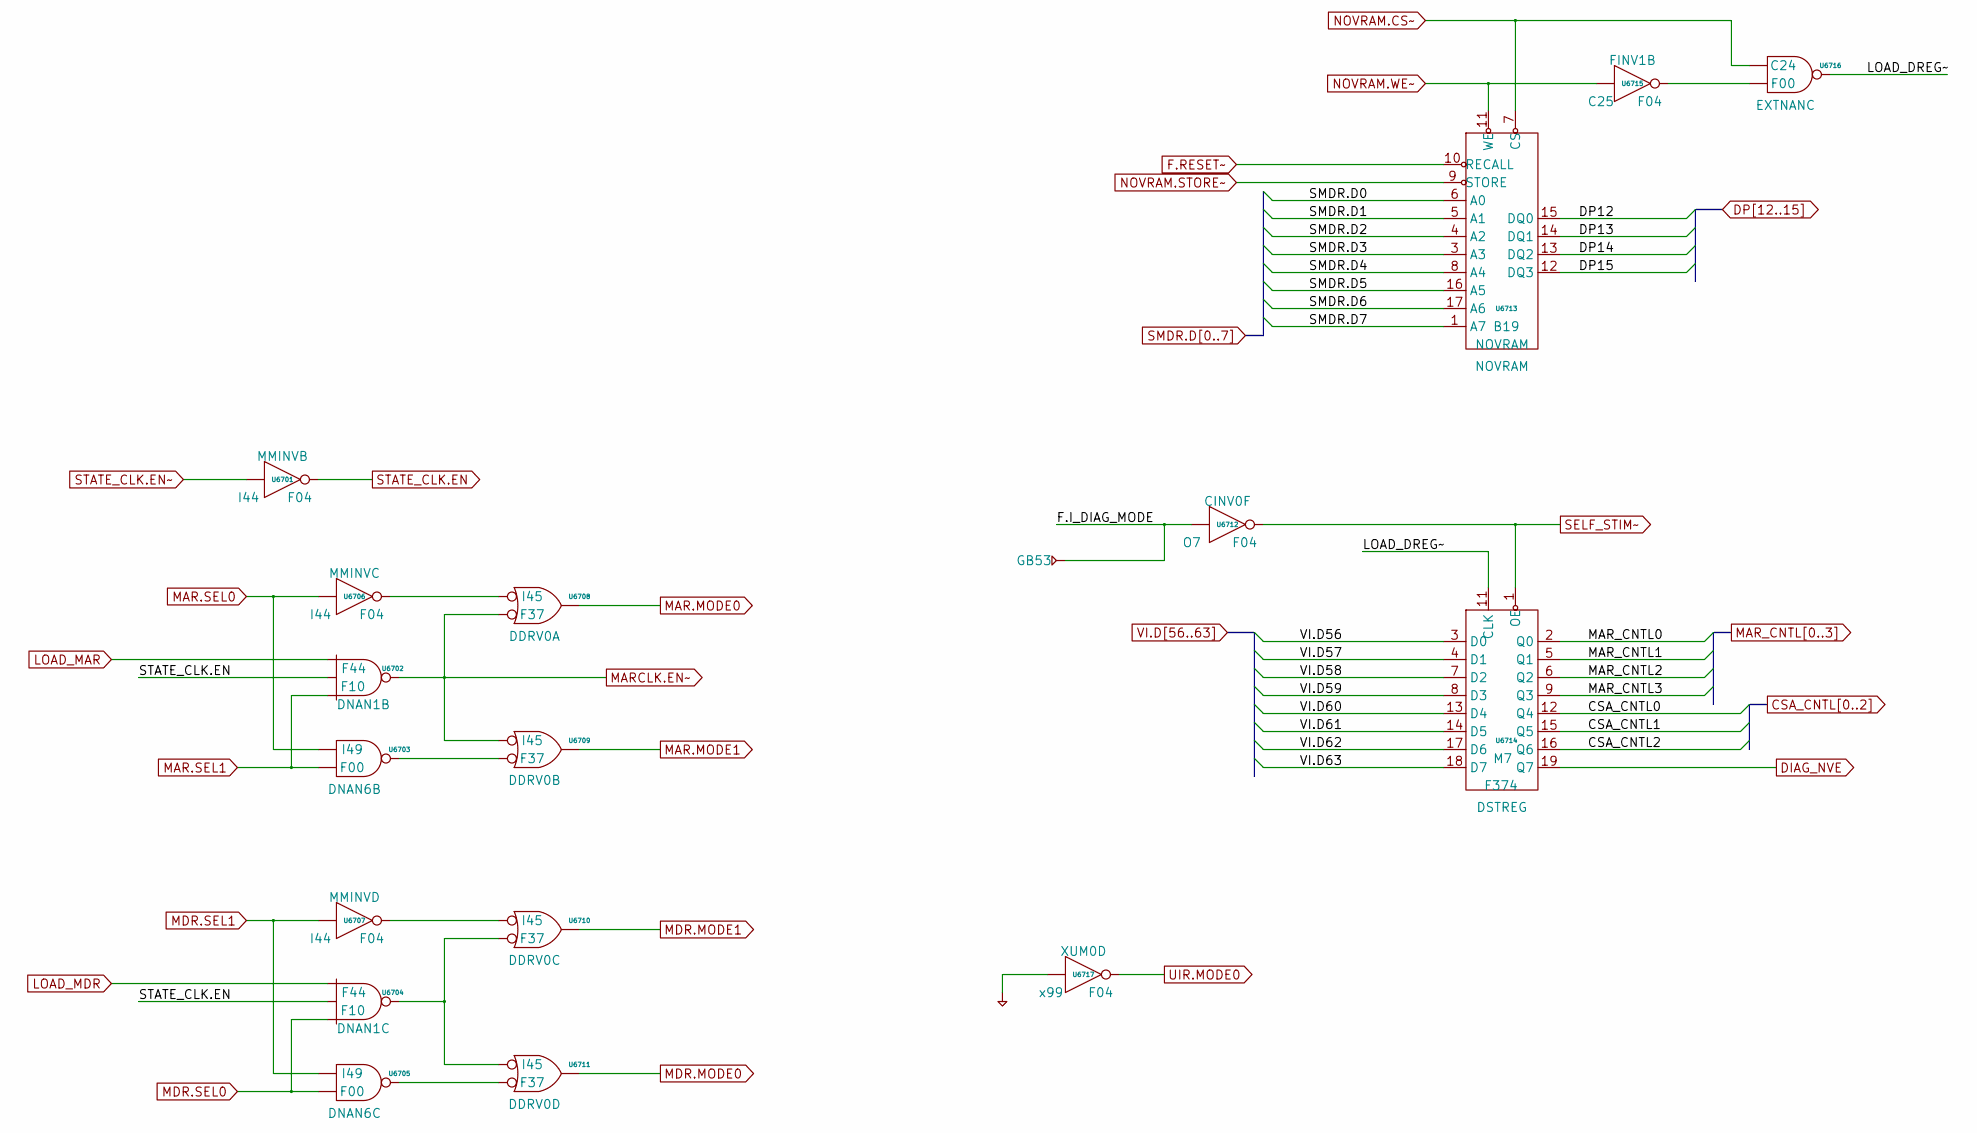
[picture p349: schematic pg_66.kicad_sch]

Parts:
GB53: GB
U6701, U6706, U6707, U6712, U6715, U6717: F04
U6702, U6704: F10
U6703, U6705, U6716: F00
U6708, U6709, U6710, U6711: F37
U6713: NOVRAM
U6714: F374

Connections:
CSA_CNTL0: U6714.12 (Q4)
CSA_CNTL1: U6714.15 (Q5)
CSA_CNTL2: U6714.16 (Q6)
DIAG_NVE: U6714.19 (Q7)
DP12: U6713.15 (DQ0)
DP13: U6713.14 (DQ1)
DP14: U6713.13 (DQ2)
DP15: U6713.12 (DQ3)
F.I_DIAG_MODE: GB53.1, U6712.1 (D0)
F.RESET~: U6713.10 (RECALL)
LOAD_DREG~: U6714.11 (CLK), U6716.3 (Q)
LOAD_MAR: U6702.1 (D0)
LOAD_MDR: U6704.1 (D0)
MAR.MODE0: U6708.3 (Q)
MAR.MODE1: U6709.3 (Q)
MAR.SEL0: U6703.1 (D0), U6706.1 (D0)
MAR.SEL1: U6702.3 (D2), U6703.2 (D1)
MARCLK.EN~: U6702.4 (Q), U6708.2 (D1), U6709.1 (D0)
MAR_CNTL0: U6714.2 (Q0)
MAR_CNTL1: U6714.5 (Q1)
MAR_CNTL2: U6714.6 (Q2)
MAR_CNTL3: U6714.9 (Q3)
MDR.MODE0: U6711.3 (Q)
MDR.MODE1: U6710.3 (Q)
MDR.SEL0: U6704.3 (D2), U6705.2 (D1)
MDR.SEL1: U6705.1 (D0), U6707.1 (D0)
NOVRAM.CS~: U6713.7 (CS), U6716.1 (D0)
NOVRAM.STORE~: U6713.9 (STORE)
NOVRAM.WE~: U6713.11 (WE), U6715.1 (D0)
unnamed: U6703.3 (Q), U6709.2 (D1)
unnamed: U6704.4 (Q), U6710.2 (D1), U6711.1 (D0)
unnamed: U6705.3 (Q), U6711.2 (D1)
unnamed: U6706.2 (Q), U6708.1 (D0)
unnamed: U6707.2 (Q), U6710.1 (D0)
unnamed: U6715.2 (Q), U6716.2 (D1)
PD: U6717.1 (D0)
SELF_STIM~: U6712.2 (Q), U6714.1 (OE)
SMDR.D0: U6713.6 (A0)
SMDR.D1: U6713.5 (A1)
SMDR.D2: U6713.4 (A2)
SMDR.D3: U6713.3 (A3)
SMDR.D4: U6713.8 (A4)
SMDR.D5: U6713.16 (A5)
SMDR.D6: U6713.17 (A6)
SMDR.D7: U6713.1 (A7)
STATE_CLK.EN: U6701.2 (Q), U6702.2 (D1), U6704.2 (D1)
STATE_CLK.EN~: U6701.1 (D0)
UIR.MODE0: U6717.2 (Q)
VI.D56: U6714.3 (D0)
VI.D57: U6714.4 (D1)
VI.D58: U6714.7 (D2)
VI.D59: U6714.8 (D3)
VI.D60: U6714.13 (D4)
VI.D61: U6714.14 (D5)
VI.D62: U6714.17 (D6)
VI.D63: U6714.18 (D7)
