Datamuseum-DK/R1000.HwDoc/Schematics/IOC/pg_02.kicad_sch

## KiCad design Schematics/IOC/pg_02.kicad_sch (2023-01-10)

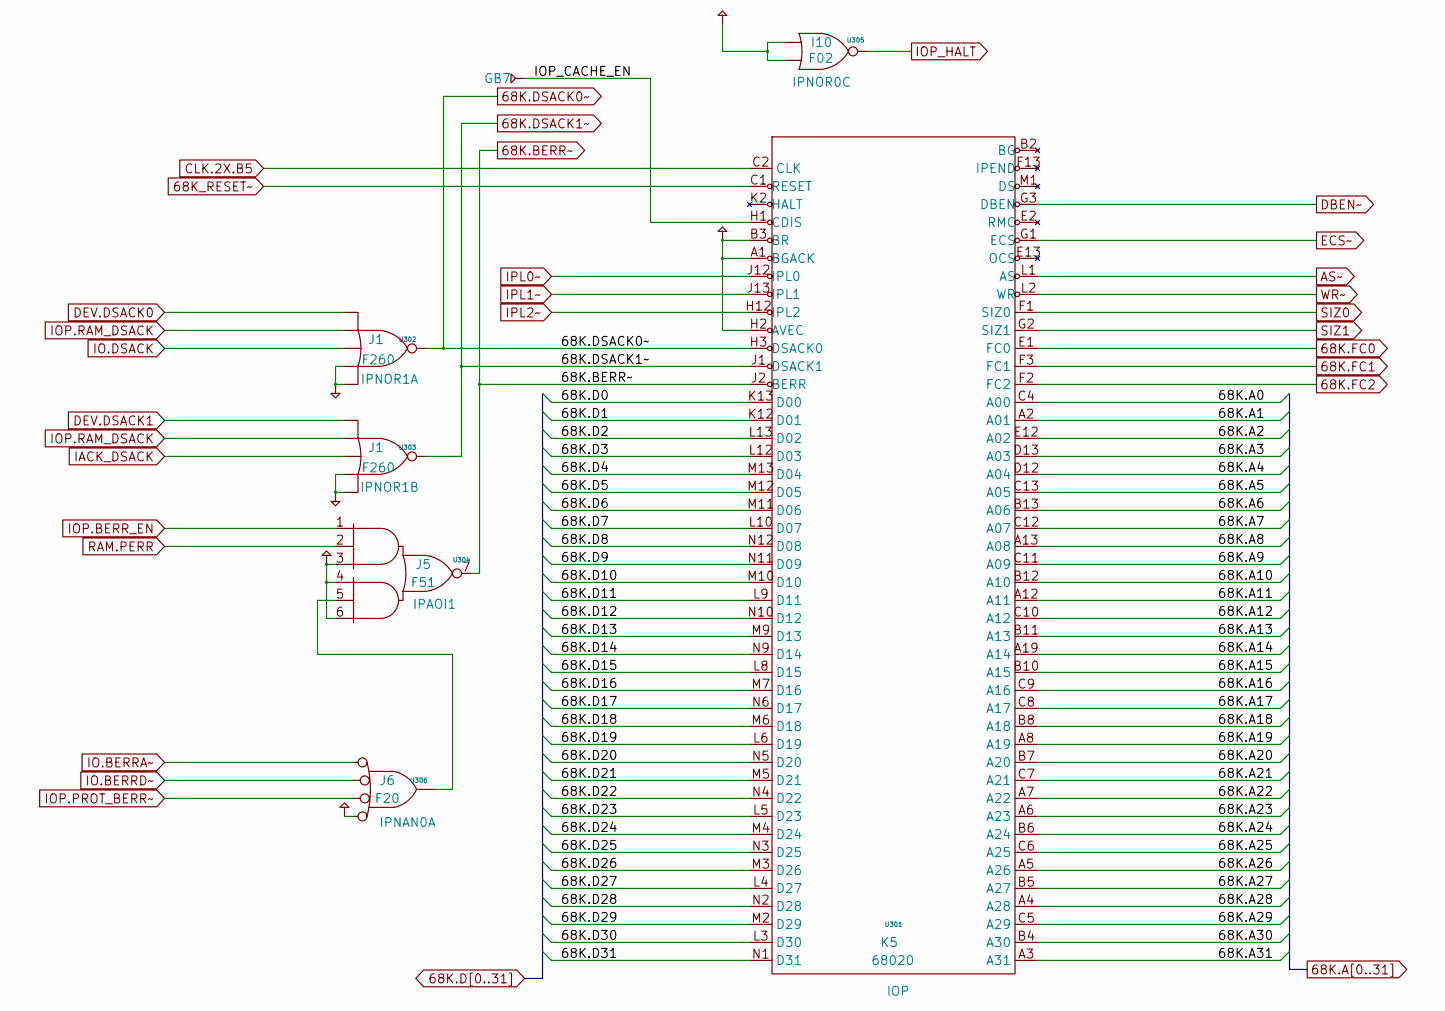
[picture p350: schematic pg_02.kicad_sch]

Parts:
GB7: GB
U301: 68020
U302, U303: F260
U304: F51
U305: F02
U306: F20

Connections:
68K.A0: U301.C4 (A00)
68K.A1: U301.A2 (A01)
68K.A2: U301.E12 (A02)
68K.A3: U301.D13 (A03)
68K.A4: U301.D12 (A04)
68K.A5: U301.C13 (A05)
68K.A6: U301.B13 (A06)
68K.A7: U301.C12 (A07)
68K.A8: U301.A13 (A08)
68K.A9: U301.C11 (A09)
68K.A10: U301.B12 (A10)
68K.A11: U301.A12 (A11)
68K.A12: U301.C10 (A12)
68K.A13: U301.B11 (A13)
68K.A14: U301.A19 (A14)
68K.A15: U301.B10 (A15)
68K.A16: U301.C9 (A16)
68K.A17: U301.C8 (A17)
68K.A18: U301.B8 (A18)
68K.A19: U301.A8 (A19)
68K.A20: U301.B7 (A20)
68K.A21: U301.C7 (A21)
68K.A22: U301.A7 (A22)
68K.A23: U301.A6 (A23)
68K.A24: U301.B6 (A24)
68K.A25: U301.C6 (A25)
68K.A26: U301.A5 (A26)
68K.A27: U301.B5 (A27)
68K.A28: U301.A4 (A28)
68K.A29: U301.C5 (A29)
68K.A30: U301.B4 (A30)
68K.A31: U301.A3 (A31)
68K.BERR~: U301.J2 (BERR), U304.7 (Q)
68K.D0: U301.K13 (D00)
68K.D1: U301.K12 (D01)
68K.D2: U301.L13 (D02)
68K.D3: U301.L12 (D03)
68K.D4: U301.M13 (D04)
68K.D5: U301.M12 (D05)
68K.D6: U301.M11 (D06)
68K.D7: U301.L10 (D07)
68K.D8: U301.N12 (D08)
68K.D9: U301.N11 (D09)
68K.D10: U301.M10 (D10)
68K.D11: U301.L9 (D11)
68K.D12: U301.N10 (D12)
68K.D13: U301.M9 (D13)
68K.D14: U301.N9 (D14)
68K.D15: U301.L8 (D15)
68K.D16: U301.M7 (D16)
68K.D17: U301.N6 (D17)
68K.D18: U301.M6 (D18)
68K.D19: U301.L6 (D19)
68K.D20: U301.N5 (D20)
68K.D21: U301.M5 (D21)
68K.D22: U301.N4 (D22)
68K.D23: U301.L5 (D23)
68K.D24: U301.M4 (D24)
68K.D25: U301.N3 (D25)
68K.D26: U301.M3 (D26)
68K.D27: U301.L4 (D27)
68K.D28: U301.N2 (D28)
68K.D29: U301.M2 (D29)
68K.D30: U301.L3 (D30)
68K.D31: U301.N1 (D31)
68K.DSACK0~: U301.H3 (DSACK0), U302.5 (Q)
68K.DSACK1~: U301.J1 (DSACK1), U303.5 (Q)
68K.FC0: U301.E1 (FC0)
68K.FC1: U301.F3 (FC1)
68K.FC2: U301.F2 (FC2)
68K_RESET~: U301.C1 (RESET)
AS~: U301.L1 (AS)
CLK.2X.B5: U301.C2 (CLK)
DBEN~: U301.G3 (DBEN)
DEV.DSACK0: U302.12 (D0)
DEV.DSACK1: U303.12 (D0)
ECS~: U301.G1 (ECS)
IACK_DSACK: U303.1 (D2)
IO.BERRA~: U306.1 (D0)
IO.BERRD~: U306.2 (D1)
IO.DSACK: U302.1 (D2)
IOP.BERR_EN: U304.1 (A1)
IOP.PROT_BERR~: U306.4 (D2)
IOP.RAM_DSACK: U302.13 (D1), U303.13 (D1)
IOP_CACHE_EN: GB7.1, U301.H1 (CDIS)
IOP_HALT: U305.3 (Q)
IPL0~: U301.J12 (IPL0)
IPL1~: U301.J13 (IPL1)
IPL2~: U301.H12 (IPL2)
unnamed: U304.5 (B2), U306.6 (Q)
PD: U302.2 (D3), U302.3 (D4), U303.2 (D3), U303.3 (D4)
PU: U301.A1 (BGACK), U301.B3 (BR), U301.H2 (AVEC), U304.3 (A3), U304.4 (B1), U304.6 (B3), U305.1 (D0), U305.2 (D1), U306.5 (D3)
RAM.PERR: U304.2 (A2)
SIZ0: U301.F1 (SIZ0)
SIZ1: U301.G2 (SIZ1)
WR~: U301.L2 (WR)
