Datamuseum-DK/R1000.HwDoc/Schematics/IOC/pg_03.kicad_sch

## KiCad design Schematics/IOC/pg_03.kicad_sch (2023-01-10)

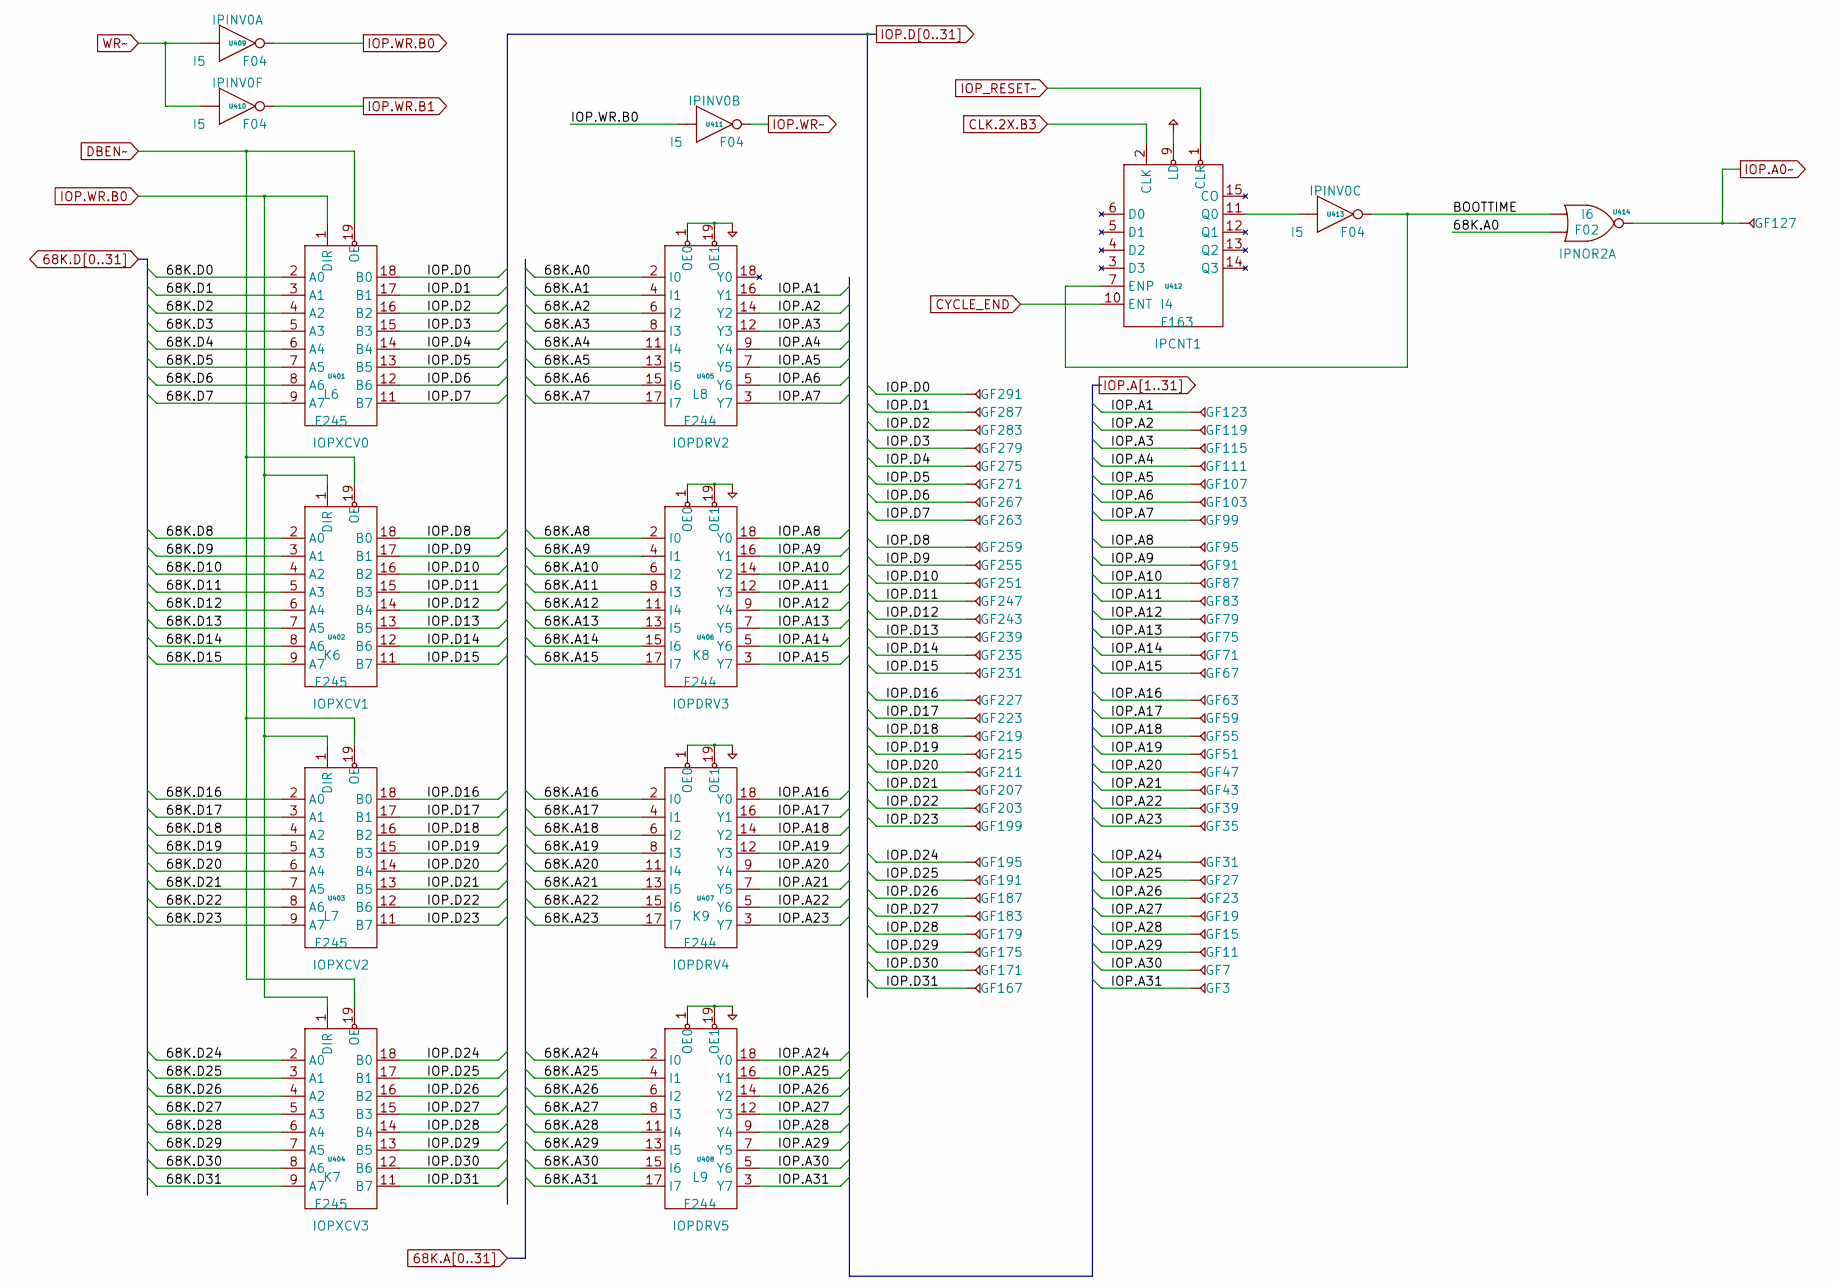
[picture p351: schematic pg_03.kicad_sch]

Parts:
GF3, GF7, GF11, GF15, GF19, GF23, GF27, GF31, GF35, GF39, GF43, GF47, GF51, GF55, GF59, GF63, GF67, GF71, GF75, GF79, GF83, GF87, GF91, GF95, GF99, GF103, GF107, GF111, GF115, GF119, GF123, GF127, GF167, GF171, GF175, GF179, GF183, GF187, GF191, GF195, GF199, GF203, GF207, GF211, GF215, GF219, GF223, GF227, GF231, GF235, GF239, GF243, GF247, GF251, GF255, GF259, GF263, GF267, GF271, GF275, GF279, GF283, GF287, GF291: GF
U401, U402, U403, U404: F245
U405, U406, U407, U408: F244
U409, U410, U411, U413: F04
U412: F163
U414: F02

Connections:
68K.A0: U405.2 (I0), U414.2 (D1)
68K.A1: U405.4 (I1)
68K.A2: U405.6 (I2)
68K.A3: U405.8 (I3)
68K.A4: U405.11 (I4)
68K.A5: U405.13 (I5)
68K.A6: U405.15 (I6)
68K.A7: U405.17 (I7)
68K.A8: U406.2 (I0)
68K.A9: U406.4 (I1)
68K.A10: U406.6 (I2)
68K.A11: U406.8 (I3)
68K.A12: U406.11 (I4)
68K.A13: U406.13 (I5)
68K.A14: U406.15 (I6)
68K.A15: U406.17 (I7)
68K.A16: U407.2 (I0)
68K.A17: U407.4 (I1)
68K.A18: U407.6 (I2)
68K.A19: U407.8 (I3)
68K.A20: U407.11 (I4)
68K.A21: U407.13 (I5)
68K.A22: U407.15 (I6)
68K.A23: U407.17 (I7)
68K.A24: U408.2 (I0)
68K.A25: U408.4 (I1)
68K.A26: U408.6 (I2)
68K.A27: U408.8 (I3)
68K.A28: U408.11 (I4)
68K.A29: U408.13 (I5)
68K.A30: U408.15 (I6)
68K.A31: U408.17 (I7)
68K.D0: U401.2 (A0)
68K.D1: U401.3 (A1)
68K.D2: U401.4 (A2)
68K.D3: U401.5 (A3)
68K.D4: U401.6 (A4)
68K.D5: U401.7 (A5)
68K.D6: U401.8 (A6)
68K.D7: U401.9 (A7)
68K.D8: U402.2 (A0)
68K.D9: U402.3 (A1)
68K.D10: U402.4 (A2)
68K.D11: U402.5 (A3)
68K.D12: U402.6 (A4)
68K.D13: U402.7 (A5)
68K.D14: U402.8 (A6)
68K.D15: U402.9 (A7)
68K.D16: U403.2 (A0)
68K.D17: U403.3 (A1)
68K.D18: U403.4 (A2)
68K.D19: U403.5 (A3)
68K.D20: U403.6 (A4)
68K.D21: U403.7 (A5)
68K.D22: U403.8 (A6)
68K.D23: U403.9 (A7)
68K.D24: U404.2 (A0)
68K.D25: U404.3 (A1)
68K.D26: U404.4 (A2)
68K.D27: U404.5 (A3)
68K.D28: U404.6 (A4)
68K.D29: U404.7 (A5)
68K.D30: U404.8 (A6)
68K.D31: U404.9 (A7)
BOOTTIME: U412.7 (ENP), U413.2 (Q), U414.1 (D0)
CLK.2X.B3: U412.2 (CLK)
CYCLE_END: U412.10 (ENT)
DBEN~: U401.19 (OE), U402.19 (OE), U403.19 (OE), U404.19 (OE)
IOP.A0~: GF127.1, U414.3 (Q)
IOP.A1: GF123.1, U405.16 (Y1)
IOP.A2: GF119.1, U405.14 (Y2)
IOP.A3: GF115.1, U405.12 (Y3)
IOP.A4: GF111.1, U405.9 (Y4)
IOP.A5: GF107.1, U405.7 (Y5)
IOP.A6: GF103.1, U405.5 (Y6)
IOP.A7: GF99.1, U405.3 (Y7)
IOP.A8: GF95.1, U406.18 (Y0)
IOP.A9: GF91.1, U406.16 (Y1)
IOP.A10: GF87.1, U406.14 (Y2)
IOP.A11: GF83.1, U406.12 (Y3)
IOP.A12: GF79.1, U406.9 (Y4)
IOP.A13: GF75.1, U406.7 (Y5)
IOP.A14: GF71.1, U406.5 (Y6)
IOP.A15: GF67.1, U406.3 (Y7)
IOP.A16: GF63.1, U407.18 (Y0)
IOP.A17: GF59.1, U407.16 (Y1)
IOP.A18: GF55.1, U407.14 (Y2)
IOP.A19: GF51.1, U407.12 (Y3)
IOP.A20: GF47.1, U407.9 (Y4)
IOP.A21: GF43.1, U407.7 (Y5)
IOP.A22: GF39.1, U407.5 (Y6)
IOP.A23: GF35.1, U407.3 (Y7)
IOP.A24: GF31.1, U408.18 (Y0)
IOP.A25: GF27.1, U408.16 (Y1)
IOP.A26: GF23.1, U408.14 (Y2)
IOP.A27: GF19.1, U408.12 (Y3)
IOP.A28: GF15.1, U408.9 (Y4)
IOP.A29: GF11.1, U408.7 (Y5)
IOP.A30: GF7.1, U408.5 (Y6)
IOP.A31: GF3.1, U408.3 (Y7)
IOP.D0: GF291.1, U401.18 (B0)
IOP.D1: GF287.1, U401.17 (B1)
IOP.D2: GF283.1, U401.16 (B2)
IOP.D3: GF279.1, U401.15 (B3)
IOP.D4: GF275.1, U401.14 (B4)
IOP.D5: GF271.1, U401.13 (B5)
IOP.D6: GF267.1, U401.12 (B6)
IOP.D7: GF263.1, U401.11 (B7)
IOP.D8: GF259.1, U402.18 (B0)
IOP.D9: GF255.1, U402.17 (B1)
IOP.D10: GF251.1, U402.16 (B2)
IOP.D11: GF247.1, U402.15 (B3)
IOP.D12: GF243.1, U402.14 (B4)
IOP.D13: GF239.1, U402.13 (B5)
IOP.D14: GF235.1, U402.12 (B6)
IOP.D15: GF231.1, U402.11 (B7)
IOP.D16: GF227.1, U403.18 (B0)
IOP.D17: GF223.1, U403.17 (B1)
IOP.D18: GF219.1, U403.16 (B2)
IOP.D19: GF215.1, U403.15 (B3)
IOP.D20: GF211.1, U403.14 (B4)
IOP.D21: GF207.1, U403.13 (B5)
IOP.D22: GF203.1, U403.12 (B6)
IOP.D23: GF199.1, U403.11 (B7)
IOP.D24: GF195.1, U404.18 (B0)
IOP.D25: GF191.1, U404.17 (B1)
IOP.D26: GF187.1, U404.16 (B2)
IOP.D27: GF183.1, U404.15 (B3)
IOP.D28: GF179.1, U404.14 (B4)
IOP.D29: GF175.1, U404.13 (B5)
IOP.D30: GF171.1, U404.12 (B6)
IOP.D31: GF167.1, U404.11 (B7)
IOP.WR.B0: U401.1 (DIR), U402.1 (DIR), U403.1 (DIR), U404.1 (DIR), U409.2 (Q), U411.1 (D0)
IOP.WR.B1: U410.2 (Q)
IOP.WR~: U411.2 (Q)
IOP_RESET~: U412.1 (CLR)
unnamed: U412.11 (Q0), U413.1 (D0)
PD: U405.1 (OE0), U405.19 (OE1), U406.1 (OE0), U406.19 (OE1), U407.1 (OE0), U407.19 (OE1), U408.1 (OE0), U408.19 (OE1)
PU: U412.9 (LD)
WR~: U409.1 (D0), U410.1 (D0)
