Datamuseum-DK/R1000.HwDoc/Schematics/IOC/pg_04.kicad_sch

## KiCad design Schematics/IOC/pg_04.kicad_sch (2023-01-10)

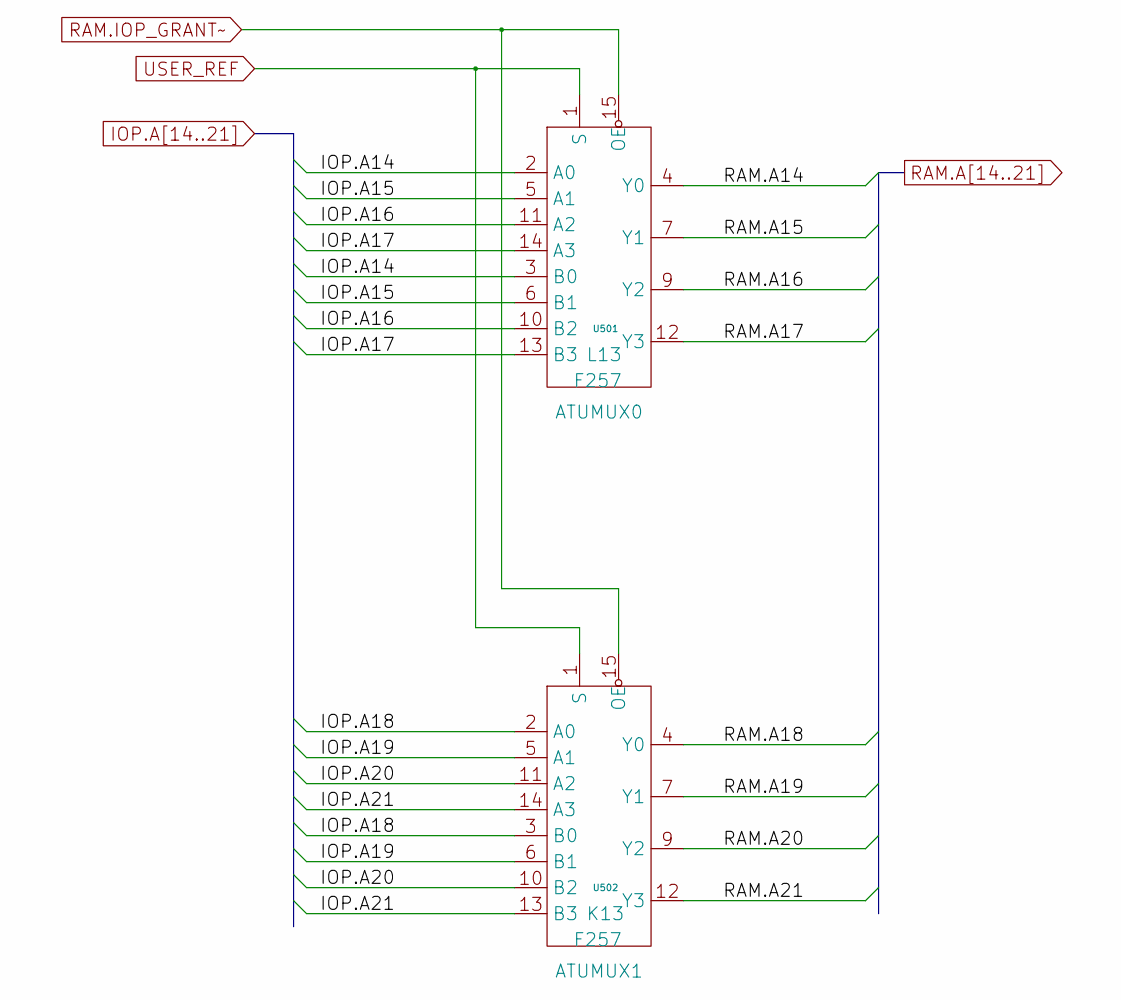
[picture p352: schematic pg_04.kicad_sch]

Parts:
U501, U502: F257

Connections:
IOP.A14: U501.2 (A0), U501.3 (B0)
IOP.A15: U501.5 (A1), U501.6 (B1)
IOP.A16: U501.10 (B2), U501.11 (A2)
IOP.A17: U501.13 (B3), U501.14 (A3)
IOP.A18: U502.2 (A0), U502.3 (B0)
IOP.A19: U502.5 (A1), U502.6 (B1)
IOP.A20: U502.10 (B2), U502.11 (A2)
IOP.A21: U502.13 (B3), U502.14 (A3)
RAM.A14: U501.4 (Y0)
RAM.A15: U501.7 (Y1)
RAM.A16: U501.9 (Y2)
RAM.A17: U501.12 (Y3)
RAM.A18: U502.4 (Y0)
RAM.A19: U502.7 (Y1)
RAM.A20: U502.9 (Y2)
RAM.A21: U502.12 (Y3)
RAM.IOP_GRANT~: U501.15 (OE), U502.15 (OE)
USER_REF: U501.1 (S), U502.1 (S)
