Datamuseum-DK/R1000.HwDoc/Schematics/IOC/pg_05.kicad_sch

## KiCad design Schematics/IOC/pg_05.kicad_sch (2023-01-10)

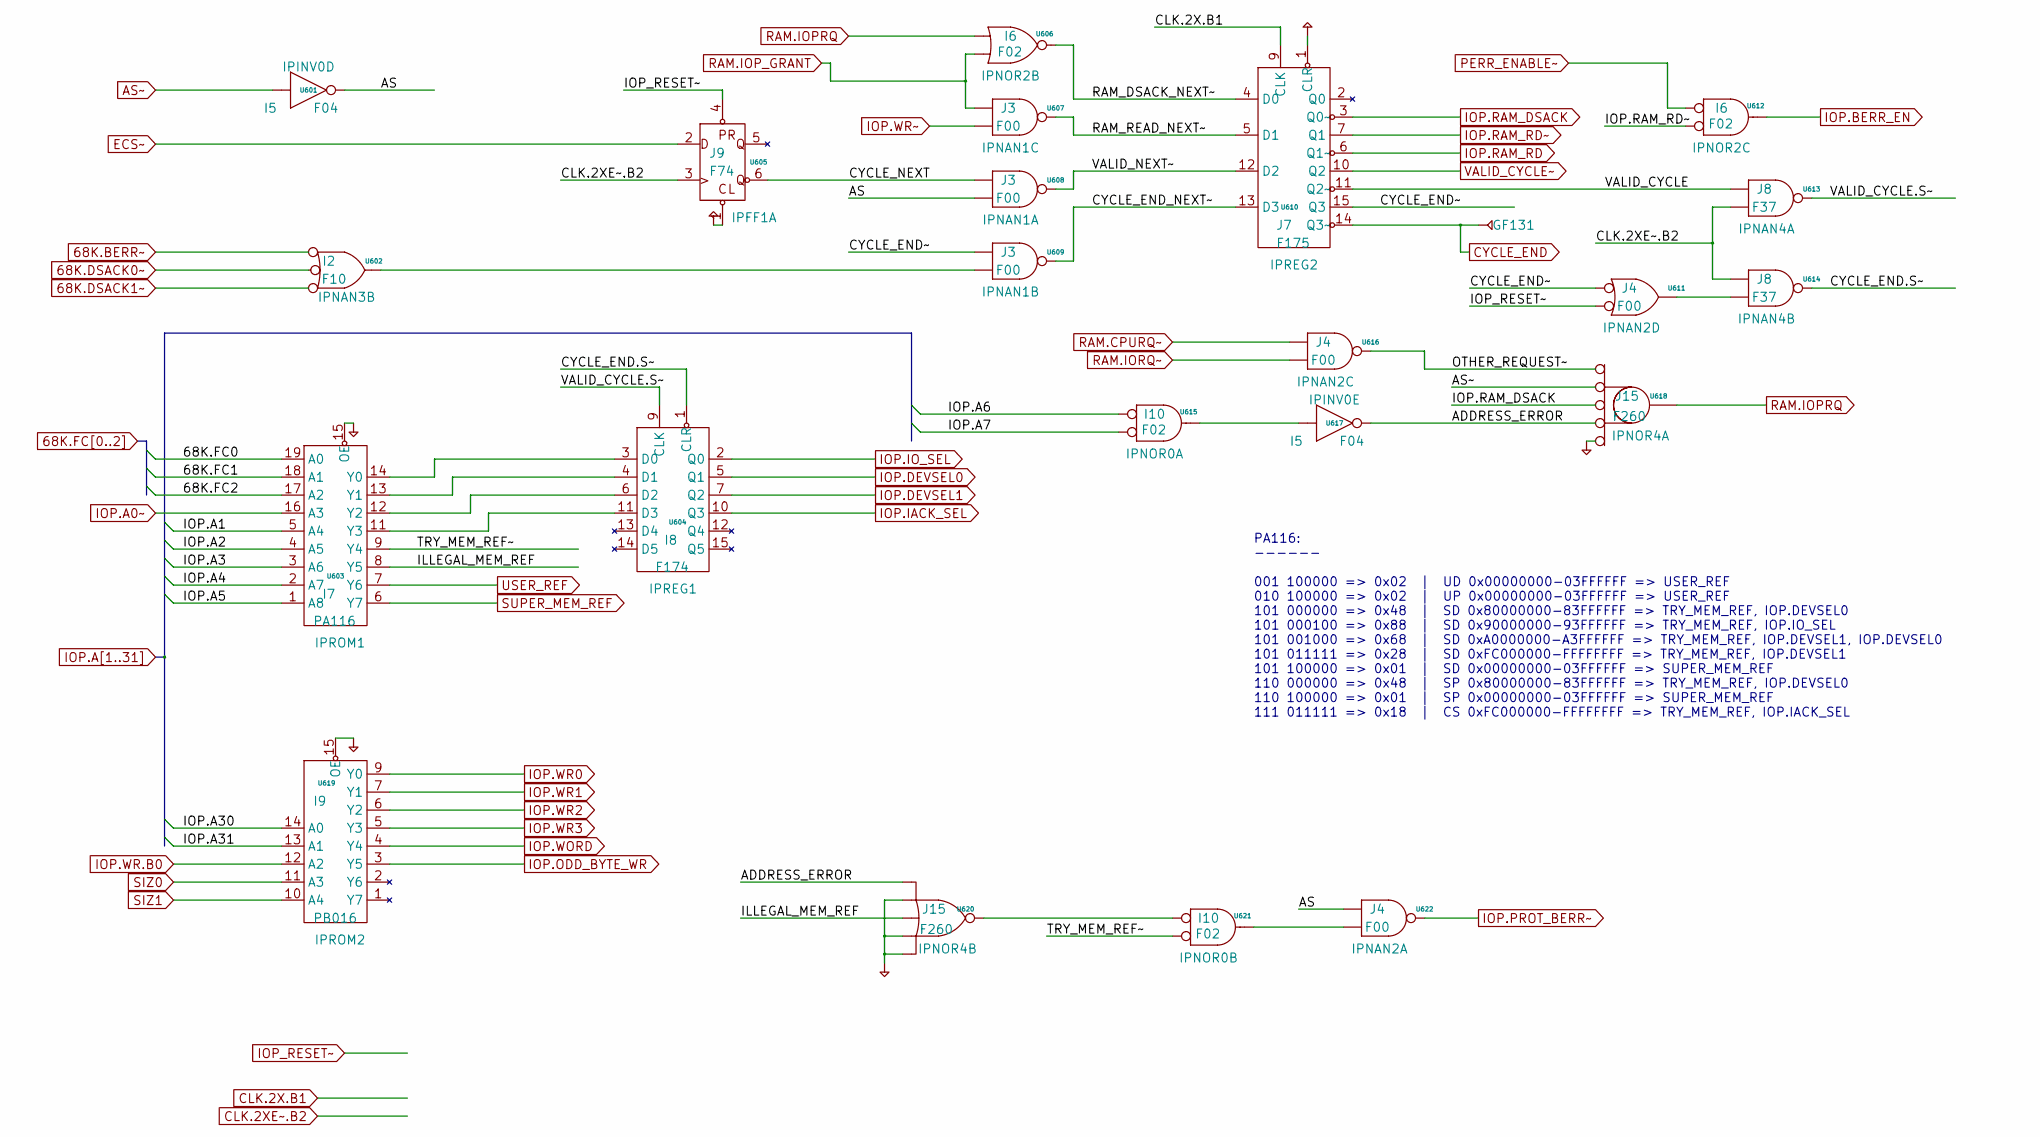
[picture p353: schematic pg_05.kicad_sch]

Parts:
GF131: GF
U601, U617: F04
U602: F10
U603: PA116
U604: F174
U605: F74
U606, U612, U615, U621: F02
U607, U608, U609, U611, U616, U622: F00
U610: F175
U613, U614: F37
U618, U620: F260
U619: PB016

Connections:
68K.BERR~: U602.1 (D0)
68K.DSACK0~: U602.2 (D1)
68K.DSACK1~: U602.3 (D2)
68K.FC0: U603.19 (A0)
68K.FC1: U603.18 (A1)
68K.FC2: U603.17 (A2)
ADDRESS_ERROR: U617.2 (Q), U618.2 (D3), U620.12 (D0)
AS: U601.2 (Q), U608.2 (D1), U622.1 (D0)
AS~: U601.1 (D0), U618.13 (D1)
CLK.2X.B1: U610.9 (CLK)
CLK.2XE~.B2: U605.3 (CLK), U613.2 (D1), U614.1 (D0)
CYCLE_END: GF131.1, U610.14 (Q3~)
CYCLE_END.S~: U604.1 (CLR), U614.3 (Q)
CYCLE_END_NEXT~: U609.3 (Q), U610.13 (D3)
CYCLE_END~: U609.1 (D0), U610.15 (Q3), U611.1 (D0)
CYCLE_NEXT: U605.6 (Q_), U608.1 (D0)
ECS~: U605.2 (D)
ILLEGAL_MEM_REF: U603.8 (Y5), U620.1 (D2)
IOP.A0~: U603.16 (A3)
IOP.A1: U603.5 (A4)
IOP.A2: U603.4 (A5)
IOP.A3: U603.3 (A6)
IOP.A4: U603.2 (A7)
IOP.A5: U603.1 (A8)
IOP.A6: U615.1 (D0)
IOP.A7: U615.2 (D1)
IOP.A30: U619.14 (A0)
IOP.A31: U619.13 (A1)
IOP.BERR_EN: U612.3 (Q)
IOP.DEVSEL0: U604.5 (Q1)
IOP.DEVSEL1: U604.7 (Q2)
IOP.IACK_SEL: U604.10 (Q3)
IOP.IO_SEL: U604.2 (Q0)
IOP.ODD_BYTE_WR: U619.3 (Y5)
IOP.PROT_BERR~: U622.3 (Q)
IOP.RAM_DSACK: U610.3 (Q0~), U618.1 (D2)
IOP.RAM_RD: U610.6 (Q1~)
IOP.RAM_RD~: U610.7 (Q1), U612.2 (D1)
IOP.WORD: U619.4 (Y4)
IOP.WR0: U619.9 (Y0)
IOP.WR1: U619.7 (Y1)
IOP.WR2: U619.6 (Y2)
IOP.WR3: U619.5 (Y3)
IOP.WR.B0: U619.12 (A2)
IOP.WR~: U607.2 (D1)
IOP_RESET~: U605.4 (PR_), U611.2 (D1)
unnamed: U602.4 (Q), U609.2 (D1)
unnamed: U603.11 (Y3), U604.11 (D3)
unnamed: U603.12 (Y2), U604.6 (D2)
unnamed: U603.13 (Y1), U604.4 (D1)
unnamed: U603.14 (Y0), U604.3 (D0)
unnamed: U611.3 (Q), U614.2 (D1)
unnamed: U615.3 (Q), U617.1 (D0)
unnamed: U620.5 (Q), U621.1 (D0)
unnamed: U621.3 (Q), U622.2 (D1)
OTHER_REQUEST~: U616.3 (Q), U618.12 (D0)
PD: U603.15 (OE), U618.3 (D4), U619.15 (OE), U620.2 (D3), U620.3 (D4), U620.13 (D1)
PERR_ENABLE~: U612.1 (D0)
PU: U605.1 (CL_), U610.1 (CLR)
RAM.CPURQ~: U616.1 (D0)
RAM.IOPRQ: U606.1 (D0), U618.5 (Q)
RAM.IOP_GRANT: U606.2 (D1), U607.1 (D0)
RAM.IORQ~: U616.2 (D1)
RAM_DSACK_NEXT~: U606.3 (Q), U610.4 (D0)
RAM_READ_NEXT~: U607.3 (Q), U610.5 (D1)
SIZ0: U619.11 (A3)
SIZ1: U619.10 (A4)
SUPER_MEM_REF: U603.6 (Y7)
TRY_MEM_REF~: U603.9 (Y4), U621.2 (D1)
USER_REF: U603.7 (Y6)
VALID_CYCLE: U610.11 (Q2~), U613.1 (D0)
VALID_CYCLE.S~: U604.9 (CLK), U613.3 (Q)
VALID_CYCLE~: U610.10 (Q2)
VALID_NEXT~: U608.3 (Q), U610.12 (D2)

Notes on the sheet:
PA116: ------ 001 100000 => 0x02 | UD 0x00000000-03FFFFFF => USER_REF 010 100000 => 0x02 | UP 0x00000000-03FFFFFF => USER_REF 101 000000 => 0x48 | SD 0x80000000-83FFFFFF => TRY_MEM_REF, IOP.DEVSEL0 101 000100 => 0x88 | SD 0x90000000-93FFFFFF => TRY_MEM_REF, IOP.IO_SEL 101 001000 => 0x68 | SD 0xA000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
