Datamuseum-DK/R1000.HwDoc/Schematics/IOC/pg_06.kicad_sch

## KiCad design Schematics/IOC/pg_06.kicad_sch (2023-01-10)

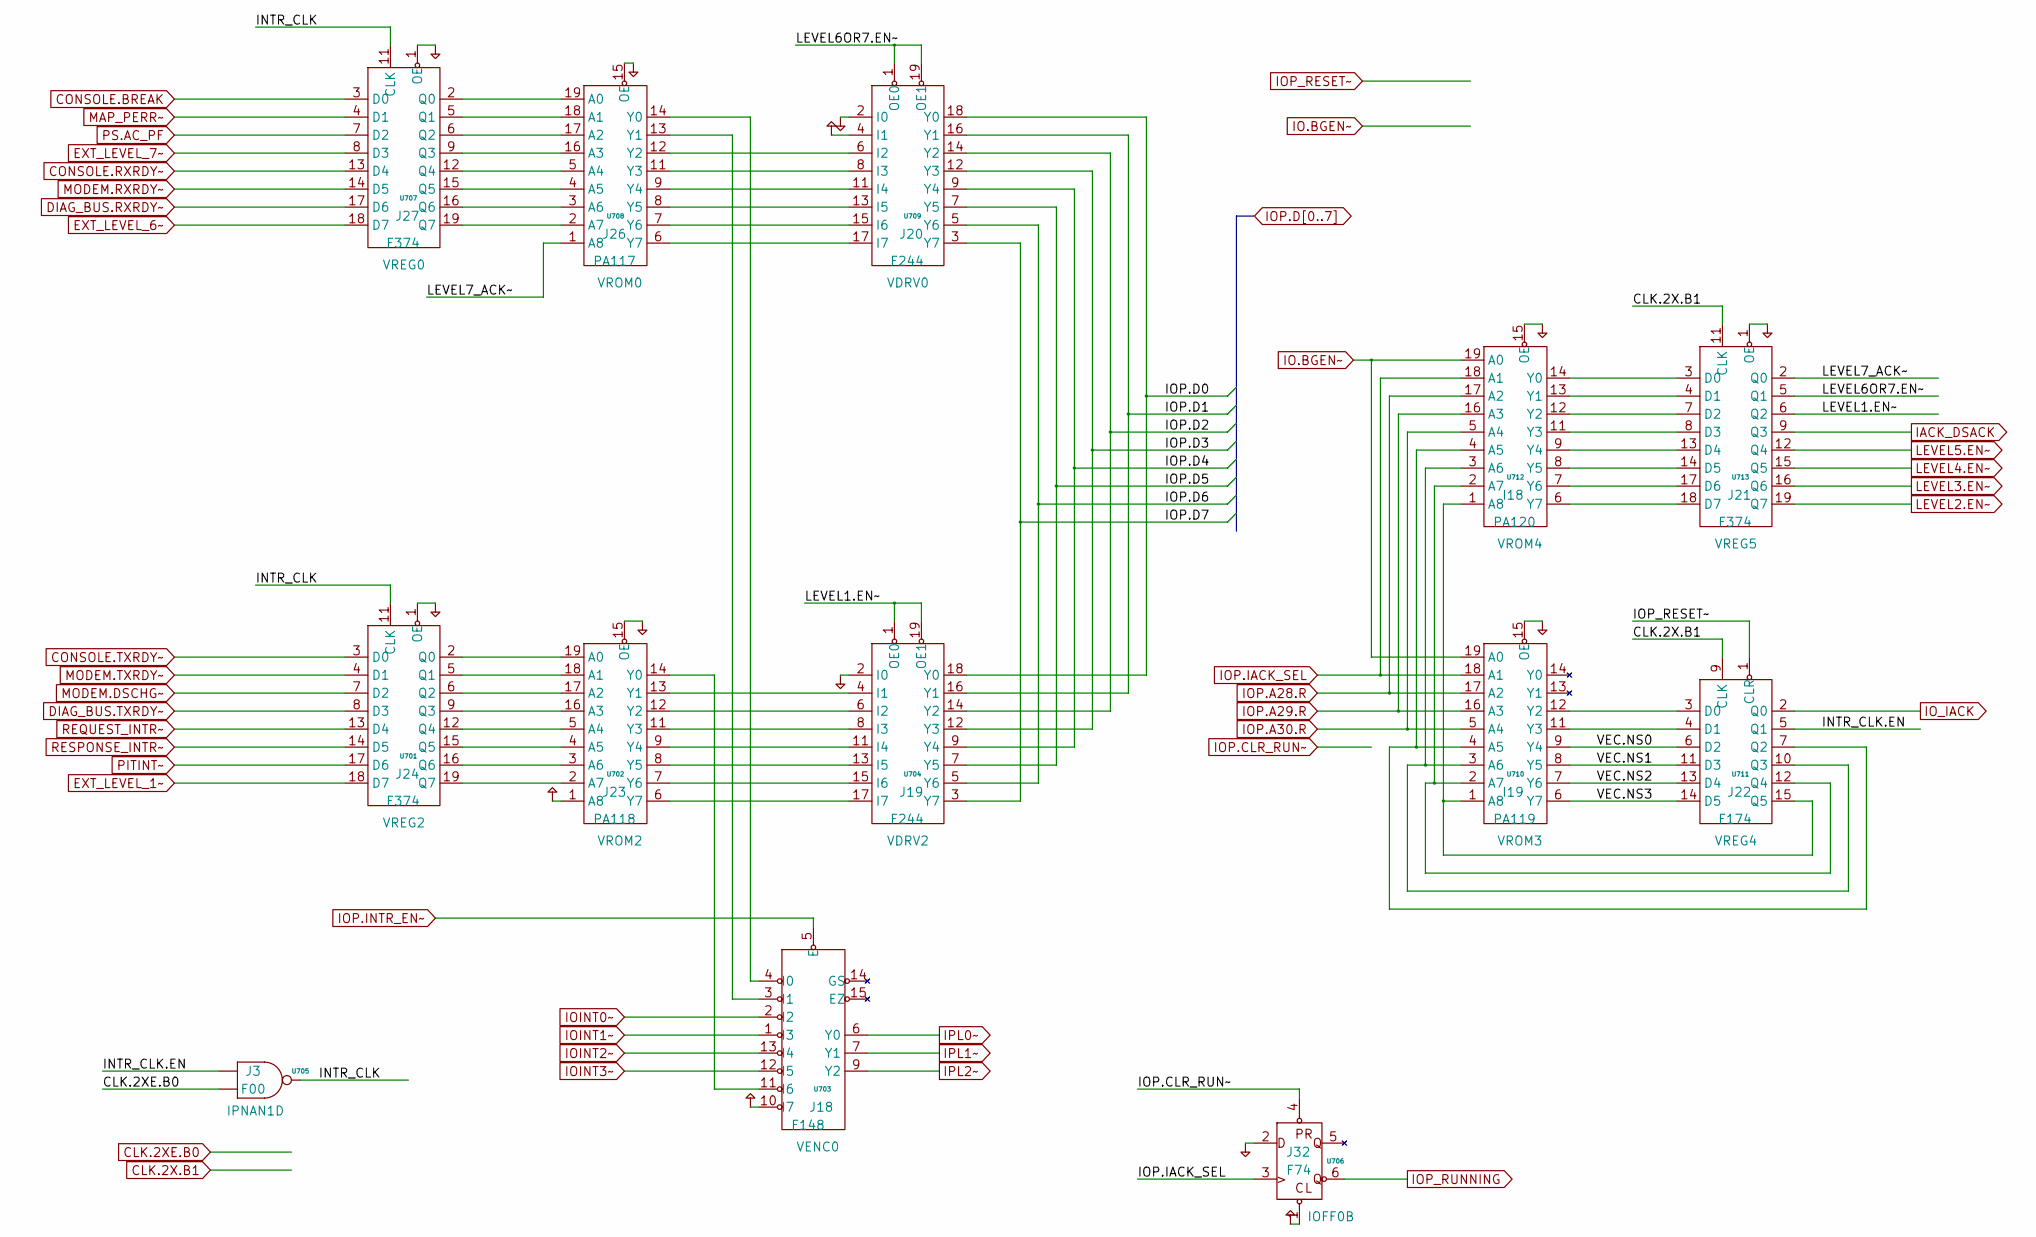
[picture p354: schematic pg_06.kicad_sch]

Parts:
U701, U707, U713: F374
U702: PA118
U703: F148
U704, U709: F244
U705: F00
U706: F74
U708: PA117
U710: PA119
U711: F174
U712: PA120

Connections:
CLK.2X.B1: U711.9 (CLK), U713.11 (CLK)
CLK.2XE.B0: U705.2 (D1)
CONSOLE.BREAK: U707.3 (D0)
CONSOLE.RXRDY~: U707.13 (D4)
CONSOLE.TXRDY~: U701.3 (D0)
DIAG_BUS.RXRDY~: U707.17 (D6)
DIAG_BUS.TXRDY~: U701.8 (D3)
EXT_LEVEL_1~: U701.18 (D7)
EXT_LEVEL_6~: U707.18 (D7)
EXT_LEVEL_7~: U707.8 (D3)
IACK_DSACK: U713.9 (Q3)
INTR_CLK: U701.11 (CLK), U705.3 (Q), U707.11 (CLK)
INTR_CLK.EN: U705.1 (D0), U711.5 (Q1)
IO.BGEN~: U710.19 (A0), U712.19 (A0)
IOINT0~: U703.2 (I2)
IOINT1~: U703.1 (I3)
IOINT2~: U703.13 (I4)
IOINT3~: U703.12 (I5)
IOP.A28.R: U710.17 (A2), U712.17 (A2)
IOP.A29.R: U710.16 (A3), U712.16 (A3)
IOP.A30.R: U710.5 (A4), U712.5 (A4)
IOP.CLR_RUN~: U706.4 (PR_)
IOP.D0: U704.18 (Y0), U709.18 (Y0)
IOP.D1: U704.16 (Y1), U709.16 (Y1)
IOP.D2: U704.14 (Y2), U709.14 (Y2)
IOP.D3: U704.12 (Y3), U709.12 (Y3)
IOP.D4: U704.9 (Y4), U709.9 (Y4)
IOP.D5: U704.7 (Y5), U709.7 (Y5)
IOP.D6: U704.5 (Y6), U709.5 (Y6)
IOP.D7: U704.3 (Y7), U709.3 (Y7)
IOP.IACK_SEL: U706.3 (CLK), U710.18 (A1), U712.18 (A1)
IOP.INTR_EN~: U703.5 (E)
IOP_RESET~: U711.1 (CLR)
IOP_RUNNING: U706.6 (Q_)
IO_IACK: U711.2 (Q0)
IPL0~: U703.6 (Y0)
IPL1~: U703.7 (Y1)
IPL2~: U703.9 (Y2)
LEVEL1.EN~: U704.1 (OE0), U704.19 (OE1), U713.6 (Q2)
LEVEL2.EN~: U713.19 (Q7)
LEVEL3.EN~: U713.16 (Q6)
LEVEL4.EN~: U713.15 (Q5)
LEVEL5.EN~: U713.12 (Q4)
LEVEL6OR7.EN~: U709.1 (OE0), U709.19 (OE1), U713.5 (Q1)
LEVEL7_ACK~: U708.1 (A8), U713.2 (Q0)
MAP_PERR~: U707.4 (D1)
MODEM.DSCHG~: U701.7 (D2)
MODEM.RXRDY~: U707.14 (D5)
MODEM.TXRDY~: U701.4 (D1)
unnamed: U701.2 (Q0), U702.19 (A0)
unnamed: U701.5 (Q1), U702.18 (A1)
unnamed: U701.6 (Q2), U702.17 (A2)
unnamed: U701.9 (Q3), U702.16 (A3)
unnamed: U701.12 (Q4), U702.5 (A4)
unnamed: U701.15 (Q5), U702.4 (A5)
unnamed: U701.16 (Q6), U702.3 (A6)
unnamed: U701.19 (Q7), U702.2 (A7)
unnamed: U702.6 (Y7), U704.17 (I7)
unnamed: U702.7 (Y6), U704.15 (I6)
unnamed: U702.8 (Y5), U704.13 (I5)
unnamed: U702.9 (Y4), U704.11 (I4)
unnamed: U702.11 (Y3), U704.8 (I3)
unnamed: U702.12 (Y2), U704.6 (I2)
unnamed: U702.13 (Y1), U704.4 (I1)
unnamed: U702.14 (Y0), U703.11 (I6)
unnamed: U703.3 (I1), U708.13 (Y1)
unnamed: U703.4 (I0), U708.14 (Y0)
unnamed: U707.2 (Q0), U708.19 (A0)
unnamed: U707.5 (Q1), U708.18 (A1)
unnamed: U707.6 (Q2), U708.17 (A2)
unnamed: U707.9 (Q3), U708.16 (A3)
unnamed: U707.12 (Q4), U708.5 (A4)
unnamed: U707.15 (Q5), U708.4 (A5)
unnamed: U707.16 (Q6), U708.3 (A6)
unnamed: U707.19 (Q7), U708.2 (A7)
unnamed: U708.6 (Y7), U709.17 (I7)
unnamed: U708.7 (Y6), U709.15 (I6)
unnamed: U708.8 (Y5), U709.13 (I5)
unnamed: U708.9 (Y4), U709.11 (I4)
unnamed: U708.11 (Y3), U709.8 (I3)
unnamed: U708.12 (Y2), U709.6 (I2)
unnamed: U710.1 (A8), U711.15 (Q5), U712.1 (A8)
unnamed: U710.2 (A7), U711.12 (Q4), U712.2 (A7)
unnamed: U710.3 (A6), U711.10 (Q3), U712.3 (A6)
unnamed: U710.4 (A5), U711.7 (Q2), U712.4 (A5)
unnamed: U710.11 (Y3), U711.4 (D1)
unnamed: U710.12 (Y2), U711.3 (D0)
unnamed: U712.6 (Y7), U713.18 (D7)
unnamed: U712.7 (Y6), U713.17 (D6)
unnamed: U712.8 (Y5), U713.14 (D5)
unnamed: U712.9 (Y4), U713.13 (D4)
unnamed: U712.11 (Y3), U713.8 (D3)
unnamed: U712.12 (Y2), U713.7 (D2)
unnamed: U712.13 (Y1), U713.4 (D1)
unnamed: U712.14 (Y0), U713.3 (D0)
PD: U701.1 (OE), U702.15 (OE), U704.2 (I0), U706.2 (D), U707.1 (OE), U708.15 (OE), U709.2 (I0), U710.15 (OE), U712.15 (OE), U713.1 (OE)
PITINT~: U701.17 (D6)
PS.AC_PF: U707.7 (D2)
PU: U702.1 (A8), U703.10 (I7), U706.1 (CL_), U709.4 (I1)
REQUEST_INTR~: U701.13 (D4)
RESPONSE_INTR~: U701.14 (D5)
VEC.NS0: U710.9 (Y4), U711.6 (D2)
VEC.NS1: U710.8 (Y5), U711.11 (D3)
VEC.NS2: U710.7 (Y6), U711.13 (D4)
VEC.NS3: U710.6 (Y7), U711.14 (D5)
