Datamuseum-DK/R1000.HwDoc/Schematics/IOC/pg_07.kicad_sch

## KiCad design Schematics/IOC/pg_07.kicad_sch (2023-01-10)

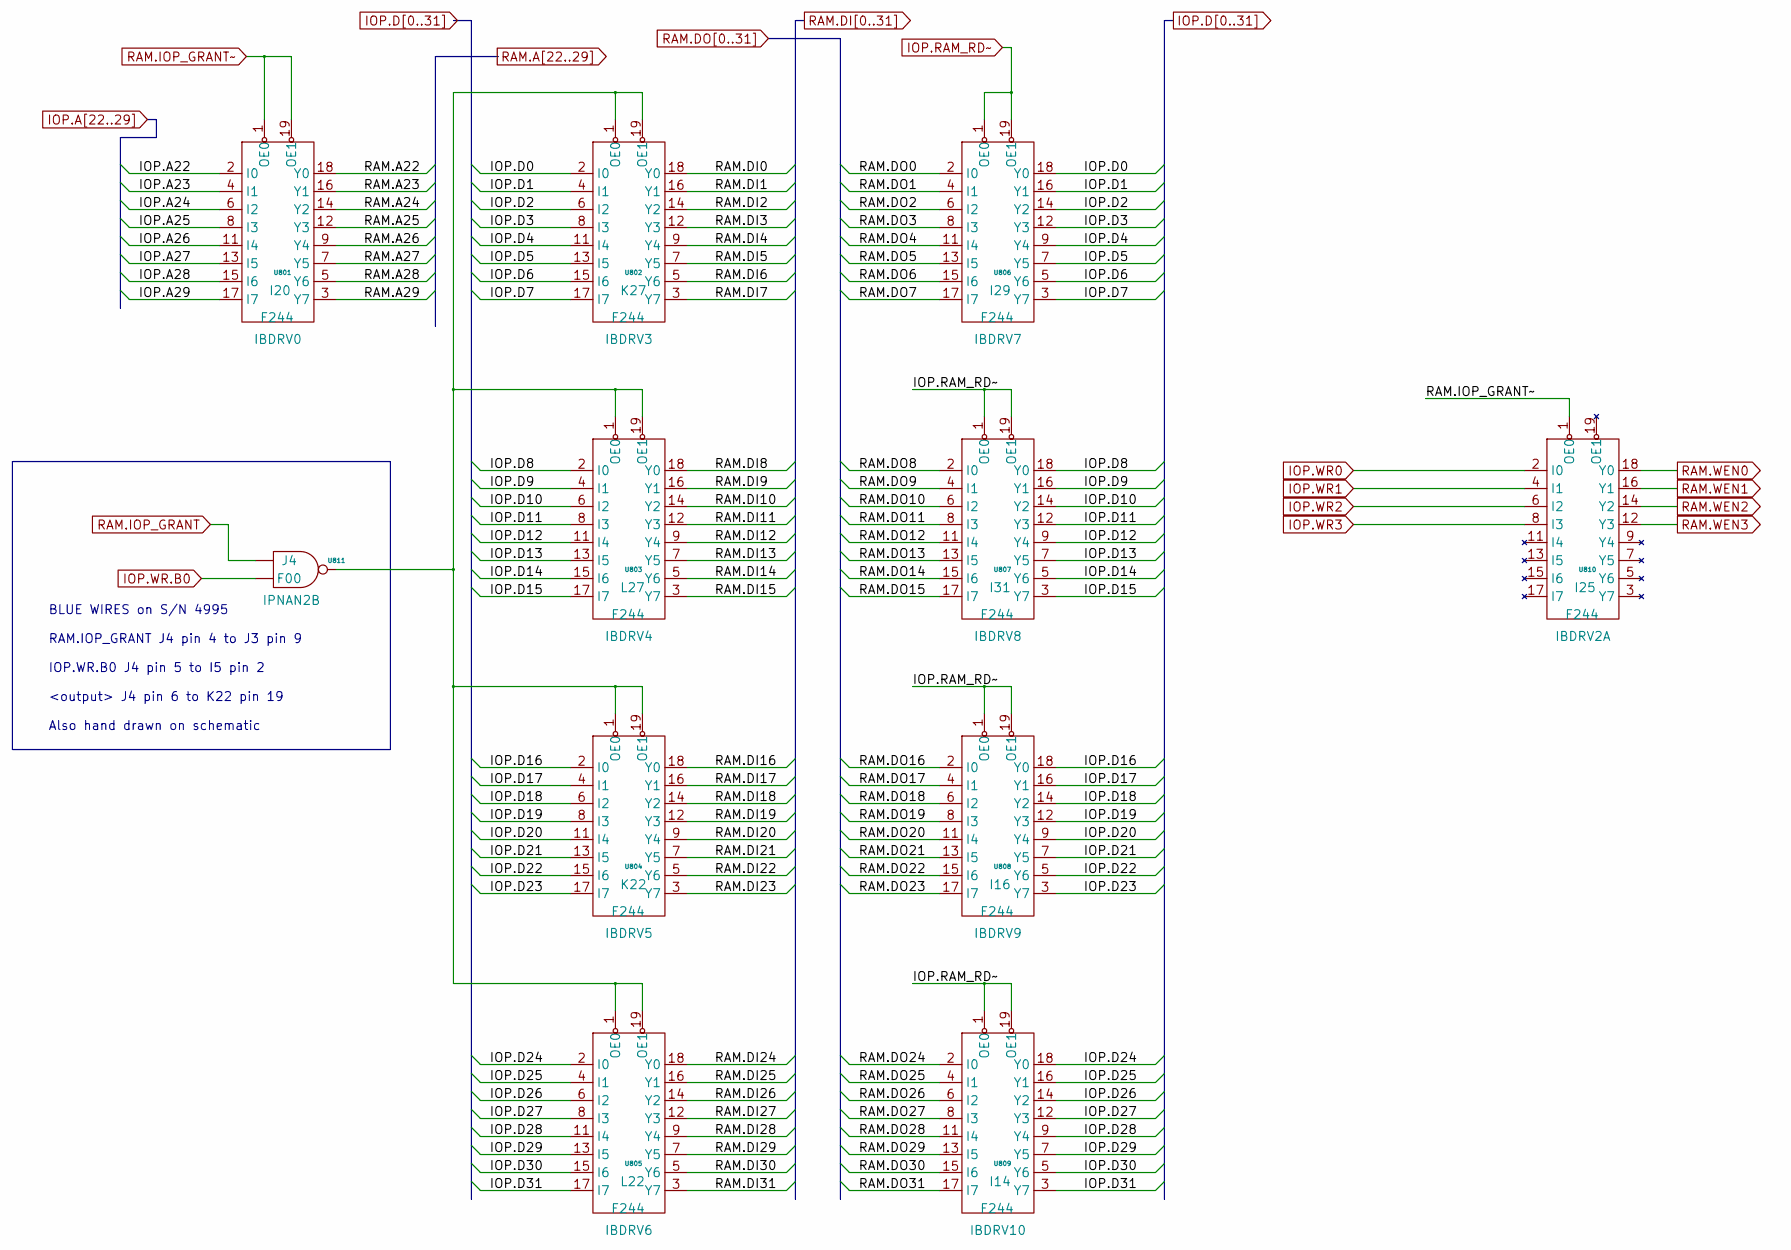
[picture p355: schematic pg_07.kicad_sch]

Parts:
U801, U802, U803, U804, U805, U806, U807, U808, U809, U810: F244
U811: F00

Connections:
IOP.A22: U801.2 (I0)
IOP.A23: U801.4 (I1)
IOP.A24: U801.6 (I2)
IOP.A25: U801.8 (I3)
IOP.A26: U801.11 (I4)
IOP.A27: U801.13 (I5)
IOP.A28: U801.15 (I6)
IOP.A29: U801.17 (I7)
IOP.D0: U802.2 (I0), U806.18 (Y0)
IOP.D1: U802.4 (I1), U806.16 (Y1)
IOP.D2: U802.6 (I2), U806.14 (Y2)
IOP.D3: U802.8 (I3), U806.12 (Y3)
IOP.D4: U802.11 (I4), U806.9 (Y4)
IOP.D5: U802.13 (I5), U806.7 (Y5)
IOP.D6: U802.15 (I6), U806.5 (Y6)
IOP.D7: U802.17 (I7), U806.3 (Y7)
IOP.D8: U803.2 (I0), U807.18 (Y0)
IOP.D9: U803.4 (I1), U807.16 (Y1)
IOP.D10: U803.6 (I2), U807.14 (Y2)
IOP.D11: U803.8 (I3), U807.12 (Y3)
IOP.D12: U803.11 (I4), U807.9 (Y4)
IOP.D13: U803.13 (I5), U807.7 (Y5)
IOP.D14: U803.15 (I6), U807.5 (Y6)
IOP.D15: U803.17 (I7), U807.3 (Y7)
IOP.D16: U804.2 (I0), U808.18 (Y0)
IOP.D17: U804.4 (I1), U808.16 (Y1)
IOP.D18: U804.6 (I2), U808.14 (Y2)
IOP.D19: U804.8 (I3), U808.12 (Y3)
IOP.D20: U804.11 (I4), U808.9 (Y4)
IOP.D21: U804.13 (I5), U808.7 (Y5)
IOP.D22: U804.15 (I6), U808.5 (Y6)
IOP.D23: U804.17 (I7), U808.3 (Y7)
IOP.D24: U805.2 (I0), U809.18 (Y0)
IOP.D25: U805.4 (I1), U809.16 (Y1)
IOP.D26: U805.6 (I2), U809.14 (Y2)
IOP.D27: U805.8 (I3), U809.12 (Y3)
IOP.D28: U805.11 (I4), U809.9 (Y4)
IOP.D29: U805.13 (I5), U809.7 (Y5)
IOP.D30: U805.15 (I6), U809.5 (Y6)
IOP.D31: U805.17 (I7), U809.3 (Y7)
IOP.RAM_RD~: U806.1 (OE0), U806.19 (OE1), U807.1 (OE0), U807.19 (OE1), U808.1 (OE0), U808.19 (OE1), U809.1 (OE0), U809.19 (OE1)
IOP.WR0: U810.2 (I0)
IOP.WR1: U810.4 (I1)
IOP.WR2: U810.6 (I2)
IOP.WR3: U810.8 (I3)
IOP.WR.B0: U811.2 (D1)
unnamed: U802.1 (OE0), U802.19 (OE1), U803.1 (OE0), U803.19 (OE1), U804.1 (OE0), U804.19 (OE1), U805.1 (OE0), U805.19 (OE1), U811.3 (Q)
RAM.A22: U801.18 (Y0)
RAM.A23: U801.16 (Y1)
RAM.A24: U801.14 (Y2)
RAM.A25: U801.12 (Y3)
RAM.A26: U801.9 (Y4)
RAM.A27: U801.7 (Y5)
RAM.A28: U801.5 (Y6)
RAM.A29: U801.3 (Y7)
RAM.DI0: U802.18 (Y0)
RAM.DI1: U802.16 (Y1)
RAM.DI2: U802.14 (Y2)
RAM.DI3: U802.12 (Y3)
RAM.DI4: U802.9 (Y4)
RAM.DI5: U802.7 (Y5)
RAM.DI6: U802.5 (Y6)
RAM.DI7: U802.3 (Y7)
RAM.DI8: U803.18 (Y0)
RAM.DI9: U803.16 (Y1)
RAM.DI10: U803.14 (Y2)
RAM.DI11: U803.12 (Y3)
RAM.DI12: U803.9 (Y4)
RAM.DI13: U803.7 (Y5)
RAM.DI14: U803.5 (Y6)
RAM.DI15: U803.3 (Y7)
RAM.DI16: U804.18 (Y0)
RAM.DI17: U804.16 (Y1)
RAM.DI18: U804.14 (Y2)
RAM.DI19: U804.12 (Y3)
RAM.DI20: U804.9 (Y4)
RAM.DI21: U804.7 (Y5)
RAM.DI22: U804.5 (Y6)
RAM.DI23: U804.3 (Y7)
RAM.DI24: U805.18 (Y0)
RAM.DI25: U805.16 (Y1)
RAM.DI26: U805.14 (Y2)
RAM.DI27: U805.12 (Y3)
RAM.DI28: U805.9 (Y4)
RAM.DI29: U805.7 (Y5)
RAM.DI30: U805.5 (Y6)
RAM.DI31: U805.3 (Y7)
RAM.DO0: U806.2 (I0)
RAM.DO1: U806.4 (I1)
RAM.DO2: U806.6 (I2)
RAM.DO3: U806.8 (I3)
RAM.DO4: U806.11 (I4)
RAM.DO5: U806.13 (I5)
RAM.DO6: U806.15 (I6)
RAM.DO7: U806.17 (I7)
RAM.DO8: U807.2 (I0)
RAM.DO9: U807.4 (I1)
RAM.DO10: U807.6 (I2)
RAM.DO11: U807.8 (I3)
RAM.DO12: U807.11 (I4)
RAM.DO13: U807.13 (I5)
RAM.DO14: U807.15 (I6)
RAM.DO15: U807.17 (I7)
RAM.DO16: U808.2 (I0)
RAM.DO17: U808.4 (I1)
RAM.DO18: U808.6 (I2)
RAM.DO19: U808.8 (I3)
RAM.DO20: U808.11 (I4)
RAM.DO21: U808.13 (I5)
RAM.DO22: U808.15 (I6)
RAM.DO23: U808.17 (I7)
RAM.DO24: U809.2 (I0)
RAM.DO25: U809.4 (I1)
RAM.DO26: U809.6 (I2)
RAM.DO27: U809.8 (I3)
RAM.DO28: U809.11 (I4)
RAM.DO29: U809.13 (I5)
RAM.DO30: U809.15 (I6)
RAM.DO31: U809.17 (I7)
RAM.IOP_GRANT: U811.1 (D0)
RAM.IOP_GRANT~: U801.1 (OE0), U801.19 (OE1), U810.1 (OE0)
RAM.WEN0: U810.18 (Y0)
RAM.WEN1: U810.16 (Y1)
RAM.WEN2: U810.14 (Y2)
RAM.WEN3: U810.12 (Y3)

Notes on the sheet:
BLUE WIRES on S/N 4995 RAM.IOP_GRANT J4 pin 4 to J3 pin 9 IOP.WR.B0 J4 pin 5 to I5 pin 2 <output> J4 pin 6 to K22 pin 19 Also hand drawn on schematic
