Datamuseum-DK/R1000.HwDoc/Schematics/IOC/pg_08.kicad_sch

## KiCad design Schematics/IOC/pg_08.kicad_sch (2023-01-10)

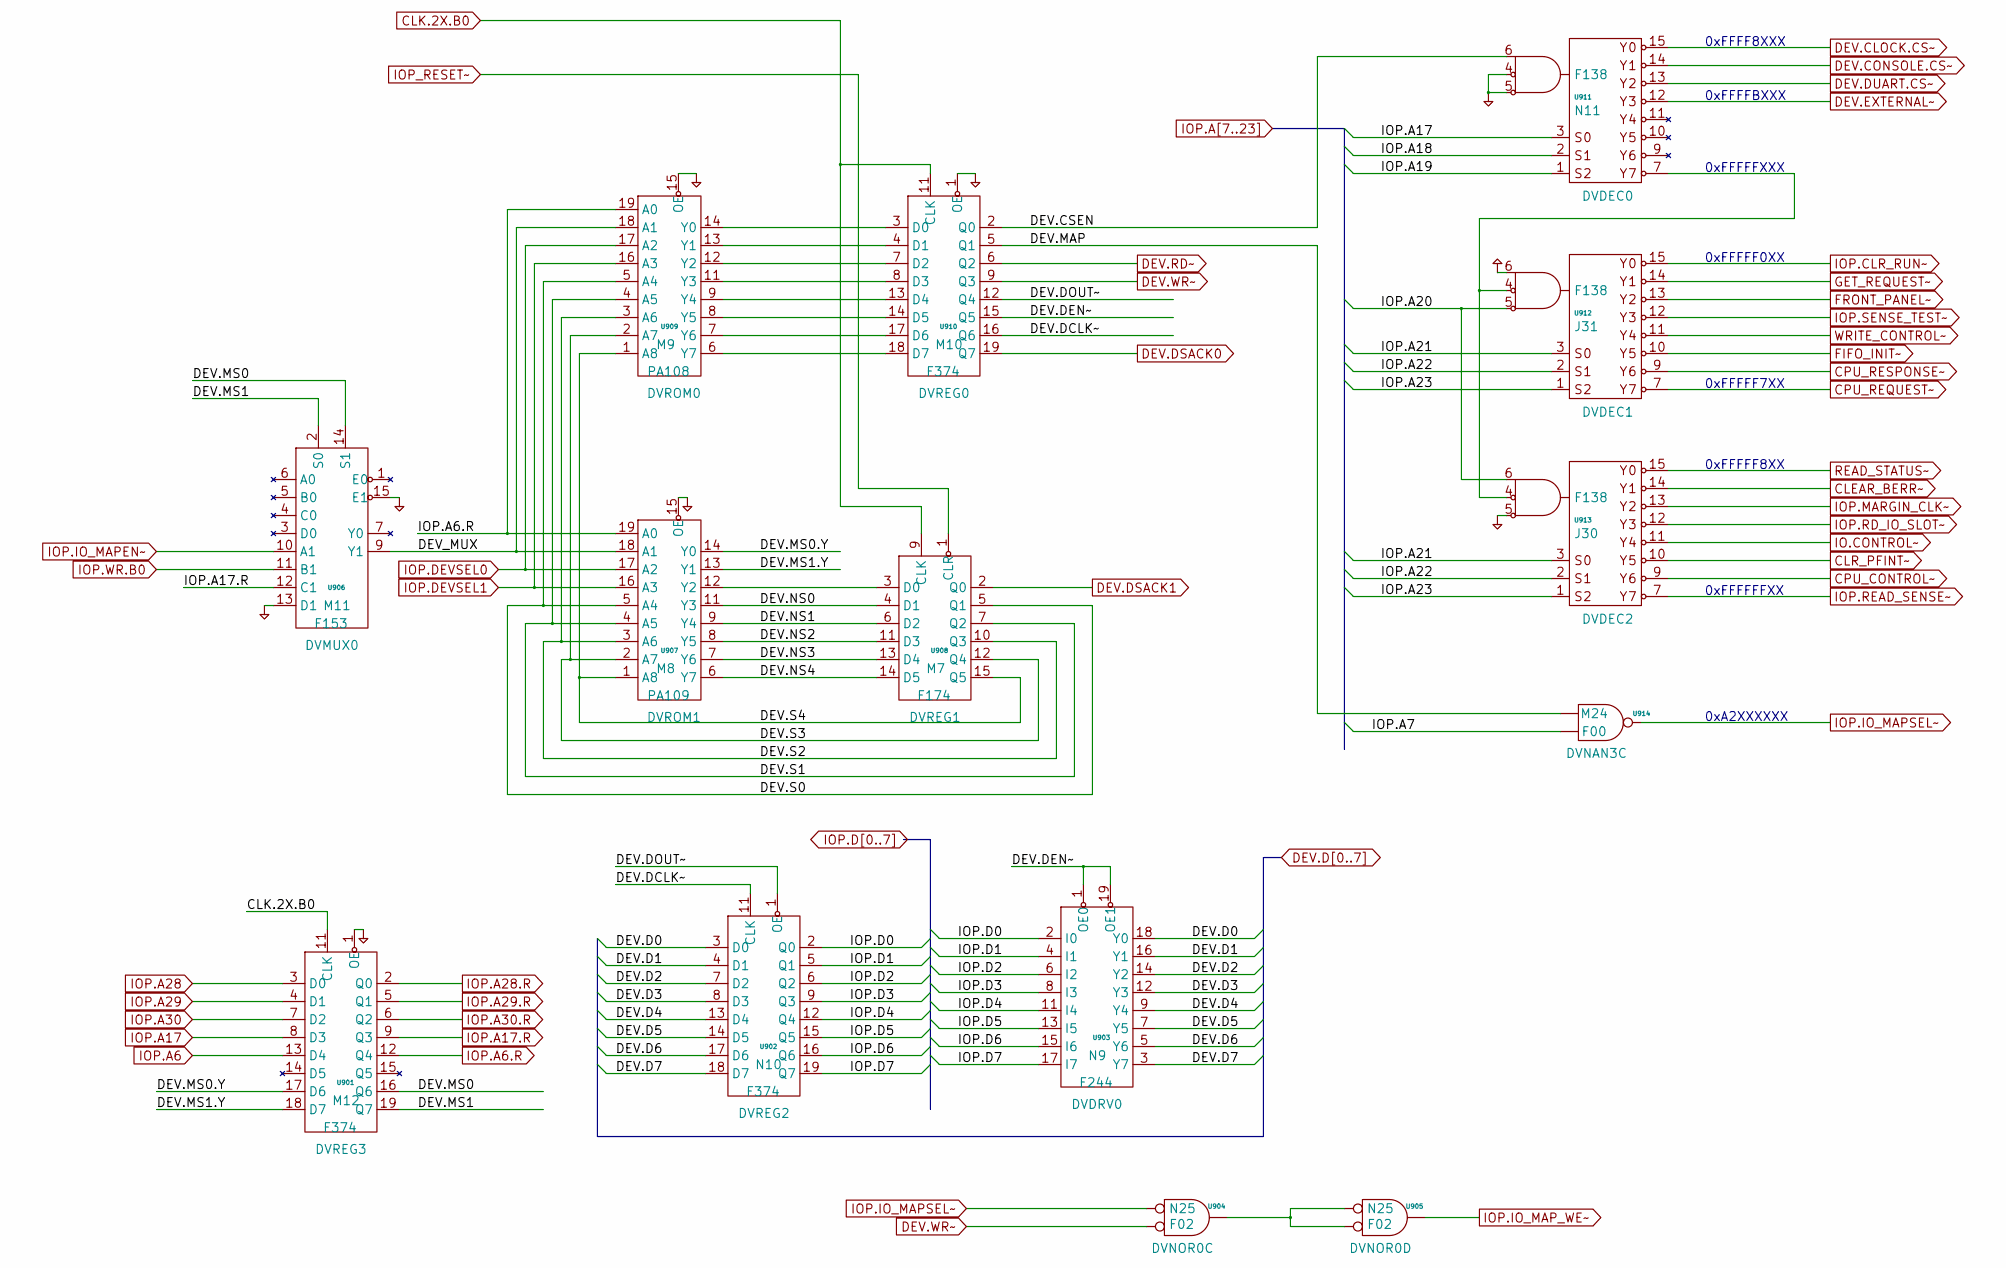
[picture p356: schematic pg_08.kicad_sch]

Parts:
U901, U902, U910: F374
U903: F244
U904, U905: F02
U906: F153
U907: PA109
U908: F174
U909: PA108
U911, U912, U913: F138
U914: F00

Connections:
CLEAR_BERR~: U913.14 (Y1_)
CLK.2X.B0: U901.11 (CLK), U908.9 (CLK), U910.11 (CLK)
CLR_PFINT~: U913.10 (Y5_)
CPU_CONTROL~: U913.9 (Y6_)
CPU_REQUEST~: U912.7 (Y7_)
CPU_RESPONSE~: U912.9 (Y6_)
DEV.CLOCK.CS~: U911.15 (Y0_)
DEV.CONSOLE.CS~: U911.14 (Y1_)
DEV.CSEN: U910.2 (Q0), U911.6 (D0)
DEV.D0: U902.3 (D0), U903.18 (Y0)
DEV.D1: U902.4 (D1), U903.16 (Y1)
DEV.D2: U902.7 (D2), U903.14 (Y2)
DEV.D3: U902.8 (D3), U903.12 (Y3)
DEV.D4: U902.13 (D4), U903.9 (Y4)
DEV.D5: U902.14 (D5), U903.7 (Y5)
DEV.D6: U902.17 (D6), U903.5 (Y6)
DEV.D7: U902.18 (D7), U903.3 (Y7)
DEV.DCLK~: U902.11 (CLK), U910.16 (Q6)
DEV.DEN~: U903.1 (OE0), U903.19 (OE1), U910.15 (Q5)
DEV.DOUT~: U902.1 (OE), U910.12 (Q4)
DEV.DSACK0: U910.19 (Q7)
DEV.DSACK1: U908.2 (Q0)
DEV.DUART.CS~: U911.13 (Y2_)
DEV.EXTERNAL~: U911.12 (Y3_)
DEV.MAP: U910.5 (Q1), U914.1 (D0)
DEV.MS0: U901.16 (Q6), U906.14 (S1)
DEV.MS0.Y: U901.17 (D6), U907.14 (Y0)
DEV.MS1: U901.19 (Q7), U906.2 (S0)
DEV.MS1.Y: U901.18 (D7), U907.13 (Y1)
DEV.NS0: U907.11 (Y3), U908.4 (D1)
DEV.NS1: U907.9 (Y4), U908.6 (D2)
DEV.NS2: U907.8 (Y5), U908.11 (D3)
DEV.NS3: U907.7 (Y6), U908.13 (D4)
DEV.NS4: U907.6 (Y7), U908.14 (D5)
DEV.RD~: U910.6 (Q2)
DEV.S0: U907.5 (A4), U908.5 (Q1), U909.5 (A4)
DEV.S1: U907.4 (A5), U908.7 (Q2), U909.4 (A5)
DEV.S2: U907.3 (A6), U908.10 (Q3), U909.3 (A6)
DEV.S3: U907.2 (A7), U908.12 (Q4), U909.2 (A7)
DEV.S4: U907.1 (A8), U908.15 (Q5), U909.1 (A8)
DEV.WR~: U904.2 (D1), U910.9 (Q3)
DEV_MUX: U906.9 (Y1), U907.18 (A1), U909.18 (A1)
FIFO_INIT~: U912.10 (Y5_)
FRONT_PANEL~: U912.13 (Y2_)
GET_REQUEST~: U912.14 (Y1_)
IO.CONTROL~: U913.11 (Y4_)
IOP.A6: U901.13 (D4)
IOP.A6.R: U901.12 (Q4), U907.19 (A0), U909.19 (A0)
IOP.A7: U914.2 (D1)
IOP.A17: U901.8 (D3), U911.3 (S0)
IOP.A17.R: U901.9 (Q3), U906.12 (C1)
IOP.A18: U911.2 (S1)
IOP.A19: U911.1 (S2)
IOP.A20: U912.5 (D2), U913.6 (D0)
IOP.A21: U912.3 (S0), U913.3 (S0)
IOP.A22: U912.2 (S1), U913.2 (S1)
IOP.A23: U912.1 (S2), U913.1 (S2)
IOP.A28: U901.3 (D0)
IOP.A28.R: U901.2 (Q0)
IOP.A29: U901.4 (D1)
IOP.A29.R: U901.5 (Q1)
IOP.A30: U901.7 (D2)
IOP.A30.R: U901.6 (Q2)
IOP.CLR_RUN~: U912.15 (Y0_)
IOP.D0: U902.2 (Q0), U903.2 (I0)
IOP.D1: U902.5 (Q1), U903.4 (I1)
IOP.D2: U902.6 (Q2), U903.6 (I2)
IOP.D3: U902.9 (Q3), U903.8 (I3)
IOP.D4: U902.12 (Q4), U903.11 (I4)
IOP.D5: U902.15 (Q5), U903.13 (I5)
IOP.D6: U902.16 (Q6), U903.15 (I6)
IOP.D7: U902.19 (Q7), U903.17 (I7)
IOP.DEVSEL0: U907.17 (A2), U909.17 (A2)
IOP.DEVSEL1: U907.16 (A3), U909.16 (A3)
IOP.IO_MAPEN~: U906.10 (A1)
IOP.IO_MAPSEL~: U904.1 (D0), U914.3 (Q)
IOP.IO_MAP_WE~: U905.3 (Q)
IOP.MARGIN_CLK~: U913.13 (Y2_)
IOP.RD_IO_SLOT~: U913.12 (Y3_)
IOP.READ_SENSE~: U913.7 (Y7_)
IOP.SENSE_TEST~: U912.12 (Y3_)
IOP.WR.B0: U906.11 (B1)
IOP_RESET~: U908.1 (CLR)
unnamed: U904.3 (Q), U905.1 (D0), U905.2 (D1)
unnamed: U907.12 (Y2), U908.3 (D0)
unnamed: U909.6 (Y7), U910.18 (D7)
unnamed: U909.7 (Y6), U910.17 (D6)
unnamed: U909.8 (Y5), U910.14 (D5)
unnamed: U909.9 (Y4), U910.13 (D4)
unnamed: U909.11 (Y3), U910.8 (D3)
unnamed: U909.12 (Y2), U910.7 (D2)
unnamed: U909.13 (Y1), U910.4 (D1)
unnamed: U909.14 (Y0), U910.3 (D0)
unnamed: U911.7 (Y7_), U912.4 (D1), U913.4 (D1)
PD: U901.1 (OE), U906.13 (D1), U906.15 (E1), U907.15 (OE), U909.15 (OE), U910.1 (OE), U911.4 (D1), U911.5 (D2), U913.5 (D2)
PU: U912.6 (D0)
READ_STATUS~: U913.15 (Y0_)
WRITE_CONTROL~: U912.11 (Y4_)

Notes on the sheet:
0xA2XXXXXX
0xFFFFFXXX
0xFFFFF7XX
0xFFFFF0XX
0xFFFFF8XX
0xFFFFBXXX
0xFFFF8XXX
0xFFFFFFXX
