Datamuseum-DK/R1000.HwDoc/Schematics/IOC/pg_10.kicad_sch

## KiCad design Schematics/IOC/pg_10.kicad_sch (2023-01-10)

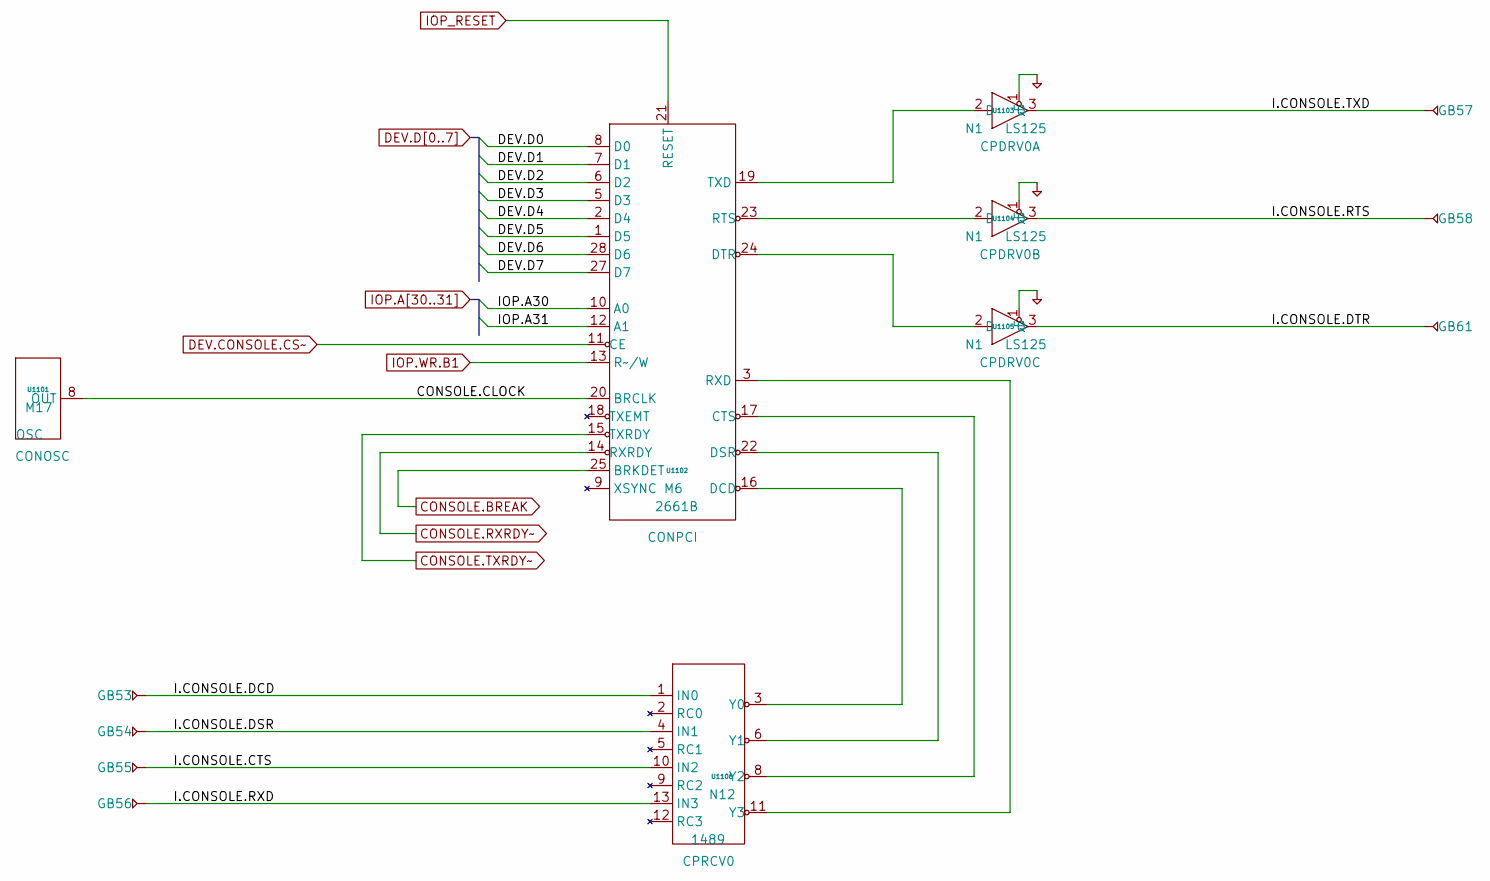
[picture p357: schematic pg_10.kicad_sch]

Parts:
GB53, GB54, GB55, GB56, GB57, GB58, GB61: GB
U1101: OSC
U1102: 2661B
U1103, U1104, U1105: LS125
U1106: 1489

Connections:
CONSOLE.BREAK: U1102.25 (BRKDET)
CONSOLE.CLOCK: U1101.8, U1102.20 (BRCLK)
CONSOLE.RXRDY~: U1102.14 (RXRDY)
CONSOLE.TXRDY~: U1102.15 (TXRDY)
DEV.CONSOLE.CS~: U1102.11 (CE)
DEV.D0: U1102.8 (D0)
DEV.D1: U1102.7 (D1)
DEV.D2: U1102.6 (D2)
DEV.D3: U1102.5 (D3)
DEV.D4: U1102.2 (D4)
DEV.D5: U1102.1 (D5)
DEV.D6: U1102.28 (D6)
DEV.D7: U1102.27 (D7)
I.CONSOLE.CTS: GB55.1, U1106.10 (IN2)
I.CONSOLE.DCD: GB53.1, U1106.1 (IN0)
I.CONSOLE.DSR: GB54.1, U1106.4 (IN1)
I.CONSOLE.DTR: GB61.1, U1105.3 (Q)
I.CONSOLE.RTS: GB58.1, U1104.3 (Q)
I.CONSOLE.RXD: GB56.1, U1106.13 (IN3)
I.CONSOLE.TXD: GB57.1, U1103.3 (Q)
IOP.A30: U1102.10 (A0)
IOP.A31: U1102.12 (A1)
IOP.WR.B1: U1102.13 (R~/W)
IOP_RESET: U1102.21 (RESET)
unnamed: U1102.3 (RXD), U1106.11 (Y3)
unnamed: U1102.16 (DCD), U1106.3 (Y0)
unnamed: U1102.17 (CTS), U1106.8 (Y2)
unnamed: U1102.19 (TXD), U1103.2 (D)
unnamed: U1102.22 (DSR), U1106.6 (Y1)
unnamed: U1102.23 (RTS), U1104.2 (D)
unnamed: U1102.24 (DTR), U1105.2 (D)
PD: U1103.1 (E), U1104.1 (E), U1105.1 (E)
