Datamuseum-DK/R1000.HwDoc/Schematics/IOC/pg_11.kicad_sch

## KiCad design Schematics/IOC/pg_11.kicad_sch (2023-01-10)

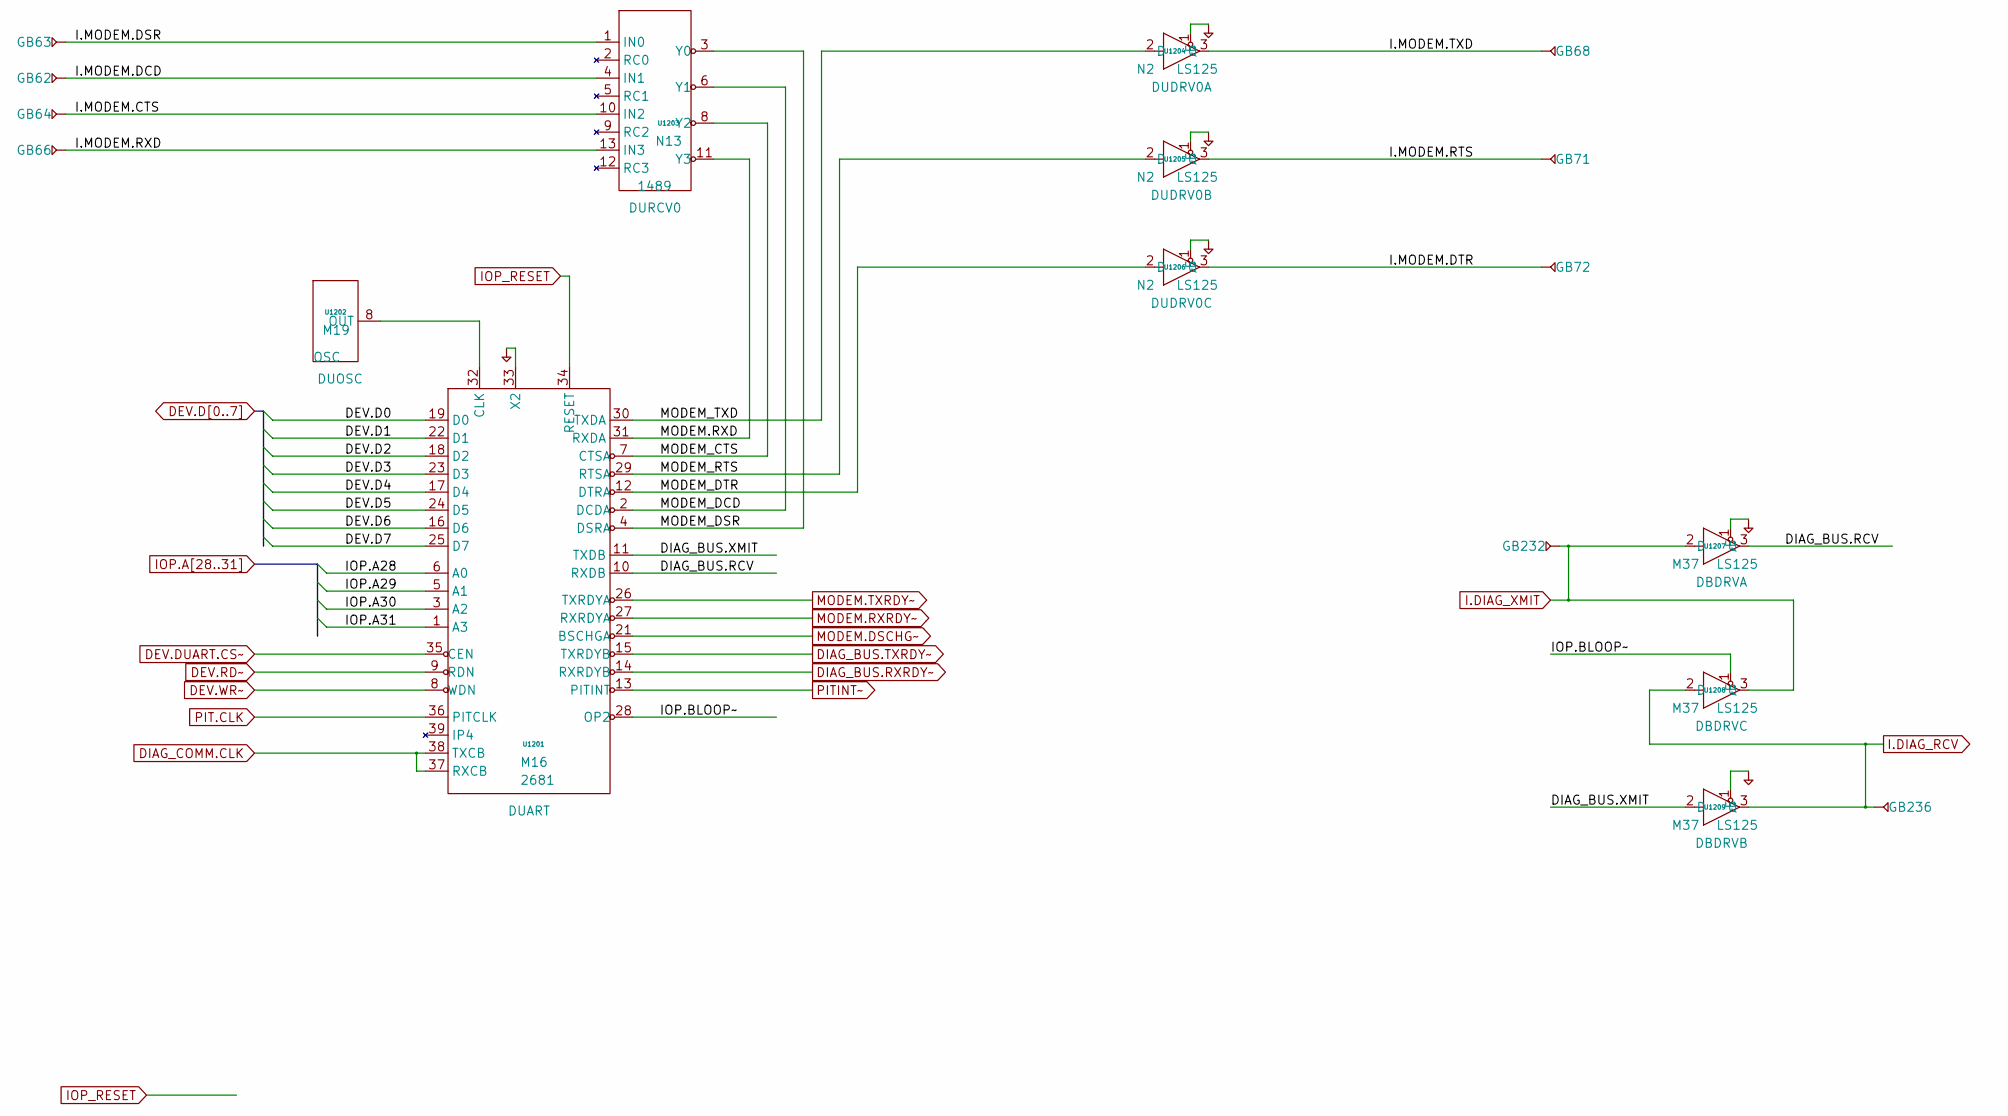
[picture p358: schematic pg_11.kicad_sch]

Parts:
GB62, GB63, GB64, GB66, GB68, GB71, GB72, GB232, GB236: GB
U1201: 2681
U1202: OSC
U1203: 1489
U1204, U1205, U1206, U1207, U1208, U1209: LS125

Connections:
DEV.D0: U1201.19 (D0)
DEV.D1: U1201.22 (D1)
DEV.D2: U1201.18 (D2)
DEV.D3: U1201.23 (D3)
DEV.D4: U1201.17 (D4)
DEV.D5: U1201.24 (D5)
DEV.D6: U1201.16 (D6)
DEV.D7: U1201.25 (D7)
DEV.DUART.CS~: U1201.35 (CEN)
DEV.RD~: U1201.9 (RDN)
DEV.WR~: U1201.8 (WDN)
DIAG_BUS.RCV: U1201.10 (RXDB), U1207.3 (Q)
DIAG_BUS.RXRDY~: U1201.14 (RXRDYB)
DIAG_BUS.TXRDY~: U1201.15 (TXRDYB)
DIAG_BUS.XMIT: U1201.11 (TXDB), U1209.2 (D)
DIAG_COMM.CLK: U1201.37 (RXCB), U1201.38 (TXCB)
I.DIAG_RCV: GB236.1, U1208.2 (D), U1209.3 (Q)
I.DIAG_XMIT: GB232.1, U1207.2 (D), U1208.3 (Q)
I.MODEM.CTS: GB64.1, U1203.10 (IN2)
I.MODEM.DCD: GB62.1, U1203.4 (IN1)
I.MODEM.DSR: GB63.1, U1203.1 (IN0)
I.MODEM.DTR: GB72.1, U1206.3 (Q)
I.MODEM.RTS: GB71.1, U1205.3 (Q)
I.MODEM.RXD: GB66.1, U1203.13 (IN3)
I.MODEM.TXD: GB68.1, U1204.3 (Q)
IOP.A28: U1201.6 (A0)
IOP.A29: U1201.5 (A1)
IOP.A30: U1201.3 (A2)
IOP.A31: U1201.1 (A3)
IOP.BLOOP~: U1201.28 (OP2), U1208.1 (E)
IOP_RESET: U1201.34 (RESET)
MODEM.DSCHG~: U1201.21 (BSCHGA)
MODEM.RXD: U1201.31 (RXDA), U1203.11 (Y3)
MODEM.RXRDY~: U1201.27 (RXRDYA)
MODEM.TXRDY~: U1201.26 (TXRDYA)
MODEM_CTS: U1201.7 (CTSA), U1203.8 (Y2)
MODEM_DCD: U1201.2 (DCDA), U1203.6 (Y1)
MODEM_DSR: U1201.4 (DSRA), U1203.3 (Y0)
MODEM_DTR: U1201.12 (DTRA), U1206.2 (D)
MODEM_RTS: U1201.29 (RTSA), U1205.2 (D)
MODEM_TXD: U1201.30 (TXDA), U1204.2 (D)
unnamed: U1201.32 (CLK), U1202.8
PD: U1201.33 (X2), U1204.1 (E), U1205.1 (E), U1206.1 (E), U1207.1 (E), U1209.1 (E)
PIT.CLK: U1201.36 (PITCLK)
PITINT~: U1201.13 (PITINT)
