Datamuseum-DK/R1000.HwDoc/Schematics/IOC/pg_12.kicad_sch

## KiCad design Schematics/IOC/pg_12.kicad_sch (2023-01-10)

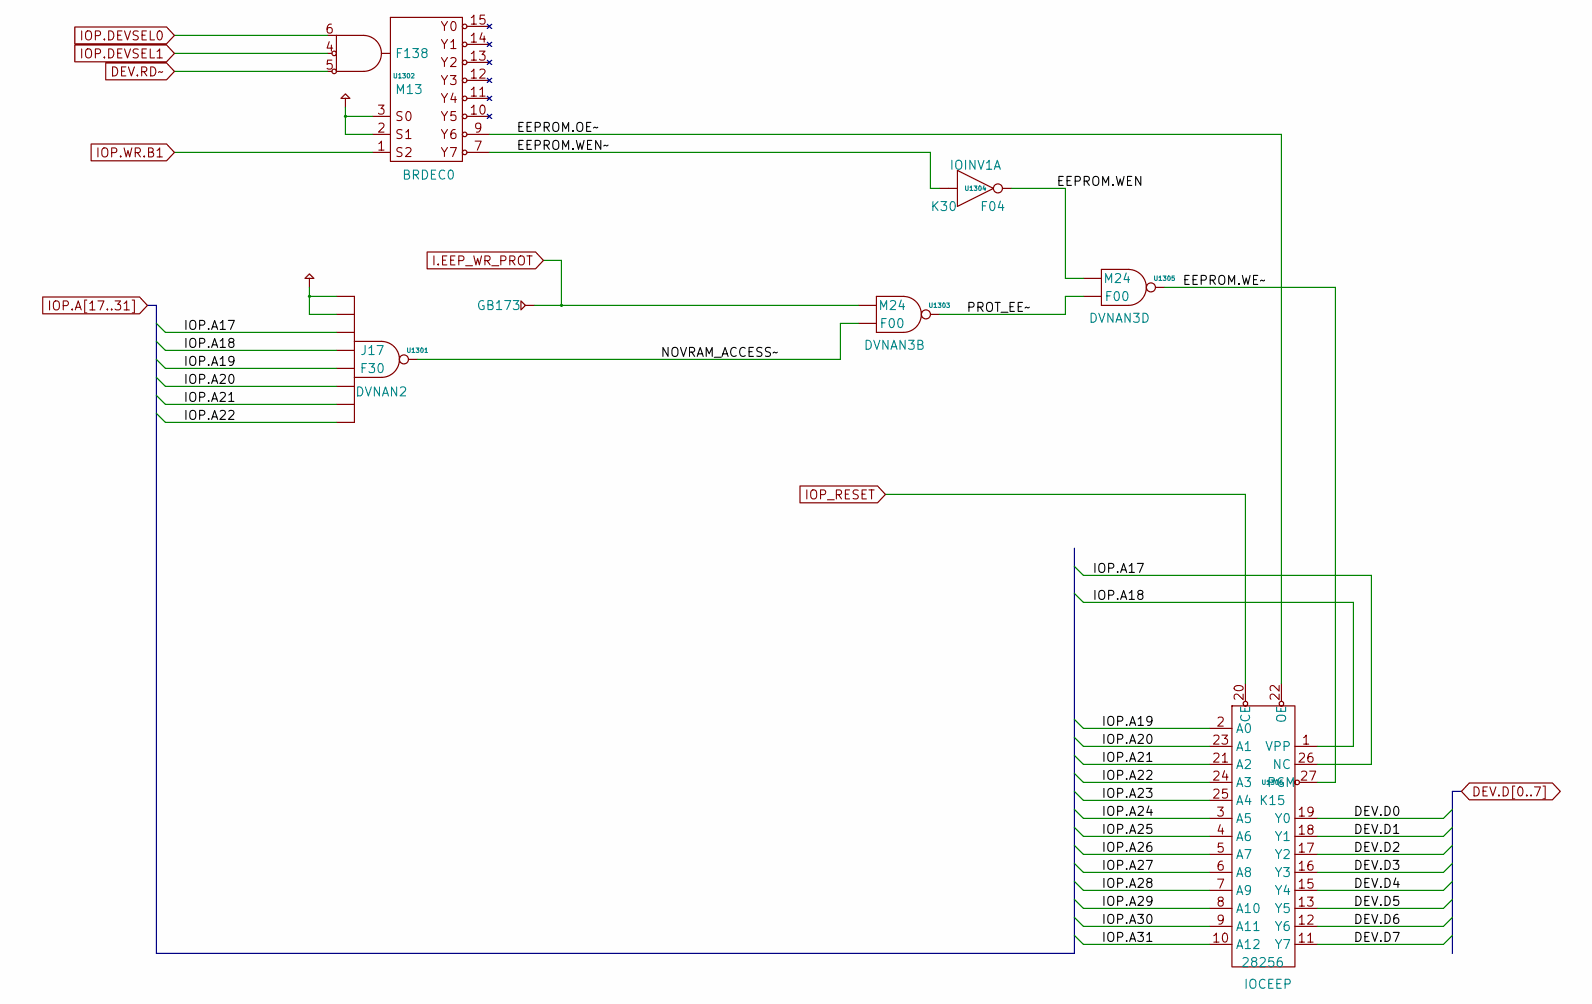
[picture p359: schematic pg_12.kicad_sch]

Parts:
GB173: GB
U1301: F30
U1302: F138
U1303, U1305: F00
U1304: F04
U1306: 28256

Connections:
DEV.D0: U1306.19 (Y0)
DEV.D1: U1306.18 (Y1)
DEV.D2: U1306.17 (Y2)
DEV.D3: U1306.16 (Y3)
DEV.D4: U1306.15 (Y4)
DEV.D5: U1306.13 (Y5)
DEV.D6: U1306.12 (Y6)
DEV.D7: U1306.11 (Y7)
DEV.RD~: U1302.5 (D2)
EEPROM.OE~: U1302.9 (Y6_), U1306.22 (OE)
EEPROM.WEN: U1304.2 (Q), U1305.1 (D0)
EEPROM.WEN~: U1302.7 (Y7_), U1304.1 (D0)
EEPROM.WE~: U1305.3 (Q), U1306.27 (PGM)
I.EEP_WR_PROT: GB173.1, U1303.1 (D0)
IOP.A17: U1301.1 (D2), U1306.26 (NC)
IOP.A18: U1301.2 (D3), U1306.1 (VPP)
IOP.A19: U1301.3 (D4), U1306.2 (A0)
IOP.A20: U1301.4 (D5), U1306.23 (A1)
IOP.A21: U1301.5 (D6), U1306.21 (A2)
IOP.A22: U1301.6 (D7), U1306.24 (A3)
IOP.A23: U1306.25 (A4)
IOP.A24: U1306.3 (A5)
IOP.A25: U1306.4 (A6)
IOP.A26: U1306.5 (A7)
IOP.A27: U1306.6 (A8)
IOP.A28: U1306.7 (A9)
IOP.A29: U1306.8 (A10)
IOP.A30: U1306.9 (A11)
IOP.A31: U1306.10 (A12)
IOP.DEVSEL0: U1302.6 (D0)
IOP.DEVSEL1: U1302.4 (D1)
IOP.WR.B1: U1302.1 (S2)
IOP_RESET: U1306.20 (CE)
NOVRAM_ACCESS~: U1301.8 (Q), U1303.2 (D1)
PROT_EE~: U1303.3 (Q), U1305.2 (D1)
PU: U1301.11 (D0), U1301.12 (D1), U1302.2 (S1), U1302.3 (S0)
