Datamuseum-DK/R1000.HwDoc/Schematics/IOC/pg_13.kicad_sch

## KiCad design Schematics/IOC/pg_13.kicad_sch (2023-01-10)

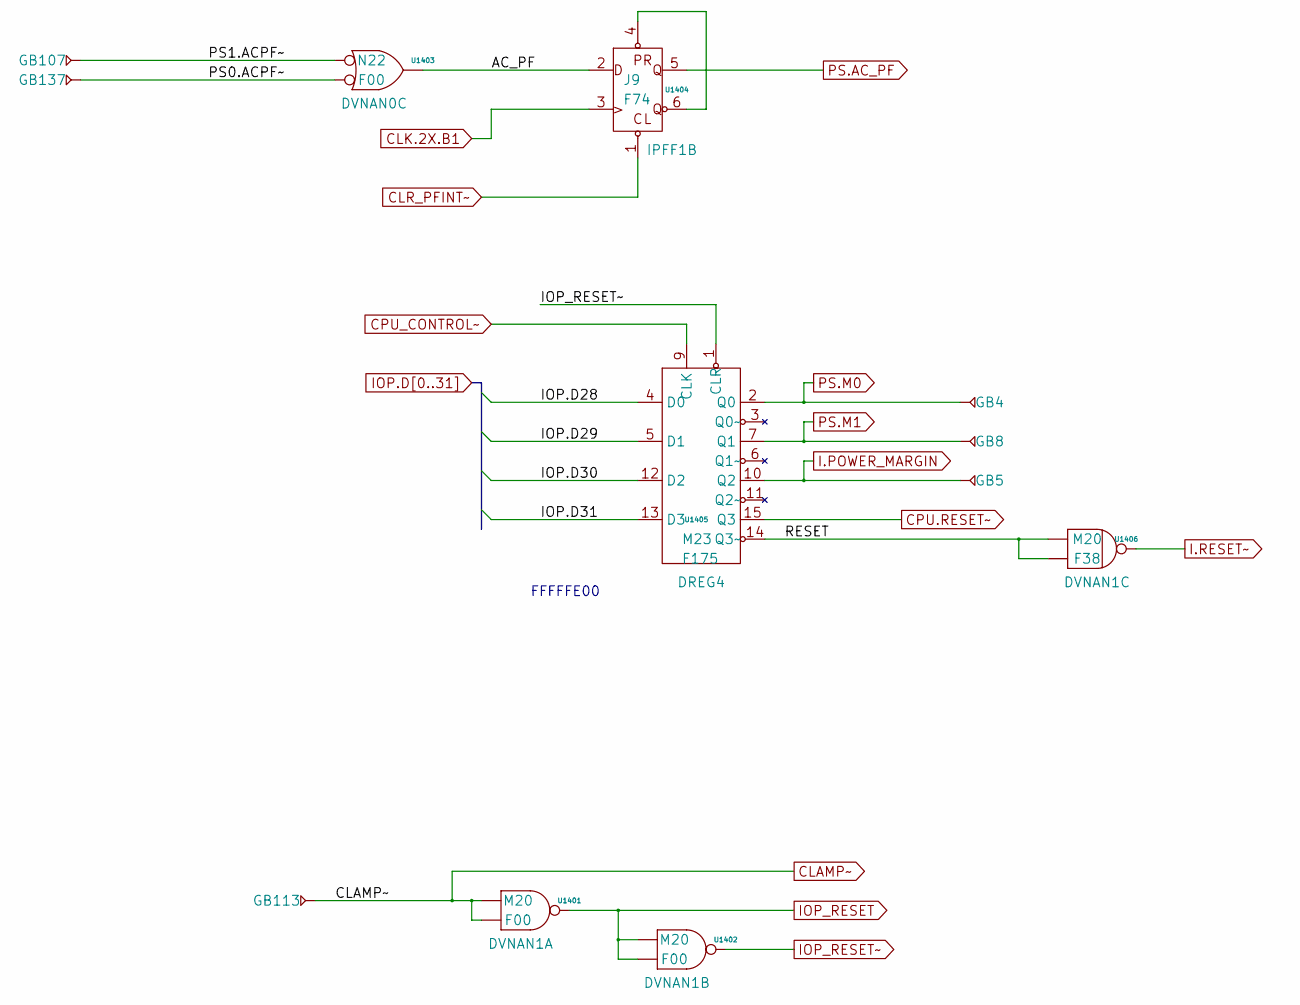
[picture p360: schematic pg_13.kicad_sch]

Parts:
GB4, GB5, GB8, GB107, GB113, GB137: GB
U1401, U1402, U1403: F00
U1404: F74
U1405: F175
U1406: F38

Connections:
AC_PF: U1403.3 (Q), U1404.2 (D)
CLAMP~: GB113.1, U1401.1 (D0), U1401.2 (D1)
CLK.2X.B1: U1404.3 (CLK)
CLR_PFINT~: U1404.1 (CL_)
CPU.RESET~: U1405.15 (Q3)
CPU_CONTROL~: U1405.9 (CLK)
I.POWER_MARGIN: GB5.1, U1405.10 (Q2)
I.RESET~: U1406.3 (Q)
IOP.D28: U1405.4 (D0)
IOP.D29: U1405.5 (D1)
IOP.D30: U1405.12 (D2)
IOP.D31: U1405.13 (D3)
IOP_RESET: U1401.3 (Q), U1402.1 (D0), U1402.2 (D1)
IOP_RESET~: U1402.3 (Q), U1405.1 (CLR)
unnamed: U1404.4 (PR_), U1404.6 (Q_)
PS0.ACPF~: GB137.1, U1403.2 (D1)
PS1.ACPF~: GB107.1, U1403.1 (D0)
PS.AC_PF: U1404.5 (Q)
PS.M0: GB4.1, U1405.2 (Q0)
PS.M1: GB8.1, U1405.7 (Q1)
RESET: U1405.14 (Q3~), U1406.1 (D0), U1406.2 (D1)

Notes on the sheet:
FFFFFE00
