Datamuseum-DK/R1000.HwDoc/Schematics/IOC/pg_14.kicad_sch

## KiCad design Schematics/IOC/pg_14.kicad_sch (2023-01-10)

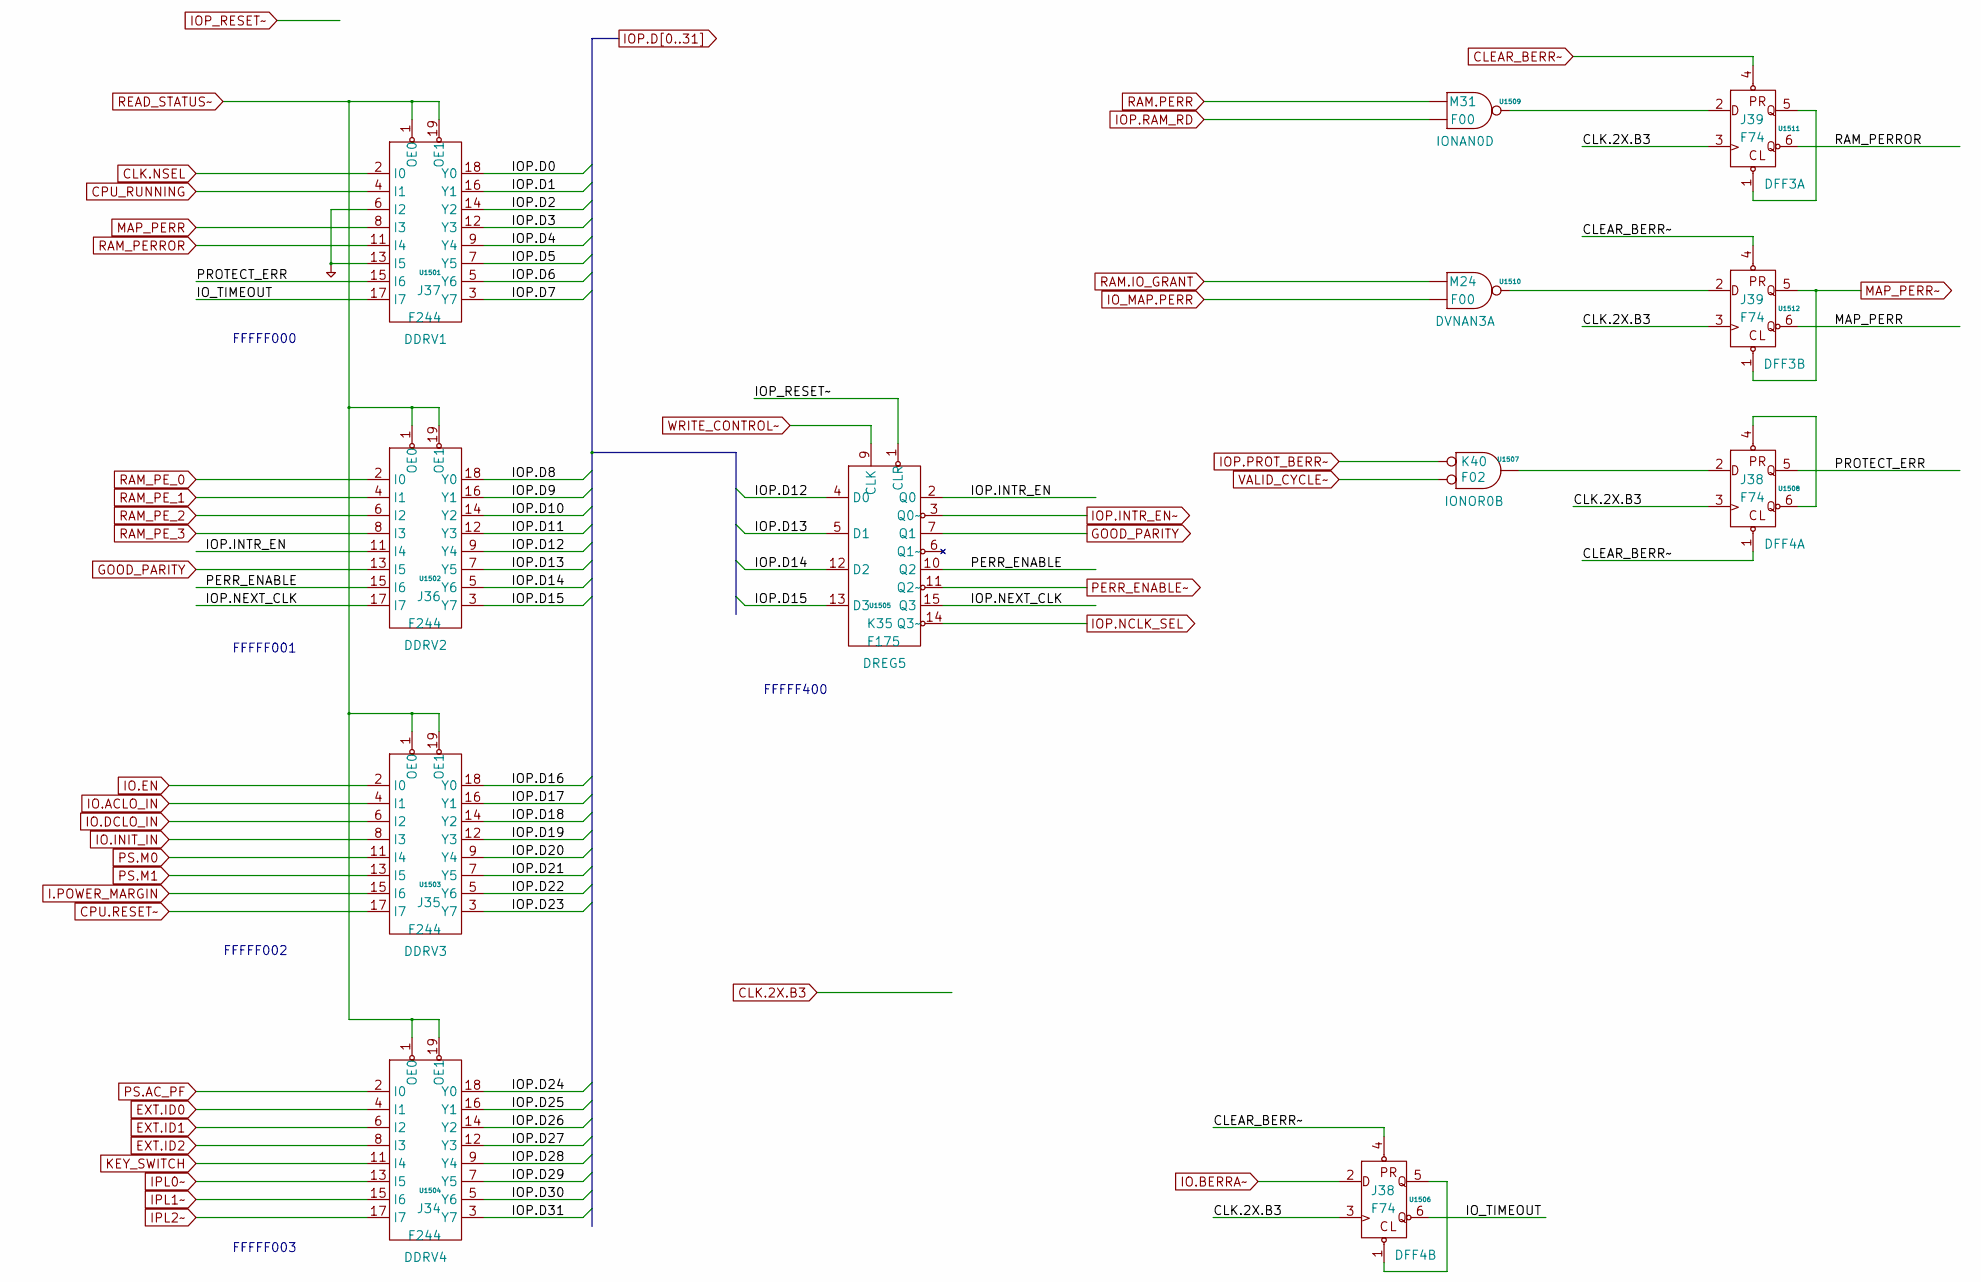
[picture p361: schematic pg_14.kicad_sch]

Parts:
U1501, U1502, U1503, U1504: F244
U1505: F175
U1506, U1508, U1511, U1512: F74
U1507: F02
U1509, U1510: F00

Connections:
CLEAR_BERR~: U1506.4 (PR_), U1508.1 (CL_), U1511.4 (PR_), U1512.4 (PR_)
CLK.2X.B3: U1506.3 (CLK), U1508.3 (CLK), U1511.3 (CLK), U1512.3 (CLK)
CLK.NSEL: U1501.2 (I0)
CPU.RESET~: U1503.17 (I7)
CPU_RUNNING: U1501.4 (I1)
EXT.ID0: U1504.4 (I1)
EXT.ID1: U1504.6 (I2)
EXT.ID2: U1504.8 (I3)
GOOD_PARITY: U1502.13 (I5), U1505.7 (Q1)
I.POWER_MARGIN: U1503.15 (I6)
IO.ACLO_IN: U1503.4 (I1)
IO.BERRA~: U1506.2 (D)
IO.DCLO_IN: U1503.6 (I2)
IO.EN: U1503.2 (I0)
IO.INIT_IN: U1503.8 (I3)
IOP.D0: U1501.18 (Y0)
IOP.D1: U1501.16 (Y1)
IOP.D2: U1501.14 (Y2)
IOP.D3: U1501.12 (Y3)
IOP.D4: U1501.9 (Y4)
IOP.D5: U1501.7 (Y5)
IOP.D6: U1501.5 (Y6)
IOP.D7: U1501.3 (Y7)
IOP.D8: U1502.18 (Y0)
IOP.D9: U1502.16 (Y1)
IOP.D10: U1502.14 (Y2)
IOP.D11: U1502.12 (Y3)
IOP.D12: U1502.9 (Y4), U1505.4 (D0)
IOP.D13: U1502.7 (Y5), U1505.5 (D1)
IOP.D14: U1502.5 (Y6), U1505.12 (D2)
IOP.D15: U1502.3 (Y7), U1505.13 (D3)
IOP.D16: U1503.18 (Y0)
IOP.D17: U1503.16 (Y1)
IOP.D18: U1503.14 (Y2)
IOP.D19: U1503.12 (Y3)
IOP.D20: U1503.9 (Y4)
IOP.D21: U1503.7 (Y5)
IOP.D22: U1503.5 (Y6)
IOP.D23: U1503.3 (Y7)
IOP.D24: U1504.18 (Y0)
IOP.D25: U1504.16 (Y1)
IOP.D26: U1504.14 (Y2)
IOP.D27: U1504.12 (Y3)
IOP.D28: U1504.9 (Y4)
IOP.D29: U1504.7 (Y5)
IOP.D30: U1504.5 (Y6)
IOP.D31: U1504.3 (Y7)
IOP.INTR_EN: U1502.11 (I4), U1505.2 (Q0)
IOP.INTR_EN~: U1505.3 (Q0~)
IOP.NCLK_SEL: U1505.14 (Q3~)
IOP.NEXT_CLK: U1502.17 (I7), U1505.15 (Q3)
IOP.PROT_BERR~: U1507.1 (D0)
IOP.RAM_RD: U1509.2 (D1)
IOP_RESET~: U1505.1 (CLR)
IO_MAP.PERR: U1510.2 (D1)
IO_TIMEOUT: U1501.17 (I7), U1506.6 (Q_)
IPL0~: U1504.13 (I5)
IPL1~: U1504.15 (I6)
IPL2~: U1504.17 (I7)
KEY_SWITCH: U1504.11 (I4)
MAP_PERR: U1501.8 (I3), U1512.6 (Q_)
MAP_PERR~: U1512.1 (CL_), U1512.5 (Q)
unnamed: U1506.1 (CL_), U1506.5 (Q)
unnamed: U1507.3 (Q), U1508.2 (D)
unnamed: U1508.4 (PR_), U1508.6 (Q_)
unnamed: U1509.3 (Q), U1511.2 (D)
unnamed: U1510.3 (Q), U1512.2 (D)
unnamed: U1511.1 (CL_), U1511.5 (Q)
PD: U1501.6 (I2), U1501.13 (I5)
PERR_ENABLE: U1502.15 (I6), U1505.10 (Q2)
PERR_ENABLE~: U1505.11 (Q2~)
PROTECT_ERR: U1501.15 (I6), U1508.5 (Q)
PS.AC_PF: U1504.2 (I0)
PS.M0: U1503.11 (I4)
PS.M1: U1503.13 (I5)
RAM.IO_GRANT: U1510.1 (D0)
RAM.PERR: U1509.1 (D0)
RAM_PERROR: U1501.11 (I4), U1511.6 (Q_)
RAM_PE_0: U1502.2 (I0)
RAM_PE_1: U1502.4 (I1)
RAM_PE_2: U1502.6 (I2)
RAM_PE_3: U1502.8 (I3)
READ_STATUS~: U1501.1 (OE0), U1501.19 (OE1), U1502.1 (OE0), U1502.19 (OE1), U1503.1 (OE0), U1503.19 (OE1), U1504.1 (OE0), U1504.19 (OE1)
VALID_CYCLE~: U1507.2 (D1)
WRITE_CONTROL~: U1505.9 (CLK)

Notes on the sheet:
FFFFF003
FFFFF000
FFFFF001
FFFFF400
FFFFF002
