Datamuseum-DK/R1000.HwDoc/Schematics/IOC/pg_15.kicad_sch

## KiCad design Schematics/IOC/pg_15.kicad_sch (2023-01-10)

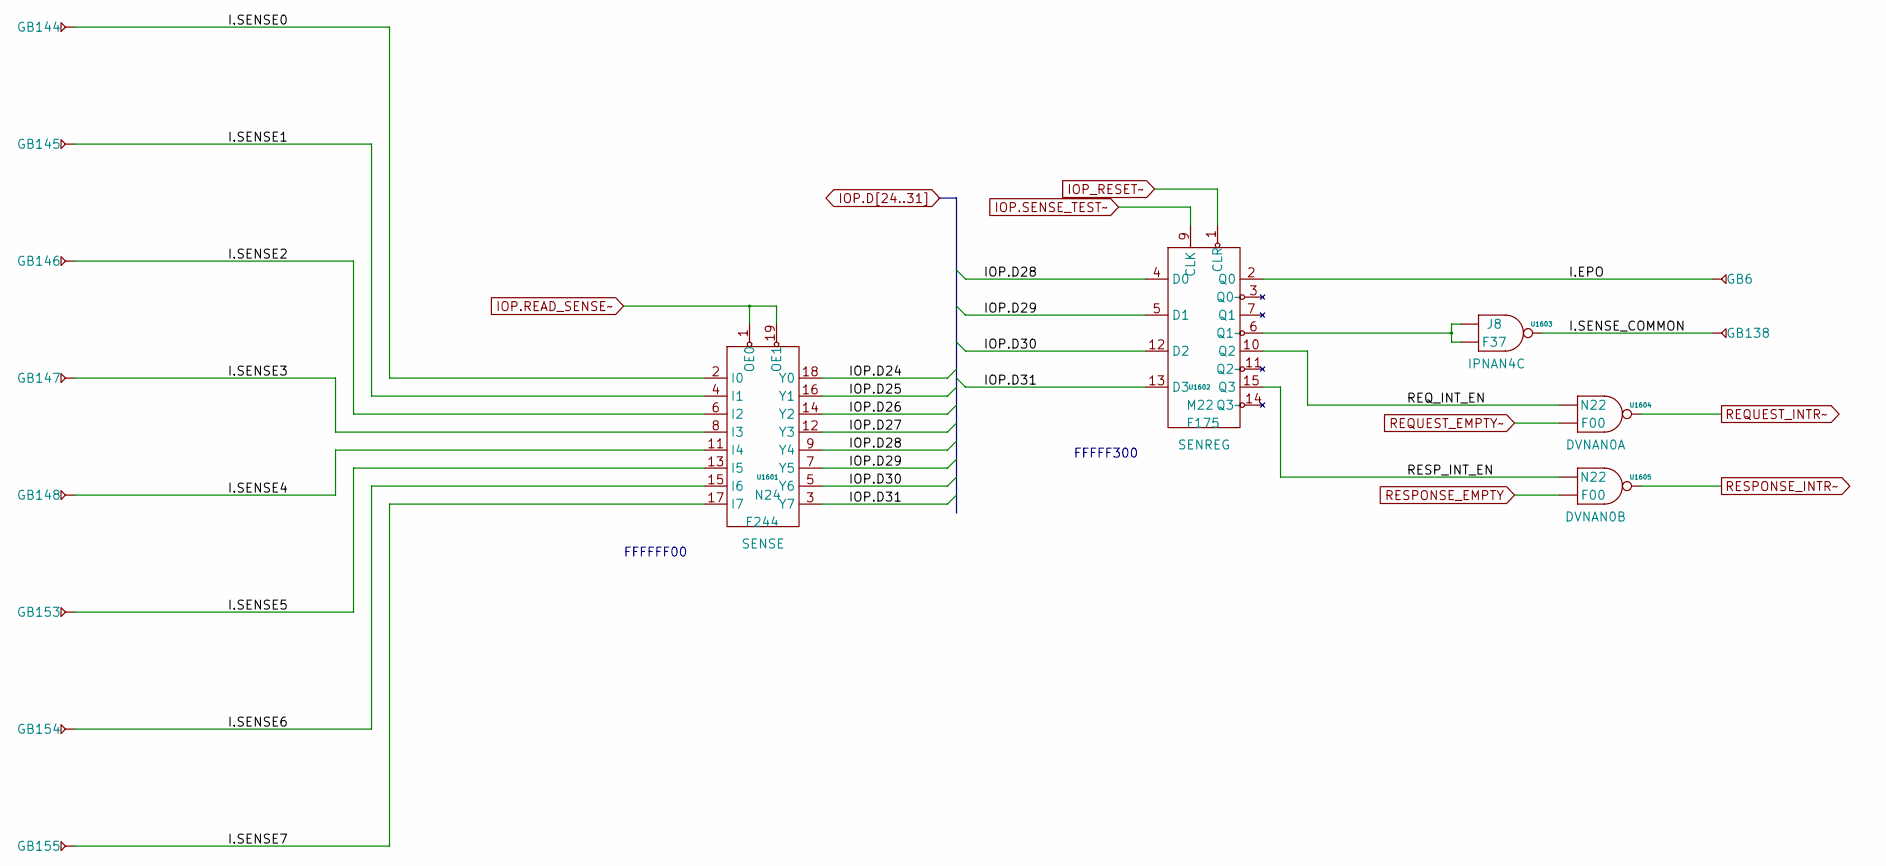
[picture p362: schematic pg_15.kicad_sch]

Parts:
GB6, GB138, GB144, GB145, GB146, GB147, GB148, GB153, GB154, GB155: GB
U1601: F244
U1602: F175
U1603: F37
U1604, U1605: F00

Connections:
I.EPO: GB6.1, U1602.2 (Q0)
I.SENSE0: GB144.1, U1601.2 (I0)
I.SENSE1: GB145.1, U1601.4 (I1)
I.SENSE2: GB146.1, U1601.6 (I2)
I.SENSE3: GB147.1, U1601.8 (I3)
I.SENSE4: GB148.1, U1601.11 (I4)
I.SENSE5: GB153.1, U1601.13 (I5)
I.SENSE6: GB154.1, U1601.15 (I6)
I.SENSE7: GB155.1, U1601.17 (I7)
I.SENSE_COMMON: GB138.1, U1603.3 (Q)
IOP.D24: U1601.18 (Y0)
IOP.D25: U1601.16 (Y1)
IOP.D26: U1601.14 (Y2)
IOP.D27: U1601.12 (Y3)
IOP.D28: U1601.9 (Y4), U1602.4 (D0)
IOP.D29: U1601.7 (Y5), U1602.5 (D1)
IOP.D30: U1601.5 (Y6), U1602.12 (D2)
IOP.D31: U1601.3 (Y7), U1602.13 (D3)
IOP.READ_SENSE~: U1601.1 (OE0), U1601.19 (OE1)
IOP.SENSE_TEST~: U1602.9 (CLK)
IOP_RESET~: U1602.1 (CLR)
unnamed: U1602.6 (Q1~), U1603.1 (D0), U1603.2 (D1)
REQUEST_EMPTY~: U1604.2 (D1)
REQUEST_INTR~: U1604.3 (Q)
REQ_INT_EN: U1602.10 (Q2), U1604.1 (D0)
RESPONSE_EMPTY: U1605.2 (D1)
RESPONSE_INTR~: U1605.3 (Q)
RESP_INT_EN: U1602.15 (Q3), U1605.1 (D0)

Notes on the sheet:
FFFFFF00
FFFFF300
