Datamuseum-DK/R1000.HwDoc/Schematics/IOC/pg_16.kicad_sch

## KiCad design Schematics/IOC/pg_16.kicad_sch (2023-01-10)

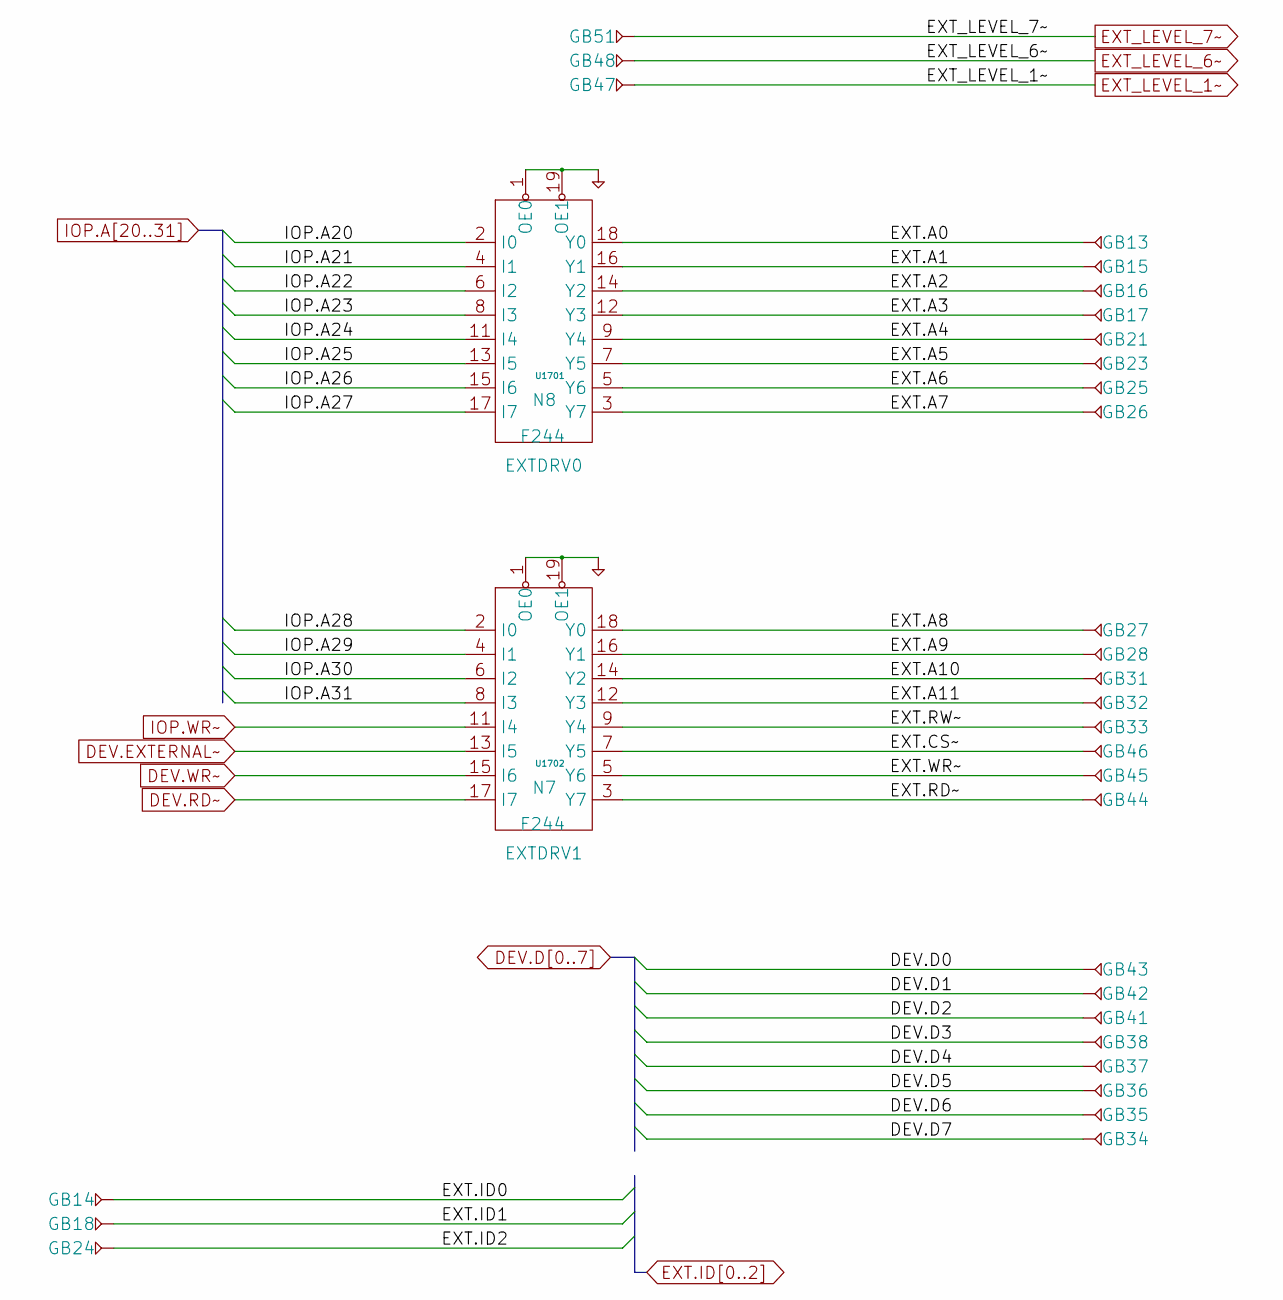
[picture p363: schematic pg_16.kicad_sch]

Parts:
GB13, GB14, GB15, GB16, GB17, GB18, GB21, GB23, GB24, GB25, GB26, GB27, GB28, GB31, GB32, GB33, GB34, GB35, GB36, GB37, GB38, GB41, GB42, GB43, GB44, GB45, GB46, GB47, GB48, GB51: GB
U1701, U1702: F244

Connections:
DEV.D0: GB43.1
DEV.D1: GB42.1
DEV.D2: GB41.1
DEV.D3: GB38.1
DEV.D4: GB37.1
DEV.D5: GB36.1
DEV.D6: GB35.1
DEV.D7: GB34.1
DEV.EXTERNAL~: U1702.13 (I5)
DEV.RD~: U1702.17 (I7)
DEV.WR~: U1702.15 (I6)
EXT.A0: GB13.1, U1701.18 (Y0)
EXT.A1: GB15.1, U1701.16 (Y1)
EXT.A2: GB16.1, U1701.14 (Y2)
EXT.A3: GB17.1, U1701.12 (Y3)
EXT.A4: GB21.1, U1701.9 (Y4)
EXT.A5: GB23.1, U1701.7 (Y5)
EXT.A6: GB25.1, U1701.5 (Y6)
EXT.A7: GB26.1, U1701.3 (Y7)
EXT.A8: GB27.1, U1702.18 (Y0)
EXT.A9: GB28.1, U1702.16 (Y1)
EXT.A10: GB31.1, U1702.14 (Y2)
EXT.A11: GB32.1, U1702.12 (Y3)
EXT.CS~: GB46.1, U1702.7 (Y5)
EXT.ID0: GB14.1
EXT.ID1: GB18.1
EXT.ID2: GB24.1
EXT.RD~: GB44.1, U1702.3 (Y7)
EXT.RW~: GB33.1, U1702.9 (Y4)
EXT.WR~: GB45.1, U1702.5 (Y6)
EXT_LEVEL_1~: GB47.1
EXT_LEVEL_6~: GB48.1
EXT_LEVEL_7~: GB51.1
IOP.A20: U1701.2 (I0)
IOP.A21: U1701.4 (I1)
IOP.A22: U1701.6 (I2)
IOP.A23: U1701.8 (I3)
IOP.A24: U1701.11 (I4)
IOP.A25: U1701.13 (I5)
IOP.A26: U1701.15 (I6)
IOP.A27: U1701.17 (I7)
IOP.A28: U1702.2 (I0)
IOP.A29: U1702.4 (I1)
IOP.A30: U1702.6 (I2)
IOP.A31: U1702.8 (I3)
IOP.WR~: U1702.11 (I4)
PD: U1701.1 (OE0), U1701.19 (OE1), U1702.1 (OE0), U1702.19 (OE1)
