Datamuseum-DK/R1000.HwDoc/Schematics/IOC/pg_17.kicad_sch

## KiCad design Schematics/IOC/pg_17.kicad_sch (2023-01-10)

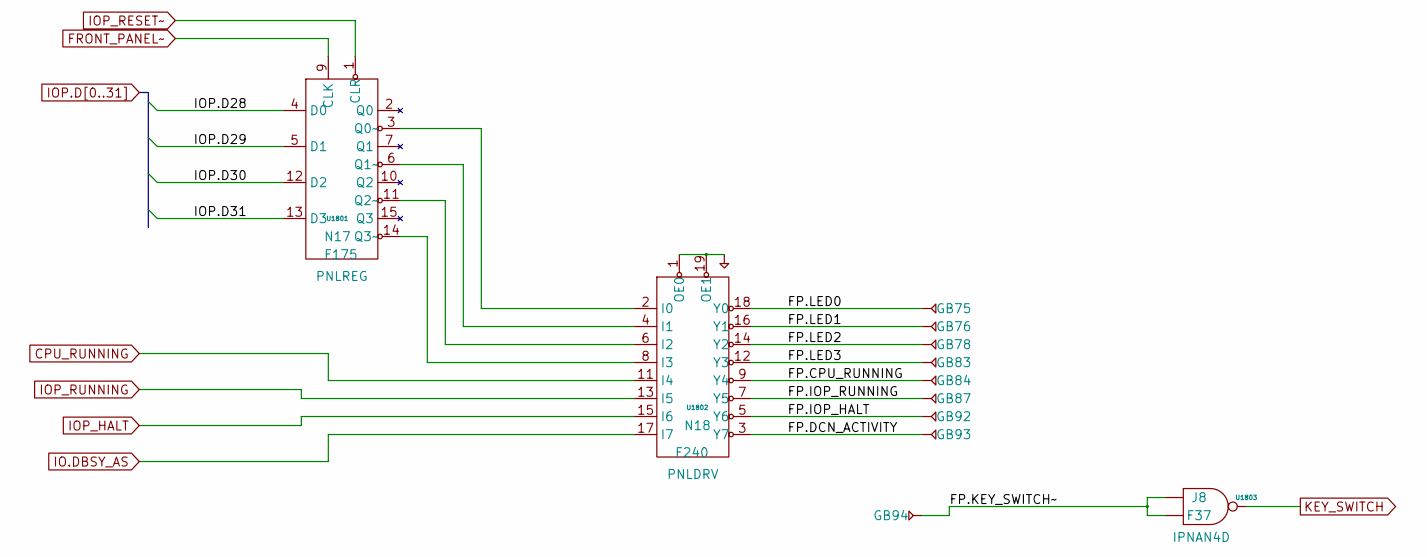
[picture p364: schematic pg_17.kicad_sch]

Parts:
GB75, GB76, GB78, GB83, GB84, GB87, GB92, GB93, GB94: GB
U1801: F175
U1802: F240
U1803: F37

Connections:
CPU_RUNNING: U1802.11 (I4)
FP.CPU_RUNNING: GB84.1, U1802.9 (Y4)
FP.DCN_ACTIVITY: GB93.1, U1802.3 (Y7)
FP.IOP_HALT: GB92.1, U1802.5 (Y6)
FP.IOP_RUNNING: GB87.1, U1802.7 (Y5)
FP.KEY_SWITCH~: GB94.1, U1803.1 (D0), U1803.2 (D1)
FP.LED0: GB75.1, U1802.18 (Y0)
FP.LED1: GB76.1, U1802.16 (Y1)
FP.LED2: GB78.1, U1802.14 (Y2)
FP.LED3: GB83.1, U1802.12 (Y3)
FRONT_PANEL~: U1801.9 (CLK)
IO.DBSY_AS: U1802.17 (I7)
IOP.D28: U1801.4 (D0)
IOP.D29: U1801.5 (D1)
IOP.D30: U1801.12 (D2)
IOP.D31: U1801.13 (D3)
IOP_HALT: U1802.15 (I6)
IOP_RESET~: U1801.1 (CLR)
IOP_RUNNING: U1802.13 (I5)
KEY_SWITCH: U1803.3 (Q)
unnamed: U1801.3 (Q0~), U1802.2 (I0)
unnamed: U1801.6 (Q1~), U1802.4 (I1)
unnamed: U1801.11 (Q2~), U1802.6 (I2)
unnamed: U1801.14 (Q3~), U1802.8 (I3)
PD: U1802.1 (OE0), U1802.19 (OE1)
