Datamuseum-DK/R1000.HwDoc/Schematics/IOC/pg_18.kicad_sch

## KiCad design Schematics/IOC/pg_18.kicad_sch (2023-01-10)

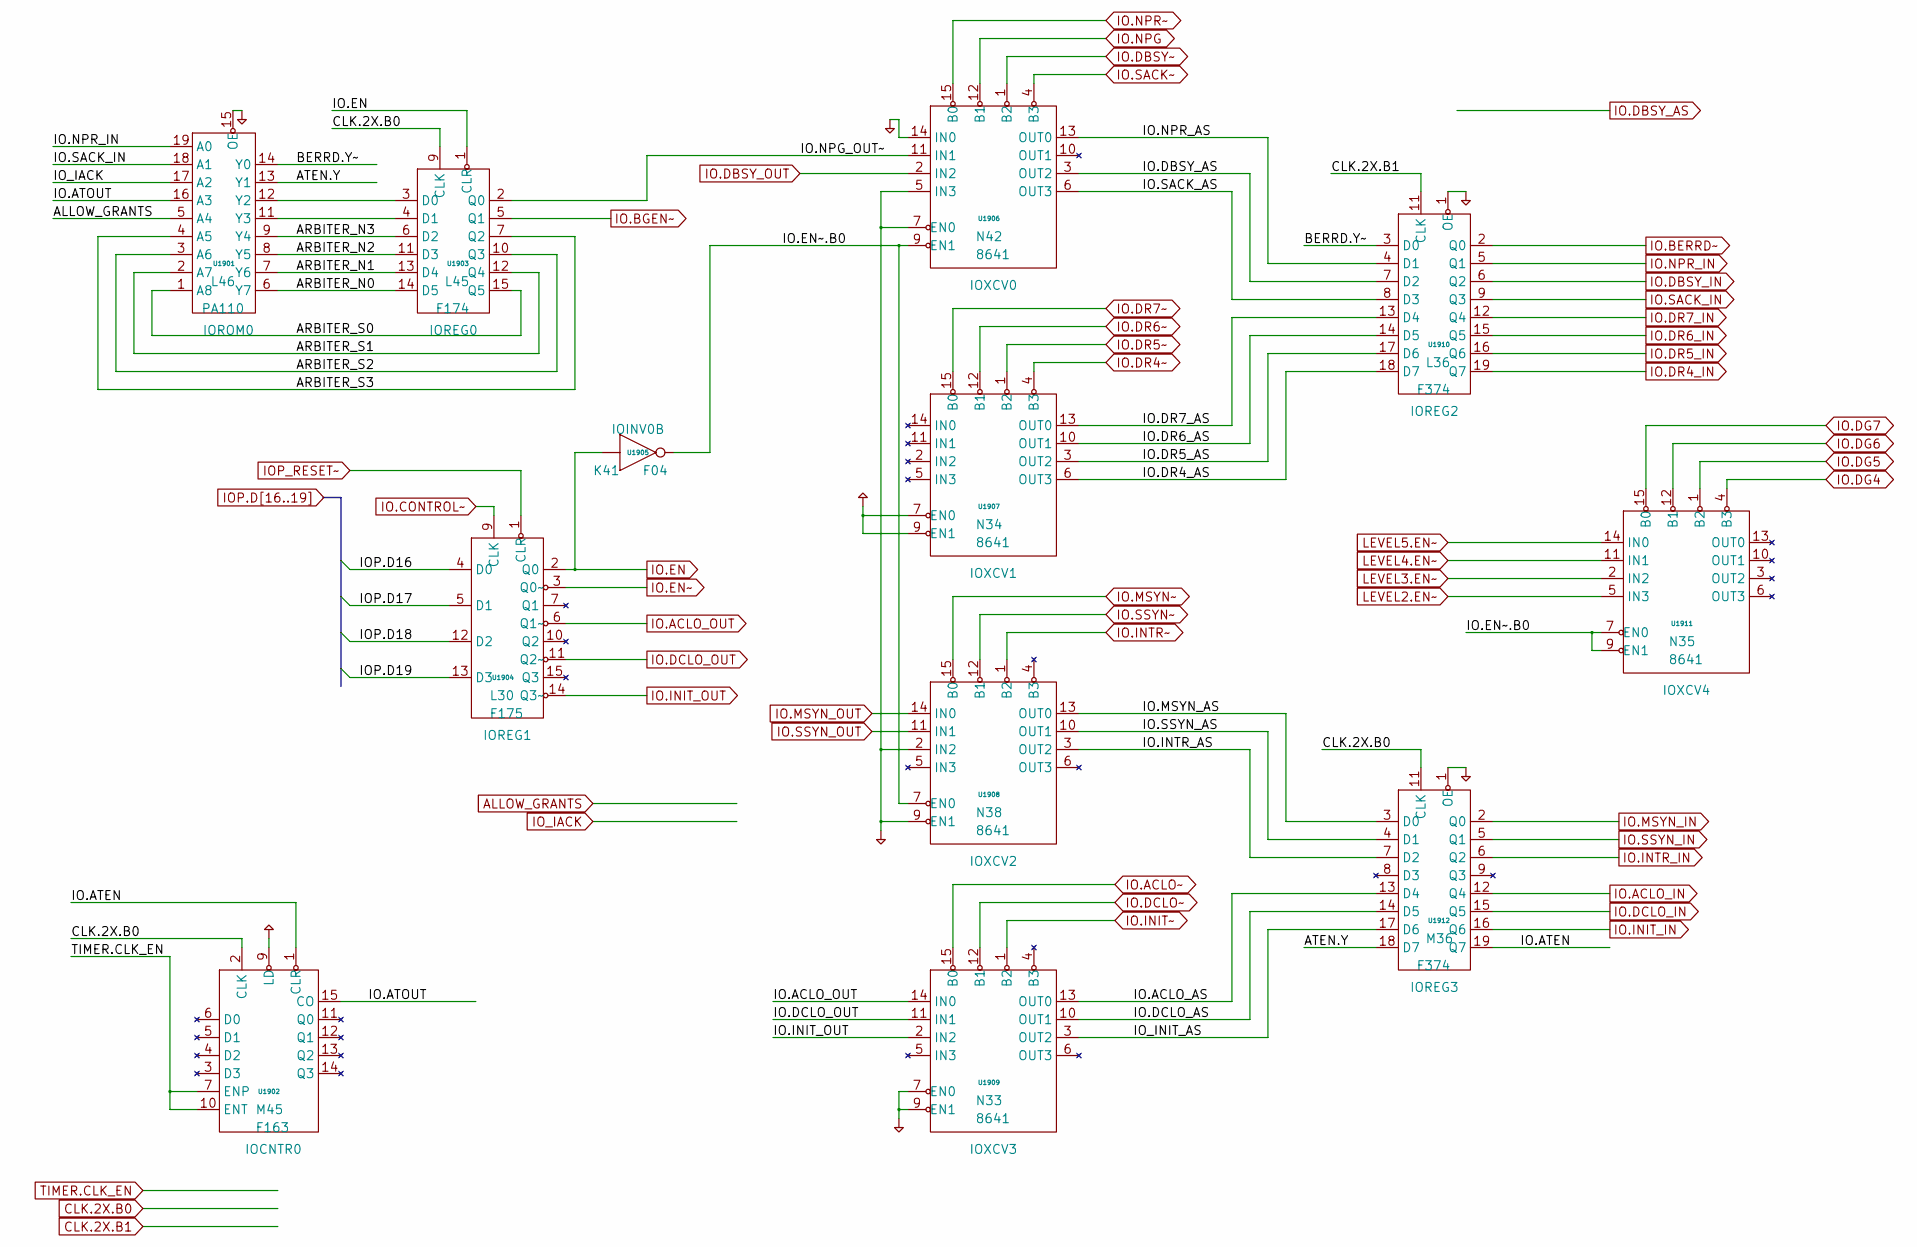
[picture p365: schematic pg_18.kicad_sch]

Parts:
U1901: PA110
U1902: F163
U1903: F174
U1904: F175
U1905: F04
U1906, U1907, U1908, U1909, U1911: 8641
U1910, U1912: F374

Connections:
ALLOW_GRANTS: U1901.5 (A4)
ARBITER_N0: U1901.6 (Y7), U1903.14 (D5)
ARBITER_N1: U1901.7 (Y6), U1903.13 (D4)
ARBITER_N2: U1901.8 (Y5), U1903.11 (D3)
ARBITER_N3: U1901.9 (Y4), U1903.6 (D2)
ARBITER_S0: U1901.1 (A8), U1903.15 (Q5)
ARBITER_S1: U1901.2 (A7), U1903.12 (Q4)
ARBITER_S2: U1901.3 (A6), U1903.10 (Q3)
ARBITER_S3: U1901.4 (A5), U1903.7 (Q2)
ATEN.Y: U1901.13 (Y1), U1912.18 (D7)
BERRD.Y~: U1901.14 (Y0), U1910.3 (D0)
CLK.2X.B0: U1902.2 (CLK), U1903.9 (CLK), U1912.11 (CLK)
CLK.2X.B1: U1910.11 (CLK)
IO.ACLO_AS: U1909.13 (OUT0), U1912.13 (D4)
IO.ACLO_IN: U1912.12 (Q4)
IO.ACLO_OUT: U1904.6 (Q1~), U1909.14 (IN0)
IO.ACLO~: U1909.15 (B0)
IO.ATEN: U1902.1 (CLR), U1912.19 (Q7)
IO.ATOUT: U1901.16 (A3), U1902.15 (CO)
IO.BERRD~: U1910.2 (Q0)
IO.BGEN~: U1903.5 (Q1)
IO.CONTROL~: U1904.9 (CLK)
IO.DBSY_AS: U1906.3 (OUT2), U1910.7 (D2)
IO.DBSY_IN: U1910.6 (Q2)
IO.DBSY_OUT: U1906.2 (IN2)
IO.DBSY~: U1906.1 (B2)
IO.DCLO_AS: U1909.10 (OUT1), U1912.14 (D5)
IO.DCLO_IN: U1912.15 (Q5)
IO.DCLO_OUT: U1904.11 (Q2~), U1909.11 (IN1)
IO.DCLO~: U1909.12 (B1)
IO.DG4: U1911.4 (B3)
IO.DG5: U1911.1 (B2)
IO.DG6: U1911.12 (B1)
IO.DG7: U1911.15 (B0)
IO.DR4_AS: U1907.6 (OUT3), U1910.18 (D7)
IO.DR4_IN: U1910.19 (Q7)
IO.DR4~: U1907.4 (B3)
IO.DR5_AS: U1907.3 (OUT2), U1910.17 (D6)
IO.DR5_IN: U1910.16 (Q6)
IO.DR5~: U1907.1 (B2)
IO.DR6_AS: U1907.10 (OUT1), U1910.14 (D5)
IO.DR6_IN: U1910.15 (Q5)
IO.DR6~: U1907.12 (B1)
IO.DR7_AS: U1907.13 (OUT0), U1910.13 (D4)
IO.DR7_IN: U1910.12 (Q4)
IO.DR7~: U1907.15 (B0)
IO.EN: U1903.1 (CLR), U1904.2 (Q0), U1905.1 (D0)
IO.EN~: U1904.3 (Q0~)
IO.EN~.B0: U1905.2 (Q), U1906.9 (EN1), U1908.7 (EN0), U1911.7 (EN0), U1911.9 (EN1)
IO.INIT_IN: U1912.16 (Q6)
IO.INIT_OUT: U1904.14 (Q3~), U1909.2 (IN2)
IO.INIT~: U1909.1 (B2)
IO.INTR_AS: U1908.3 (OUT2), U1912.7 (D2)
IO.INTR_IN: U1912.6 (Q2)
IO.INTR~: U1908.1 (B2)
IO.MSYN_AS: U1908.13 (OUT0), U1912.3 (D0)
IO.MSYN_IN: U1912.2 (Q0)
IO.MSYN_OUT: U1908.14 (IN0)
IO.MSYN~: U1908.15 (B0)
IO.NPG: U1906.12 (B1)
IO.NPG_OUT~: U1903.2 (Q0), U1906.11 (IN1)
IO.NPR_AS: U1906.13 (OUT0), U1910.4 (D1)
IO.NPR_IN: U1901.19 (A0), U1910.5 (Q1)
IO.NPR~: U1906.15 (B0)
IO.SACK_AS: U1906.6 (OUT3), U1910.8 (D3)
IO.SACK_IN: U1901.18 (A1), U1910.9 (Q3)
IO.SACK~: U1906.4 (B3)
IO.SSYN_AS: U1908.10 (OUT1), U1912.4 (D1)
IO.SSYN_IN: U1912.5 (Q1)
IO.SSYN_OUT: U1908.11 (IN1)
IO.SSYN~: U1908.12 (B1)
IOP.D16: U1904.4 (D0)
IOP.D17: U1904.5 (D1)
IOP.D18: U1904.12 (D2)
IOP.D19: U1904.13 (D3)
IOP_RESET~: U1904.1 (CLR)
IO_IACK: U1901.17 (A2)
IO_INIT_AS: U1909.3 (OUT2), U1912.17 (D6)
LEVEL2.EN~: U1911.5 (IN3)
LEVEL3.EN~: U1911.2 (IN2)
LEVEL4.EN~: U1911.11 (IN1)
LEVEL5.EN~: U1911.14 (IN0)
unnamed: U1901.11 (Y3), U1903.4 (D1)
unnamed: U1901.12 (Y2), U1903.3 (D0)
PD: U1901.15 (OE), U1906.5 (IN3), U1906.7 (EN0), U1906.14 (IN0), U1908.2 (IN2), U1908.9 (EN1), U1909.7 (EN0), U1909.9 (EN1), U1910.1 (OE), U1912.1 (OE)
PU: U1902.9 (LD), U1907.7 (EN0), U1907.9 (EN1)
TIMER.CLK_EN: U1902.7 (ENP), U1902.10 (ENT)
