Datamuseum-DK/R1000.HwDoc/Schematics/IOC/pg_19.kicad_sch

## KiCad design Schematics/IOC/pg_19.kicad_sch (2023-01-10)

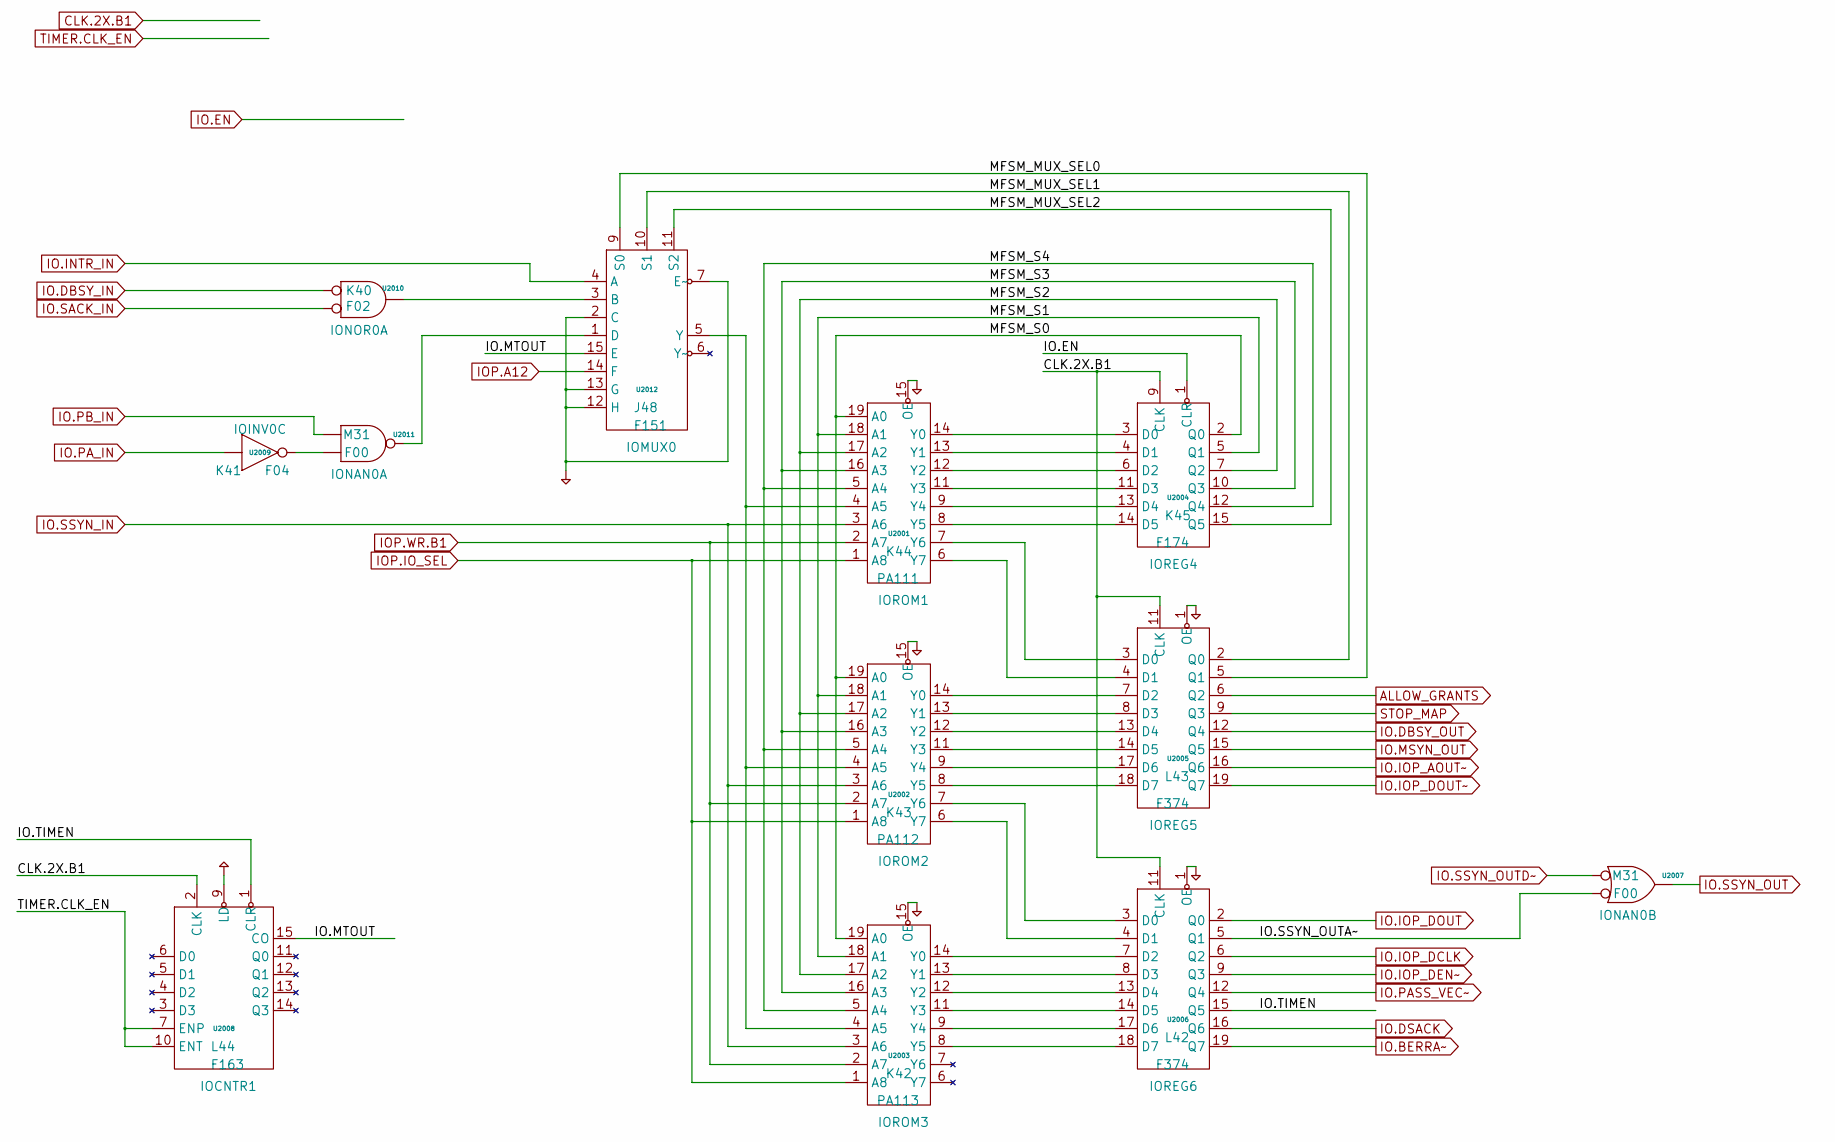
[picture p366: schematic pg_19.kicad_sch]

Parts:
U2001: PA111
U2002: PA112
U2003: PA113
U2004: F174
U2005, U2006: F374
U2007, U2011: F00
U2008: F163
U2009: F04
U2010: F02
U2012: F151

Connections:
ALLOW_GRANTS: U2005.6 (Q2)
CLK.2X.B1: U2004.9 (CLK), U2005.11 (CLK), U2006.11 (CLK), U2008.2 (CLK)
IO.BERRA~: U2006.19 (Q7)
IO.DBSY_IN: U2010.1 (D0)
IO.DBSY_OUT: U2005.12 (Q4)
IO.DSACK: U2006.16 (Q6)
IO.EN: U2004.1 (CLR)
IO.INTR_IN: U2012.4 (A)
IO.IOP_AOUT~: U2005.16 (Q6)
IO.IOP_DCLK: U2006.6 (Q2)
IO.IOP_DEN~: U2006.9 (Q3)
IO.IOP_DOUT: U2006.2 (Q0)
IO.IOP_DOUT~: U2005.19 (Q7)
IO.MSYN_OUT: U2005.15 (Q5)
IO.MTOUT: U2008.15 (CO), U2012.15 (E)
IO.PASS_VEC~: U2006.12 (Q4)
IO.PA_IN: U2009.1 (D0)
IO.PB_IN: U2011.1 (D0)
IO.SACK_IN: U2010.2 (D1)
IO.SSYN_IN: U2001.3 (A6), U2002.3 (A6), U2003.3 (A6)
IO.SSYN_OUT: U2007.3 (Q)
IO.SSYN_OUTA~: U2006.5 (Q1), U2007.2 (D1)
IO.SSYN_OUTD~: U2007.1 (D0)
IO.TIMEN: U2006.15 (Q5), U2008.1 (CLR)
IOP.A12: U2012.14 (F)
IOP.IO_SEL: U2001.1 (A8), U2002.1 (A8), U2003.1 (A8)
IOP.WR.B1: U2001.2 (A7), U2002.2 (A7), U2003.2 (A7)
MFSM_MUX_SEL0: U2005.5 (Q1), U2012.9 (S0)
MFSM_MUX_SEL1: U2005.2 (Q0), U2012.10 (S1)
MFSM_MUX_SEL2: U2004.15 (Q5), U2012.11 (S2)
MFSM_S0: U2001.19 (A0), U2002.19 (A0), U2003.19 (A0), U2004.2 (Q0)
MFSM_S1: U2001.18 (A1), U2002.18 (A1), U2003.18 (A1), U2004.5 (Q1)
MFSM_S2: U2001.17 (A2), U2002.17 (A2), U2003.17 (A2), U2004.7 (Q2)
MFSM_S3: U2001.16 (A3), U2002.16 (A3), U2003.16 (A3), U2004.10 (Q3)
MFSM_S4: U2001.5 (A4), U2002.5 (A4), U2003.5 (A4), U2004.12 (Q4)
unnamed: U2001.4 (A5), U2002.4 (A5), U2003.4 (A5), U2012.5 (Y)
unnamed: U2001.6 (Y7), U2005.4 (D1)
unnamed: U2001.7 (Y6), U2005.3 (D0)
unnamed: U2001.8 (Y5), U2004.14 (D5)
unnamed: U2001.9 (Y4), U2004.13 (D4)
unnamed: U2001.11 (Y3), U2004.11 (D3)
unnamed: U2001.12 (Y2), U2004.6 (D2)
unnamed: U2001.13 (Y1), U2004.4 (D1)
unnamed: U2001.14 (Y0), U2004.3 (D0)
unnamed: U2002.6 (Y7), U2006.4 (D1)
unnamed: U2002.7 (Y6), U2006.3 (D0)
unnamed: U2002.8 (Y5), U2005.18 (D7)
unnamed: U2002.9 (Y4), U2005.17 (D6)
unnamed: U2002.11 (Y3), U2005.14 (D5)
unnamed: U2002.12 (Y2), U2005.13 (D4)
unnamed: U2002.13 (Y1), U2005.8 (D3)
unnamed: U2002.14 (Y0), U2005.7 (D2)
unnamed: U2003.8 (Y5), U2006.18 (D7)
unnamed: U2003.9 (Y4), U2006.17 (D6)
unnamed: U2003.11 (Y3), U2006.14 (D5)
unnamed: U2003.12 (Y2), U2006.13 (D4)
unnamed: U2003.13 (Y1), U2006.8 (D3)
unnamed: U2003.14 (Y0), U2006.7 (D2)
unnamed: U2009.2 (Q), U2011.2 (D1)
unnamed: U2010.3 (Q), U2012.3 (B)
unnamed: U2011.3 (Q), U2012.1 (D)
PD: U2001.15 (OE), U2002.15 (OE), U2003.15 (OE), U2005.1 (OE), U2006.1 (OE), U2012.2 (C), U2012.7 (E~), U2012.12 (H), U2012.13 (G)
PU: U2008.9 (LD)
STOP_MAP: U2005.9 (Q3)
TIMER.CLK_EN: U2008.7 (ENP), U2008.10 (ENT)
