Datamuseum-DK/R1000.HwDoc/Schematics/IOC/pg_20.kicad_sch

## KiCad design Schematics/IOC/pg_20.kicad_sch (2023-01-10)

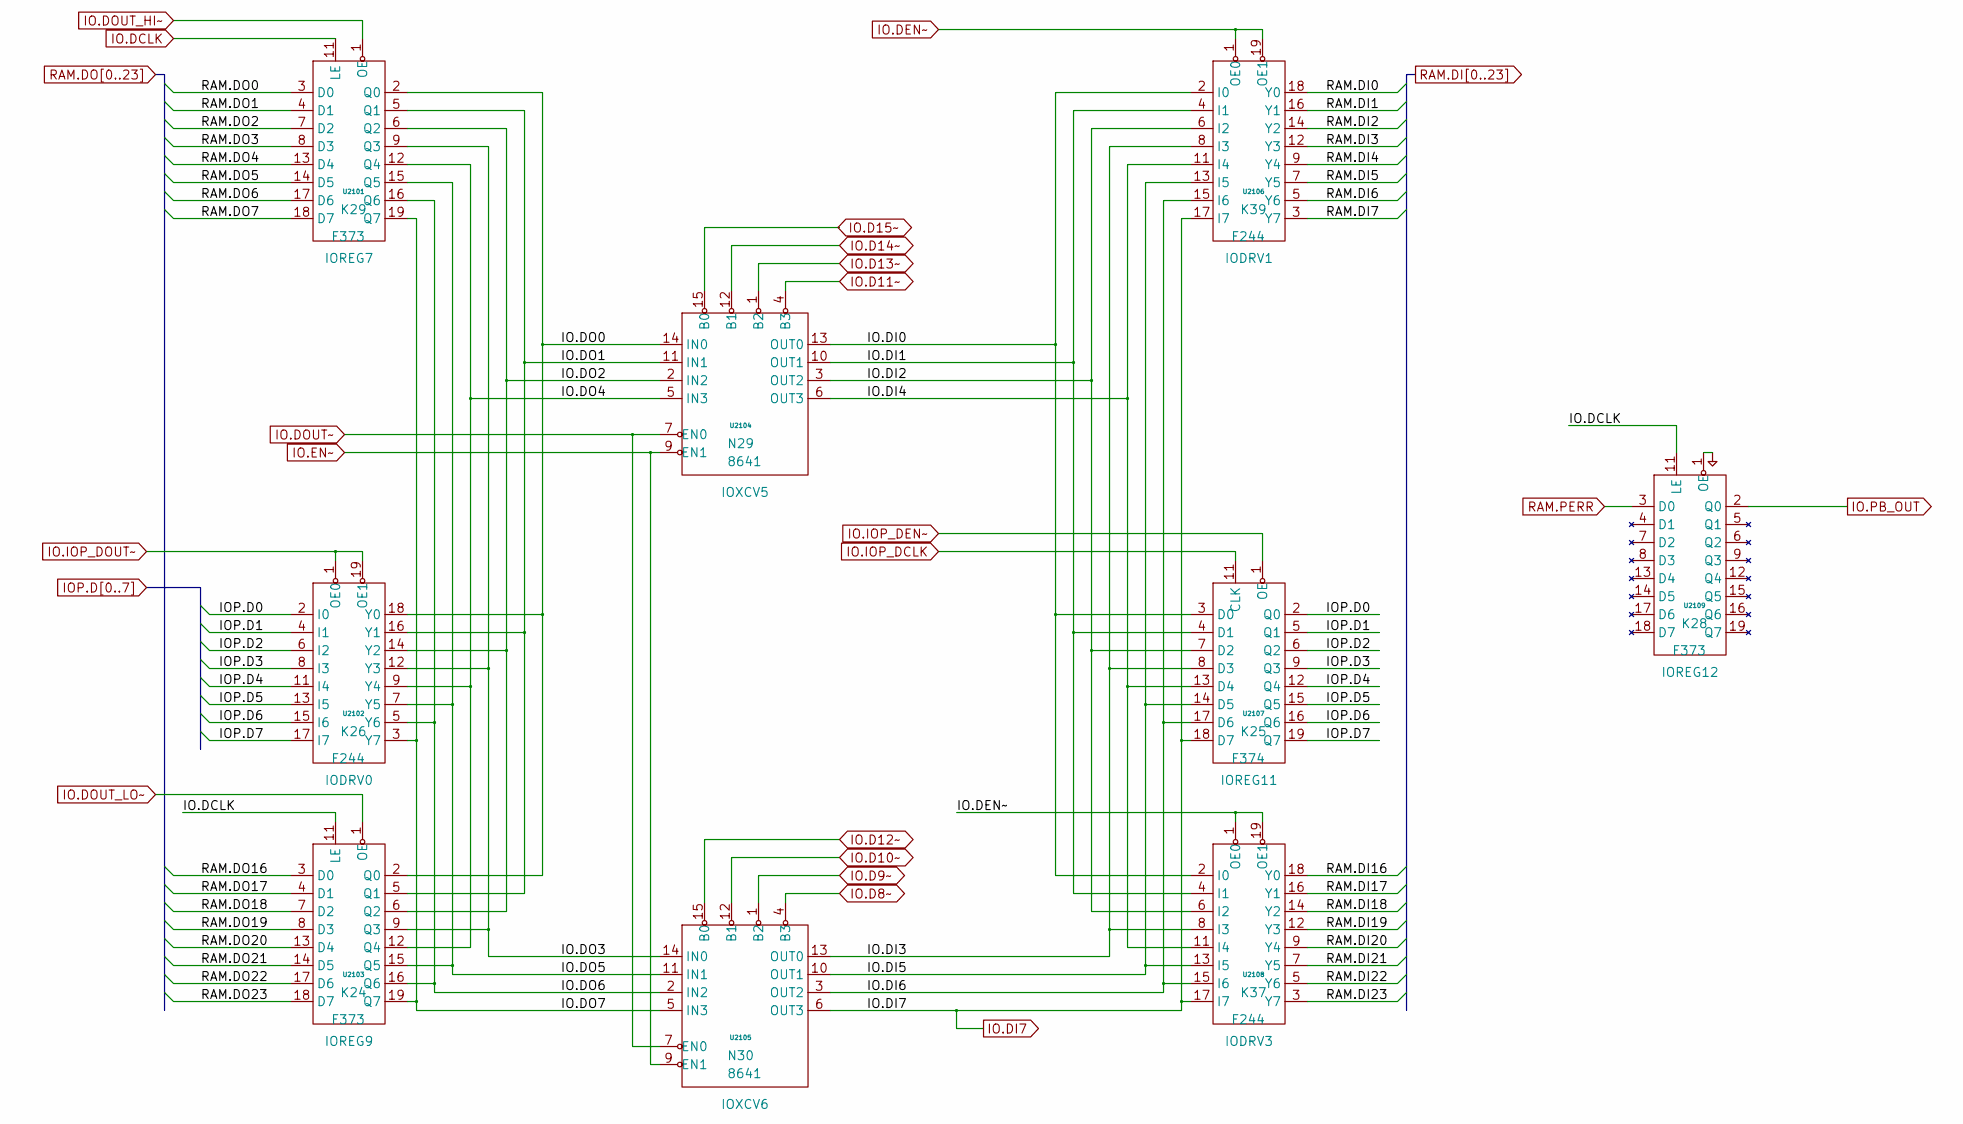
[picture p367: schematic pg_20.kicad_sch]

Parts:
U2101, U2103, U2109: F373
U2102, U2106, U2108: F244
U2104, U2105: 8641
U2107: F374

Connections:
IO.D8~: U2105.4 (B3)
IO.D9~: U2105.1 (B2)
IO.D10~: U2105.12 (B1)
IO.D11~: U2104.4 (B3)
IO.D12~: U2105.15 (B0)
IO.D13~: U2104.1 (B2)
IO.D14~: U2104.12 (B1)
IO.D15~: U2104.15 (B0)
IO.DCLK: U2101.11 (LE), U2103.11 (LE), U2109.11 (LE)
IO.DEN~: U2106.1 (OE0), U2106.19 (OE1), U2108.1 (OE0), U2108.19 (OE1)
IO.DI0: U2104.13 (OUT0), U2106.2 (I0), U2107.3 (D0), U2108.2 (I0)
IO.DI1: U2104.10 (OUT1), U2106.4 (I1), U2107.4 (D1), U2108.4 (I1)
IO.DI2: U2104.3 (OUT2), U2106.6 (I2), U2107.7 (D2), U2108.6 (I2)
IO.DI3: U2105.13 (OUT0), U2106.8 (I3), U2107.8 (D3), U2108.8 (I3)
IO.DI4: U2104.6 (OUT3), U2106.11 (I4), U2107.13 (D4), U2108.11 (I4)
IO.DI5: U2105.10 (OUT1), U2106.13 (I5), U2107.14 (D5), U2108.13 (I5)
IO.DI6: U2105.3 (OUT2), U2106.15 (I6), U2107.17 (D6), U2108.15 (I6)
IO.DI7: U2105.6 (OUT3), U2106.17 (I7), U2107.18 (D7), U2108.17 (I7)
IO.DO0: U2101.2 (Q0), U2102.18 (Y0), U2103.2 (Q0), U2104.14 (IN0)
IO.DO1: U2101.5 (Q1), U2102.16 (Y1), U2103.5 (Q1), U2104.11 (IN1)
IO.DO2: U2101.6 (Q2), U2102.14 (Y2), U2103.6 (Q2), U2104.2 (IN2)
IO.DO3: U2101.9 (Q3), U2102.12 (Y3), U2103.9 (Q3), U2105.14 (IN0)
IO.DO4: U2101.12 (Q4), U2102.9 (Y4), U2103.12 (Q4), U2104.5 (IN3)
IO.DO5: U2101.15 (Q5), U2102.7 (Y5), U2103.15 (Q5), U2105.11 (IN1)
IO.DO6: U2101.16 (Q6), U2102.5 (Y6), U2103.16 (Q6), U2105.2 (IN2)
IO.DO7: U2101.19 (Q7), U2102.3 (Y7), U2103.19 (Q7), U2105.5 (IN3)
IO.DOUT_HI~: U2101.1 (OE)
IO.DOUT_LO~: U2103.1 (OE)
IO.DOUT~: U2104.7 (EN0), U2105.7 (EN0)
IO.EN~: U2104.9 (EN1), U2105.9 (EN1)
IO.IOP_DCLK: U2107.11 (CLK)
IO.IOP_DEN~: U2107.1 (OE)
IO.IOP_DOUT~: U2102.1 (OE0), U2102.19 (OE1)
IO.PB_OUT: U2109.2 (Q0)
IOP.D0: U2102.2 (I0), U2107.2 (Q0)
IOP.D1: U2102.4 (I1), U2107.5 (Q1)
IOP.D2: U2102.6 (I2), U2107.6 (Q2)
IOP.D3: U2102.8 (I3), U2107.9 (Q3)
IOP.D4: U2102.11 (I4), U2107.12 (Q4)
IOP.D5: U2102.13 (I5), U2107.15 (Q5)
IOP.D6: U2102.15 (I6), U2107.16 (Q6)
IOP.D7: U2102.17 (I7), U2107.19 (Q7)
PD: U2109.1 (OE)
RAM.DI0: U2106.18 (Y0)
RAM.DI1: U2106.16 (Y1)
RAM.DI2: U2106.14 (Y2)
RAM.DI3: U2106.12 (Y3)
RAM.DI4: U2106.9 (Y4)
RAM.DI5: U2106.7 (Y5)
RAM.DI6: U2106.5 (Y6)
RAM.DI7: U2106.3 (Y7)
RAM.DI16: U2108.18 (Y0)
RAM.DI17: U2108.16 (Y1)
RAM.DI18: U2108.14 (Y2)
RAM.DI19: U2108.12 (Y3)
RAM.DI20: U2108.9 (Y4)
RAM.DI21: U2108.7 (Y5)
RAM.DI22: U2108.5 (Y6)
RAM.DI23: U2108.3 (Y7)
RAM.DO0: U2101.3 (D0)
RAM.DO1: U2101.4 (D1)
RAM.DO2: U2101.7 (D2)
RAM.DO3: U2101.8 (D3)
RAM.DO4: U2101.13 (D4)
RAM.DO5: U2101.14 (D5)
RAM.DO6: U2101.17 (D6)
RAM.DO7: U2101.18 (D7)
RAM.DO16: U2103.3 (D0)
RAM.DO17: U2103.4 (D1)
RAM.DO18: U2103.7 (D2)
RAM.DO19: U2103.8 (D3)
RAM.DO20: U2103.13 (D4)
RAM.DO21: U2103.14 (D5)
RAM.DO22: U2103.17 (D6)
RAM.DO23: U2103.18 (D7)
RAM.PERR: U2109.3 (D0)
