Datamuseum-DK/R1000.HwDoc/Schematics/IOC/pg_21.kicad_sch

## KiCad design Schematics/IOC/pg_21.kicad_sch (2023-01-10)

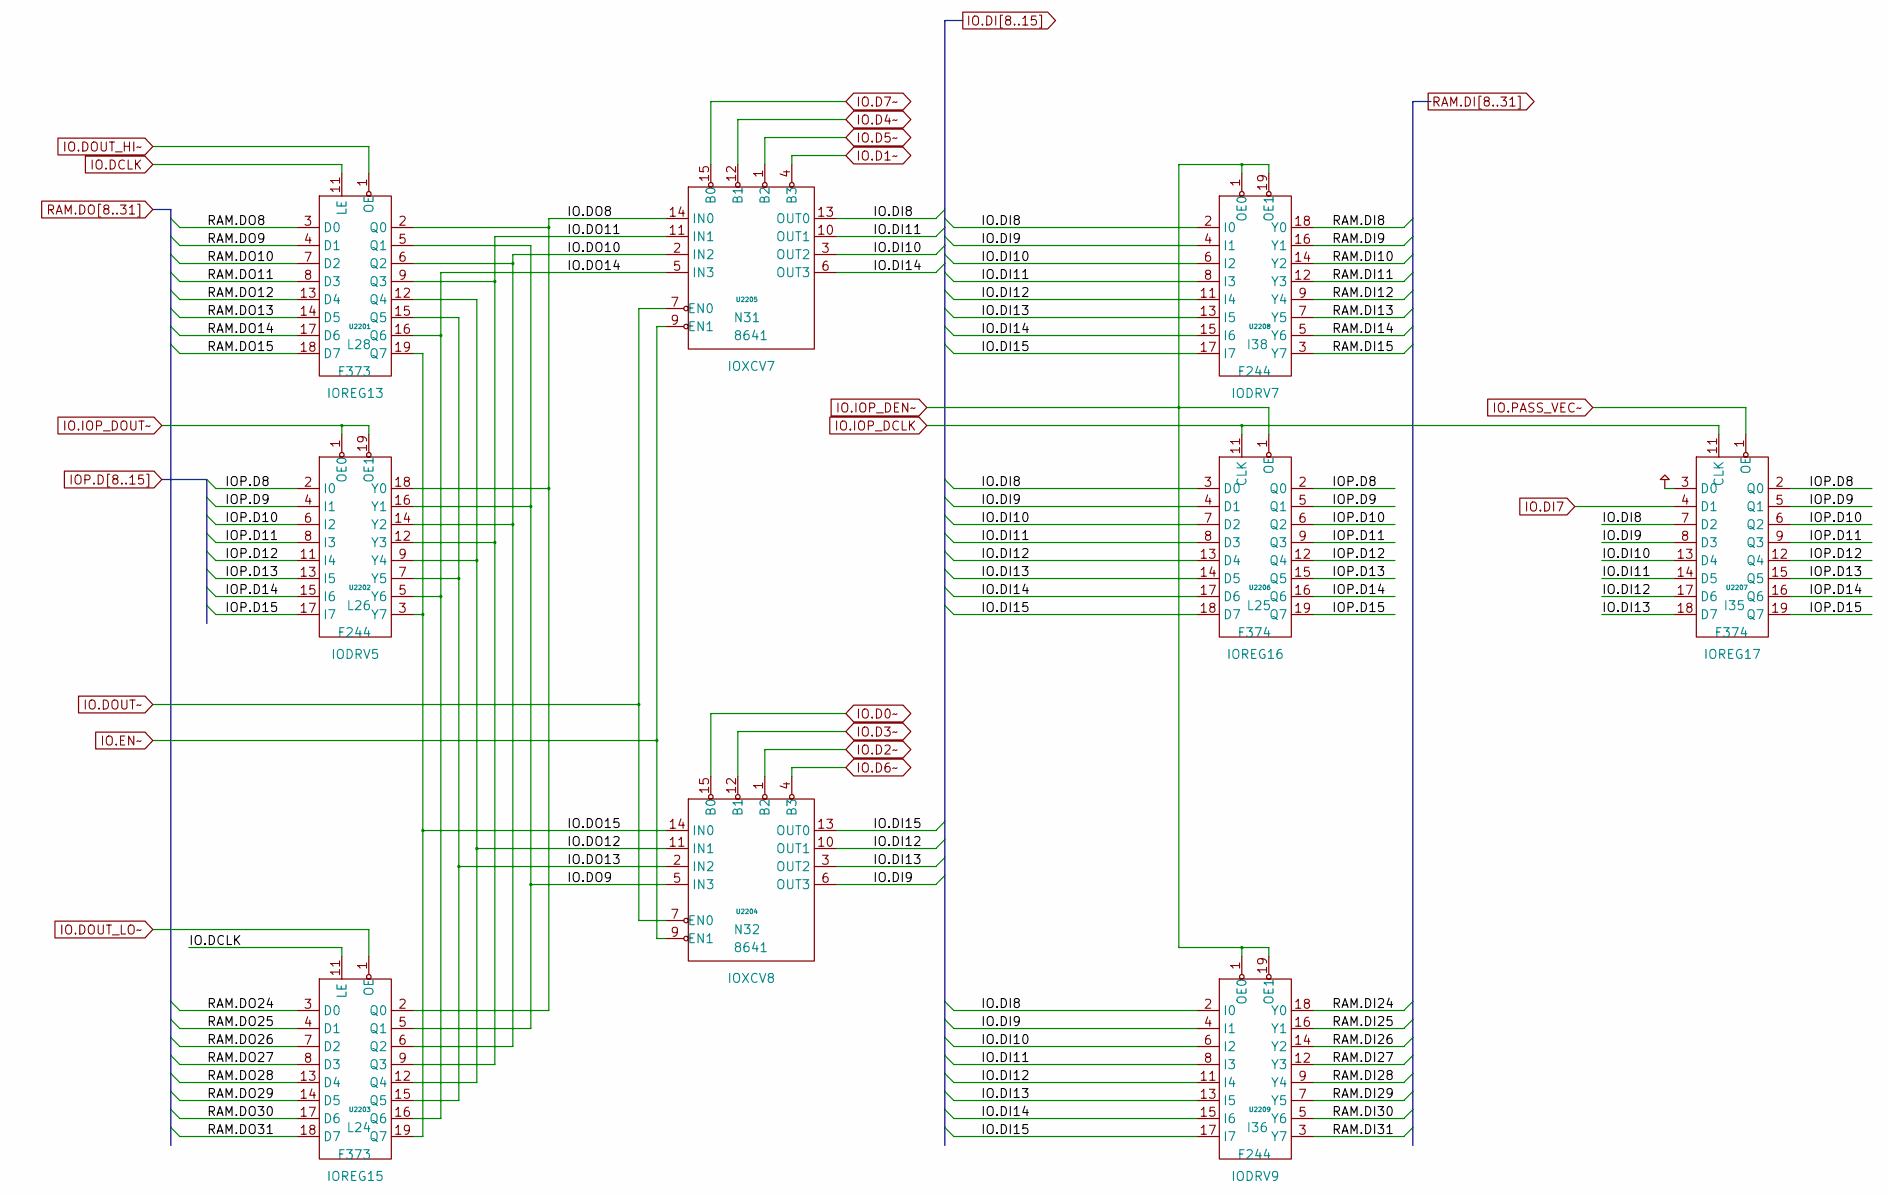
[picture p368: schematic pg_21.kicad_sch]

Parts:
U2201, U2203: F373
U2202, U2208, U2209: F244
U2204, U2205: 8641
U2206, U2207: F374

Connections:
IO.D0~: U2204.15 (B0)
IO.D1~: U2205.4 (B3)
IO.D2~: U2204.1 (B2)
IO.D3~: U2204.12 (B1)
IO.D4~: U2205.12 (B1)
IO.D5~: U2205.1 (B2)
IO.D6~: U2204.4 (B3)
IO.D7~: U2205.15 (B0)
IO.DCLK: U2201.11 (LE), U2203.11 (LE)
IO.DI7: U2207.4 (D1)
IO.DI8: U2205.13 (OUT0), U2206.3 (D0), U2207.7 (D2), U2208.2 (I0), U2209.2 (I0)
IO.DI9: U2204.6 (OUT3), U2206.4 (D1), U2207.8 (D3), U2208.4 (I1), U2209.4 (I1)
IO.DI10: U2205.3 (OUT2), U2206.7 (D2), U2207.13 (D4), U2208.6 (I2), U2209.6 (I2)
IO.DI11: U2205.10 (OUT1), U2206.8 (D3), U2207.14 (D5), U2208.8 (I3), U2209.8 (I3)
IO.DI12: U2204.10 (OUT1), U2206.13 (D4), U2207.17 (D6), U2208.11 (I4), U2209.11 (I4)
IO.DI13: U2204.3 (OUT2), U2206.14 (D5), U2207.18 (D7), U2208.13 (I5), U2209.13 (I5)
IO.DI14: U2205.6 (OUT3), U2206.17 (D6), U2208.15 (I6), U2209.15 (I6)
IO.DI15: U2204.13 (OUT0), U2206.18 (D7), U2208.17 (I7), U2209.17 (I7)
IO.DO8: U2201.2 (Q0), U2202.18 (Y0), U2203.2 (Q0), U2205.14 (IN0)
IO.DO9: U2201.5 (Q1), U2202.16 (Y1), U2203.5 (Q1), U2204.5 (IN3)
IO.DO10: U2201.6 (Q2), U2202.14 (Y2), U2203.6 (Q2), U2205.2 (IN2)
IO.DO11: U2201.9 (Q3), U2202.12 (Y3), U2203.9 (Q3), U2205.11 (IN1)
IO.DO12: U2201.12 (Q4), U2202.9 (Y4), U2203.12 (Q4), U2204.11 (IN1)
IO.DO13: U2201.15 (Q5), U2202.7 (Y5), U2203.15 (Q5), U2204.2 (IN2)
IO.DO14: U2201.16 (Q6), U2202.5 (Y6), U2203.16 (Q6), U2205.5 (IN3)
IO.DO15: U2201.19 (Q7), U2202.3 (Y7), U2203.19 (Q7), U2204.14 (IN0)
IO.DOUT_HI~: U2201.1 (OE)
IO.DOUT_LO~: U2203.1 (OE)
IO.DOUT~: U2204.7 (EN0), U2205.7 (EN0)
IO.EN~: U2204.9 (EN1), U2205.9 (EN1)
IO.IOP_DCLK: U2206.11 (CLK), U2207.11 (CLK)
IO.IOP_DEN~: U2206.1 (OE), U2208.1 (OE0), U2208.19 (OE1), U2209.1 (OE0), U2209.19 (OE1)
IO.IOP_DOUT~: U2202.1 (OE0), U2202.19 (OE1)
IO.PASS_VEC~: U2207.1 (OE)
IOP.D8: U2202.2 (I0), U2206.2 (Q0), U2207.2 (Q0)
IOP.D9: U2202.4 (I1), U2206.5 (Q1), U2207.5 (Q1)
IOP.D10: U2202.6 (I2), U2206.6 (Q2), U2207.6 (Q2)
IOP.D11: U2202.8 (I3), U2206.9 (Q3), U2207.9 (Q3)
IOP.D12: U2202.11 (I4), U2206.12 (Q4), U2207.12 (Q4)
IOP.D13: U2202.13 (I5), U2206.15 (Q5), U2207.15 (Q5)
IOP.D14: U2202.15 (I6), U2206.16 (Q6), U2207.16 (Q6)
IOP.D15: U2202.17 (I7), U2206.19 (Q7), U2207.19 (Q7)
PU: U2207.3 (D0)
RAM.DI8: U2208.18 (Y0)
RAM.DI9: U2208.16 (Y1)
RAM.DI10: U2208.14 (Y2)
RAM.DI11: U2208.12 (Y3)
RAM.DI12: U2208.9 (Y4)
RAM.DI13: U2208.7 (Y5)
RAM.DI14: U2208.5 (Y6)
RAM.DI15: U2208.3 (Y7)
RAM.DI24: U2209.18 (Y0)
RAM.DI25: U2209.16 (Y1)
RAM.DI26: U2209.14 (Y2)
RAM.DI27: U2209.12 (Y3)
RAM.DI28: U2209.9 (Y4)
RAM.DI29: U2209.7 (Y5)
RAM.DI30: U2209.5 (Y6)
RAM.DI31: U2209.3 (Y7)
RAM.DO8: U2201.3 (D0)
RAM.DO9: U2201.4 (D1)
RAM.DO10: U2201.7 (D2)
RAM.DO11: U2201.8 (D3)
RAM.DO12: U2201.13 (D4)
RAM.DO13: U2201.14 (D5)
RAM.DO14: U2201.17 (D6)
RAM.DO15: U2201.18 (D7)
RAM.DO24: U2203.3 (D0)
RAM.DO25: U2203.4 (D1)
RAM.DO26: U2203.7 (D2)
RAM.DO27: U2203.8 (D3)
RAM.DO28: U2203.13 (D4)
RAM.DO29: U2203.14 (D5)
RAM.DO30: U2203.17 (D6)
RAM.DO31: U2203.18 (D7)
