Datamuseum-DK/R1000.HwDoc/Schematics/IOC/pg_22.kicad_sch

## KiCad design Schematics/IOC/pg_22.kicad_sch (2023-01-10)

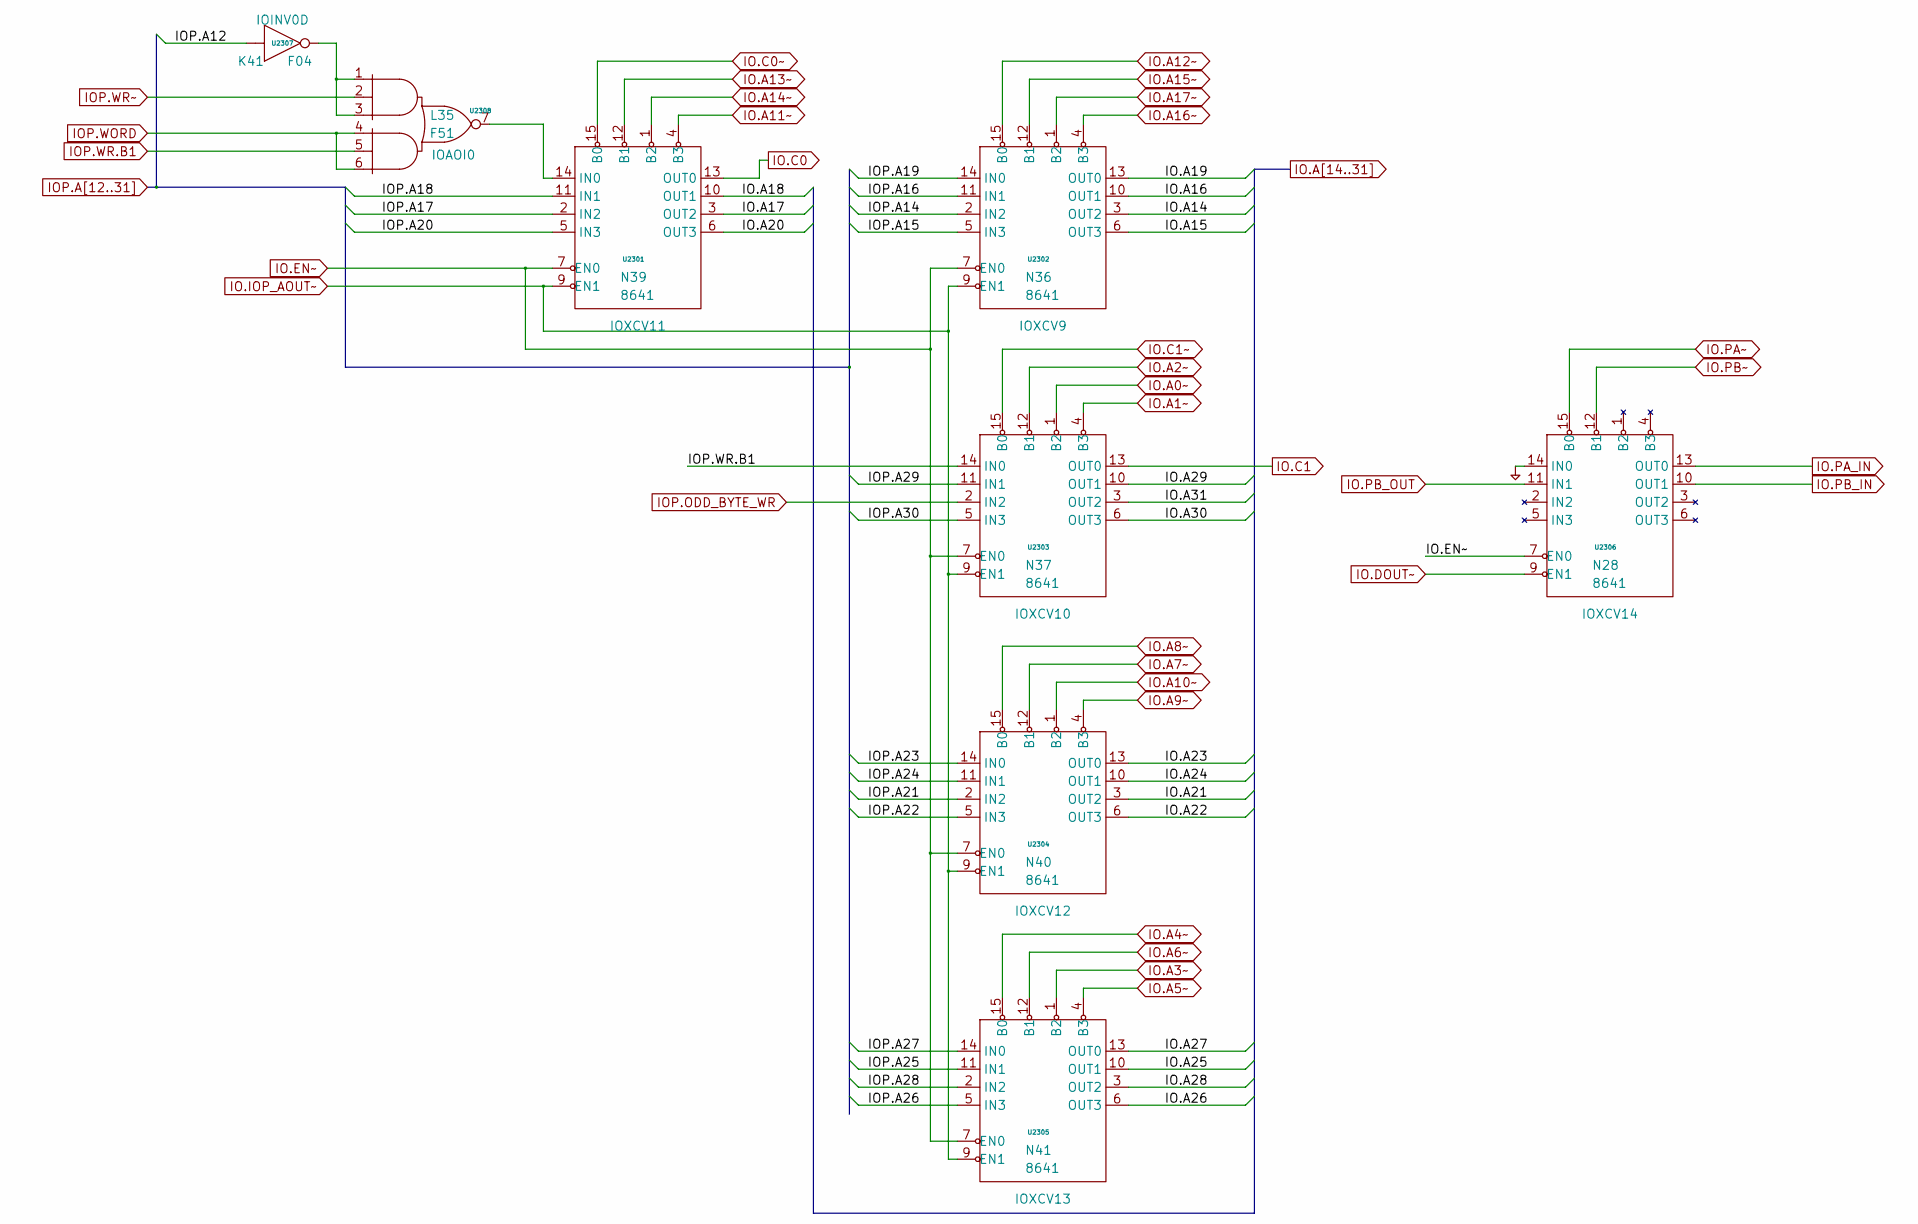
[picture p369: schematic pg_22.kicad_sch]

Parts:
U2301, U2302, U2303, U2304, U2305, U2306: 8641
U2307: F04
U2308: F51

Connections:
IO.A0~: U2303.1 (B2)
IO.A1~: U2303.4 (B3)
IO.A2~: U2303.12 (B1)
IO.A3~: U2305.1 (B2)
IO.A4~: U2305.15 (B0)
IO.A5~: U2305.4 (B3)
IO.A6~: U2305.12 (B1)
IO.A7~: U2304.12 (B1)
IO.A8~: U2304.15 (B0)
IO.A9~: U2304.4 (B3)
IO.A10~: U2304.1 (B2)
IO.A11~: U2301.4 (B3)
IO.A12~: U2302.15 (B0)
IO.A13~: U2301.12 (B1)
IO.A14: U2302.3 (OUT2)
IO.A14~: U2301.1 (B2)
IO.A15: U2302.6 (OUT3)
IO.A15~: U2302.12 (B1)
IO.A16: U2302.10 (OUT1)
IO.A16~: U2302.4 (B3)
IO.A17: U2301.3 (OUT2)
IO.A17~: U2302.1 (B2)
IO.A18: U2301.10 (OUT1)
IO.A19: U2302.13 (OUT0)
IO.A20: U2301.6 (OUT3)
IO.A21: U2304.3 (OUT2)
IO.A22: U2304.6 (OUT3)
IO.A23: U2304.13 (OUT0)
IO.A24: U2304.10 (OUT1)
IO.A25: U2305.10 (OUT1)
IO.A26: U2305.6 (OUT3)
IO.A27: U2305.13 (OUT0)
IO.A28: U2305.3 (OUT2)
IO.A29: U2303.10 (OUT1)
IO.A30: U2303.6 (OUT3)
IO.A31: U2303.3 (OUT2)
IO.C0: U2301.13 (OUT0)
IO.C0~: U2301.15 (B0)
IO.C1: U2303.13 (OUT0)
IO.C1~: U2303.15 (B0)
IO.DOUT~: U2306.9 (EN1)
IO.EN~: U2301.7 (EN0), U2302.7 (EN0), U2303.7 (EN0), U2304.7 (EN0), U2305.7 (EN0), U2306.7 (EN0)
IO.IOP_AOUT~: U2301.9 (EN1), U2302.9 (EN1), U2303.9 (EN1), U2304.9 (EN1), U2305.9 (EN1)
IO.PA_IN: U2306.13 (OUT0)
IO.PA~: U2306.15 (B0)
IO.PB_IN: U2306.10 (OUT1)
IO.PB_OUT: U2306.11 (IN1)
IO.PB~: U2306.12 (B1)
IOP.A12: U2307.1 (D0)
IOP.A14: U2302.2 (IN2)
IOP.A15: U2302.5 (IN3)
IOP.A16: U2302.11 (IN1)
IOP.A17: U2301.2 (IN2)
IOP.A18: U2301.11 (IN1)
IOP.A19: U2302.14 (IN0)
IOP.A20: U2301.5 (IN3)
IOP.A21: U2304.2 (IN2)
IOP.A22: U2304.5 (IN3)
IOP.A23: U2304.14 (IN0)
IOP.A24: U2304.11 (IN1)
IOP.A25: U2305.11 (IN1)
IOP.A26: U2305.5 (IN3)
IOP.A27: U2305.14 (IN0)
IOP.A28: U2305.2 (IN2)
IOP.A29: U2303.11 (IN1)
IOP.A30: U2303.5 (IN3)
IOP.ODD_BYTE_WR: U2303.2 (IN2)
IOP.WORD: U2308.4 (B1), U2308.6 (B3)
IOP.WR.B1: U2303.14 (IN0), U2308.5 (B2)
IOP.WR~: U2308.2 (A2)
unnamed: U2301.14 (IN0), U2308.7 (Q)
unnamed: U2307.2 (Q), U2308.1 (A1), U2308.3 (A3)
PD: U2306.14 (IN0)
