Datamuseum-DK/R1000.HwDoc/Schematics/IOC/pg_23.kicad_sch

## KiCad design Schematics/IOC/pg_23.kicad_sch (2023-01-10)

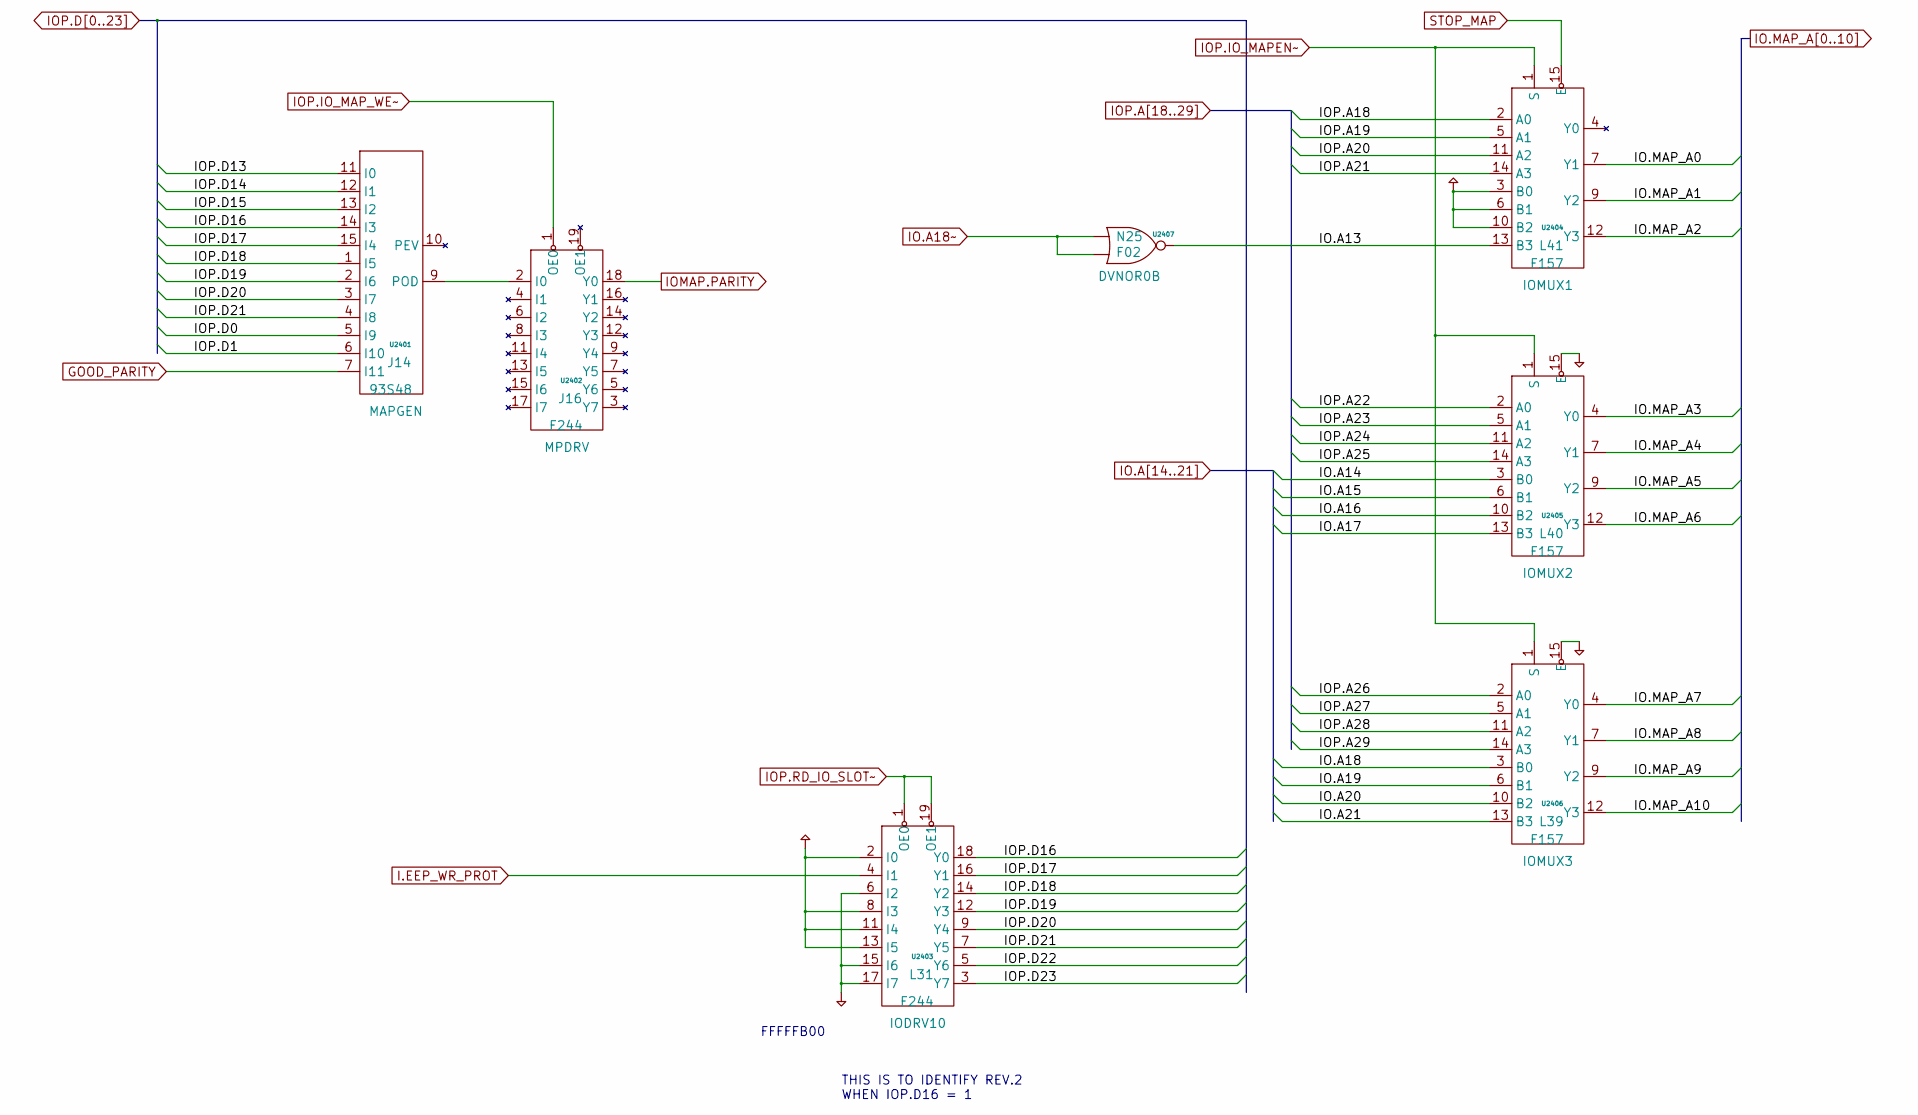
[picture p370: schematic pg_23.kicad_sch]

Parts:
U2401: 93S48
U2402, U2403: F244
U2404, U2405, U2406: F157
U2407: F02

Connections:
GOOD_PARITY: U2401.7 (I11)
I.EEP_WR_PROT: U2403.4 (I1)
IO.A13: U2404.13 (B3), U2407.3 (Q)
IO.A14: U2405.3 (B0)
IO.A15: U2405.6 (B1)
IO.A16: U2405.10 (B2)
IO.A17: U2405.13 (B3)
IO.A18: U2406.3 (B0)
IO.A18~: U2407.1 (D0), U2407.2 (D1)
IO.A19: U2406.6 (B1)
IO.A20: U2406.10 (B2)
IO.A21: U2406.13 (B3)
IO.MAP_A0: U2404.7 (Y1)
IO.MAP_A1: U2404.9 (Y2)
IO.MAP_A2: U2404.12 (Y3)
IO.MAP_A3: U2405.4 (Y0)
IO.MAP_A4: U2405.7 (Y1)
IO.MAP_A5: U2405.9 (Y2)
IO.MAP_A6: U2405.12 (Y3)
IO.MAP_A7: U2406.4 (Y0)
IO.MAP_A8: U2406.7 (Y1)
IO.MAP_A9: U2406.9 (Y2)
IO.MAP_A10: U2406.12 (Y3)
IOMAP.PARITY: U2402.18 (Y0)
IOP.A18: U2404.2 (A0)
IOP.A19: U2404.5 (A1)
IOP.A20: U2404.11 (A2)
IOP.A21: U2404.14 (A3)
IOP.A22: U2405.2 (A0)
IOP.A23: U2405.5 (A1)
IOP.A24: U2405.11 (A2)
IOP.A25: U2405.14 (A3)
IOP.A26: U2406.2 (A0)
IOP.A27: U2406.5 (A1)
IOP.A28: U2406.11 (A2)
IOP.A29: U2406.14 (A3)
IOP.D0: U2401.5 (I9)
IOP.D1: U2401.6 (I10)
IOP.D13: U2401.11 (I0)
IOP.D14: U2401.12 (I1)
IOP.D15: U2401.13 (I2)
IOP.D16: U2401.14 (I3), U2403.18 (Y0)
IOP.D17: U2401.15 (I4), U2403.16 (Y1)
IOP.D18: U2401.1 (I5), U2403.14 (Y2)
IOP.D19: U2401.2 (I6), U2403.12 (Y3)
IOP.D20: U2401.3 (I7), U2403.9 (Y4)
IOP.D21: U2401.4 (I8), U2403.7 (Y5)
IOP.D22: U2403.5 (Y6)
IOP.D23: U2403.3 (Y7)
IOP.IO_MAPEN~: U2404.1 (S), U2405.1 (S), U2406.1 (S)
IOP.IO_MAP_WE~: U2402.1 (OE0)
IOP.RD_IO_SLOT~: U2403.1 (OE0), U2403.19 (OE1)
unnamed: U2401.9 (POD), U2402.2 (I0)
PD: U2403.6 (I2), U2403.15 (I6), U2403.17 (I7), U2405.15 (E), U2406.15 (E)
PU: U2403.2 (I0), U2403.8 (I3), U2403.11 (I4), U2403.13 (I5), U2404.3 (B0), U2404.6 (B1), U2404.10 (B2)
STOP_MAP: U2404.15 (E)

Notes on the sheet:
FFFFFB00
THIS IS TO IDENTIFY REV.2 WHEN IOP.D16 = 1
