Datamuseum-DK/R1000.HwDoc/Schematics/IOC/pg_24.kicad_sch

## KiCad design Schematics/IOC/pg_24.kicad_sch (2023-01-10)

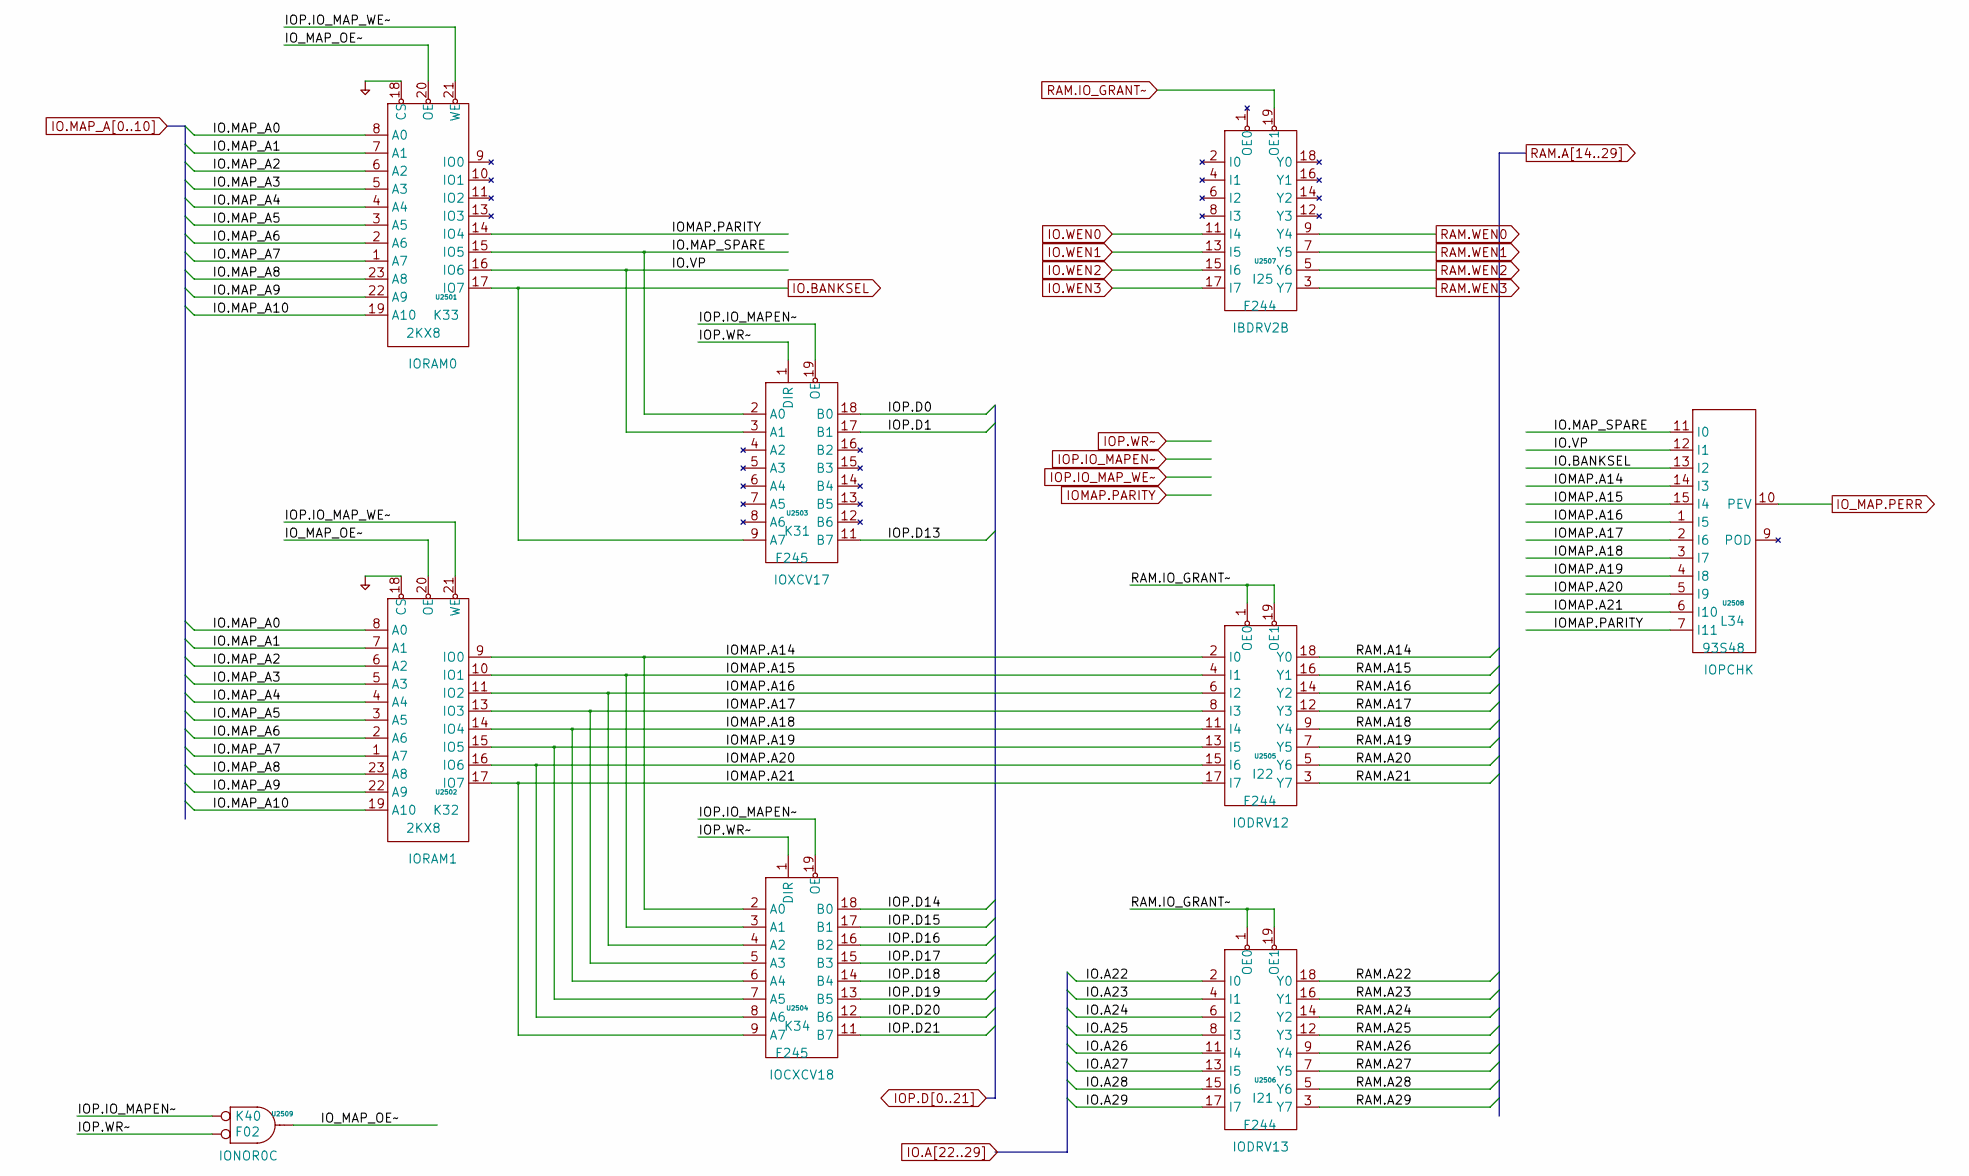
[picture p371: schematic pg_24.kicad_sch]

Parts:
U2501, U2502: 2KX8
U2503, U2504: F245
U2505, U2506, U2507: F244
U2508: 93S48
U2509: F02

Connections:
IO.A22: U2506.2 (I0)
IO.A23: U2506.4 (I1)
IO.A24: U2506.6 (I2)
IO.A25: U2506.8 (I3)
IO.A26: U2506.11 (I4)
IO.A27: U2506.13 (I5)
IO.A28: U2506.15 (I6)
IO.A29: U2506.17 (I7)
IO.BANKSEL: U2501.17 (IO7), U2503.9 (A7), U2508.13 (I2)
IO.MAP_A0: U2501.8 (A0), U2502.8 (A0)
IO.MAP_A1: U2501.7 (A1), U2502.7 (A1)
IO.MAP_A2: U2501.6 (A2), U2502.6 (A2)
IO.MAP_A3: U2501.5 (A3), U2502.5 (A3)
IO.MAP_A4: U2501.4 (A4), U2502.4 (A4)
IO.MAP_A5: U2501.3 (A5), U2502.3 (A5)
IO.MAP_A6: U2501.2 (A6), U2502.2 (A6)
IO.MAP_A7: U2501.1 (A7), U2502.1 (A7)
IO.MAP_A8: U2501.23 (A8), U2502.23 (A8)
IO.MAP_A9: U2501.22 (A9), U2502.22 (A9)
IO.MAP_A10: U2501.19 (A10), U2502.19 (A10)
IO.MAP_SPARE: U2501.15 (IO5), U2503.2 (A0), U2508.11 (I0)
IO.VP: U2501.16 (IO6), U2503.3 (A1), U2508.12 (I1)
IO.WEN0: U2507.11 (I4)
IO.WEN1: U2507.13 (I5)
IO.WEN2: U2507.15 (I6)
IO.WEN3: U2507.17 (I7)
IOMAP.A14: U2502.9 (IO0), U2504.2 (A0), U2505.2 (I0), U2508.14 (I3)
IOMAP.A15: U2502.10 (IO1), U2504.3 (A1), U2505.4 (I1), U2508.15 (I4)
IOMAP.A16: U2502.11 (IO2), U2504.4 (A2), U2505.6 (I2), U2508.1 (I5)
IOMAP.A17: U2502.13 (IO3), U2504.5 (A3), U2505.8 (I3), U2508.2 (I6)
IOMAP.A18: U2502.14 (IO4), U2504.6 (A4), U2505.11 (I4), U2508.3 (I7)
IOMAP.A19: U2502.15 (IO5), U2504.7 (A5), U2505.13 (I5), U2508.4 (I8)
IOMAP.A20: U2502.16 (IO6), U2504.8 (A6), U2505.15 (I6), U2508.5 (I9)
IOMAP.A21: U2502.17 (IO7), U2504.9 (A7), U2505.17 (I7), U2508.6 (I10)
IOMAP.PARITY: U2501.14 (IO4), U2508.7 (I11)
IOP.D0: U2503.18 (B0)
IOP.D1: U2503.17 (B1)
IOP.D13: U2503.11 (B7)
IOP.D14: U2504.18 (B0)
IOP.D15: U2504.17 (B1)
IOP.D16: U2504.16 (B2)
IOP.D17: U2504.15 (B3)
IOP.D18: U2504.14 (B4)
IOP.D19: U2504.13 (B5)
IOP.D20: U2504.12 (B6)
IOP.D21: U2504.11 (B7)
IOP.IO_MAPEN~: U2503.19 (OE), U2504.19 (OE), U2509.1 (D0)
IOP.IO_MAP_WE~: U2501.21 (WE), U2502.21 (WE)
IOP.WR~: U2503.1 (DIR), U2504.1 (DIR), U2509.2 (D1)
IO_MAP.PERR: U2508.10 (PEV)
IO_MAP_OE~: U2501.20 (OE), U2502.20 (OE), U2509.3 (Q)
PD: U2501.18 (CS), U2502.18 (CS)
RAM.A14: U2505.18 (Y0)
RAM.A15: U2505.16 (Y1)
RAM.A16: U2505.14 (Y2)
RAM.A17: U2505.12 (Y3)
RAM.A18: U2505.9 (Y4)
RAM.A19: U2505.7 (Y5)
RAM.A20: U2505.5 (Y6)
RAM.A21: U2505.3 (Y7)
RAM.A22: U2506.18 (Y0)
RAM.A23: U2506.16 (Y1)
RAM.A24: U2506.14 (Y2)
RAM.A25: U2506.12 (Y3)
RAM.A26: U2506.9 (Y4)
RAM.A27: U2506.7 (Y5)
RAM.A28: U2506.5 (Y6)
RAM.A29: U2506.3 (Y7)
RAM.IO_GRANT~: U2505.1 (OE0), U2505.19 (OE1), U2506.1 (OE0), U2506.19 (OE1), U2507.19 (OE1)
RAM.WEN0: U2507.9 (Y4)
RAM.WEN1: U2507.7 (Y5)
RAM.WEN2: U2507.5 (Y6)
RAM.WEN3: U2507.3 (Y7)
