Datamuseum-DK/R1000.HwDoc/Schematics/IOC/pg_25.kicad_sch

## KiCad design Schematics/IOC/pg_25.kicad_sch (2023-01-10)

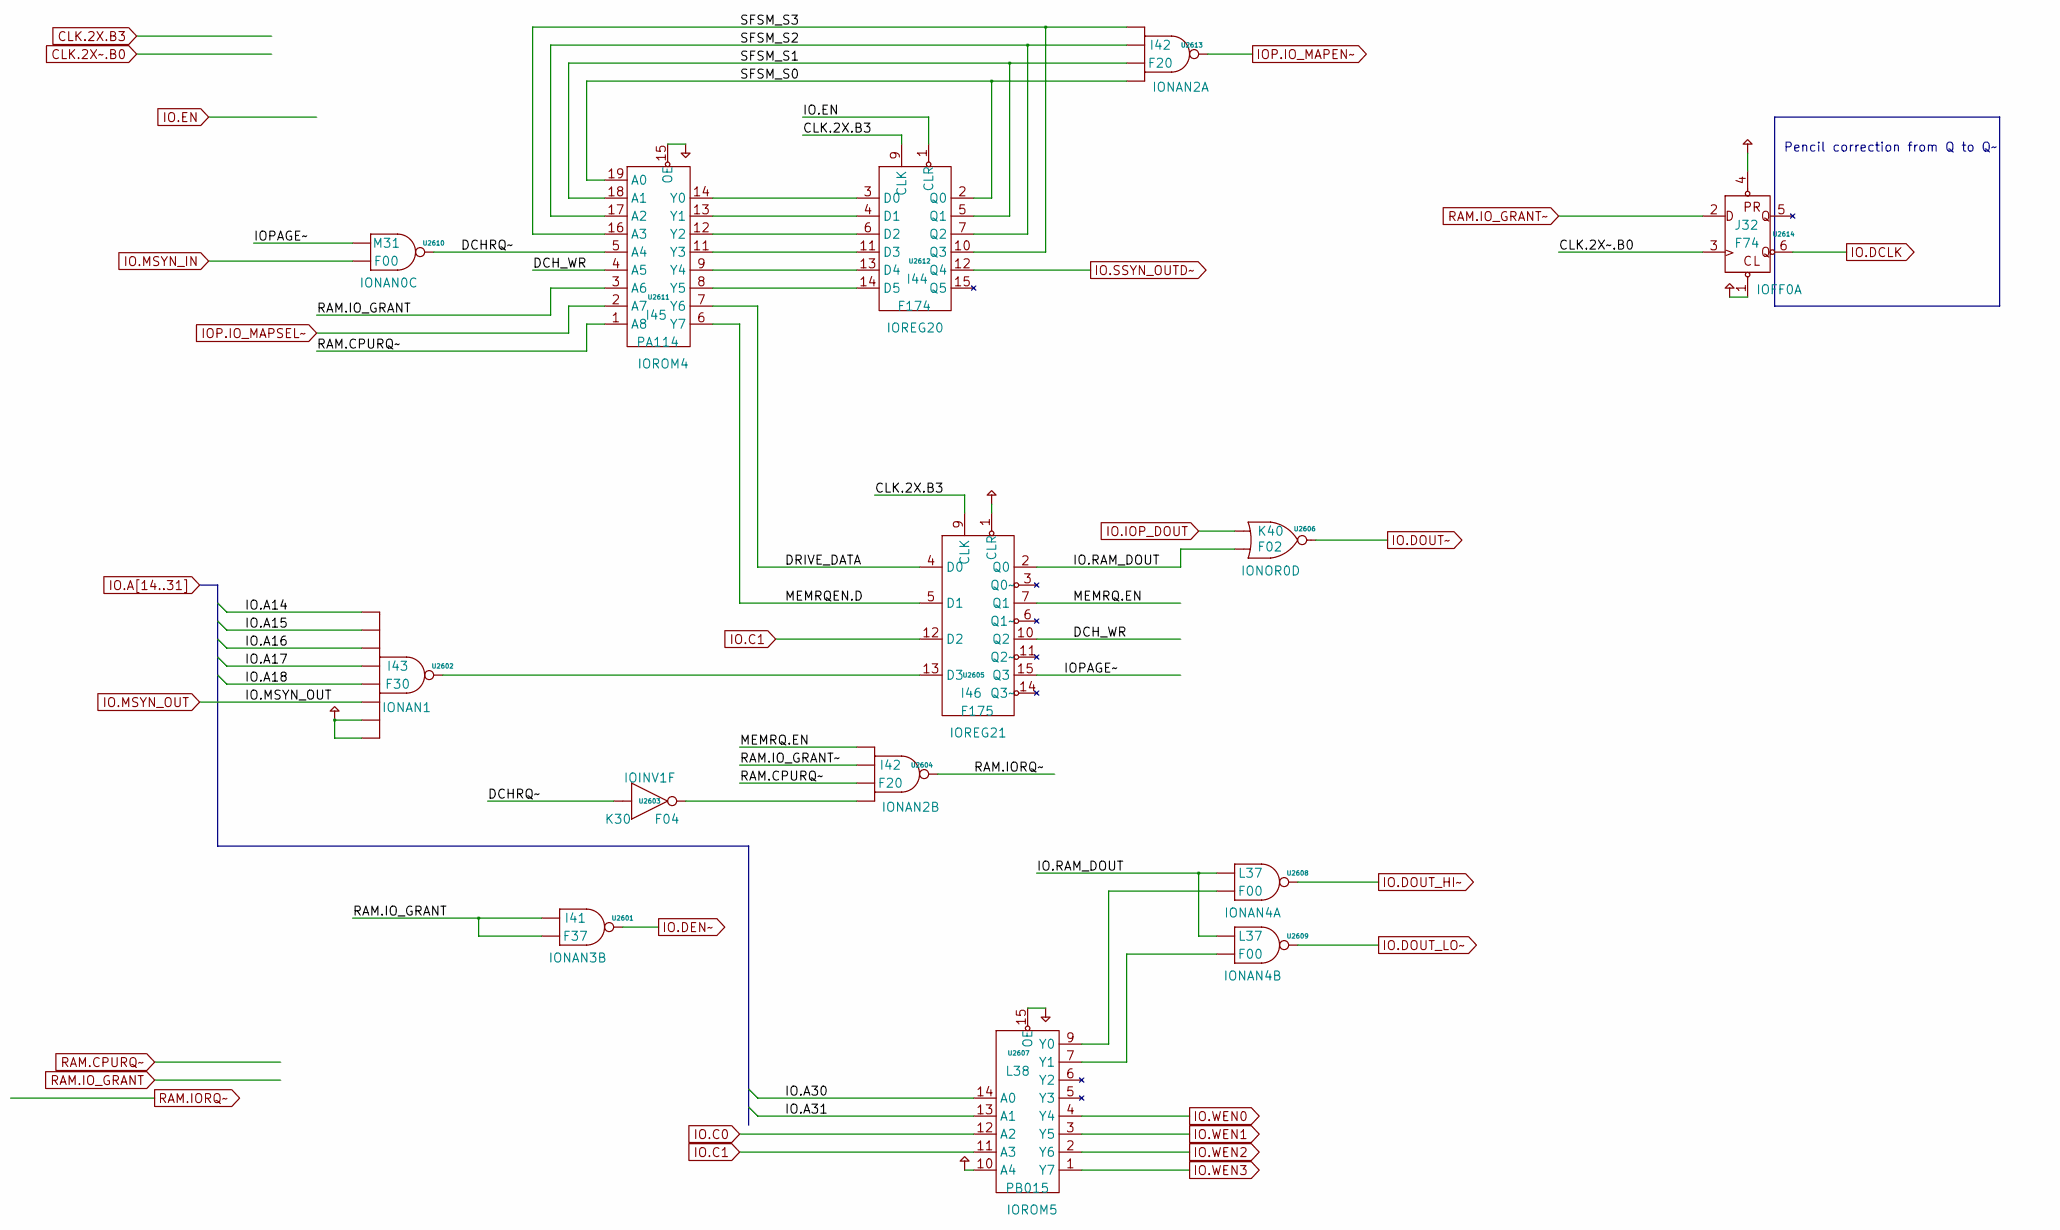
[picture p372: schematic pg_25.kicad_sch]

Parts:
U2601: F37
U2602: F30
U2603: F04
U2604, U2613: F20
U2605: F175
U2606: F02
U2607: PB015
U2608, U2609, U2610: F00
U2611: PA114
U2612: F174
U2614: F74

Connections:
CLK.2X.B3: U2605.9 (CLK), U2612.9 (CLK)
CLK.2X~.B0: U2614.3 (CLK)
DCHRQ~: U2603.1 (D0), U2610.3 (Q), U2611.5 (A4)
DCH_WR: U2605.10 (Q2), U2611.4 (A5)
DRIVE_DATA: U2605.4 (D0), U2611.7 (Y6)
IO.A14: U2602.11 (D0)
IO.A15: U2602.12 (D1)
IO.A16: U2602.1 (D2)
IO.A17: U2602.2 (D3)
IO.A18: U2602.3 (D4)
IO.A30: U2607.14 (A0)
IO.A31: U2607.13 (A1)
IO.C0: U2607.12 (A2)
IO.C1: U2605.12 (D2), U2607.11 (A3)
IO.DCLK: U2614.6 (Q_)
IO.DEN~: U2601.3 (Q)
IO.DOUT_HI~: U2608.3 (Q)
IO.DOUT_LO~: U2609.3 (Q)
IO.DOUT~: U2606.3 (Q)
IO.EN: U2612.1 (CLR)
IO.IOP_DOUT: U2606.1 (D0)
IO.MSYN_IN: U2610.2 (D1)
IO.MSYN_OUT: U2602.4 (D5)
IO.RAM_DOUT: U2605.2 (Q0), U2606.2 (D1), U2608.1 (D0), U2609.1 (D0)
IO.SSYN_OUTD~: U2612.12 (Q4)
IO.WEN0: U2607.4 (Y4)
IO.WEN1: U2607.3 (Y5)
IO.WEN2: U2607.2 (Y6)
IO.WEN3: U2607.1 (Y7)
IOP.IO_MAPEN~: U2613.6 (Q)
IOP.IO_MAPSEL~: U2611.2 (A7)
IOPAGE~: U2605.15 (Q3), U2610.1 (D0)
MEMRQ.EN: U2604.1 (D0), U2605.7 (Q1)
MEMRQEN.D: U2605.5 (D1), U2611.6 (Y7)
unnamed: U2602.8 (Q), U2605.13 (D3)
unnamed: U2603.2 (Q), U2604.5 (D3)
unnamed: U2607.7 (Y1), U2609.2 (D1)
unnamed: U2607.9 (Y0), U2608.2 (D1)
unnamed: U2611.8 (Y5), U2612.14 (D5)
unnamed: U2611.9 (Y4), U2612.13 (D4)
unnamed: U2611.11 (Y3), U2612.11 (D3)
unnamed: U2611.12 (Y2), U2612.6 (D2)
unnamed: U2611.13 (Y1), U2612.4 (D1)
unnamed: U2611.14 (Y0), U2612.3 (D0)
PD: U2607.15 (OE), U2611.15 (OE)
PU: U2602.5 (D6), U2602.6 (D7), U2605.1 (CLR), U2607.10 (A4), U2614.1 (CL_), U2614.4 (PR_)
RAM.CPURQ~: U2604.4 (D2), U2611.1 (A8)
RAM.IORQ~: U2604.6 (Q)
RAM.IO_GRANT: U2601.1 (D0), U2601.2 (D1), U2611.3 (A6)
RAM.IO_GRANT~: U2604.2 (D1), U2614.2 (D)
SFSM_S0: U2611.19 (A0), U2612.2 (Q0), U2613.5 (D3)
SFSM_S1: U2611.18 (A1), U2612.5 (Q1), U2613.4 (D2)
SFSM_S2: U2611.17 (A2), U2612.7 (Q2), U2613.2 (D1)
SFSM_S3: U2611.16 (A3), U2612.10 (Q3), U2613.1 (D0)

Notes on the sheet:
Pencil correction from Q to Q~
