Datamuseum-DK/R1000.HwDoc/Schematics/IOC/pg_26.kicad_sch

## KiCad design Schematics/IOC/pg_26.kicad_sch (2023-01-10)

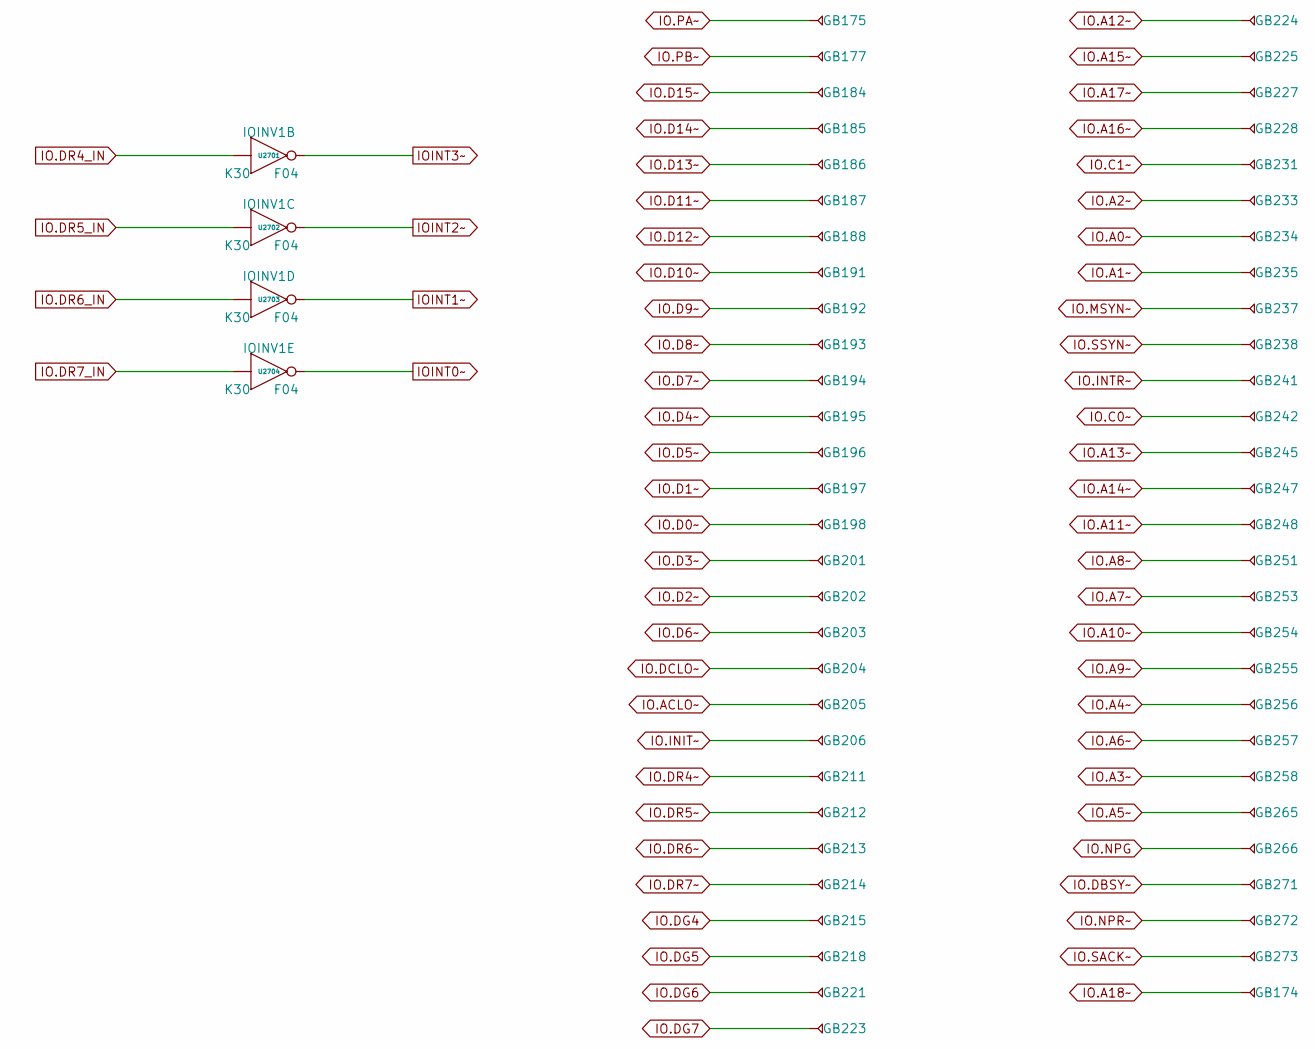
[picture p373: schematic pg_26.kicad_sch]

Parts:
GB174, GB175, GB177, GB184, GB185, GB186, GB187, GB188, GB191, GB192, GB193, GB194, GB195, GB196, GB197, GB198, GB201, GB202, GB203, GB204, GB205, GB206, GB211, GB212, GB213, GB214, GB215, GB218, GB221, GB223, GB224, GB225, GB227, GB228, GB231, GB233, GB234, GB235, GB237, GB238, GB241, GB242, GB245, GB247, GB248, GB251, GB253, GB254, GB255, GB256, GB257, GB258, GB265, GB266, GB271, GB272, GB273: GB
U2701, U2702, U2703, U2704: F04

Connections:
IO.A0~: GB234.1
IO.A1~: GB235.1
IO.A2~: GB233.1
IO.A3~: GB258.1
IO.A4~: GB256.1
IO.A5~: GB265.1
IO.A6~: GB257.1
IO.A7~: GB253.1
IO.A8~: GB251.1
IO.A9~: GB255.1
IO.A10~: GB254.1
IO.A11~: GB248.1
IO.A12~: GB224.1
IO.A13~: GB245.1
IO.A14~: GB247.1
IO.A15~: GB225.1
IO.A16~: GB228.1
IO.A17~: GB227.1
IO.A18~: GB174.1
IO.ACLO~: GB205.1
IO.C0~: GB242.1
IO.C1~: GB231.1
IO.D0~: GB198.1
IO.D1~: GB197.1
IO.D2~: GB202.1
IO.D3~: GB201.1
IO.D4~: GB195.1
IO.D5~: GB196.1
IO.D6~: GB203.1
IO.D7~: GB194.1
IO.D8~: GB193.1
IO.D9~: GB192.1
IO.D10~: GB191.1
IO.D11~: GB187.1
IO.D12~: GB188.1
IO.D13~: GB186.1
IO.D14~: GB185.1
IO.D15~: GB184.1
IO.DBSY~: GB271.1
IO.DCLO~: GB204.1
IO.DG4: GB215.1
IO.DG5: GB218.1
IO.DG6: GB221.1
IO.DG7: GB223.1
IO.DR4_IN: U2701.1 (D0)
IO.DR4~: GB211.1
IO.DR5_IN: U2702.1 (D0)
IO.DR5~: GB212.1
IO.DR6_IN: U2703.1 (D0)
IO.DR6~: GB213.1
IO.DR7_IN: U2704.1 (D0)
IO.DR7~: GB214.1
IO.INIT~: GB206.1
IO.INTR~: GB241.1
IO.MSYN~: GB237.1
IO.NPG: GB266.1
IO.NPR~: GB272.1
IO.PA~: GB175.1
IO.PB~: GB177.1
IO.SACK~: GB273.1
IO.SSYN~: GB238.1
IOINT0~: U2704.2 (Q)
IOINT1~: U2703.2 (Q)
IOINT2~: U2702.2 (Q)
IOINT3~: U2701.2 (Q)
