Datamuseum-DK/R1000.HwDoc/Schematics/IOC/pg_27.kicad_sch

## KiCad design Schematics/IOC/pg_27.kicad_sch (2023-01-10)

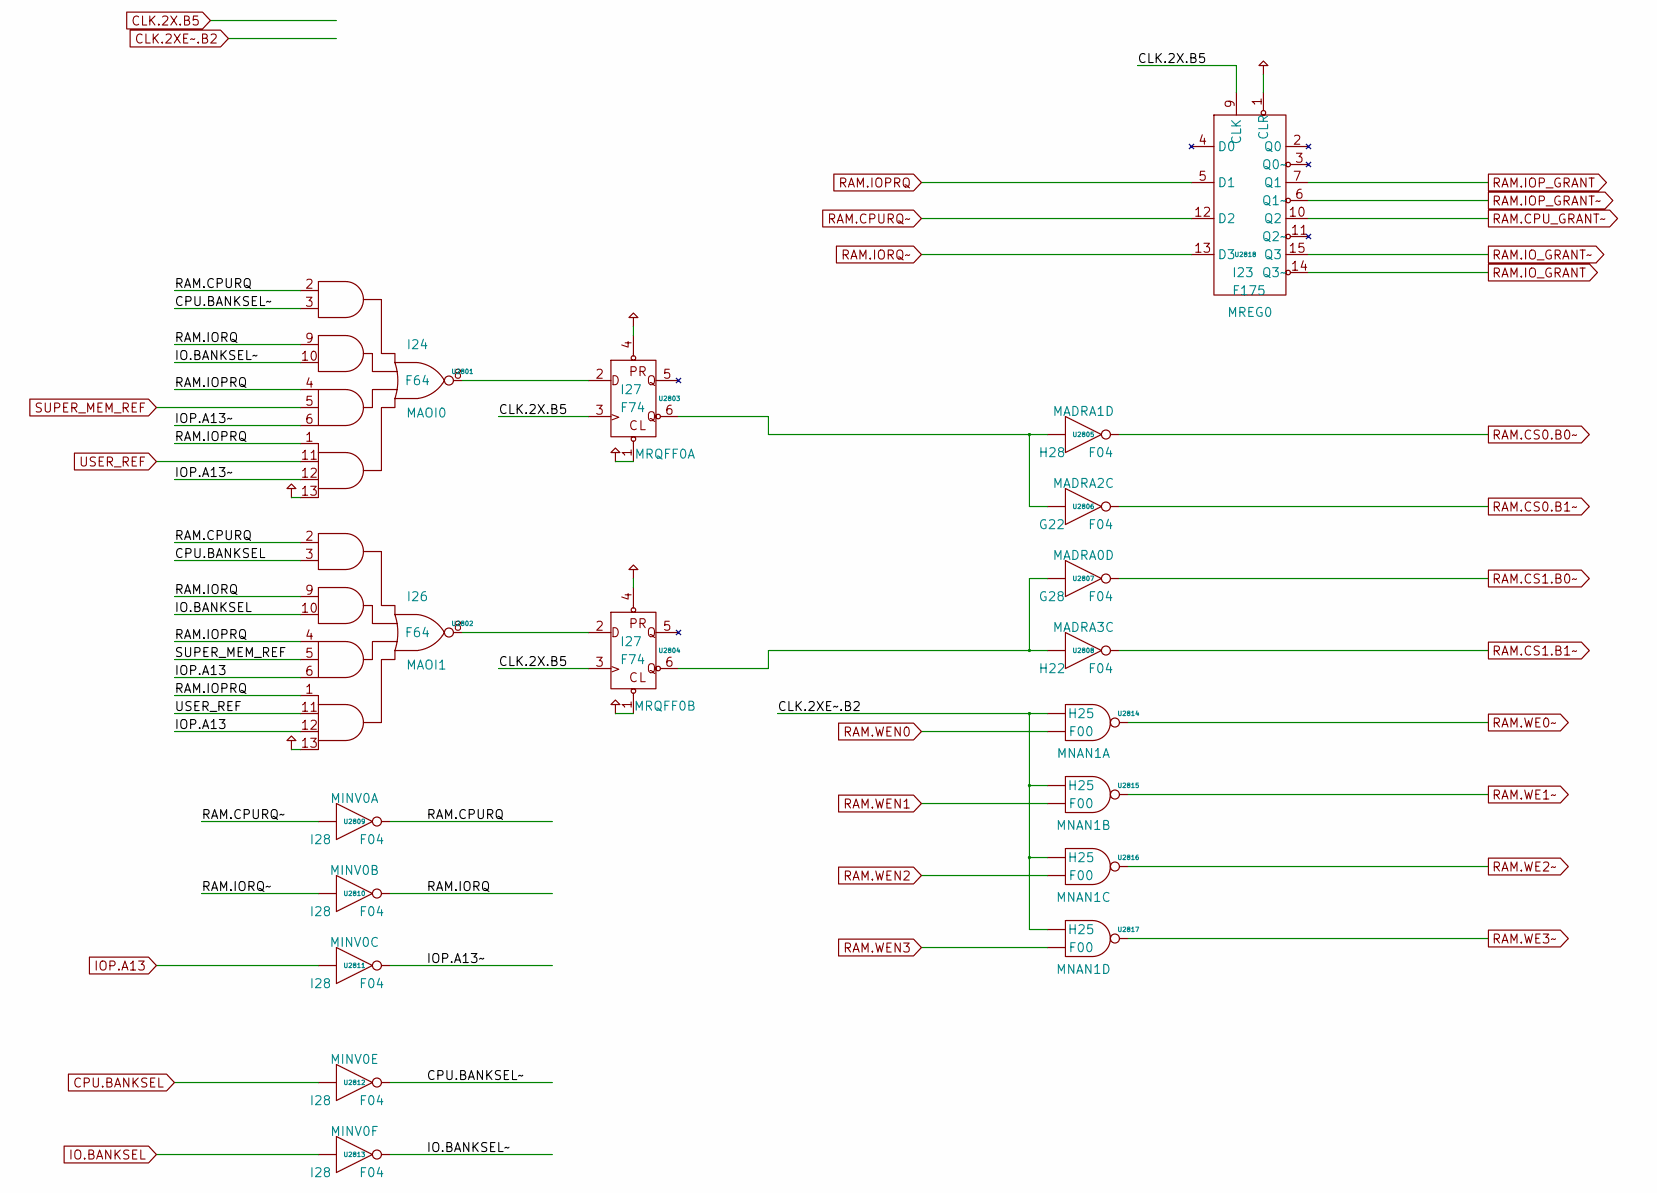
[picture p374: schematic pg_27.kicad_sch]

Parts:
U2801, U2802: F64
U2803, U2804: F74
U2805, U2806, U2807, U2808, U2809, U2810, U2811, U2812, U2813: F04
U2814, U2815, U2816, U2817: F00
U2818: F175

Connections:
CLK.2X.B5: U2803.3 (CLK), U2804.3 (CLK), U2818.9 (CLK)
CLK.2XE~.B2: U2814.1 (D0), U2815.1 (D0), U2816.1 (D0), U2817.1 (D0)
CPU.BANKSEL: U2802.3 (A1), U2812.1 (D0)
CPU.BANKSEL~: U2801.3 (A1), U2812.2 (Q)
IO.BANKSEL: U2802.10 (B1), U2813.1 (D0)
IO.BANKSEL~: U2801.10 (B1), U2813.2 (Q)
IOP.A13: U2802.6 (C2), U2802.12 (D2), U2811.1 (D0)
IOP.A13~: U2801.6 (C2), U2801.12 (D2), U2811.2 (Q)
unnamed: U2801.8 (Q), U2803.2 (D)
unnamed: U2802.8 (Q), U2804.2 (D)
unnamed: U2803.6 (Q_), U2805.1 (D0), U2806.1 (D0)
unnamed: U2804.6 (Q_), U2807.1 (D0), U2808.1 (D0)
PU: U2801.13 (D3), U2802.13 (D3), U2803.1 (CL_), U2803.4 (PR_), U2804.1 (CL_), U2804.4 (PR_), U2818.1 (CLR)
RAM.CPURQ: U2801.2 (A0), U2802.2 (A0), U2809.2 (Q)
RAM.CPURQ~: U2809.1 (D0), U2818.12 (D2)
RAM.CPU_GRANT~: U2818.10 (Q2)
RAM.CS0.B0~: U2805.2 (Q)
RAM.CS0.B1~: U2806.2 (Q)
RAM.CS1.B0~: U2807.2 (Q)
RAM.CS1.B1~: U2808.2 (Q)
RAM.IOPRQ: U2801.1 (D0), U2801.4 (C0), U2802.1 (D0), U2802.4 (C0), U2818.5 (D1)
RAM.IOP_GRANT: U2818.7 (Q1)
RAM.IOP_GRANT~: U2818.6 (Q1~)
RAM.IORQ: U2801.9 (B0), U2802.9 (B0), U2810.2 (Q)
RAM.IORQ~: U2810.1 (D0), U2818.13 (D3)
RAM.IO_GRANT: U2818.14 (Q3~)
RAM.IO_GRANT~: U2818.15 (Q3)
RAM.WE0~: U2814.3 (Q)
RAM.WE1~: U2815.3 (Q)
RAM.WE2~: U2816.3 (Q)
RAM.WE3~: U2817.3 (Q)
RAM.WEN0: U2814.2 (D1)
RAM.WEN1: U2815.2 (D1)
RAM.WEN2: U2816.2 (D1)
RAM.WEN3: U2817.2 (D1)
SUPER_MEM_REF: U2801.5 (C1), U2802.5 (C1)
USER_REF: U2801.11 (D1), U2802.11 (D1)
