Datamuseum-DK/R1000.HwDoc/Schematics/IOC/pg_28.kicad_sch

## KiCad design Schematics/IOC/pg_28.kicad_sch (2023-01-10)

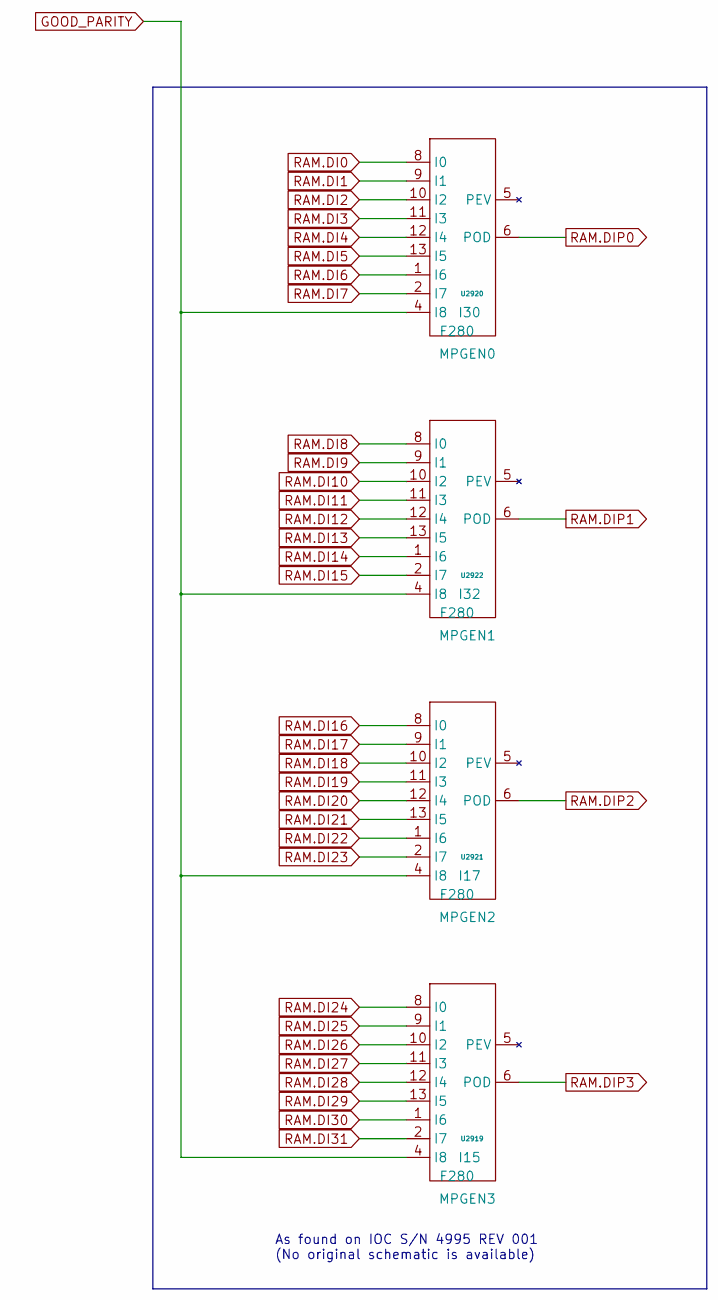
[picture p375: schematic pg_28.kicad_sch]

Parts:
U2919, U2920, U2921, U2922: F280

Connections:
GOOD_PARITY: U2919.4 (I8), U2920.4 (I8), U2921.4 (I8), U2922.4 (I8)
RAM.DI0: U2920.8 (I0)
RAM.DI1: U2920.9 (I1)
RAM.DI2: U2920.10 (I2)
RAM.DI3: U2920.11 (I3)
RAM.DI4: U2920.12 (I4)
RAM.DI5: U2920.13 (I5)
RAM.DI6: U2920.1 (I6)
RAM.DI7: U2920.2 (I7)
RAM.DI8: U2922.8 (I0)
RAM.DI9: U2922.9 (I1)
RAM.DI10: U2922.10 (I2)
RAM.DI11: U2922.11 (I3)
RAM.DI12: U2922.12 (I4)
RAM.DI13: U2922.13 (I5)
RAM.DI14: U2922.1 (I6)
RAM.DI15: U2922.2 (I7)
RAM.DI16: U2921.8 (I0)
RAM.DI17: U2921.9 (I1)
RAM.DI18: U2921.10 (I2)
RAM.DI19: U2921.11 (I3)
RAM.DI20: U2921.12 (I4)
RAM.DI21: U2921.13 (I5)
RAM.DI22: U2921.1 (I6)
RAM.DI23: U2921.2 (I7)
RAM.DI24: U2919.8 (I0)
RAM.DI25: U2919.9 (I1)
RAM.DI26: U2919.10 (I2)
RAM.DI27: U2919.11 (I3)
RAM.DI28: U2919.12 (I4)
RAM.DI29: U2919.13 (I5)
RAM.DI30: U2919.1 (I6)
RAM.DI31: U2919.2 (I7)
RAM.DIP0: U2920.6 (POD)
RAM.DIP1: U2922.6 (POD)
RAM.DIP2: U2921.6 (POD)
RAM.DIP3: U2919.6 (POD)

Notes on the sheet:
As found on IOC S/N 4995 REV 001 (No original schematic is available)
