Datamuseum-DK/R1000.HwDoc/Schematics/IOC/pg_29.kicad_sch

## KiCad design Schematics/IOC/pg_29.kicad_sch (2023-01-10)

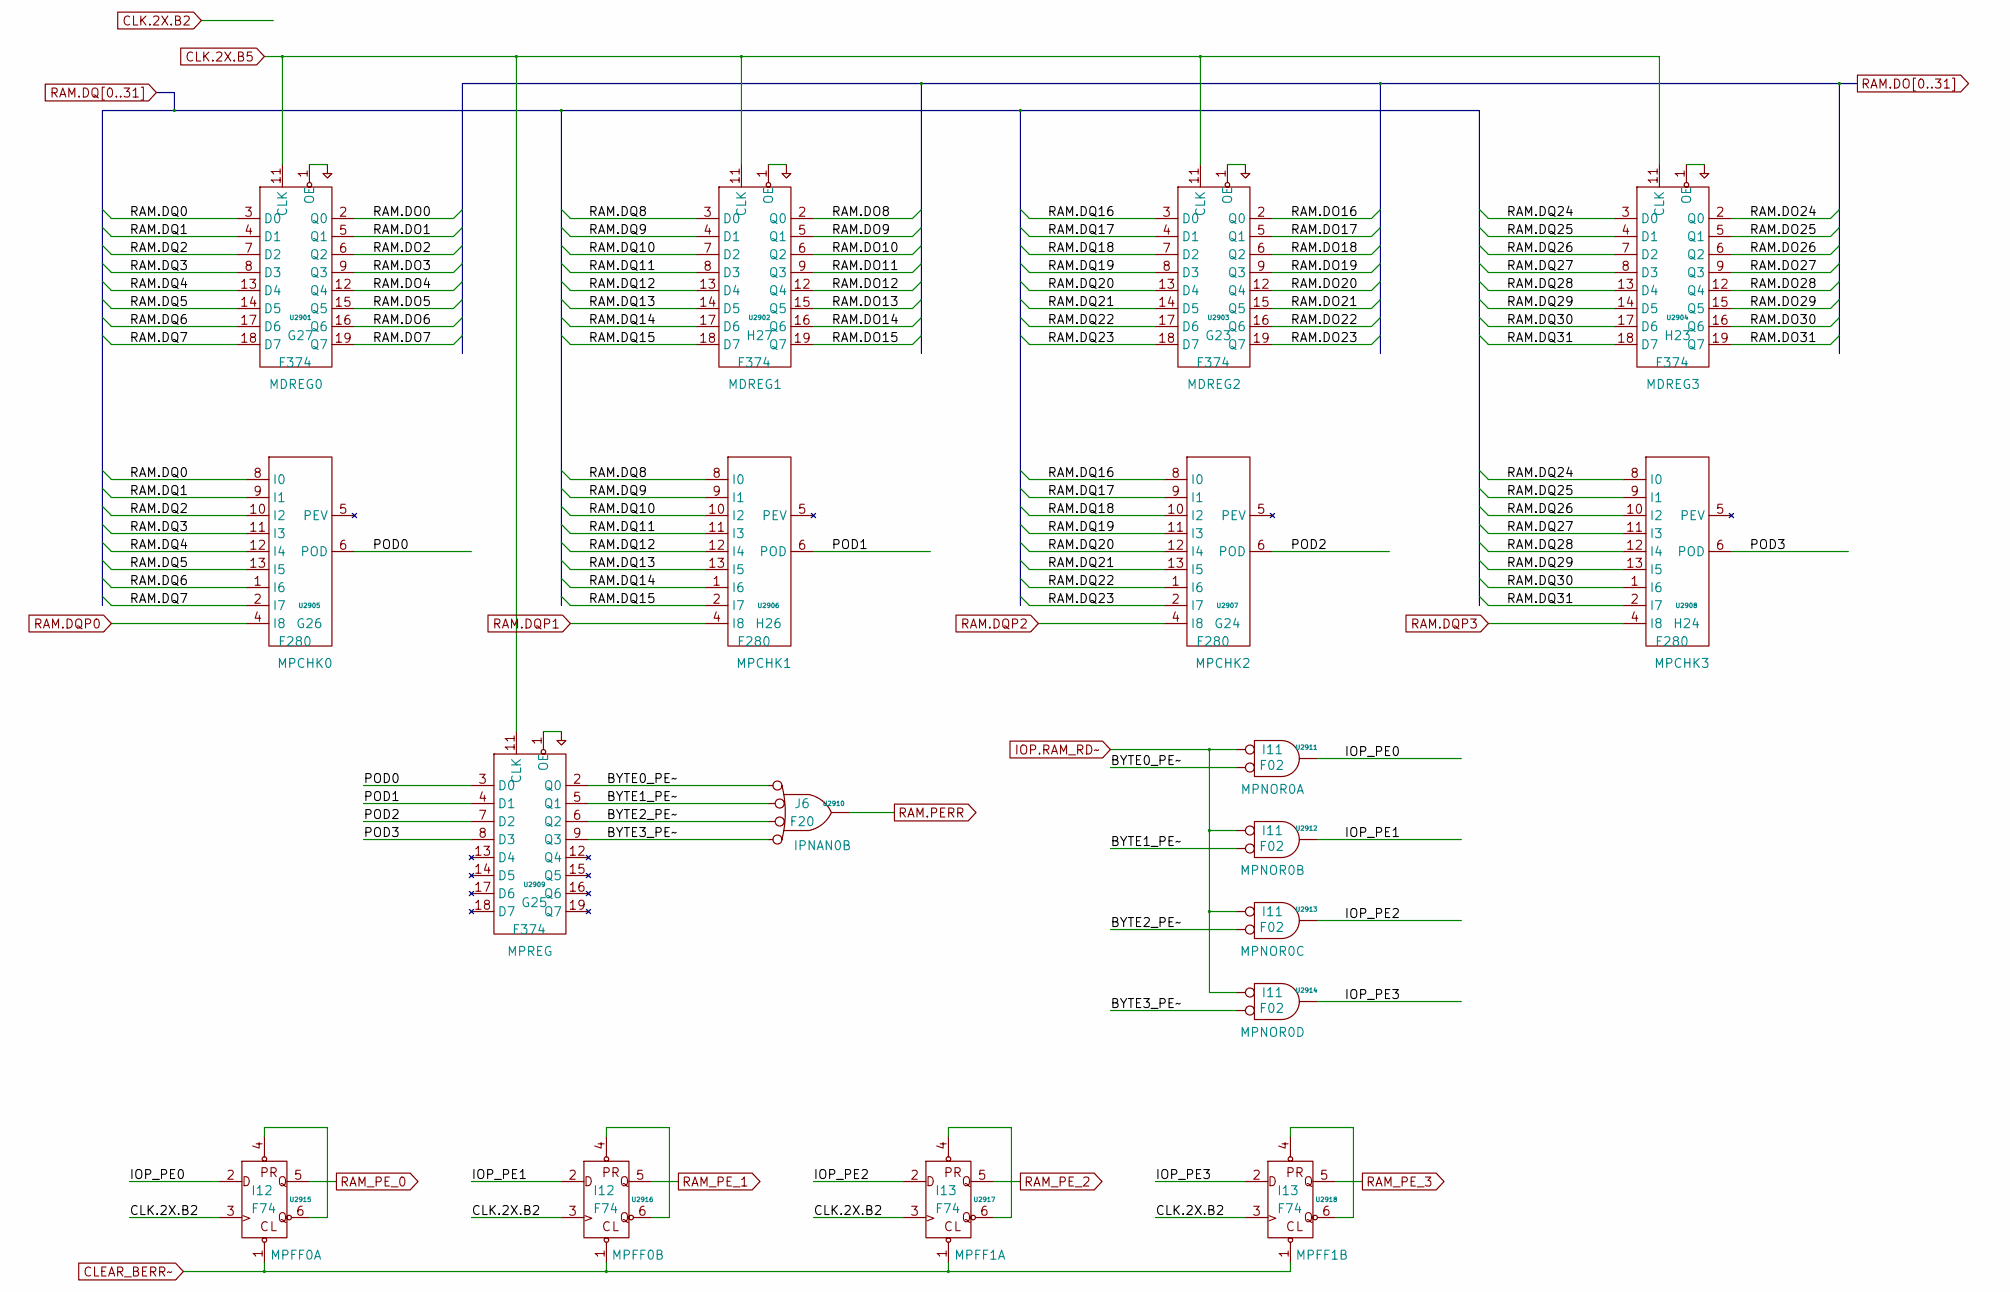
[picture p376: schematic pg_29.kicad_sch]

Parts:
U2901, U2902, U2903, U2904, U2909: F374
U2905, U2906, U2907, U2908: F280
U2910: F20
U2911, U2912, U2913, U2914: F02
U2915, U2916, U2917, U2918: F74

Connections:
BYTE0_PE~: U2909.2 (Q0), U2910.1 (D0), U2911.2 (D1)
BYTE1_PE~: U2909.5 (Q1), U2910.2 (D1), U2912.2 (D1)
BYTE2_PE~: U2909.6 (Q2), U2910.4 (D2), U2913.2 (D1)
BYTE3_PE~: U2909.9 (Q3), U2910.5 (D3), U2914.2 (D1)
CLEAR_BERR~: U2915.1 (CL_), U2916.1 (CL_), U2917.1 (CL_), U2918.1 (CL_)
CLK.2X.B2: U2915.3 (CLK), U2916.3 (CLK), U2917.3 (CLK), U2918.3 (CLK)
CLK.2X.B5: U2901.11 (CLK), U2902.11 (CLK), U2903.11 (CLK), U2904.11 (CLK), U2909.11 (CLK)
IOP.RAM_RD~: U2911.1 (D0), U2912.1 (D0), U2913.1 (D0), U2914.1 (D0)
IOP_PE0: U2911.3 (Q), U2915.2 (D)
IOP_PE1: U2912.3 (Q), U2916.2 (D)
IOP_PE2: U2913.3 (Q), U2917.2 (D)
IOP_PE3: U2914.3 (Q), U2918.2 (D)
unnamed: U2915.4 (PR_), U2915.6 (Q_)
unnamed: U2916.4 (PR_), U2916.6 (Q_)
unnamed: U2917.4 (PR_), U2917.6 (Q_)
unnamed: U2918.4 (PR_), U2918.6 (Q_)
PD: U2901.1 (OE), U2902.1 (OE), U2903.1 (OE), U2904.1 (OE), U2909.1 (OE)
POD0: U2905.6 (POD), U2909.3 (D0)
POD1: U2906.6 (POD), U2909.4 (D1)
POD2: U2907.6 (POD), U2909.7 (D2)
POD3: U2908.6 (POD), U2909.8 (D3)
RAM.DO0: U2901.2 (Q0)
RAM.DO1: U2901.5 (Q1)
RAM.DO2: U2901.6 (Q2)
RAM.DO3: U2901.9 (Q3)
RAM.DO4: U2901.12 (Q4)
RAM.DO5: U2901.15 (Q5)
RAM.DO6: U2901.16 (Q6)
RAM.DO7: U2901.19 (Q7)
RAM.DO8: U2902.2 (Q0)
RAM.DO9: U2902.5 (Q1)
RAM.DO10: U2902.6 (Q2)
RAM.DO11: U2902.9 (Q3)
RAM.DO12: U2902.12 (Q4)
RAM.DO13: U2902.15 (Q5)
RAM.DO14: U2902.16 (Q6)
RAM.DO15: U2902.19 (Q7)
RAM.DO16: U2903.2 (Q0)
RAM.DO17: U2903.5 (Q1)
RAM.DO18: U2903.6 (Q2)
RAM.DO19: U2903.9 (Q3)
RAM.DO20: U2903.12 (Q4)
RAM.DO21: U2903.15 (Q5)
RAM.DO22: U2903.16 (Q6)
RAM.DO23: U2903.19 (Q7)
RAM.DO24: U2904.2 (Q0)
RAM.DO25: U2904.5 (Q1)
RAM.DO26: U2904.6 (Q2)
RAM.DO27: U2904.9 (Q3)
RAM.DO28: U2904.12 (Q4)
RAM.DO29: U2904.15 (Q5)
RAM.DO30: U2904.16 (Q6)
RAM.DO31: U2904.19 (Q7)
RAM.DQ0: U2901.3 (D0), U2905.8 (I0)
RAM.DQ1: U2901.4 (D1), U2905.9 (I1)
RAM.DQ2: U2901.7 (D2), U2905.10 (I2)
RAM.DQ3: U2901.8 (D3), U2905.11 (I3)
RAM.DQ4: U2901.13 (D4), U2905.12 (I4)
RAM.DQ5: U2901.14 (D5), U2905.13 (I5)
RAM.DQ6: U2901.17 (D6), U2905.1 (I6)
RAM.DQ7: U2901.18 (D7), U2905.2 (I7)
RAM.DQ8: U2902.3 (D0), U2906.8 (I0)
RAM.DQ9: U2902.4 (D1), U2906.9 (I1)
RAM.DQ10: U2902.7 (D2), U2906.10 (I2)
RAM.DQ11: U2902.8 (D3), U2906.11 (I3)
RAM.DQ12: U2902.13 (D4), U2906.12 (I4)
RAM.DQ13: U2902.14 (D5), U2906.13 (I5)
RAM.DQ14: U2902.17 (D6), U2906.1 (I6)
RAM.DQ15: U2902.18 (D7), U2906.2 (I7)
RAM.DQ16: U2903.3 (D0), U2907.8 (I0)
RAM.DQ17: U2903.4 (D1), U2907.9 (I1)
RAM.DQ18: U2903.7 (D2), U2907.10 (I2)
RAM.DQ19: U2903.8 (D3), U2907.11 (I3)
RAM.DQ20: U2903.13 (D4), U2907.12 (I4)
RAM.DQ21: U2903.14 (D5), U2907.13 (I5)
RAM.DQ22: U2903.17 (D6), U2907.1 (I6)
RAM.DQ23: U2903.18 (D7), U2907.2 (I7)
RAM.DQ24: U2904.3 (D0), U2908.8 (I0)
RAM.DQ25: U2904.4 (D1), U2908.9 (I1)
RAM.DQ26: U2904.7 (D2), U2908.10 (I2)
RAM.DQ27: U2904.8 (D3), U2908.11 (I3)
RAM.DQ28: U2904.13 (D4), U2908.12 (I4)
RAM.DQ29: U2904.14 (D5), U2908.13 (I5)
RAM.DQ30: U2904.17 (D6), U2908.1 (I6)
RAM.DQ31: U2904.18 (D7), U2908.2 (I7)
RAM.DQP0: U2905.4 (I8)
RAM.DQP1: U2906.4 (I8)
RAM.DQP2: U2907.4 (I8)
RAM.DQP3: U2908.4 (I8)
RAM.PERR: U2910.6 (Q)
RAM_PE_0: U2915.5 (Q)
RAM_PE_1: U2916.5 (Q)
RAM_PE_2: U2917.5 (Q)
RAM_PE_3: U2918.5 (Q)
