Datamuseum-DK/R1000.HwDoc/Schematics/IOC/pg_30.kicad_sch

## KiCad design Schematics/IOC/pg_30.kicad_sch (2023-01-10)

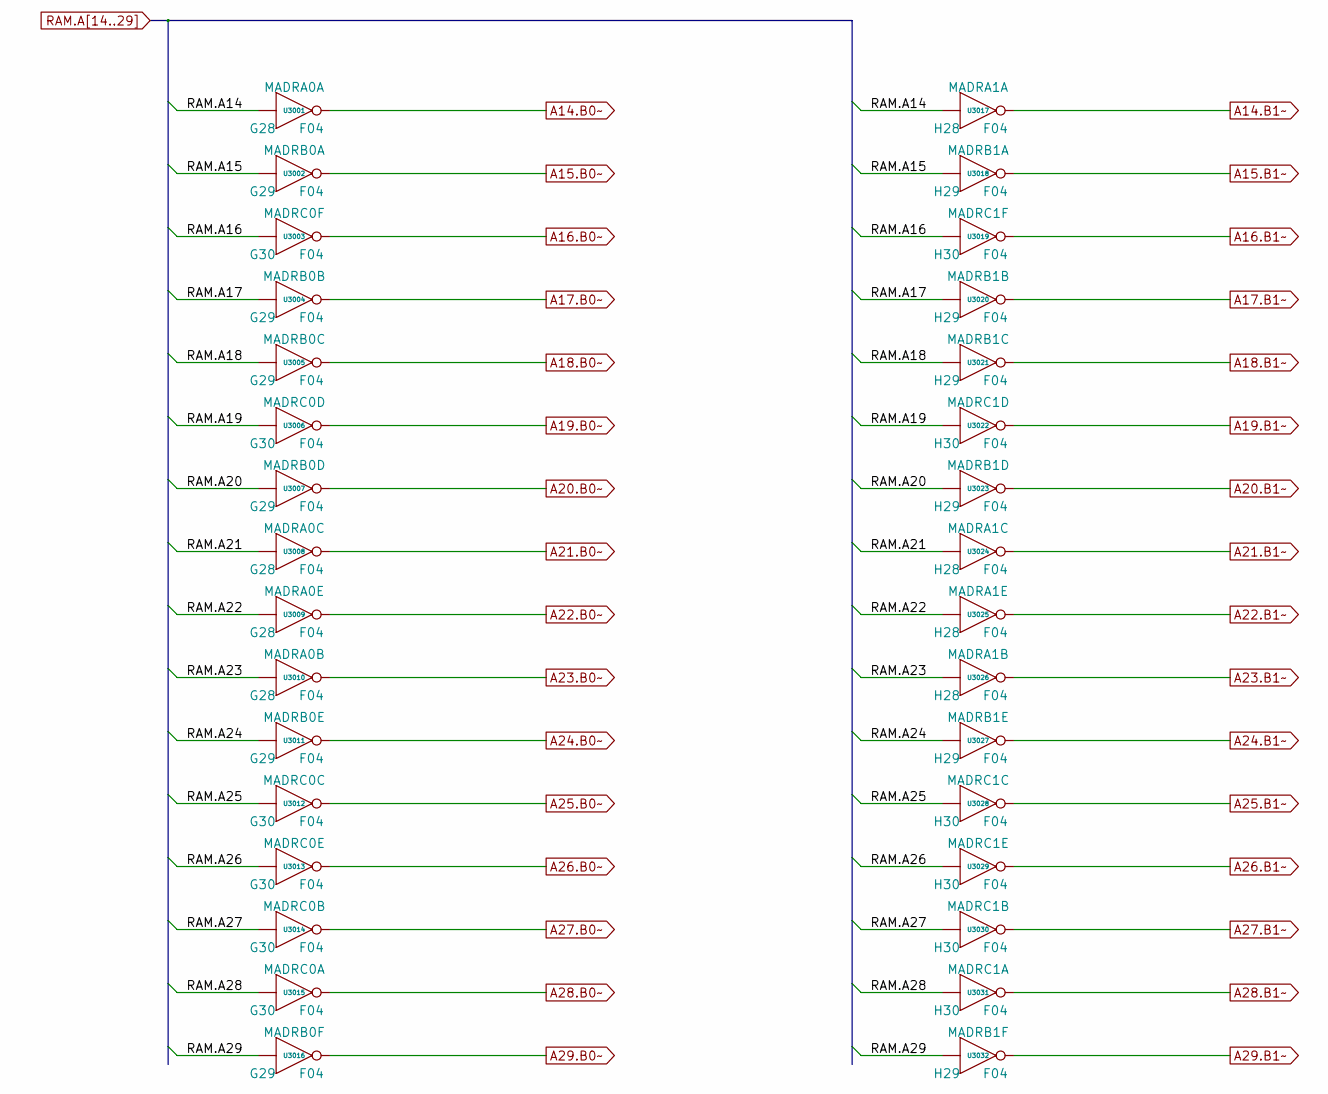
[picture p377: schematic pg_30.kicad_sch]

Parts:
U3001, U3002, U3003, U3004, U3005, U3006, U3007, U3008, U3009, U3010, U3011, U3012, U3013, U3014, U3015, U3016, U3017, U3018, U3019, U3020, U3021, U3022, U3023, U3024, U3025, U3026, U3027, U3028, U3029, U3030, U3031, U3032: F04

Connections:
A14.B0~: U3001.2 (Q)
A14.B1~: U3017.2 (Q)
A15.B0~: U3002.2 (Q)
A15.B1~: U3018.2 (Q)
A16.B0~: U3003.2 (Q)
A16.B1~: U3019.2 (Q)
A17.B0~: U3004.2 (Q)
A17.B1~: U3020.2 (Q)
A18.B0~: U3005.2 (Q)
A18.B1~: U3021.2 (Q)
A19.B0~: U3006.2 (Q)
A19.B1~: U3022.2 (Q)
A20.B0~: U3007.2 (Q)
A20.B1~: U3023.2 (Q)
A21.B0~: U3008.2 (Q)
A21.B1~: U3024.2 (Q)
A22.B0~: U3009.2 (Q)
A22.B1~: U3025.2 (Q)
A23.B0~: U3010.2 (Q)
A23.B1~: U3026.2 (Q)
A24.B0~: U3011.2 (Q)
A24.B1~: U3027.2 (Q)
A25.B0~: U3012.2 (Q)
A25.B1~: U3028.2 (Q)
A26.B0~: U3013.2 (Q)
A26.B1~: U3029.2 (Q)
A27.B0~: U3014.2 (Q)
A27.B1~: U3030.2 (Q)
A28.B0~: U3015.2 (Q)
A28.B1~: U3031.2 (Q)
A29.B0~: U3016.2 (Q)
A29.B1~: U3032.2 (Q)
RAM.A14: U3001.1 (D0), U3017.1 (D0)
RAM.A15: U3002.1 (D0), U3018.1 (D0)
RAM.A16: U3003.1 (D0), U3019.1 (D0)
RAM.A17: U3004.1 (D0), U3020.1 (D0)
RAM.A18: U3005.1 (D0), U3021.1 (D0)
RAM.A19: U3006.1 (D0), U3022.1 (D0)
RAM.A20: U3007.1 (D0), U3023.1 (D0)
RAM.A21: U3008.1 (D0), U3024.1 (D0)
RAM.A22: U3009.1 (D0), U3025.1 (D0)
RAM.A23: U3010.1 (D0), U3026.1 (D0)
RAM.A24: U3011.1 (D0), U3027.1 (D0)
RAM.A25: U3012.1 (D0), U3028.1 (D0)
RAM.A26: U3013.1 (D0), U3029.1 (D0)
RAM.A27: U3014.1 (D0), U3030.1 (D0)
RAM.A28: U3015.1 (D0), U3031.1 (D0)
RAM.A29: U3016.1 (D0), U3032.1 (D0)
