Datamuseum-DK/R1000.HwDoc/Schematics/IOC/pg_31.kicad_sch

## KiCad design Schematics/IOC/pg_31.kicad_sch (2023-01-10)

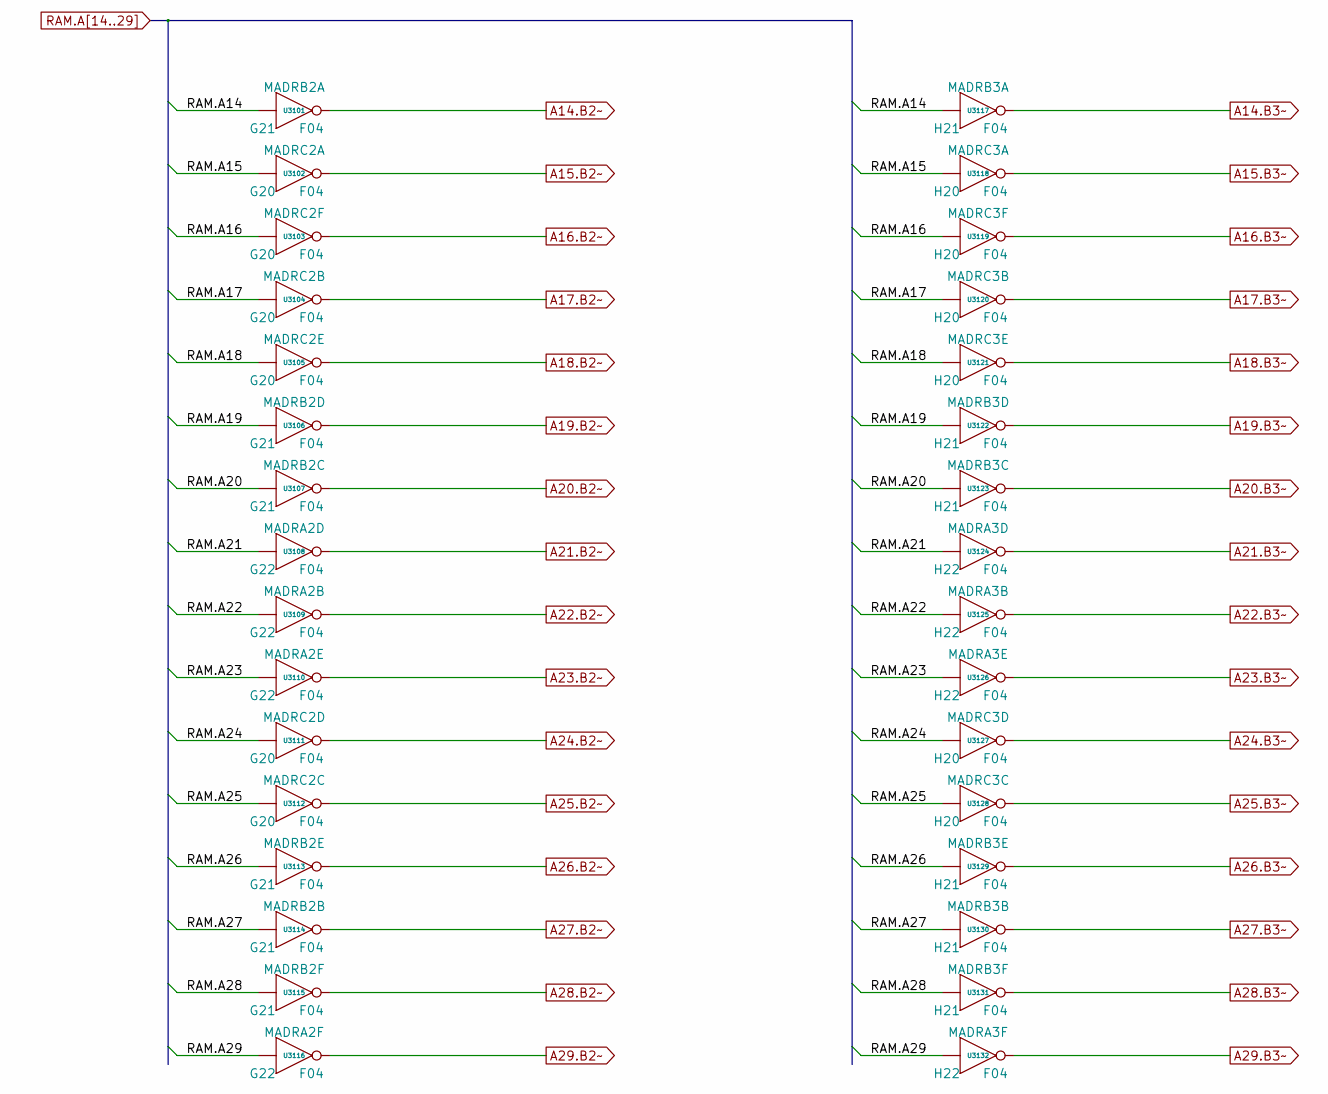
[picture p378: schematic pg_31.kicad_sch]

Parts:
U3101, U3102, U3103, U3104, U3105, U3106, U3107, U3108, U3109, U3110, U3111, U3112, U3113, U3114, U3115, U3116, U3117, U3118, U3119, U3120, U3121, U3122, U3123, U3124, U3125, U3126, U3127, U3128, U3129, U3130, U3131, U3132: F04

Connections:
A14.B2~: U3101.2 (Q)
A14.B3~: U3117.2 (Q)
A15.B2~: U3102.2 (Q)
A15.B3~: U3118.2 (Q)
A16.B2~: U3103.2 (Q)
A16.B3~: U3119.2 (Q)
A17.B2~: U3104.2 (Q)
A17.B3~: U3120.2 (Q)
A18.B2~: U3105.2 (Q)
A18.B3~: U3121.2 (Q)
A19.B2~: U3106.2 (Q)
A19.B3~: U3122.2 (Q)
A20.B2~: U3107.2 (Q)
A20.B3~: U3123.2 (Q)
A21.B2~: U3108.2 (Q)
A21.B3~: U3124.2 (Q)
A22.B2~: U3109.2 (Q)
A22.B3~: U3125.2 (Q)
A23.B2~: U3110.2 (Q)
A23.B3~: U3126.2 (Q)
A24.B2~: U3111.2 (Q)
A24.B3~: U3127.2 (Q)
A25.B2~: U3112.2 (Q)
A25.B3~: U3128.2 (Q)
A26.B2~: U3113.2 (Q)
A26.B3~: U3129.2 (Q)
A27.B2~: U3114.2 (Q)
A27.B3~: U3130.2 (Q)
A28.B2~: U3115.2 (Q)
A28.B3~: U3131.2 (Q)
A29.B2~: U3116.2 (Q)
A29.B3~: U3132.2 (Q)
RAM.A14: U3101.1 (D0), U3117.1 (D0)
RAM.A15: U3102.1 (D0), U3118.1 (D0)
RAM.A16: U3103.1 (D0), U3119.1 (D0)
RAM.A17: U3104.1 (D0), U3120.1 (D0)
RAM.A18: U3105.1 (D0), U3121.1 (D0)
RAM.A19: U3106.1 (D0), U3122.1 (D0)
RAM.A20: U3107.1 (D0), U3123.1 (D0)
RAM.A21: U3108.1 (D0), U3124.1 (D0)
RAM.A22: U3109.1 (D0), U3125.1 (D0)
RAM.A23: U3110.1 (D0), U3126.1 (D0)
RAM.A24: U3111.1 (D0), U3127.1 (D0)
RAM.A25: U3112.1 (D0), U3128.1 (D0)
RAM.A26: U3113.1 (D0), U3129.1 (D0)
RAM.A27: U3114.1 (D0), U3130.1 (D0)
RAM.A28: U3115.1 (D0), U3131.1 (D0)
RAM.A29: U3116.1 (D0), U3132.1 (D0)
