Datamuseum-DK/R1000.HwDoc/Schematics/IOC/pg_32.kicad_sch

## KiCad design Schematics/IOC/pg_32.kicad_sch (2023-01-10)

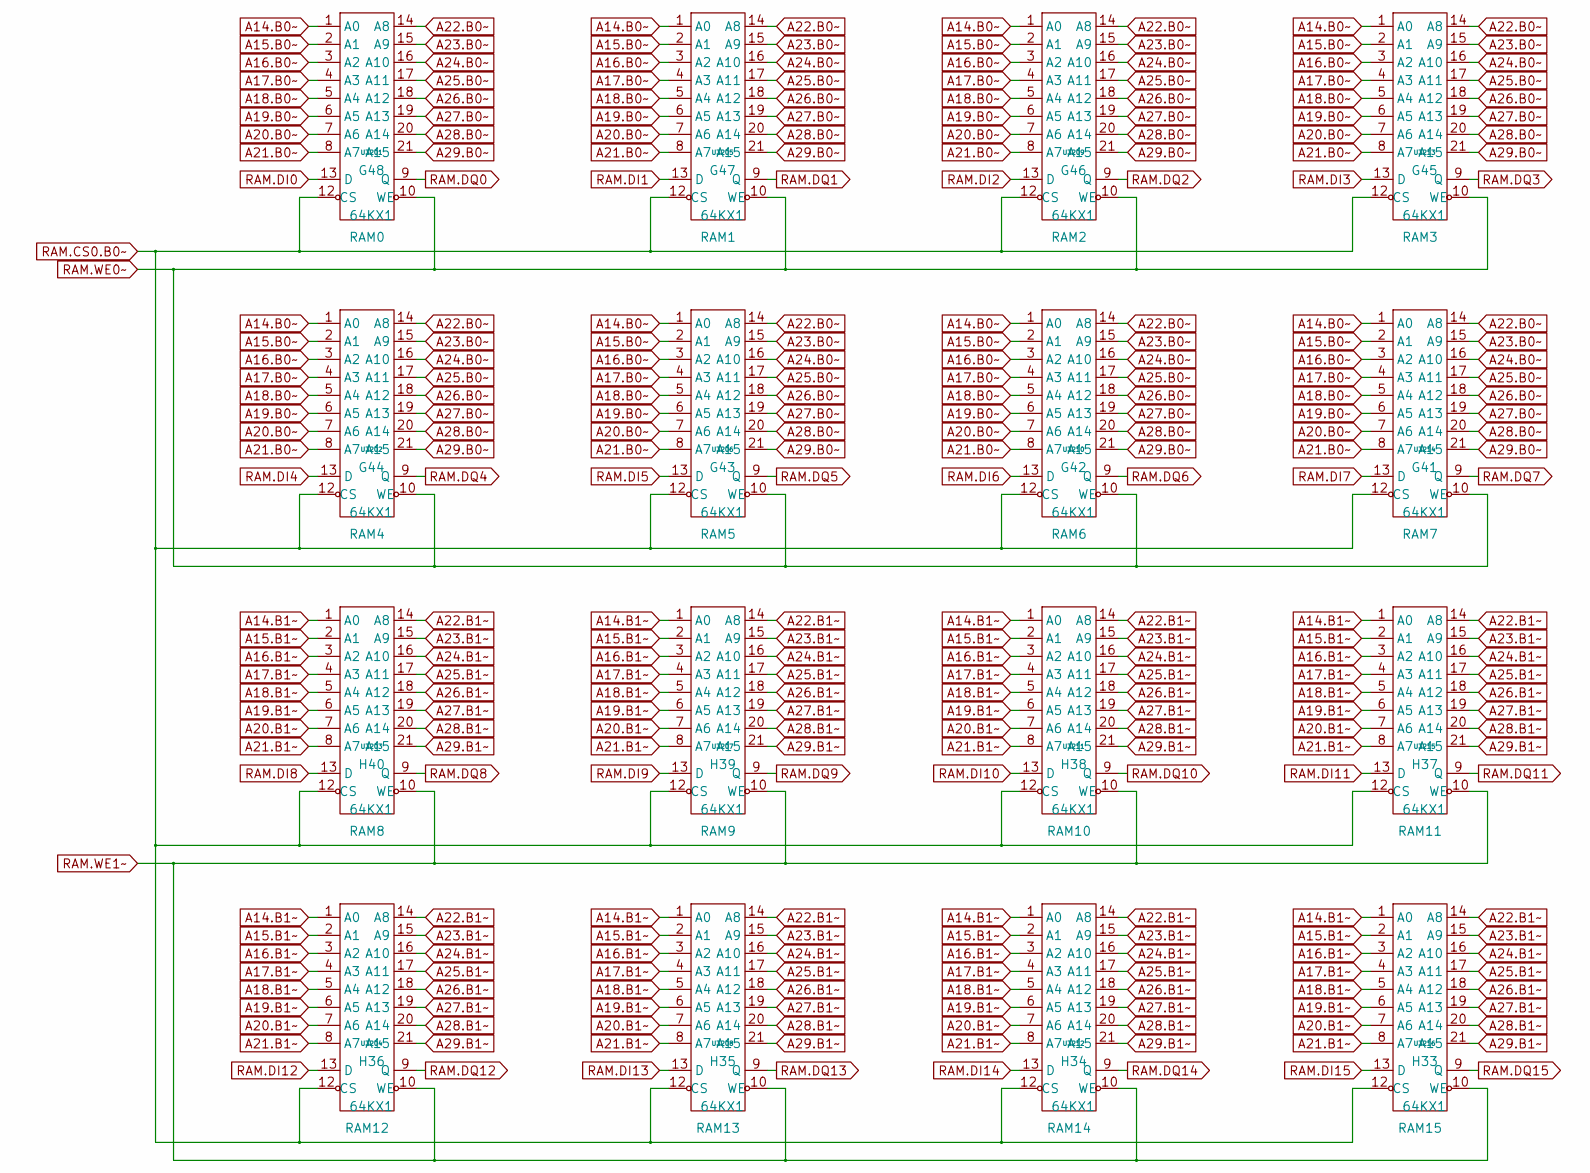
[picture p379: schematic pg_32.kicad_sch]

Parts:
U3201, U3202, U3203, U3204, U3205, U3206, U3207, U3208, U3209, U3210, U3211, U3212, U3213, U3214, U3215, U3216: 64KX1

Connections:
A14.B0~: U3201.1 (A0), U3202.1 (A0), U3205.1 (A0), U3206.1 (A0), U3209.1 (A0), U3210.1 (A0), U3213.1 (A0), U3214.1 (A0)
A14.B1~: U3203.1 (A0), U3204.1 (A0), U3207.1 (A0), U3208.1 (A0), U3211.1 (A0), U3212.1 (A0), U3215.1 (A0), U3216.1 (A0)
A15.B0~: U3201.2 (A1), U3202.2 (A1), U3205.2 (A1), U3206.2 (A1), U3209.2 (A1), U3210.2 (A1), U3213.2 (A1), U3214.2 (A1)
A15.B1~: U3203.2 (A1), U3204.2 (A1), U3207.2 (A1), U3208.2 (A1), U3211.2 (A1), U3212.2 (A1), U3215.2 (A1), U3216.2 (A1)
A16.B0~: U3201.3 (A2), U3202.3 (A2), U3205.3 (A2), U3206.3 (A2), U3209.3 (A2), U3210.3 (A2), U3213.3 (A2), U3214.3 (A2)
A16.B1~: U3203.3 (A2), U3204.3 (A2), U3207.3 (A2), U3208.3 (A2), U3211.3 (A2), U3212.3 (A2), U3215.3 (A2), U3216.3 (A2)
A17.B0~: U3201.4 (A3), U3202.4 (A3), U3205.4 (A3), U3206.4 (A3), U3209.4 (A3), U3210.4 (A3), U3213.4 (A3), U3214.4 (A3)
A17.B1~: U3203.4 (A3), U3204.4 (A3), U3207.4 (A3), U3208.4 (A3), U3211.4 (A3), U3212.4 (A3), U3215.4 (A3), U3216.4 (A3)
A18.B0~: U3201.5 (A4), U3202.5 (A4), U3205.5 (A4), U3206.5 (A4), U3209.5 (A4), U3210.5 (A4), U3213.5 (A4), U3214.5 (A4)
A18.B1~: U3203.5 (A4), U3204.5 (A4), U3207.5 (A4), U3208.5 (A4), U3211.5 (A4), U3212.5 (A4), U3215.5 (A4), U3216.5 (A4)
A19.B0~: U3201.6 (A5), U3202.6 (A5), U3205.6 (A5), U3206.6 (A5), U3209.6 (A5), U3210.6 (A5), U3213.6 (A5), U3214.6 (A5)
A19.B1~: U3203.6 (A5), U3204.6 (A5), U3207.6 (A5), U3208.6 (A5), U3211.6 (A5), U3212.6 (A5), U3215.6 (A5), U3216.6 (A5)
A20.B0~: U3201.7 (A6), U3202.7 (A6), U3205.7 (A6), U3206.7 (A6), U3209.7 (A6), U3210.7 (A6), U3213.7 (A6), U3214.7 (A6)
A20.B1~: U3203.7 (A6), U3204.7 (A6), U3207.7 (A6), U3208.7 (A6), U3211.7 (A6), U3212.7 (A6), U3215.7 (A6), U3216.7 (A6)
A21.B0~: U3201.8 (A7), U3202.8 (A7), U3205.8 (A7), U3206.8 (A7), U3209.8 (A7), U3210.8 (A7), U3213.8 (A7), U3214.8 (A7)
A21.B1~: U3203.8 (A7), U3204.8 (A7), U3207.8 (A7), U3208.8 (A7), U3211.8 (A7), U3212.8 (A7), U3215.8 (A7), U3216.8 (A7)
A22.B0~: U3201.14 (A8), U3202.14 (A8), U3205.14 (A8), U3206.14 (A8), U3209.14 (A8), U3210.14 (A8), U3213.14 (A8), U3214.14 (A8)
A22.B1~: U3203.14 (A8), U3204.14 (A8), U3207.14 (A8), U3208.14 (A8), U3211.14 (A8), U3212.14 (A8), U3215.14 (A8), U3216.14 (A8)
A23.B0~: U3201.15 (A9), U3202.15 (A9), U3205.15 (A9), U3206.15 (A9), U3209.15 (A9), U3210.15 (A9), U3213.15 (A9), U3214.15 (A9)
A23.B1~: U3203.15 (A9), U3204.15 (A9), U3207.15 (A9), U3208.15 (A9), U3211.15 (A9), U3212.15 (A9), U3215.15 (A9), U3216.15 (A9)
A24.B0~: U3201.16 (A10), U3202.16 (A10), U3205.16 (A10), U3206.16 (A10), U3209.16 (A10), U3210.16 (A10), U3213.16 (A10), U3214.16 (A10)
A24.B1~: U3203.16 (A10), U3204.16 (A10), U3207.16 (A10), U3208.16 (A10), U3211.16 (A10), U3212.16 (A10), U3215.16 (A10), U3216.16 (A10)
A25.B0~: U3201.17 (A11), U3202.17 (A11), U3205.17 (A11), U3206.17 (A11), U3209.17 (A11), U3210.17 (A11), U3213.17 (A11), U3214.17 (A11)
A25.B1~: U3203.17 (A11), U3204.17 (A11), U3207.17 (A11), U3208.17 (A11), U3211.17 (A11), U3212.17 (A11), U3215.17 (A11), U3216.17 (A11)
A26.B0~: U3201.18 (A12), U3202.18 (A12), U3205.18 (A12), U3206.18 (A12), U3209.18 (A12), U3210.18 (A12), U3213.18 (A12), U3214.18 (A12)
A26.B1~: U3203.18 (A12), U3204.18 (A12), U3207.18 (A12), U3208.18 (A12), U3211.18 (A12), U3212.18 (A12), U3215.18 (A12), U3216.18 (A12)
A27.B0~: U3201.19 (A13), U3202.19 (A13), U3205.19 (A13), U3206.19 (A13), U3209.19 (A13), U3210.19 (A13), U3213.19 (A13), U3214.19 (A13)
A27.B1~: U3203.19 (A13), U3204.19 (A13), U3207.19 (A13), U3208.19 (A13), U3211.19 (A13), U3212.19 (A13), U3215.19 (A13), U3216.19 (A13)
A28.B0~: U3201.20 (A14), U3202.20 (A14), U3205.20 (A14), U3206.20 (A14), U3209.20 (A14), U3210.20 (A14), U3213.20 (A14), U3214.20 (A14)
A28.B1~: U3203.20 (A14), U3204.20 (A14), U3207.20 (A14), U3208.20 (A14), U3211.20 (A14), U3212.20 (A14), U3215.20 (A14), U3216.20 (A14)
A29.B0~: U3201.21 (A15), U3202.21 (A15), U3205.21 (A15), U3206.21 (A15), U3209.21 (A15), U3210.21 (A15), U3213.21 (A15), U3214.21 (A15)
A29.B1~: U3203.21 (A15), U3204.21 (A15), U3207.21 (A15), U3208.21 (A15), U3211.21 (A15), U3212.21 (A15), U3215.21 (A15), U3216.21 (A15)
RAM.CS0.B0~: U3201.12 (CS), U3202.12 (CS), U3203.12 (CS), U3204.12 (CS), U3205.12 (CS), U3206.12 (CS), U3207.12 (CS), U3208.12 (CS), U3209.12 (CS), U3210.12 (CS), U3211.12 (CS), U3212.12 (CS), U3213.12 (CS), U3214.12 (CS), U3215.12 (CS), U3216.12 (CS)
RAM.DI0: U3201.13 (D)
RAM.DI1: U3205.13 (D)
RAM.DI2: U3209.13 (D)
RAM.DI3: U3213.13 (D)
RAM.DI4: U3202.13 (D)
RAM.DI5: U3206.13 (D)
RAM.DI6: U3210.13 (D)
RAM.DI7: U3214.13 (D)
RAM.DI8: U3203.13 (D)
RAM.DI9: U3207.13 (D)
RAM.DI10: U3211.13 (D)
RAM.DI11: U3215.13 (D)
RAM.DI12: U3204.13 (D)
RAM.DI13: U3208.13 (D)
RAM.DI14: U3212.13 (D)
RAM.DI15: U3216.13 (D)
RAM.DQ0: U3201.9 (Q)
RAM.DQ1: U3205.9 (Q)
RAM.DQ2: U3209.9 (Q)
RAM.DQ3: U3213.9 (Q)
RAM.DQ4: U3202.9 (Q)
RAM.DQ5: U3206.9 (Q)
RAM.DQ6: U3210.9 (Q)
RAM.DQ7: U3214.9 (Q)
RAM.DQ8: U3203.9 (Q)
RAM.DQ9: U3207.9 (Q)
RAM.DQ10: U3211.9 (Q)
RAM.DQ11: U3215.9 (Q)
RAM.DQ12: U3204.9 (Q)
RAM.DQ13: U3208.9 (Q)
RAM.DQ14: U3212.9 (Q)
RAM.DQ15: U3216.9 (Q)
RAM.WE0~: U3201.10 (WE), U3202.10 (WE), U3205.10 (WE), U3206.10 (WE), U3209.10 (WE), U3210.10 (WE), U3213.10 (WE), U3214.10 (WE)
RAM.WE1~: U3203.10 (WE), U3204.10 (WE), U3207.10 (WE), U3208.10 (WE), U3211.10 (WE), U3212.10 (WE), U3215.10 (WE), U3216.10 (WE)
