Datamuseum-DK/R1000.HwDoc/Schematics/IOC/pg_33.kicad_sch

## KiCad design Schematics/IOC/pg_33.kicad_sch (2023-01-10)

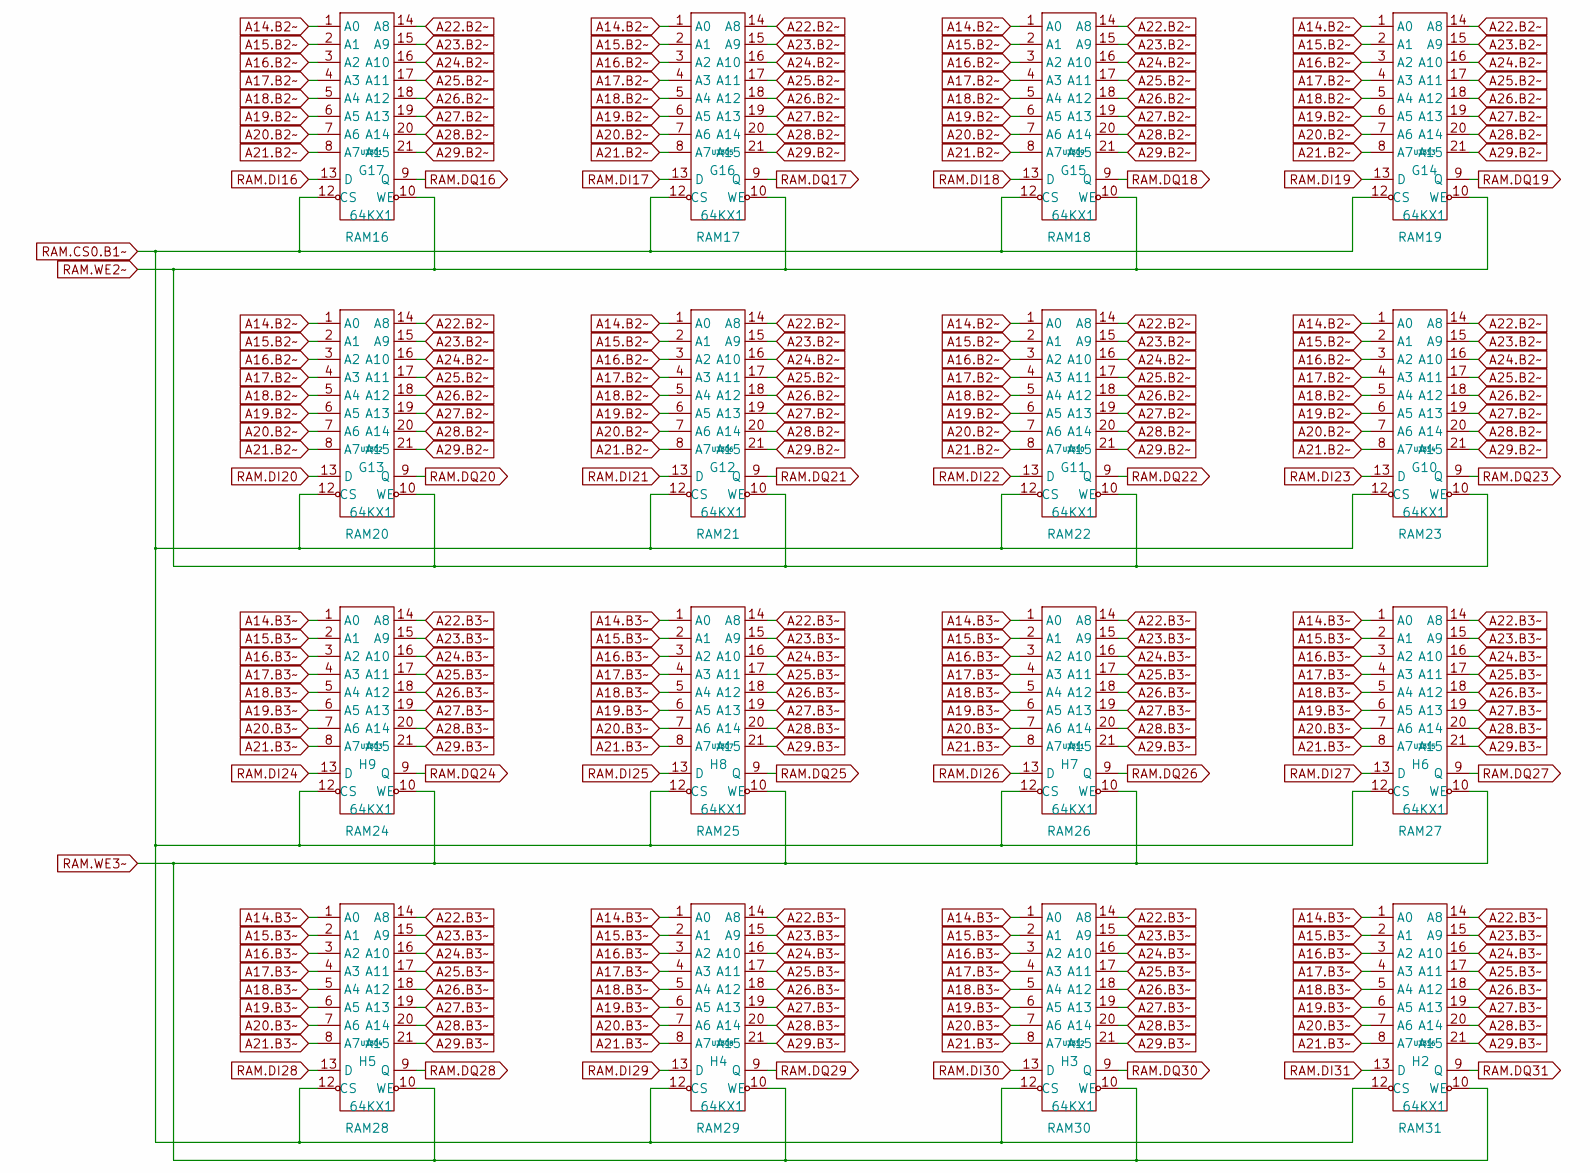
[picture p380: schematic pg_33.kicad_sch]

Parts:
U3301, U3302, U3303, U3304, U3305, U3306, U3307, U3308, U3309, U3310, U3311, U3312, U3313, U3314, U3315, U3316: 64KX1

Connections:
A14.B2~: U3301.1 (A0), U3302.1 (A0), U3305.1 (A0), U3306.1 (A0), U3309.1 (A0), U3310.1 (A0), U3313.1 (A0), U3314.1 (A0)
A14.B3~: U3303.1 (A0), U3304.1 (A0), U3307.1 (A0), U3308.1 (A0), U3311.1 (A0), U3312.1 (A0), U3315.1 (A0), U3316.1 (A0)
A15.B2~: U3301.2 (A1), U3302.2 (A1), U3305.2 (A1), U3306.2 (A1), U3309.2 (A1), U3310.2 (A1), U3313.2 (A1), U3314.2 (A1)
A15.B3~: U3303.2 (A1), U3304.2 (A1), U3307.2 (A1), U3308.2 (A1), U3311.2 (A1), U3312.2 (A1), U3315.2 (A1), U3316.2 (A1)
A16.B2~: U3301.3 (A2), U3302.3 (A2), U3305.3 (A2), U3306.3 (A2), U3309.3 (A2), U3310.3 (A2), U3313.3 (A2), U3314.3 (A2)
A16.B3~: U3303.3 (A2), U3304.3 (A2), U3307.3 (A2), U3308.3 (A2), U3311.3 (A2), U3312.3 (A2), U3315.3 (A2), U3316.3 (A2)
A17.B2~: U3301.4 (A3), U3302.4 (A3), U3305.4 (A3), U3306.4 (A3), U3309.4 (A3), U3310.4 (A3), U3313.4 (A3), U3314.4 (A3)
A17.B3~: U3303.4 (A3), U3304.4 (A3), U3307.4 (A3), U3308.4 (A3), U3311.4 (A3), U3312.4 (A3), U3315.4 (A3), U3316.4 (A3)
A18.B2~: U3301.5 (A4), U3302.5 (A4), U3305.5 (A4), U3306.5 (A4), U3309.5 (A4), U3310.5 (A4), U3313.5 (A4), U3314.5 (A4)
A18.B3~: U3303.5 (A4), U3304.5 (A4), U3307.5 (A4), U3308.5 (A4), U3311.5 (A4), U3312.5 (A4), U3315.5 (A4), U3316.5 (A4)
A19.B2~: U3301.6 (A5), U3302.6 (A5), U3305.6 (A5), U3306.6 (A5), U3309.6 (A5), U3310.6 (A5), U3313.6 (A5), U3314.6 (A5)
A19.B3~: U3303.6 (A5), U3304.6 (A5), U3307.6 (A5), U3308.6 (A5), U3311.6 (A5), U3312.6 (A5), U3315.6 (A5), U3316.6 (A5)
A20.B2~: U3301.7 (A6), U3302.7 (A6), U3305.7 (A6), U3306.7 (A6), U3309.7 (A6), U3310.7 (A6), U3313.7 (A6), U3314.7 (A6)
A20.B3~: U3303.7 (A6), U3304.7 (A6), U3307.7 (A6), U3308.7 (A6), U3311.7 (A6), U3312.7 (A6), U3315.7 (A6), U3316.7 (A6)
A21.B2~: U3301.8 (A7), U3302.8 (A7), U3305.8 (A7), U3306.8 (A7), U3309.8 (A7), U3310.8 (A7), U3313.8 (A7), U3314.8 (A7)
A21.B3~: U3303.8 (A7), U3304.8 (A7), U3307.8 (A7), U3308.8 (A7), U3311.8 (A7), U3312.8 (A7), U3315.8 (A7), U3316.8 (A7)
A22.B2~: U3301.14 (A8), U3302.14 (A8), U3305.14 (A8), U3306.14 (A8), U3309.14 (A8), U3310.14 (A8), U3313.14 (A8), U3314.14 (A8)
A22.B3~: U3303.14 (A8), U3304.14 (A8), U3307.14 (A8), U3308.14 (A8), U3311.14 (A8), U3312.14 (A8), U3315.14 (A8), U3316.14 (A8)
A23.B2~: U3301.15 (A9), U3302.15 (A9), U3305.15 (A9), U3306.15 (A9), U3309.15 (A9), U3310.15 (A9), U3313.15 (A9), U3314.15 (A9)
A23.B3~: U3303.15 (A9), U3304.15 (A9), U3307.15 (A9), U3308.15 (A9), U3311.15 (A9), U3312.15 (A9), U3315.15 (A9), U3316.15 (A9)
A24.B2~: U3301.16 (A10), U3302.16 (A10), U3305.16 (A10), U3306.16 (A10), U3309.16 (A10), U3310.16 (A10), U3313.16 (A10), U3314.16 (A10)
A24.B3~: U3303.16 (A10), U3304.16 (A10), U3307.16 (A10), U3308.16 (A10), U3311.16 (A10), U3312.16 (A10), U3315.16 (A10), U3316.16 (A10)
A25.B2~: U3301.17 (A11), U3302.17 (A11), U3305.17 (A11), U3306.17 (A11), U3309.17 (A11), U3310.17 (A11), U3313.17 (A11), U3314.17 (A11)
A25.B3~: U3303.17 (A11), U3304.17 (A11), U3307.17 (A11), U3308.17 (A11), U3311.17 (A11), U3312.17 (A11), U3315.17 (A11), U3316.17 (A11)
A26.B2~: U3301.18 (A12), U3302.18 (A12), U3305.18 (A12), U3306.18 (A12), U3309.18 (A12), U3310.18 (A12), U3313.18 (A12), U3314.18 (A12)
A26.B3~: U3303.18 (A12), U3304.18 (A12), U3307.18 (A12), U3308.18 (A12), U3311.18 (A12), U3312.18 (A12), U3315.18 (A12), U3316.18 (A12)
A27.B2~: U3301.19 (A13), U3302.19 (A13), U3305.19 (A13), U3306.19 (A13), U3309.19 (A13), U3310.19 (A13), U3313.19 (A13), U3314.19 (A13)
A27.B3~: U3303.19 (A13), U3304.19 (A13), U3307.19 (A13), U3308.19 (A13), U3311.19 (A13), U3312.19 (A13), U3315.19 (A13), U3316.19 (A13)
A28.B2~: U3301.20 (A14), U3302.20 (A14), U3305.20 (A14), U3306.20 (A14), U3309.20 (A14), U3310.20 (A14), U3313.20 (A14), U3314.20 (A14)
A28.B3~: U3303.20 (A14), U3304.20 (A14), U3307.20 (A14), U3308.20 (A14), U3311.20 (A14), U3312.20 (A14), U3315.20 (A14), U3316.20 (A14)
A29.B2~: U3301.21 (A15), U3302.21 (A15), U3305.21 (A15), U3306.21 (A15), U3309.21 (A15), U3310.21 (A15), U3313.21 (A15), U3314.21 (A15)
A29.B3~: U3303.21 (A15), U3304.21 (A15), U3307.21 (A15), U3308.21 (A15), U3311.21 (A15), U3312.21 (A15), U3315.21 (A15), U3316.21 (A15)
RAM.CS0.B1~: U3301.12 (CS), U3302.12 (CS), U3303.12 (CS), U3304.12 (CS), U3305.12 (CS), U3306.12 (CS), U3307.12 (CS), U3308.12 (CS), U3309.12 (CS), U3310.12 (CS), U3311.12 (CS), U3312.12 (CS), U3313.12 (CS), U3314.12 (CS), U3315.12 (CS), U3316.12 (CS)
RAM.DI16: U3301.13 (D)
RAM.DI17: U3305.13 (D)
RAM.DI18: U3309.13 (D)
RAM.DI19: U3313.13 (D)
RAM.DI20: U3302.13 (D)
RAM.DI21: U3306.13 (D)
RAM.DI22: U3310.13 (D)
RAM.DI23: U3314.13 (D)
RAM.DI24: U3303.13 (D)
RAM.DI25: U3307.13 (D)
RAM.DI26: U3311.13 (D)
RAM.DI27: U3315.13 (D)
RAM.DI28: U3304.13 (D)
RAM.DI29: U3308.13 (D)
RAM.DI30: U3312.13 (D)
RAM.DI31: U3316.13 (D)
RAM.DQ16: U3301.9 (Q)
RAM.DQ17: U3305.9 (Q)
RAM.DQ18: U3309.9 (Q)
RAM.DQ19: U3313.9 (Q)
RAM.DQ20: U3302.9 (Q)
RAM.DQ21: U3306.9 (Q)
RAM.DQ22: U3310.9 (Q)
RAM.DQ23: U3314.9 (Q)
RAM.DQ24: U3303.9 (Q)
RAM.DQ25: U3307.9 (Q)
RAM.DQ26: U3311.9 (Q)
RAM.DQ27: U3315.9 (Q)
RAM.DQ28: U3304.9 (Q)
RAM.DQ29: U3308.9 (Q)
RAM.DQ30: U3312.9 (Q)
RAM.DQ31: U3316.9 (Q)
RAM.WE2~: U3301.10 (WE), U3302.10 (WE), U3305.10 (WE), U3306.10 (WE), U3309.10 (WE), U3310.10 (WE), U3313.10 (WE), U3314.10 (WE)
RAM.WE3~: U3303.10 (WE), U3304.10 (WE), U3307.10 (WE), U3308.10 (WE), U3311.10 (WE), U3312.10 (WE), U3315.10 (WE), U3316.10 (WE)
