Datamuseum-DK/R1000.HwDoc/Schematics/IOC/pg_34.kicad_sch

## KiCad design Schematics/IOC/pg_34.kicad_sch (2023-01-10)

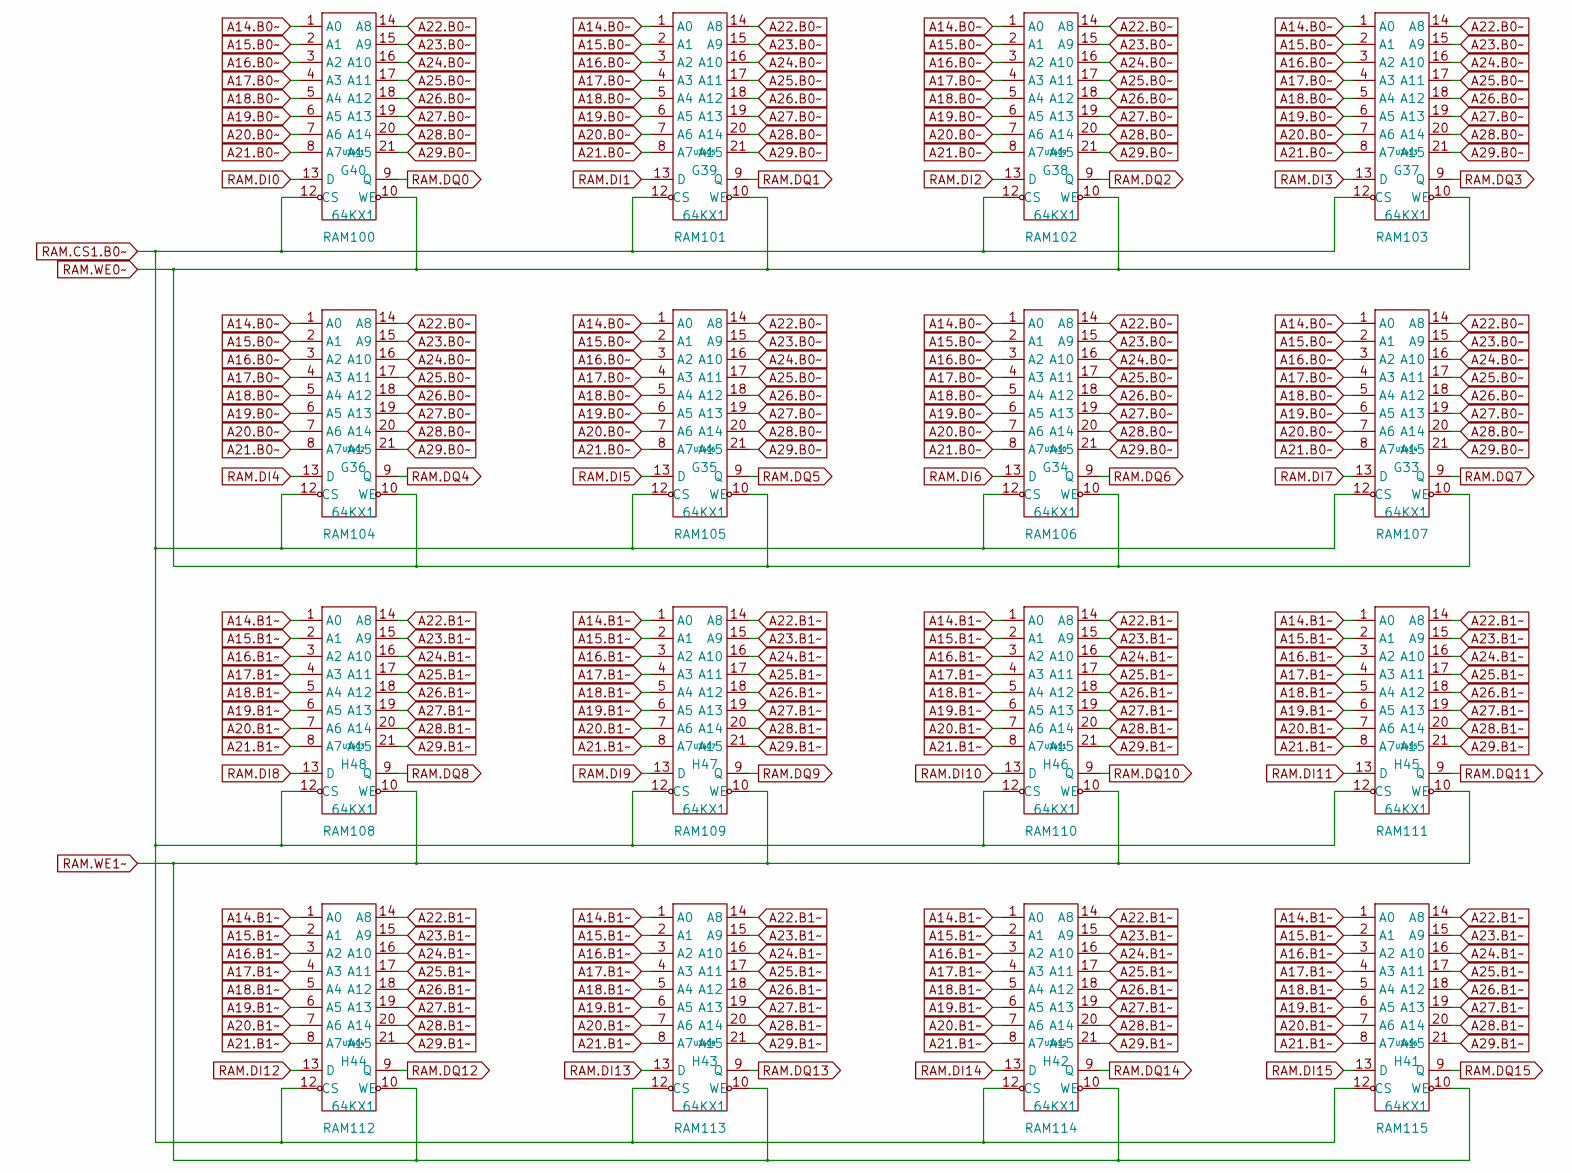
[picture p381: schematic pg_34.kicad_sch]

Parts:
U3401, U3402, U3403, U3404, U3405, U3406, U3407, U3408, U3409, U3410, U3411, U3412, U3413, U3414, U3415, U3416: 64KX1

Connections:
A14.B0~: U3401.1 (A0), U3402.1 (A0), U3405.1 (A0), U3406.1 (A0), U3409.1 (A0), U3410.1 (A0), U3413.1 (A0), U3414.1 (A0)
A14.B1~: U3403.1 (A0), U3404.1 (A0), U3407.1 (A0), U3408.1 (A0), U3411.1 (A0), U3412.1 (A0), U3415.1 (A0), U3416.1 (A0)
A15.B0~: U3401.2 (A1), U3402.2 (A1), U3405.2 (A1), U3406.2 (A1), U3409.2 (A1), U3410.2 (A1), U3413.2 (A1), U3414.2 (A1)
A15.B1~: U3403.2 (A1), U3404.2 (A1), U3407.2 (A1), U3408.2 (A1), U3411.2 (A1), U3412.2 (A1), U3415.2 (A1), U3416.2 (A1)
A16.B0~: U3401.3 (A2), U3402.3 (A2), U3405.3 (A2), U3406.3 (A2), U3409.3 (A2), U3410.3 (A2), U3413.3 (A2), U3414.3 (A2)
A16.B1~: U3403.3 (A2), U3404.3 (A2), U3407.3 (A2), U3408.3 (A2), U3411.3 (A2), U3412.3 (A2), U3415.3 (A2), U3416.3 (A2)
A17.B0~: U3401.4 (A3), U3402.4 (A3), U3405.4 (A3), U3406.4 (A3), U3409.4 (A3), U3410.4 (A3), U3413.4 (A3), U3414.4 (A3)
A17.B1~: U3403.4 (A3), U3404.4 (A3), U3407.4 (A3), U3408.4 (A3), U3411.4 (A3), U3412.4 (A3), U3415.4 (A3), U3416.4 (A3)
A18.B0~: U3401.5 (A4), U3402.5 (A4), U3405.5 (A4), U3406.5 (A4), U3409.5 (A4), U3410.5 (A4), U3413.5 (A4), U3414.5 (A4)
A18.B1~: U3403.5 (A4), U3404.5 (A4), U3407.5 (A4), U3408.5 (A4), U3411.5 (A4), U3412.5 (A4), U3415.5 (A4), U3416.5 (A4)
A19.B0~: U3401.6 (A5), U3402.6 (A5), U3405.6 (A5), U3406.6 (A5), U3409.6 (A5), U3410.6 (A5), U3413.6 (A5), U3414.6 (A5)
A19.B1~: U3403.6 (A5), U3404.6 (A5), U3407.6 (A5), U3408.6 (A5), U3411.6 (A5), U3412.6 (A5), U3415.6 (A5), U3416.6 (A5)
A20.B0~: U3401.7 (A6), U3402.7 (A6), U3405.7 (A6), U3406.7 (A6), U3409.7 (A6), U3410.7 (A6), U3413.7 (A6), U3414.7 (A6)
A20.B1~: U3403.7 (A6), U3404.7 (A6), U3407.7 (A6), U3408.7 (A6), U3411.7 (A6), U3412.7 (A6), U3415.7 (A6), U3416.7 (A6)
A21.B0~: U3401.8 (A7), U3402.8 (A7), U3405.8 (A7), U3406.8 (A7), U3409.8 (A7), U3410.8 (A7), U3413.8 (A7), U3414.8 (A7)
A21.B1~: U3403.8 (A7), U3404.8 (A7), U3407.8 (A7), U3408.8 (A7), U3411.8 (A7), U3412.8 (A7), U3415.8 (A7), U3416.8 (A7)
A22.B0~: U3401.14 (A8), U3402.14 (A8), U3405.14 (A8), U3406.14 (A8), U3409.14 (A8), U3410.14 (A8), U3413.14 (A8), U3414.14 (A8)
A22.B1~: U3403.14 (A8), U3404.14 (A8), U3407.14 (A8), U3408.14 (A8), U3411.14 (A8), U3412.14 (A8), U3415.14 (A8), U3416.14 (A8)
A23.B0~: U3401.15 (A9), U3402.15 (A9), U3405.15 (A9), U3406.15 (A9), U3409.15 (A9), U3410.15 (A9), U3413.15 (A9), U3414.15 (A9)
A23.B1~: U3403.15 (A9), U3404.15 (A9), U3407.15 (A9), U3408.15 (A9), U3411.15 (A9), U3412.15 (A9), U3415.15 (A9), U3416.15 (A9)
A24.B0~: U3401.16 (A10), U3402.16 (A10), U3405.16 (A10), U3406.16 (A10), U3409.16 (A10), U3410.16 (A10), U3413.16 (A10), U3414.16 (A10)
A24.B1~: U3403.16 (A10), U3404.16 (A10), U3407.16 (A10), U3408.16 (A10), U3411.16 (A10), U3412.16 (A10), U3415.16 (A10), U3416.16 (A10)
A25.B0~: U3401.17 (A11), U3402.17 (A11), U3405.17 (A11), U3406.17 (A11), U3409.17 (A11), U3410.17 (A11), U3413.17 (A11), U3414.17 (A11)
A25.B1~: U3403.17 (A11), U3404.17 (A11), U3407.17 (A11), U3408.17 (A11), U3411.17 (A11), U3412.17 (A11), U3415.17 (A11), U3416.17 (A11)
A26.B0~: U3401.18 (A12), U3402.18 (A12), U3405.18 (A12), U3406.18 (A12), U3409.18 (A12), U3410.18 (A12), U3413.18 (A12), U3414.18 (A12)
A26.B1~: U3403.18 (A12), U3404.18 (A12), U3407.18 (A12), U3408.18 (A12), U3411.18 (A12), U3412.18 (A12), U3415.18 (A12), U3416.18 (A12)
A27.B0~: U3401.19 (A13), U3402.19 (A13), U3405.19 (A13), U3406.19 (A13), U3409.19 (A13), U3410.19 (A13), U3413.19 (A13), U3414.19 (A13)
A27.B1~: U3403.19 (A13), U3404.19 (A13), U3407.19 (A13), U3408.19 (A13), U3411.19 (A13), U3412.19 (A13), U3415.19 (A13), U3416.19 (A13)
A28.B0~: U3401.20 (A14), U3402.20 (A14), U3405.20 (A14), U3406.20 (A14), U3409.20 (A14), U3410.20 (A14), U3413.20 (A14), U3414.20 (A14)
A28.B1~: U3403.20 (A14), U3404.20 (A14), U3407.20 (A14), U3408.20 (A14), U3411.20 (A14), U3412.20 (A14), U3415.20 (A14), U3416.20 (A14)
A29.B0~: U3401.21 (A15), U3402.21 (A15), U3405.21 (A15), U3406.21 (A15), U3409.21 (A15), U3410.21 (A15), U3413.21 (A15), U3414.21 (A15)
A29.B1~: U3403.21 (A15), U3404.21 (A15), U3407.21 (A15), U3408.21 (A15), U3411.21 (A15), U3412.21 (A15), U3415.21 (A15), U3416.21 (A15)
RAM.CS1.B0~: U3401.12 (CS), U3402.12 (CS), U3403.12 (CS), U3404.12 (CS), U3405.12 (CS), U3406.12 (CS), U3407.12 (CS), U3408.12 (CS), U3409.12 (CS), U3410.12 (CS), U3411.12 (CS), U3412.12 (CS), U3413.12 (CS), U3414.12 (CS), U3415.12 (CS), U3416.12 (CS)
RAM.DI0: U3401.13 (D)
RAM.DI1: U3405.13 (D)
RAM.DI2: U3409.13 (D)
RAM.DI3: U3413.13 (D)
RAM.DI4: U3402.13 (D)
RAM.DI5: U3406.13 (D)
RAM.DI6: U3410.13 (D)
RAM.DI7: U3414.13 (D)
RAM.DI8: U3403.13 (D)
RAM.DI9: U3407.13 (D)
RAM.DI10: U3411.13 (D)
RAM.DI11: U3415.13 (D)
RAM.DI12: U3404.13 (D)
RAM.DI13: U3408.13 (D)
RAM.DI14: U3412.13 (D)
RAM.DI15: U3416.13 (D)
RAM.DQ0: U3401.9 (Q)
RAM.DQ1: U3405.9 (Q)
RAM.DQ2: U3409.9 (Q)
RAM.DQ3: U3413.9 (Q)
RAM.DQ4: U3402.9 (Q)
RAM.DQ5: U3406.9 (Q)
RAM.DQ6: U3410.9 (Q)
RAM.DQ7: U3414.9 (Q)
RAM.DQ8: U3403.9 (Q)
RAM.DQ9: U3407.9 (Q)
RAM.DQ10: U3411.9 (Q)
RAM.DQ11: U3415.9 (Q)
RAM.DQ12: U3404.9 (Q)
RAM.DQ13: U3408.9 (Q)
RAM.DQ14: U3412.9 (Q)
RAM.DQ15: U3416.9 (Q)
RAM.WE0~: U3401.10 (WE), U3402.10 (WE), U3405.10 (WE), U3406.10 (WE), U3409.10 (WE), U3410.10 (WE), U3413.10 (WE), U3414.10 (WE)
RAM.WE1~: U3403.10 (WE), U3404.10 (WE), U3407.10 (WE), U3408.10 (WE), U3411.10 (WE), U3412.10 (WE), U3415.10 (WE), U3416.10 (WE)
