Datamuseum-DK/R1000.HwDoc/Schematics/IOC/pg_35.kicad_sch

## KiCad design Schematics/IOC/pg_35.kicad_sch (2023-01-10)

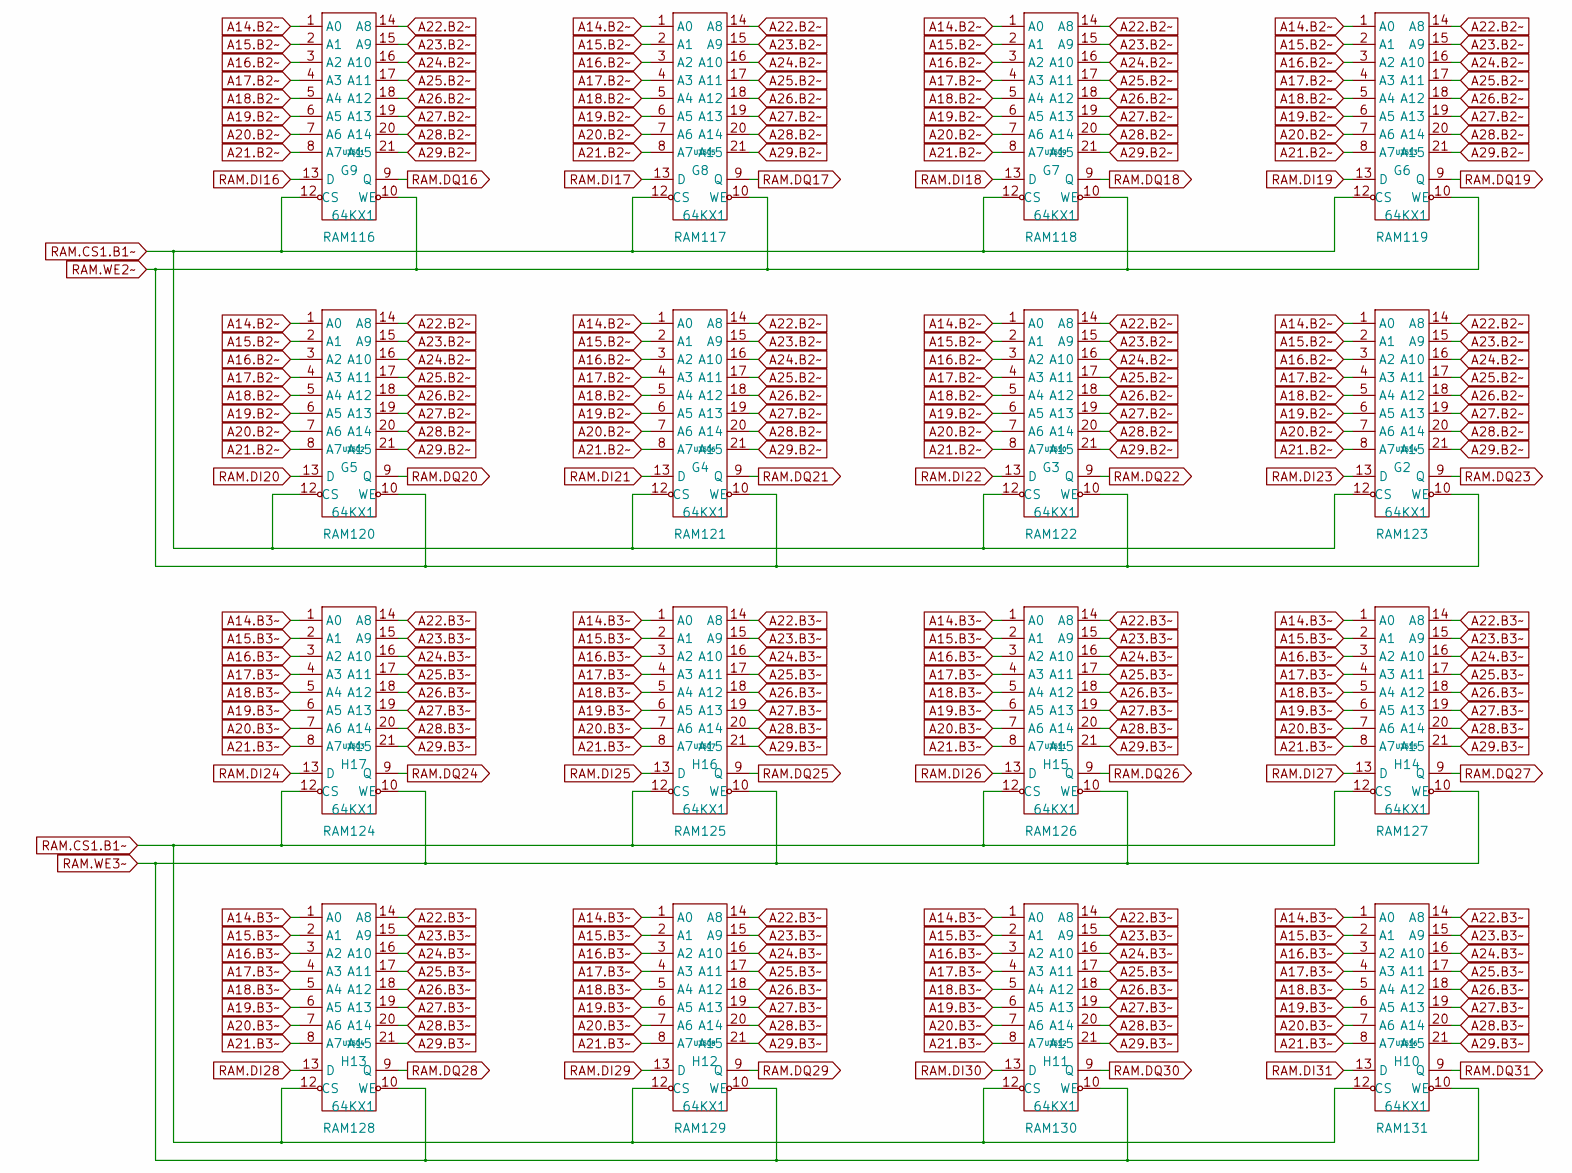
[picture p382: schematic pg_35.kicad_sch]

Parts:
U3501, U3502, U3503, U3504, U3505, U3506, U3507, U3508, U3509, U3510, U3511, U3512, U3513, U3514, U3515, U3516: 64KX1

Connections:
A14.B2~: U3501.1 (A0), U3502.1 (A0), U3505.1 (A0), U3506.1 (A0), U3509.1 (A0), U3510.1 (A0), U3513.1 (A0), U3514.1 (A0)
A14.B3~: U3503.1 (A0), U3504.1 (A0), U3507.1 (A0), U3508.1 (A0), U3511.1 (A0), U3512.1 (A0), U3515.1 (A0), U3516.1 (A0)
A15.B2~: U3501.2 (A1), U3502.2 (A1), U3505.2 (A1), U3506.2 (A1), U3509.2 (A1), U3510.2 (A1), U3513.2 (A1), U3514.2 (A1)
A15.B3~: U3503.2 (A1), U3504.2 (A1), U3507.2 (A1), U3508.2 (A1), U3511.2 (A1), U3512.2 (A1), U3515.2 (A1), U3516.2 (A1)
A16.B2~: U3501.3 (A2), U3502.3 (A2), U3505.3 (A2), U3506.3 (A2), U3509.3 (A2), U3510.3 (A2), U3513.3 (A2), U3514.3 (A2)
A16.B3~: U3503.3 (A2), U3504.3 (A2), U3507.3 (A2), U3508.3 (A2), U3511.3 (A2), U3512.3 (A2), U3515.3 (A2), U3516.3 (A2)
A17.B2~: U3501.4 (A3), U3502.4 (A3), U3505.4 (A3), U3506.4 (A3), U3509.4 (A3), U3510.4 (A3), U3513.4 (A3), U3514.4 (A3)
A17.B3~: U3503.4 (A3), U3504.4 (A3), U3507.4 (A3), U3508.4 (A3), U3511.4 (A3), U3512.4 (A3), U3515.4 (A3), U3516.4 (A3)
A18.B2~: U3501.5 (A4), U3502.5 (A4), U3505.5 (A4), U3506.5 (A4), U3509.5 (A4), U3510.5 (A4), U3513.5 (A4), U3514.5 (A4)
A18.B3~: U3503.5 (A4), U3504.5 (A4), U3507.5 (A4), U3508.5 (A4), U3511.5 (A4), U3512.5 (A4), U3515.5 (A4), U3516.5 (A4)
A19.B2~: U3501.6 (A5), U3502.6 (A5), U3505.6 (A5), U3506.6 (A5), U3509.6 (A5), U3510.6 (A5), U3513.6 (A5), U3514.6 (A5)
A19.B3~: U3503.6 (A5), U3504.6 (A5), U3507.6 (A5), U3508.6 (A5), U3511.6 (A5), U3512.6 (A5), U3515.6 (A5), U3516.6 (A5)
A20.B2~: U3501.7 (A6), U3502.7 (A6), U3505.7 (A6), U3506.7 (A6), U3509.7 (A6), U3510.7 (A6), U3513.7 (A6), U3514.7 (A6)
A20.B3~: U3503.7 (A6), U3504.7 (A6), U3507.7 (A6), U3508.7 (A6), U3511.7 (A6), U3512.7 (A6), U3515.7 (A6), U3516.7 (A6)
A21.B2~: U3501.8 (A7), U3502.8 (A7), U3505.8 (A7), U3506.8 (A7), U3509.8 (A7), U3510.8 (A7), U3513.8 (A7), U3514.8 (A7)
A21.B3~: U3503.8 (A7), U3504.8 (A7), U3507.8 (A7), U3508.8 (A7), U3511.8 (A7), U3512.8 (A7), U3515.8 (A7), U3516.8 (A7)
A22.B2~: U3501.14 (A8), U3502.14 (A8), U3505.14 (A8), U3506.14 (A8), U3509.14 (A8), U3510.14 (A8), U3513.14 (A8), U3514.14 (A8)
A22.B3~: U3503.14 (A8), U3504.14 (A8), U3507.14 (A8), U3508.14 (A8), U3511.14 (A8), U3512.14 (A8), U3515.14 (A8), U3516.14 (A8)
A23.B2~: U3501.15 (A9), U3502.15 (A9), U3505.15 (A9), U3506.15 (A9), U3509.15 (A9), U3510.15 (A9), U3513.15 (A9), U3514.15 (A9)
A23.B3~: U3503.15 (A9), U3504.15 (A9), U3507.15 (A9), U3508.15 (A9), U3511.15 (A9), U3512.15 (A9), U3515.15 (A9), U3516.15 (A9)
A24.B2~: U3501.16 (A10), U3502.16 (A10), U3505.16 (A10), U3506.16 (A10), U3509.16 (A10), U3510.16 (A10), U3513.16 (A10), U3514.16 (A10)
A24.B3~: U3503.16 (A10), U3504.16 (A10), U3507.16 (A10), U3508.16 (A10), U3511.16 (A10), U3512.16 (A10), U3515.16 (A10), U3516.16 (A10)
A25.B2~: U3501.17 (A11), U3502.17 (A11), U3505.17 (A11), U3506.17 (A11), U3509.17 (A11), U3510.17 (A11), U3513.17 (A11), U3514.17 (A11)
A25.B3~: U3503.17 (A11), U3504.17 (A11), U3507.17 (A11), U3508.17 (A11), U3511.17 (A11), U3512.17 (A11), U3515.17 (A11), U3516.17 (A11)
A26.B2~: U3501.18 (A12), U3502.18 (A12), U3505.18 (A12), U3506.18 (A12), U3509.18 (A12), U3510.18 (A12), U3513.18 (A12), U3514.18 (A12)
A26.B3~: U3503.18 (A12), U3504.18 (A12), U3507.18 (A12), U3508.18 (A12), U3511.18 (A12), U3512.18 (A12), U3515.18 (A12), U3516.18 (A12)
A27.B2~: U3501.19 (A13), U3502.19 (A13), U3505.19 (A13), U3506.19 (A13), U3509.19 (A13), U3510.19 (A13), U3513.19 (A13), U3514.19 (A13)
A27.B3~: U3503.19 (A13), U3504.19 (A13), U3507.19 (A13), U3508.19 (A13), U3511.19 (A13), U3512.19 (A13), U3515.19 (A13), U3516.19 (A13)
A28.B2~: U3501.20 (A14), U3502.20 (A14), U3505.20 (A14), U3506.20 (A14), U3509.20 (A14), U3510.20 (A14), U3513.20 (A14), U3514.20 (A14)
A28.B3~: U3503.20 (A14), U3504.20 (A14), U3507.20 (A14), U3508.20 (A14), U3511.20 (A14), U3512.20 (A14), U3515.20 (A14), U3516.20 (A14)
A29.B2~: U3501.21 (A15), U3502.21 (A15), U3505.21 (A15), U3506.21 (A15), U3509.21 (A15), U3510.21 (A15), U3513.21 (A15), U3514.21 (A15)
A29.B3~: U3503.21 (A15), U3504.21 (A15), U3507.21 (A15), U3508.21 (A15), U3511.21 (A15), U3512.21 (A15), U3515.21 (A15), U3516.21 (A15)
RAM.CS1.B1~: U3501.12 (CS), U3502.12 (CS), U3503.12 (CS), U3504.12 (CS), U3505.12 (CS), U3506.12 (CS), U3507.12 (CS), U3508.12 (CS), U3509.12 (CS), U3510.12 (CS), U3511.12 (CS), U3512.12 (CS), U3513.12 (CS), U3514.12 (CS), U3515.12 (CS), U3516.12 (CS)
RAM.DI16: U3501.13 (D)
RAM.DI17: U3505.13 (D)
RAM.DI18: U3509.13 (D)
RAM.DI19: U3513.13 (D)
RAM.DI20: U3502.13 (D)
RAM.DI21: U3506.13 (D)
RAM.DI22: U3510.13 (D)
RAM.DI23: U3514.13 (D)
RAM.DI24: U3503.13 (D)
RAM.DI25: U3507.13 (D)
RAM.DI26: U3511.13 (D)
RAM.DI27: U3515.13 (D)
RAM.DI28: U3504.13 (D)
RAM.DI29: U3508.13 (D)
RAM.DI30: U3512.13 (D)
RAM.DI31: U3516.13 (D)
RAM.DQ16: U3501.9 (Q)
RAM.DQ17: U3505.9 (Q)
RAM.DQ18: U3509.9 (Q)
RAM.DQ19: U3513.9 (Q)
RAM.DQ20: U3502.9 (Q)
RAM.DQ21: U3506.9 (Q)
RAM.DQ22: U3510.9 (Q)
RAM.DQ23: U3514.9 (Q)
RAM.DQ24: U3503.9 (Q)
RAM.DQ25: U3507.9 (Q)
RAM.DQ26: U3511.9 (Q)
RAM.DQ27: U3515.9 (Q)
RAM.DQ28: U3504.9 (Q)
RAM.DQ29: U3508.9 (Q)
RAM.DQ30: U3512.9 (Q)
RAM.DQ31: U3516.9 (Q)
RAM.WE2~: U3501.10 (WE), U3502.10 (WE), U3505.10 (WE), U3506.10 (WE), U3509.10 (WE), U3510.10 (WE), U3513.10 (WE), U3514.10 (WE)
RAM.WE3~: U3503.10 (WE), U3504.10 (WE), U3507.10 (WE), U3508.10 (WE), U3511.10 (WE), U3512.10 (WE), U3515.10 (WE), U3516.10 (WE)
