Datamuseum-DK/R1000.HwDoc/Schematics/IOC/pg_36.kicad_sch

## KiCad design Schematics/IOC/pg_36.kicad_sch (2023-01-10)

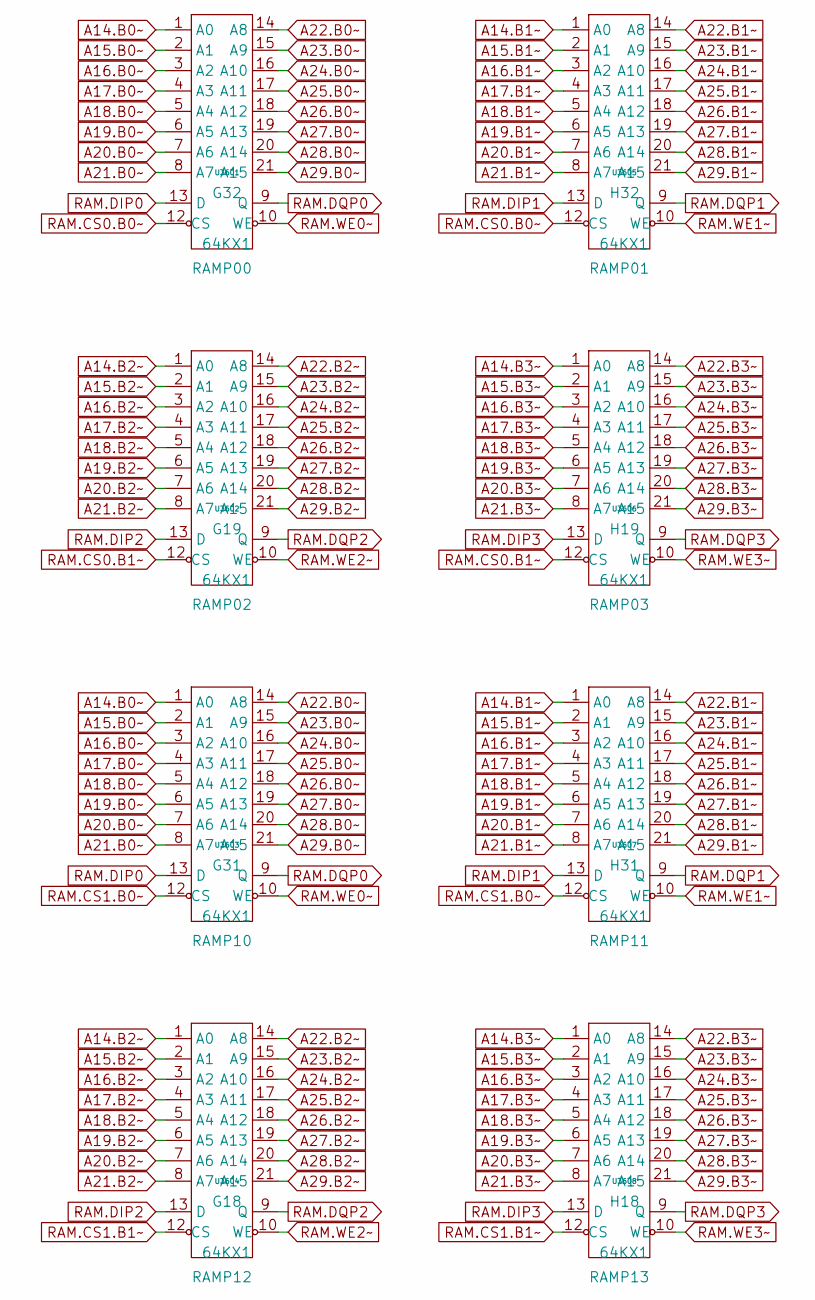
[picture p383: schematic pg_36.kicad_sch]

Parts:
U3601, U3602, U3603, U3604, U3605, U3606, U3607, U3608: 64KX1

Connections:
A14.B0~: U3601.1 (A0), U3603.1 (A0)
A14.B1~: U3605.1 (A0), U3607.1 (A0)
A14.B2~: U3602.1 (A0), U3604.1 (A0)
A14.B3~: U3606.1 (A0), U3608.1 (A0)
A15.B0~: U3601.2 (A1), U3603.2 (A1)
A15.B1~: U3605.2 (A1), U3607.2 (A1)
A15.B2~: U3602.2 (A1), U3604.2 (A1)
A15.B3~: U3606.2 (A1), U3608.2 (A1)
A16.B0~: U3601.3 (A2), U3603.3 (A2)
A16.B1~: U3605.3 (A2), U3607.3 (A2)
A16.B2~: U3602.3 (A2), U3604.3 (A2)
A16.B3~: U3606.3 (A2), U3608.3 (A2)
A17.B0~: U3601.4 (A3), U3603.4 (A3)
A17.B1~: U3605.4 (A3), U3607.4 (A3)
A17.B2~: U3602.4 (A3), U3604.4 (A3)
A17.B3~: U3606.4 (A3), U3608.4 (A3)
A18.B0~: U3601.5 (A4), U3603.5 (A4)
A18.B1~: U3605.5 (A4), U3607.5 (A4)
A18.B2~: U3602.5 (A4), U3604.5 (A4)
A18.B3~: U3606.5 (A4), U3608.5 (A4)
A19.B0~: U3601.6 (A5), U3603.6 (A5)
A19.B1~: U3605.6 (A5), U3607.6 (A5)
A19.B2~: U3602.6 (A5), U3604.6 (A5)
A19.B3~: U3606.6 (A5), U3608.6 (A5)
A20.B0~: U3601.7 (A6), U3603.7 (A6)
A20.B1~: U3605.7 (A6), U3607.7 (A6)
A20.B2~: U3602.7 (A6), U3604.7 (A6)
A20.B3~: U3606.7 (A6), U3608.7 (A6)
A21.B0~: U3601.8 (A7), U3603.8 (A7)
A21.B1~: U3605.8 (A7), U3607.8 (A7)
A21.B2~: U3602.8 (A7), U3604.8 (A7)
A21.B3~: U3606.8 (A7), U3608.8 (A7)
A22.B0~: U3601.14 (A8), U3603.14 (A8)
A22.B1~: U3605.14 (A8), U3607.14 (A8)
A22.B2~: U3602.14 (A8), U3604.14 (A8)
A22.B3~: U3606.14 (A8), U3608.14 (A8)
A23.B0~: U3601.15 (A9), U3603.15 (A9)
A23.B1~: U3605.15 (A9), U3607.15 (A9)
A23.B2~: U3602.15 (A9), U3604.15 (A9)
A23.B3~: U3606.15 (A9), U3608.15 (A9)
A24.B0~: U3601.16 (A10), U3603.16 (A10)
A24.B1~: U3605.16 (A10), U3607.16 (A10)
A24.B2~: U3602.16 (A10), U3604.16 (A10)
A24.B3~: U3606.16 (A10), U3608.16 (A10)
A25.B0~: U3601.17 (A11), U3603.17 (A11)
A25.B1~: U3605.17 (A11), U3607.17 (A11)
A25.B2~: U3602.17 (A11), U3604.17 (A11)
A25.B3~: U3606.17 (A11), U3608.17 (A11)
A26.B0~: U3601.18 (A12), U3603.18 (A12)
A26.B1~: U3605.18 (A12), U3607.18 (A12)
A26.B2~: U3602.18 (A12), U3604.18 (A12)
A26.B3~: U3606.18 (A12), U3608.18 (A12)
A27.B0~: U3601.19 (A13), U3603.19 (A13)
A27.B1~: U3605.19 (A13), U3607.19 (A13)
A27.B2~: U3602.19 (A13), U3604.19 (A13)
A27.B3~: U3606.19 (A13), U3608.19 (A13)
A28.B0~: U3601.20 (A14), U3603.20 (A14)
A28.B1~: U3605.20 (A14), U3607.20 (A14)
A28.B2~: U3602.20 (A14), U3604.20 (A14)
A28.B3~: U3606.20 (A14), U3608.20 (A14)
A29.B0~: U3601.21 (A15), U3603.21 (A15)
A29.B1~: U3605.21 (A15), U3607.21 (A15)
A29.B2~: U3602.21 (A15), U3604.21 (A15)
A29.B3~: U3606.21 (A15), U3608.21 (A15)
RAM.CS0.B0~: U3601.12 (CS), U3605.12 (CS)
RAM.CS0.B1~: U3602.12 (CS), U3606.12 (CS)
RAM.CS1.B0~: U3603.12 (CS), U3607.12 (CS)
RAM.CS1.B1~: U3604.12 (CS), U3608.12 (CS)
RAM.DIP0: U3601.13 (D), U3603.13 (D)
RAM.DIP1: U3605.13 (D), U3607.13 (D)
RAM.DIP2: U3602.13 (D), U3604.13 (D)
RAM.DIP3: U3606.13 (D), U3608.13 (D)
RAM.DQP0: U3601.9 (Q), U3603.9 (Q)
RAM.DQP1: U3605.9 (Q), U3607.9 (Q)
RAM.DQP2: U3602.9 (Q), U3604.9 (Q)
RAM.DQP3: U3606.9 (Q), U3608.9 (Q)
RAM.WE0~: U3601.10 (WE), U3603.10 (WE)
RAM.WE1~: U3605.10 (WE), U3607.10 (WE)
RAM.WE2~: U3602.10 (WE), U3604.10 (WE)
RAM.WE3~: U3606.10 (WE), U3608.10 (WE)
