Datamuseum-DK/R1000.HwDoc/Schematics/IOC/pg_40.kicad_sch

## KiCad design Schematics/IOC/pg_40.kicad_sch (2023-01-10)

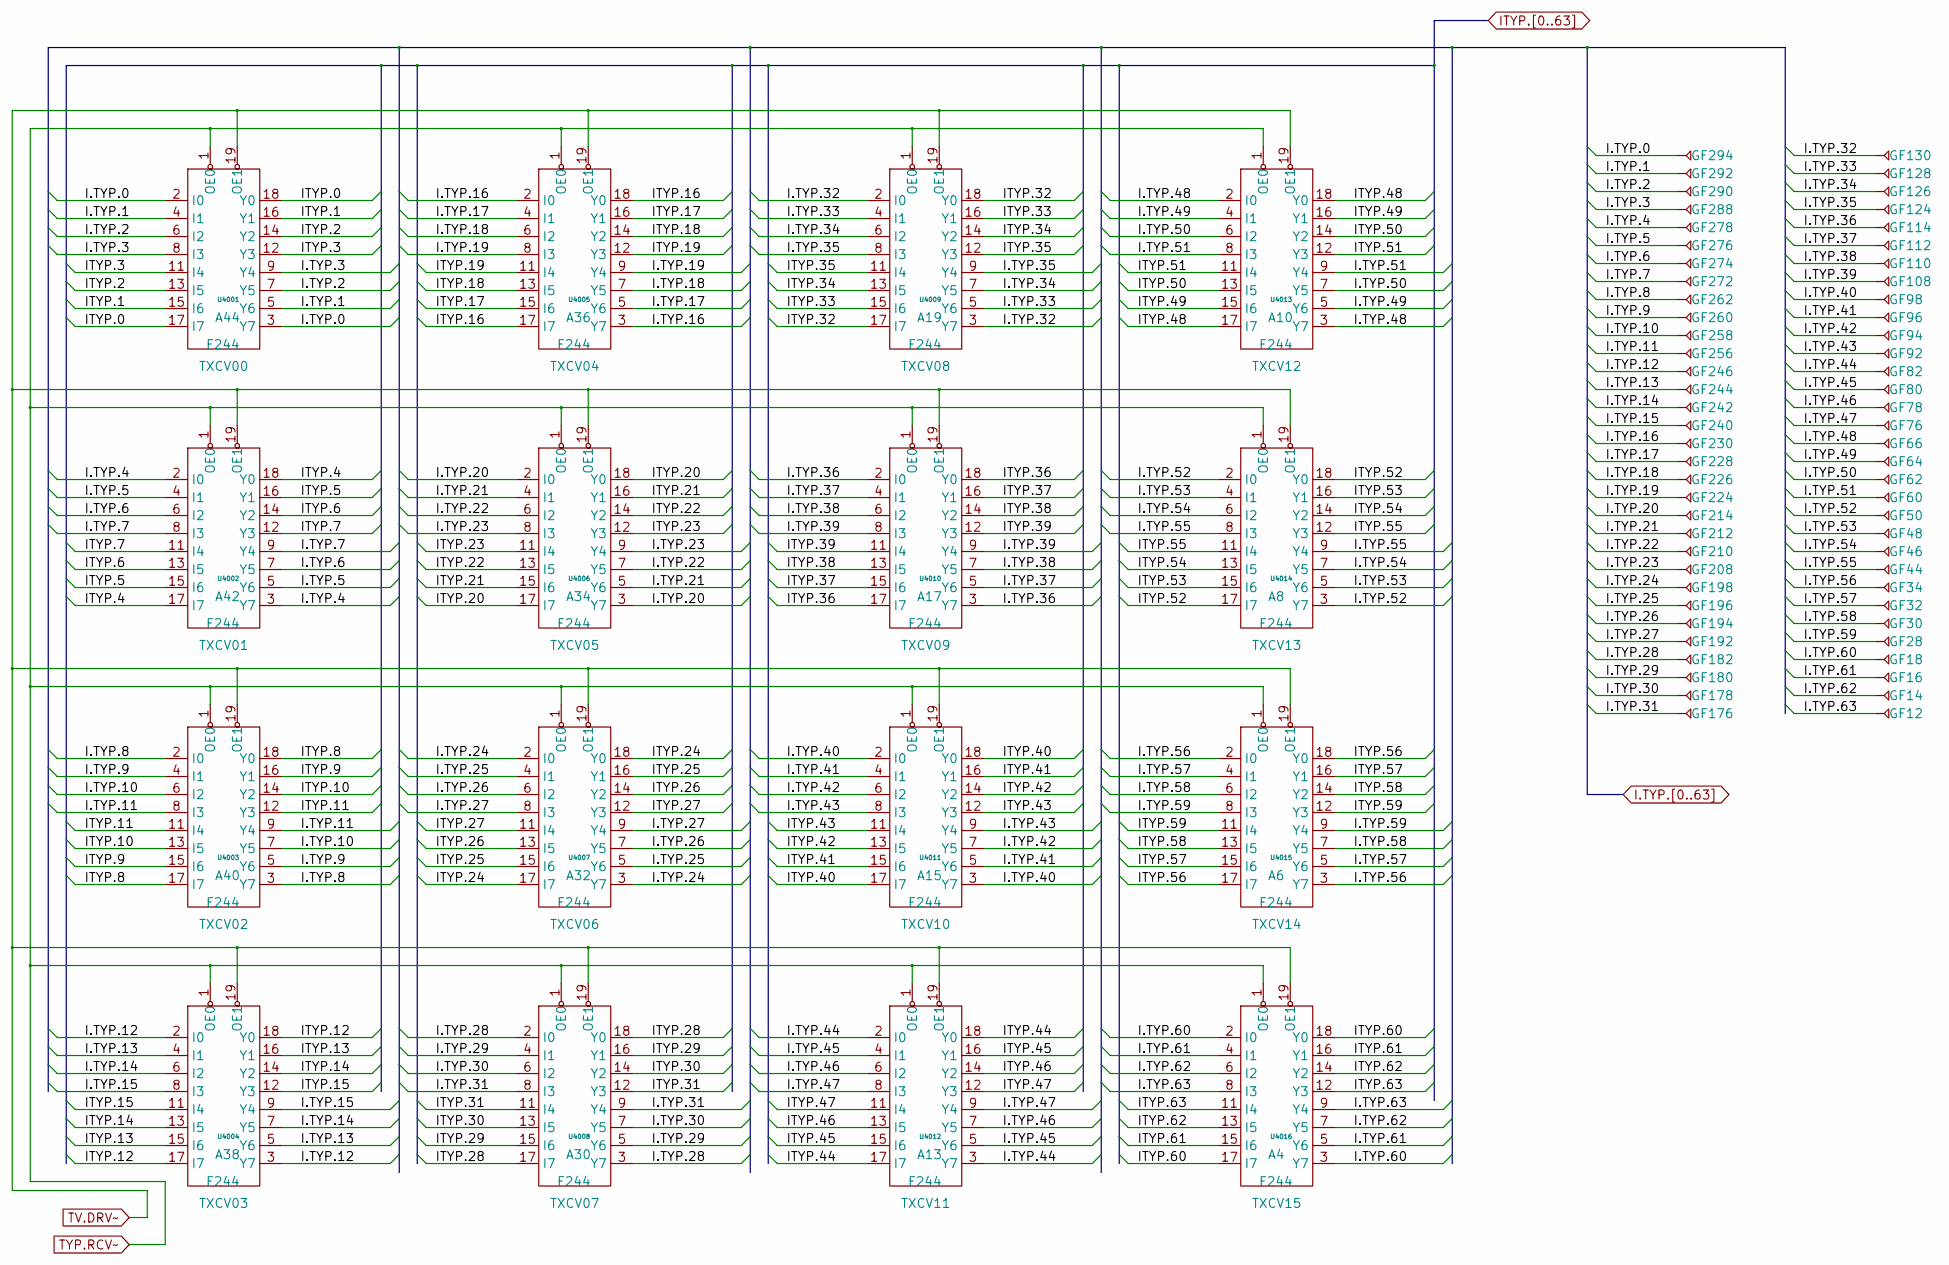
[picture p384: schematic pg_40.kicad_sch]

Parts:
GF12, GF14, GF16, GF18, GF28, GF30, GF32, GF34, GF44, GF46, GF48, GF50, GF60, GF62, GF64, GF66, GF76, GF78, GF80, GF82, GF92, GF94, GF96, GF98, GF108, GF110, GF112, GF114, GF124, GF126, GF128, GF130, GF176, GF178, GF180, GF182, GF192, GF194, GF196, GF198, GF208, GF210, GF212, GF214, GF224, GF226, GF228, GF230, GF240, GF242, GF244, GF246, GF256, GF258, GF260, GF262, GF272, GF274, GF276, GF278, GF288, GF290, GF292, GF294: GF
U4001, U4002, U4003, U4004, U4005, U4006, U4007, U4008, U4009, U4010, U4011, U4012, U4013, U4014, U4015, U4016: F244

Connections:
I.TYP.0: GF294.1, U4001.2 (I0), U4001.3 (Y7)
I.TYP.1: GF292.1, U4001.4 (I1), U4001.5 (Y6)
I.TYP.2: GF290.1, U4001.6 (I2), U4001.7 (Y5)
I.TYP.3: GF288.1, U4001.8 (I3), U4001.9 (Y4)
I.TYP.4: GF278.1, U4002.2 (I0), U4002.3 (Y7)
I.TYP.5: GF276.1, U4002.4 (I1), U4002.5 (Y6)
I.TYP.6: GF274.1, U4002.6 (I2), U4002.7 (Y5)
I.TYP.7: GF272.1, U4002.8 (I3), U4002.9 (Y4)
I.TYP.8: GF262.1, U4003.2 (I0), U4003.3 (Y7)
I.TYP.9: GF260.1, U4003.4 (I1), U4003.5 (Y6)
I.TYP.10: GF258.1, U4003.6 (I2), U4003.7 (Y5)
I.TYP.11: GF256.1, U4003.8 (I3), U4003.9 (Y4)
I.TYP.12: GF246.1, U4004.2 (I0), U4004.3 (Y7)
I.TYP.13: GF244.1, U4004.4 (I1), U4004.5 (Y6)
I.TYP.14: GF242.1, U4004.6 (I2), U4004.7 (Y5)
I.TYP.15: GF240.1, U4004.8 (I3), U4004.9 (Y4)
I.TYP.16: GF230.1, U4005.2 (I0), U4005.3 (Y7)
I.TYP.17: GF228.1, U4005.4 (I1), U4005.5 (Y6)
I.TYP.18: GF226.1, U4005.6 (I2), U4005.7 (Y5)
I.TYP.19: GF224.1, U4005.8 (I3), U4005.9 (Y4)
I.TYP.20: GF214.1, U4006.2 (I0), U4006.3 (Y7)
I.TYP.21: GF212.1, U4006.4 (I1), U4006.5 (Y6)
I.TYP.22: GF210.1, U4006.6 (I2), U4006.7 (Y5)
I.TYP.23: GF208.1, U4006.8 (I3), U4006.9 (Y4)
I.TYP.24: GF198.1, U4007.2 (I0), U4007.3 (Y7)
I.TYP.25: GF196.1, U4007.4 (I1), U4007.5 (Y6)
I.TYP.26: GF194.1, U4007.6 (I2), U4007.7 (Y5)
I.TYP.27: GF192.1, U4007.8 (I3), U4007.9 (Y4)
I.TYP.28: GF182.1, U4008.2 (I0), U4008.3 (Y7)
I.TYP.29: GF180.1, U4008.4 (I1), U4008.5 (Y6)
I.TYP.30: GF178.1, U4008.6 (I2), U4008.7 (Y5)
I.TYP.31: GF176.1, U4008.8 (I3), U4008.9 (Y4)
I.TYP.32: GF130.1, U4009.2 (I0), U4009.3 (Y7)
I.TYP.33: GF128.1, U4009.4 (I1), U4009.5 (Y6)
I.TYP.34: GF126.1, U4009.6 (I2), U4009.7 (Y5)
I.TYP.35: GF124.1, U4009.8 (I3), U4009.9 (Y4)
I.TYP.36: GF114.1, U4010.2 (I0), U4010.3 (Y7)
I.TYP.37: GF112.1, U4010.4 (I1), U4010.5 (Y6)
I.TYP.38: GF110.1, U4010.6 (I2), U4010.7 (Y5)
I.TYP.39: GF108.1, U4010.8 (I3), U4010.9 (Y4)
I.TYP.40: GF98.1, U4011.2 (I0), U4011.3 (Y7)
I.TYP.41: GF96.1, U4011.4 (I1), U4011.5 (Y6)
I.TYP.42: GF94.1, U4011.6 (I2), U4011.7 (Y5)
I.TYP.43: GF92.1, U4011.8 (I3), U4011.9 (Y4)
I.TYP.44: GF82.1, U4012.2 (I0), U4012.3 (Y7)
I.TYP.45: GF80.1, U4012.4 (I1), U4012.5 (Y6)
I.TYP.46: GF78.1, U4012.6 (I2), U4012.7 (Y5)
I.TYP.47: GF76.1, U4012.8 (I3), U4012.9 (Y4)
I.TYP.48: GF66.1, U4013.2 (I0), U4013.3 (Y7)
I.TYP.49: GF64.1, U4013.4 (I1), U4013.5 (Y6)
I.TYP.50: GF62.1, U4013.6 (I2), U4013.7 (Y5)
I.TYP.51: GF60.1, U4013.8 (I3), U4013.9 (Y4)
I.TYP.52: GF50.1, U4014.2 (I0), U4014.3 (Y7)
I.TYP.53: GF48.1, U4014.4 (I1), U4014.5 (Y6)
I.TYP.54: GF46.1, U4014.6 (I2), U4014.7 (Y5)
I.TYP.55: GF44.1, U4014.8 (I3), U4014.9 (Y4)
I.TYP.56: GF34.1, U4015.2 (I0), U4015.3 (Y7)
I.TYP.57: GF32.1, U4015.4 (I1), U4015.5 (Y6)
I.TYP.58: GF30.1, U4015.6 (I2), U4015.7 (Y5)
I.TYP.59: GF28.1, U4015.8 (I3), U4015.9 (Y4)
I.TYP.60: GF18.1, U4016.2 (I0), U4016.3 (Y7)
I.TYP.61: GF16.1, U4016.4 (I1), U4016.5 (Y6)
I.TYP.62: GF14.1, U4016.6 (I2), U4016.7 (Y5)
I.TYP.63: GF12.1, U4016.8 (I3), U4016.9 (Y4)
ITYP.0: U4001.17 (I7), U4001.18 (Y0)
ITYP.1: U4001.15 (I6), U4001.16 (Y1)
ITYP.2: U4001.13 (I5), U4001.14 (Y2)
ITYP.3: U4001.11 (I4), U4001.12 (Y3)
ITYP.4: U4002.17 (I7), U4002.18 (Y0)
ITYP.5: U4002.15 (I6), U4002.16 (Y1)
ITYP.6: U4002.13 (I5), U4002.14 (Y2)
ITYP.7: U4002.11 (I4), U4002.12 (Y3)
ITYP.8: U4003.17 (I7), U4003.18 (Y0)
ITYP.9: U4003.15 (I6), U4003.16 (Y1)
ITYP.10: U4003.13 (I5), U4003.14 (Y2)
ITYP.11: U4003.11 (I4), U4003.12 (Y3)
ITYP.12: U4004.17 (I7), U4004.18 (Y0)
ITYP.13: U4004.15 (I6), U4004.16 (Y1)
ITYP.14: U4004.13 (I5), U4004.14 (Y2)
ITYP.15: U4004.11 (I4), U4004.12 (Y3)
ITYP.16: U4005.17 (I7), U4005.18 (Y0)
ITYP.17: U4005.15 (I6), U4005.16 (Y1)
ITYP.18: U4005.13 (I5), U4005.14 (Y2)
ITYP.19: U4005.11 (I4), U4005.12 (Y3)
ITYP.20: U4006.17 (I7), U4006.18 (Y0)
ITYP.21: U4006.15 (I6), U4006.16 (Y1)
ITYP.22: U4006.13 (I5), U4006.14 (Y2)
ITYP.23: U4006.11 (I4), U4006.12 (Y3)
ITYP.24: U4007.17 (I7), U4007.18 (Y0)
ITYP.25: U4007.15 (I6), U4007.16 (Y1)
ITYP.26: U4007.13 (I5), U4007.14 (Y2)
ITYP.27: U4007.11 (I4), U4007.12 (Y3)
ITYP.28: U4008.17 (I7), U4008.18 (Y0)
ITYP.29: U4008.15 (I6), U4008.16 (Y1)
ITYP.30: U4008.13 (I5), U4008.14 (Y2)
ITYP.31: U4008.11 (I4), U4008.12 (Y3)
ITYP.32: U4009.17 (I7), U4009.18 (Y0)
ITYP.33: U4009.15 (I6), U4009.16 (Y1)
ITYP.34: U4009.13 (I5), U4009.14 (Y2)
ITYP.35: U4009.11 (I4), U4009.12 (Y3)
ITYP.36: U4010.17 (I7), U4010.18 (Y0)
ITYP.37: U4010.15 (I6), U4010.16 (Y1)
ITYP.38: U4010.13 (I5), U4010.14 (Y2)
ITYP.39: U4010.11 (I4), U4010.12 (Y3)
ITYP.40: U4011.17 (I7), U4011.18 (Y0)
ITYP.41: U4011.15 (I6), U4011.16 (Y1)
ITYP.42: U4011.13 (I5), U4011.14 (Y2)
ITYP.43: U4011.11 (I4), U4011.12 (Y3)
ITYP.44: U4012.17 (I7), U4012.18 (Y0)
ITYP.45: U4012.15 (I6), U4012.16 (Y1)
ITYP.46: U4012.13 (I5), U4012.14 (Y2)
ITYP.47: U4012.11 (I4), U4012.12 (Y3)
ITYP.48: U4013.17 (I7), U4013.18 (Y0)
ITYP.49: U4013.15 (I6), U4013.16 (Y1)
ITYP.50: U4013.13 (I5), U4013.14 (Y2)
ITYP.51: U4013.11 (I4), U4013.12 (Y3)
ITYP.52: U4014.17 (I7), U4014.18 (Y0)
ITYP.53: U4014.15 (I6), U4014.16 (Y1)
ITYP.54: U4014.13 (I5), U4014.14 (Y2)
ITYP.55: U4014.11 (I4), U4014.12 (Y3)
ITYP.56: U4015.17 (I7), U4015.18 (Y0)
ITYP.57: U4015.15 (I6), U4015.16 (Y1)
ITYP.58: U4015.13 (I5), U4015.14 (Y2)
ITYP.59: U4015.11 (I4), U4015.12 (Y3)
ITYP.60: U4016.17 (I7), U4016.18 (Y0)
ITYP.61: U4016.15 (I6), U4016.16 (Y1)
ITYP.62: U4016.13 (I5), U4016.14 (Y2)
ITYP.63: U4016.11 (I4), U4016.12 (Y3)
TV.DRV~: U4001.19 (OE1), U4002.19 (OE1), U4003.19 (OE1), U4004.19 (OE1), U4005.19 (OE1), U4006.19 (OE1), U4007.19 (OE1), U4008.19 (OE1), U4009.19 (OE1), U4010.19 (OE1), U4011.19 (OE1), U4012.19 (OE1), U4013.19 (OE1), U4014.19 (OE1), U4015.19 (OE1), U4016.19 (OE1)
TYP.RCV~: U4001.1 (OE0), U4002.1 (OE0), U4003.1 (OE0), U4004.1 (OE0), U4005.1 (OE0), U4006.1 (OE0), U4007.1 (OE0), U4008.1 (OE0), U4009.1 (OE0), U4010.1 (OE0), U4011.1 (OE0), U4012.1 (OE0), U4013.1 (OE0), U4014.1 (OE0), U4015.1 (OE0), U4016.1 (OE0)
