Datamuseum-DK/R1000.HwDoc/Schematics/IOC/pg_41.kicad_sch

## KiCad design Schematics/IOC/pg_41.kicad_sch (2023-01-10)

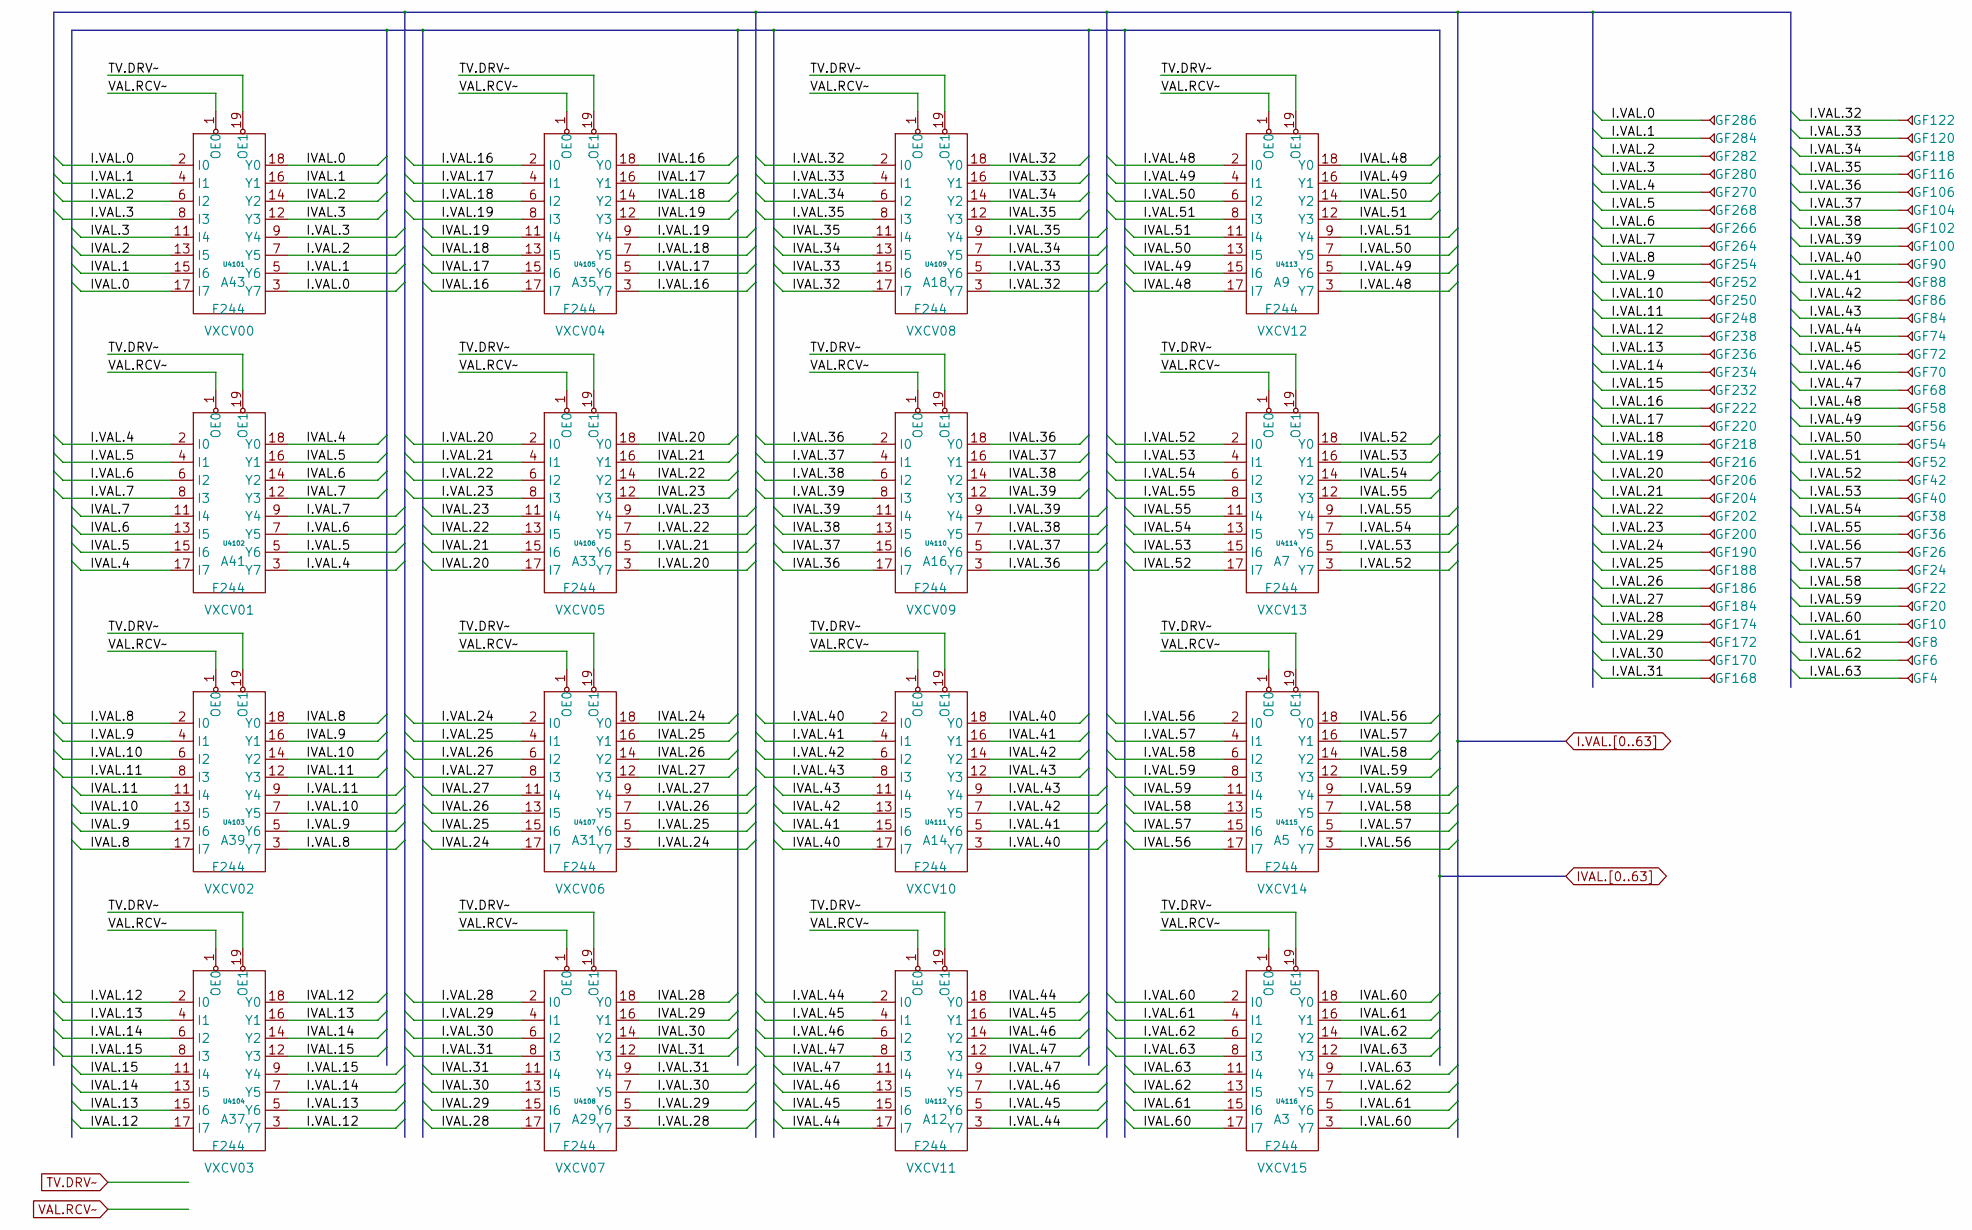
[picture p385: schematic pg_41.kicad_sch]

Parts:
GF4, GF6, GF8, GF10, GF20, GF22, GF24, GF26, GF36, GF38, GF40, GF42, GF52, GF54, GF56, GF58, GF68, GF70, GF72, GF74, GF84, GF86, GF88, GF90, GF100, GF102, GF104, GF106, GF116, GF118, GF120, GF122, GF168, GF170, GF172, GF174, GF184, GF186, GF188, GF190, GF200, GF202, GF204, GF206, GF216, GF218, GF220, GF222, GF232, GF234, GF236, GF238, GF248, GF250, GF252, GF254, GF264, GF266, GF268, GF270, GF280, GF282, GF284, GF286: GF
U4101, U4102, U4103, U4104, U4105, U4106, U4107, U4108, U4109, U4110, U4111, U4112, U4113, U4114, U4115, U4116: F244

Connections:
I.VAL.0: GF286.1, U4101.2 (I0), U4101.3 (Y7)
I.VAL.1: GF284.1, U4101.4 (I1), U4101.5 (Y6)
I.VAL.2: GF282.1, U4101.6 (I2), U4101.7 (Y5)
I.VAL.3: GF280.1, U4101.8 (I3), U4101.9 (Y4)
I.VAL.4: GF270.1, U4102.2 (I0), U4102.3 (Y7)
I.VAL.5: GF268.1, U4102.4 (I1), U4102.5 (Y6)
I.VAL.6: GF266.1, U4102.6 (I2), U4102.7 (Y5)
I.VAL.7: GF264.1, U4102.8 (I3), U4102.9 (Y4)
I.VAL.8: GF254.1, U4103.2 (I0), U4103.3 (Y7)
I.VAL.9: GF252.1, U4103.4 (I1), U4103.5 (Y6)
I.VAL.10: GF250.1, U4103.6 (I2), U4103.7 (Y5)
I.VAL.11: GF248.1, U4103.8 (I3), U4103.9 (Y4)
I.VAL.12: GF238.1, U4104.2 (I0), U4104.3 (Y7)
I.VAL.13: GF236.1, U4104.4 (I1), U4104.5 (Y6)
I.VAL.14: GF234.1, U4104.6 (I2), U4104.7 (Y5)
I.VAL.15: GF232.1, U4104.8 (I3), U4104.9 (Y4)
I.VAL.16: GF222.1, U4105.2 (I0), U4105.3 (Y7)
I.VAL.17: GF220.1, U4105.4 (I1), U4105.5 (Y6)
I.VAL.18: GF218.1, U4105.6 (I2), U4105.7 (Y5)
I.VAL.19: GF216.1, U4105.8 (I3), U4105.9 (Y4)
I.VAL.20: GF206.1, U4106.2 (I0), U4106.3 (Y7)
I.VAL.21: GF204.1, U4106.4 (I1), U4106.5 (Y6)
I.VAL.22: GF202.1, U4106.6 (I2), U4106.7 (Y5)
I.VAL.23: GF200.1, U4106.8 (I3), U4106.9 (Y4)
I.VAL.24: GF190.1, U4107.2 (I0), U4107.3 (Y7)
I.VAL.25: GF188.1, U4107.4 (I1), U4107.5 (Y6)
I.VAL.26: GF186.1, U4107.6 (I2), U4107.7 (Y5)
I.VAL.27: GF184.1, U4107.8 (I3), U4107.9 (Y4)
I.VAL.28: GF174.1, U4108.2 (I0), U4108.3 (Y7)
I.VAL.29: GF172.1, U4108.4 (I1), U4108.5 (Y6)
I.VAL.30: GF170.1, U4108.6 (I2), U4108.7 (Y5)
I.VAL.31: GF168.1, U4108.8 (I3), U4108.9 (Y4)
I.VAL.32: GF122.1, U4109.2 (I0), U4109.3 (Y7)
I.VAL.33: GF120.1, U4109.4 (I1), U4109.5 (Y6)
I.VAL.34: GF118.1, U4109.6 (I2), U4109.7 (Y5)
I.VAL.35: GF116.1, U4109.8 (I3), U4109.9 (Y4)
I.VAL.36: GF106.1, U4110.2 (I0), U4110.3 (Y7)
I.VAL.37: GF104.1, U4110.4 (I1), U4110.5 (Y6)
I.VAL.38: GF102.1, U4110.6 (I2), U4110.7 (Y5)
I.VAL.39: GF100.1, U4110.8 (I3), U4110.9 (Y4)
I.VAL.40: GF90.1, U4111.2 (I0), U4111.3 (Y7)
I.VAL.41: GF88.1, U4111.4 (I1), U4111.5 (Y6)
I.VAL.42: GF86.1, U4111.6 (I2), U4111.7 (Y5)
I.VAL.43: GF84.1, U4111.8 (I3), U4111.9 (Y4)
I.VAL.44: GF74.1, U4112.2 (I0), U4112.3 (Y7)
I.VAL.45: GF72.1, U4112.4 (I1), U4112.5 (Y6)
I.VAL.46: GF70.1, U4112.6 (I2), U4112.7 (Y5)
I.VAL.47: GF68.1, U4112.8 (I3), U4112.9 (Y4)
I.VAL.48: GF58.1, U4113.2 (I0), U4113.3 (Y7)
I.VAL.49: GF56.1, U4113.4 (I1), U4113.5 (Y6)
I.VAL.50: GF54.1, U4113.6 (I2), U4113.7 (Y5)
I.VAL.51: GF52.1, U4113.8 (I3), U4113.9 (Y4)
I.VAL.52: GF42.1, U4114.2 (I0), U4114.3 (Y7)
I.VAL.53: GF40.1, U4114.4 (I1), U4114.5 (Y6)
I.VAL.54: GF38.1, U4114.6 (I2), U4114.7 (Y5)
I.VAL.55: GF36.1, U4114.8 (I3), U4114.9 (Y4)
I.VAL.56: GF26.1, U4115.2 (I0), U4115.3 (Y7)
I.VAL.57: GF24.1, U4115.4 (I1), U4115.5 (Y6)
I.VAL.58: GF22.1, U4115.6 (I2), U4115.7 (Y5)
I.VAL.59: GF20.1, U4115.8 (I3), U4115.9 (Y4)
I.VAL.60: GF10.1, U4116.2 (I0), U4116.3 (Y7)
I.VAL.61: GF8.1, U4116.4 (I1), U4116.5 (Y6)
I.VAL.62: GF6.1, U4116.6 (I2), U4116.7 (Y5)
I.VAL.63: GF4.1, U4116.8 (I3), U4116.9 (Y4)
IVAL.0: U4101.17 (I7), U4101.18 (Y0)
IVAL.1: U4101.15 (I6), U4101.16 (Y1)
IVAL.2: U4101.13 (I5), U4101.14 (Y2)
IVAL.3: U4101.11 (I4), U4101.12 (Y3)
IVAL.4: U4102.17 (I7), U4102.18 (Y0)
IVAL.5: U4102.15 (I6), U4102.16 (Y1)
IVAL.6: U4102.13 (I5), U4102.14 (Y2)
IVAL.7: U4102.11 (I4), U4102.12 (Y3)
IVAL.8: U4103.17 (I7), U4103.18 (Y0)
IVAL.9: U4103.15 (I6), U4103.16 (Y1)
IVAL.10: U4103.13 (I5), U4103.14 (Y2)
IVAL.11: U4103.11 (I4), U4103.12 (Y3)
IVAL.12: U4104.17 (I7), U4104.18 (Y0)
IVAL.13: U4104.15 (I6), U4104.16 (Y1)
IVAL.14: U4104.13 (I5), U4104.14 (Y2)
IVAL.15: U4104.11 (I4), U4104.12 (Y3)
IVAL.16: U4105.17 (I7), U4105.18 (Y0)
IVAL.17: U4105.15 (I6), U4105.16 (Y1)
IVAL.18: U4105.13 (I5), U4105.14 (Y2)
IVAL.19: U4105.11 (I4), U4105.12 (Y3)
IVAL.20: U4106.17 (I7), U4106.18 (Y0)
IVAL.21: U4106.15 (I6), U4106.16 (Y1)
IVAL.22: U4106.13 (I5), U4106.14 (Y2)
IVAL.23: U4106.11 (I4), U4106.12 (Y3)
IVAL.24: U4107.17 (I7), U4107.18 (Y0)
IVAL.25: U4107.15 (I6), U4107.16 (Y1)
IVAL.26: U4107.13 (I5), U4107.14 (Y2)
IVAL.27: U4107.11 (I4), U4107.12 (Y3)
IVAL.28: U4108.17 (I7), U4108.18 (Y0)
IVAL.29: U4108.15 (I6), U4108.16 (Y1)
IVAL.30: U4108.13 (I5), U4108.14 (Y2)
IVAL.31: U4108.11 (I4), U4108.12 (Y3)
IVAL.32: U4109.17 (I7), U4109.18 (Y0)
IVAL.33: U4109.15 (I6), U4109.16 (Y1)
IVAL.34: U4109.13 (I5), U4109.14 (Y2)
IVAL.35: U4109.11 (I4), U4109.12 (Y3)
IVAL.36: U4110.17 (I7), U4110.18 (Y0)
IVAL.37: U4110.15 (I6), U4110.16 (Y1)
IVAL.38: U4110.13 (I5), U4110.14 (Y2)
IVAL.39: U4110.11 (I4), U4110.12 (Y3)
IVAL.40: U4111.17 (I7), U4111.18 (Y0)
IVAL.41: U4111.15 (I6), U4111.16 (Y1)
IVAL.42: U4111.13 (I5), U4111.14 (Y2)
IVAL.43: U4111.11 (I4), U4111.12 (Y3)
IVAL.44: U4112.17 (I7), U4112.18 (Y0)
IVAL.45: U4112.15 (I6), U4112.16 (Y1)
IVAL.46: U4112.13 (I5), U4112.14 (Y2)
IVAL.47: U4112.11 (I4), U4112.12 (Y3)
IVAL.48: U4113.17 (I7), U4113.18 (Y0)
IVAL.49: U4113.15 (I6), U4113.16 (Y1)
IVAL.50: U4113.13 (I5), U4113.14 (Y2)
IVAL.51: U4113.11 (I4), U4113.12 (Y3)
IVAL.52: U4114.17 (I7), U4114.18 (Y0)
IVAL.53: U4114.15 (I6), U4114.16 (Y1)
IVAL.54: U4114.13 (I5), U4114.14 (Y2)
IVAL.55: U4114.11 (I4), U4114.12 (Y3)
IVAL.56: U4115.17 (I7), U4115.18 (Y0)
IVAL.57: U4115.15 (I6), U4115.16 (Y1)
IVAL.58: U4115.13 (I5), U4115.14 (Y2)
IVAL.59: U4115.11 (I4), U4115.12 (Y3)
IVAL.60: U4116.17 (I7), U4116.18 (Y0)
IVAL.61: U4116.15 (I6), U4116.16 (Y1)
IVAL.62: U4116.13 (I5), U4116.14 (Y2)
IVAL.63: U4116.11 (I4), U4116.12 (Y3)
TV.DRV~: U4101.19 (OE1), U4102.19 (OE1), U4103.19 (OE1), U4104.19 (OE1), U4105.19 (OE1), U4106.19 (OE1), U4107.19 (OE1), U4108.19 (OE1), U4109.19 (OE1), U4110.19 (OE1), U4111.19 (OE1), U4112.19 (OE1), U4113.19 (OE1), U4114.19 (OE1), U4115.19 (OE1), U4116.19 (OE1)
VAL.RCV~: U4101.1 (OE0), U4102.1 (OE0), U4103.1 (OE0), U4104.1 (OE0), U4105.1 (OE0), U4106.1 (OE0), U4107.1 (OE0), U4108.1 (OE0), U4109.1 (OE0), U4110.1 (OE0), U4111.1 (OE0), U4112.1 (OE0), U4113.1 (OE0), U4114.1 (OE0), U4115.1 (OE0), U4116.1 (OE0)
