Datamuseum-DK/R1000.HwDoc/Schematics/IOC/pg_42.kicad_sch

## KiCad design Schematics/IOC/pg_42.kicad_sch (2023-01-10)

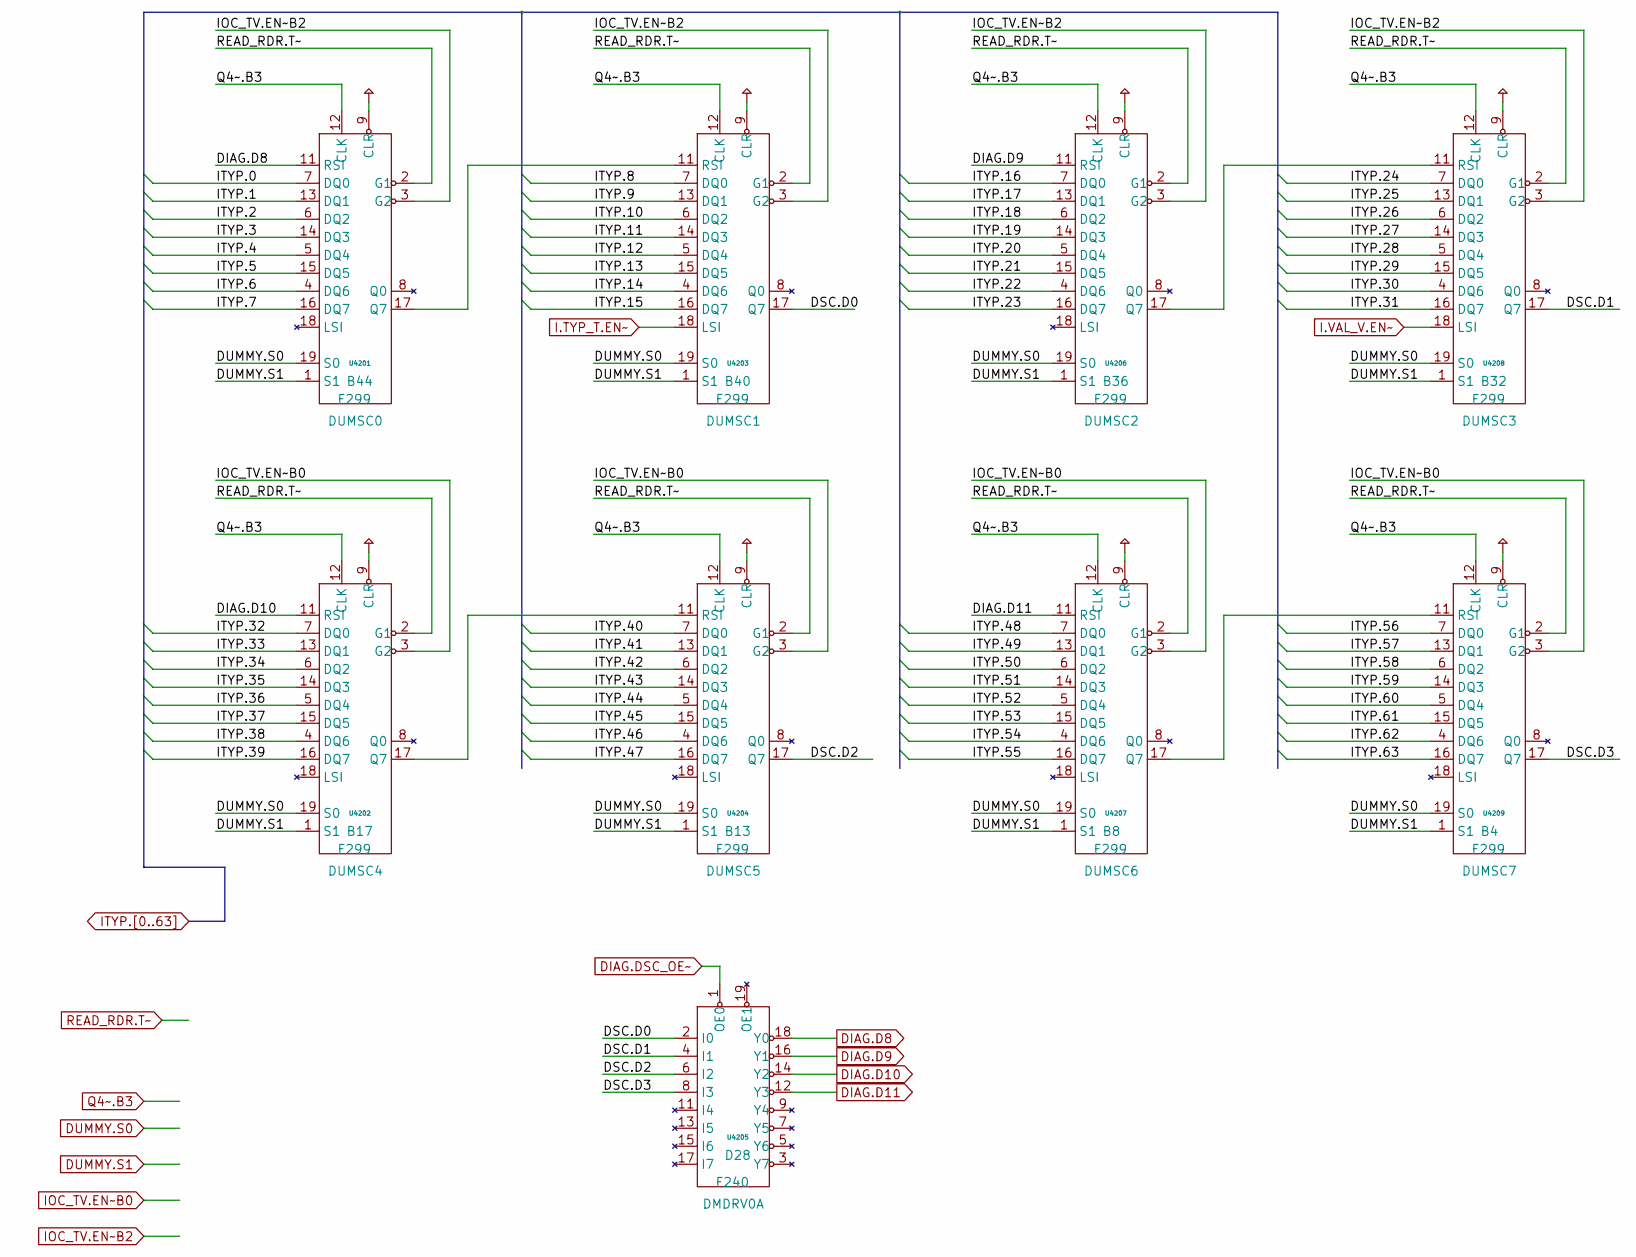
[picture p386: schematic pg_42.kicad_sch]

Parts:
U4201, U4202, U4203, U4204, U4206, U4207, U4208, U4209: F299
U4205: F240

Connections:
DIAG.D8: U4201.11 (RSI), U4205.18 (Y0)
DIAG.D9: U4205.16 (Y1), U4206.11 (RSI)
DIAG.D10: U4202.11 (RSI), U4205.14 (Y2)
DIAG.D11: U4205.12 (Y3), U4207.11 (RSI)
DIAG.DSC_OE~: U4205.1 (OE0)
DSC.D0: U4203.17 (Q7), U4205.2 (I0)
DSC.D1: U4205.4 (I1), U4208.17 (Q7)
DSC.D2: U4204.17 (Q7), U4205.6 (I2)
DSC.D3: U4205.8 (I3), U4209.17 (Q7)
DUMMY.S0: U4201.19 (S0), U4202.19 (S0), U4203.19 (S0), U4204.19 (S0), U4206.19 (S0), U4207.19 (S0), U4208.19 (S0), U4209.19 (S0)
DUMMY.S1: U4201.1 (S1), U4202.1 (S1), U4203.1 (S1), U4204.1 (S1), U4206.1 (S1), U4207.1 (S1), U4208.1 (S1), U4209.1 (S1)
I.TYP_T.EN~: U4203.18 (LSI)
I.VAL_V.EN~: U4208.18 (LSI)
IOC_TV.EN~B0: U4202.3 (G2), U4204.3 (G2), U4207.3 (G2), U4209.3 (G2)
IOC_TV.EN~B2: U4201.3 (G2), U4203.3 (G2), U4206.3 (G2), U4208.3 (G2)
ITYP.0: U4201.7 (DQ0)
ITYP.1: U4201.13 (DQ1)
ITYP.2: U4201.6 (DQ2)
ITYP.3: U4201.14 (DQ3)
ITYP.4: U4201.5 (DQ4)
ITYP.5: U4201.15 (DQ5)
ITYP.6: U4201.4 (DQ6)
ITYP.7: U4201.16 (DQ7)
ITYP.8: U4203.7 (DQ0)
ITYP.9: U4203.13 (DQ1)
ITYP.10: U4203.6 (DQ2)
ITYP.11: U4203.14 (DQ3)
ITYP.12: U4203.5 (DQ4)
ITYP.13: U4203.15 (DQ5)
ITYP.14: U4203.4 (DQ6)
ITYP.15: U4203.16 (DQ7)
ITYP.16: U4206.7 (DQ0)
ITYP.17: U4206.13 (DQ1)
ITYP.18: U4206.6 (DQ2)
ITYP.19: U4206.14 (DQ3)
ITYP.20: U4206.5 (DQ4)
ITYP.21: U4206.15 (DQ5)
ITYP.22: U4206.4 (DQ6)
ITYP.23: U4206.16 (DQ7)
ITYP.24: U4208.7 (DQ0)
ITYP.25: U4208.13 (DQ1)
ITYP.26: U4208.6 (DQ2)
ITYP.27: U4208.14 (DQ3)
ITYP.28: U4208.5 (DQ4)
ITYP.29: U4208.15 (DQ5)
ITYP.30: U4208.4 (DQ6)
ITYP.31: U4208.16 (DQ7)
ITYP.32: U4202.7 (DQ0)
ITYP.33: U4202.13 (DQ1)
ITYP.34: U4202.6 (DQ2)
ITYP.35: U4202.14 (DQ3)
ITYP.36: U4202.5 (DQ4)
ITYP.37: U4202.15 (DQ5)
ITYP.38: U4202.4 (DQ6)
ITYP.39: U4202.16 (DQ7)
ITYP.40: U4204.7 (DQ0)
ITYP.41: U4204.13 (DQ1)
ITYP.42: U4204.6 (DQ2)
ITYP.43: U4204.14 (DQ3)
ITYP.44: U4204.5 (DQ4)
ITYP.45: U4204.15 (DQ5)
ITYP.46: U4204.4 (DQ6)
ITYP.47: U4204.16 (DQ7)
ITYP.48: U4207.7 (DQ0)
ITYP.49: U4207.13 (DQ1)
ITYP.50: U4207.6 (DQ2)
ITYP.51: U4207.14 (DQ3)
ITYP.52: U4207.5 (DQ4)
ITYP.53: U4207.15 (DQ5)
ITYP.54: U4207.4 (DQ6)
ITYP.55: U4207.16 (DQ7)
ITYP.56: U4209.7 (DQ0)
ITYP.57: U4209.13 (DQ1)
ITYP.58: U4209.6 (DQ2)
ITYP.59: U4209.14 (DQ3)
ITYP.60: U4209.5 (DQ4)
ITYP.61: U4209.15 (DQ5)
ITYP.62: U4209.4 (DQ6)
ITYP.63: U4209.16 (DQ7)
unnamed: U4201.17 (Q7), U4203.11 (RSI)
unnamed: U4202.17 (Q7), U4204.11 (RSI)
unnamed: U4206.17 (Q7), U4208.11 (RSI)
unnamed: U4207.17 (Q7), U4209.11 (RSI)
PU: U4201.9 (CLR), U4202.9 (CLR), U4203.9 (CLR), U4204.9 (CLR), U4206.9 (CLR), U4207.9 (CLR), U4208.9 (CLR), U4209.9 (CLR)
Q4~.B3: U4201.12 (CLK), U4202.12 (CLK), U4203.12 (CLK), U4204.12 (CLK), U4206.12 (CLK), U4207.12 (CLK), U4208.12 (CLK), U4209.12 (CLK)
READ_RDR.T~: U4201.2 (G1), U4202.2 (G1), U4203.2 (G1), U4204.2 (G1), U4206.2 (G1), U4207.2 (G1), U4208.2 (G1), U4209.2 (G1)
