Datamuseum-DK/R1000.HwDoc/Schematics/IOC/pg_43.kicad_sch

## KiCad design Schematics/IOC/pg_43.kicad_sch (2023-01-10)

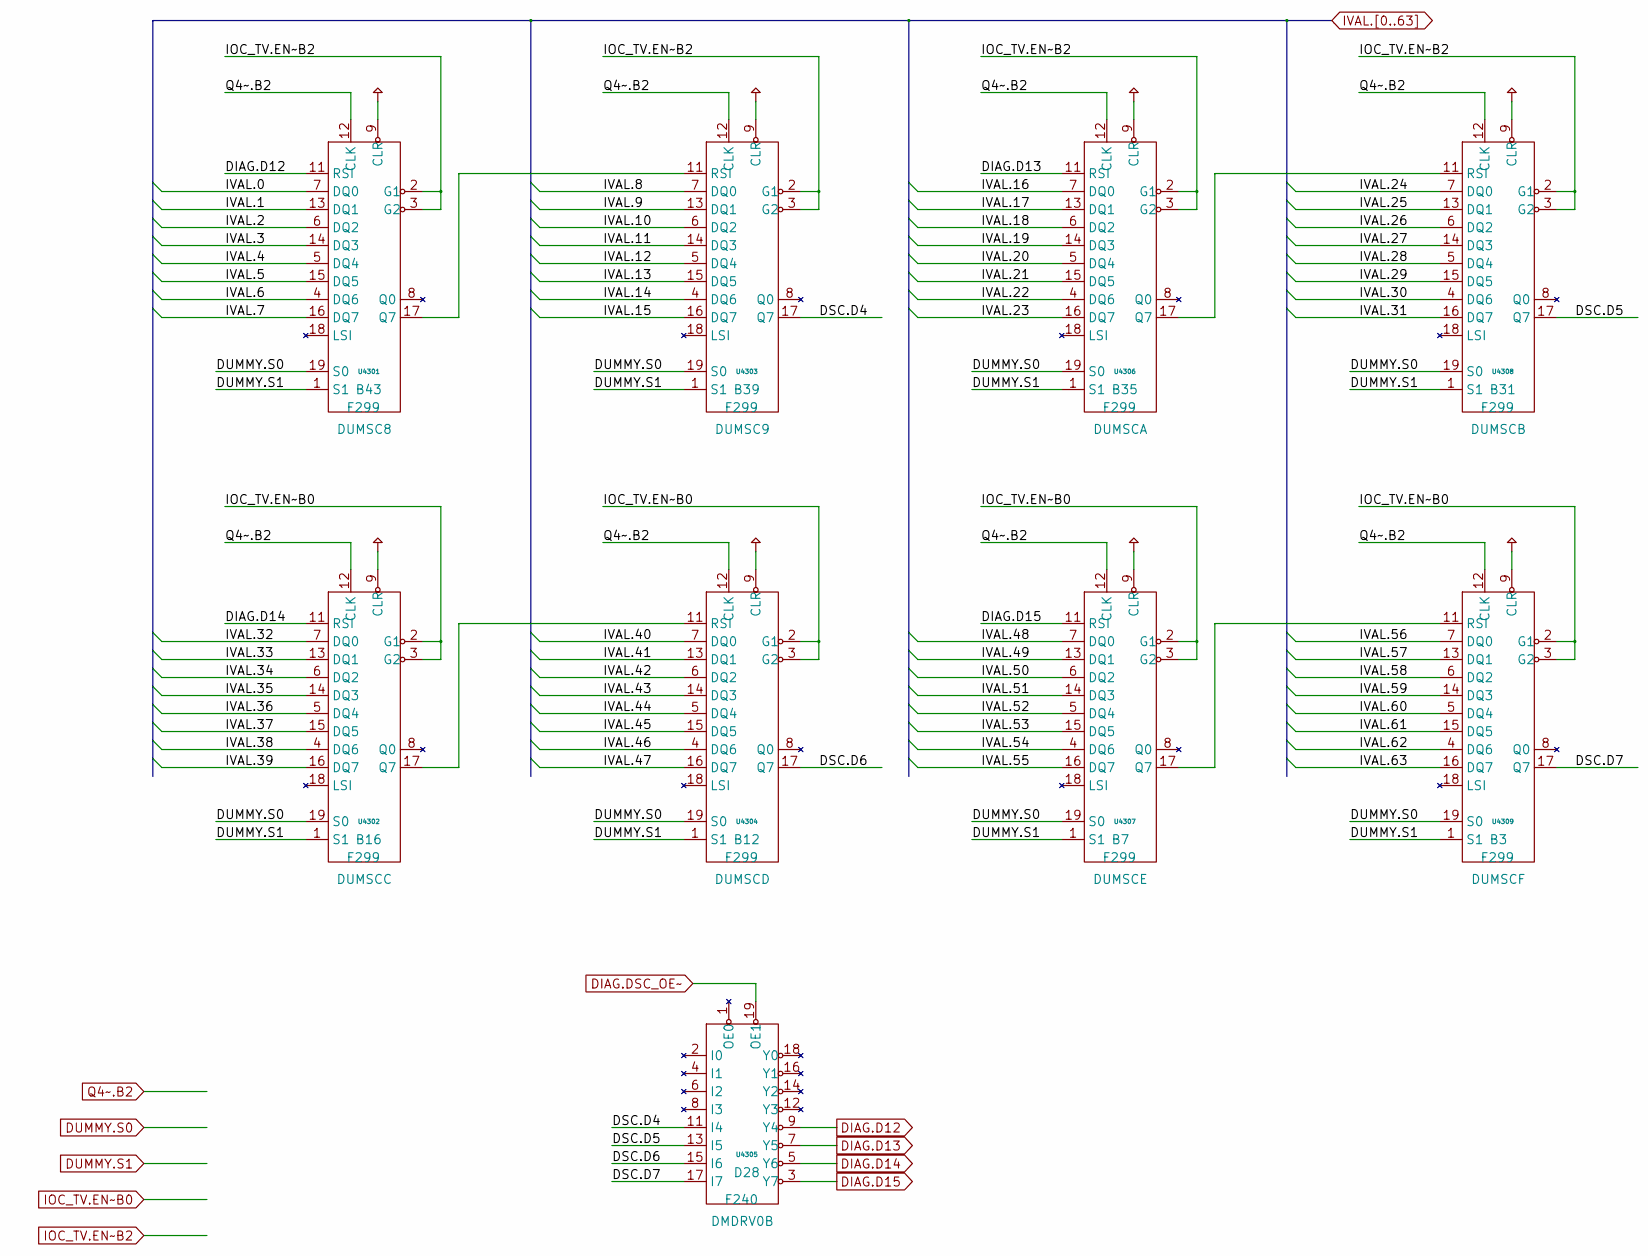
[picture p387: schematic pg_43.kicad_sch]

Parts:
U4301, U4302, U4303, U4304, U4306, U4307, U4308, U4309: F299
U4305: F240

Connections:
DIAG.D12: U4301.11 (RSI), U4305.9 (Y4)
DIAG.D13: U4305.7 (Y5), U4306.11 (RSI)
DIAG.D14: U4302.11 (RSI), U4305.5 (Y6)
DIAG.D15: U4305.3 (Y7), U4307.11 (RSI)
DIAG.DSC_OE~: U4305.19 (OE1)
DSC.D4: U4303.17 (Q7), U4305.11 (I4)
DSC.D5: U4305.13 (I5), U4308.17 (Q7)
DSC.D6: U4304.17 (Q7), U4305.15 (I6)
DSC.D7: U4305.17 (I7), U4309.17 (Q7)
DUMMY.S0: U4301.19 (S0), U4302.19 (S0), U4303.19 (S0), U4304.19 (S0), U4306.19 (S0), U4307.19 (S0), U4308.19 (S0), U4309.19 (S0)
DUMMY.S1: U4301.1 (S1), U4302.1 (S1), U4303.1 (S1), U4304.1 (S1), U4306.1 (S1), U4307.1 (S1), U4308.1 (S1), U4309.1 (S1)
IOC_TV.EN~B0: U4302.2 (G1), U4302.3 (G2), U4304.2 (G1), U4304.3 (G2), U4307.2 (G1), U4307.3 (G2), U4309.2 (G1), U4309.3 (G2)
IOC_TV.EN~B2: U4301.2 (G1), U4301.3 (G2), U4303.2 (G1), U4303.3 (G2), U4306.2 (G1), U4306.3 (G2), U4308.2 (G1), U4308.3 (G2)
IVAL.0: U4301.7 (DQ0)
IVAL.1: U4301.13 (DQ1)
IVAL.2: U4301.6 (DQ2)
IVAL.3: U4301.14 (DQ3)
IVAL.4: U4301.5 (DQ4)
IVAL.5: U4301.15 (DQ5)
IVAL.6: U4301.4 (DQ6)
IVAL.7: U4301.16 (DQ7)
IVAL.8: U4303.7 (DQ0)
IVAL.9: U4303.13 (DQ1)
IVAL.10: U4303.6 (DQ2)
IVAL.11: U4303.14 (DQ3)
IVAL.12: U4303.5 (DQ4)
IVAL.13: U4303.15 (DQ5)
IVAL.14: U4303.4 (DQ6)
IVAL.15: U4303.16 (DQ7)
IVAL.16: U4306.7 (DQ0)
IVAL.17: U4306.13 (DQ1)
IVAL.18: U4306.6 (DQ2)
IVAL.19: U4306.14 (DQ3)
IVAL.20: U4306.5 (DQ4)
IVAL.21: U4306.15 (DQ5)
IVAL.22: U4306.4 (DQ6)
IVAL.23: U4306.16 (DQ7)
IVAL.24: U4308.7 (DQ0)
IVAL.25: U4308.13 (DQ1)
IVAL.26: U4308.6 (DQ2)
IVAL.27: U4308.14 (DQ3)
IVAL.28: U4308.5 (DQ4)
IVAL.29: U4308.15 (DQ5)
IVAL.30: U4308.4 (DQ6)
IVAL.31: U4308.16 (DQ7)
IVAL.32: U4302.7 (DQ0)
IVAL.33: U4302.13 (DQ1)
IVAL.34: U4302.6 (DQ2)
IVAL.35: U4302.14 (DQ3)
IVAL.36: U4302.5 (DQ4)
IVAL.37: U4302.15 (DQ5)
IVAL.38: U4302.4 (DQ6)
IVAL.39: U4302.16 (DQ7)
IVAL.40: U4304.7 (DQ0)
IVAL.41: U4304.13 (DQ1)
IVAL.42: U4304.6 (DQ2)
IVAL.43: U4304.14 (DQ3)
IVAL.44: U4304.5 (DQ4)
IVAL.45: U4304.15 (DQ5)
IVAL.46: U4304.4 (DQ6)
IVAL.47: U4304.16 (DQ7)
IVAL.48: U4307.7 (DQ0)
IVAL.49: U4307.13 (DQ1)
IVAL.50: U4307.6 (DQ2)
IVAL.51: U4307.14 (DQ3)
IVAL.52: U4307.5 (DQ4)
IVAL.53: U4307.15 (DQ5)
IVAL.54: U4307.4 (DQ6)
IVAL.55: U4307.16 (DQ7)
IVAL.56: U4309.7 (DQ0)
IVAL.57: U4309.13 (DQ1)
IVAL.58: U4309.6 (DQ2)
IVAL.59: U4309.14 (DQ3)
IVAL.60: U4309.5 (DQ4)
IVAL.61: U4309.15 (DQ5)
IVAL.62: U4309.4 (DQ6)
IVAL.63: U4309.16 (DQ7)
unnamed: U4301.17 (Q7), U4303.11 (RSI)
unnamed: U4302.17 (Q7), U4304.11 (RSI)
unnamed: U4306.17 (Q7), U4308.11 (RSI)
unnamed: U4307.17 (Q7), U4309.11 (RSI)
PU: U4301.9 (CLR), U4302.9 (CLR), U4303.9 (CLR), U4304.9 (CLR), U4306.9 (CLR), U4307.9 (CLR), U4308.9 (CLR), U4309.9 (CLR)
Q4~.B2: U4301.12 (CLK), U4302.12 (CLK), U4303.12 (CLK), U4304.12 (CLK), U4306.12 (CLK), U4307.12 (CLK), U4308.12 (CLK), U4309.12 (CLK)
