Datamuseum-DK/R1000.HwDoc/Schematics/IOC/pg_44.kicad_sch

## KiCad design Schematics/IOC/pg_44.kicad_sch (2023-01-10)

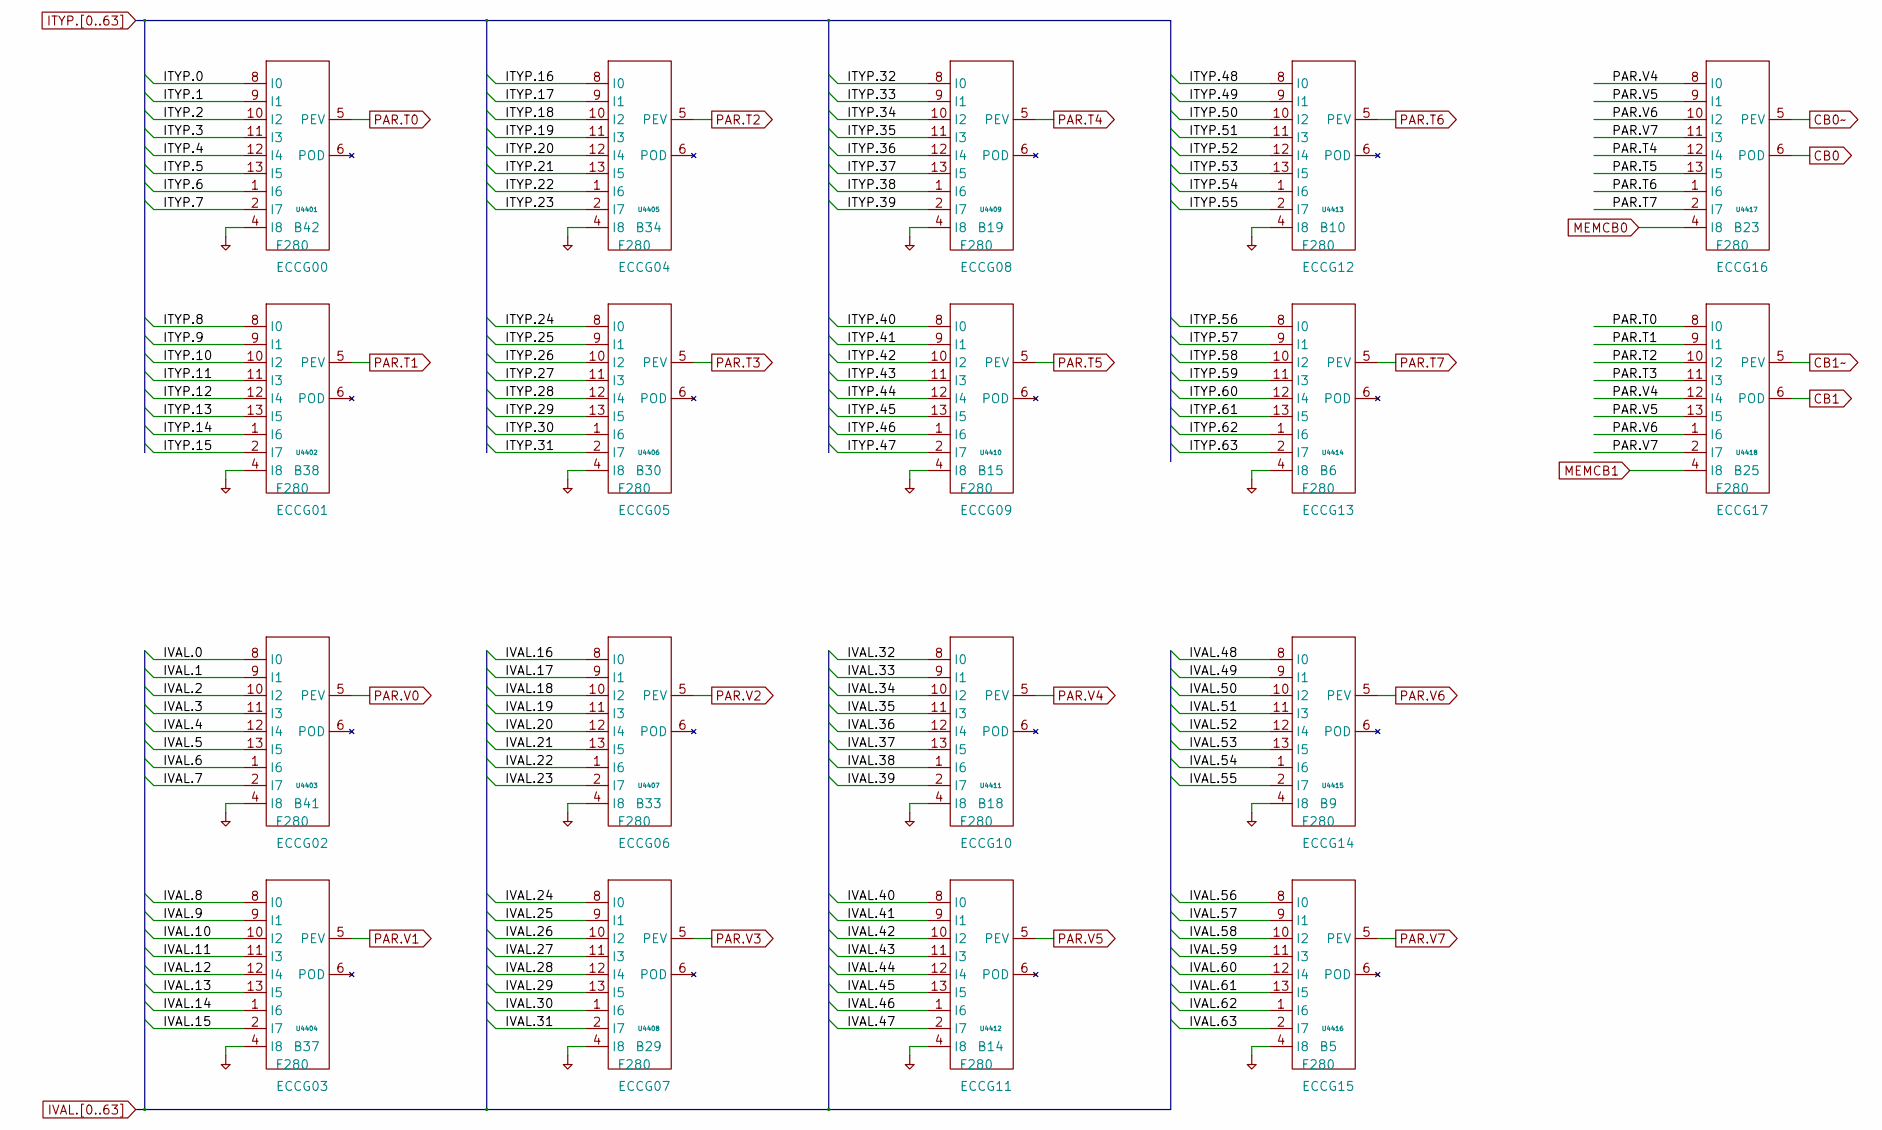
[picture p388: schematic pg_44.kicad_sch]

Parts:
U4401, U4402, U4403, U4404, U4405, U4406, U4407, U4408, U4409, U4410, U4411, U4412, U4413, U4414, U4415, U4416, U4417, U4418: F280

Connections:
CB0: U4417.6 (POD)
CB0~: U4417.5 (PEV)
CB1: U4418.6 (POD)
CB1~: U4418.5 (PEV)
ITYP.0: U4401.8 (I0)
ITYP.1: U4401.9 (I1)
ITYP.2: U4401.10 (I2)
ITYP.3: U4401.11 (I3)
ITYP.4: U4401.12 (I4)
ITYP.5: U4401.13 (I5)
ITYP.6: U4401.1 (I6)
ITYP.7: U4401.2 (I7)
ITYP.8: U4402.8 (I0)
ITYP.9: U4402.9 (I1)
ITYP.10: U4402.10 (I2)
ITYP.11: U4402.11 (I3)
ITYP.12: U4402.12 (I4)
ITYP.13: U4402.13 (I5)
ITYP.14: U4402.1 (I6)
ITYP.15: U4402.2 (I7)
ITYP.16: U4405.8 (I0)
ITYP.17: U4405.9 (I1)
ITYP.18: U4405.10 (I2)
ITYP.19: U4405.11 (I3)
ITYP.20: U4405.12 (I4)
ITYP.21: U4405.13 (I5)
ITYP.22: U4405.1 (I6)
ITYP.23: U4405.2 (I7)
ITYP.24: U4406.8 (I0)
ITYP.25: U4406.9 (I1)
ITYP.26: U4406.10 (I2)
ITYP.27: U4406.11 (I3)
ITYP.28: U4406.12 (I4)
ITYP.29: U4406.13 (I5)
ITYP.30: U4406.1 (I6)
ITYP.31: U4406.2 (I7)
ITYP.32: U4409.8 (I0)
ITYP.33: U4409.9 (I1)
ITYP.34: U4409.10 (I2)
ITYP.35: U4409.11 (I3)
ITYP.36: U4409.12 (I4)
ITYP.37: U4409.13 (I5)
ITYP.38: U4409.1 (I6)
ITYP.39: U4409.2 (I7)
ITYP.40: U4410.8 (I0)
ITYP.41: U4410.9 (I1)
ITYP.42: U4410.10 (I2)
ITYP.43: U4410.11 (I3)
ITYP.44: U4410.12 (I4)
ITYP.45: U4410.13 (I5)
ITYP.46: U4410.1 (I6)
ITYP.47: U4410.2 (I7)
ITYP.48: U4413.8 (I0)
ITYP.49: U4413.9 (I1)
ITYP.50: U4413.10 (I2)
ITYP.51: U4413.11 (I3)
ITYP.52: U4413.12 (I4)
ITYP.53: U4413.13 (I5)
ITYP.54: U4413.1 (I6)
ITYP.55: U4413.2 (I7)
ITYP.56: U4414.8 (I0)
ITYP.57: U4414.9 (I1)
ITYP.58: U4414.10 (I2)
ITYP.59: U4414.11 (I3)
ITYP.60: U4414.12 (I4)
ITYP.61: U4414.13 (I5)
ITYP.62: U4414.1 (I6)
ITYP.63: U4414.2 (I7)
IVAL.0: U4403.8 (I0)
IVAL.1: U4403.9 (I1)
IVAL.2: U4403.10 (I2)
IVAL.3: U4403.11 (I3)
IVAL.4: U4403.12 (I4)
IVAL.5: U4403.13 (I5)
IVAL.6: U4403.1 (I6)
IVAL.7: U4403.2 (I7)
IVAL.8: U4404.8 (I0)
IVAL.9: U4404.9 (I1)
IVAL.10: U4404.10 (I2)
IVAL.11: U4404.11 (I3)
IVAL.12: U4404.12 (I4)
IVAL.13: U4404.13 (I5)
IVAL.14: U4404.1 (I6)
IVAL.15: U4404.2 (I7)
IVAL.16: U4407.8 (I0)
IVAL.17: U4407.9 (I1)
IVAL.18: U4407.10 (I2)
IVAL.19: U4407.11 (I3)
IVAL.20: U4407.12 (I4)
IVAL.21: U4407.13 (I5)
IVAL.22: U4407.1 (I6)
IVAL.23: U4407.2 (I7)
IVAL.24: U4408.8 (I0)
IVAL.25: U4408.9 (I1)
IVAL.26: U4408.10 (I2)
IVAL.27: U4408.11 (I3)
IVAL.28: U4408.12 (I4)
IVAL.29: U4408.13 (I5)
IVAL.30: U4408.1 (I6)
IVAL.31: U4408.2 (I7)
IVAL.32: U4411.8 (I0)
IVAL.33: U4411.9 (I1)
IVAL.34: U4411.10 (I2)
IVAL.35: U4411.11 (I3)
IVAL.36: U4411.12 (I4)
IVAL.37: U4411.13 (I5)
IVAL.38: U4411.1 (I6)
IVAL.39: U4411.2 (I7)
IVAL.40: U4412.8 (I0)
IVAL.41: U4412.9 (I1)
IVAL.42: U4412.10 (I2)
IVAL.43: U4412.11 (I3)
IVAL.44: U4412.12 (I4)
IVAL.45: U4412.13 (I5)
IVAL.46: U4412.1 (I6)
IVAL.47: U4412.2 (I7)
IVAL.48: U4415.8 (I0)
IVAL.49: U4415.9 (I1)
IVAL.50: U4415.10 (I2)
IVAL.51: U4415.11 (I3)
IVAL.52: U4415.12 (I4)
IVAL.53: U4415.13 (I5)
IVAL.54: U4415.1 (I6)
IVAL.55: U4415.2 (I7)
IVAL.56: U4416.8 (I0)
IVAL.57: U4416.9 (I1)
IVAL.58: U4416.10 (I2)
IVAL.59: U4416.11 (I3)
IVAL.60: U4416.12 (I4)
IVAL.61: U4416.13 (I5)
IVAL.62: U4416.1 (I6)
IVAL.63: U4416.2 (I7)
MEMCB0: U4417.4 (I8)
MEMCB1: U4418.4 (I8)
PAR.T0: U4401.5 (PEV), U4418.8 (I0)
PAR.T1: U4402.5 (PEV), U4418.9 (I1)
PAR.T2: U4405.5 (PEV), U4418.10 (I2)
PAR.T3: U4406.5 (PEV), U4418.11 (I3)
PAR.T4: U4409.5 (PEV), U4417.12 (I4)
PAR.T5: U4410.5 (PEV), U4417.13 (I5)
PAR.T6: U4413.5 (PEV), U4417.1 (I6)
PAR.T7: U4414.5 (PEV), U4417.2 (I7)
PAR.V0: U4403.5 (PEV)
PAR.V1: U4404.5 (PEV)
PAR.V2: U4407.5 (PEV)
PAR.V3: U4408.5 (PEV)
PAR.V4: U4411.5 (PEV), U4417.8 (I0), U4418.12 (I4)
PAR.V5: U4412.5 (PEV), U4417.9 (I1), U4418.13 (I5)
PAR.V6: U4415.5 (PEV), U4417.10 (I2), U4418.1 (I6)
PAR.V7: U4416.5 (PEV), U4417.11 (I3), U4418.2 (I7)
PD: U4401.4 (I8), U4402.4 (I8), U4403.4 (I8), U4404.4 (I8), U4405.4 (I8), U4406.4 (I8), U4407.4 (I8), U4408.4 (I8), U4409.4 (I8), U4410.4 (I8), U4411.4 (I8), U4412.4 (I8), U4413.4 (I8), U4414.4 (I8), U4415.4 (I8), U4416.4 (I8)
