Datamuseum-DK/R1000.HwDoc/Schematics/IOC/pg_45.kicad_sch

## KiCad design Schematics/IOC/pg_45.kicad_sch (2023-01-10)

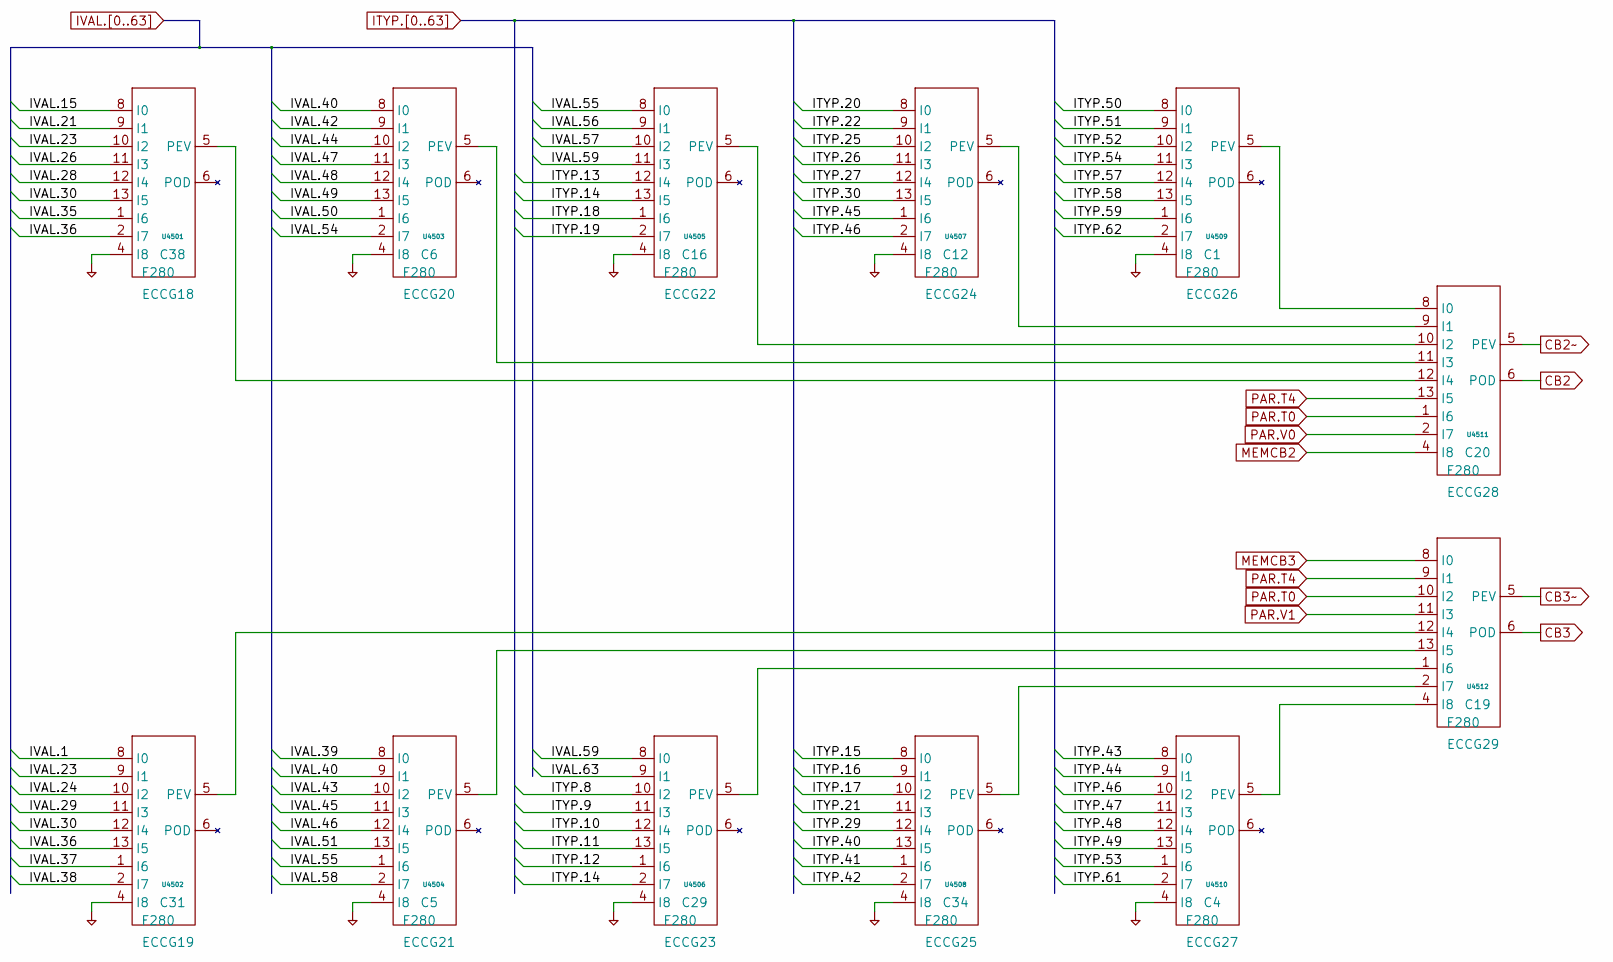
[picture p389: schematic pg_45.kicad_sch]

Parts:
U4501, U4502, U4503, U4504, U4505, U4506, U4507, U4508, U4509, U4510, U4511, U4512: F280

Connections:
CB2: U4511.6 (POD)
CB2~: U4511.5 (PEV)
CB3: U4512.6 (POD)
CB3~: U4512.5 (PEV)
ITYP.8: U4506.10 (I2)
ITYP.9: U4506.11 (I3)
ITYP.10: U4506.12 (I4)
ITYP.11: U4506.13 (I5)
ITYP.12: U4506.1 (I6)
ITYP.13: U4505.12 (I4)
ITYP.14: U4505.13 (I5), U4506.2 (I7)
ITYP.15: U4508.8 (I0)
ITYP.16: U4508.9 (I1)
ITYP.17: U4508.10 (I2)
ITYP.18: U4505.1 (I6)
ITYP.19: U4505.2 (I7)
ITYP.20: U4507.8 (I0)
ITYP.21: U4508.11 (I3)
ITYP.22: U4507.9 (I1)
ITYP.25: U4507.10 (I2)
ITYP.26: U4507.11 (I3)
ITYP.27: U4507.12 (I4)
ITYP.29: U4508.12 (I4)
ITYP.30: U4507.13 (I5)
ITYP.40: U4508.13 (I5)
ITYP.41: U4508.1 (I6)
ITYP.42: U4508.2 (I7)
ITYP.43: U4510.8 (I0)
ITYP.44: U4510.9 (I1)
ITYP.45: U4507.1 (I6)
ITYP.46: U4507.2 (I7), U4510.10 (I2)
ITYP.47: U4510.11 (I3)
ITYP.48: U4510.12 (I4)
ITYP.49: U4510.13 (I5)
ITYP.50: U4509.8 (I0)
ITYP.51: U4509.9 (I1)
ITYP.52: U4509.10 (I2)
ITYP.53: U4510.1 (I6)
ITYP.54: U4509.11 (I3)
ITYP.57: U4509.12 (I4)
ITYP.58: U4509.13 (I5)
ITYP.59: U4509.1 (I6)
ITYP.61: U4510.2 (I7)
ITYP.62: U4509.2 (I7)
IVAL.1: U4502.8 (I0)
IVAL.15: U4501.8 (I0)
IVAL.21: U4501.9 (I1)
IVAL.23: U4501.10 (I2), U4502.9 (I1)
IVAL.24: U4502.10 (I2)
IVAL.26: U4501.11 (I3)
IVAL.28: U4501.12 (I4)
IVAL.29: U4502.11 (I3)
IVAL.30: U4501.13 (I5), U4502.12 (I4)
IVAL.35: U4501.1 (I6)
IVAL.36: U4501.2 (I7), U4502.13 (I5)
IVAL.37: U4502.1 (I6)
IVAL.38: U4502.2 (I7)
IVAL.39: U4504.8 (I0)
IVAL.40: U4503.8 (I0), U4504.9 (I1)
IVAL.42: U4503.9 (I1)
IVAL.43: U4504.10 (I2)
IVAL.44: U4503.10 (I2)
IVAL.45: U4504.11 (I3)
IVAL.46: U4504.12 (I4)
IVAL.47: U4503.11 (I3)
IVAL.48: U4503.12 (I4)
IVAL.49: U4503.13 (I5)
IVAL.50: U4503.1 (I6)
IVAL.51: U4504.13 (I5)
IVAL.54: U4503.2 (I7)
IVAL.55: U4504.1 (I6), U4505.8 (I0)
IVAL.56: U4505.9 (I1)
IVAL.57: U4505.10 (I2)
IVAL.58: U4504.2 (I7)
IVAL.59: U4505.11 (I3), U4506.8 (I0)
IVAL.63: U4506.9 (I1)
MEMCB2: U4511.4 (I8)
MEMCB3: U4512.8 (I0)
unnamed: U4501.5 (PEV), U4511.12 (I4)
unnamed: U4502.5 (PEV), U4512.12 (I4)
unnamed: U4503.5 (PEV), U4511.11 (I3)
unnamed: U4504.5 (PEV), U4512.13 (I5)
unnamed: U4505.5 (PEV), U4511.10 (I2)
unnamed: U4506.5 (PEV), U4512.1 (I6)
unnamed: U4507.5 (PEV), U4511.9 (I1)
unnamed: U4508.5 (PEV), U4512.2 (I7)
unnamed: U4509.5 (PEV), U4511.8 (I0)
unnamed: U4510.5 (PEV), U4512.4 (I8)
PAR.T0: U4511.1 (I6), U4512.10 (I2)
PAR.T4: U4511.13 (I5), U4512.9 (I1)
PAR.V0: U4511.2 (I7)
PAR.V1: U4512.11 (I3)
PD: U4501.4 (I8), U4502.4 (I8), U4503.4 (I8), U4504.4 (I8), U4505.4 (I8), U4506.4 (I8), U4507.4 (I8), U4508.4 (I8), U4509.4 (I8), U4510.4 (I8)
