Datamuseum-DK/R1000.HwDoc/Schematics/IOC/pg_46.kicad_sch

## KiCad design Schematics/IOC/pg_46.kicad_sch (2023-01-10)

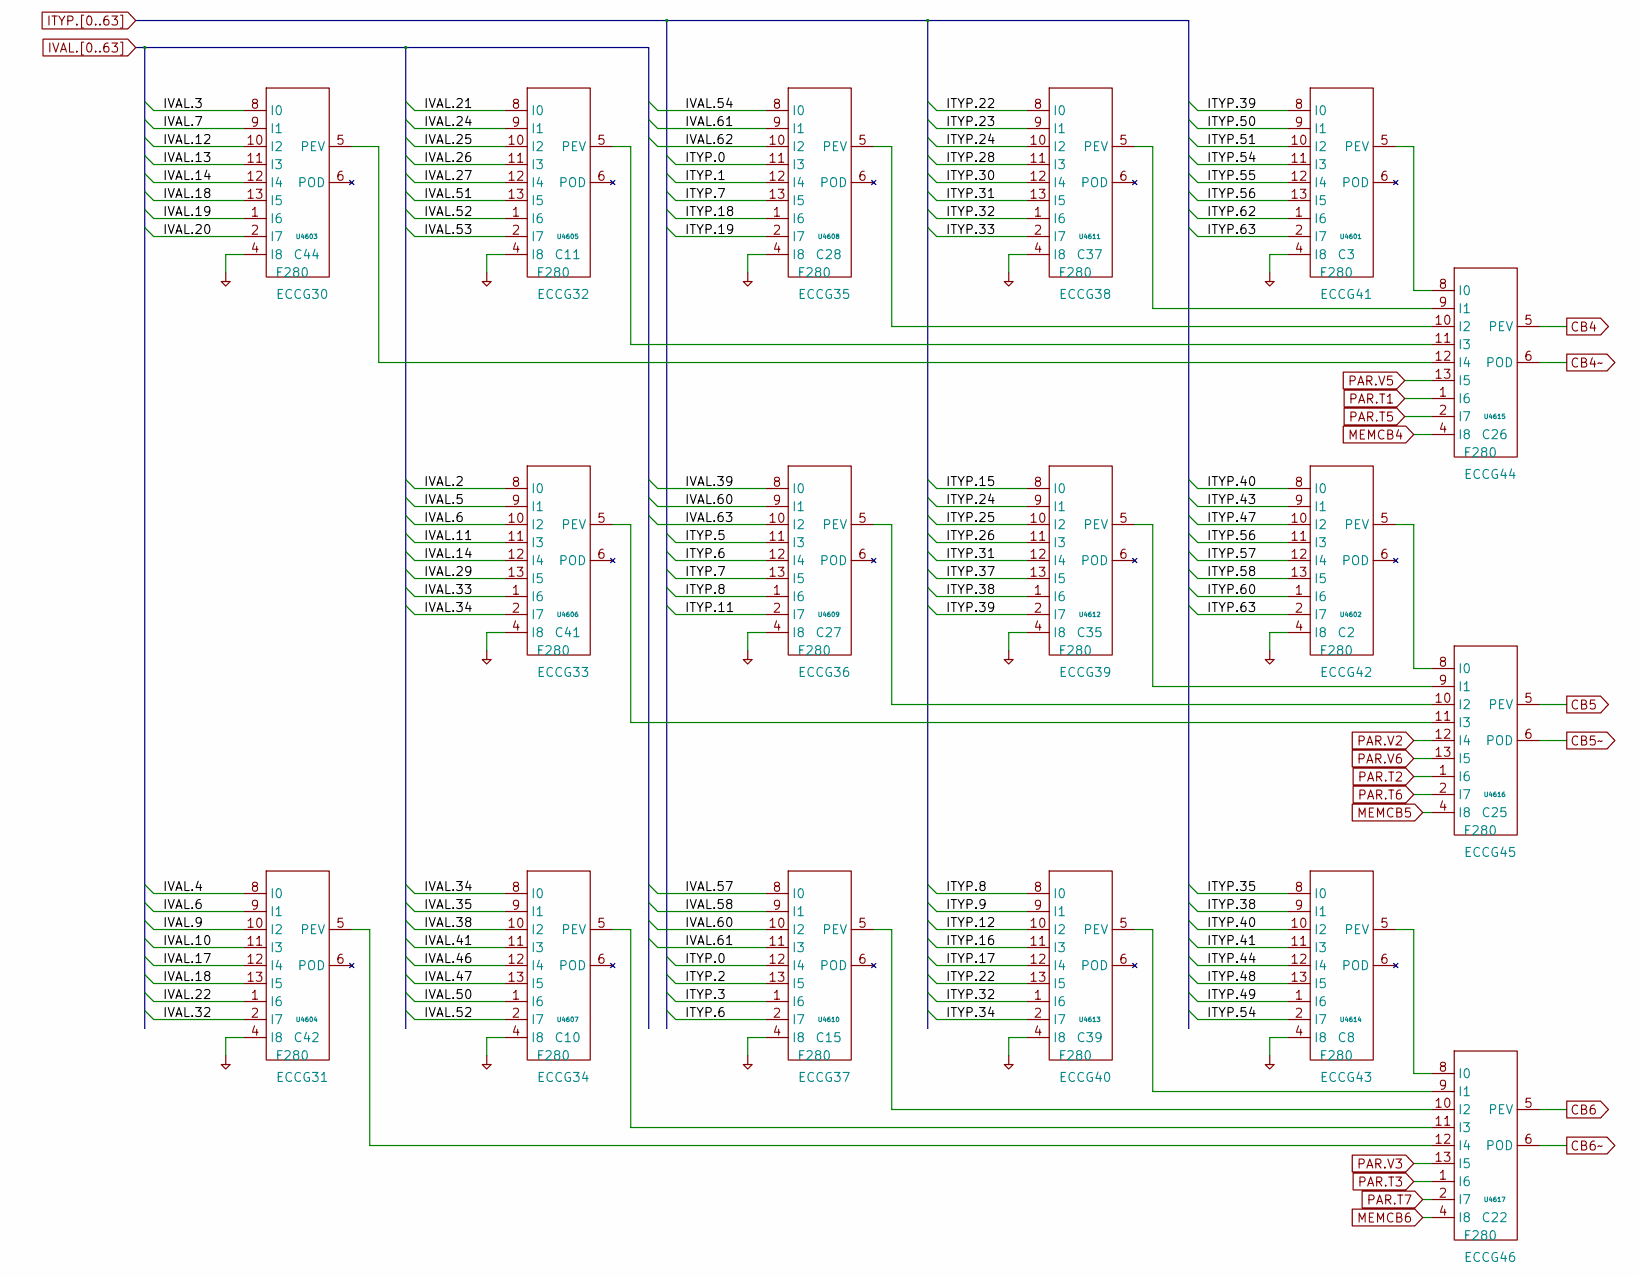
[picture p390: schematic pg_46.kicad_sch]

Parts:
U4601, U4602, U4603, U4604, U4605, U4606, U4607, U4608, U4609, U4610, U4611, U4612, U4613, U4614, U4615, U4616, U4617: F280

Connections:
CB4: U4615.5 (PEV)
CB4~: U4615.6 (POD)
CB5: U4616.5 (PEV)
CB5~: U4616.6 (POD)
CB6: U4617.5 (PEV)
CB6~: U4617.6 (POD)
ITYP.0: U4608.11 (I3), U4610.12 (I4)
ITYP.1: U4608.12 (I4)
ITYP.2: U4610.13 (I5)
ITYP.3: U4610.1 (I6)
ITYP.5: U4609.11 (I3)
ITYP.6: U4609.12 (I4), U4610.2 (I7)
ITYP.7: U4608.13 (I5), U4609.13 (I5)
ITYP.8: U4609.1 (I6), U4613.8 (I0)
ITYP.9: U4613.9 (I1)
ITYP.11: U4609.2 (I7)
ITYP.12: U4613.10 (I2)
ITYP.15: U4612.8 (I0)
ITYP.16: U4613.11 (I3)
ITYP.17: U4613.12 (I4)
ITYP.18: U4608.1 (I6)
ITYP.19: U4608.2 (I7)
ITYP.22: U4611.8 (I0), U4613.13 (I5)
ITYP.23: U4611.9 (I1)
ITYP.24: U4611.10 (I2), U4612.9 (I1)
ITYP.25: U4612.10 (I2)
ITYP.26: U4612.11 (I3)
ITYP.28: U4611.11 (I3)
ITYP.30: U4611.12 (I4)
ITYP.31: U4611.13 (I5), U4612.12 (I4)
ITYP.32: U4611.1 (I6), U4613.1 (I6)
ITYP.33: U4611.2 (I7)
ITYP.34: U4613.2 (I7)
ITYP.35: U4614.8 (I0)
ITYP.37: U4612.13 (I5)
ITYP.38: U4612.1 (I6), U4614.9 (I1)
ITYP.39: U4601.8 (I0), U4612.2 (I7)
ITYP.40: U4602.8 (I0), U4614.10 (I2)
ITYP.41: U4614.11 (I3)
ITYP.43: U4602.9 (I1)
ITYP.44: U4614.12 (I4)
ITYP.47: U4602.10 (I2)
ITYP.48: U4614.13 (I5)
ITYP.49: U4614.1 (I6)
ITYP.50: U4601.9 (I1)
ITYP.51: U4601.10 (I2)
ITYP.54: U4601.11 (I3), U4614.2 (I7)
ITYP.55: U4601.12 (I4)
ITYP.56: U4601.13 (I5), U4602.11 (I3)
ITYP.57: U4602.12 (I4)
ITYP.58: U4602.13 (I5)
ITYP.60: U4602.1 (I6)
ITYP.62: U4601.1 (I6)
ITYP.63: U4601.2 (I7), U4602.2 (I7)
IVAL.2: U4606.8 (I0)
IVAL.3: U4603.8 (I0)
IVAL.4: U4604.8 (I0)
IVAL.5: U4606.9 (I1)
IVAL.6: U4604.9 (I1), U4606.10 (I2)
IVAL.7: U4603.9 (I1)
IVAL.9: U4604.10 (I2)
IVAL.10: U4604.11 (I3)
IVAL.11: U4606.11 (I3)
IVAL.12: U4603.10 (I2)
IVAL.13: U4603.11 (I3)
IVAL.14: U4603.12 (I4), U4606.12 (I4)
IVAL.17: U4604.12 (I4)
IVAL.18: U4603.13 (I5), U4604.13 (I5)
IVAL.19: U4603.1 (I6)
IVAL.20: U4603.2 (I7)
IVAL.21: U4605.8 (I0)
IVAL.22: U4604.1 (I6)
IVAL.24: U4605.9 (I1)
IVAL.25: U4605.10 (I2)
IVAL.26: U4605.11 (I3)
IVAL.27: U4605.12 (I4)
IVAL.29: U4606.13 (I5)
IVAL.32: U4604.2 (I7)
IVAL.33: U4606.1 (I6)
IVAL.34: U4606.2 (I7), U4607.8 (I0)
IVAL.35: U4607.9 (I1)
IVAL.38: U4607.10 (I2)
IVAL.39: U4609.8 (I0)
IVAL.41: U4607.11 (I3)
IVAL.46: U4607.12 (I4)
IVAL.47: U4607.13 (I5)
IVAL.50: U4607.1 (I6)
IVAL.51: U4605.13 (I5)
IVAL.52: U4605.1 (I6), U4607.2 (I7)
IVAL.53: U4605.2 (I7)
IVAL.54: U4608.8 (I0)
IVAL.57: U4610.8 (I0)
IVAL.58: U4610.9 (I1)
IVAL.60: U4609.9 (I1), U4610.10 (I2)
IVAL.61: U4608.9 (I1), U4610.11 (I3)
IVAL.62: U4608.10 (I2)
IVAL.63: U4609.10 (I2)
MEMCB4: U4615.4 (I8)
MEMCB5: U4616.4 (I8)
MEMCB6: U4617.4 (I8)
unnamed: U4601.5 (PEV), U4615.8 (I0)
unnamed: U4602.5 (PEV), U4616.8 (I0)
unnamed: U4603.5 (PEV), U4615.12 (I4)
unnamed: U4604.5 (PEV), U4617.12 (I4)
unnamed: U4605.5 (PEV), U4615.11 (I3)
unnamed: U4606.5 (PEV), U4616.11 (I3)
unnamed: U4607.5 (PEV), U4617.11 (I3)
unnamed: U4608.5 (PEV), U4615.10 (I2)
unnamed: U4609.5 (PEV), U4616.10 (I2)
unnamed: U4610.5 (PEV), U4617.10 (I2)
unnamed: U4611.5 (PEV), U4615.9 (I1)
unnamed: U4612.5 (PEV), U4616.9 (I1)
unnamed: U4613.5 (PEV), U4617.9 (I1)
unnamed: U4614.5 (PEV), U4617.8 (I0)
PAR.T1: U4615.1 (I6)
PAR.T2: U4616.1 (I6)
PAR.T3: U4617.1 (I6)
PAR.T5: U4615.2 (I7)
PAR.T6: U4616.2 (I7)
PAR.T7: U4617.2 (I7)
PAR.V2: U4616.12 (I4)
PAR.V3: U4617.13 (I5)
PAR.V5: U4615.13 (I5)
PAR.V6: U4616.13 (I5)
PD: U4601.4 (I8), U4602.4 (I8), U4603.4 (I8), U4604.4 (I8), U4605.4 (I8), U4606.4 (I8), U4607.4 (I8), U4608.4 (I8), U4609.4 (I8), U4610.4 (I8), U4611.4 (I8), U4612.4 (I8), U4613.4 (I8), U4614.4 (I8)
