Datamuseum-DK/R1000.HwDoc/Schematics/IOC/pg_47.kicad_sch

## KiCad design Schematics/IOC/pg_47.kicad_sch (2023-01-10)

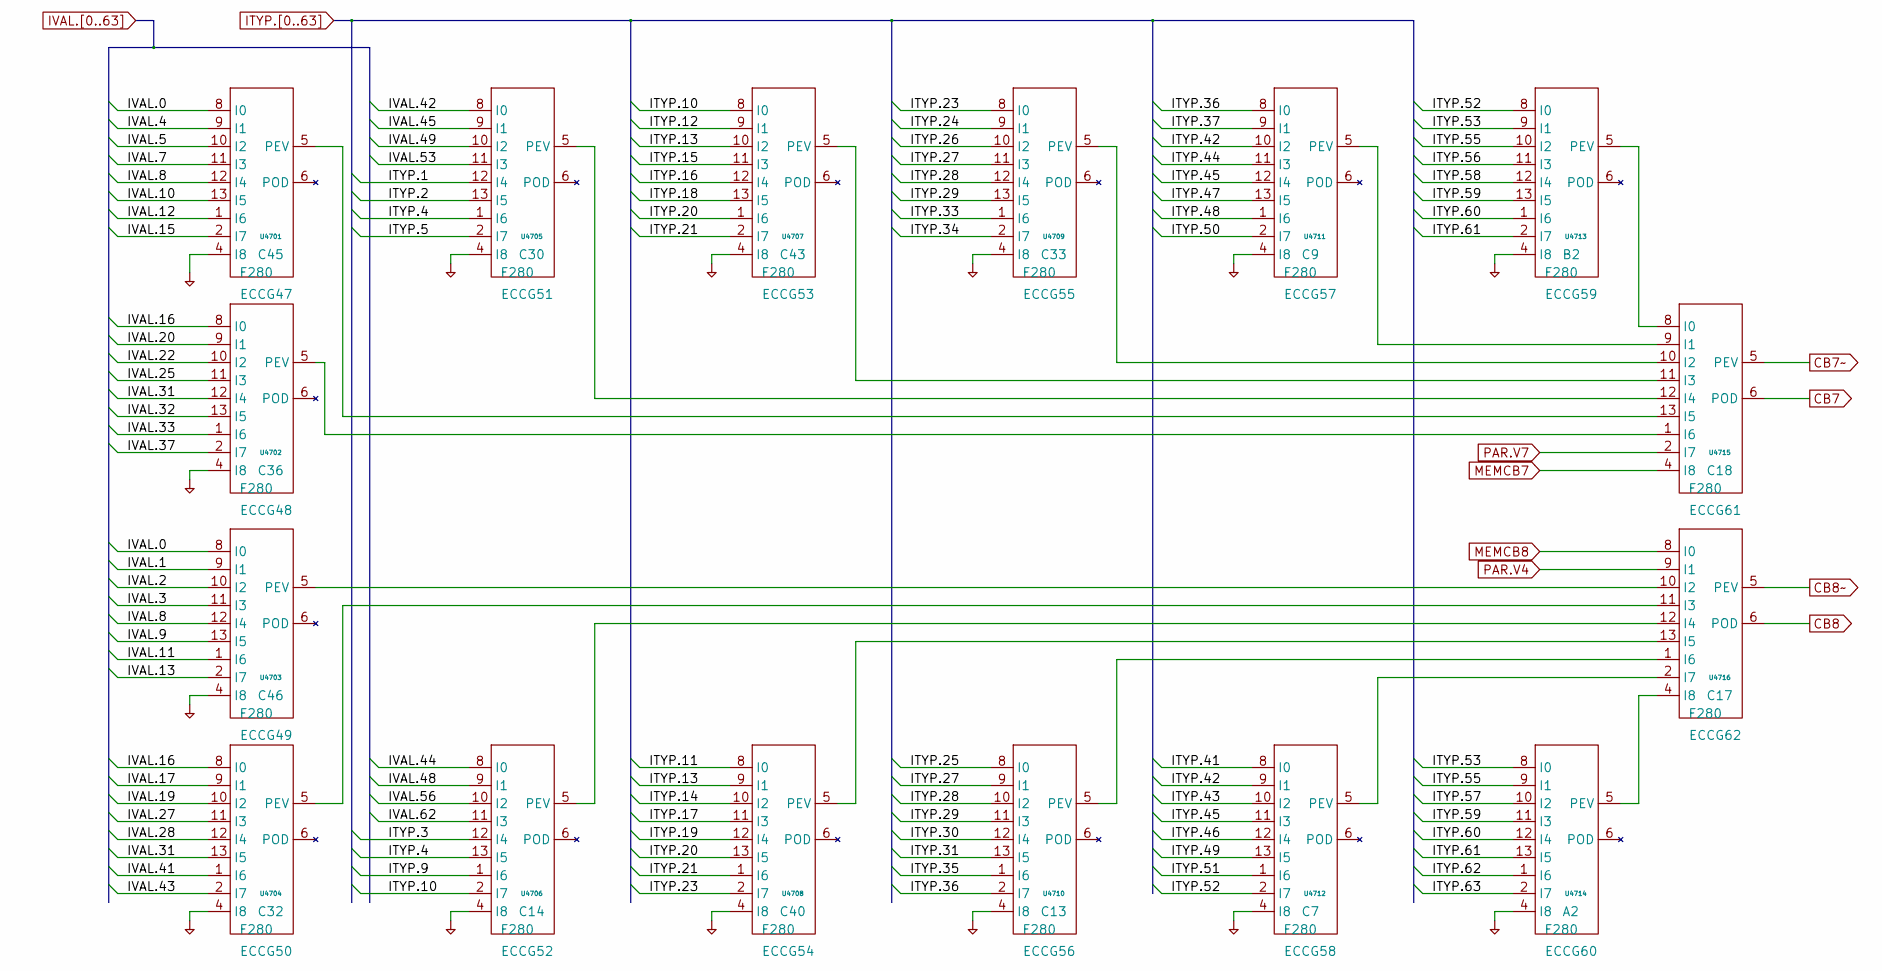
[picture p391: schematic pg_47.kicad_sch]

Parts:
U4701, U4702, U4703, U4704, U4705, U4706, U4707, U4708, U4709, U4710, U4711, U4712, U4713, U4714, U4715, U4716: F280

Connections:
CB7: U4715.6 (POD)
CB7~: U4715.5 (PEV)
CB8: U4716.6 (POD)
CB8~: U4716.5 (PEV)
ITYP.1: U4705.12 (I4)
ITYP.2: U4705.13 (I5)
ITYP.3: U4706.12 (I4)
ITYP.4: U4705.1 (I6), U4706.13 (I5)
ITYP.5: U4705.2 (I7)
ITYP.9: U4706.1 (I6)
ITYP.10: U4706.2 (I7), U4707.8 (I0)
ITYP.11: U4708.8 (I0)
ITYP.12: U4707.9 (I1)
ITYP.13: U4707.10 (I2), U4708.9 (I1)
ITYP.14: U4708.10 (I2)
ITYP.15: U4707.11 (I3)
ITYP.16: U4707.12 (I4)
ITYP.17: U4708.11 (I3)
ITYP.18: U4707.13 (I5)
ITYP.19: U4708.12 (I4)
ITYP.20: U4707.1 (I6), U4708.13 (I5)
ITYP.21: U4707.2 (I7), U4708.1 (I6)
ITYP.23: U4708.2 (I7), U4709.8 (I0)
ITYP.24: U4709.9 (I1)
ITYP.25: U4710.8 (I0)
ITYP.26: U4709.10 (I2)
ITYP.27: U4709.11 (I3), U4710.9 (I1)
ITYP.28: U4709.12 (I4), U4710.10 (I2)
ITYP.29: U4709.13 (I5), U4710.11 (I3)
ITYP.30: U4710.12 (I4)
ITYP.31: U4710.13 (I5)
ITYP.33: U4709.1 (I6)
ITYP.34: U4709.2 (I7)
ITYP.35: U4710.1 (I6)
ITYP.36: U4710.2 (I7), U4711.8 (I0)
ITYP.37: U4711.9 (I1)
ITYP.41: U4712.8 (I0)
ITYP.42: U4711.10 (I2), U4712.9 (I1)
ITYP.43: U4712.10 (I2)
ITYP.44: U4711.11 (I3)
ITYP.45: U4711.12 (I4), U4712.11 (I3)
ITYP.46: U4712.12 (I4)
ITYP.47: U4711.13 (I5)
ITYP.48: U4711.1 (I6)
ITYP.49: U4712.13 (I5)
ITYP.50: U4711.2 (I7)
ITYP.51: U4712.1 (I6)
ITYP.52: U4712.2 (I7), U4713.8 (I0)
ITYP.53: U4713.9 (I1), U4714.8 (I0)
ITYP.55: U4713.10 (I2), U4714.9 (I1)
ITYP.56: U4713.11 (I3)
ITYP.57: U4714.10 (I2)
ITYP.58: U4713.12 (I4)
ITYP.59: U4713.13 (I5), U4714.11 (I3)
ITYP.60: U4713.1 (I6), U4714.12 (I4)
ITYP.61: U4713.2 (I7), U4714.13 (I5)
ITYP.62: U4714.1 (I6)
ITYP.63: U4714.2 (I7)
IVAL.0: U4701.8 (I0), U4703.8 (I0)
IVAL.1: U4703.9 (I1)
IVAL.2: U4703.10 (I2)
IVAL.3: U4703.11 (I3)
IVAL.4: U4701.9 (I1)
IVAL.5: U4701.10 (I2)
IVAL.7: U4701.11 (I3)
IVAL.8: U4701.12 (I4), U4703.12 (I4)
IVAL.9: U4703.13 (I5)
IVAL.10: U4701.13 (I5)
IVAL.11: U4703.1 (I6)
IVAL.12: U4701.1 (I6)
IVAL.13: U4703.2 (I7)
IVAL.15: U4701.2 (I7)
IVAL.16: U4702.8 (I0), U4704.8 (I0)
IVAL.17: U4704.9 (I1)
IVAL.19: U4704.10 (I2)
IVAL.20: U4702.9 (I1)
IVAL.22: U4702.10 (I2)
IVAL.25: U4702.11 (I3)
IVAL.27: U4704.11 (I3)
IVAL.28: U4704.12 (I4)
IVAL.31: U4702.12 (I4), U4704.13 (I5)
IVAL.32: U4702.13 (I5)
IVAL.33: U4702.1 (I6)
IVAL.37: U4702.2 (I7)
IVAL.41: U4704.1 (I6)
IVAL.42: U4705.8 (I0)
IVAL.43: U4704.2 (I7)
IVAL.44: U4706.8 (I0)
IVAL.45: U4705.9 (I1)
IVAL.48: U4706.9 (I1)
IVAL.49: U4705.10 (I2)
IVAL.53: U4705.11 (I3)
IVAL.56: U4706.10 (I2)
IVAL.62: U4706.11 (I3)
MEMCB7: U4715.4 (I8)
MEMCB8: U4716.8 (I0)
unnamed: U4701.5 (PEV), U4715.13 (I5)
unnamed: U4702.5 (PEV), U4715.1 (I6)
unnamed: U4703.5 (PEV), U4716.10 (I2)
unnamed: U4704.5 (PEV), U4716.11 (I3)
unnamed: U4705.5 (PEV), U4715.12 (I4)
unnamed: U4706.5 (PEV), U4716.12 (I4)
unnamed: U4707.5 (PEV), U4715.11 (I3)
unnamed: U4708.5 (PEV), U4716.13 (I5)
unnamed: U4709.5 (PEV), U4715.10 (I2)
unnamed: U4710.5 (PEV), U4716.1 (I6)
unnamed: U4711.5 (PEV), U4715.9 (I1)
unnamed: U4712.5 (PEV), U4716.2 (I7)
unnamed: U4713.5 (PEV), U4715.8 (I0)
unnamed: U4714.5 (PEV), U4716.4 (I8)
PAR.V4: U4716.9 (I1)
PAR.V7: U4715.2 (I7)
PD: U4701.4 (I8), U4702.4 (I8), U4703.4 (I8), U4704.4 (I8), U4705.4 (I8), U4706.4 (I8), U4707.4 (I8), U4708.4 (I8), U4709.4 (I8), U4710.4 (I8), U4711.4 (I8), U4712.4 (I8), U4713.4 (I8), U4714.4 (I8)
