Datamuseum-DK/R1000.HwDoc/Schematics/IOC/pg_48.kicad_sch

## KiCad design Schematics/IOC/pg_48.kicad_sch (2023-01-10)

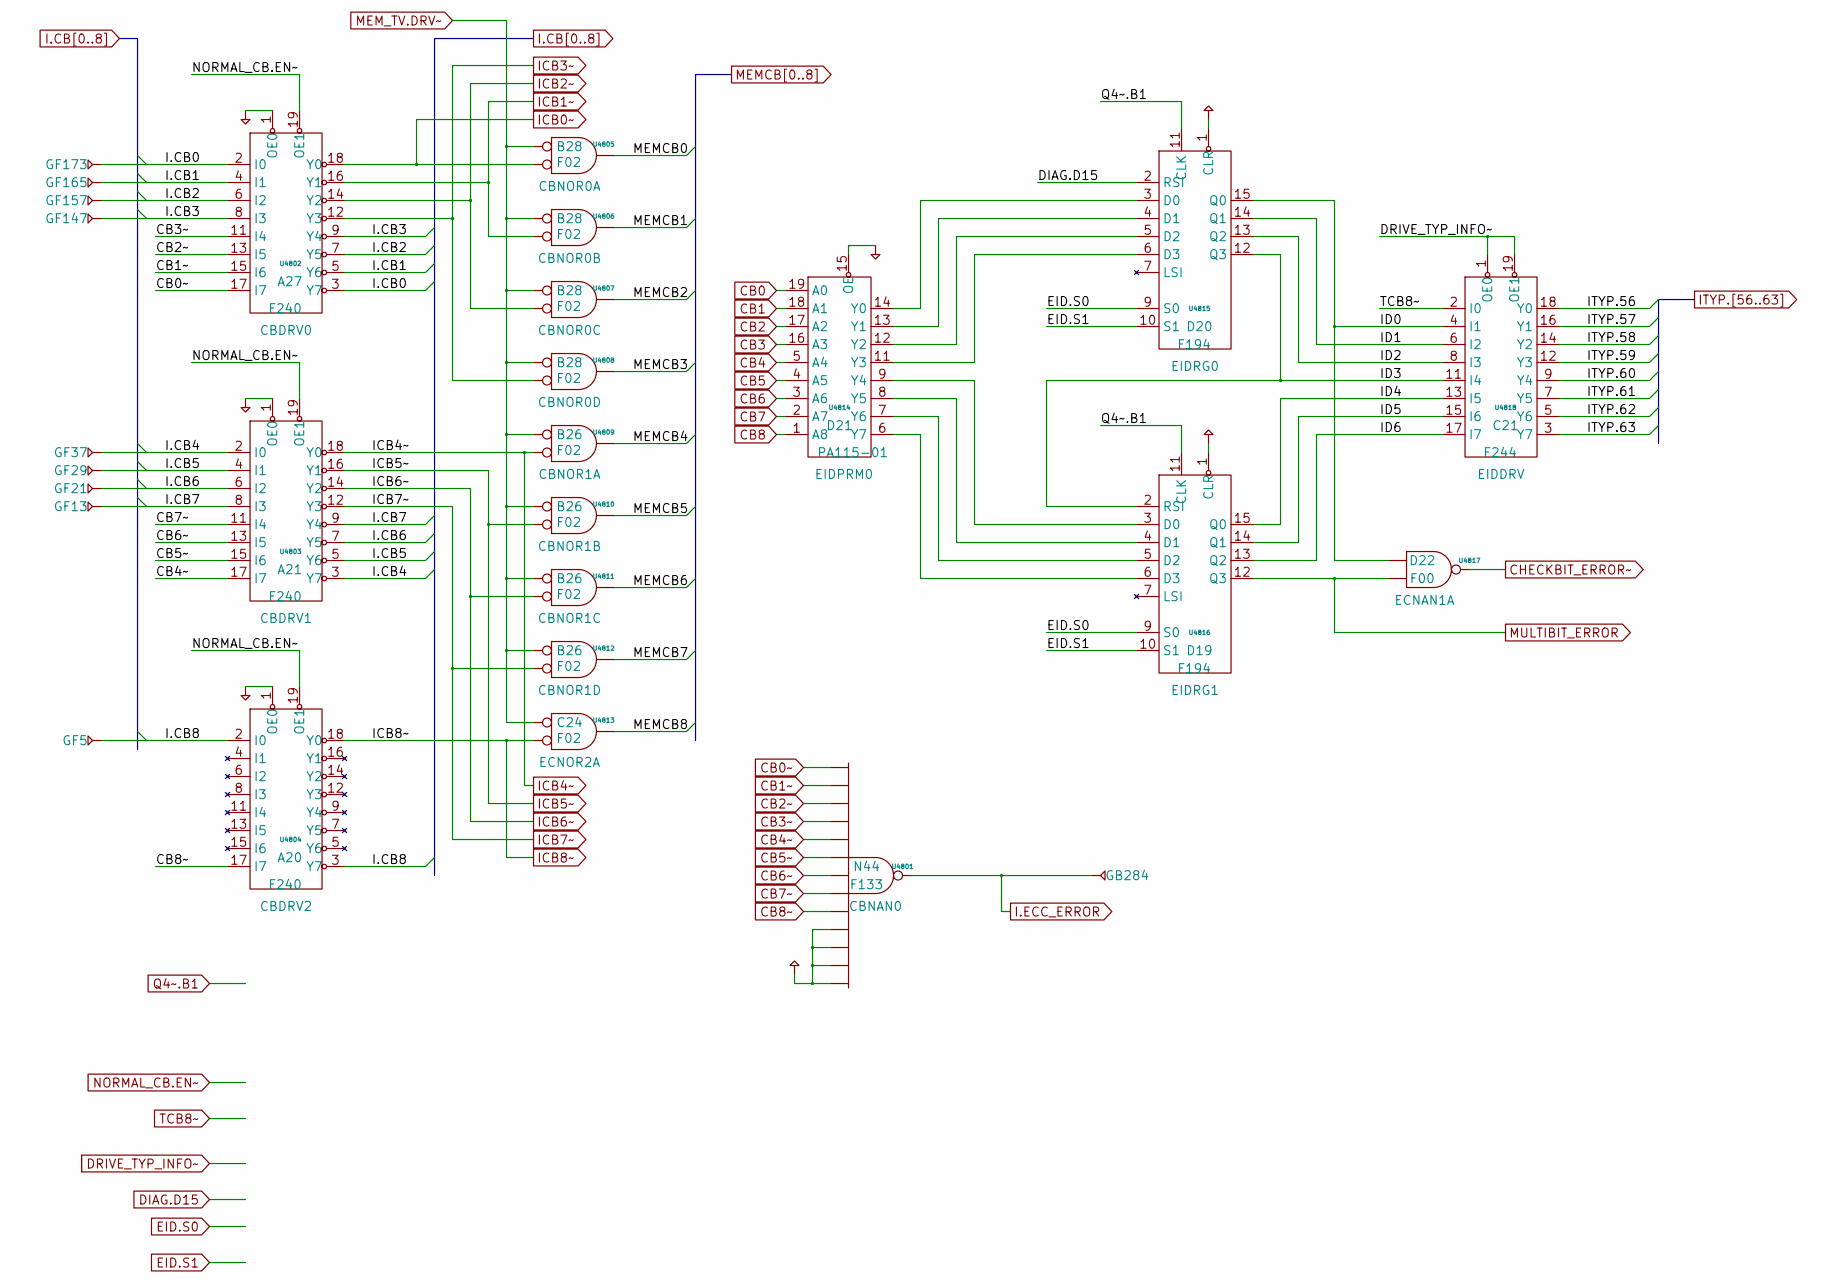
[picture p392: schematic pg_48.kicad_sch]

Parts:
GB284: GB
GF5, GF13, GF21, GF29, GF37, GF147, GF157, GF165, GF173: GF
U4801: F133
U4802, U4803, U4804: F240
U4805, U4806, U4807, U4808, U4809, U4810, U4811, U4812, U4813: F02
U4814: PA115-01
U4815, U4816: F194
U4817: F00
U4818: F244

Connections:
CB0: U4814.19 (A0)
CB0~: U4801.10 (D0), U4802.17 (I7)
CB1: U4814.18 (A1)
CB1~: U4801.11 (D1), U4802.15 (I6)
CB2: U4814.17 (A2)
CB2~: U4801.12 (D2), U4802.13 (I5)
CB3: U4814.16 (A3)
CB3~: U4801.13 (D3), U4802.11 (I4)
CB4: U4814.5 (A4)
CB4~: U4801.14 (D4), U4803.17 (I7)
CB5: U4814.4 (A5)
CB5~: U4801.15 (D5), U4803.15 (I6)
CB6: U4814.3 (A6)
CB6~: U4801.1 (D6), U4803.13 (I5)
CB7: U4814.2 (A7)
CB7~: U4801.2 (D7), U4803.11 (I4)
CB8: U4814.1 (A8)
CB8~: U4801.3 (D8), U4804.17 (I7)
CHECKBIT_ERROR~: U4817.3 (Q)
DIAG.D15: U4815.2 (RSI)
DRIVE_TYP_INFO~: U4818.1 (OE0), U4818.19 (OE1)
EID.S0: U4815.9 (S0), U4816.9 (S0)
EID.S1: U4815.10 (S1), U4816.10 (S1)
I.CB0: GF173.1, U4802.2 (I0), U4802.3 (Y7)
I.CB1: GF165.1, U4802.4 (I1), U4802.5 (Y6)
I.CB2: GF157.1, U4802.6 (I2), U4802.7 (Y5)
I.CB3: GF147.1, U4802.8 (I3), U4802.9 (Y4)
I.CB4: GF37.1, U4803.2 (I0), U4803.3 (Y7)
I.CB5: GF29.1, U4803.4 (I1), U4803.5 (Y6)
I.CB6: GF21.1, U4803.6 (I2), U4803.7 (Y5)
I.CB7: GF13.1, U4803.8 (I3), U4803.9 (Y4)
I.CB8: GF5.1, U4804.2 (I0), U4804.3 (Y7)
I.ECC_ERROR: GB284.1, U4801.8 (Q)
ICB0~: U4802.18 (Y0), U4805.2 (D1)
ICB1~: U4802.16 (Y1), U4806.2 (D1)
ICB2~: U4802.14 (Y2), U4807.2 (D1)
ICB3~: U4802.12 (Y3), U4808.2 (D1)
ICB4~: U4803.18 (Y0), U4809.2 (D1)
ICB5~: U4803.16 (Y1), U4810.2 (D1)
ICB6~: U4803.14 (Y2), U4811.2 (D1)
ICB7~: U4803.12 (Y3), U4812.2 (D1)
ICB8~: U4804.18 (Y0), U4813.2 (D1)
ID0: U4815.15 (Q0), U4817.1 (D0), U4818.4 (I1)
ID1: U4815.14 (Q1), U4818.6 (I2)
ID2: U4815.13 (Q2), U4818.8 (I3)
ID3: U4815.12 (Q3), U4816.2 (RSI), U4818.11 (I4)
ID4: U4816.15 (Q0), U4818.13 (I5)
ID5: U4816.14 (Q1), U4818.15 (I6)
ID6: U4816.13 (Q2), U4818.17 (I7)
ITYP.56: U4818.18 (Y0)
ITYP.57: U4818.16 (Y1)
ITYP.58: U4818.14 (Y2)
ITYP.59: U4818.12 (Y3)
ITYP.60: U4818.9 (Y4)
ITYP.61: U4818.7 (Y5)
ITYP.62: U4818.5 (Y6)
ITYP.63: U4818.3 (Y7)
MEMCB0: U4805.3 (Q)
MEMCB1: U4806.3 (Q)
MEMCB2: U4807.3 (Q)
MEMCB3: U4808.3 (Q)
MEMCB4: U4809.3 (Q)
MEMCB5: U4810.3 (Q)
MEMCB6: U4811.3 (Q)
MEMCB7: U4812.3 (Q)
MEMCB8: U4813.3 (Q)
MEM_TV.DRV~: U4805.1 (D0), U4806.1 (D0), U4807.1 (D0), U4808.1 (D0), U4809.1 (D0), U4810.1 (D0), U4811.1 (D0), U4812.1 (D0), U4813.1 (D0)
MULTIBIT_ERROR: U4816.12 (Q3), U4817.2 (D1)
NORMAL_CB.EN~: U4802.19 (OE1), U4803.19 (OE1), U4804.19 (OE1)
unnamed: U4814.6 (Y7), U4816.6 (D3)
unnamed: U4814.7 (Y6), U4816.5 (D2)
unnamed: U4814.8 (Y5), U4816.4 (D1)
unnamed: U4814.9 (Y4), U4816.3 (D0)
unnamed: U4814.11 (Y3), U4815.6 (D3)
unnamed: U4814.12 (Y2), U4815.5 (D2)
unnamed: U4814.13 (Y1), U4815.4 (D1)
unnamed: U4814.14 (Y0), U4815.3 (D0)
PD: U4802.1 (OE0), U4803.1 (OE0), U4804.1 (OE0), U4814.15 (OE)
PU: U4801.4 (D9), U4801.5 (D10), U4801.6 (D11), U4801.7 (D12), U4815.1 (CLR), U4816.1 (CLR)
Q4~.B1: U4815.11 (CLK), U4816.11 (CLK)
TCB8~: U4818.2 (I0)
