Datamuseum-DK/R1000.HwDoc/Schematics/IOC/pg_49.kicad_sch

## KiCad design Schematics/IOC/pg_49.kicad_sch (2023-01-10)

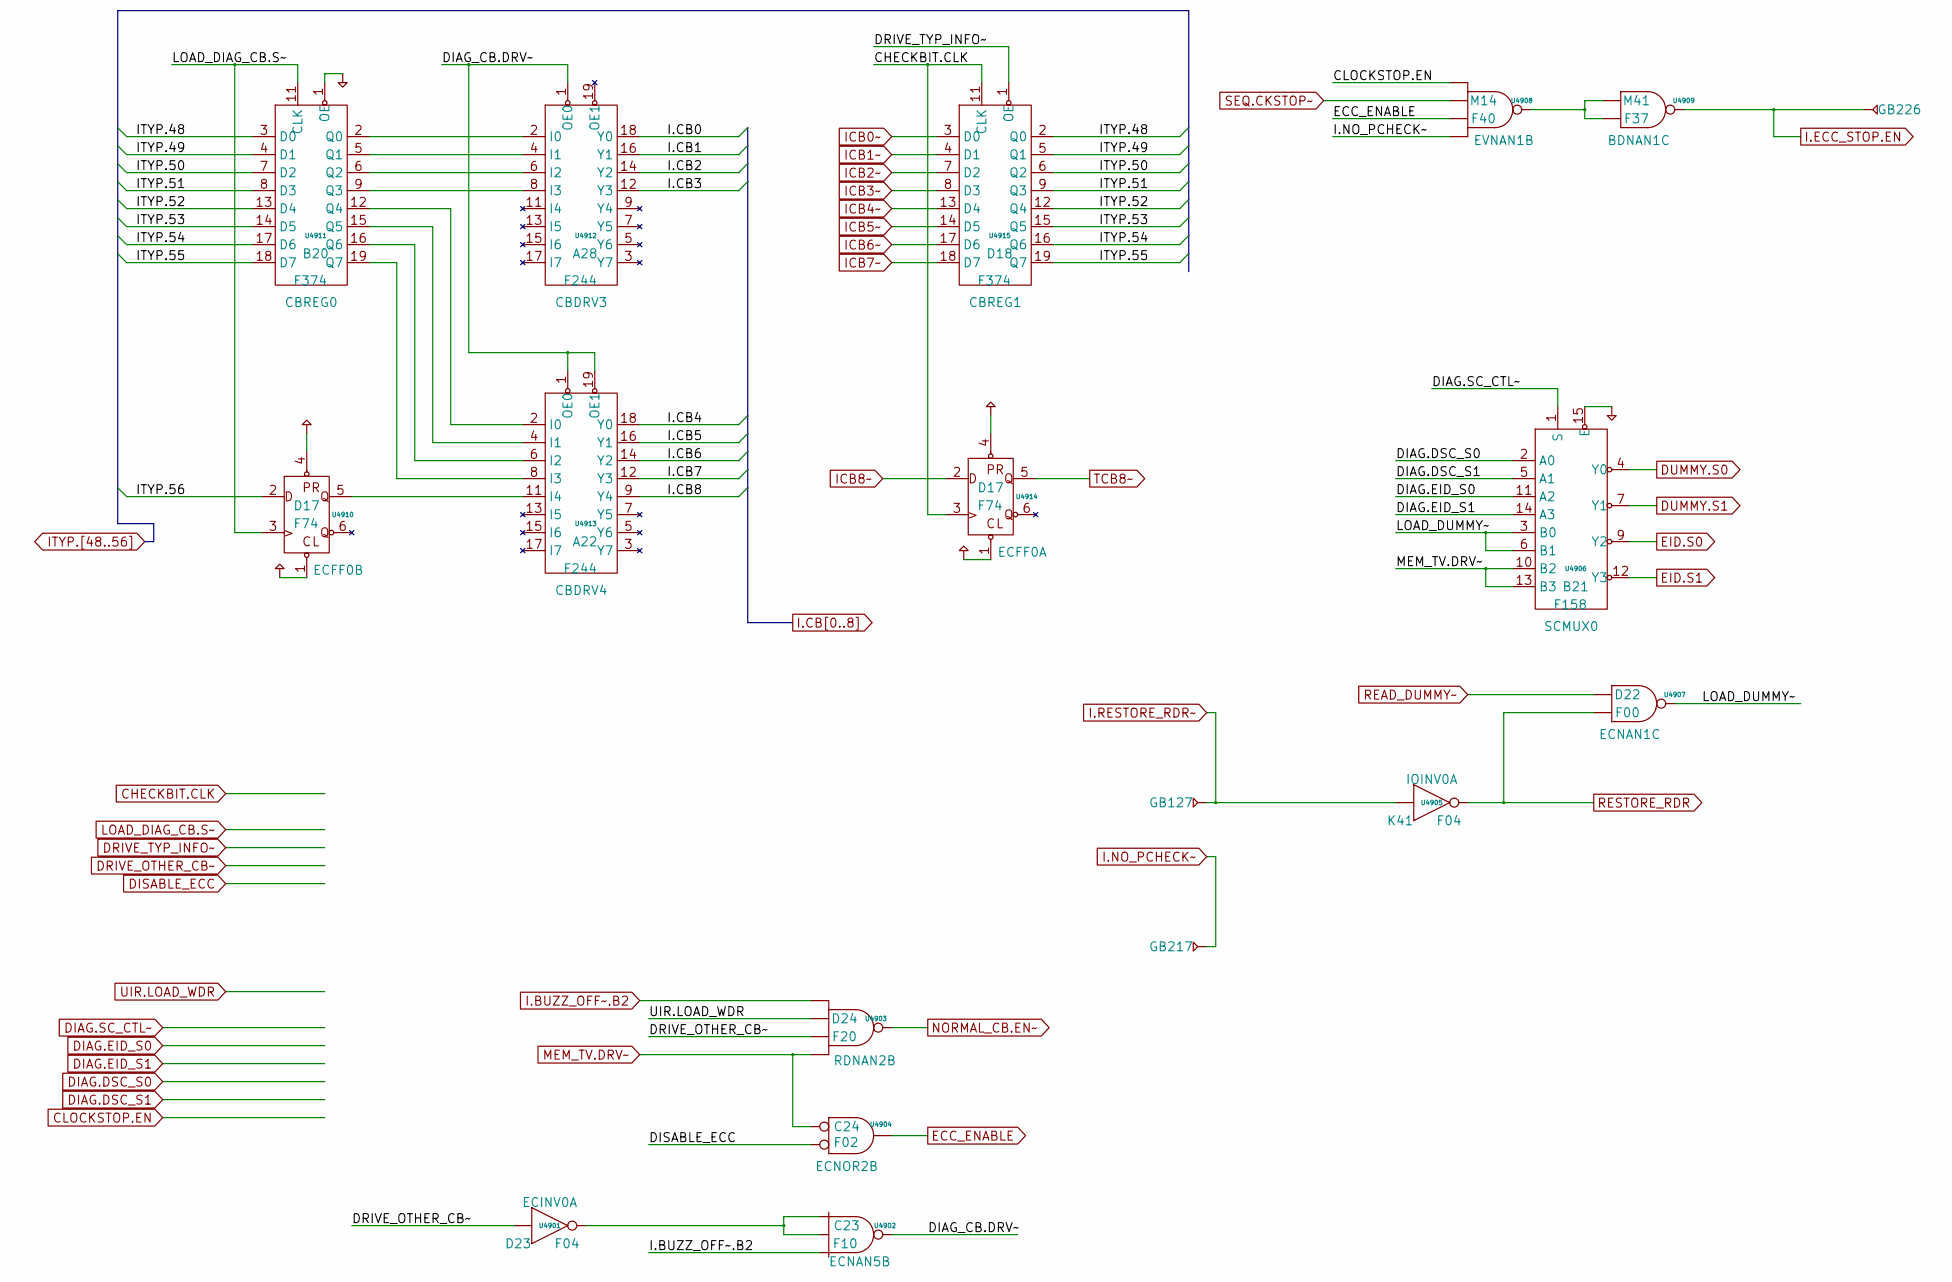
[picture p393: schematic pg_49.kicad_sch]

Parts:
GB127, GB217, GB226: GB
U4901, U4905: F04
U4902: F10
U4903: F20
U4904: F02
U4906: F158
U4907: F00
U4908: F40
U4909: F37
U4910, U4914: F74
U4911, U4915: F374
U4912, U4913: F244

Connections:
CHECKBIT.CLK: U4914.3 (CLK), U4915.11 (CLK)
CLOCKSTOP.EN: U4908.1 (D0)
DIAG.DSC_S0: U4906.2 (A0)
DIAG.DSC_S1: U4906.5 (A1)
DIAG.EID_S0: U4906.11 (A2)
DIAG.EID_S1: U4906.14 (A3)
DIAG.SC_CTL~: U4906.1 (S)
DIAG_CB.DRV~: U4902.4 (Q), U4912.1 (OE0), U4913.1 (OE0), U4913.19 (OE1)
DISABLE_ECC: U4904.2 (D1)
DRIVE_OTHER_CB~: U4901.1 (D0), U4903.4 (D2)
DRIVE_TYP_INFO~: U4915.1 (OE)
DUMMY.S0: U4906.4 (Y0)
DUMMY.S1: U4906.7 (Y1)
ECC_ENABLE: U4904.3 (Q), U4908.4 (D4)
EID.S0: U4906.9 (Y2)
EID.S1: U4906.12 (Y3)
I.BUZZ_OFF~.B2: U4902.3 (D2), U4903.1 (D0)
I.CB0: U4912.18 (Y0)
I.CB1: U4912.16 (Y1)
I.CB2: U4912.14 (Y2)
I.CB3: U4912.12 (Y3)
I.CB4: U4913.18 (Y0)
I.CB5: U4913.16 (Y1)
I.CB6: U4913.14 (Y2)
I.CB7: U4913.12 (Y3)
I.CB8: U4913.9 (Y4)
I.ECC_STOP.EN: GB226.1, U4909.3 (Q)
I.NO_PCHECK~: GB217.1, U4908.5 (D5)
I.RESTORE_RDR~: GB127.1, U4905.1 (D0)
ICB0~: U4915.3 (D0)
ICB1~: U4915.4 (D1)
ICB2~: U4915.7 (D2)
ICB3~: U4915.8 (D3)
ICB4~: U4915.13 (D4)
ICB5~: U4915.14 (D5)
ICB6~: U4915.17 (D6)
ICB7~: U4915.18 (D7)
ICB8~: U4914.2 (D)
ITYP.48: U4911.3 (D0), U4915.2 (Q0)
ITYP.49: U4911.4 (D1), U4915.5 (Q1)
ITYP.50: U4911.7 (D2), U4915.6 (Q2)
ITYP.51: U4911.8 (D3), U4915.9 (Q3)
ITYP.52: U4911.13 (D4), U4915.12 (Q4)
ITYP.53: U4911.14 (D5), U4915.15 (Q5)
ITYP.54: U4911.17 (D6), U4915.16 (Q6)
ITYP.55: U4911.18 (D7), U4915.19 (Q7)
ITYP.56: U4910.2 (D)
LOAD_DIAG_CB.S~: U4910.3 (CLK), U4911.11 (CLK)
LOAD_DUMMY~: U4906.3 (B0), U4906.6 (B1), U4907.3 (Q)
MEM_TV.DRV~: U4903.5 (D3), U4904.1 (D0), U4906.10 (B2), U4906.13 (B3)
NORMAL_CB.EN~: U4903.6 (Q)
unnamed: U4901.2 (Q), U4902.1 (D0), U4902.2 (D1)
unnamed: U4908.6 (Q), U4909.1 (D0), U4909.2 (D1)
unnamed: U4910.5 (Q), U4913.11 (I4)
unnamed: U4911.2 (Q0), U4912.2 (I0)
unnamed: U4911.5 (Q1), U4912.4 (I1)
unnamed: U4911.6 (Q2), U4912.6 (I2)
unnamed: U4911.9 (Q3), U4912.8 (I3)
unnamed: U4911.12 (Q4), U4913.2 (I0)
unnamed: U4911.15 (Q5), U4913.4 (I1)
unnamed: U4911.16 (Q6), U4913.6 (I2)
unnamed: U4911.19 (Q7), U4913.8 (I3)
PD: U4906.15 (E), U4911.1 (OE)
PU: U4910.1 (CL_), U4910.4 (PR_), U4914.1 (CL_), U4914.4 (PR_)
READ_DUMMY~: U4907.1 (D0)
RESTORE_RDR: U4905.2 (Q), U4907.2 (D1)
SEQ.CKSTOP~: U4908.2 (D3)
TCB8~: U4914.5 (Q)
UIR.LOAD_WDR: U4903.2 (D1)
