Datamuseum-DK/R1000.HwDoc/Schematics/IOC/pg_50.kicad_sch

## KiCad design Schematics/IOC/pg_50.kicad_sch (2023-01-10)

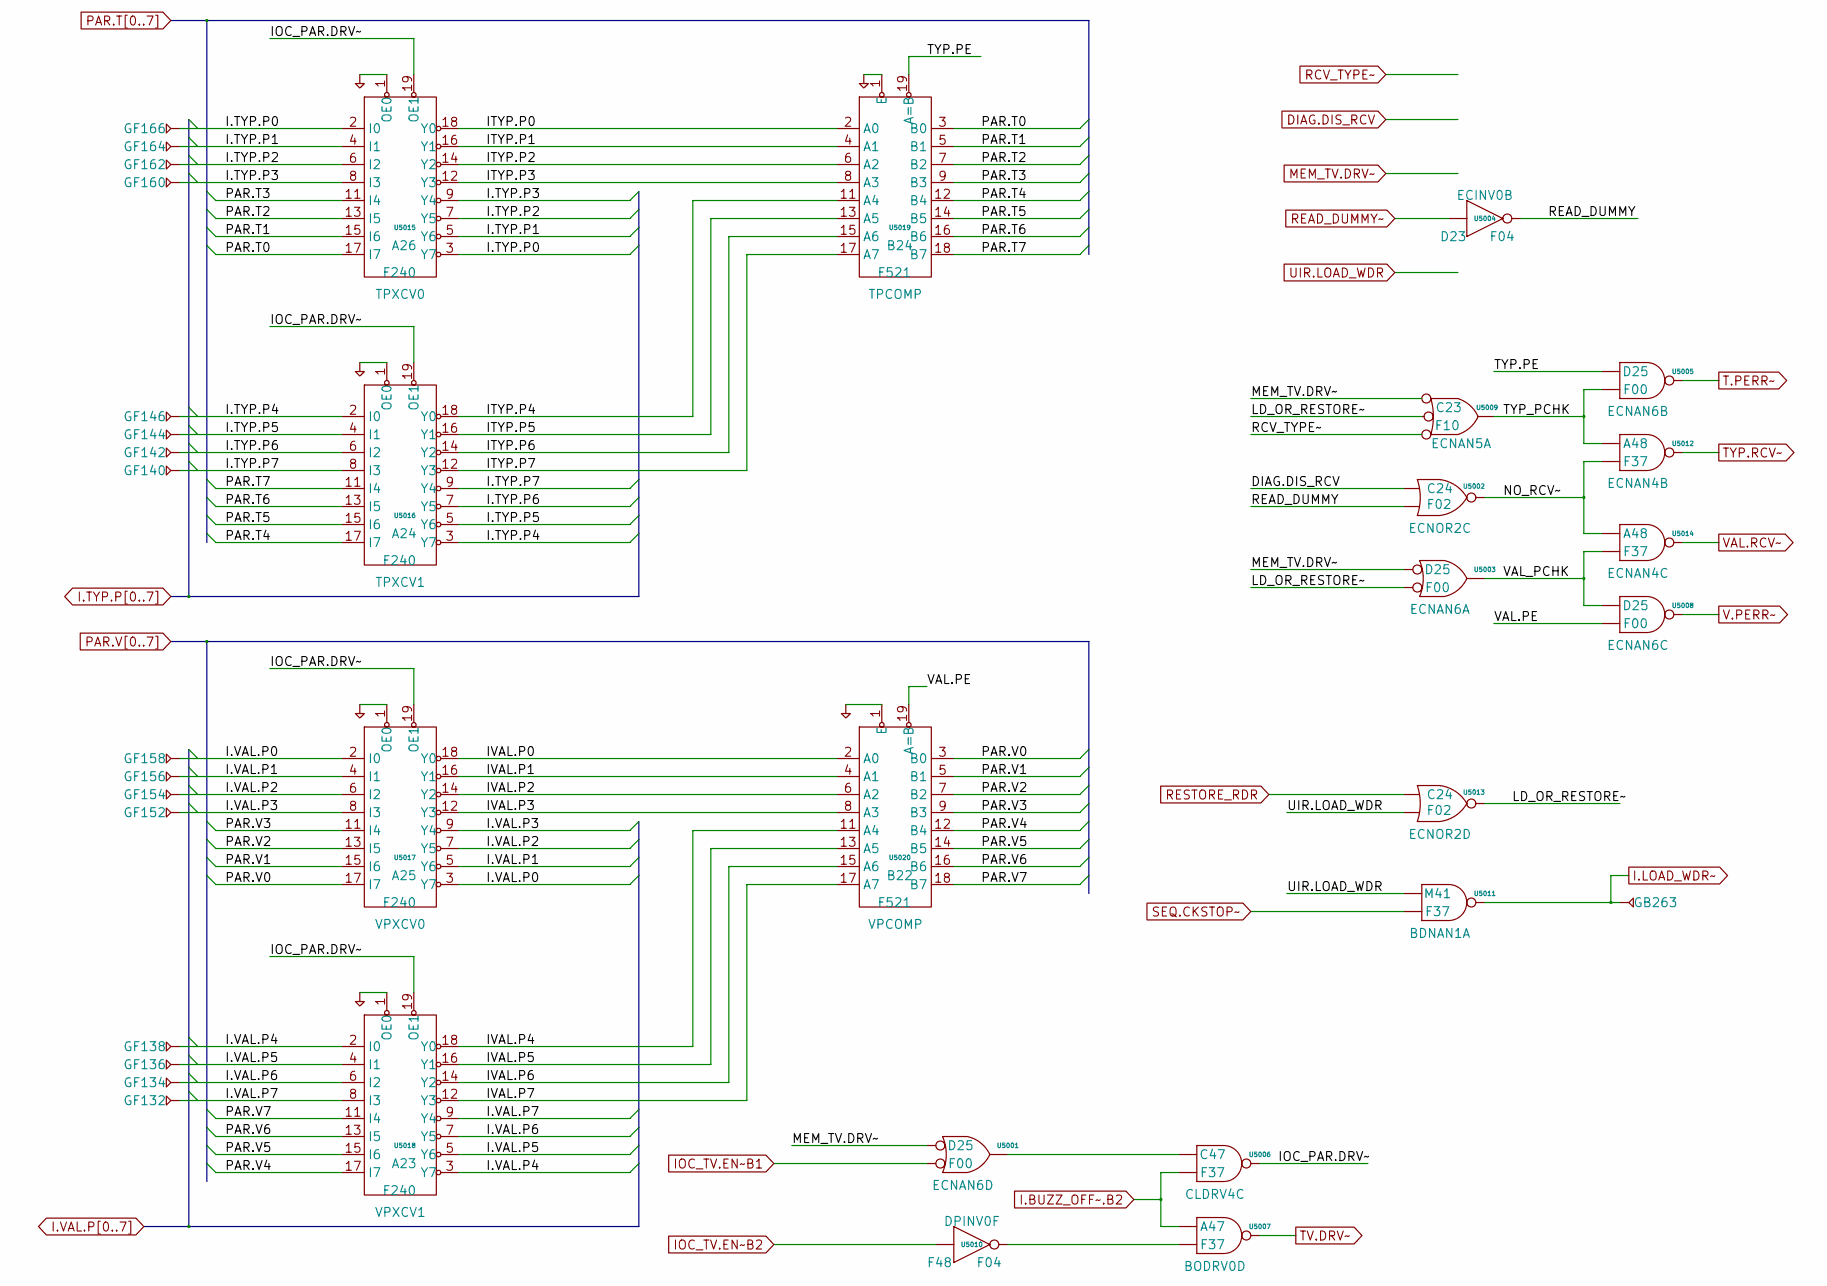
[picture p394: schematic pg_50.kicad_sch]

Parts:
GB263: GB
GF132, GF134, GF136, GF138, GF140, GF142, GF144, GF146, GF152, GF154, GF156, GF158, GF160, GF162, GF164, GF166: GF
U5001, U5003, U5005, U5008: F00
U5002, U5013: F02
U5004, U5010: F04
U5006, U5007, U5011, U5012, U5014: F37
U5009: F10
U5015, U5016, U5017, U5018: F240
U5019, U5020: F521

Connections:
DIAG.DIS_RCV: U5002.1 (D0)
I.BUZZ_OFF~.B2: U5006.2 (D1), U5007.1 (D0)
I.LOAD_WDR~: GB263.1, U5011.3 (Q)
I.TYP.P0: GF166.1, U5015.2 (I0), U5015.3 (Y7)
I.TYP.P1: GF164.1, U5015.4 (I1), U5015.5 (Y6)
I.TYP.P2: GF162.1, U5015.6 (I2), U5015.7 (Y5)
I.TYP.P3: GF160.1, U5015.8 (I3), U5015.9 (Y4)
I.TYP.P4: GF146.1, U5016.2 (I0), U5016.3 (Y7)
I.TYP.P5: GF144.1, U5016.4 (I1), U5016.5 (Y6)
I.TYP.P6: GF142.1, U5016.6 (I2), U5016.7 (Y5)
I.TYP.P7: GF140.1, U5016.8 (I3), U5016.9 (Y4)
I.VAL.P0: GF158.1, U5017.2 (I0), U5017.3 (Y7)
I.VAL.P1: GF156.1, U5017.4 (I1), U5017.5 (Y6)
I.VAL.P2: GF154.1, U5017.6 (I2), U5017.7 (Y5)
I.VAL.P3: GF152.1, U5017.8 (I3), U5017.9 (Y4)
I.VAL.P4: GF138.1, U5018.2 (I0), U5018.3 (Y7)
I.VAL.P5: GF136.1, U5018.4 (I1), U5018.5 (Y6)
I.VAL.P6: GF134.1, U5018.6 (I2), U5018.7 (Y5)
I.VAL.P7: GF132.1, U5018.8 (I3), U5018.9 (Y4)
IOC_PAR.DRV~: U5006.3 (Q), U5015.19 (OE1), U5016.19 (OE1), U5017.19 (OE1), U5018.19 (OE1)
IOC_TV.EN~B1: U5001.2 (D1)
IOC_TV.EN~B2: U5010.1 (D0)
ITYP.P0: U5015.18 (Y0), U5019.2 (A0)
ITYP.P1: U5015.16 (Y1), U5019.4 (A1)
ITYP.P2: U5015.14 (Y2), U5019.6 (A2)
ITYP.P3: U5015.12 (Y3), U5019.8 (A3)
ITYP.P4: U5016.18 (Y0), U5019.11 (A4)
ITYP.P5: U5016.16 (Y1), U5019.13 (A5)
ITYP.P6: U5016.14 (Y2), U5019.15 (A6)
ITYP.P7: U5016.12 (Y3), U5019.17 (A7)
IVAL.P0: U5017.18 (Y0), U5020.2 (A0)
IVAL.P1: U5017.16 (Y1), U5020.4 (A1)
IVAL.P2: U5017.14 (Y2), U5020.6 (A2)
IVAL.P3: U5017.12 (Y3), U5020.8 (A3)
IVAL.P4: U5018.18 (Y0), U5020.11 (A4)
IVAL.P5: U5018.16 (Y1), U5020.13 (A5)
IVAL.P6: U5018.14 (Y2), U5020.15 (A6)
IVAL.P7: U5018.12 (Y3), U5020.17 (A7)
LD_OR_RESTORE~: U5003.2 (D1), U5009.2 (D1), U5013.3 (Q)
MEM_TV.DRV~: U5001.1 (D0), U5003.1 (D0), U5009.1 (D0)
NO_RCV~: U5002.3 (Q), U5012.2 (D1), U5014.1 (D0)
unnamed: U5001.3 (Q), U5006.1 (D0)
unnamed: U5007.2 (D1), U5010.2 (Q)
PAR.T0: U5015.17 (I7), U5019.3 (B0)
PAR.T1: U5015.15 (I6), U5019.5 (B1)
PAR.T2: U5015.13 (I5), U5019.7 (B2)
PAR.T3: U5015.11 (I4), U5019.9 (B3)
PAR.T4: U5016.17 (I7), U5019.12 (B4)
PAR.T5: U5016.15 (I6), U5019.14 (B5)
PAR.T6: U5016.13 (I5), U5019.16 (B6)
PAR.T7: U5016.11 (I4), U5019.18 (B7)
PAR.V0: U5017.17 (I7), U5020.3 (B0)
PAR.V1: U5017.15 (I6), U5020.5 (B1)
PAR.V2: U5017.13 (I5), U5020.7 (B2)
PAR.V3: U5017.11 (I4), U5020.9 (B3)
PAR.V4: U5018.17 (I7), U5020.12 (B4)
PAR.V5: U5018.15 (I6), U5020.14 (B5)
PAR.V6: U5018.13 (I5), U5020.16 (B6)
PAR.V7: U5018.11 (I4), U5020.18 (B7)
PD: U5015.1 (OE0), U5016.1 (OE0), U5017.1 (OE0), U5018.1 (OE0), U5019.1 (E), U5020.1 (E)
RCV_TYPE~: U5009.3 (D2)
READ_DUMMY: U5002.2 (D1), U5004.2 (Q)
READ_DUMMY~: U5004.1 (D0)
RESTORE_RDR: U5013.1 (D0)
SEQ.CKSTOP~: U5011.2 (D1)
T.PERR~: U5005.3 (Q)
TV.DRV~: U5007.3 (Q)
TYP.PE: U5005.1 (D0), U5019.19 (A=B)
TYP.RCV~: U5012.3 (Q)
TYP_PCHK: U5005.2 (D1), U5009.4 (Q), U5012.1 (D0)
UIR.LOAD_WDR: U5011.1 (D0), U5013.2 (D1)
V.PERR~: U5008.3 (Q)
VAL.PE: U5008.2 (D1), U5020.19 (A=B)
VAL.RCV~: U5014.3 (Q)
VAL_PCHK: U5003.3 (Q), U5008.1 (D0), U5014.2 (D1)
