Datamuseum-DK/R1000.HwDoc/Schematics/IOC/pg_51.kicad_sch

## KiCad design Schematics/IOC/pg_51.kicad_sch (2023-01-10)

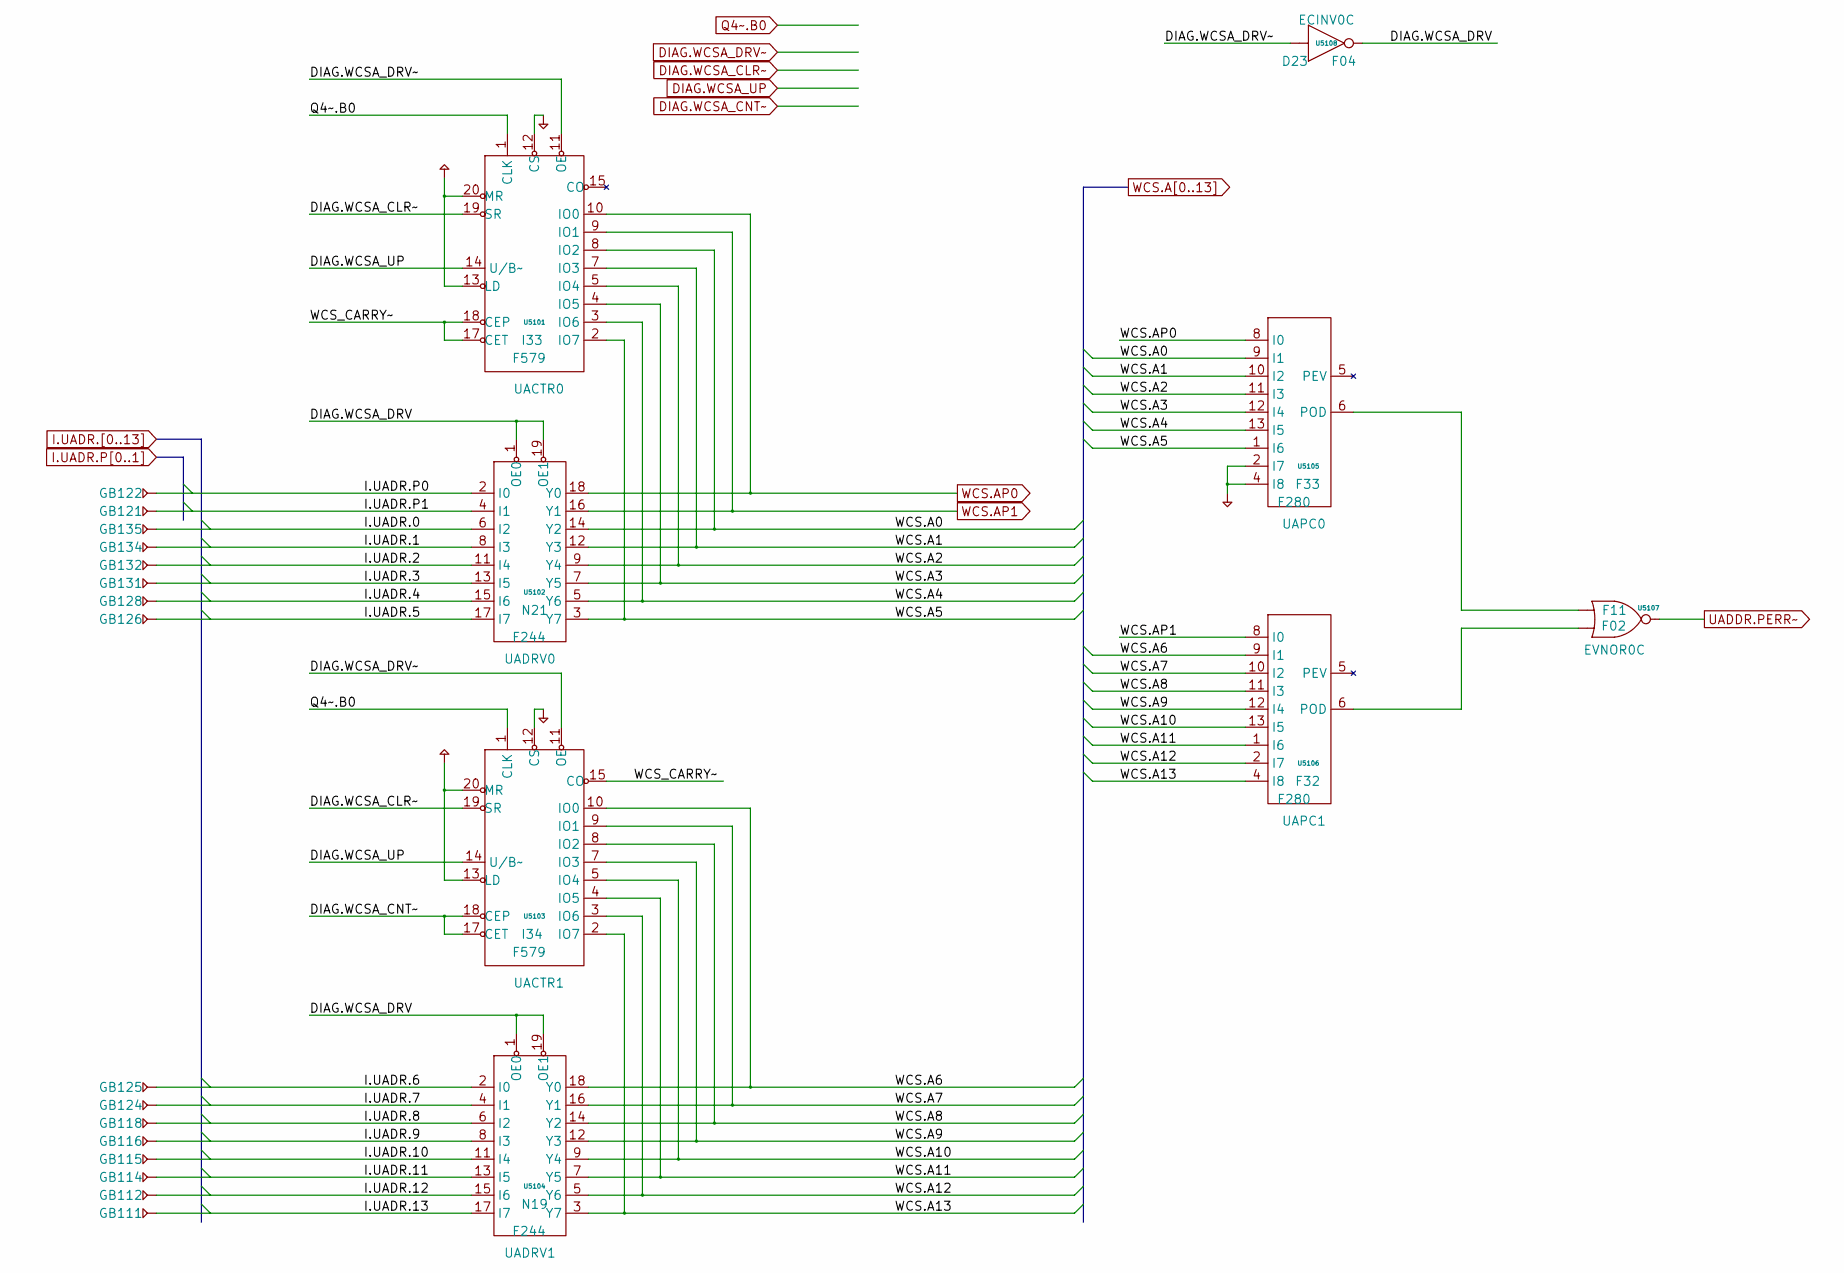
[picture p395: schematic pg_51.kicad_sch]

Parts:
GB111, GB112, GB114, GB115, GB116, GB118, GB121, GB122, GB124, GB125, GB126, GB128, GB131, GB132, GB134, GB135: GB
U5101, U5103: F579
U5102, U5104: F244
U5105, U5106: F280
U5107: F02
U5108: F04

Connections:
DIAG.WCSA_CLR~: U5101.19 (SR), U5103.19 (SR)
DIAG.WCSA_CNT~: U5103.17 (CET), U5103.18 (CEP)
DIAG.WCSA_DRV: U5102.1 (OE0), U5102.19 (OE1), U5104.1 (OE0), U5104.19 (OE1), U5108.2 (Q)
DIAG.WCSA_DRV~: U5101.11 (OE), U5103.11 (OE), U5108.1 (D0)
DIAG.WCSA_UP: U5101.14 (U/B~), U5103.14 (U/B~)
I.UADR.0: GB135.1, U5102.6 (I2)
I.UADR.1: GB134.1, U5102.8 (I3)
I.UADR.2: GB132.1, U5102.11 (I4)
I.UADR.3: GB131.1, U5102.13 (I5)
I.UADR.4: GB128.1, U5102.15 (I6)
I.UADR.5: GB126.1, U5102.17 (I7)
I.UADR.6: GB125.1, U5104.2 (I0)
I.UADR.7: GB124.1, U5104.4 (I1)
I.UADR.8: GB118.1, U5104.6 (I2)
I.UADR.9: GB116.1, U5104.8 (I3)
I.UADR.10: GB115.1, U5104.11 (I4)
I.UADR.11: GB114.1, U5104.13 (I5)
I.UADR.12: GB112.1, U5104.15 (I6)
I.UADR.13: GB111.1, U5104.17 (I7)
I.UADR.P0: GB122.1, U5102.2 (I0)
I.UADR.P1: GB121.1, U5102.4 (I1)
unnamed: U5105.6 (POD), U5107.1 (D0)
unnamed: U5106.6 (POD), U5107.2 (D1)
PD: U5101.12 (CS), U5103.12 (CS), U5105.2 (I7), U5105.4 (I8)
PU: U5101.13 (LD), U5101.20 (MR), U5103.13 (LD), U5103.20 (MR)
Q4~.B0: U5101.1 (CLK), U5103.1 (CLK)
UADDR.PERR~: U5107.3 (Q)
WCS.A0: U5101.8 (IO2), U5102.14 (Y2), U5105.9 (I1)
WCS.A1: U5101.7 (IO3), U5102.12 (Y3), U5105.10 (I2)
WCS.A2: U5101.5 (IO4), U5102.9 (Y4), U5105.11 (I3)
WCS.A3: U5101.4 (IO5), U5102.7 (Y5), U5105.12 (I4)
WCS.A4: U5101.3 (IO6), U5102.5 (Y6), U5105.13 (I5)
WCS.A5: U5101.2 (IO7), U5102.3 (Y7), U5105.1 (I6)
WCS.A6: U5103.10 (IO0), U5104.18 (Y0), U5106.9 (I1)
WCS.A7: U5103.9 (IO1), U5104.16 (Y1), U5106.10 (I2)
WCS.A8: U5103.8 (IO2), U5104.14 (Y2), U5106.11 (I3)
WCS.A9: U5103.7 (IO3), U5104.12 (Y3), U5106.12 (I4)
WCS.A10: U5103.5 (IO4), U5104.9 (Y4), U5106.13 (I5)
WCS.A11: U5103.4 (IO5), U5104.7 (Y5), U5106.1 (I6)
WCS.A12: U5103.3 (IO6), U5104.5 (Y6), U5106.2 (I7)
WCS.A13: U5103.2 (IO7), U5104.3 (Y7), U5106.4 (I8)
WCS.AP0: U5101.10 (IO0), U5102.18 (Y0), U5105.8 (I0)
WCS.AP1: U5101.9 (IO1), U5102.16 (Y1), U5106.8 (I0)
WCS_CARRY~: U5101.17 (CET), U5101.18 (CEP), U5103.15 (CO)
