Datamuseum-DK/R1000.HwDoc/Schematics/IOC/pg_52.kicad_sch

## KiCad design Schematics/IOC/pg_52.kicad_sch (2023-01-10)

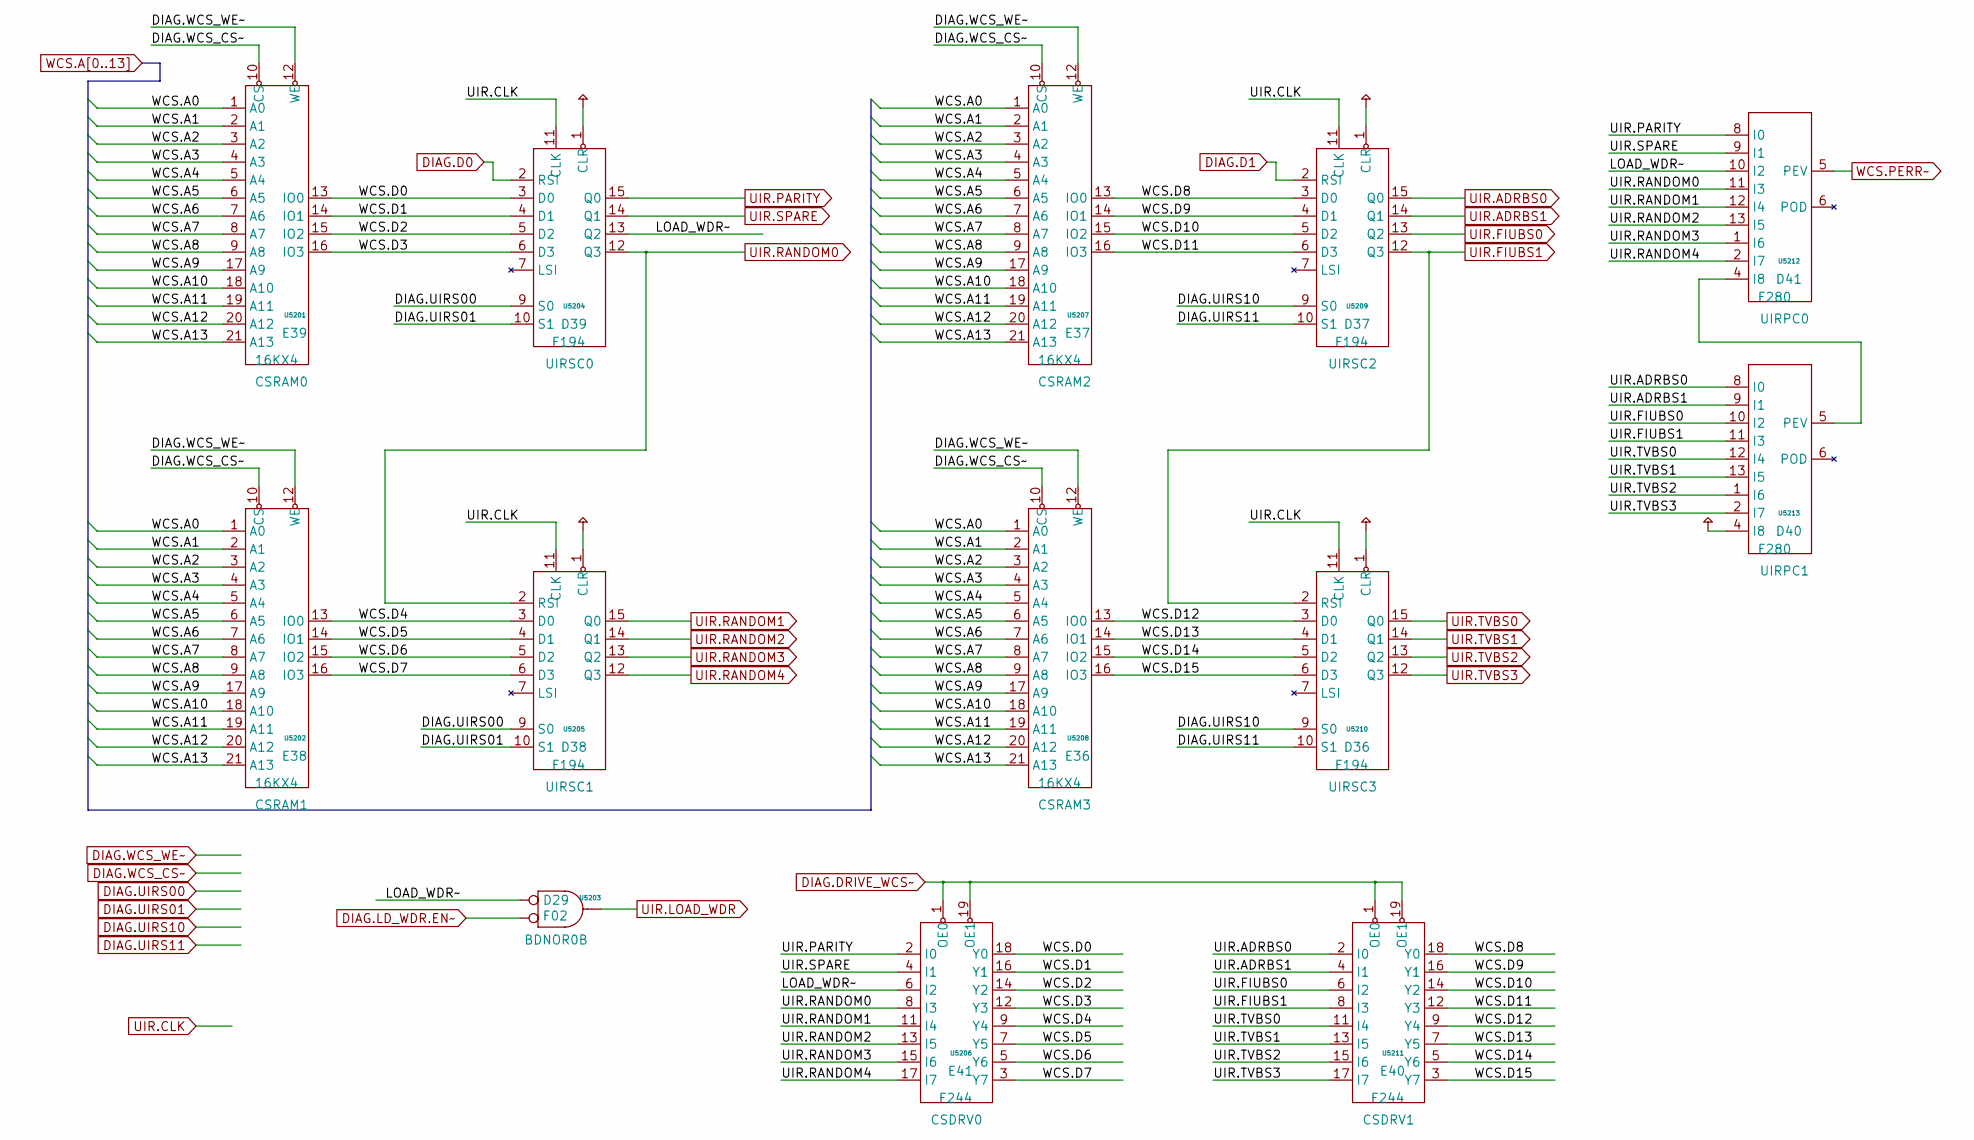
[picture p396: schematic pg_52.kicad_sch]

Parts:
U5201, U5202, U5207, U5208: 16KX4
U5203: F02
U5204, U5205, U5209, U5210: F194
U5206, U5211: F244
U5212, U5213: F280

Connections:
DIAG.D0: U5204.2 (RSI)
DIAG.D1: U5209.2 (RSI)
DIAG.DRIVE_WCS~: U5206.1 (OE0), U5206.19 (OE1), U5211.1 (OE0), U5211.19 (OE1)
DIAG.LD_WDR.EN~: U5203.2 (D1)
DIAG.UIRS00: U5204.9 (S0), U5205.9 (S0)
DIAG.UIRS01: U5204.10 (S1), U5205.10 (S1)
DIAG.UIRS10: U5209.9 (S0), U5210.9 (S0)
DIAG.UIRS11: U5209.10 (S1), U5210.10 (S1)
DIAG.WCS_CS~: U5201.10 (CS), U5202.10 (CS), U5207.10 (CS), U5208.10 (CS)
DIAG.WCS_WE~: U5201.12 (WE), U5202.12 (WE), U5207.12 (WE), U5208.12 (WE)
LOAD_WDR~: U5203.1 (D0), U5204.13 (Q2), U5206.6 (I2), U5212.10 (I2)
unnamed: U5212.4 (I8), U5213.5 (PEV)
PU: U5204.1 (CLR), U5205.1 (CLR), U5209.1 (CLR), U5210.1 (CLR), U5213.4 (I8)
UIR.ADRBS0: U5209.15 (Q0), U5211.2 (I0), U5213.8 (I0)
UIR.ADRBS1: U5209.14 (Q1), U5211.4 (I1), U5213.9 (I1)
UIR.CLK: U5204.11 (CLK), U5205.11 (CLK), U5209.11 (CLK), U5210.11 (CLK)
UIR.FIUBS0: U5209.13 (Q2), U5211.6 (I2), U5213.10 (I2)
UIR.FIUBS1: U5209.12 (Q3), U5210.2 (RSI), U5211.8 (I3), U5213.11 (I3)
UIR.LOAD_WDR: U5203.3 (Q)
UIR.PARITY: U5204.15 (Q0), U5206.2 (I0), U5212.8 (I0)
UIR.RANDOM0: U5204.12 (Q3), U5205.2 (RSI), U5206.8 (I3), U5212.11 (I3)
UIR.RANDOM1: U5205.15 (Q0), U5206.11 (I4), U5212.12 (I4)
UIR.RANDOM2: U5205.14 (Q1), U5206.13 (I5), U5212.13 (I5)
UIR.RANDOM3: U5205.13 (Q2), U5206.15 (I6), U5212.1 (I6)
UIR.RANDOM4: U5205.12 (Q3), U5206.17 (I7), U5212.2 (I7)
UIR.SPARE: U5204.14 (Q1), U5206.4 (I1), U5212.9 (I1)
UIR.TVBS0: U5210.15 (Q0), U5211.11 (I4), U5213.12 (I4)
UIR.TVBS1: U5210.14 (Q1), U5211.13 (I5), U5213.13 (I5)
UIR.TVBS2: U5210.13 (Q2), U5211.15 (I6), U5213.1 (I6)
UIR.TVBS3: U5210.12 (Q3), U5211.17 (I7), U5213.2 (I7)
WCS.A0: U5201.1 (A0), U5202.1 (A0), U5207.1 (A0), U5208.1 (A0)
WCS.A1: U5201.2 (A1), U5202.2 (A1), U5207.2 (A1), U5208.2 (A1)
WCS.A2: U5201.3 (A2), U5202.3 (A2), U5207.3 (A2), U5208.3 (A2)
WCS.A3: U5201.4 (A3), U5202.4 (A3), U5207.4 (A3), U5208.4 (A3)
WCS.A4: U5201.5 (A4), U5202.5 (A4), U5207.5 (A4), U5208.5 (A4)
WCS.A5: U5201.6 (A5), U5202.6 (A5), U5207.6 (A5), U5208.6 (A5)
WCS.A6: U5201.7 (A6), U5202.7 (A6), U5207.7 (A6), U5208.7 (A6)
WCS.A7: U5201.8 (A7), U5202.8 (A7), U5207.8 (A7), U5208.8 (A7)
WCS.A8: U5201.9 (A8), U5202.9 (A8), U5207.9 (A8), U5208.9 (A8)
WCS.A9: U5201.17 (A9), U5202.17 (A9), U5207.17 (A9), U5208.17 (A9)
WCS.A10: U5201.18 (A10), U5202.18 (A10), U5207.18 (A10), U5208.18 (A10)
WCS.A11: U5201.19 (A11), U5202.19 (A11), U5207.19 (A11), U5208.19 (A11)
WCS.A12: U5201.20 (A12), U5202.20 (A12), U5207.20 (A12), U5208.20 (A12)
WCS.A13: U5201.21 (A13), U5202.21 (A13), U5207.21 (A13), U5208.21 (A13)
WCS.D0: U5201.13 (IO0), U5204.3 (D0), U5206.18 (Y0)
WCS.D1: U5201.14 (IO1), U5204.4 (D1), U5206.16 (Y1)
WCS.D2: U5201.15 (IO2), U5204.5 (D2), U5206.14 (Y2)
WCS.D3: U5201.16 (IO3), U5204.6 (D3), U5206.12 (Y3)
WCS.D4: U5202.13 (IO0), U5205.3 (D0), U5206.9 (Y4)
WCS.D5: U5202.14 (IO1), U5205.4 (D1), U5206.7 (Y5)
WCS.D6: U5202.15 (IO2), U5205.5 (D2), U5206.5 (Y6)
WCS.D7: U5202.16 (IO3), U5205.6 (D3), U5206.3 (Y7)
WCS.D8: U5207.13 (IO0), U5209.3 (D0), U5211.18 (Y0)
WCS.D9: U5207.14 (IO1), U5209.4 (D1), U5211.16 (Y1)
WCS.D10: U5207.15 (IO2), U5209.5 (D2), U5211.14 (Y2)
WCS.D11: U5207.16 (IO3), U5209.6 (D3), U5211.12 (Y3)
WCS.D12: U5208.13 (IO0), U5210.3 (D0), U5211.9 (Y4)
WCS.D13: U5208.14 (IO1), U5210.4 (D1), U5211.7 (Y5)
WCS.D14: U5208.15 (IO2), U5210.5 (D2), U5211.5 (Y6)
WCS.D15: U5208.16 (IO3), U5210.6 (D3), U5211.3 (Y7)
WCS.PERR~: U5212.5 (PEV)
