Datamuseum-DK/R1000.HwDoc/Schematics/IOC/pg_53.kicad_sch

## KiCad design Schematics/IOC/pg_53.kicad_sch (2023-01-10)

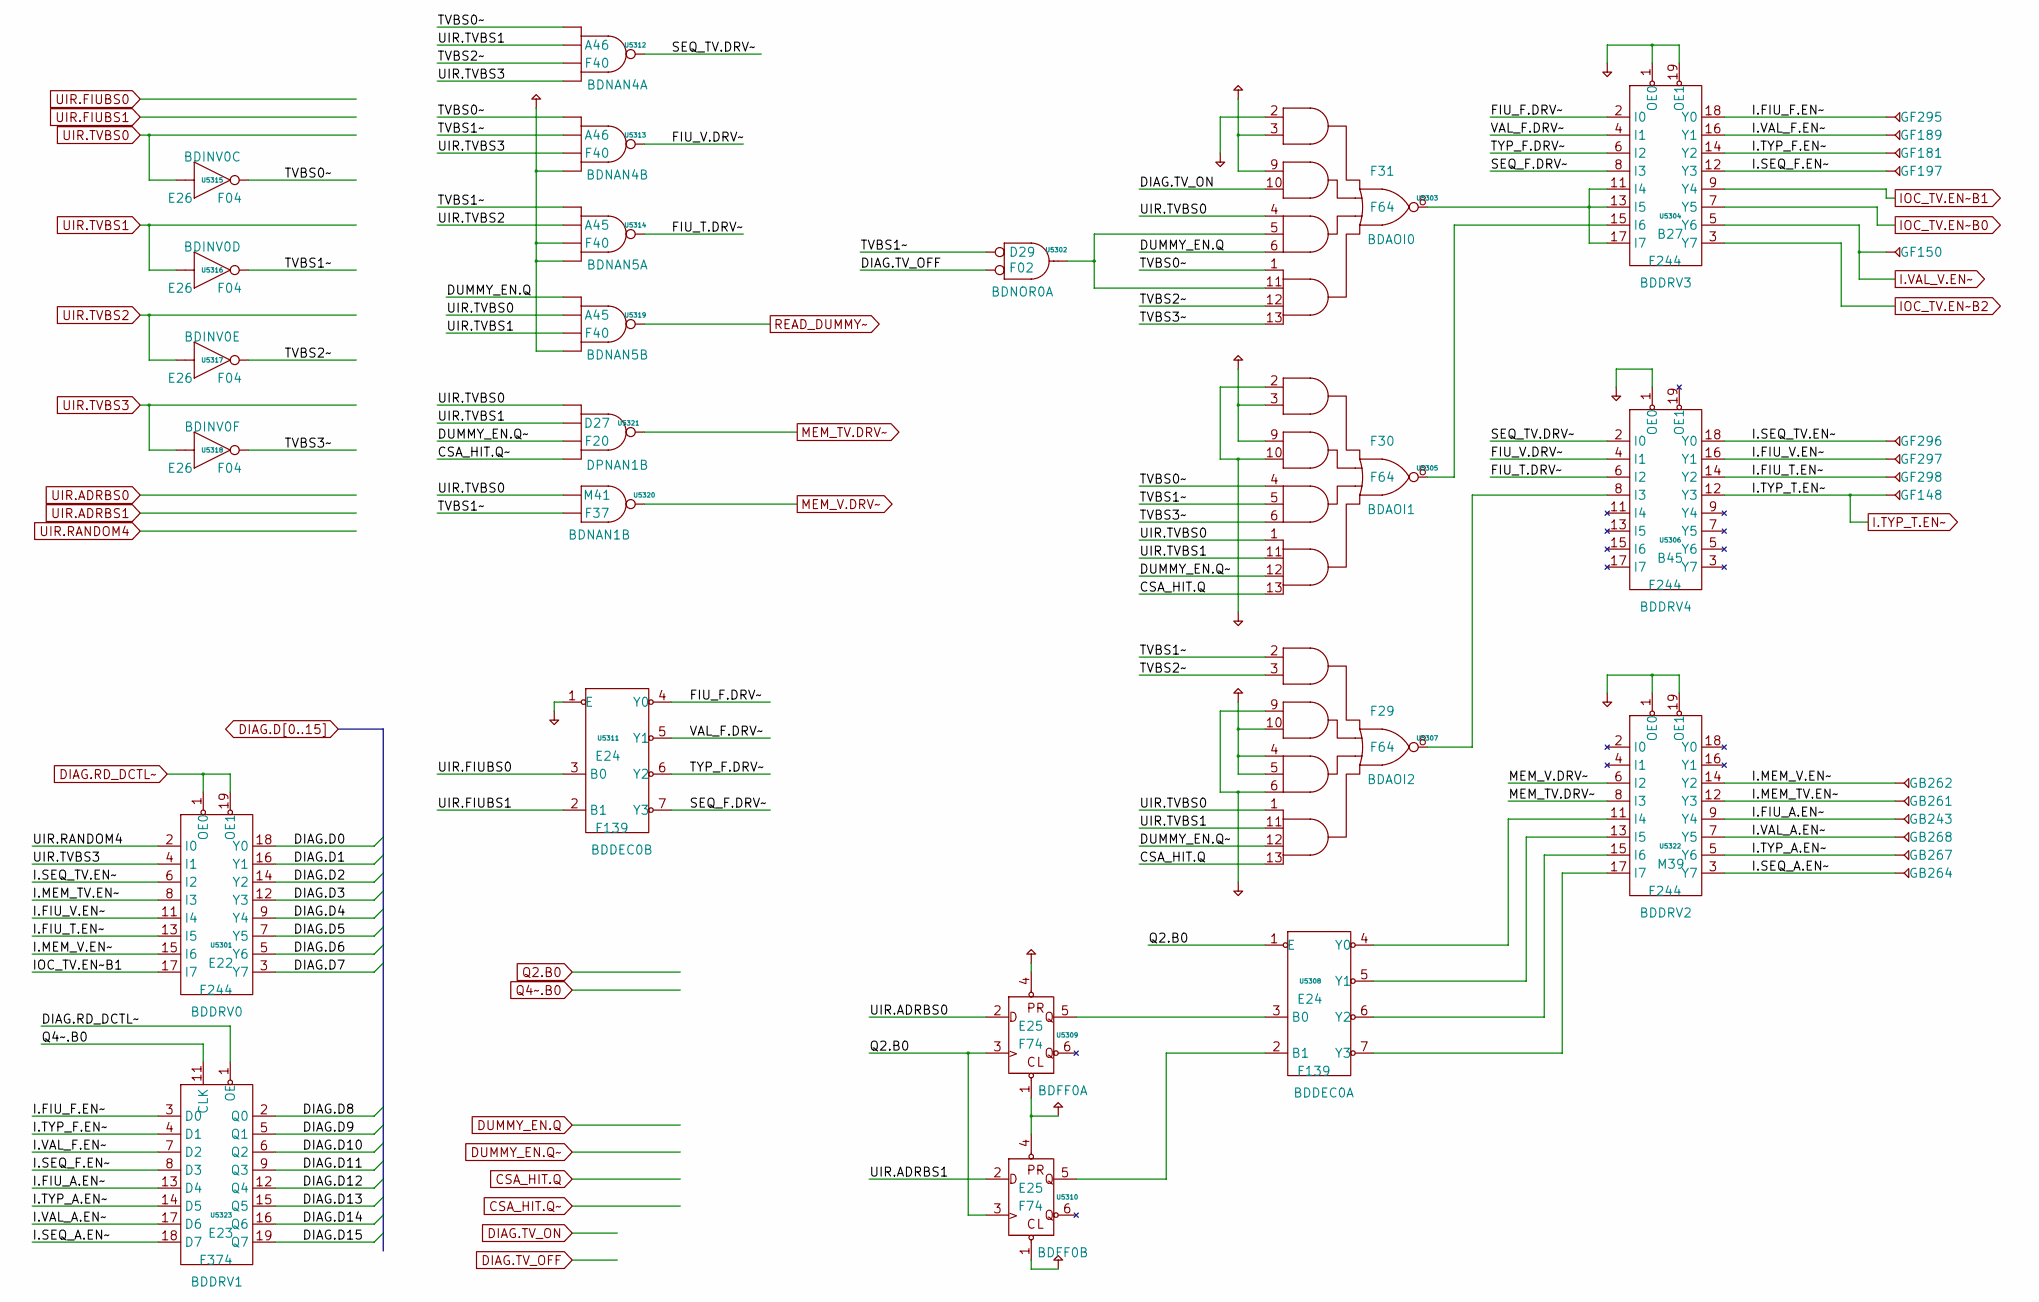
[picture p397: schematic pg_53.kicad_sch]

Parts:
GB243, GB261, GB262, GB264, GB267, GB268: GB
GF148, GF150, GF181, GF189, GF197, GF295, GF296, GF297, GF298: GF
U5301, U5304, U5306, U5322: F244
U5302: F02
U5303, U5305, U5307: F64
U5308, U5311: F139
U5309, U5310: F74
U5312, U5313, U5314, U5319: F40
U5315, U5316, U5317, U5318: F04
U5320: F37
U5321: F20
U5323: F374

Connections:
CSA_HIT.Q: U5305.13 (D3), U5307.13 (D3)
CSA_HIT.Q~: U5321.5 (D3)
DIAG.D0: U5301.18 (Y0)
DIAG.D1: U5301.16 (Y1)
DIAG.D2: U5301.14 (Y2)
DIAG.D3: U5301.12 (Y3)
DIAG.D4: U5301.9 (Y4)
DIAG.D5: U5301.7 (Y5)
DIAG.D6: U5301.5 (Y6)
DIAG.D7: U5301.3 (Y7)
DIAG.D8: U5323.2 (Q0)
DIAG.D9: U5323.5 (Q1)
DIAG.D10: U5323.6 (Q2)
DIAG.D11: U5323.9 (Q3)
DIAG.D12: U5323.12 (Q4)
DIAG.D13: U5323.15 (Q5)
DIAG.D14: U5323.16 (Q6)
DIAG.D15: U5323.19 (Q7)
DIAG.RD_DCTL~: U5301.1 (OE0), U5301.19 (OE1), U5323.1 (OE)
DIAG.TV_OFF: U5302.2 (D1)
DIAG.TV_ON: U5303.10 (B1)
DUMMY_EN.Q: U5303.6 (C2), U5319.1 (D0)
DUMMY_EN.Q~: U5305.12 (D2), U5307.12 (D2), U5321.4 (D2)
FIU_F.DRV~: U5304.2 (I0), U5311.4 (Y0)
FIU_T.DRV~: U5306.6 (I2), U5314.6 (Q)
FIU_V.DRV~: U5306.4 (I1), U5313.6 (Q)
I.FIU_A.EN~: GB243.1, U5322.9 (Y4), U5323.13 (D4)
I.FIU_F.EN~: GF295.1, U5304.18 (Y0), U5323.3 (D0)
I.FIU_T.EN~: GF298.1, U5301.13 (I5), U5306.14 (Y2)
I.FIU_V.EN~: GF297.1, U5301.11 (I4), U5306.16 (Y1)
I.MEM_TV.EN~: GB261.1, U5301.8 (I3), U5322.12 (Y3)
I.MEM_V.EN~: GB262.1, U5301.15 (I6), U5322.14 (Y2)
I.SEQ_A.EN~: GB264.1, U5322.3 (Y7), U5323.18 (D7)
I.SEQ_F.EN~: GF197.1, U5304.12 (Y3), U5323.8 (D3)
I.SEQ_TV.EN~: GF296.1, U5301.6 (I2), U5306.18 (Y0)
I.TYP_A.EN~: GB267.1, U5322.5 (Y6), U5323.14 (D5)
I.TYP_F.EN~: GF181.1, U5304.14 (Y2), U5323.4 (D1)
I.TYP_T.EN~: GF148.1, U5306.12 (Y3)
I.VAL_A.EN~: GB268.1, U5322.7 (Y5), U5323.17 (D6)
I.VAL_F.EN~: GF189.1, U5304.16 (Y1), U5323.7 (D2)
I.VAL_V.EN~: GF150.1, U5304.5 (Y6)
IOC_TV.EN~B0: U5304.7 (Y5)
IOC_TV.EN~B1: U5301.17 (I7), U5304.9 (Y4)
IOC_TV.EN~B2: U5304.3 (Y7)
MEM_TV.DRV~: U5321.6 (Q), U5322.8 (I3)
MEM_V.DRV~: U5320.3 (Q), U5322.6 (I2)
unnamed: U5302.3 (Q), U5303.5 (C1), U5303.11 (D1)
unnamed: U5303.8 (Q), U5304.11 (I4), U5304.13 (I5), U5304.17 (I7)
unnamed: U5304.15 (I6), U5305.8 (Q)
unnamed: U5306.8 (I3), U5307.8 (Q)
unnamed: U5308.2 (B1), U5310.5 (Q)
unnamed: U5308.3 (B0), U5309.5 (Q)
unnamed: U5308.4 (Y0), U5322.11 (I4)
unnamed: U5308.5 (Y1), U5322.13 (I5)
unnamed: U5308.6 (Y2), U5322.15 (I6)
unnamed: U5308.7 (Y3), U5322.17 (I7)
PD: U5303.2 (A0), U5304.1 (OE0), U5304.19 (OE1), U5305.2 (A0), U5305.10 (B1), U5306.1 (OE0), U5307.6 (C2), U5307.9 (B0), U5311.1 (E), U5322.1 (OE0), U5322.19 (OE1)
PU: U5303.3 (A1), U5303.9 (B0), U5305.3 (A1), U5305.9 (B0), U5307.4 (C0), U5307.5 (C1), U5307.10 (B1), U5309.1 (CL_), U5309.4 (PR_), U5310.1 (CL_), U5310.4 (PR_), U5313.5 (D5), U5314.4 (D4), U5314.5 (D5), U5319.5 (D5)
Q2.B0: U5308.1 (E), U5309.3 (CLK), U5310.3 (CLK)
Q4~.B0: U5323.11 (CLK)
READ_DUMMY~: U5319.6 (Q)
SEQ_F.DRV~: U5304.8 (I3), U5311.7 (Y3)
SEQ_TV.DRV~: U5306.2 (I0), U5312.6 (Q)
TVBS0~: U5303.1 (D0), U5305.4 (C0), U5312.1 (D0), U5313.1 (D0), U5315.2 (Q)
TVBS1~: U5302.1 (D0), U5305.5 (C1), U5307.2 (A0), U5313.2 (D3), U5314.1 (D0), U5316.2 (Q), U5320.2 (D1)
TVBS2~: U5303.12 (D2), U5307.3 (A1), U5312.4 (D4), U5317.2 (Q)
TVBS3~: U5303.13 (D3), U5305.6 (C2), U5318.2 (Q)
TYP_F.DRV~: U5304.6 (I2), U5311.6 (Y2)
UIR.ADRBS0: U5309.2 (D)
UIR.ADRBS1: U5310.2 (D)
UIR.FIUBS0: U5311.3 (B0)
UIR.FIUBS1: U5311.2 (B1)
UIR.RANDOM4: U5301.2 (I0)
UIR.TVBS0: U5303.4 (C0), U5305.1 (D0), U5307.1 (D0), U5315.1 (D0), U5319.2 (D3), U5320.1 (D0), U5321.1 (D0)
UIR.TVBS1: U5305.11 (D1), U5307.11 (D1), U5312.2 (D3), U5316.1 (D0), U5319.4 (D4), U5321.2 (D1)
UIR.TVBS2: U5314.2 (D3), U5317.1 (D0)
UIR.TVBS3: U5301.4 (I1), U5312.5 (D5), U5313.4 (D4), U5318.1 (D0)
VAL_F.DRV~: U5304.4 (I1), U5311.5 (Y1)
