Datamuseum-DK/R1000.HwDoc/Schematics/IOC/pg_54.kicad_sch

## KiCad design Schematics/IOC/pg_54.kicad_sch (2023-01-10)

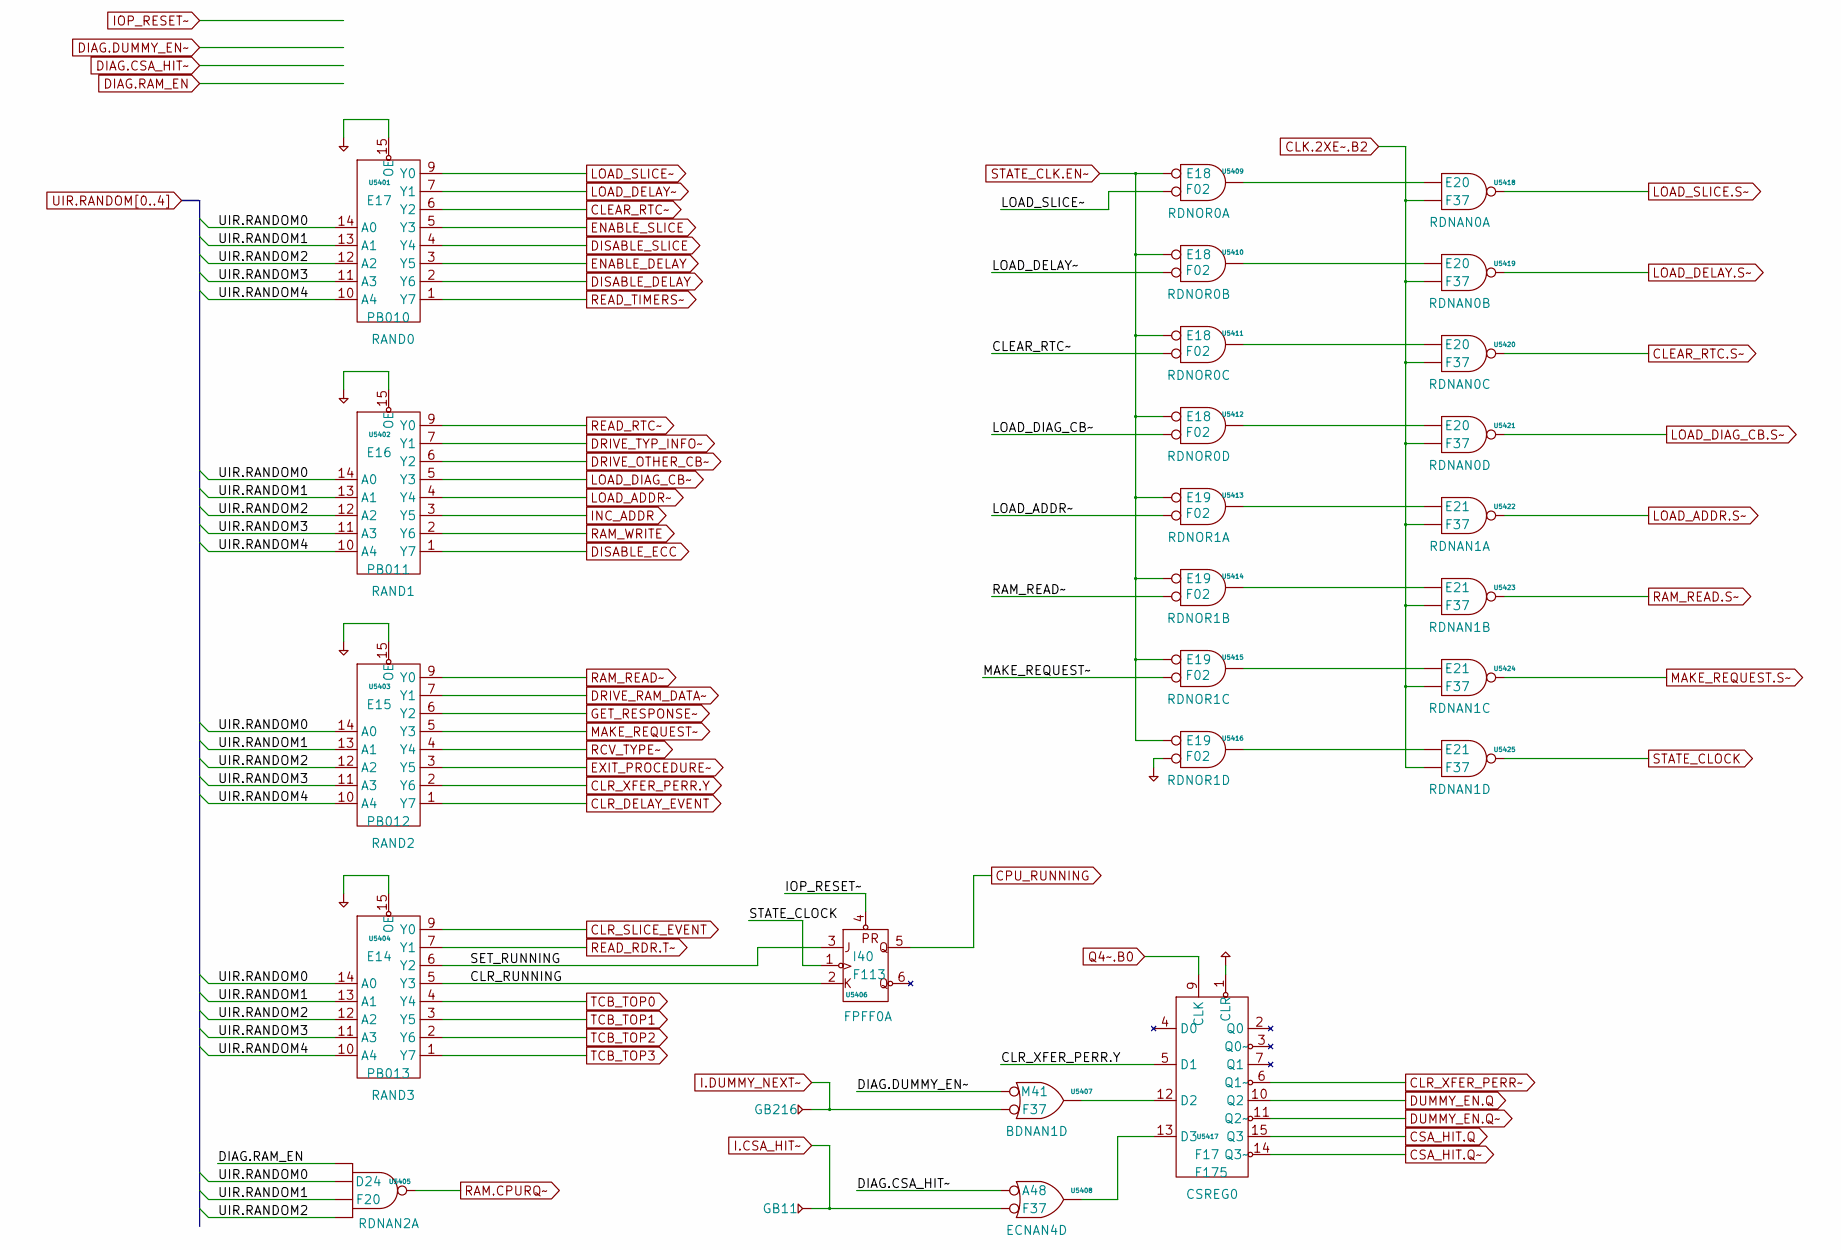
[picture p398: schematic pg_54.kicad_sch]

Parts:
GB11, GB216: GB
U5401: PB010
U5402: PB011
U5403: PB012
U5404: PB013
U5405: F20
U5406: F113
U5407, U5408, U5418, U5419, U5420, U5421, U5422, U5423, U5424, U5425: F37
U5409, U5410, U5411, U5412, U5413, U5414, U5415, U5416: F02
U5417: F175

Connections:
CLEAR_RTC.S~: U5420.3 (Q)
CLEAR_RTC~: U5401.6 (Y2), U5411.2 (D1)
CLK.2XE~.B2: U5418.2 (D1), U5419.2 (D1), U5420.2 (D1), U5421.2 (D1), U5422.2 (D1), U5423.2 (D1), U5424.2 (D1), U5425.2 (D1)
CLR_DELAY_EVENT: U5403.1 (Y7)
CLR_RUNNING: U5404.5 (Y3), U5406.2 (K)
CLR_SLICE_EVENT: U5404.9 (Y0)
CLR_XFER_PERR.Y: U5403.2 (Y6), U5417.5 (D1)
CLR_XFER_PERR~: U5417.6 (Q1~)
CPU_RUNNING: U5406.5 (Q)
CSA_HIT.Q: U5417.15 (Q3)
CSA_HIT.Q~: U5417.14 (Q3~)
DIAG.CSA_HIT~: U5408.1 (D0)
DIAG.DUMMY_EN~: U5407.1 (D0)
DIAG.RAM_EN: U5405.1 (D0)
DISABLE_DELAY: U5401.2 (Y6)
DISABLE_ECC: U5402.1 (Y7)
DISABLE_SLICE: U5401.4 (Y4)
DRIVE_OTHER_CB~: U5402.6 (Y2)
DRIVE_RAM_DATA~: U5403.7 (Y1)
DRIVE_TYP_INFO~: U5402.7 (Y1)
DUMMY_EN.Q: U5417.10 (Q2)
DUMMY_EN.Q~: U5417.11 (Q2~)
ENABLE_DELAY: U5401.3 (Y5)
ENABLE_SLICE: U5401.5 (Y3)
EXIT_PROCEDURE~: U5403.3 (Y5)
GET_RESPONSE~: U5403.6 (Y2)
I.CSA_HIT~: GB11.1, U5408.2 (D1)
I.DUMMY_NEXT~: GB216.1, U5407.2 (D1)
INC_ADDR: U5402.3 (Y5)
IOP_RESET~: U5406.4 (PR_)
LOAD_ADDR.S~: U5422.3 (Q)
LOAD_ADDR~: U5402.4 (Y4), U5413.2 (D1)
LOAD_DELAY.S~: U5419.3 (Q)
LOAD_DELAY~: U5401.7 (Y1), U5410.2 (D1)
LOAD_DIAG_CB.S~: U5421.3 (Q)
LOAD_DIAG_CB~: U5402.5 (Y3), U5412.2 (D1)
LOAD_SLICE.S~: U5418.3 (Q)
LOAD_SLICE~: U5401.9 (Y0), U5409.2 (D1)
MAKE_REQUEST.S~: U5424.3 (Q)
MAKE_REQUEST~: U5403.5 (Y3), U5415.2 (D1)
unnamed: U5407.3 (Q), U5417.12 (D2)
unnamed: U5408.3 (Q), U5417.13 (D3)
unnamed: U5409.3 (Q), U5418.1 (D0)
unnamed: U5410.3 (Q), U5419.1 (D0)
unnamed: U5411.3 (Q), U5420.1 (D0)
unnamed: U5412.3 (Q), U5421.1 (D0)
unnamed: U5413.3 (Q), U5422.1 (D0)
unnamed: U5414.3 (Q), U5423.1 (D0)
unnamed: U5415.3 (Q), U5424.1 (D0)
unnamed: U5416.3 (Q), U5425.1 (D0)
PD: U5401.15 (OE), U5402.15 (OE), U5403.15 (OE), U5404.15 (OE), U5416.2 (D1)
PU: U5417.1 (CLR)
Q4~.B0: U5417.9 (CLK)
RAM.CPURQ~: U5405.6 (Q)
RAM_READ.S~: U5423.3 (Q)
RAM_READ~: U5403.9 (Y0), U5414.2 (D1)
RAM_WRITE: U5402.2 (Y6)
RCV_TYPE~: U5403.4 (Y4)
READ_RDR.T~: U5404.7 (Y1)
READ_RTC~: U5402.9 (Y0)
READ_TIMERS~: U5401.1 (Y7)
SET_RUNNING: U5404.6 (Y2), U5406.3 (J)
STATE_CLK.EN~: U5409.1 (D0), U5410.1 (D0), U5411.1 (D0), U5412.1 (D0), U5413.1 (D0), U5414.1 (D0), U5415.1 (D0), U5416.1 (D0)
STATE_CLOCK: U5406.1 (CLK_), U5425.3 (Q)
TCB_TOP0: U5404.4 (Y4)
TCB_TOP1: U5404.3 (Y5)
TCB_TOP2: U5404.2 (Y6)
TCB_TOP3: U5404.1 (Y7)
UIR.RANDOM0: U5401.14 (A0), U5402.14 (A0), U5403.14 (A0), U5404.14 (A0), U5405.2 (D1)
UIR.RANDOM1: U5401.13 (A1), U5402.13 (A1), U5403.13 (A1), U5404.13 (A1), U5405.4 (D2)
UIR.RANDOM2: U5401.12 (A2), U5402.12 (A2), U5403.12 (A2), U5404.12 (A2), U5405.5 (D3)
UIR.RANDOM3: U5401.11 (A3), U5402.11 (A3), U5403.11 (A3), U5404.11 (A3)
UIR.RANDOM4: U5401.10 (A4), U5402.10 (A4), U5403.10 (A4), U5404.10 (A4)
