Datamuseum-DK/R1000.HwDoc/Schematics/IOC/pg_55.kicad_sch

## KiCad design Schematics/IOC/pg_55.kicad_sch (2023-01-10)

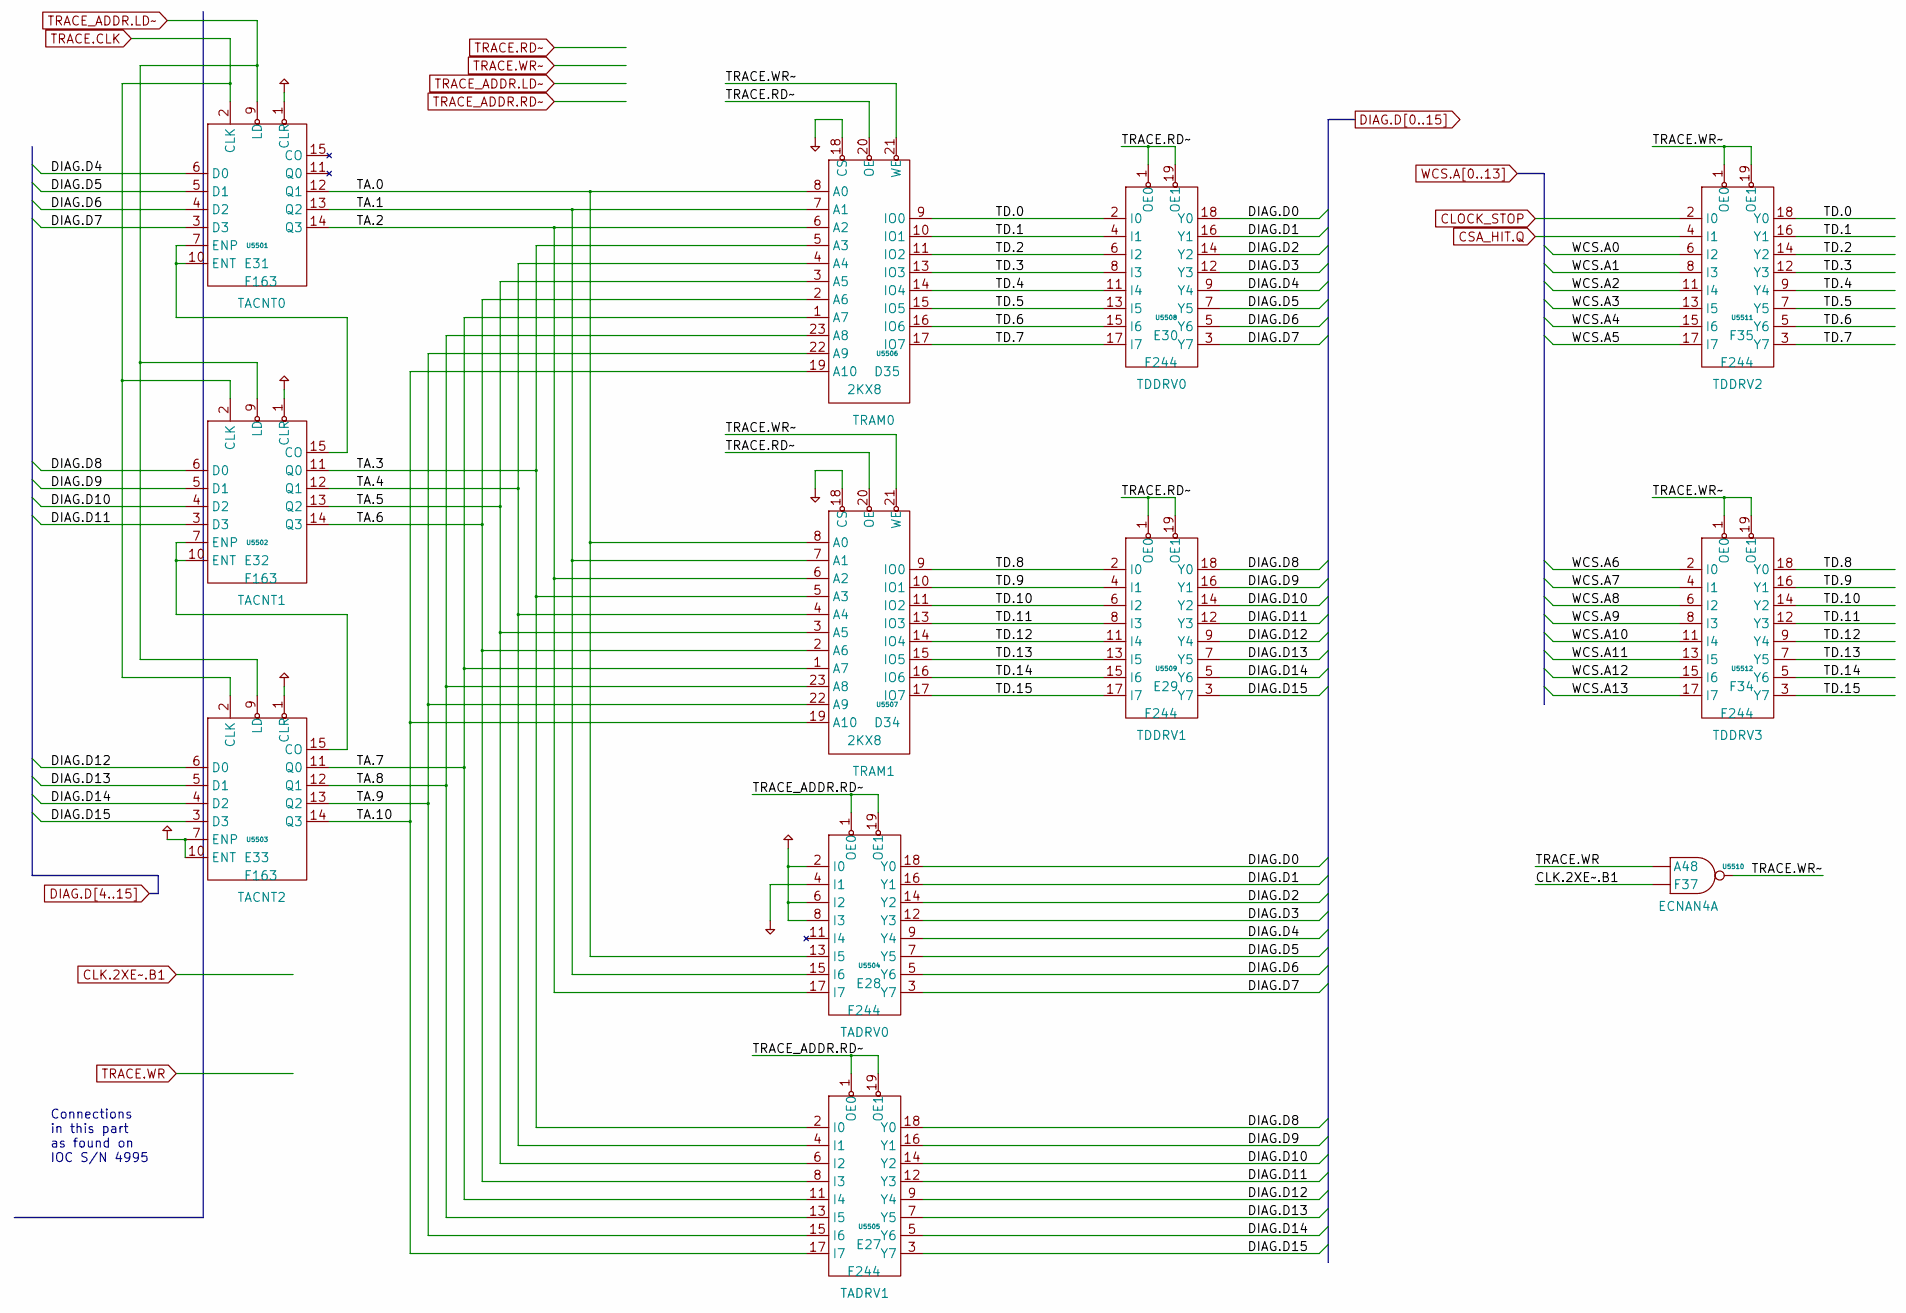
[picture p399: schematic pg_55.kicad_sch]

Parts:
U5501, U5502, U5503: F163
U5504, U5505, U5508, U5509, U5511, U5512: F244
U5506, U5507: 2KX8
U5510: F37

Connections:
CLK.2XE~.B1: U5510.2 (D1)
CLOCK_STOP: U5511.2 (I0)
CSA_HIT.Q: U5511.4 (I1)
DIAG.D0: U5504.18 (Y0), U5508.18 (Y0)
DIAG.D1: U5504.16 (Y1), U5508.16 (Y1)
DIAG.D2: U5504.14 (Y2), U5508.14 (Y2)
DIAG.D3: U5504.12 (Y3), U5508.12 (Y3)
DIAG.D4: U5501.6 (D0), U5504.9 (Y4), U5508.9 (Y4)
DIAG.D5: U5501.5 (D1), U5504.7 (Y5), U5508.7 (Y5)
DIAG.D6: U5501.4 (D2), U5504.5 (Y6), U5508.5 (Y6)
DIAG.D7: U5501.3 (D3), U5504.3 (Y7), U5508.3 (Y7)
DIAG.D8: U5502.6 (D0), U5505.18 (Y0), U5509.18 (Y0)
DIAG.D9: U5502.5 (D1), U5505.16 (Y1), U5509.16 (Y1)
DIAG.D10: U5502.4 (D2), U5505.14 (Y2), U5509.14 (Y2)
DIAG.D11: U5502.3 (D3), U5505.12 (Y3), U5509.12 (Y3)
DIAG.D12: U5503.6 (D0), U5505.9 (Y4), U5509.9 (Y4)
DIAG.D13: U5503.5 (D1), U5505.7 (Y5), U5509.7 (Y5)
DIAG.D14: U5503.4 (D2), U5505.5 (Y6), U5509.5 (Y6)
DIAG.D15: U5503.3 (D3), U5505.3 (Y7), U5509.3 (Y7)
unnamed: U5501.7 (ENP), U5501.10 (ENT), U5502.15 (CO)
unnamed: U5502.7 (ENP), U5502.10 (ENT), U5503.15 (CO)
PD: U5504.4 (I1), U5506.18 (CS), U5507.18 (CS)
PU: U5501.1 (CLR), U5502.1 (CLR), U5503.1 (CLR), U5503.7 (ENP), U5503.10 (ENT), U5504.2 (I0), U5504.6 (I2), U5504.8 (I3)
TA.0: U5501.12 (Q1), U5504.13 (I5), U5506.8 (A0), U5507.8 (A0)
TA.1: U5501.13 (Q2), U5504.15 (I6), U5506.7 (A1), U5507.7 (A1)
TA.2: U5501.14 (Q3), U5504.17 (I7), U5506.6 (A2), U5507.6 (A2)
TA.3: U5502.11 (Q0), U5505.2 (I0), U5506.5 (A3), U5507.5 (A3)
TA.4: U5502.12 (Q1), U5505.4 (I1), U5506.4 (A4), U5507.4 (A4)
TA.5: U5502.13 (Q2), U5505.6 (I2), U5506.3 (A5), U5507.3 (A5)
TA.6: U5502.14 (Q3), U5505.8 (I3), U5506.2 (A6), U5507.2 (A6)
TA.7: U5503.11 (Q0), U5505.11 (I4), U5506.1 (A7), U5507.1 (A7)
TA.8: U5503.12 (Q1), U5505.13 (I5), U5506.23 (A8), U5507.23 (A8)
TA.9: U5503.13 (Q2), U5505.15 (I6), U5506.22 (A9), U5507.22 (A9)
TA.10: U5503.14 (Q3), U5505.17 (I7), U5506.19 (A10), U5507.19 (A10)
TD.0: U5506.9 (IO0), U5508.2 (I0), U5511.18 (Y0)
TD.1: U5506.10 (IO1), U5508.4 (I1), U5511.16 (Y1)
TD.2: U5506.11 (IO2), U5508.6 (I2), U5511.14 (Y2)
TD.3: U5506.13 (IO3), U5508.8 (I3), U5511.12 (Y3)
TD.4: U5506.14 (IO4), U5508.11 (I4), U5511.9 (Y4)
TD.5: U5506.15 (IO5), U5508.13 (I5), U5511.7 (Y5)
TD.6: U5506.16 (IO6), U5508.15 (I6), U5511.5 (Y6)
TD.7: U5506.17 (IO7), U5508.17 (I7), U5511.3 (Y7)
TD.8: U5507.9 (IO0), U5509.2 (I0), U5512.18 (Y0)
TD.9: U5507.10 (IO1), U5509.4 (I1), U5512.16 (Y1)
TD.10: U5507.11 (IO2), U5509.6 (I2), U5512.14 (Y2)
TD.11: U5507.13 (IO3), U5509.8 (I3), U5512.12 (Y3)
TD.12: U5507.14 (IO4), U5509.11 (I4), U5512.9 (Y4)
TD.13: U5507.15 (IO5), U5509.13 (I5), U5512.7 (Y5)
TD.14: U5507.16 (IO6), U5509.15 (I6), U5512.5 (Y6)
TD.15: U5507.17 (IO7), U5509.17 (I7), U5512.3 (Y7)
TRACE.CLK: U5501.2 (CLK), U5502.2 (CLK), U5503.2 (CLK)
TRACE.RD~: U5506.20 (OE), U5507.20 (OE), U5508.1 (OE0), U5508.19 (OE1), U5509.1 (OE0), U5509.19 (OE1)
TRACE.WR: U5510.1 (D0)
TRACE.WR~: U5506.21 (WE), U5507.21 (WE), U5510.3 (Q), U5511.1 (OE0), U5511.19 (OE1), U5512.1 (OE0), U5512.19 (OE1)
TRACE_ADDR.LD~: U5501.9 (LD), U5502.9 (LD), U5503.9 (LD)
TRACE_ADDR.RD~: U5504.1 (OE0), U5504.19 (OE1), U5505.1 (OE0), U5505.19 (OE1)
WCS.A0: U5511.6 (I2)
WCS.A1: U5511.8 (I3)
WCS.A2: U5511.11 (I4)
WCS.A3: U5511.13 (I5)
WCS.A4: U5511.15 (I6)
WCS.A5: U5511.17 (I7)
WCS.A6: U5512.2 (I0)
WCS.A7: U5512.4 (I1)
WCS.A8: U5512.6 (I2)
WCS.A9: U5512.8 (I3)
WCS.A10: U5512.11 (I4)
WCS.A11: U5512.13 (I5)
WCS.A12: U5512.15 (I6)
WCS.A13: U5512.17 (I7)

Notes on the sheet:
Connections in this part as found on IOC S/N 4995
