Datamuseum-DK/R1000.HwDoc/Schematics/IOC/pg_56.kicad_sch

## KiCad design Schematics/IOC/pg_56.kicad_sch (2023-01-10)

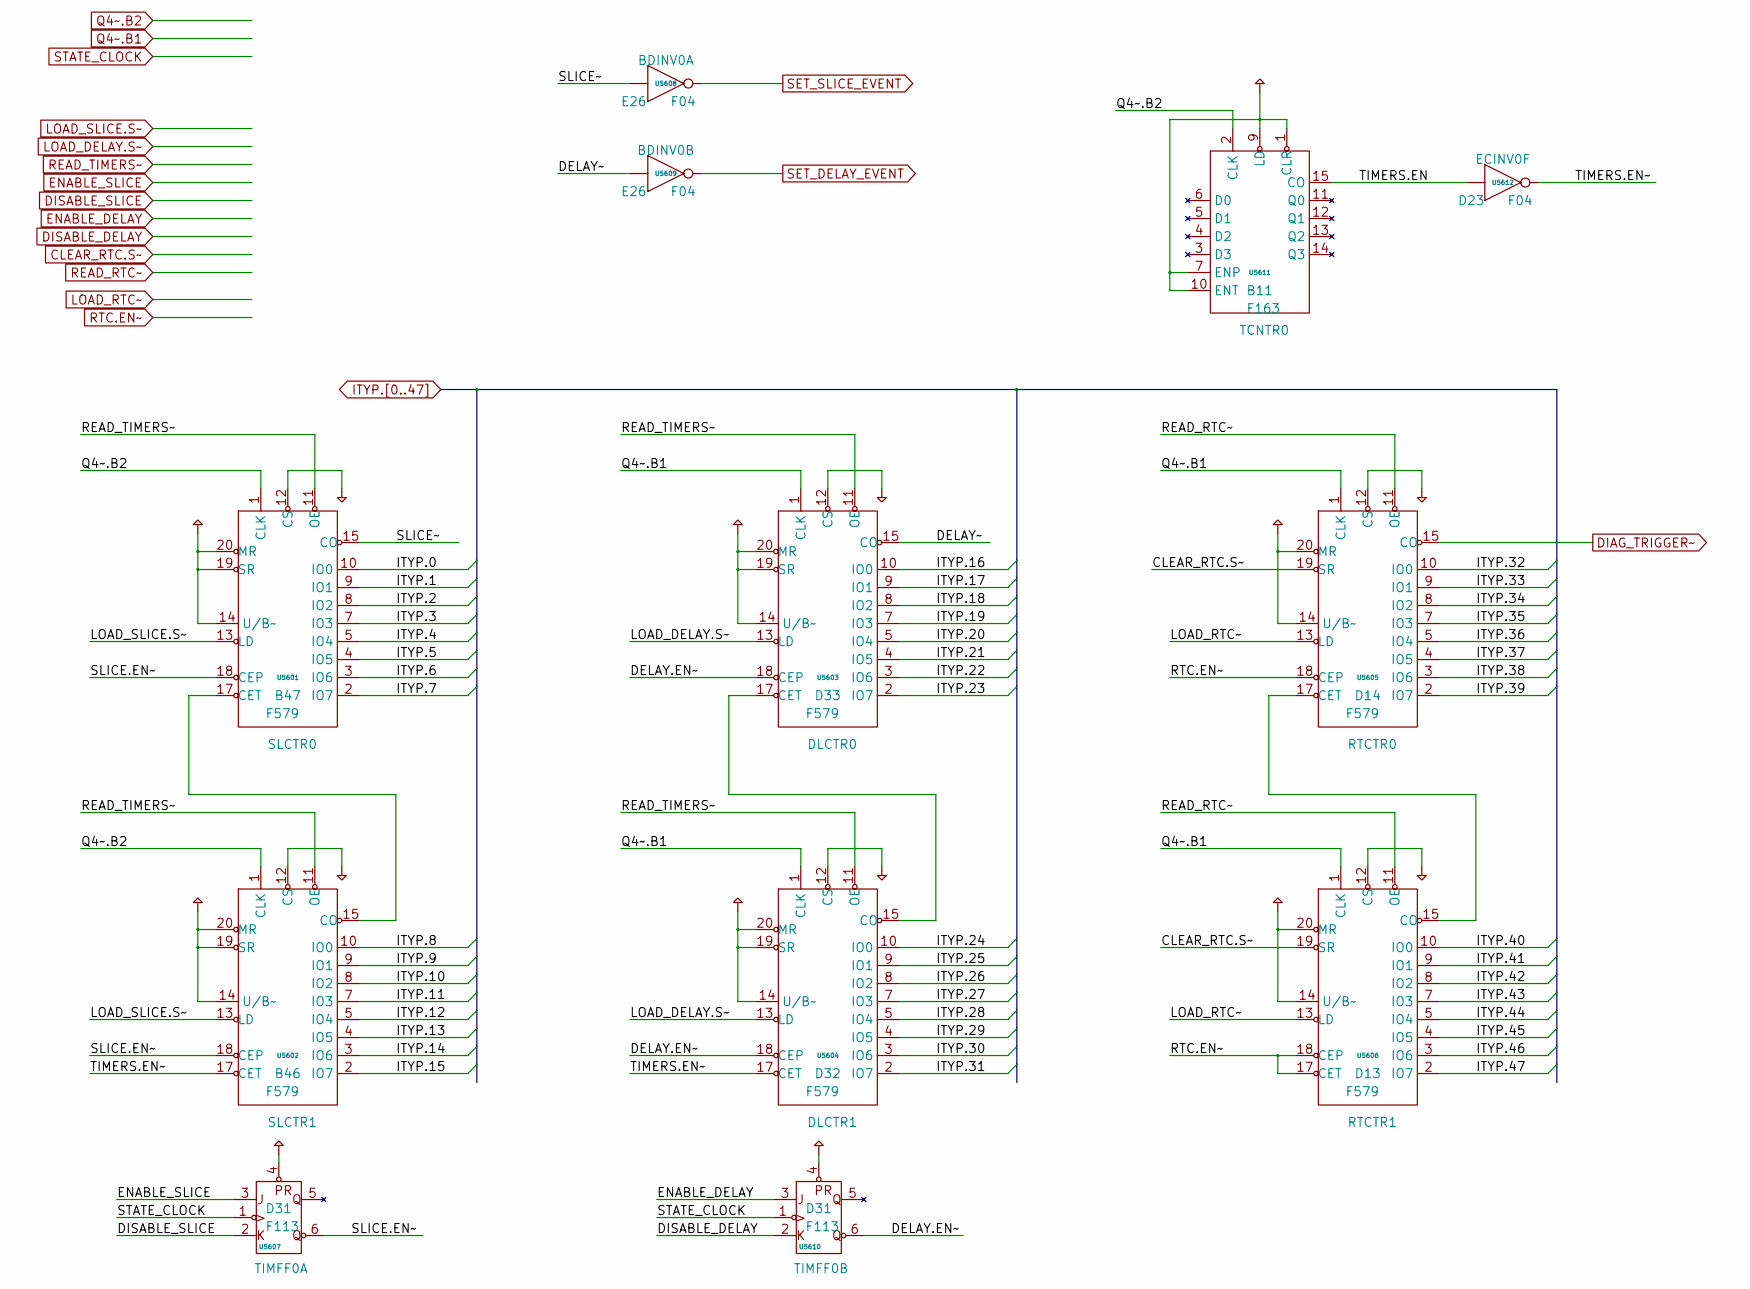
[picture p400: schematic pg_56.kicad_sch]

Parts:
U5601, U5602, U5603, U5604, U5605, U5606: F579
U5607, U5610: F113
U5608, U5609, U5612: F04
U5611: F163

Connections:
CLEAR_RTC.S~: U5605.19 (SR), U5606.19 (SR)
DELAY.EN~: U5603.18 (CEP), U5604.18 (CEP), U5610.6 (Q_)
DELAY~: U5603.15 (CO), U5609.1 (D0)
DIAG_TRIGGER~: U5605.15 (CO)
DISABLE_DELAY: U5610.2 (K)
DISABLE_SLICE: U5607.2 (K)
ENABLE_DELAY: U5610.3 (J)
ENABLE_SLICE: U5607.3 (J)
ITYP.0: U5601.10 (IO0)
ITYP.1: U5601.9 (IO1)
ITYP.2: U5601.8 (IO2)
ITYP.3: U5601.7 (IO3)
ITYP.4: U5601.5 (IO4)
ITYP.5: U5601.4 (IO5)
ITYP.6: U5601.3 (IO6)
ITYP.7: U5601.2 (IO7)
ITYP.8: U5602.10 (IO0)
ITYP.9: U5602.9 (IO1)
ITYP.10: U5602.8 (IO2)
ITYP.11: U5602.7 (IO3)
ITYP.12: U5602.5 (IO4)
ITYP.13: U5602.4 (IO5)
ITYP.14: U5602.3 (IO6)
ITYP.15: U5602.2 (IO7)
ITYP.16: U5603.10 (IO0)
ITYP.17: U5603.9 (IO1)
ITYP.18: U5603.8 (IO2)
ITYP.19: U5603.7 (IO3)
ITYP.20: U5603.5 (IO4)
ITYP.21: U5603.4 (IO5)
ITYP.22: U5603.3 (IO6)
ITYP.23: U5603.2 (IO7)
ITYP.24: U5604.10 (IO0)
ITYP.25: U5604.9 (IO1)
ITYP.26: U5604.8 (IO2)
ITYP.27: U5604.7 (IO3)
ITYP.28: U5604.5 (IO4)
ITYP.29: U5604.4 (IO5)
ITYP.30: U5604.3 (IO6)
ITYP.31: U5604.2 (IO7)
ITYP.32: U5605.10 (IO0)
ITYP.33: U5605.9 (IO1)
ITYP.34: U5605.8 (IO2)
ITYP.35: U5605.7 (IO3)
ITYP.36: U5605.5 (IO4)
ITYP.37: U5605.4 (IO5)
ITYP.38: U5605.3 (IO6)
ITYP.39: U5605.2 (IO7)
ITYP.40: U5606.10 (IO0)
ITYP.41: U5606.9 (IO1)
ITYP.42: U5606.8 (IO2)
ITYP.43: U5606.7 (IO3)
ITYP.44: U5606.5 (IO4)
ITYP.45: U5606.4 (IO5)
ITYP.46: U5606.3 (IO6)
ITYP.47: U5606.2 (IO7)
LOAD_DELAY.S~: U5603.13 (LD), U5604.13 (LD)
LOAD_RTC~: U5605.13 (LD), U5606.13 (LD)
LOAD_SLICE.S~: U5601.13 (LD), U5602.13 (LD)
unnamed: U5601.17 (CET), U5602.15 (CO)
unnamed: U5603.17 (CET), U5604.15 (CO)
unnamed: U5605.17 (CET), U5606.15 (CO)
PD: U5601.12 (CS), U5602.12 (CS), U5603.12 (CS), U5604.12 (CS), U5605.12 (CS), U5606.12 (CS)
PU: U5601.14 (U/B~), U5601.19 (SR), U5601.20 (MR), U5602.14 (U/B~), U5602.19 (SR), U5602.20 (MR), U5603.14 (U/B~), U5603.19 (SR), U5603.20 (MR), U5604.14 (U/B~), U5604.19 (SR), U5604.20 (MR), U5605.14 (U/B~), U5605.20 (MR), U5606.14 (U/B~), U5606.20 (MR), U5607.4 (PR_), U5610.4 (PR_), U5611.1 (CLR), U5611.7 (ENP), U5611.9 (LD), U5611.10 (ENT)
Q4~.B1: U5603.1 (CLK), U5604.1 (CLK), U5605.1 (CLK), U5606.1 (CLK)
Q4~.B2: U5601.1 (CLK), U5602.1 (CLK), U5611.2 (CLK)
READ_RTC~: U5605.11 (OE), U5606.11 (OE)
READ_TIMERS~: U5601.11 (OE), U5602.11 (OE), U5603.11 (OE), U5604.11 (OE)
RTC.EN~: U5605.18 (CEP), U5606.17 (CET), U5606.18 (CEP)
SET_DELAY_EVENT: U5609.2 (Q)
SET_SLICE_EVENT: U5608.2 (Q)
SLICE.EN~: U5601.18 (CEP), U5602.18 (CEP), U5607.6 (Q_)
SLICE~: U5601.15 (CO), U5608.1 (D0)
STATE_CLOCK: U5607.1 (CLK_), U5610.1 (CLK_)
TIMERS.EN: U5611.15 (CO), U5612.1 (D0)
TIMERS.EN~: U5602.17 (CET), U5604.17 (CET), U5612.2 (Q)
