Datamuseum-DK/R1000.HwDoc/Schematics/IOC/pg_57.kicad_sch

## KiCad design Schematics/IOC/pg_57.kicad_sch (2023-01-10)

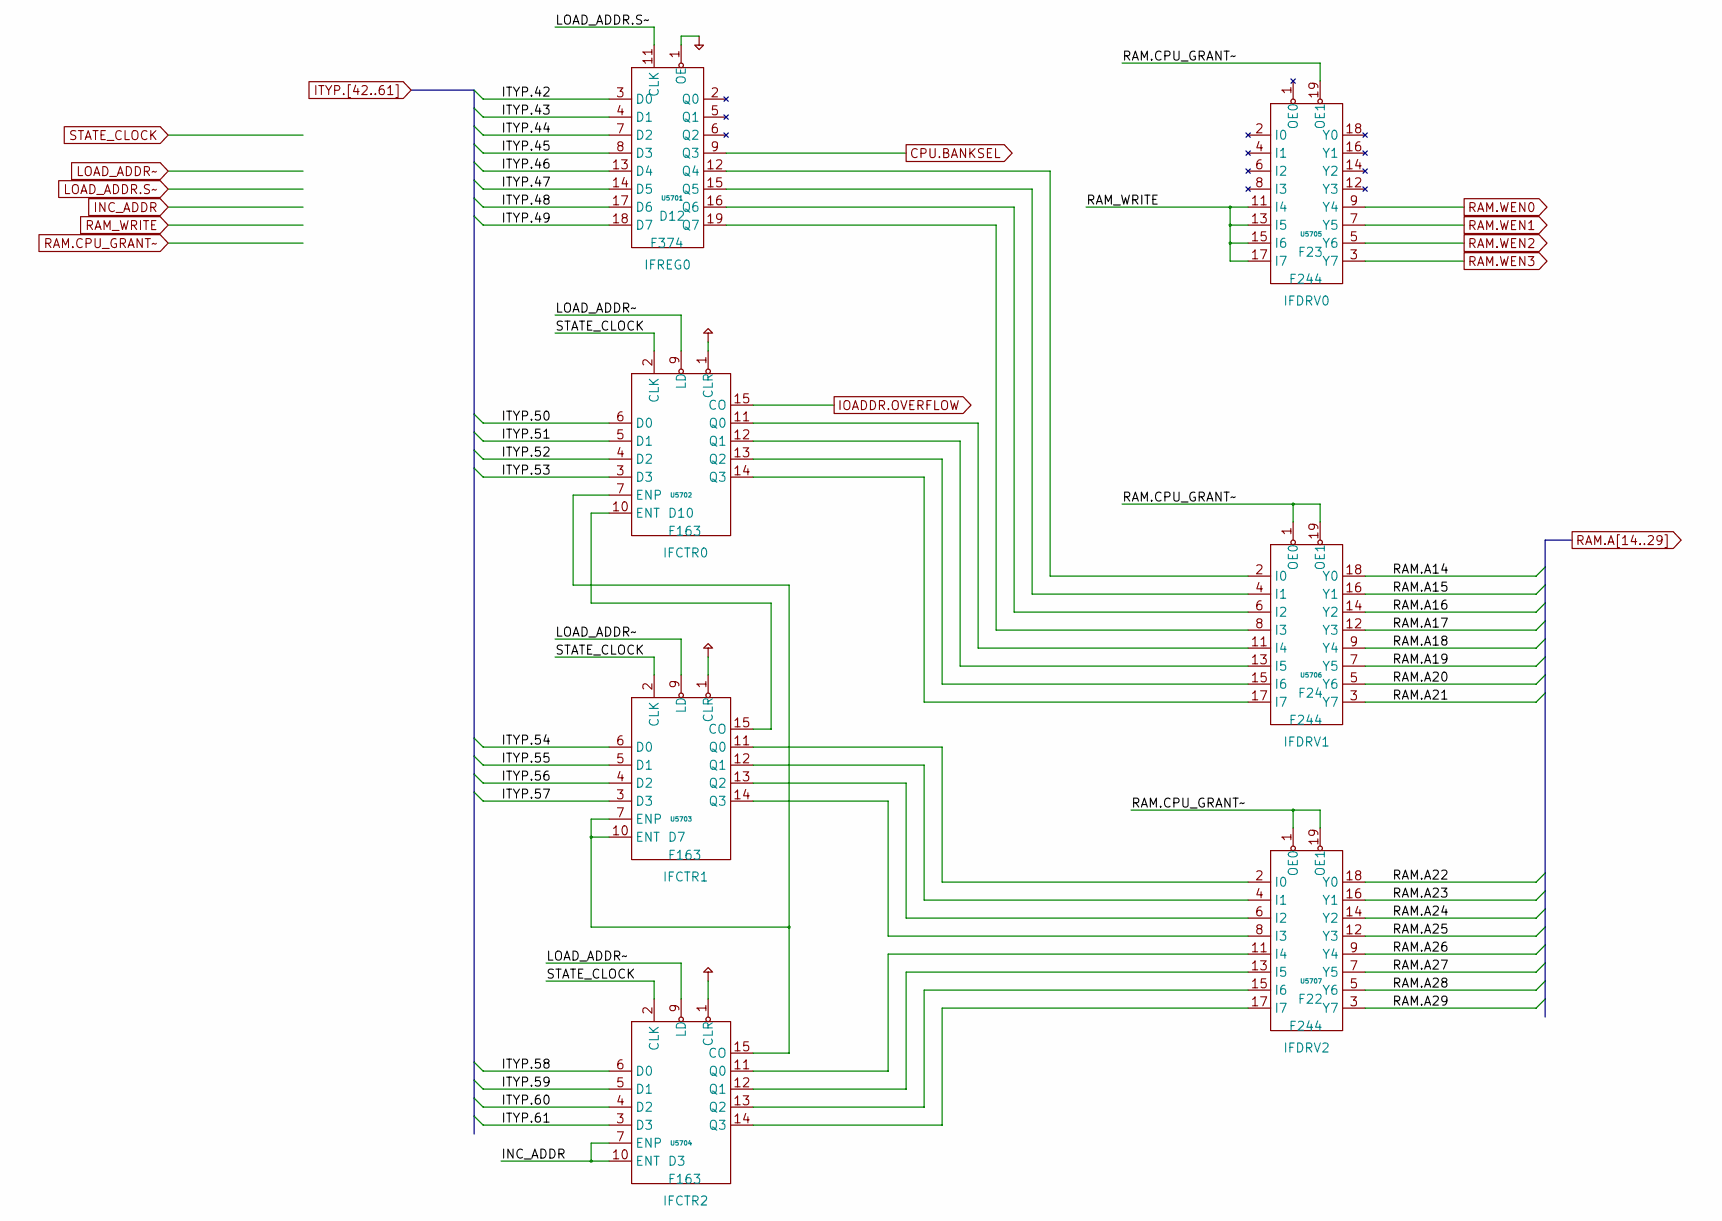
[picture p401: schematic pg_57.kicad_sch]

Parts:
U5701: F374
U5702, U5703, U5704: F163
U5705, U5706, U5707: F244

Connections:
CPU.BANKSEL: U5701.9 (Q3)
INC_ADDR: U5704.7 (ENP), U5704.10 (ENT)
IOADDR.OVERFLOW: U5702.15 (CO)
ITYP.42: U5701.3 (D0)
ITYP.43: U5701.4 (D1)
ITYP.44: U5701.7 (D2)
ITYP.45: U5701.8 (D3)
ITYP.46: U5701.13 (D4)
ITYP.47: U5701.14 (D5)
ITYP.48: U5701.17 (D6)
ITYP.49: U5701.18 (D7)
ITYP.50: U5702.6 (D0)
ITYP.51: U5702.5 (D1)
ITYP.52: U5702.4 (D2)
ITYP.53: U5702.3 (D3)
ITYP.54: U5703.6 (D0)
ITYP.55: U5703.5 (D1)
ITYP.56: U5703.4 (D2)
ITYP.57: U5703.3 (D3)
ITYP.58: U5704.6 (D0)
ITYP.59: U5704.5 (D1)
ITYP.60: U5704.4 (D2)
ITYP.61: U5704.3 (D3)
LOAD_ADDR.S~: U5701.11 (CLK)
LOAD_ADDR~: U5702.9 (LD), U5703.9 (LD), U5704.9 (LD)
unnamed: U5701.12 (Q4), U5706.2 (I0)
unnamed: U5701.15 (Q5), U5706.4 (I1)
unnamed: U5701.16 (Q6), U5706.6 (I2)
unnamed: U5701.19 (Q7), U5706.8 (I3)
unnamed: U5702.7 (ENP), U5703.7 (ENP), U5703.10 (ENT), U5704.15 (CO)
unnamed: U5702.10 (ENT), U5703.15 (CO)
unnamed: U5702.11 (Q0), U5706.11 (I4)
unnamed: U5702.12 (Q1), U5706.13 (I5)
unnamed: U5702.13 (Q2), U5706.15 (I6)
unnamed: U5702.14 (Q3), U5706.17 (I7)
unnamed: U5703.11 (Q0), U5707.2 (I0)
unnamed: U5703.12 (Q1), U5707.4 (I1)
unnamed: U5703.13 (Q2), U5707.6 (I2)
unnamed: U5703.14 (Q3), U5707.8 (I3)
unnamed: U5704.11 (Q0), U5707.11 (I4)
unnamed: U5704.12 (Q1), U5707.13 (I5)
unnamed: U5704.13 (Q2), U5707.15 (I6)
unnamed: U5704.14 (Q3), U5707.17 (I7)
PD: U5701.1 (OE)
PU: U5702.1 (CLR), U5703.1 (CLR), U5704.1 (CLR)
RAM.A14: U5706.18 (Y0)
RAM.A15: U5706.16 (Y1)
RAM.A16: U5706.14 (Y2)
RAM.A17: U5706.12 (Y3)
RAM.A18: U5706.9 (Y4)
RAM.A19: U5706.7 (Y5)
RAM.A20: U5706.5 (Y6)
RAM.A21: U5706.3 (Y7)
RAM.A22: U5707.18 (Y0)
RAM.A23: U5707.16 (Y1)
RAM.A24: U5707.14 (Y2)
RAM.A25: U5707.12 (Y3)
RAM.A26: U5707.9 (Y4)
RAM.A27: U5707.7 (Y5)
RAM.A28: U5707.5 (Y6)
RAM.A29: U5707.3 (Y7)
RAM.CPU_GRANT~: U5705.19 (OE1), U5706.1 (OE0), U5706.19 (OE1), U5707.1 (OE0), U5707.19 (OE1)
RAM.WEN0: U5705.9 (Y4)
RAM.WEN1: U5705.7 (Y5)
RAM.WEN2: U5705.5 (Y6)
RAM.WEN3: U5705.3 (Y7)
RAM_WRITE: U5705.11 (I4), U5705.13 (I5), U5705.15 (I6), U5705.17 (I7)
STATE_CLOCK: U5702.2 (CLK), U5703.2 (CLK), U5704.2 (CLK)
