Datamuseum-DK/R1000.HwDoc/Schematics/IOC/pg_58.kicad_sch

## KiCad design Schematics/IOC/pg_58.kicad_sch (2023-01-10)

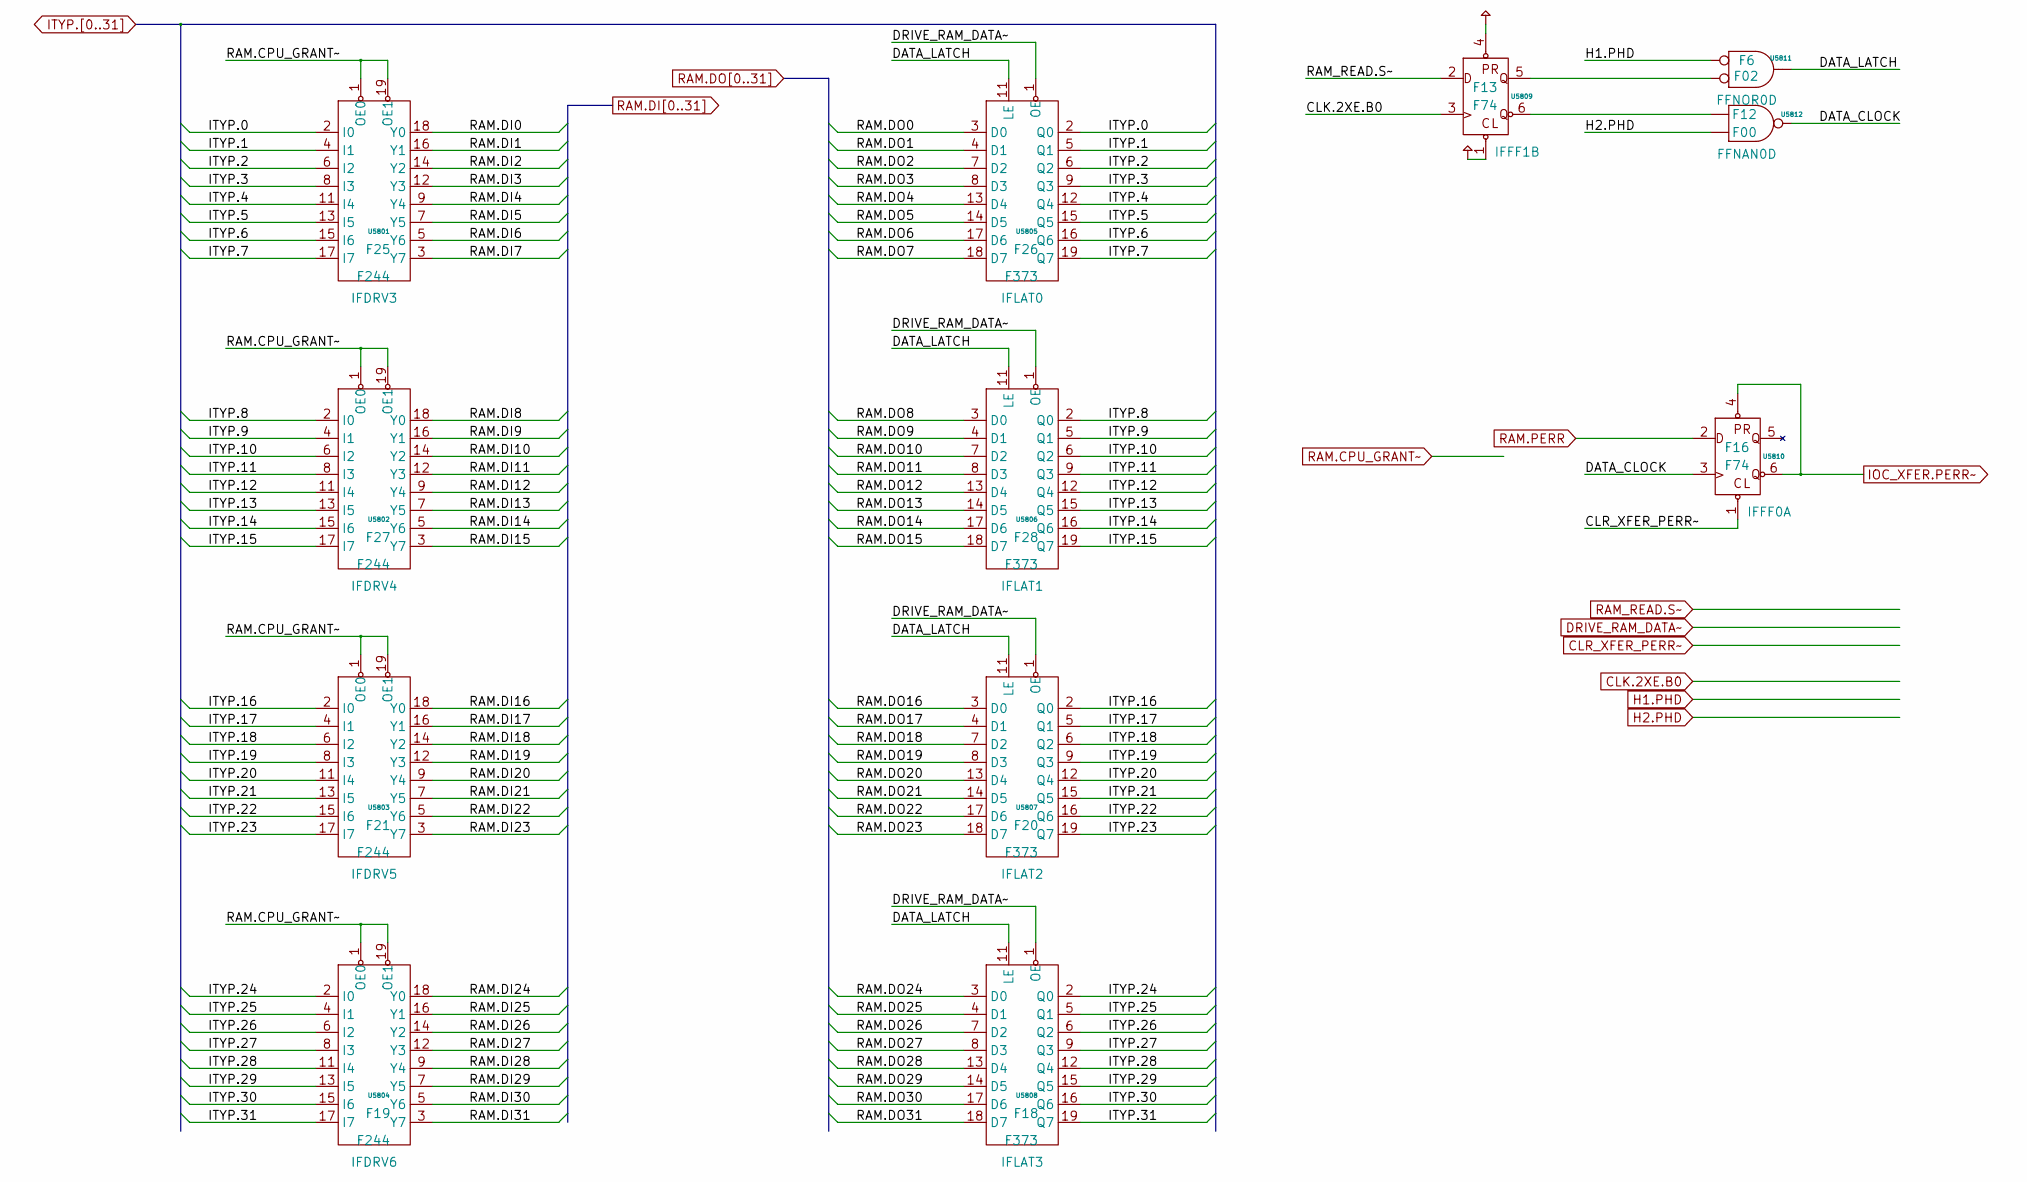
[picture p402: schematic pg_58.kicad_sch]

Parts:
U5801, U5802, U5803, U5804: F244
U5805, U5806, U5807, U5808: F373
U5809, U5810: F74
U5811: F02
U5812: F00

Connections:
CLK.2XE.B0: U5809.3 (CLK)
CLR_XFER_PERR~: U5810.1 (CL_)
DATA_CLOCK: U5810.3 (CLK), U5812.3 (Q)
DATA_LATCH: U5805.11 (LE), U5806.11 (LE), U5807.11 (LE), U5808.11 (LE), U5811.3 (Q)
DRIVE_RAM_DATA~: U5805.1 (OE), U5806.1 (OE), U5807.1 (OE), U5808.1 (OE)
H1.PHD: U5811.1 (D0)
H2.PHD: U5812.2 (D1)
IOC_XFER.PERR~: U5810.4 (PR_), U5810.6 (Q_)
ITYP.0: U5801.2 (I0), U5805.2 (Q0)
ITYP.1: U5801.4 (I1), U5805.5 (Q1)
ITYP.2: U5801.6 (I2), U5805.6 (Q2)
ITYP.3: U5801.8 (I3), U5805.9 (Q3)
ITYP.4: U5801.11 (I4), U5805.12 (Q4)
ITYP.5: U5801.13 (I5), U5805.15 (Q5)
ITYP.6: U5801.15 (I6), U5805.16 (Q6)
ITYP.7: U5801.17 (I7), U5805.19 (Q7)
ITYP.8: U5802.2 (I0), U5806.2 (Q0)
ITYP.9: U5802.4 (I1), U5806.5 (Q1)
ITYP.10: U5802.6 (I2), U5806.6 (Q2)
ITYP.11: U5802.8 (I3), U5806.9 (Q3)
ITYP.12: U5802.11 (I4), U5806.12 (Q4)
ITYP.13: U5802.13 (I5), U5806.15 (Q5)
ITYP.14: U5802.15 (I6), U5806.16 (Q6)
ITYP.15: U5802.17 (I7), U5806.19 (Q7)
ITYP.16: U5803.2 (I0), U5807.2 (Q0)
ITYP.17: U5803.4 (I1), U5807.5 (Q1)
ITYP.18: U5803.6 (I2), U5807.6 (Q2)
ITYP.19: U5803.8 (I3), U5807.9 (Q3)
ITYP.20: U5803.11 (I4), U5807.12 (Q4)
ITYP.21: U5803.13 (I5), U5807.15 (Q5)
ITYP.22: U5803.15 (I6), U5807.16 (Q6)
ITYP.23: U5803.17 (I7), U5807.19 (Q7)
ITYP.24: U5804.2 (I0), U5808.2 (Q0)
ITYP.25: U5804.4 (I1), U5808.5 (Q1)
ITYP.26: U5804.6 (I2), U5808.6 (Q2)
ITYP.27: U5804.8 (I3), U5808.9 (Q3)
ITYP.28: U5804.11 (I4), U5808.12 (Q4)
ITYP.29: U5804.13 (I5), U5808.15 (Q5)
ITYP.30: U5804.15 (I6), U5808.16 (Q6)
ITYP.31: U5804.17 (I7), U5808.19 (Q7)
unnamed: U5809.5 (Q), U5811.2 (D1)
unnamed: U5809.6 (Q_), U5812.1 (D0)
PU: U5809.1 (CL_), U5809.4 (PR_)
RAM.CPU_GRANT~: U5801.1 (OE0), U5801.19 (OE1), U5802.1 (OE0), U5802.19 (OE1), U5803.1 (OE0), U5803.19 (OE1), U5804.1 (OE0), U5804.19 (OE1)
RAM.DI0: U5801.18 (Y0)
RAM.DI1: U5801.16 (Y1)
RAM.DI2: U5801.14 (Y2)
RAM.DI3: U5801.12 (Y3)
RAM.DI4: U5801.9 (Y4)
RAM.DI5: U5801.7 (Y5)
RAM.DI6: U5801.5 (Y6)
RAM.DI7: U5801.3 (Y7)
RAM.DI8: U5802.18 (Y0)
RAM.DI9: U5802.16 (Y1)
RAM.DI10: U5802.14 (Y2)
RAM.DI11: U5802.12 (Y3)
RAM.DI12: U5802.9 (Y4)
RAM.DI13: U5802.7 (Y5)
RAM.DI14: U5802.5 (Y6)
RAM.DI15: U5802.3 (Y7)
RAM.DI16: U5803.18 (Y0)
RAM.DI17: U5803.16 (Y1)
RAM.DI18: U5803.14 (Y2)
RAM.DI19: U5803.12 (Y3)
RAM.DI20: U5803.9 (Y4)
RAM.DI21: U5803.7 (Y5)
RAM.DI22: U5803.5 (Y6)
RAM.DI23: U5803.3 (Y7)
RAM.DI24: U5804.18 (Y0)
RAM.DI25: U5804.16 (Y1)
RAM.DI26: U5804.14 (Y2)
RAM.DI27: U5804.12 (Y3)
RAM.DI28: U5804.9 (Y4)
RAM.DI29: U5804.7 (Y5)
RAM.DI30: U5804.5 (Y6)
RAM.DI31: U5804.3 (Y7)
RAM.DO0: U5805.3 (D0)
RAM.DO1: U5805.4 (D1)
RAM.DO2: U5805.7 (D2)
RAM.DO3: U5805.8 (D3)
RAM.DO4: U5805.13 (D4)
RAM.DO5: U5805.14 (D5)
RAM.DO6: U5805.17 (D6)
RAM.DO7: U5805.18 (D7)
RAM.DO8: U5806.3 (D0)
RAM.DO9: U5806.4 (D1)
RAM.DO10: U5806.7 (D2)
RAM.DO11: U5806.8 (D3)
RAM.DO12: U5806.13 (D4)
RAM.DO13: U5806.14 (D5)
RAM.DO14: U5806.17 (D6)
RAM.DO15: U5806.18 (D7)
RAM.DO16: U5807.3 (D0)
RAM.DO17: U5807.4 (D1)
RAM.DO18: U5807.7 (D2)
RAM.DO19: U5807.8 (D3)
RAM.DO20: U5807.13 (D4)
RAM.DO21: U5807.14 (D5)
RAM.DO22: U5807.17 (D6)
RAM.DO23: U5807.18 (D7)
RAM.DO24: U5808.3 (D0)
RAM.DO25: U5808.4 (D1)
RAM.DO26: U5808.7 (D2)
RAM.DO27: U5808.8 (D3)
RAM.DO28: U5808.13 (D4)
RAM.DO29: U5808.14 (D5)
RAM.DO30: U5808.17 (D6)
RAM.DO31: U5808.18 (D7)
RAM.PERR: U5810.2 (D)
RAM_READ.S~: U5809.2 (D)
