Datamuseum-DK/R1000.HwDoc/Schematics/IOC/pg_59.kicad_sch

## KiCad design Schematics/IOC/pg_59.kicad_sch (2023-01-10)

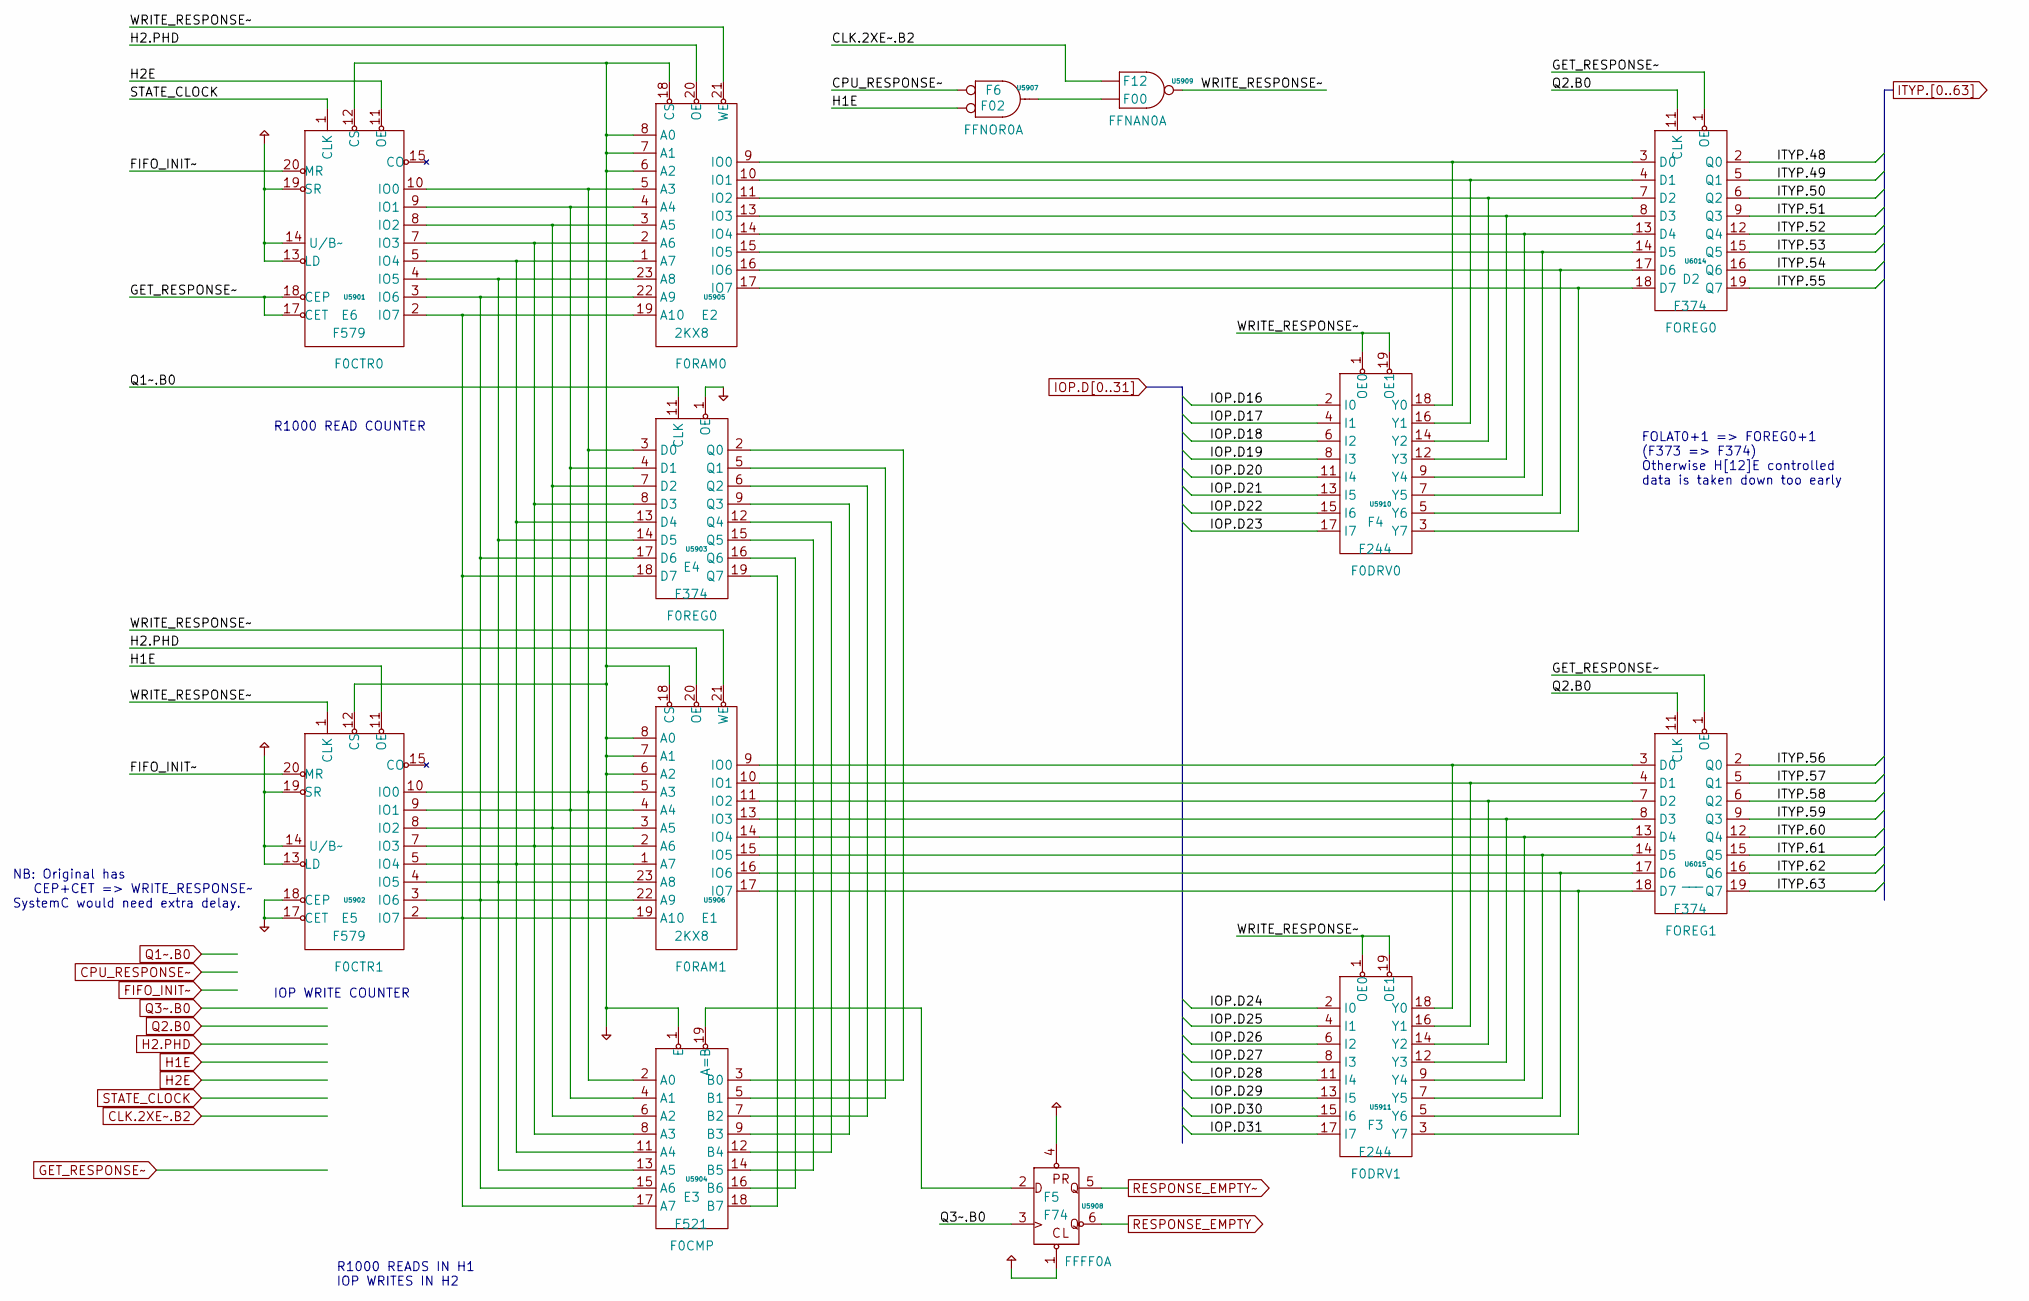
[picture p403: schematic pg_59.kicad_sch]

Parts:
U5901, U5902: F579
U5903, U6014, U6015: F374
U5904: F521
U5905, U5906: 2KX8
U5907: F02
U5908: F74
U5909: F00
U5910, U5911: F244

Connections:
CLK.2XE~.B2: U5909.1 (D0)
CPU_RESPONSE~: U5907.1 (D0)
FIFO_INIT~: U5901.20 (MR), U5902.20 (MR)
GET_RESPONSE~: U5901.17 (CET), U5901.18 (CEP), U6014.1 (OE), U6015.1 (OE)
H1E: U5902.11 (OE), U5907.2 (D1)
H2.PHD: U5905.20 (OE), U5906.20 (OE)
H2E: U5901.11 (OE)
IOP.D16: U5910.2 (I0)
IOP.D17: U5910.4 (I1)
IOP.D18: U5910.6 (I2)
IOP.D19: U5910.8 (I3)
IOP.D20: U5910.11 (I4)
IOP.D21: U5910.13 (I5)
IOP.D22: U5910.15 (I6)
IOP.D23: U5910.17 (I7)
IOP.D24: U5911.2 (I0)
IOP.D25: U5911.4 (I1)
IOP.D26: U5911.6 (I2)
IOP.D27: U5911.8 (I3)
IOP.D28: U5911.11 (I4)
IOP.D29: U5911.13 (I5)
IOP.D30: U5911.15 (I6)
IOP.D31: U5911.17 (I7)
ITYP.48: U6014.2 (Q0)
ITYP.49: U6014.5 (Q1)
ITYP.50: U6014.6 (Q2)
ITYP.51: U6014.9 (Q3)
ITYP.52: U6014.12 (Q4)
ITYP.53: U6014.15 (Q5)
ITYP.54: U6014.16 (Q6)
ITYP.55: U6014.19 (Q7)
ITYP.56: U6015.2 (Q0)
ITYP.57: U6015.5 (Q1)
ITYP.58: U6015.6 (Q2)
ITYP.59: U6015.9 (Q3)
ITYP.60: U6015.12 (Q4)
ITYP.61: U6015.15 (Q5)
ITYP.62: U6015.16 (Q6)
ITYP.63: U6015.19 (Q7)
unnamed: U5901.2 (IO7), U5902.2 (IO7), U5903.18 (D7), U5904.17 (A7), U5905.19 (A10), U5906.19 (A10)
unnamed: U5901.3 (IO6), U5902.3 (IO6), U5903.17 (D6), U5904.15 (A6), U5905.22 (A9), U5906.22 (A9)
unnamed: U5901.4 (IO5), U5902.4 (IO5), U5903.14 (D5), U5904.13 (A5), U5905.23 (A8), U5906.23 (A8)
unnamed: U5901.5 (IO4), U5902.5 (IO4), U5903.13 (D4), U5904.11 (A4), U5905.1 (A7), U5906.1 (A7)
unnamed: U5901.7 (IO3), U5902.7 (IO3), U5903.8 (D3), U5904.8 (A3), U5905.2 (A6), U5906.2 (A6)
unnamed: U5901.8 (IO2), U5902.8 (IO2), U5903.7 (D2), U5904.6 (A2), U5905.3 (A5), U5906.3 (A5)
unnamed: U5901.9 (IO1), U5902.9 (IO1), U5903.4 (D1), U5904.4 (A1), U5905.4 (A4), U5906.4 (A4)
unnamed: U5901.10 (IO0), U5902.10 (IO0), U5903.3 (D0), U5904.2 (A0), U5905.5 (A3), U5906.5 (A3)
unnamed: U5903.2 (Q0), U5904.3 (B0)
unnamed: U5903.5 (Q1), U5904.5 (B1)
unnamed: U5903.6 (Q2), U5904.7 (B2)
unnamed: U5903.9 (Q3), U5904.9 (B3)
unnamed: U5903.12 (Q4), U5904.12 (B4)
unnamed: U5903.15 (Q5), U5904.14 (B5)
unnamed: U5903.16 (Q6), U5904.16 (B6)
unnamed: U5903.19 (Q7), U5904.18 (B7)
unnamed: U5904.19 (A=B), U5908.2 (D)
unnamed: U5905.9 (IO0), U5910.18 (Y0), U6014.3 (D0)
unnamed: U5905.10 (IO1), U5910.16 (Y1), U6014.4 (D1)
unnamed: U5905.11 (IO2), U5910.14 (Y2), U6014.7 (D2)
unnamed: U5905.13 (IO3), U5910.12 (Y3), U6014.8 (D3)
unnamed: U5905.14 (IO4), U5910.9 (Y4), U6014.13 (D4)
unnamed: U5905.15 (IO5), U5910.7 (Y5), U6014.14 (D5)
unnamed: U5905.16 (IO6), U5910.5 (Y6), U6014.17 (D6)
unnamed: U5905.17 (IO7), U5910.3 (Y7), U6014.18 (D7)
unnamed: U5906.9 (IO0), U5911.18 (Y0), U6015.3 (D0)
unnamed: U5906.10 (IO1), U5911.16 (Y1), U6015.4 (D1)
unnamed: U5906.11 (IO2), U5911.14 (Y2), U6015.7 (D2)
unnamed: U5906.13 (IO3), U5911.12 (Y3), U6015.8 (D3)
unnamed: U5906.14 (IO4), U5911.9 (Y4), U6015.13 (D4)
unnamed: U5906.15 (IO5), U5911.7 (Y5), U6015.14 (D5)
unnamed: U5906.16 (IO6), U5911.5 (Y6), U6015.17 (D6)
unnamed: U5906.17 (IO7), U5911.3 (Y7), U6015.18 (D7)
unnamed: U5907.3 (Q), U5909.2 (D1)
PD: U5901.12 (CS), U5902.12 (CS), U5902.17 (CET), U5902.18 (CEP), U5903.1 (OE), U5904.1 (E), U5905.6 (A2), U5905.7 (A1), U5905.8 (A0), U5905.18 (CS), U5906.6 (A2), U5906.7 (A1), U5906.8 (A0), U5906.18 (CS)
PU: U5901.13 (LD), U5901.14 (U/B~), U5901.19 (SR), U5902.13 (LD), U5902.14 (U/B~), U5902.19 (SR), U5908.1 (CL_), U5908.4 (PR_)
Q1~.B0: U5903.11 (CLK)
Q2.B0: U6014.11 (CLK), U6015.11 (CLK)
Q3~.B0: U5908.3 (CLK)
RESPONSE_EMPTY: U5908.6 (Q_)
RESPONSE_EMPTY~: U5908.5 (Q)
STATE_CLOCK: U5901.1 (CLK)
WRITE_RESPONSE~: U5902.1 (CLK), U5905.21 (WE), U5906.21 (WE), U5909.3 (Q), U5910.1 (OE0), U5910.19 (OE1), U5911.1 (OE0), U5911.19 (OE1)

Notes on the sheet:
FOLAT0+1 => FOREG0+1 (F373 => F374) Otherwise H[12]E controlled data is taken down too early
IOP WRITE COUNTER
R1000 READ COUNTER
NB: Original has CEP+CET => WRITE_RESPONSE~ SystemC would need extra delay.
R1000 READS IN H1 IOP WRITES IN H2
