Datamuseum-DK/R1000.HwDoc/Schematics/IOC/pg_60.kicad_sch

## KiCad design Schematics/IOC/pg_60.kicad_sch (2023-01-10)

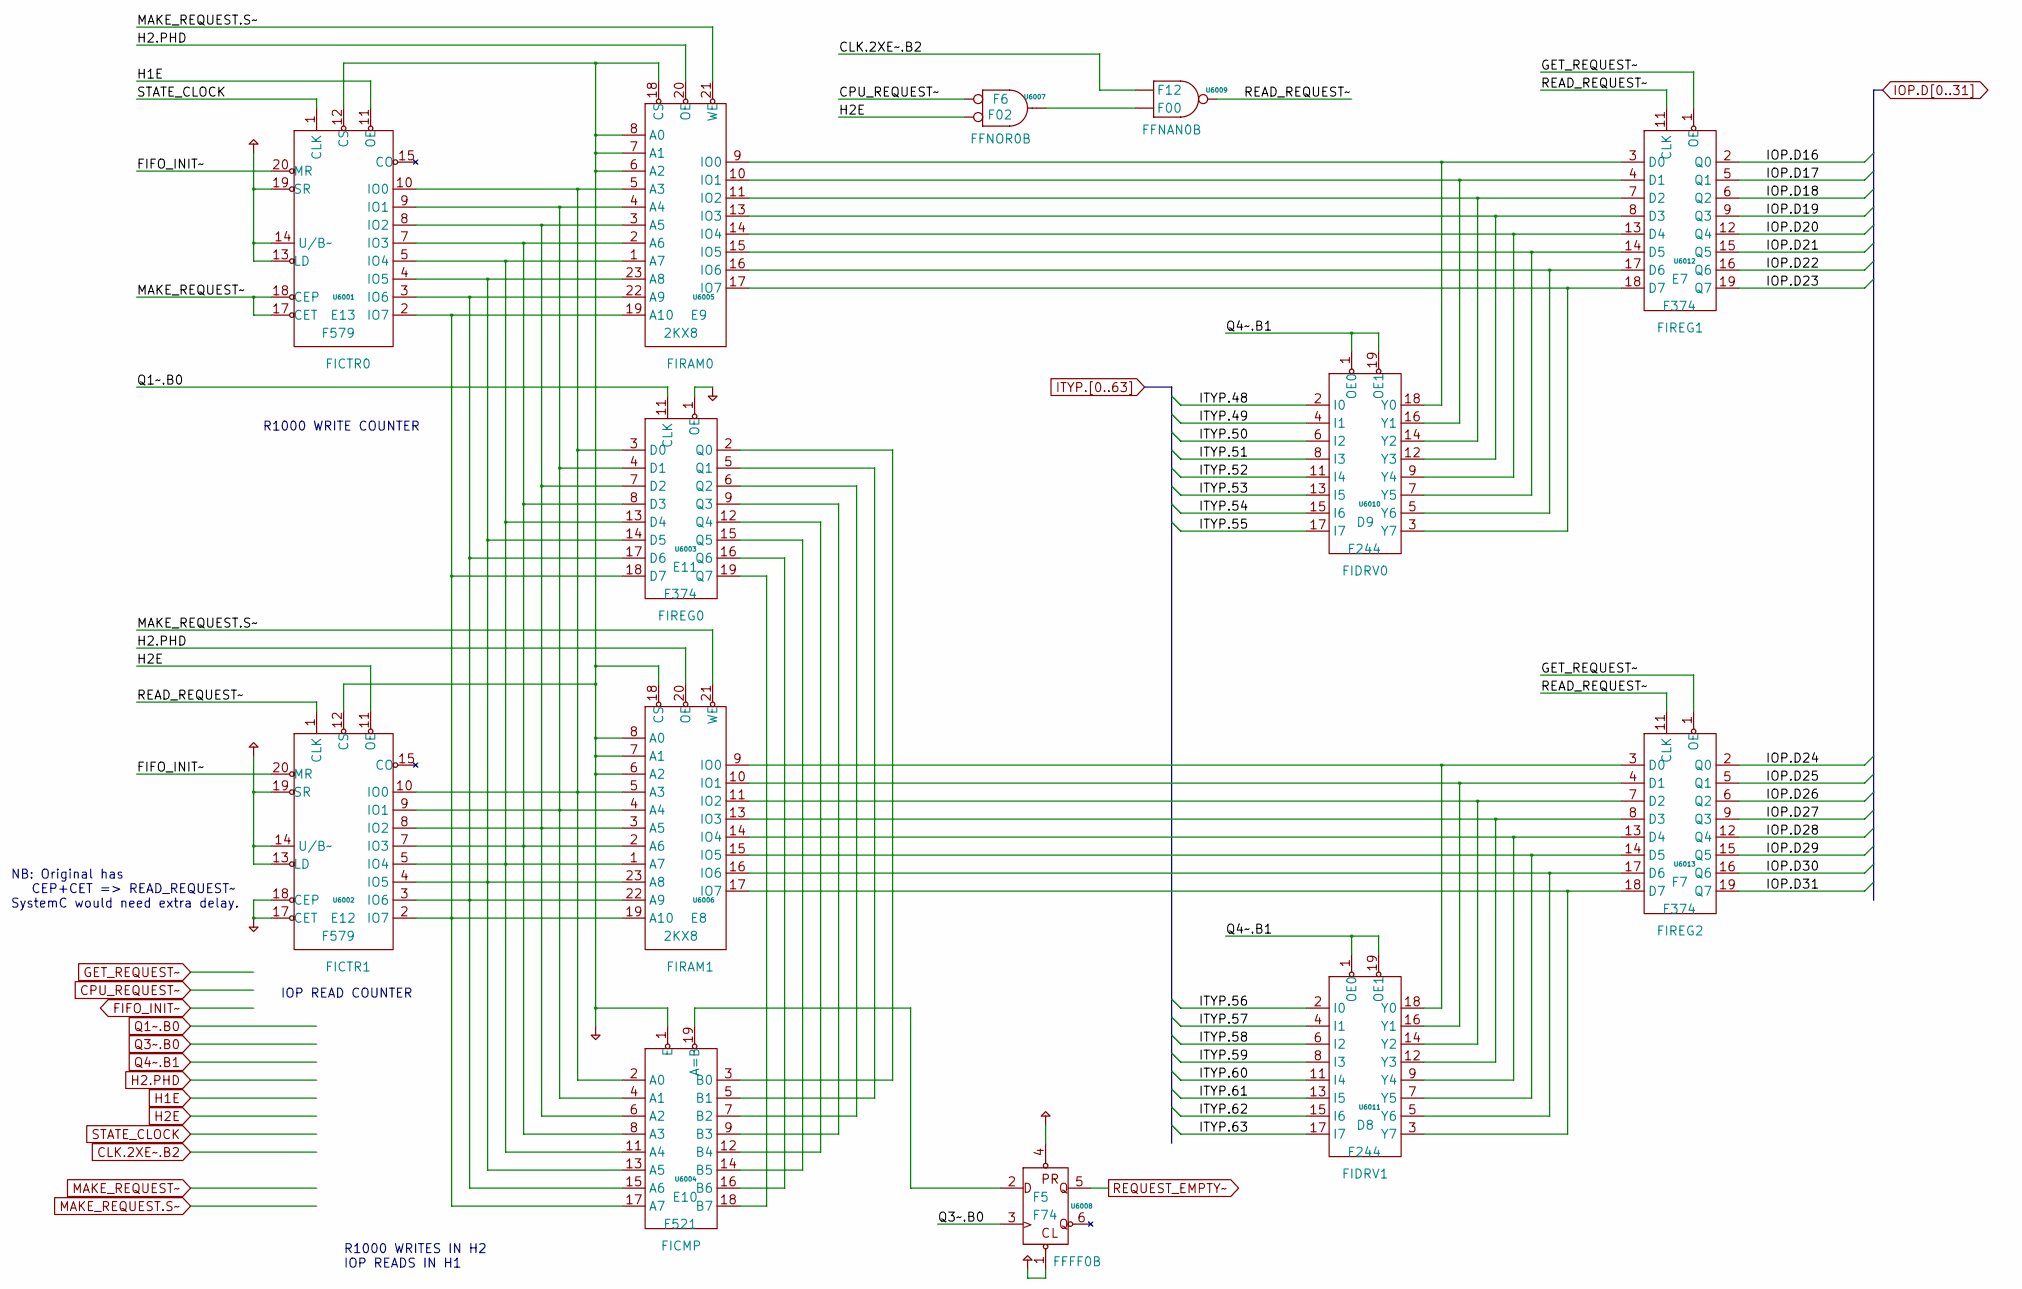
[picture p404: schematic pg_60.kicad_sch]

Parts:
U6001, U6002: F579
U6003, U6012, U6013: F374
U6004: F521
U6005, U6006: 2KX8
U6007: F02
U6008: F74
U6009: F00
U6010, U6011: F244

Connections:
CLK.2XE~.B2: U6009.1 (D0)
CPU_REQUEST~: U6007.1 (D0)
FIFO_INIT~: U6001.20 (MR), U6002.20 (MR)
GET_REQUEST~: U6012.1 (OE), U6013.1 (OE)
H1E: U6001.11 (OE)
H2.PHD: U6005.20 (OE), U6006.20 (OE)
H2E: U6002.11 (OE), U6007.2 (D1)
IOP.D16: U6012.2 (Q0)
IOP.D17: U6012.5 (Q1)
IOP.D18: U6012.6 (Q2)
IOP.D19: U6012.9 (Q3)
IOP.D20: U6012.12 (Q4)
IOP.D21: U6012.15 (Q5)
IOP.D22: U6012.16 (Q6)
IOP.D23: U6012.19 (Q7)
IOP.D24: U6013.2 (Q0)
IOP.D25: U6013.5 (Q1)
IOP.D26: U6013.6 (Q2)
IOP.D27: U6013.9 (Q3)
IOP.D28: U6013.12 (Q4)
IOP.D29: U6013.15 (Q5)
IOP.D30: U6013.16 (Q6)
IOP.D31: U6013.19 (Q7)
ITYP.48: U6010.2 (I0)
ITYP.49: U6010.4 (I1)
ITYP.50: U6010.6 (I2)
ITYP.51: U6010.8 (I3)
ITYP.52: U6010.11 (I4)
ITYP.53: U6010.13 (I5)
ITYP.54: U6010.15 (I6)
ITYP.55: U6010.17 (I7)
ITYP.56: U6011.2 (I0)
ITYP.57: U6011.4 (I1)
ITYP.58: U6011.6 (I2)
ITYP.59: U6011.8 (I3)
ITYP.60: U6011.11 (I4)
ITYP.61: U6011.13 (I5)
ITYP.62: U6011.15 (I6)
ITYP.63: U6011.17 (I7)
MAKE_REQUEST.S~: U6005.21 (WE), U6006.21 (WE)
MAKE_REQUEST~: U6001.17 (CET), U6001.18 (CEP)
unnamed: U6001.2 (IO7), U6002.2 (IO7), U6003.18 (D7), U6004.17 (A7), U6005.19 (A10), U6006.19 (A10)
unnamed: U6001.3 (IO6), U6002.3 (IO6), U6003.17 (D6), U6004.15 (A6), U6005.22 (A9), U6006.22 (A9)
unnamed: U6001.4 (IO5), U6002.4 (IO5), U6003.14 (D5), U6004.13 (A5), U6005.23 (A8), U6006.23 (A8)
unnamed: U6001.5 (IO4), U6002.5 (IO4), U6003.13 (D4), U6004.11 (A4), U6005.1 (A7), U6006.1 (A7)
unnamed: U6001.7 (IO3), U6002.7 (IO3), U6003.8 (D3), U6004.8 (A3), U6005.2 (A6), U6006.2 (A6)
unnamed: U6001.8 (IO2), U6002.8 (IO2), U6003.7 (D2), U6004.6 (A2), U6005.3 (A5), U6006.3 (A5)
unnamed: U6001.9 (IO1), U6002.9 (IO1), U6003.4 (D1), U6004.4 (A1), U6005.4 (A4), U6006.4 (A4)
unnamed: U6001.10 (IO0), U6002.10 (IO0), U6003.3 (D0), U6004.2 (A0), U6005.5 (A3), U6006.5 (A3)
unnamed: U6003.2 (Q0), U6004.3 (B0)
unnamed: U6003.5 (Q1), U6004.5 (B1)
unnamed: U6003.6 (Q2), U6004.7 (B2)
unnamed: U6003.9 (Q3), U6004.9 (B3)
unnamed: U6003.12 (Q4), U6004.12 (B4)
unnamed: U6003.15 (Q5), U6004.14 (B5)
unnamed: U6003.16 (Q6), U6004.16 (B6)
unnamed: U6003.19 (Q7), U6004.18 (B7)
unnamed: U6004.19 (A=B), U6008.2 (D)
unnamed: U6005.9 (IO0), U6010.18 (Y0), U6012.3 (D0)
unnamed: U6005.10 (IO1), U6010.16 (Y1), U6012.4 (D1)
unnamed: U6005.11 (IO2), U6010.14 (Y2), U6012.7 (D2)
unnamed: U6005.13 (IO3), U6010.12 (Y3), U6012.8 (D3)
unnamed: U6005.14 (IO4), U6010.9 (Y4), U6012.13 (D4)
unnamed: U6005.15 (IO5), U6010.7 (Y5), U6012.14 (D5)
unnamed: U6005.16 (IO6), U6010.5 (Y6), U6012.17 (D6)
unnamed: U6005.17 (IO7), U6010.3 (Y7), U6012.18 (D7)
unnamed: U6006.9 (IO0), U6011.18 (Y0), U6013.3 (D0)
unnamed: U6006.10 (IO1), U6011.16 (Y1), U6013.4 (D1)
unnamed: U6006.11 (IO2), U6011.14 (Y2), U6013.7 (D2)
unnamed: U6006.13 (IO3), U6011.12 (Y3), U6013.8 (D3)
unnamed: U6006.14 (IO4), U6011.9 (Y4), U6013.13 (D4)
unnamed: U6006.15 (IO5), U6011.7 (Y5), U6013.14 (D5)
unnamed: U6006.16 (IO6), U6011.5 (Y6), U6013.17 (D6)
unnamed: U6006.17 (IO7), U6011.3 (Y7), U6013.18 (D7)
unnamed: U6007.3 (Q), U6009.2 (D1)
PD: U6001.12 (CS), U6002.12 (CS), U6002.17 (CET), U6002.18 (CEP), U6003.1 (OE), U6004.1 (E), U6005.6 (A2), U6005.7 (A1), U6005.8 (A0), U6005.18 (CS), U6006.6 (A2), U6006.7 (A1), U6006.8 (A0), U6006.18 (CS)
PU: U6001.13 (LD), U6001.14 (U/B~), U6001.19 (SR), U6002.13 (LD), U6002.14 (U/B~), U6002.19 (SR), U6008.1 (CL_), U6008.4 (PR_)
Q1~.B0: U6003.11 (CLK)
Q3~.B0: U6008.3 (CLK)
Q4~.B1: U6010.1 (OE0), U6010.19 (OE1), U6011.1 (OE0), U6011.19 (OE1)
READ_REQUEST~: U6002.1 (CLK), U6009.3 (Q), U6012.11 (CLK), U6013.11 (CLK)
REQUEST_EMPTY~: U6008.5 (Q)
STATE_CLOCK: U6001.1 (CLK)

Notes on the sheet:
NB: Original has CEP+CET => READ_REQUEST~ SystemC would need extra delay.
R1000 WRITE COUNTER
R1000 WRITES IN H2 IOP READS IN H1
IOP READ COUNTER
