Datamuseum-DK/R1000.HwDoc/Schematics/IOC/pg_61.kicad_sch

## KiCad design Schematics/IOC/pg_61.kicad_sch (2023-01-10)

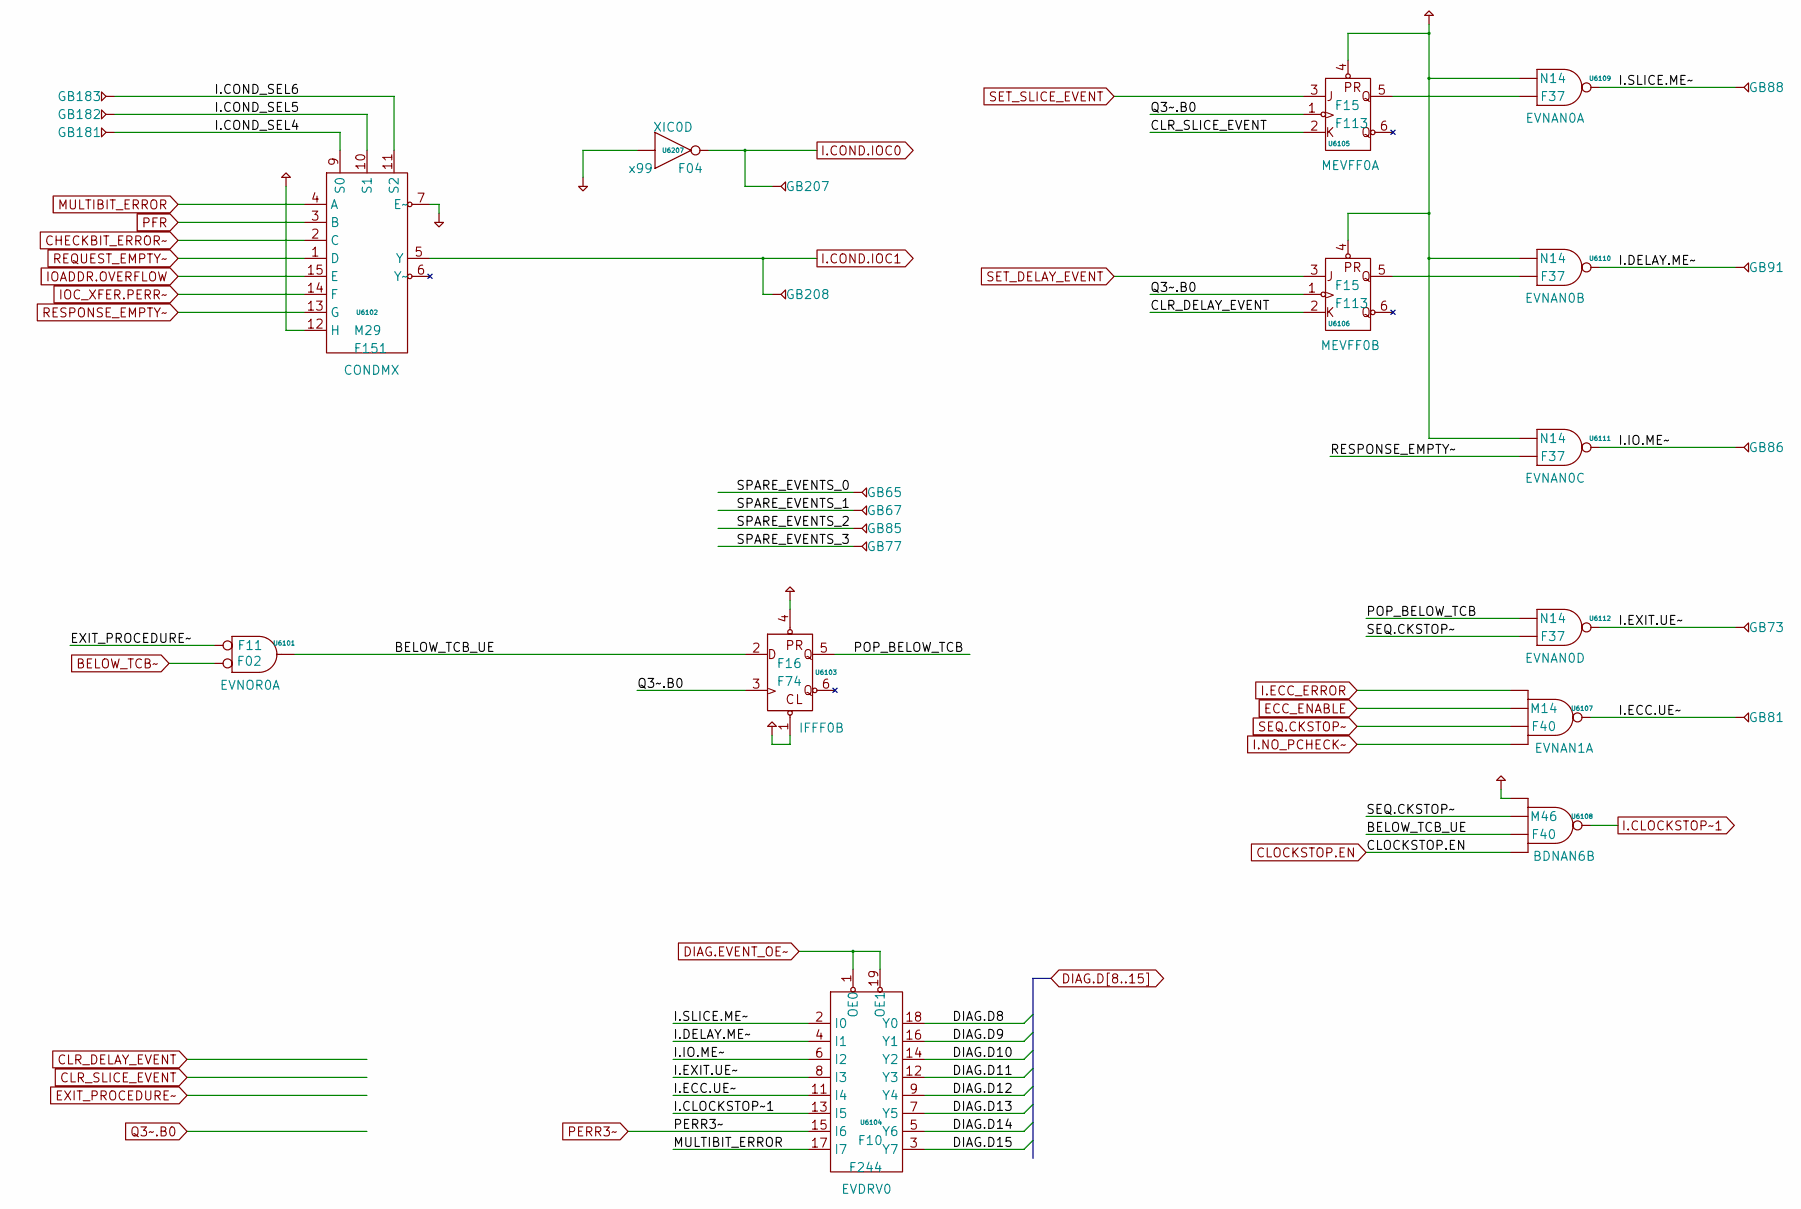
[picture p405: schematic pg_61.kicad_sch]

Parts:
GB65, GB67, GB73, GB77, GB81, GB85, GB86, GB88, GB91, GB181, GB182, GB183, GB207, GB208: GB
U6101: F02
U6102: F151
U6103: F74
U6104: F244
U6105, U6106: F113
U6107, U6108: F40
U6109, U6110, U6111, U6112: F37
U6207: F04

Connections:
BELOW_TCB_UE: U6101.3 (Q), U6103.2 (D), U6108.4 (D4)
BELOW_TCB~: U6101.2 (D1)
CHECKBIT_ERROR~: U6102.2 (C)
CLOCKSTOP.EN: U6108.5 (D5)
CLR_DELAY_EVENT: U6106.2 (K)
CLR_SLICE_EVENT: U6105.2 (K)
DIAG.D8: U6104.18 (Y0)
DIAG.D9: U6104.16 (Y1)
DIAG.D10: U6104.14 (Y2)
DIAG.D11: U6104.12 (Y3)
DIAG.D12: U6104.9 (Y4)
DIAG.D13: U6104.7 (Y5)
DIAG.D14: U6104.5 (Y6)
DIAG.D15: U6104.3 (Y7)
DIAG.EVENT_OE~: U6104.1 (OE0), U6104.19 (OE1)
ECC_ENABLE: U6107.2 (D3)
EXIT_PROCEDURE~: U6101.1 (D0)
I.CLOCKSTOP~1: U6104.13 (I5), U6108.6 (Q)
I.COND.IOC0: GB207.1, U6207.2 (Q)
I.COND.IOC1: GB208.1, U6102.5 (Y)
I.COND_SEL4: GB181.1, U6102.9 (S0)
I.COND_SEL5: GB182.1, U6102.10 (S1)
I.COND_SEL6: GB183.1, U6102.11 (S2)
I.DELAY.ME~: GB91.1, U6104.4 (I1), U6110.3 (Q)
I.ECC.UE~: GB81.1, U6104.11 (I4), U6107.6 (Q)
I.ECC_ERROR: U6107.1 (D0)
I.EXIT.UE~: GB73.1, U6104.8 (I3), U6112.3 (Q)
I.IO.ME~: GB86.1, U6104.6 (I2), U6111.3 (Q)
I.NO_PCHECK~: U6107.5 (D5)
I.SLICE.ME~: GB88.1, U6104.2 (I0), U6109.3 (Q)
IOADDR.OVERFLOW: U6102.15 (E)
IOC_XFER.PERR~: U6102.14 (F)
MULTIBIT_ERROR: U6102.4 (A), U6104.17 (I7)
unnamed: U6105.5 (Q), U6109.2 (D1)
unnamed: U6106.5 (Q), U6110.2 (D1)
PD: U6102.7 (E~), U6207.1 (D0)
PERR3~: U6104.15 (I6)
PFR: U6102.3 (B)
POP_BELOW_TCB: U6103.5 (Q), U6112.1 (D0)
PU: U6102.12 (H), U6103.1 (CL_), U6103.4 (PR_), U6105.4 (PR_), U6106.4 (PR_), U6108.1 (D0), U6109.1 (D0), U6110.1 (D0), U6111.1 (D0)
Q3~.B0: U6103.3 (CLK), U6105.1 (CLK_), U6106.1 (CLK_)
REQUEST_EMPTY~: U6102.1 (D)
RESPONSE_EMPTY~: U6102.13 (G), U6111.2 (D1)
SEQ.CKSTOP~: U6107.4 (D4), U6108.2 (D3), U6112.2 (D1)
SET_DELAY_EVENT: U6106.3 (J)
SET_SLICE_EVENT: U6105.3 (J)
SPARE_EVENTS_0: GB65.1
SPARE_EVENTS_1: GB67.1
SPARE_EVENTS_2: GB85.1
SPARE_EVENTS_3: GB77.1
