Datamuseum-DK/R1000.HwDoc/Schematics/IOC/pg_62.kicad_sch

## KiCad design Schematics/IOC/pg_62.kicad_sch (2023-01-10)

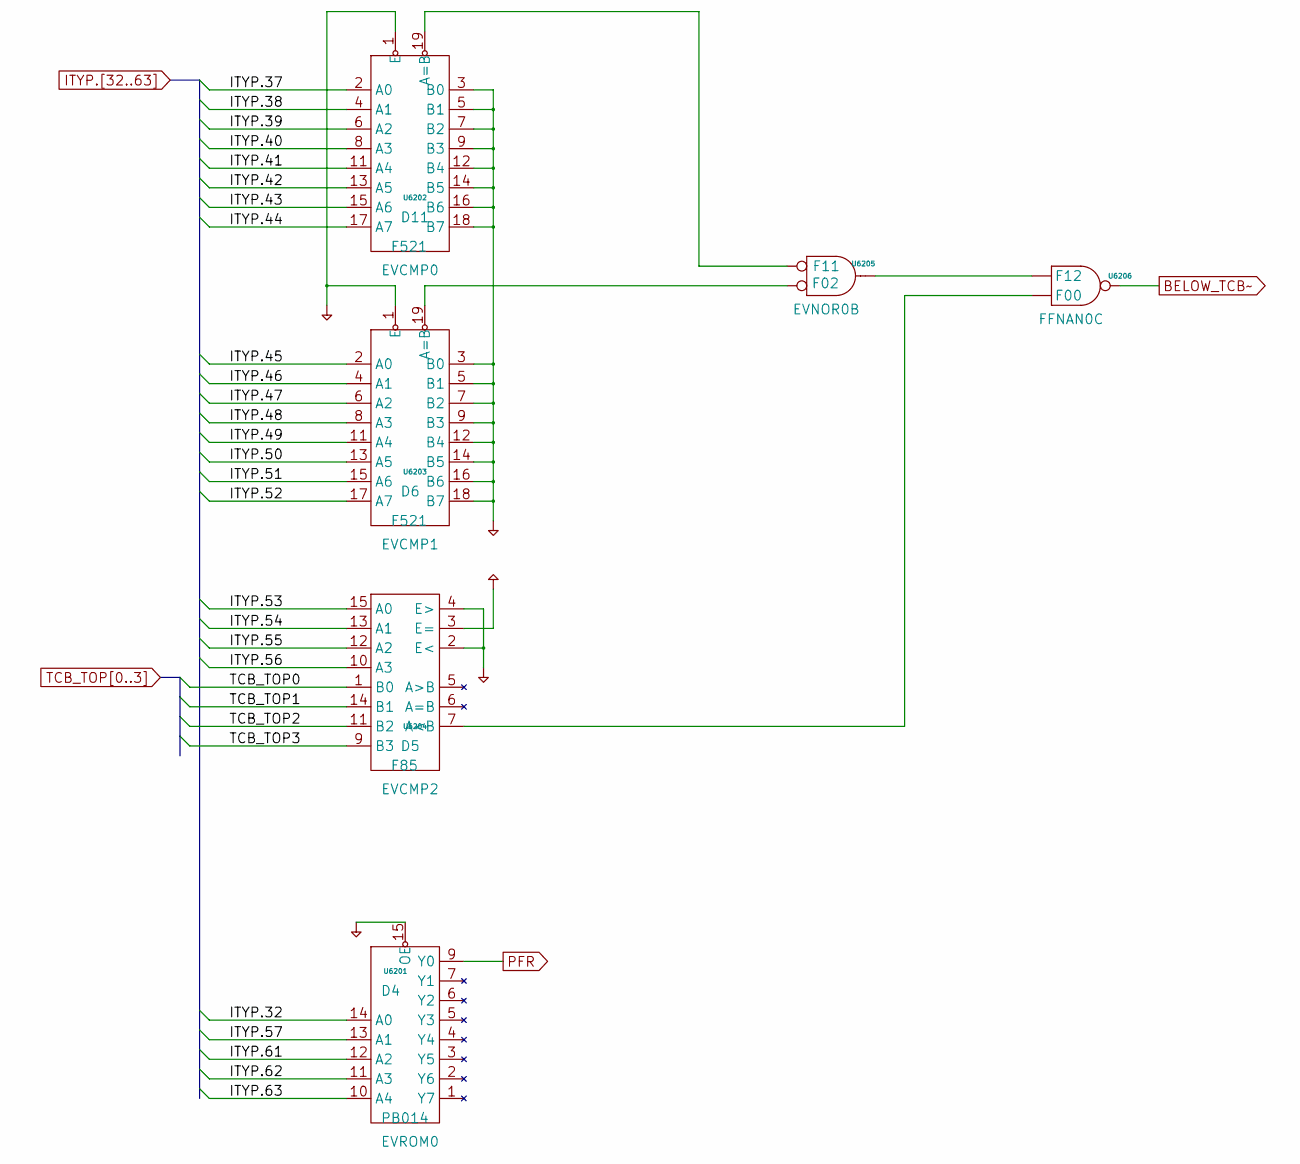
[picture p406: schematic pg_62.kicad_sch]

Parts:
U6201: PB014
U6202, U6203: F521
U6204: F85
U6205: F02
U6206: F00

Connections:
BELOW_TCB~: U6206.3 (Q)
ITYP.32: U6201.14 (A0)
ITYP.37: U6202.2 (A0)
ITYP.38: U6202.4 (A1)
ITYP.39: U6202.6 (A2)
ITYP.40: U6202.8 (A3)
ITYP.41: U6202.11 (A4)
ITYP.42: U6202.13 (A5)
ITYP.43: U6202.15 (A6)
ITYP.44: U6202.17 (A7)
ITYP.45: U6203.2 (A0)
ITYP.46: U6203.4 (A1)
ITYP.47: U6203.6 (A2)
ITYP.48: U6203.8 (A3)
ITYP.49: U6203.11 (A4)
ITYP.50: U6203.13 (A5)
ITYP.51: U6203.15 (A6)
ITYP.52: U6203.17 (A7)
ITYP.53: U6204.15 (A0)
ITYP.54: U6204.13 (A1)
ITYP.55: U6204.12 (A2)
ITYP.56: U6204.10 (A3)
ITYP.57: U6201.13 (A1)
ITYP.61: U6201.12 (A2)
ITYP.62: U6201.11 (A3)
ITYP.63: U6201.10 (A4)
unnamed: U6202.19 (A=B), U6205.1 (D0)
unnamed: U6203.19 (A=B), U6205.2 (D1)
unnamed: U6204.7 (A<B), U6206.2 (D1)
unnamed: U6205.3 (Q), U6206.1 (D0)
PD: U6201.15 (OE), U6202.1 (E), U6202.3 (B0), U6202.5 (B1), U6202.7 (B2), U6202.9 (B3), U6202.12 (B4), U6202.14 (B5), U6202.16 (B6), U6202.18 (B7), U6203.1 (E), U6203.3 (B0), U6203.5 (B1), U6203.7 (B2), U6203.9 (B3), U6203.12 (B4), U6203.14 (B5), U6203.16 (B6), U6203.18 (B7), U6204.2 (E<), U6204.4 (E>)
PFR: U6201.9 (Y0)
PU: U6204.3 (E=)
TCB_TOP0: U6204.1 (B0)
TCB_TOP1: U6204.14 (B1)
TCB_TOP2: U6204.11 (B2)
TCB_TOP3: U6204.9 (B3)
