Datamuseum-DK/R1000.HwDoc/Schematics/IOC/pg_63.kicad_sch

## KiCad design Schematics/IOC/pg_63.kicad_sch (2023-01-10)

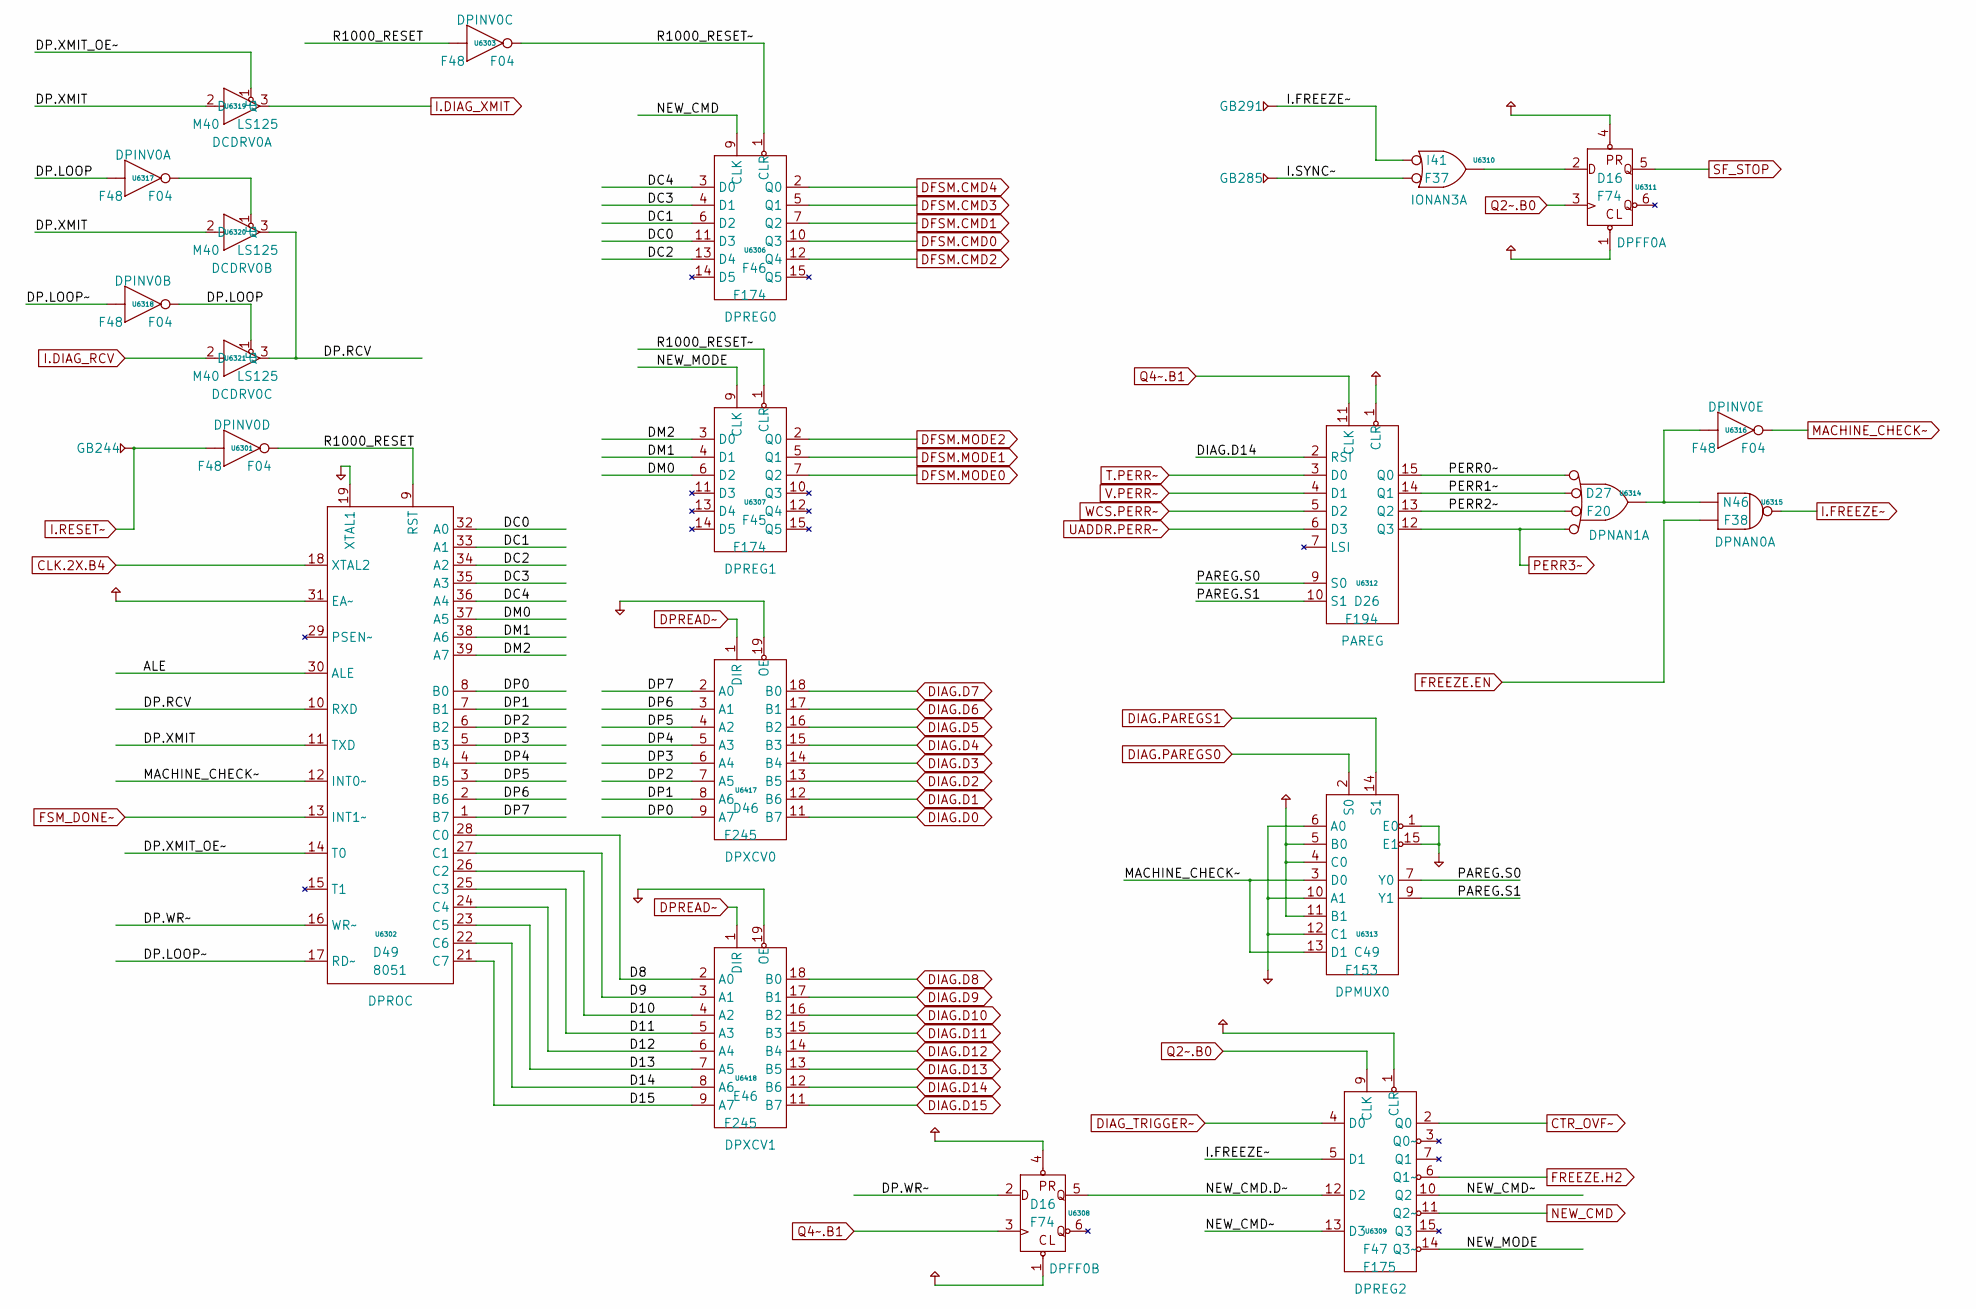
[picture p407: schematic pg_63.kicad_sch]

Parts:
GB244, GB285, GB291: GB
U6301, U6303, U6316, U6317, U6318: F04
U6302: 8051
U6306, U6307: F174
U6308, U6311: F74
U6309: F175
U6310: F37
U6312: F194
U6313: F153
U6314: F20
U6315: F38
U6319, U6320, U6321: LS125
U6417, U6418: F245

Connections:
ALE: U6302.30 (ALE)
CLK.2X.B4: U6302.18 (XTAL2)
CTR_OVF~: U6309.2 (Q0)
D8: U6302.28 (C0), U6418.2 (A0)
D9: U6302.27 (C1), U6418.3 (A1)
D10: U6302.26 (C2), U6418.4 (A2)
D11: U6302.25 (C3), U6418.5 (A3)
D12: U6302.24 (C4), U6418.6 (A4)
D13: U6302.23 (C5), U6418.7 (A5)
D14: U6302.22 (C6), U6418.8 (A6)
D15: U6302.21 (C7), U6418.9 (A7)
DC0: U6302.32 (A0), U6306.11 (D3)
DC1: U6302.33 (A1), U6306.6 (D2)
DC2: U6302.34 (A2), U6306.13 (D4)
DC3: U6302.35 (A3), U6306.4 (D1)
DC4: U6302.36 (A4), U6306.3 (D0)
DFSM.CMD0: U6306.10 (Q3)
DFSM.CMD1: U6306.7 (Q2)
DFSM.CMD2: U6306.12 (Q4)
DFSM.CMD3: U6306.5 (Q1)
DFSM.CMD4: U6306.2 (Q0)
DFSM.MODE0: U6307.7 (Q2)
DFSM.MODE1: U6307.5 (Q1)
DFSM.MODE2: U6307.2 (Q0)
DIAG.D0: U6417.11 (B7)
DIAG.D1: U6417.12 (B6)
DIAG.D2: U6417.13 (B5)
DIAG.D3: U6417.14 (B4)
DIAG.D4: U6417.15 (B3)
DIAG.D5: U6417.16 (B2)
DIAG.D6: U6417.17 (B1)
DIAG.D7: U6417.18 (B0)
DIAG.D8: U6418.18 (B0)
DIAG.D9: U6418.17 (B1)
DIAG.D10: U6418.16 (B2)
DIAG.D11: U6418.15 (B3)
DIAG.D12: U6418.14 (B4)
DIAG.D13: U6418.13 (B5)
DIAG.D14: U6312.2 (RSI), U6418.12 (B6)
DIAG.D15: U6418.11 (B7)
DIAG.PAREGS0: U6313.2 (S0)
DIAG.PAREGS1: U6313.14 (S1)
DIAG_TRIGGER~: U6309.4 (D0)
DM0: U6302.37 (A5), U6307.6 (D2)
DM1: U6302.38 (A6), U6307.4 (D1)
DM2: U6302.39 (A7), U6307.3 (D0)
DP0: U6302.8 (B0), U6417.9 (A7)
DP1: U6302.7 (B1), U6417.8 (A6)
DP2: U6302.6 (B2), U6417.7 (A5)
DP3: U6302.5 (B3), U6417.6 (A4)
DP4: U6302.4 (B4), U6417.5 (A3)
DP5: U6302.3 (B5), U6417.4 (A2)
DP6: U6302.2 (B6), U6417.3 (A1)
DP7: U6302.1 (B7), U6417.2 (A0)
DP.LOOP: U6317.1 (D0), U6318.2 (Q), U6321.1 (E)
DP.LOOP~: U6302.17 (RD~), U6318.1 (D0)
DP.RCV: U6302.10 (RXD), U6320.3 (Q), U6321.3 (Q)
DP.WR~: U6302.16 (WR~), U6308.2 (D)
DP.XMIT: U6302.11 (TXD), U6319.2 (D), U6320.2 (D)
DP.XMIT_OE~: U6302.14 (T0), U6319.1 (E)
DPREAD~: U6417.1 (DIR), U6418.1 (DIR)
FREEZE.EN: U6315.2 (D1)
FREEZE.H2: U6309.6 (Q1~)
FSM_DONE~: U6302.13 (INT1~)
I.DIAG_RCV: U6321.2 (D)
I.DIAG_XMIT: U6319.3 (Q)
I.FREEZE~: GB291.1, U6309.5 (D1), U6310.1 (D0), U6315.3 (Q)
I.RESET~: GB244.1, U6301.1 (D0)
I.SYNC~: GB285.1, U6310.2 (D1)
MACHINE_CHECK~: U6302.12 (INT0~), U6313.3 (D0), U6313.13 (D1), U6316.2 (Q)
NEW_CMD: U6306.9 (CLK), U6309.11 (Q2~)
NEW_CMD.D~: U6308.5 (Q), U6309.12 (D2)
NEW_CMD~: U6309.10 (Q2), U6309.13 (D3)
NEW_MODE: U6307.9 (CLK), U6309.14 (Q3~)
unnamed: U6310.3 (Q), U6311.2 (D)
unnamed: U6314.6 (Q), U6315.1 (D0), U6316.1 (D0)
unnamed: U6317.2 (Q), U6320.1 (E)
PAREG.S0: U6312.9 (S0), U6313.7 (Y0)
PAREG.S1: U6312.10 (S1), U6313.9 (Y1)
PD: U6302.19 (XTAL1), U6313.1 (E0), U6313.6 (A0), U6313.10 (A1), U6313.12 (C1), U6313.15 (E1), U6417.19 (OE), U6418.19 (OE)
PERR0~: U6312.15 (Q0), U6314.1 (D0)
PERR1~: U6312.14 (Q1), U6314.2 (D1)
PERR2~: U6312.13 (Q2), U6314.4 (D2)
PERR3~: U6312.12 (Q3), U6314.5 (D3)
PU: U6302.31 (EA~), U6308.1 (CL_), U6308.4 (PR_), U6309.1 (CLR), U6311.1 (CL_), U6311.4 (PR_), U6312.1 (CLR), U6313.4 (C0), U6313.5 (B0), U6313.11 (B1)
Q2~.B0: U6309.9 (CLK), U6311.3 (CLK)
Q4~.B1: U6308.3 (CLK), U6312.11 (CLK)
R1000_RESET: U6301.2 (Q), U6302.9 (RST), U6303.1 (D0)
R1000_RESET~: U6303.2 (Q), U6306.1 (CLR), U6307.1 (CLR)
SF_STOP: U6311.5 (Q)
T.PERR~: U6312.3 (D0)
UADDR.PERR~: U6312.6 (D3)
V.PERR~: U6312.4 (D1)
WCS.PERR~: U6312.5 (D2)
