Datamuseum-DK/R1000.HwDoc/Schematics/IOC/pg_64.kicad_sch

## KiCad design Schematics/IOC/pg_64.kicad_sch (2023-01-10)

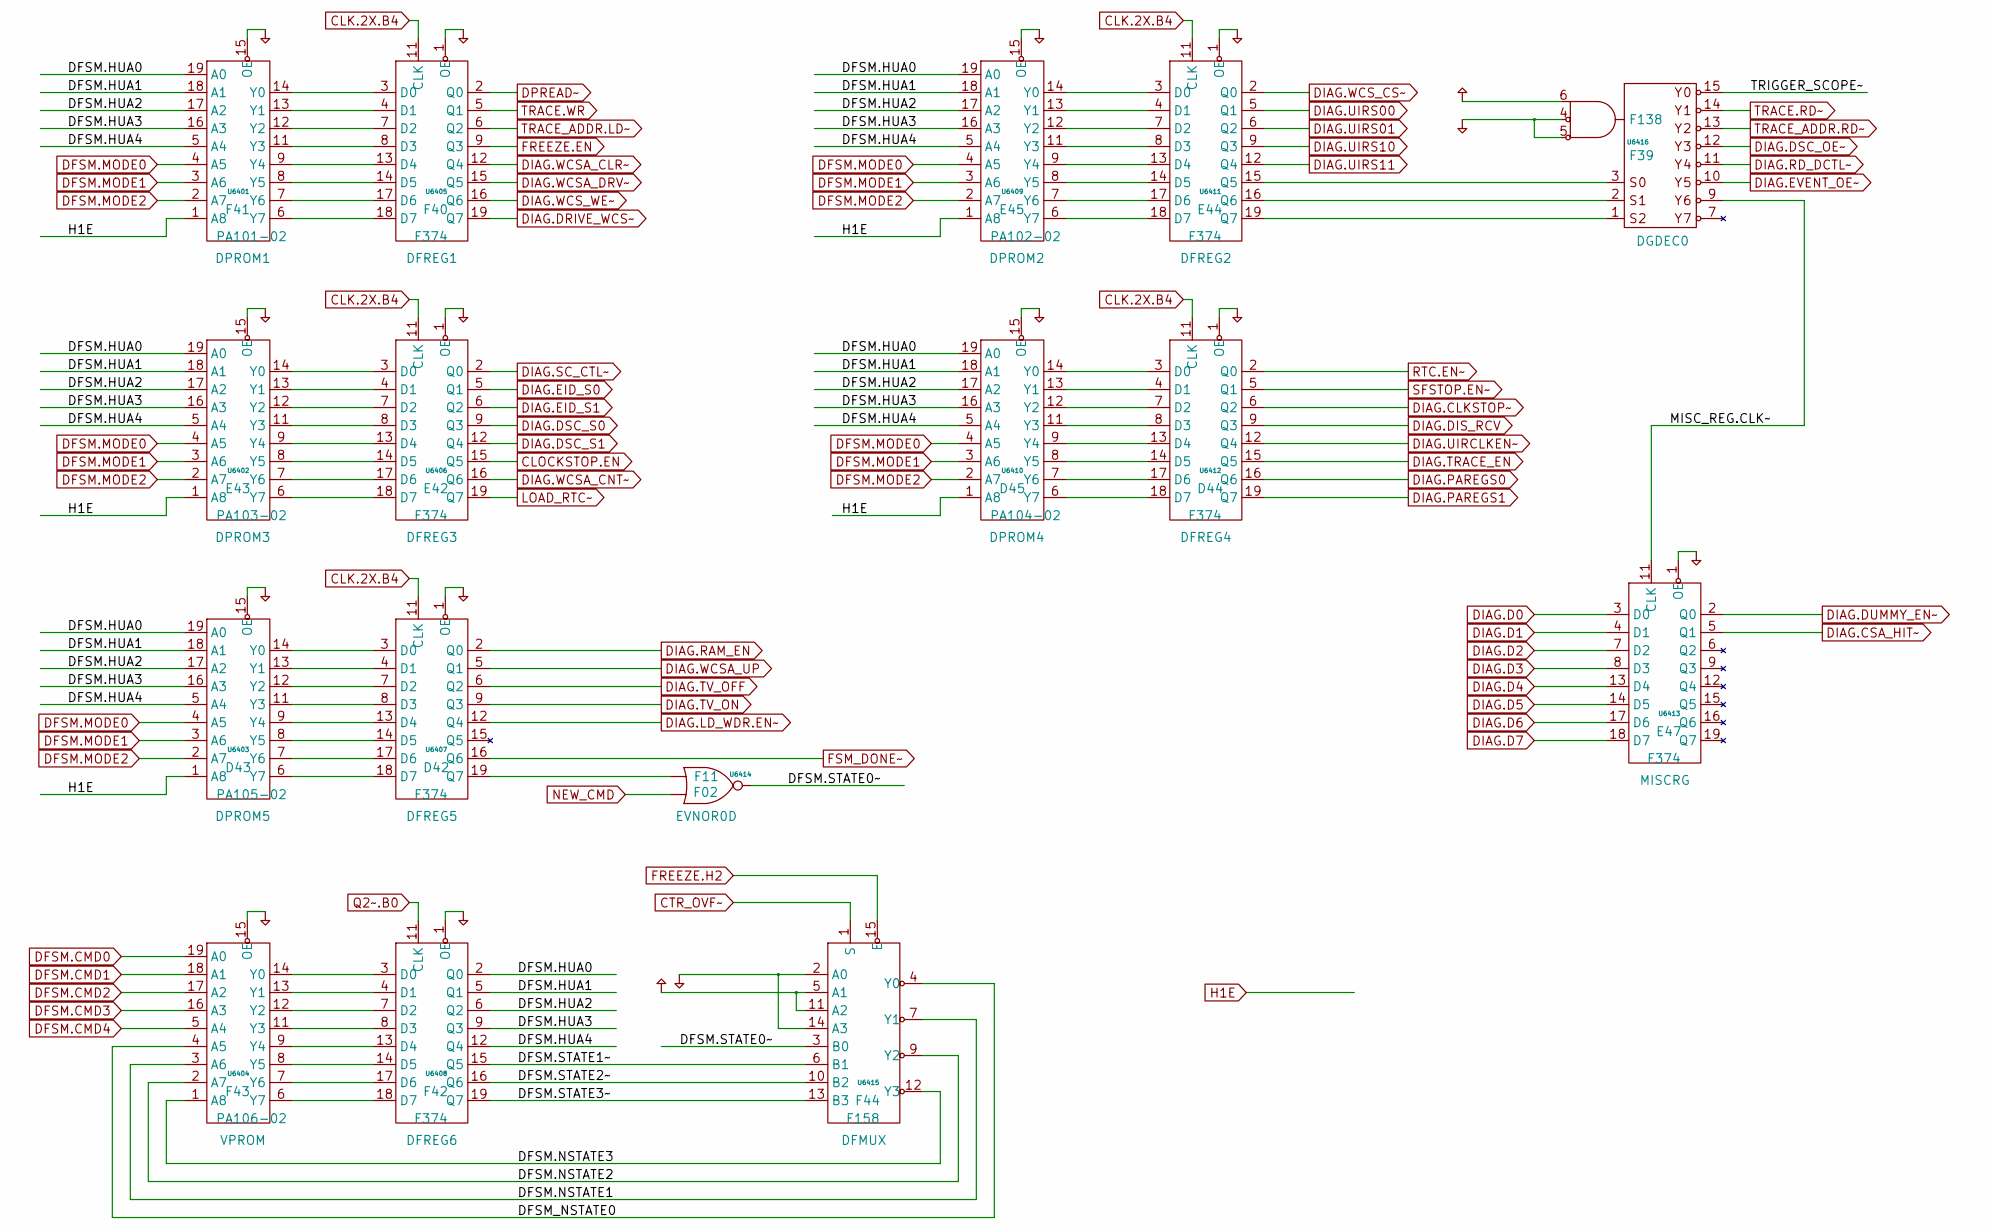
[picture p408: schematic pg_64.kicad_sch]

Parts:
U6401: PA101-02
U6402: PA103-02
U6403: PA105-02
U6404: PA106-02
U6405, U6406, U6407, U6408, U6411, U6412, U6413: F374
U6409: PA102-02
U6410: PA104-02
U6414: F02
U6415: F158
U6416: F138

Connections:
CLK.2X.B4: U6405.11 (CLK), U6406.11 (CLK), U6407.11 (CLK), U6411.11 (CLK), U6412.11 (CLK)
CLOCKSTOP.EN: U6406.15 (Q5)
CTR_OVF~: U6415.1 (S)
DFSM.CMD0: U6404.19 (A0)
DFSM.CMD1: U6404.18 (A1)
DFSM.CMD2: U6404.17 (A2)
DFSM.CMD3: U6404.16 (A3)
DFSM.CMD4: U6404.5 (A4)
DFSM.HUA0: U6401.19 (A0), U6402.19 (A0), U6403.19 (A0), U6408.2 (Q0), U6409.19 (A0), U6410.19 (A0)
DFSM.HUA1: U6401.18 (A1), U6402.18 (A1), U6403.18 (A1), U6408.5 (Q1), U6409.18 (A1), U6410.18 (A1)
DFSM.HUA2: U6401.17 (A2), U6402.17 (A2), U6403.17 (A2), U6408.6 (Q2), U6409.17 (A2), U6410.17 (A2)
DFSM.HUA3: U6401.16 (A3), U6402.16 (A3), U6403.16 (A3), U6408.9 (Q3), U6409.16 (A3), U6410.16 (A3)
DFSM.HUA4: U6401.5 (A4), U6402.5 (A4), U6403.5 (A4), U6408.12 (Q4), U6409.5 (A4), U6410.5 (A4)
DFSM.MODE0: U6401.4 (A5), U6402.4 (A5), U6403.4 (A5), U6409.4 (A5), U6410.4 (A5)
DFSM.MODE1: U6401.3 (A6), U6402.3 (A6), U6403.3 (A6), U6409.3 (A6), U6410.3 (A6)
DFSM.MODE2: U6401.2 (A7), U6402.2 (A7), U6403.2 (A7), U6409.2 (A7), U6410.2 (A7)
DFSM.NSTATE1: U6404.3 (A6), U6415.7 (Y1)
DFSM.NSTATE2: U6404.2 (A7), U6415.9 (Y2)
DFSM.NSTATE3: U6404.1 (A8), U6415.12 (Y3)
DFSM.STATE0~: U6414.3 (Q), U6415.3 (B0)
DFSM.STATE1~: U6408.15 (Q5), U6415.6 (B1)
DFSM.STATE2~: U6408.16 (Q6), U6415.10 (B2)
DFSM.STATE3~: U6408.19 (Q7), U6415.13 (B3)
DFSM_NSTATE0: U6404.4 (A5), U6415.4 (Y0)
DIAG.CLKSTOP~: U6412.6 (Q2)
DIAG.CSA_HIT~: U6413.5 (Q1)
DIAG.D0: U6413.3 (D0)
DIAG.D1: U6413.4 (D1)
DIAG.D2: U6413.7 (D2)
DIAG.D3: U6413.8 (D3)
DIAG.D4: U6413.13 (D4)
DIAG.D5: U6413.14 (D5)
DIAG.D6: U6413.17 (D6)
DIAG.D7: U6413.18 (D7)
DIAG.DIS_RCV: U6412.9 (Q3)
DIAG.DRIVE_WCS~: U6405.19 (Q7)
DIAG.DSC_OE~: U6416.12 (Y3_)
DIAG.DSC_S0: U6406.9 (Q3)
DIAG.DSC_S1: U6406.12 (Q4)
DIAG.DUMMY_EN~: U6413.2 (Q0)
DIAG.EID_S0: U6406.5 (Q1)
DIAG.EID_S1: U6406.6 (Q2)
DIAG.EVENT_OE~: U6416.10 (Y5_)
DIAG.LD_WDR.EN~: U6407.12 (Q4)
DIAG.PAREGS0: U6412.16 (Q6)
DIAG.PAREGS1: U6412.19 (Q7)
DIAG.RAM_EN: U6407.2 (Q0)
DIAG.RD_DCTL~: U6416.11 (Y4_)
DIAG.SC_CTL~: U6406.2 (Q0)
DIAG.TRACE_EN: U6412.15 (Q5)
DIAG.TV_OFF: U6407.6 (Q2)
DIAG.TV_ON: U6407.9 (Q3)
DIAG.UIRCLKEN~: U6412.12 (Q4)
DIAG.UIRS00: U6411.5 (Q1)
DIAG.UIRS01: U6411.6 (Q2)
DIAG.UIRS10: U6411.9 (Q3)
DIAG.UIRS11: U6411.12 (Q4)
DIAG.WCSA_CLR~: U6405.12 (Q4)
DIAG.WCSA_CNT~: U6406.16 (Q6)
DIAG.WCSA_DRV~: U6405.15 (Q5)
DIAG.WCSA_UP: U6407.5 (Q1)
DIAG.WCS_CS~: U6411.2 (Q0)
DIAG.WCS_WE~: U6405.16 (Q6)
DPREAD~: U6405.2 (Q0)
FREEZE.EN: U6405.9 (Q3)
FREEZE.H2: U6415.15 (E)
FSM_DONE~: U6407.16 (Q6)
H1E: U6401.1 (A8), U6402.1 (A8), U6403.1 (A8), U6409.1 (A8), U6410.1 (A8)
LOAD_RTC~: U6406.19 (Q7)
MISC_REG.CLK~: U6413.11 (CLK), U6416.9 (Y6_)
NEW_CMD: U6414.2 (D1)
unnamed: U6401.6 (Y7), U6405.18 (D7)
unnamed: U6401.7 (Y6), U6405.17 (D6)
unnamed: U6401.8 (Y5), U6405.14 (D5)
unnamed: U6401.9 (Y4), U6405.13 (D4)
unnamed: U6401.11 (Y3), U6405.8 (D3)
unnamed: U6401.12 (Y2), U6405.7 (D2)
unnamed: U6401.13 (Y1), U6405.4 (D1)
unnamed: U6401.14 (Y0), U6405.3 (D0)
unnamed: U6402.6 (Y7), U6406.18 (D7)
unnamed: U6402.7 (Y6), U6406.17 (D6)
unnamed: U6402.8 (Y5), U6406.14 (D5)
unnamed: U6402.9 (Y4), U6406.13 (D4)
unnamed: U6402.11 (Y3), U6406.8 (D3)
unnamed: U6402.12 (Y2), U6406.7 (D2)
unnamed: U6402.13 (Y1), U6406.4 (D1)
unnamed: U6402.14 (Y0), U6406.3 (D0)
unnamed: U6403.6 (Y7), U6407.18 (D7)
unnamed: U6403.7 (Y6), U6407.17 (D6)
unnamed: U6403.8 (Y5), U6407.14 (D5)
unnamed: U6403.9 (Y4), U6407.13 (D4)
unnamed: U6403.11 (Y3), U6407.8 (D3)
unnamed: U6403.12 (Y2), U6407.7 (D2)
unnamed: U6403.13 (Y1), U6407.4 (D1)
unnamed: U6403.14 (Y0), U6407.3 (D0)
unnamed: U6404.6 (Y7), U6408.18 (D7)
unnamed: U6404.7 (Y6), U6408.17 (D6)
unnamed: U6404.8 (Y5), U6408.14 (D5)
unnamed: U6404.9 (Y4), U6408.13 (D4)
unnamed: U6404.11 (Y3), U6408.8 (D3)
unnamed: U6404.12 (Y2), U6408.7 (D2)
unnamed: U6404.13 (Y1), U6408.4 (D1)
unnamed: U6404.14 (Y0), U6408.3 (D0)
unnamed: U6407.19 (Q7), U6414.1 (D0)
unnamed: U6409.6 (Y7), U6411.18 (D7)
unnamed: U6409.7 (Y6), U6411.17 (D6)
unnamed: U6409.8 (Y5), U6411.14 (D5)
unnamed: U6409.9 (Y4), U6411.13 (D4)
unnamed: U6409.11 (Y3), U6411.8 (D3)
unnamed: U6409.12 (Y2), U6411.7 (D2)
unnamed: U6409.13 (Y1), U6411.4 (D1)
unnamed: U6409.14 (Y0), U6411.3 (D0)
unnamed: U6410.6 (Y7), U6412.18 (D7)
unnamed: U6410.7 (Y6), U6412.17 (D6)
unnamed: U6410.8 (Y5), U6412.14 (D5)
unnamed: U6410.9 (Y4), U6412.13 (D4)
unnamed: U6410.11 (Y3), U6412.8 (D3)
unnamed: U6410.12 (Y2), U6412.7 (D2)
unnamed: U6410.13 (Y1), U6412.4 (D1)
unnamed: U6410.14 (Y0), U6412.3 (D0)
unnamed: U6411.15 (Q5), U6416.3 (S0)
unnamed: U6411.16 (Q6), U6416.2 (S1)
unnamed: U6411.19 (Q7), U6416.1 (S2)
PD: U6401.15 (OE), U6402.15 (OE), U6403.15 (OE), U6404.15 (OE), U6405.1 (OE), U6406.1 (OE), U6407.1 (OE), U6408.1 (OE), U6409.15 (OE), U6410.15 (OE), U6411.1 (OE), U6412.1 (OE), U6413.1 (OE), U6415.2 (A0), U6415.14 (A3), U6416.4 (D1), U6416.5 (D2)
PU: U6415.5 (A1), U6415.11 (A2), U6416.6 (D0)
Q2~.B0: U6408.11 (CLK)
RTC.EN~: U6412.2 (Q0)
SFSTOP.EN~: U6412.5 (Q1)
TRACE.RD~: U6416.14 (Y1_)
TRACE.WR: U6405.5 (Q1)
TRACE_ADDR.LD~: U6405.6 (Q2)
TRACE_ADDR.RD~: U6416.13 (Y2_)
TRIGGER_SCOPE~: U6416.15 (Y0_)
