Datamuseum-DK/R1000.HwDoc/Schematics/IOC/pg_65.kicad_sch

## KiCad design Schematics/IOC/pg_65.kicad_sch (2023-01-10)

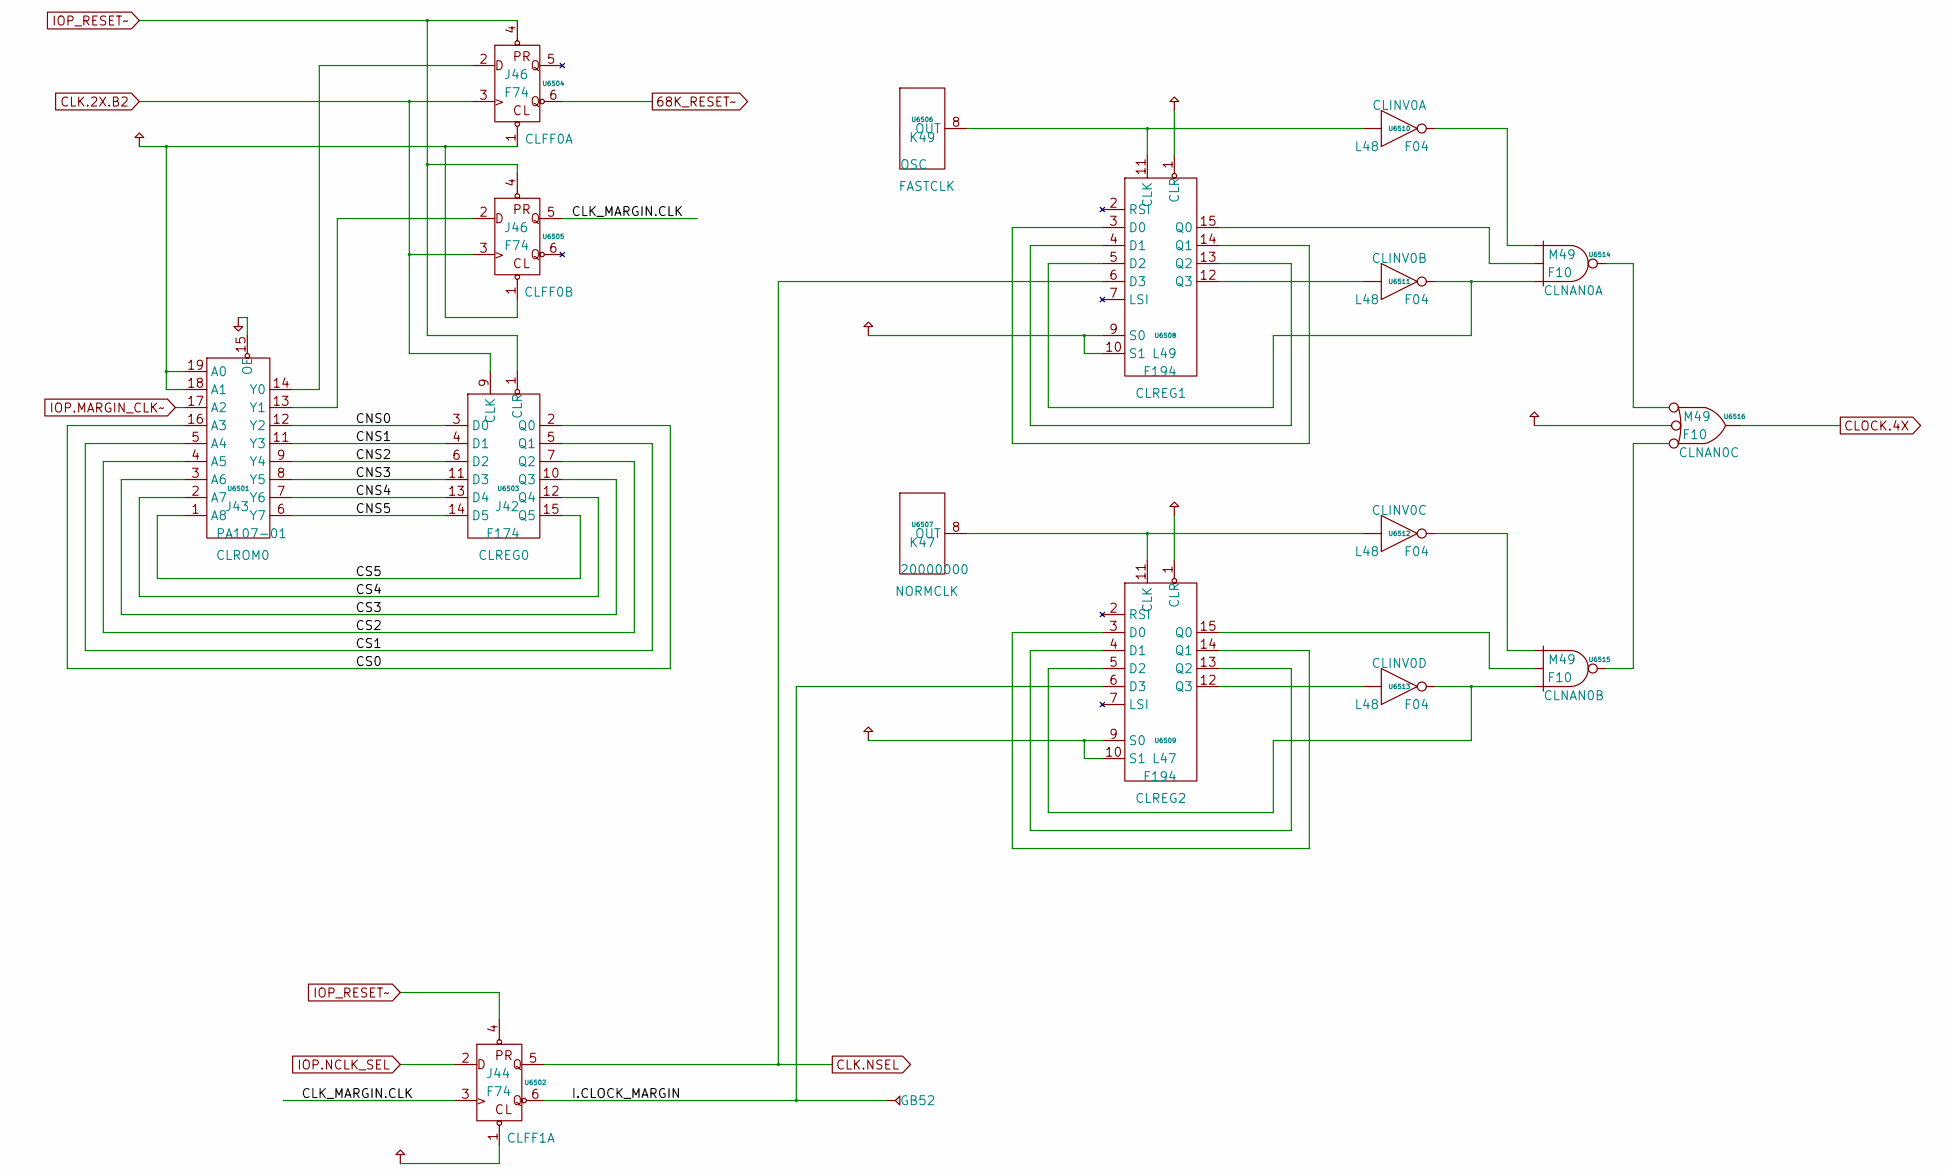
[picture p409: schematic pg_65.kicad_sch]

Parts:
GB52: GB
U6501: PA107-01
U6502, U6504, U6505: F74
U6503: F174
U6506: OSC
U6507: 20000000
U6508, U6509: F194
U6510, U6511, U6512, U6513: F04
U6514, U6515, U6516: F10

Connections:
68K_RESET~: U6504.6 (Q_)
CLK.2X.B2: U6503.9 (CLK), U6504.3 (CLK), U6505.3 (CLK)
CLK.NSEL: U6502.5 (Q), U6508.6 (D3)
CLK_MARGIN.CLK: U6502.3 (CLK), U6505.5 (Q)
CLOCK.4X: U6516.4 (Q)
CNS0: U6501.12 (Y2), U6503.3 (D0)
CNS1: U6501.11 (Y3), U6503.4 (D1)
CNS2: U6501.9 (Y4), U6503.6 (D2)
CNS3: U6501.8 (Y5), U6503.11 (D3)
CNS4: U6501.7 (Y6), U6503.13 (D4)
CNS5: U6501.6 (Y7), U6503.14 (D5)
CS0: U6501.16 (A3), U6503.2 (Q0)
CS1: U6501.5 (A4), U6503.5 (Q1)
CS2: U6501.4 (A5), U6503.7 (Q2)
CS3: U6501.3 (A6), U6503.10 (Q3)
CS4: U6501.2 (A7), U6503.12 (Q4)
CS5: U6501.1 (A8), U6503.15 (Q5)
I.CLOCK_MARGIN: GB52.1, U6502.6 (Q_), U6509.6 (D3)
IOP.MARGIN_CLK~: U6501.17 (A2)
IOP.NCLK_SEL: U6502.2 (D)
IOP_RESET~: U6502.4 (PR_), U6503.1 (CLR), U6504.4 (PR_), U6505.4 (PR_)
unnamed: U6501.13 (Y1), U6505.2 (D)
unnamed: U6501.14 (Y0), U6504.2 (D)
unnamed: U6506.8, U6508.11 (CLK), U6510.1 (D0)
unnamed: U6507.8, U6509.11 (CLK), U6512.1 (D0)
unnamed: U6508.5 (D2), U6511.2 (Q), U6514.3 (D2)
unnamed: U6508.12 (Q3), U6511.1 (D0)
unnamed: U6508.4 (D1), U6508.13 (Q2)
unnamed: U6508.3 (D0), U6508.14 (Q1)
unnamed: U6508.15 (Q0), U6514.2 (D1)
unnamed: U6509.5 (D2), U6513.2 (Q), U6515.3 (D2)
unnamed: U6509.12 (Q3), U6513.1 (D0)
unnamed: U6509.4 (D1), U6509.13 (Q2)
unnamed: U6509.3 (D0), U6509.14 (Q1)
unnamed: U6509.15 (Q0), U6515.2 (D1)
unnamed: U6510.2 (Q), U6514.1 (D0)
unnamed: U6512.2 (Q), U6515.1 (D0)
unnamed: U6514.4 (Q), U6516.1 (D0)
unnamed: U6515.4 (Q), U6516.3 (D2)
PD: U6501.15 (OE)
PU: U6501.18 (A1), U6501.19 (A0), U6502.1 (CL_), U6504.1 (CL_), U6505.1 (CL_), U6508.1 (CLR), U6508.9 (S0), U6508.10 (S1), U6509.1 (CLR), U6509.9 (S0), U6509.10 (S1), U6516.2 (D1)
