Datamuseum-DK/R1000.HwDoc/Schematics/IOC/pg_66.kicad_sch

## KiCad design Schematics/IOC/pg_66.kicad_sch (2023-01-10)

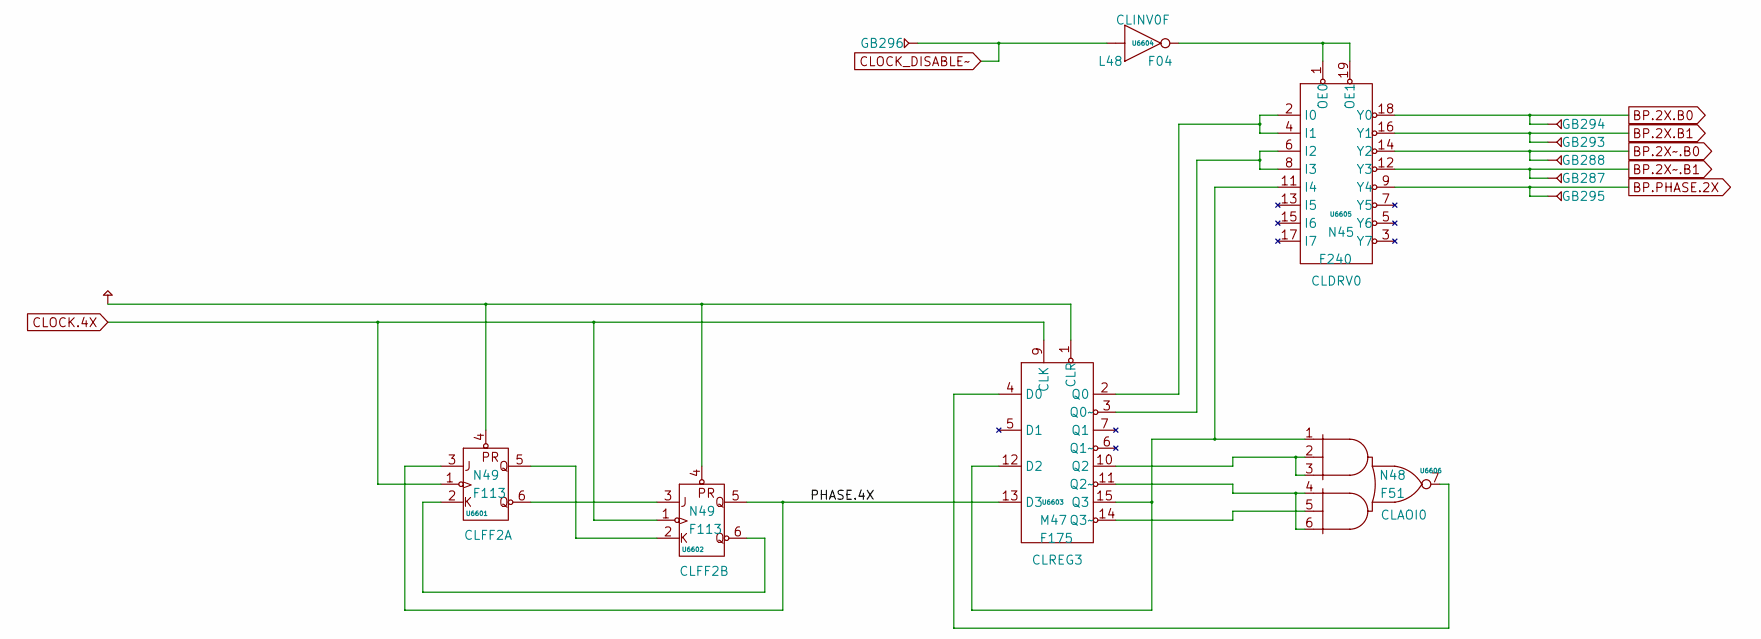
[picture p410: schematic pg_66.kicad_sch]

Parts:
GB287, GB288, GB293, GB294, GB295, GB296: GB
U6601, U6602: F113
U6603: F175
U6604: F04
U6605: F240
U6606: F51

Connections:
BP.2X.B0: GB294.1, U6605.18 (Y0)
BP.2X.B1: GB293.1, U6605.16 (Y1)
BP.2X~.B0: GB288.1, U6605.14 (Y2)
BP.2X~.B1: GB287.1, U6605.12 (Y3)
BP.PHASE.2X: GB295.1, U6605.9 (Y4)
CLOCK.4X: U6601.1 (CLK_), U6602.1 (CLK_), U6603.9 (CLK)
CLOCK_DISABLE~: GB296.1, U6604.1 (D0)
unnamed: U6601.2 (K), U6602.6 (Q_)
unnamed: U6601.5 (Q), U6602.2 (K)
unnamed: U6601.6 (Q_), U6602.3 (J)
unnamed: U6603.2 (Q0), U6605.2 (I0), U6605.4 (I1)
unnamed: U6603.3 (Q0~), U6605.6 (I2), U6605.8 (I3)
unnamed: U6603.4 (D0), U6606.7 (Q)
unnamed: U6603.10 (Q2), U6606.2 (A2), U6606.3 (A3)
unnamed: U6603.11 (Q2~), U6606.4 (B1), U6606.6 (B3)
unnamed: U6603.12 (D2), U6603.15 (Q3), U6605.11 (I4), U6606.1 (A1)
unnamed: U6603.14 (Q3~), U6606.5 (B2)
unnamed: U6604.2 (Q), U6605.1 (OE0), U6605.19 (OE1)
PHASE.4X: U6601.3 (J), U6602.5 (Q), U6603.13 (D3)
PU: U6601.4 (PR_), U6602.4 (PR_), U6603.1 (CLR)
