Datamuseum-DK/R1000.HwDoc/Schematics/IOC/pg_67.kicad_sch

## KiCad design Schematics/IOC/pg_67.kicad_sch (2023-01-10)

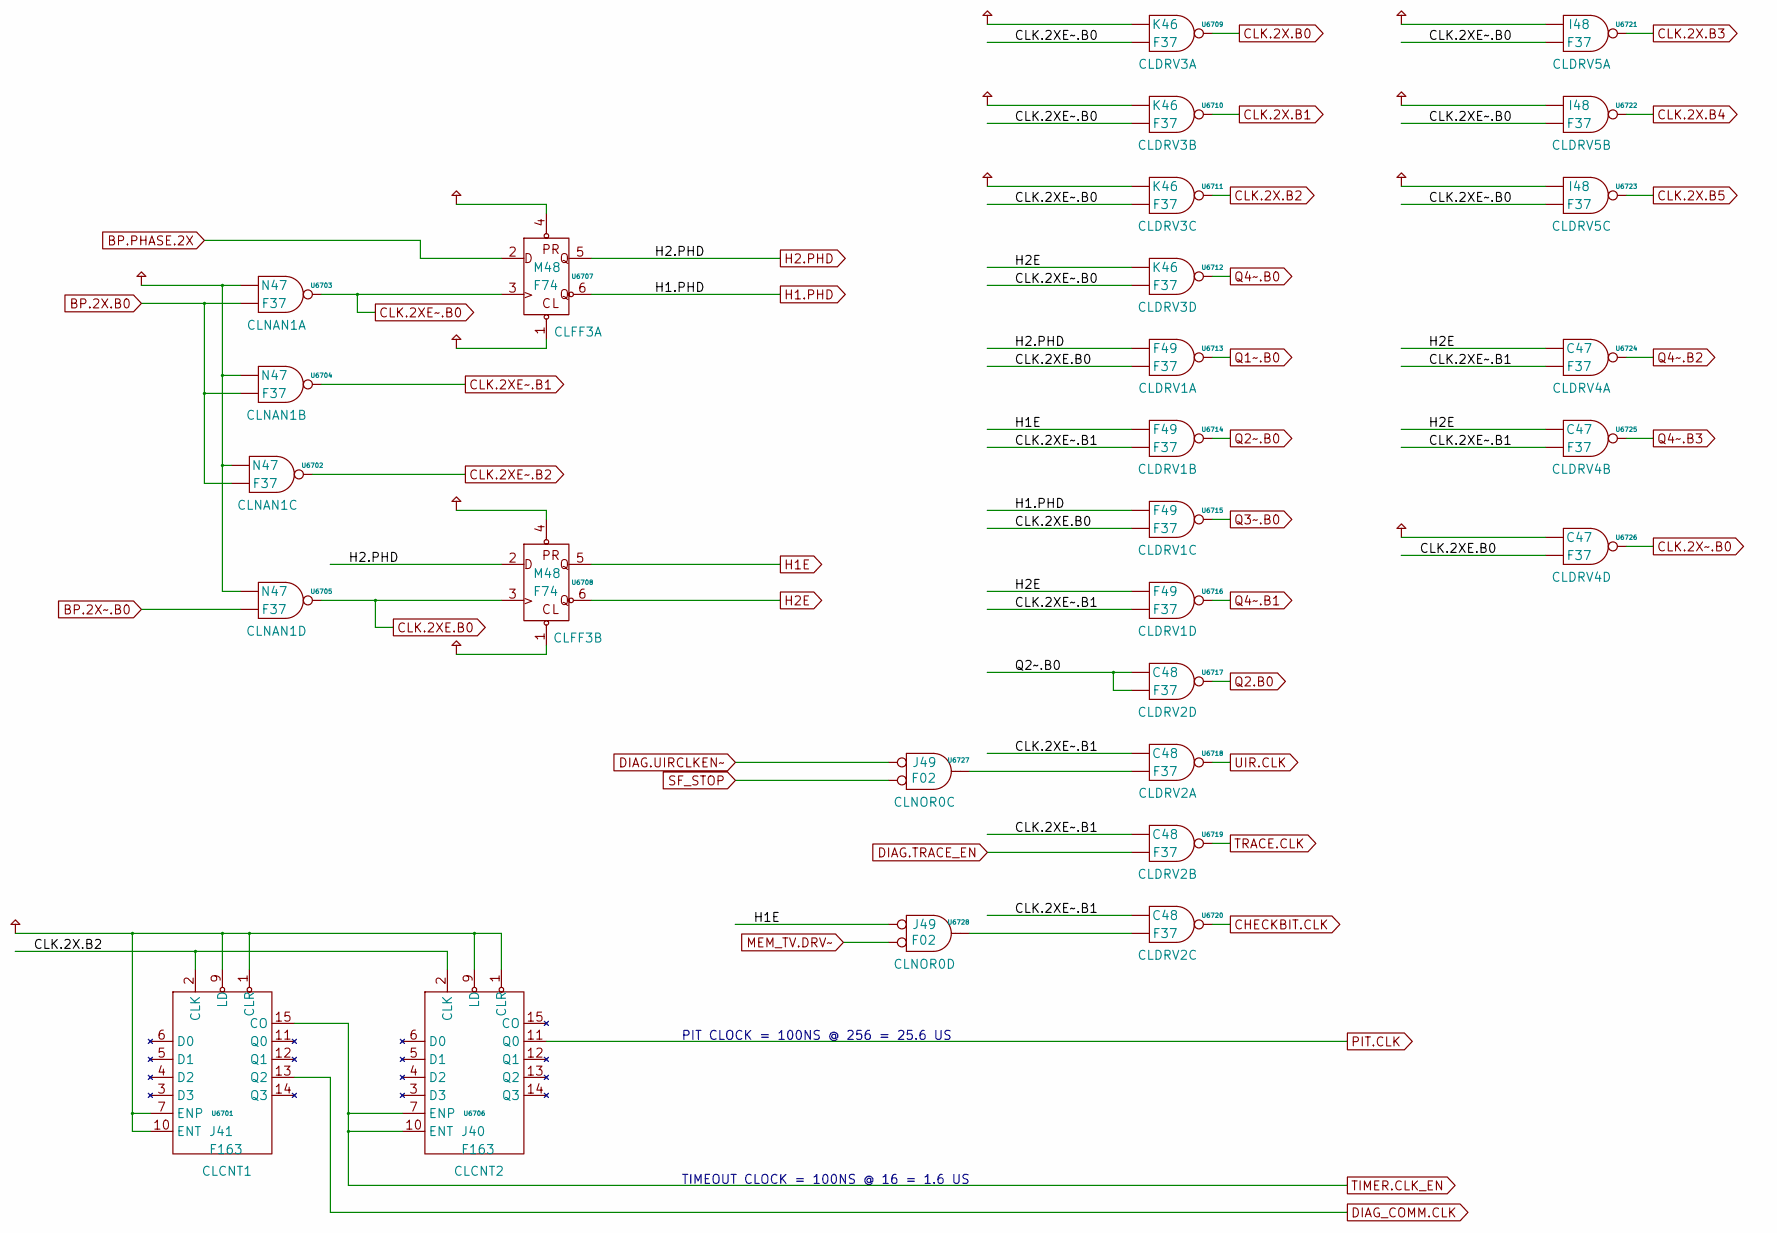
[picture p411: schematic pg_67.kicad_sch]

Parts:
U6701, U6706: F163
U6702, U6703, U6704, U6705, U6709, U6710, U6711, U6712, U6713, U6714, U6715, U6716, U6717, U6718, U6719, U6720, U6721, U6722, U6723, U6724, U6725, U6726: F37
U6707, U6708: F74
U6727, U6728: F02

Connections:
BP.2X.B0: U6702.2 (D1), U6703.2 (D1), U6704.2 (D1)
BP.2X~.B0: U6705.2 (D1)
BP.PHASE.2X: U6707.2 (D)
CHECKBIT.CLK: U6720.3 (Q)
CLK.2X.B0: U6709.3 (Q)
CLK.2X.B1: U6710.3 (Q)
CLK.2X.B2: U6701.2 (CLK), U6706.2 (CLK), U6711.3 (Q)
CLK.2X.B3: U6721.3 (Q)
CLK.2X.B4: U6722.3 (Q)
CLK.2X.B5: U6723.3 (Q)
CLK.2XE.B0: U6705.3 (Q), U6708.3 (CLK), U6713.2 (D1), U6715.2 (D1), U6726.2 (D1)
CLK.2XE~.B0: U6703.3 (Q), U6707.3 (CLK), U6709.2 (D1), U6710.2 (D1), U6711.2 (D1), U6712.2 (D1), U6721.2 (D1), U6722.2 (D1), U6723.2 (D1)
CLK.2XE~.B1: U6704.3 (Q), U6714.2 (D1), U6716.2 (D1), U6718.1 (D0), U6719.1 (D0), U6720.1 (D0), U6724.2 (D1), U6725.2 (D1)
CLK.2XE~.B2: U6702.3 (Q)
CLK.2X~.B0: U6726.3 (Q)
DIAG.TRACE_EN: U6719.2 (D1)
DIAG.UIRCLKEN~: U6727.1 (D0)
DIAG_COMM.CLK: U6701.13 (Q2)
H1.PHD: U6707.6 (Q_), U6715.1 (D0)
H1E: U6708.5 (Q), U6714.1 (D0), U6728.1 (D0)
H2.PHD: U6707.5 (Q), U6708.2 (D), U6713.1 (D0)
H2E: U6708.6 (Q_), U6712.1 (D0), U6716.1 (D0), U6724.1 (D0), U6725.1 (D0)
MEM_TV.DRV~: U6728.2 (D1)
unnamed: U6718.2 (D1), U6727.3 (Q)
unnamed: U6720.2 (D1), U6728.3 (Q)
PIT.CLK: U6706.11 (Q0)
PU: U6701.1 (CLR), U6701.7 (ENP), U6701.9 (LD), U6701.10 (ENT), U6702.1 (D0), U6703.1 (D0), U6704.1 (D0), U6705.1 (D0), U6706.1 (CLR), U6706.9 (LD), U6707.1 (CL_), U6707.4 (PR_), U6708.1 (CL_), U6708.4 (PR_), U6709.1 (D0), U6710.1 (D0), U6711.1 (D0), U6721.1 (D0), U6722.1 (D0), U6723.1 (D0), U6726.1 (D0)
Q1~.B0: U6713.3 (Q)
Q2.B0: U6717.3 (Q)
Q2~.B0: U6714.3 (Q), U6717.1 (D0), U6717.2 (D1)
Q3~.B0: U6715.3 (Q)
Q4~.B0: U6712.3 (Q)
Q4~.B1: U6716.3 (Q)
Q4~.B2: U6724.3 (Q)
Q4~.B3: U6725.3 (Q)
SF_STOP: U6727.2 (D1)
TIMER.CLK_EN: U6701.15 (CO), U6706.7 (ENP), U6706.10 (ENT)
TRACE.CLK: U6719.3 (Q)
UIR.CLK: U6718.3 (Q)

Notes on the sheet:
TIMEOUT CLOCK = 100NS @ 16 = 1.6 US
PIT CLOCK = 100NS @ 256 = 25.6 US
