Datamuseum-DK/R1000.HwDoc/Schematics/IOC/pg_68.kicad_sch

## KiCad design Schematics/IOC/pg_68.kicad_sch (2023-01-10)

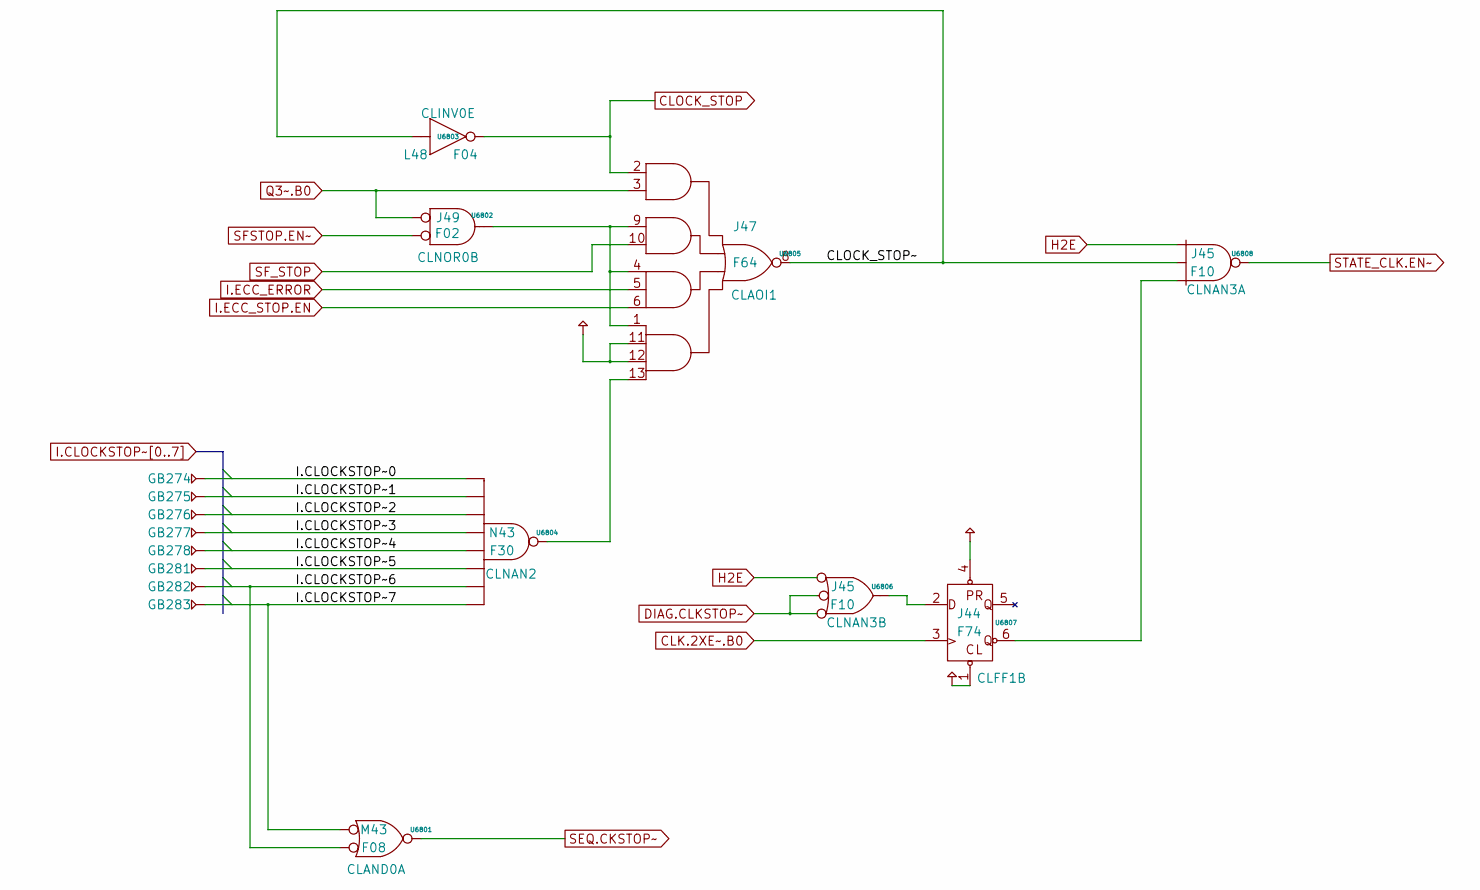
[picture p412: schematic pg_68.kicad_sch]

Parts:
GB274, GB275, GB276, GB277, GB278, GB281, GB282, GB283: GB
U6801: F08
U6802: F02
U6803: F04
U6804: F30
U6805: F64
U6806, U6808: F10
U6807: F74

Connections:
CLK.2XE~.B0: U6807.3 (CLK)
CLOCK_STOP: U6803.2 (Q), U6805.2 (A0)
CLOCK_STOP~: U6803.1 (D0), U6805.8 (Q), U6808.2 (D1)
DIAG.CLKSTOP~: U6806.2 (D1), U6806.3 (D2)
H2E: U6806.1 (D0), U6808.1 (D0)
I.CLOCKSTOP~0: GB274.1, U6804.11 (D0)
I.CLOCKSTOP~1: GB275.1, U6804.12 (D1)
I.CLOCKSTOP~2: GB276.1, U6804.1 (D2)
I.CLOCKSTOP~3: GB277.1, U6804.2 (D3)
I.CLOCKSTOP~4: GB278.1, U6804.3 (D4)
I.CLOCKSTOP~5: GB281.1, U6804.4 (D5)
I.CLOCKSTOP~6: GB282.1, U6801.2 (D1), U6804.5 (D6)
I.CLOCKSTOP~7: GB283.1, U6801.1 (D0), U6804.6 (D7)
I.ECC_ERROR: U6805.5 (C1)
I.ECC_STOP.EN: U6805.6 (C2)
unnamed: U6802.3 (Q), U6805.1 (D0), U6805.4 (C0), U6805.9 (B0)
unnamed: U6804.8 (Q), U6805.13 (D3)
unnamed: U6806.4 (Q), U6807.2 (D)
unnamed: U6807.6 (Q_), U6808.3 (D2)
PU: U6805.11 (D1), U6805.12 (D2), U6807.1 (CL_), U6807.4 (PR_)
Q3~.B0: U6802.1 (D0), U6805.3 (A1)
SEQ.CKSTOP~: U6801.3 (Q)
SFSTOP.EN~: U6802.2 (D1)
SF_STOP: U6805.10 (B1)
STATE_CLK.EN~: U6808.4 (Q)
