Datamuseum-DK/R1000.HwDoc/Schematics/IOC/pg_69.kicad_sch

## KiCad design Schematics/IOC/pg_69.kicad_sch (2023-01-10)

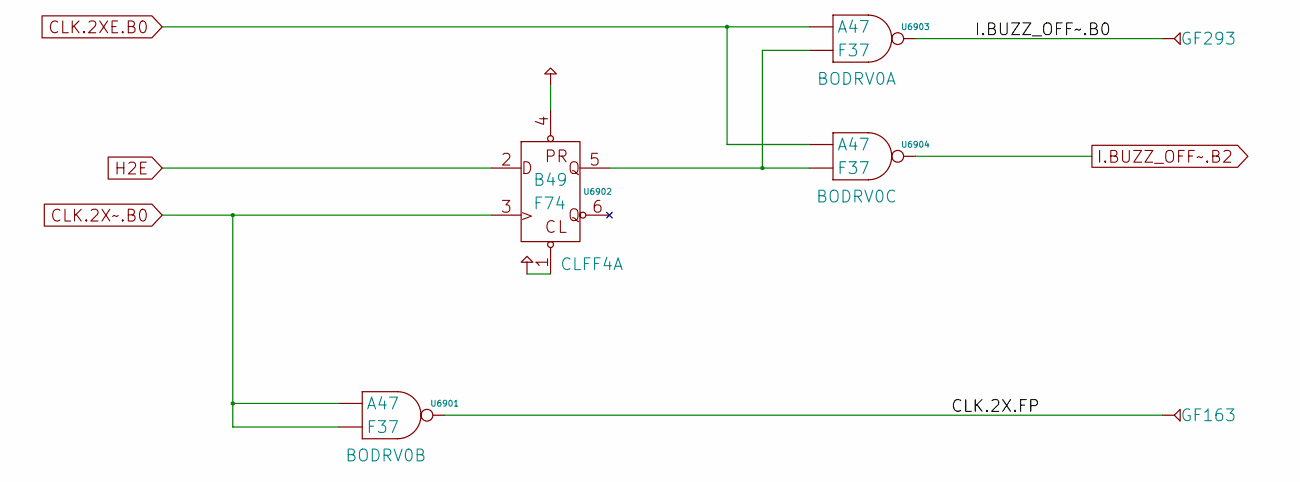
[picture p413: schematic pg_69.kicad_sch]

Parts:
GF163, GF293: GF
U6901, U6903, U6904: F37
U6902: F74

Connections:
CLK.2X.FP: GF163.1, U6901.3 (Q)
CLK.2XE.B0: U6903.1 (D0), U6904.1 (D0)
CLK.2X~.B0: U6901.1 (D0), U6901.2 (D1), U6902.3 (CLK)
H2E: U6902.2 (D)
I.BUZZ_OFF~.B0: GF293.1, U6903.3 (Q)
I.BUZZ_OFF~.B2: U6904.3 (Q)
unnamed: U6902.5 (Q), U6903.2 (D1), U6904.2 (D1)
PU: U6902.1 (CL_), U6902.4 (PR_)
