Datamuseum-DK/R1000.HwDoc/Schematics/IOC/pg_70.kicad_sch

## KiCad design Schematics/IOC/pg_70.kicad_sch (2023-01-10)

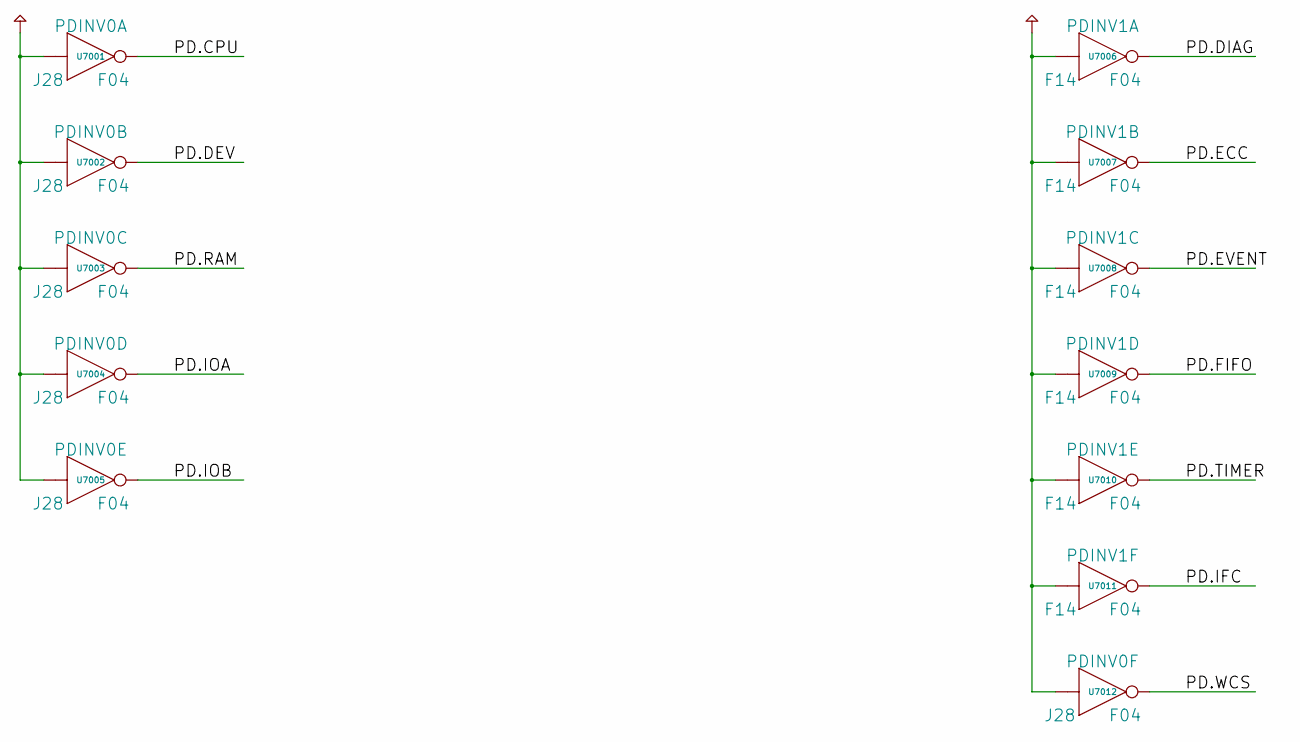
[picture p414: schematic pg_70.kicad_sch]

Parts:
U7001, U7002, U7003, U7004, U7005, U7006, U7007, U7008, U7009, U7010, U7011, U7012: F04

Connections:
PD.CPU: U7001.2 (Q)
PD.DEV: U7002.2 (Q)
PD.DIAG: U7006.2 (Q)
PD.ECC: U7007.2 (Q)
PD.EVENT: U7008.2 (Q)
PD.FIFO: U7009.2 (Q)
PD.IFC: U7011.2 (Q)
PD.IOA: U7004.2 (Q)
PD.IOB: U7005.2 (Q)
PD.RAM: U7003.2 (Q)
PD.TIMER: U7010.2 (Q)
PD.WCS: U7012.2 (Q)
PU: U7001.1 (D0), U7002.1 (D0), U7003.1 (D0), U7004.1 (D0), U7005.1 (D0), U7006.1 (D0), U7007.1 (D0), U7008.1 (D0), U7009.1 (D0), U7010.1 (D0), U7011.1 (D0), U7012.1 (D0)
