Datamuseum-DK/R1000.HwDoc/Schematics/IOC/pg_71.kicad_sch

## KiCad design Schematics/IOC/pg_71.kicad_sch (2023-01-10)

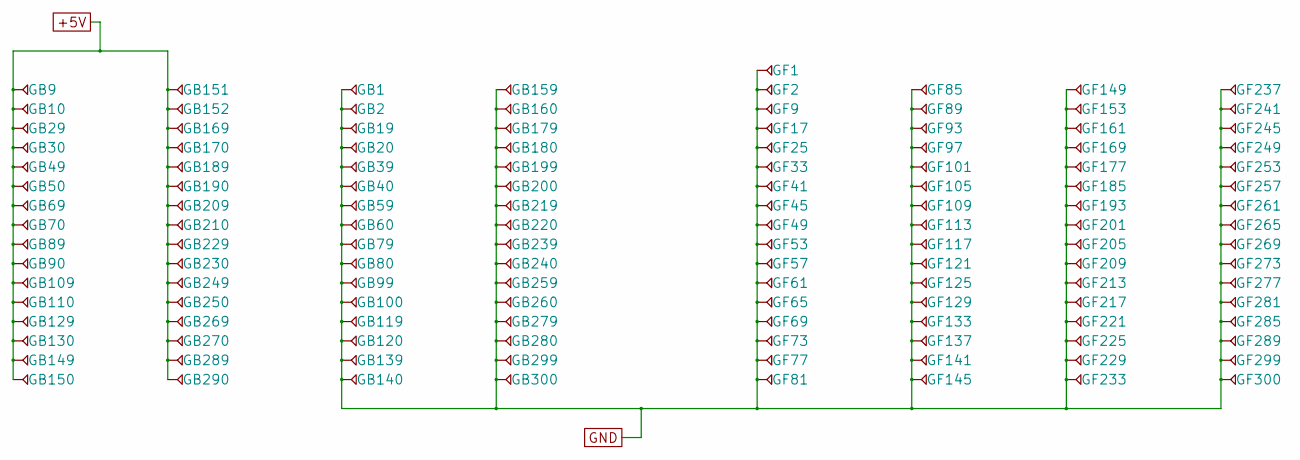
[picture p415: schematic pg_71.kicad_sch]

Parts:
GB1, GB2, GB9, GB10, GB19, GB20, GB29, GB30, GB39, GB40, GB49, GB50, GB59, GB60, GB69, GB70, GB79, GB80, GB89, GB90, GB99, GB100, GB109, GB110, GB119, GB120, GB129, GB130, GB139, GB140, GB149, GB150, GB151, GB152, GB159, GB160, GB169, GB170, GB179, GB180, GB189, GB190, GB199, GB200, GB209, GB210, GB219, GB220, GB229, GB230, GB239, GB240, GB249, GB250, GB259, GB260, GB269, GB270, GB279, GB280, GB289, GB290, GB299, GB300: GB
GF1, GF2, GF9, GF17, GF25, GF33, GF41, GF45, GF49, GF53, GF57, GF61, GF65, GF69, GF73, GF77, GF81, GF85, GF89, GF93, GF97, GF101, GF105, GF109, GF113, GF117, GF121, GF125, GF129, GF133, GF137, GF141, GF145, GF149, GF153, GF161, GF169, GF177, GF185, GF193, GF201, GF205, GF209, GF213, GF217, GF221, GF225, GF229, GF233, GF237, GF241, GF245, GF249, GF253, GF257, GF261, GF265, GF269, GF273, GF277, GF281, GF285, GF289, GF299, GF300: GF

Connections:
+5V: GB9.1, GB10.1, GB29.1, GB30.1, GB49.1, GB50.1, GB69.1, GB70.1, GB89.1, GB90.1, GB109.1, GB110.1, GB129.1, GB130.1, GB149.1, GB150.1, GB151.1, GB152.1, GB169.1, GB170.1, GB189.1, GB190.1, GB209.1, GB210.1, GB229.1, GB230.1, GB249.1, GB250.1, GB269.1, GB270.1, GB289.1, GB290.1
GND: GB1.1, GB2.1, GB19.1, GB20.1, GB39.1, GB40.1, GB59.1, GB60.1, GB79.1, GB80.1, GB99.1, GB100.1, GB119.1, GB120.1, GB139.1, GB140.1, GB159.1, GB160.1, GB179.1, GB180.1, GB199.1, GB200.1, GB219.1, GB220.1, GB239.1, GB240.1, GB259.1, GB260.1, GB279.1, GB280.1, GB299.1, GB300.1, GF1.1, GF2.1, GF9.1, GF17.1, GF25.1, GF33.1, GF41.1, GF45.1, GF49.1, GF53.1, GF57.1, GF61.1, GF65.1, GF69.1, GF73.1, GF77.1, GF81.1, GF85.1, GF89.1, GF93.1, GF97.1, GF101.1, GF105.1, GF109.1, GF113.1, GF117.1, GF121.1, GF125.1, GF129.1, GF133.1, GF137.1, GF141.1, GF145.1, GF149.1, GF153.1, GF161.1, GF169.1, GF177.1, GF185.1, GF193.1, GF201.1, GF205.1, GF209.1, GF213.1, GF217.1, GF221.1, GF225.1, GF229.1, GF233.1, GF237.1, GF241.1, GF245.1, GF249.1, GF253.1, GF257.1, GF261.1, GF265.1, GF269.1, GF273.1, GF277.1, GF281.1, GF285.1, GF289.1, GF299.1, GF300.1
