Datamuseum-DK/R1000.HwDoc/Schematics/MEM32/pg_02.kicad_sch

## KiCad design Schematics/MEM32/pg_02.kicad_sch (2023-01-10)

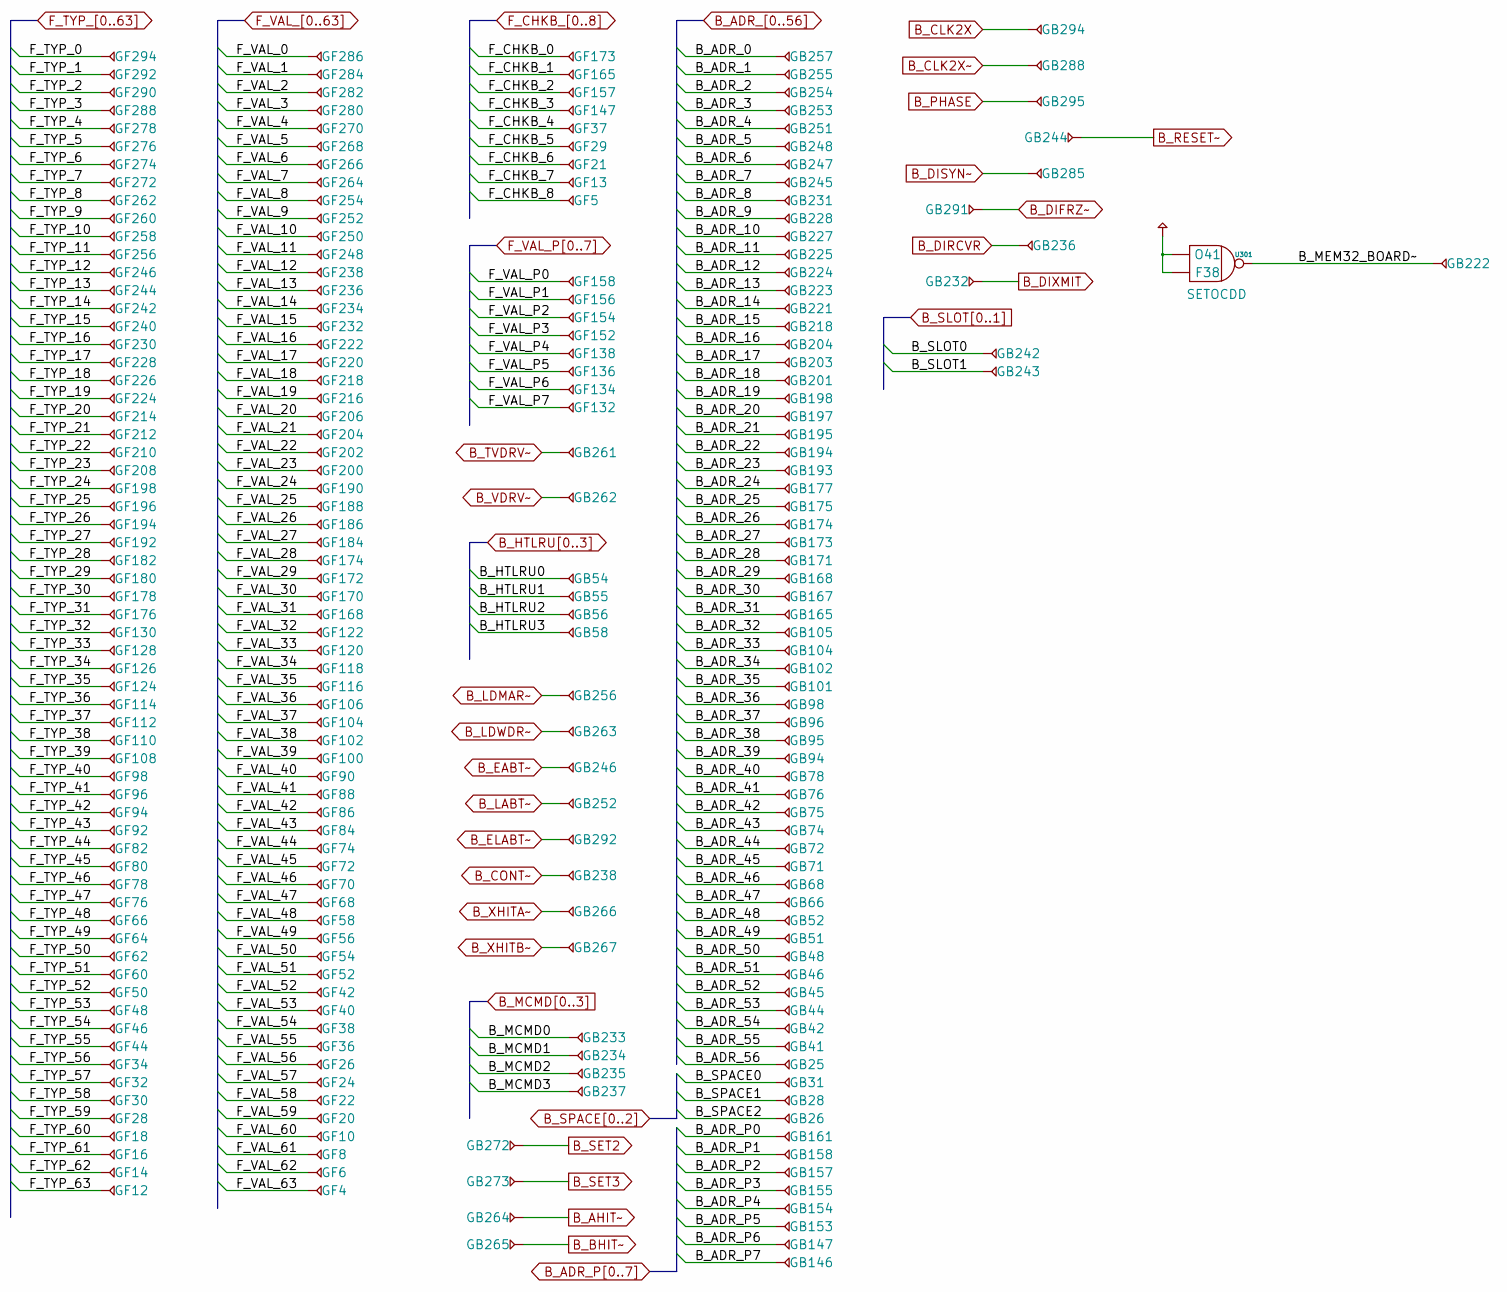
[picture p416: schematic pg_02.kicad_sch]

Parts:
GB25, GB26, GB28, GB31, GB41, GB42, GB44, GB45, GB46, GB48, GB51, GB52, GB54, GB55, GB56, GB58, GB66, GB68, GB71, GB72, GB74, GB75, GB76, GB78, GB94, GB95, GB96, GB98, GB101, GB102, GB104, GB105, GB146, GB147, GB153, GB154, GB155, GB157, GB158, GB161, GB165, GB167, GB168, GB171, GB173, GB174, GB175, GB177, GB193, GB194, GB195, GB197, GB198, GB201, GB203, GB204, GB218, GB221, GB222, GB223, GB224, GB225, GB227, GB228, GB231, GB232, GB233, GB234, GB235, GB236, GB237, GB238, GB242, GB243, GB244, GB245, GB246, GB247, GB248, GB251, GB252, GB253, GB254, GB255, GB256, GB257, GB261, GB262, GB263, GB264, GB265, GB266, GB267, GB272, GB273, GB285, GB288, GB291, GB292, GB294, GB295: GB
GF4, GF5, GF6, GF8, GF10, GF12, GF13, GF14, GF16, GF18, GF20, GF21, GF22, GF24, GF26, GF28, GF29, GF30, GF32, GF34, GF36, GF37, GF38, GF40, GF42, GF44, GF46, GF48, GF50, GF52, GF54, GF56, GF58, GF60, GF62, GF64, GF66, GF68, GF70, GF72, GF74, GF76, GF78, GF80, GF82, GF84, GF86, GF88, GF90, GF92, GF94, GF96, GF98, GF100, GF102, GF104, GF106, GF108, GF110, GF112, GF114, GF116, GF118, GF120, GF122, GF124, GF126, GF128, GF130, GF132, GF134, GF136, GF138, GF147, GF152, GF154, GF156, GF157, GF158, GF165, GF168, GF170, GF172, GF173, GF174, GF176, GF178, GF180, GF182, GF184, GF186, GF188, GF190, GF192, GF194, GF196, GF198, GF200, GF202, GF204, GF206, GF208, GF210, GF212, GF214, GF216, GF218, GF220, GF222, GF224, GF226, GF228, GF230, GF232, GF234, GF236, GF238, GF240, GF242, GF244, GF246, GF248, GF250, GF252, GF254, GF256, GF258, GF260, GF262, GF264, GF266, GF268, GF270, GF272, GF274, GF276, GF278, GF280, GF282, GF284, GF286, GF288, GF290, GF292, GF294: GF
U301: F38

Connections:
B_ADR_0: GB257.1
B_ADR_1: GB255.1
B_ADR_2: GB254.1
B_ADR_3: GB253.1
B_ADR_4: GB251.1
B_ADR_5: GB248.1
B_ADR_6: GB247.1
B_ADR_7: GB245.1
B_ADR_8: GB231.1
B_ADR_9: GB228.1
B_ADR_10: GB227.1
B_ADR_11: GB225.1
B_ADR_12: GB224.1
B_ADR_13: GB223.1
B_ADR_14: GB221.1
B_ADR_15: GB218.1
B_ADR_16: GB204.1
B_ADR_17: GB203.1
B_ADR_18: GB201.1
B_ADR_19: GB198.1
B_ADR_20: GB197.1
B_ADR_21: GB195.1
B_ADR_22: GB194.1
B_ADR_23: GB193.1
B_ADR_24: GB177.1
B_ADR_25: GB175.1
B_ADR_26: GB174.1
B_ADR_27: GB173.1
B_ADR_28: GB171.1
B_ADR_29: GB168.1
B_ADR_30: GB167.1
B_ADR_31: GB165.1
B_ADR_32: GB105.1
B_ADR_33: GB104.1
B_ADR_34: GB102.1
B_ADR_35: GB101.1
B_ADR_36: GB98.1
B_ADR_37: GB96.1
B_ADR_38: GB95.1
B_ADR_39: GB94.1
B_ADR_40: GB78.1
B_ADR_41: GB76.1
B_ADR_42: GB75.1
B_ADR_43: GB74.1
B_ADR_44: GB72.1
B_ADR_45: GB71.1
B_ADR_46: GB68.1
B_ADR_47: GB66.1
B_ADR_48: GB52.1
B_ADR_49: GB51.1
B_ADR_50: GB48.1
B_ADR_51: GB46.1
B_ADR_52: GB45.1
B_ADR_53: GB44.1
B_ADR_54: GB42.1
B_ADR_55: GB41.1
B_ADR_56: GB25.1
B_ADR_P0: GB161.1
B_ADR_P1: GB158.1
B_ADR_P2: GB157.1
B_ADR_P3: GB155.1
B_ADR_P4: GB154.1
B_ADR_P5: GB153.1
B_ADR_P6: GB147.1
B_ADR_P7: GB146.1
B_AHIT~: GB264.1
B_BHIT~: GB265.1
B_CLK2X: GB294.1
B_CLK2X~: GB288.1
B_CONT~: GB238.1
B_DIFRZ~: GB291.1
B_DIRCVR: GB236.1
B_DISYN~: GB285.1
B_DIXMIT: GB232.1
B_EABT~: GB246.1
B_ELABT~: GB292.1
B_HTLRU0: GB54.1
B_HTLRU1: GB55.1
B_HTLRU2: GB56.1
B_HTLRU3: GB58.1
B_LABT~: GB252.1
B_LDMAR~: GB256.1
B_LDWDR~: GB263.1
B_MCMD0: GB233.1
B_MCMD1: GB234.1
B_MCMD2: GB235.1
B_MCMD3: GB237.1
B_MEM32_BOARD~: GB222.1, U301.3 (Q)
B_PHASE: GB295.1
B_RESET~: GB244.1
B_SET2: GB272.1
B_SET3: GB273.1
B_SLOT0: GB242.1
B_SLOT1: GB243.1
B_SPACE0: GB31.1
B_SPACE1: GB28.1
B_SPACE2: GB26.1
B_TVDRV~: GB261.1
B_VDRV~: GB262.1
B_XHITA~: GB266.1
B_XHITB~: GB267.1
F_CHKB_0: GF173.1
F_CHKB_1: GF165.1
F_CHKB_2: GF157.1
F_CHKB_3: GF147.1
F_CHKB_4: GF37.1
F_CHKB_5: GF29.1
F_CHKB_6: GF21.1
F_CHKB_7: GF13.1
F_CHKB_8: GF5.1
F_TYP_0: GF294.1
F_TYP_1: GF292.1
F_TYP_2: GF290.1
F_TYP_3: GF288.1
F_TYP_4: GF278.1
F_TYP_5: GF276.1
F_TYP_6: GF274.1
F_TYP_7: GF272.1
F_TYP_8: GF262.1
F_TYP_9: GF260.1
F_TYP_10: GF258.1
F_TYP_11: GF256.1
F_TYP_12: GF246.1
F_TYP_13: GF244.1
F_TYP_14: GF242.1
F_TYP_15: GF240.1
F_TYP_16: GF230.1
F_TYP_17: GF228.1
F_TYP_18: GF226.1
F_TYP_19: GF224.1
F_TYP_20: GF214.1
F_TYP_21: GF212.1
F_TYP_22: GF210.1
F_TYP_23: GF208.1
F_TYP_24: GF198.1
F_TYP_25: GF196.1
F_TYP_26: GF194.1
F_TYP_27: GF192.1
F_TYP_28: GF182.1
F_TYP_29: GF180.1
F_TYP_30: GF178.1
F_TYP_31: GF176.1
F_TYP_32: GF130.1
F_TYP_33: GF128.1
F_TYP_34: GF126.1
F_TYP_35: GF124.1
F_TYP_36: GF114.1
F_TYP_37: GF112.1
F_TYP_38: GF110.1
F_TYP_39: GF108.1
F_TYP_40: GF98.1
F_TYP_41: GF96.1
F_TYP_42: GF94.1
F_TYP_43: GF92.1
F_TYP_44: GF82.1
F_TYP_45: GF80.1
F_TYP_46: GF78.1
F_TYP_47: GF76.1
F_TYP_48: GF66.1
F_TYP_49: GF64.1
F_TYP_50: GF62.1
F_TYP_51: GF60.1
F_TYP_52: GF50.1
F_TYP_53: GF48.1
F_TYP_54: GF46.1
F_TYP_55: GF44.1
F_TYP_56: GF34.1
F_TYP_57: GF32.1
F_TYP_58: GF30.1
F_TYP_59: GF28.1
F_TYP_60: GF18.1
F_TYP_61: GF16.1
F_TYP_62: GF14.1
F_TYP_63: GF12.1
F_VAL_0: GF286.1
F_VAL_1: GF284.1
F_VAL_2: GF282.1
F_VAL_3: GF280.1
F_VAL_4: GF270.1
F_VAL_5: GF268.1
F_VAL_6: GF266.1
F_VAL_7: GF264.1
F_VAL_8: GF254.1
F_VAL_9: GF252.1
F_VAL_10: GF250.1
F_VAL_11: GF248.1
F_VAL_12: GF238.1
F_VAL_13: GF236.1
F_VAL_14: GF234.1
F_VAL_15: GF232.1
F_VAL_16: GF222.1
F_VAL_17: GF220.1
F_VAL_18: GF218.1
F_VAL_19: GF216.1
F_VAL_20: GF206.1
F_VAL_21: GF204.1
F_VAL_22: GF202.1
F_VAL_23: GF200.1
F_VAL_24: GF190.1
F_VAL_25: GF188.1
F_VAL_26: GF186.1
F_VAL_27: GF184.1
F_VAL_28: GF174.1
F_VAL_29: GF172.1
F_VAL_30: GF170.1
F_VAL_31: GF168.1
F_VAL_32: GF122.1
F_VAL_33: GF120.1
F_VAL_34: GF118.1
F_VAL_35: GF116.1
F_VAL_36: GF106.1
F_VAL_37: GF104.1
F_VAL_38: GF102.1
F_VAL_39: GF100.1
F_VAL_40: GF90.1
F_VAL_41: GF88.1
F_VAL_42: GF86.1
F_VAL_43: GF84.1
F_VAL_44: GF74.1
F_VAL_45: GF72.1
F_VAL_46: GF70.1
F_VAL_47: GF68.1
F_VAL_48: GF58.1
F_VAL_49: GF56.1
F_VAL_50: GF54.1
F_VAL_51: GF52.1
F_VAL_52: GF42.1
F_VAL_53: GF40.1
F_VAL_54: GF38.1
F_VAL_55: GF36.1
F_VAL_56: GF26.1
F_VAL_57: GF24.1
F_VAL_58: GF22.1
F_VAL_59: GF20.1
F_VAL_60: GF10.1
F_VAL_61: GF8.1
F_VAL_62: GF6.1
F_VAL_63: GF4.1
F_VAL_P0: GF158.1
F_VAL_P1: GF156.1
F_VAL_P2: GF154.1
F_VAL_P3: GF152.1
F_VAL_P4: GF138.1
F_VAL_P5: GF136.1
F_VAL_P6: GF134.1
F_VAL_P7: GF132.1
PU: U301.1 (D0), U301.2 (D1)
