Datamuseum-DK/R1000.HwDoc/Schematics/MEM32/pg_03.kicad_sch

## KiCad design Schematics/MEM32/pg_03.kicad_sch (2023-01-10)

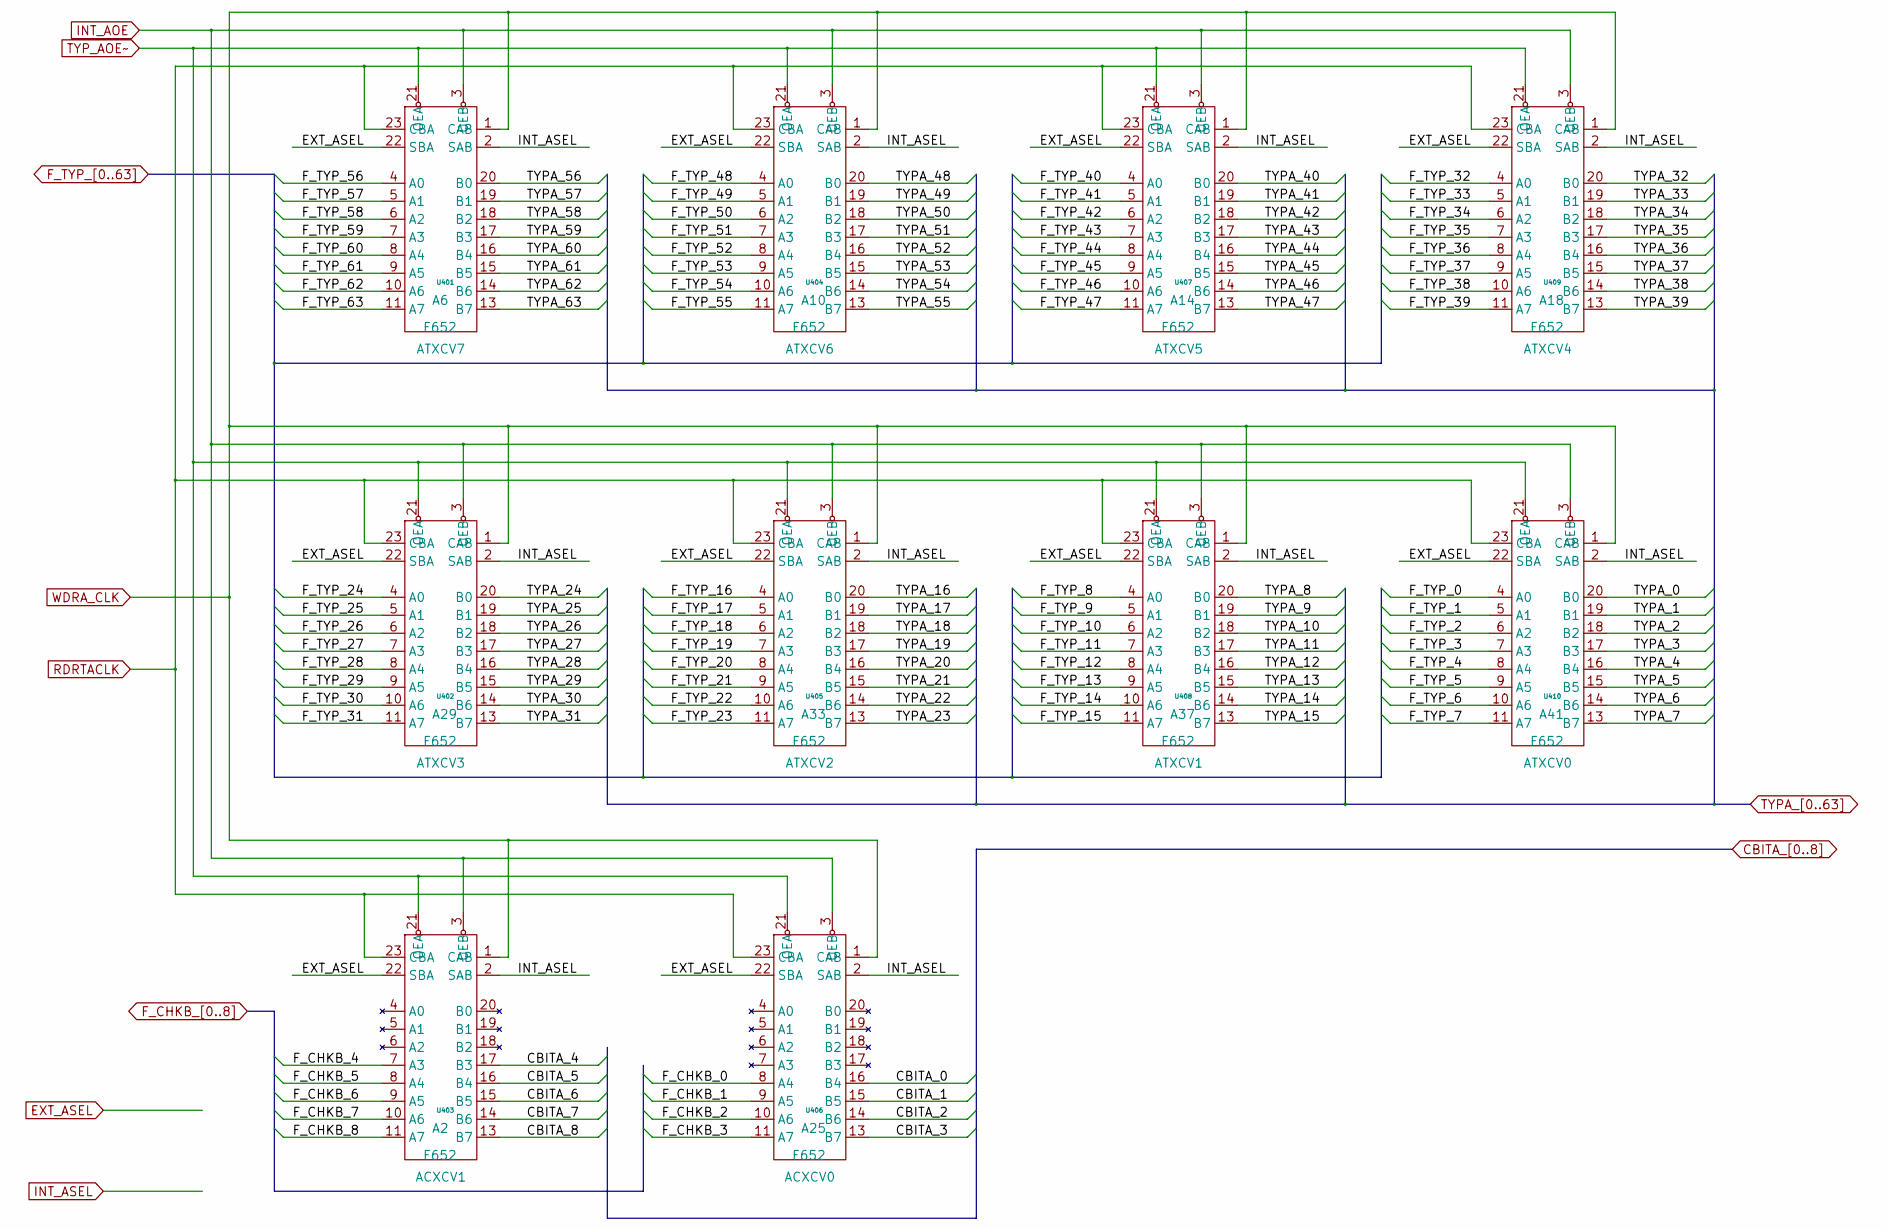
[picture p417: schematic pg_03.kicad_sch]

Parts:
U401, U402, U403, U404, U405, U406, U407, U408, U409, U410: F652

Connections:
CBITA_0: U406.16 (B4)
CBITA_1: U406.15 (B5)
CBITA_2: U406.14 (B6)
CBITA_3: U406.13 (B7)
CBITA_4: U403.17 (B3)
CBITA_5: U403.16 (B4)
CBITA_6: U403.15 (B5)
CBITA_7: U403.14 (B6)
CBITA_8: U403.13 (B7)
EXT_ASEL: U401.22 (SBA), U402.22 (SBA), U403.22 (SBA), U404.22 (SBA), U405.22 (SBA), U406.22 (SBA), U407.22 (SBA), U408.22 (SBA), U409.22 (SBA), U410.22 (SBA)
F_CHKB_0: U406.8 (A4)
F_CHKB_1: U406.9 (A5)
F_CHKB_2: U406.10 (A6)
F_CHKB_3: U406.11 (A7)
F_CHKB_4: U403.7 (A3)
F_CHKB_5: U403.8 (A4)
F_CHKB_6: U403.9 (A5)
F_CHKB_7: U403.10 (A6)
F_CHKB_8: U403.11 (A7)
F_TYP_0: U410.4 (A0)
F_TYP_1: U410.5 (A1)
F_TYP_2: U410.6 (A2)
F_TYP_3: U410.7 (A3)
F_TYP_4: U410.8 (A4)
F_TYP_5: U410.9 (A5)
F_TYP_6: U410.10 (A6)
F_TYP_7: U410.11 (A7)
F_TYP_8: U408.4 (A0)
F_TYP_9: U408.5 (A1)
F_TYP_10: U408.6 (A2)
F_TYP_11: U408.7 (A3)
F_TYP_12: U408.8 (A4)
F_TYP_13: U408.9 (A5)
F_TYP_14: U408.10 (A6)
F_TYP_15: U408.11 (A7)
F_TYP_16: U405.4 (A0)
F_TYP_17: U405.5 (A1)
F_TYP_18: U405.6 (A2)
F_TYP_19: U405.7 (A3)
F_TYP_20: U405.8 (A4)
F_TYP_21: U405.9 (A5)
F_TYP_22: U405.10 (A6)
F_TYP_23: U405.11 (A7)
F_TYP_24: U402.4 (A0)
F_TYP_25: U402.5 (A1)
F_TYP_26: U402.6 (A2)
F_TYP_27: U402.7 (A3)
F_TYP_28: U402.8 (A4)
F_TYP_29: U402.9 (A5)
F_TYP_30: U402.10 (A6)
F_TYP_31: U402.11 (A7)
F_TYP_32: U409.4 (A0)
F_TYP_33: U409.5 (A1)
F_TYP_34: U409.6 (A2)
F_TYP_35: U409.7 (A3)
F_TYP_36: U409.8 (A4)
F_TYP_37: U409.9 (A5)
F_TYP_38: U409.10 (A6)
F_TYP_39: U409.11 (A7)
F_TYP_40: U407.4 (A0)
F_TYP_41: U407.5 (A1)
F_TYP_42: U407.6 (A2)
F_TYP_43: U407.7 (A3)
F_TYP_44: U407.8 (A4)
F_TYP_45: U407.9 (A5)
F_TYP_46: U407.10 (A6)
F_TYP_47: U407.11 (A7)
F_TYP_48: U404.4 (A0)
F_TYP_49: U404.5 (A1)
F_TYP_50: U404.6 (A2)
F_TYP_51: U404.7 (A3)
F_TYP_52: U404.8 (A4)
F_TYP_53: U404.9 (A5)
F_TYP_54: U404.10 (A6)
F_TYP_55: U404.11 (A7)
F_TYP_56: U401.4 (A0)
F_TYP_57: U401.5 (A1)
F_TYP_58: U401.6 (A2)
F_TYP_59: U401.7 (A3)
F_TYP_60: U401.8 (A4)
F_TYP_61: U401.9 (A5)
F_TYP_62: U401.10 (A6)
F_TYP_63: U401.11 (A7)
INT_AOE: U401.3 (OEB), U402.3 (OEB), U403.3 (OEB), U404.3 (OEB), U405.3 (OEB), U406.3 (OEB), U407.3 (OEB), U408.3 (OEB), U409.3 (OEB), U410.3 (OEB)
INT_ASEL: U401.2 (SAB), U402.2 (SAB), U403.2 (SAB), U404.2 (SAB), U405.2 (SAB), U406.2 (SAB), U407.2 (SAB), U408.2 (SAB), U409.2 (SAB), U410.2 (SAB)
RDRTACLK: U401.23 (CBA), U402.23 (CBA), U403.23 (CBA), U404.23 (CBA), U405.23 (CBA), U406.23 (CBA), U407.23 (CBA), U408.23 (CBA), U409.23 (CBA), U410.23 (CBA)
TYPA_0: U410.20 (B0)
TYPA_1: U410.19 (B1)
TYPA_2: U410.18 (B2)
TYPA_3: U410.17 (B3)
TYPA_4: U410.16 (B4)
TYPA_5: U410.15 (B5)
TYPA_6: U410.14 (B6)
TYPA_7: U410.13 (B7)
TYPA_8: U408.20 (B0)
TYPA_9: U408.19 (B1)
TYPA_10: U408.18 (B2)
TYPA_11: U408.17 (B3)
TYPA_12: U408.16 (B4)
TYPA_13: U408.15 (B5)
TYPA_14: U408.14 (B6)
TYPA_15: U408.13 (B7)
TYPA_16: U405.20 (B0)
TYPA_17: U405.19 (B1)
TYPA_18: U405.18 (B2)
TYPA_19: U405.17 (B3)
TYPA_20: U405.16 (B4)
TYPA_21: U405.15 (B5)
TYPA_22: U405.14 (B6)
TYPA_23: U405.13 (B7)
TYPA_24: U402.20 (B0)
TYPA_25: U402.19 (B1)
TYPA_26: U402.18 (B2)
TYPA_27: U402.17 (B3)
TYPA_28: U402.16 (B4)
TYPA_29: U402.15 (B5)
TYPA_30: U402.14 (B6)
TYPA_31: U402.13 (B7)
TYPA_32: U409.20 (B0)
TYPA_33: U409.19 (B1)
TYPA_34: U409.18 (B2)
TYPA_35: U409.17 (B3)
TYPA_36: U409.16 (B4)
TYPA_37: U409.15 (B5)
TYPA_38: U409.14 (B6)
TYPA_39: U409.13 (B7)
TYPA_40: U407.20 (B0)
TYPA_41: U407.19 (B1)
TYPA_42: U407.18 (B2)
TYPA_43: U407.17 (B3)
TYPA_44: U407.16 (B4)
TYPA_45: U407.15 (B5)
TYPA_46: U407.14 (B6)
TYPA_47: U407.13 (B7)
TYPA_48: U404.20 (B0)
TYPA_49: U404.19 (B1)
TYPA_50: U404.18 (B2)
TYPA_51: U404.17 (B3)
TYPA_52: U404.16 (B4)
TYPA_53: U404.15 (B5)
TYPA_54: U404.14 (B6)
TYPA_55: U404.13 (B7)
TYPA_56: U401.20 (B0)
TYPA_57: U401.19 (B1)
TYPA_58: U401.18 (B2)
TYPA_59: U401.17 (B3)
TYPA_60: U401.16 (B4)
TYPA_61: U401.15 (B5)
TYPA_62: U401.14 (B6)
TYPA_63: U401.13 (B7)
TYP_AOE~: U401.21 (OEA), U402.21 (OEA), U403.21 (OEA), U404.21 (OEA), U405.21 (OEA), U406.21 (OEA), U407.21 (OEA), U408.21 (OEA), U409.21 (OEA), U410.21 (OEA)
WDRA_CLK: U401.1 (CAB), U402.1 (CAB), U403.1 (CAB), U404.1 (CAB), U405.1 (CAB), U406.1 (CAB), U407.1 (CAB), U408.1 (CAB), U409.1 (CAB), U410.1 (CAB)
