Datamuseum-DK/R1000.HwDoc/Schematics/MEM32/pg_04.kicad_sch

## KiCad design Schematics/MEM32/pg_04.kicad_sch (2023-01-10)

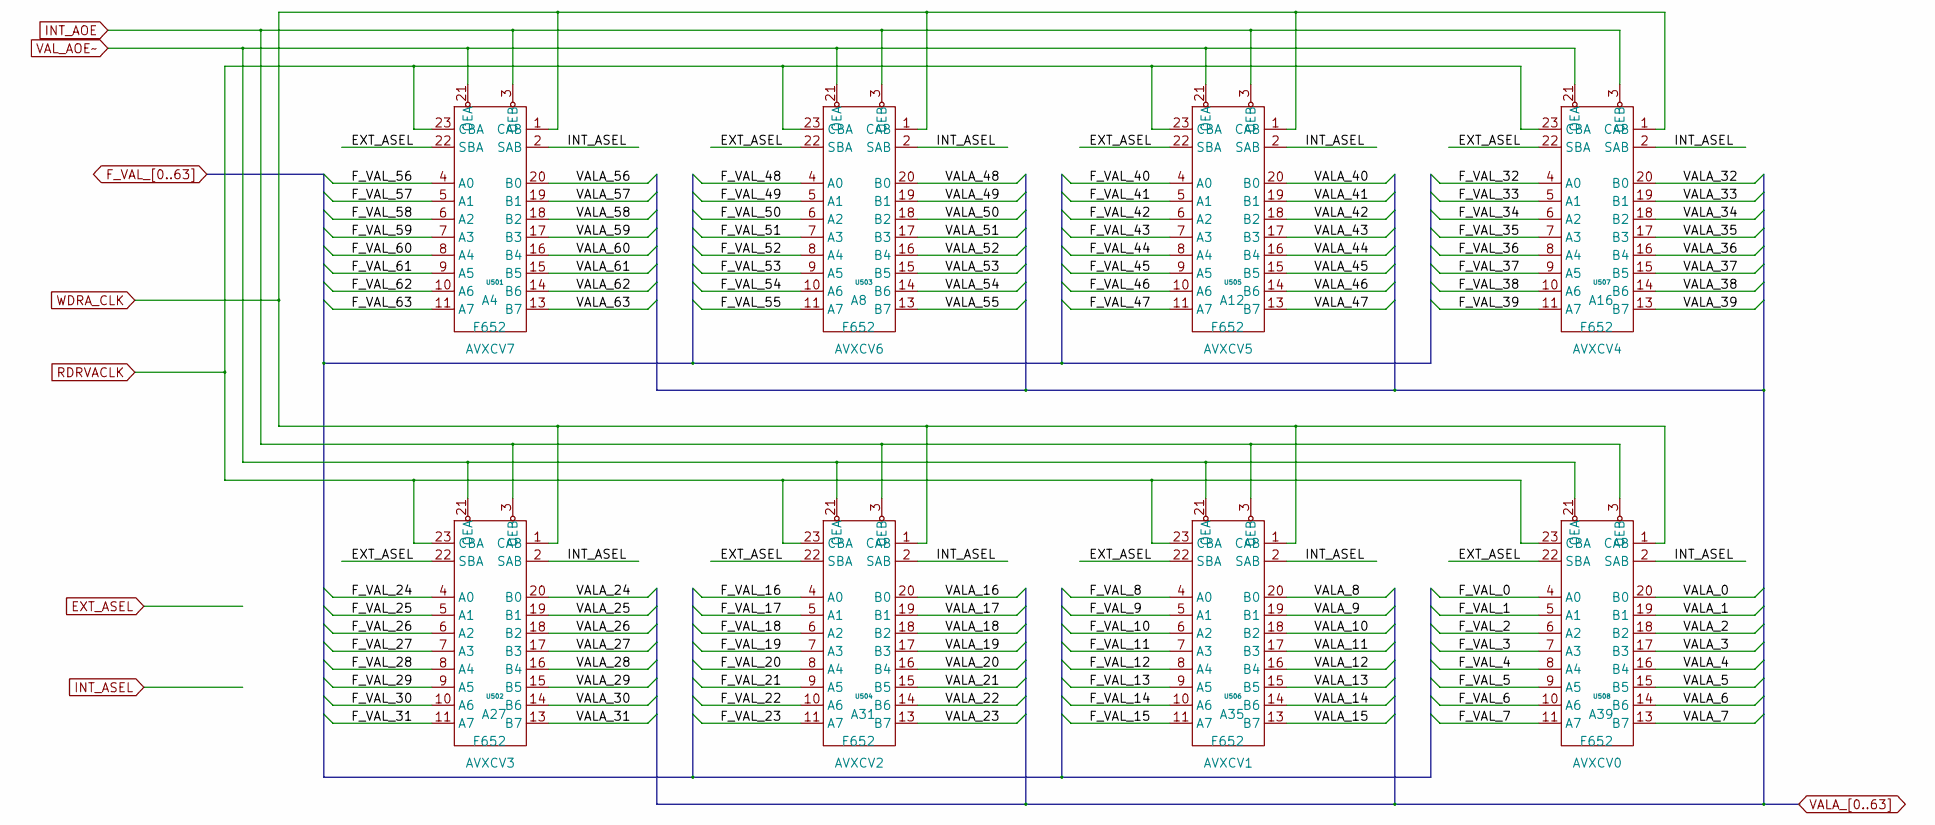
[picture p418: schematic pg_04.kicad_sch]

Parts:
U501, U502, U503, U504, U505, U506, U507, U508: F652

Connections:
EXT_ASEL: U501.22 (SBA), U502.22 (SBA), U503.22 (SBA), U504.22 (SBA), U505.22 (SBA), U506.22 (SBA), U507.22 (SBA), U508.22 (SBA)
F_VAL_0: U508.4 (A0)
F_VAL_1: U508.5 (A1)
F_VAL_2: U508.6 (A2)
F_VAL_3: U508.7 (A3)
F_VAL_4: U508.8 (A4)
F_VAL_5: U508.9 (A5)
F_VAL_6: U508.10 (A6)
F_VAL_7: U508.11 (A7)
F_VAL_8: U506.4 (A0)
F_VAL_9: U506.5 (A1)
F_VAL_10: U506.6 (A2)
F_VAL_11: U506.7 (A3)
F_VAL_12: U506.8 (A4)
F_VAL_13: U506.9 (A5)
F_VAL_14: U506.10 (A6)
F_VAL_15: U506.11 (A7)
F_VAL_16: U504.4 (A0)
F_VAL_17: U504.5 (A1)
F_VAL_18: U504.6 (A2)
F_VAL_19: U504.7 (A3)
F_VAL_20: U504.8 (A4)
F_VAL_21: U504.9 (A5)
F_VAL_22: U504.10 (A6)
F_VAL_23: U504.11 (A7)
F_VAL_24: U502.4 (A0)
F_VAL_25: U502.5 (A1)
F_VAL_26: U502.6 (A2)
F_VAL_27: U502.7 (A3)
F_VAL_28: U502.8 (A4)
F_VAL_29: U502.9 (A5)
F_VAL_30: U502.10 (A6)
F_VAL_31: U502.11 (A7)
F_VAL_32: U507.4 (A0)
F_VAL_33: U507.5 (A1)
F_VAL_34: U507.6 (A2)
F_VAL_35: U507.7 (A3)
F_VAL_36: U507.8 (A4)
F_VAL_37: U507.9 (A5)
F_VAL_38: U507.10 (A6)
F_VAL_39: U507.11 (A7)
F_VAL_40: U505.4 (A0)
F_VAL_41: U505.5 (A1)
F_VAL_42: U505.6 (A2)
F_VAL_43: U505.7 (A3)
F_VAL_44: U505.8 (A4)
F_VAL_45: U505.9 (A5)
F_VAL_46: U505.10 (A6)
F_VAL_47: U505.11 (A7)
F_VAL_48: U503.4 (A0)
F_VAL_49: U503.5 (A1)
F_VAL_50: U503.6 (A2)
F_VAL_51: U503.7 (A3)
F_VAL_52: U503.8 (A4)
F_VAL_53: U503.9 (A5)
F_VAL_54: U503.10 (A6)
F_VAL_55: U503.11 (A7)
F_VAL_56: U501.4 (A0)
F_VAL_57: U501.5 (A1)
F_VAL_58: U501.6 (A2)
F_VAL_59: U501.7 (A3)
F_VAL_60: U501.8 (A4)
F_VAL_61: U501.9 (A5)
F_VAL_62: U501.10 (A6)
F_VAL_63: U501.11 (A7)
INT_AOE: U501.3 (OEB), U502.3 (OEB), U503.3 (OEB), U504.3 (OEB), U505.3 (OEB), U506.3 (OEB), U507.3 (OEB), U508.3 (OEB)
INT_ASEL: U501.2 (SAB), U502.2 (SAB), U503.2 (SAB), U504.2 (SAB), U505.2 (SAB), U506.2 (SAB), U507.2 (SAB), U508.2 (SAB)
RDRVACLK: U501.23 (CBA), U502.23 (CBA), U503.23 (CBA), U504.23 (CBA), U505.23 (CBA), U506.23 (CBA), U507.23 (CBA), U508.23 (CBA)
VALA_0: U508.20 (B0)
VALA_1: U508.19 (B1)
VALA_2: U508.18 (B2)
VALA_3: U508.17 (B3)
VALA_4: U508.16 (B4)
VALA_5: U508.15 (B5)
VALA_6: U508.14 (B6)
VALA_7: U508.13 (B7)
VALA_8: U506.20 (B0)
VALA_9: U506.19 (B1)
VALA_10: U506.18 (B2)
VALA_11: U506.17 (B3)
VALA_12: U506.16 (B4)
VALA_13: U506.15 (B5)
VALA_14: U506.14 (B6)
VALA_15: U506.13 (B7)
VALA_16: U504.20 (B0)
VALA_17: U504.19 (B1)
VALA_18: U504.18 (B2)
VALA_19: U504.17 (B3)
VALA_20: U504.16 (B4)
VALA_21: U504.15 (B5)
VALA_22: U504.14 (B6)
VALA_23: U504.13 (B7)
VALA_24: U502.20 (B0)
VALA_25: U502.19 (B1)
VALA_26: U502.18 (B2)
VALA_27: U502.17 (B3)
VALA_28: U502.16 (B4)
VALA_29: U502.15 (B5)
VALA_30: U502.14 (B6)
VALA_31: U502.13 (B7)
VALA_32: U507.20 (B0)
VALA_33: U507.19 (B1)
VALA_34: U507.18 (B2)
VALA_35: U507.17 (B3)
VALA_36: U507.16 (B4)
VALA_37: U507.15 (B5)
VALA_38: U507.14 (B6)
VALA_39: U507.13 (B7)
VALA_40: U505.20 (B0)
VALA_41: U505.19 (B1)
VALA_42: U505.18 (B2)
VALA_43: U505.17 (B3)
VALA_44: U505.16 (B4)
VALA_45: U505.15 (B5)
VALA_46: U505.14 (B6)
VALA_47: U505.13 (B7)
VALA_48: U503.20 (B0)
VALA_49: U503.19 (B1)
VALA_50: U503.18 (B2)
VALA_51: U503.17 (B3)
VALA_52: U503.16 (B4)
VALA_53: U503.15 (B5)
VALA_54: U503.14 (B6)
VALA_55: U503.13 (B7)
VALA_56: U501.20 (B0)
VALA_57: U501.19 (B1)
VALA_58: U501.18 (B2)
VALA_59: U501.17 (B3)
VALA_60: U501.16 (B4)
VALA_61: U501.15 (B5)
VALA_62: U501.14 (B6)
VALA_63: U501.13 (B7)
VAL_AOE~: U501.21 (OEA), U502.21 (OEA), U503.21 (OEA), U504.21 (OEA), U505.21 (OEA), U506.21 (OEA), U507.21 (OEA), U508.21 (OEA)
WDRA_CLK: U501.1 (CAB), U502.1 (CAB), U503.1 (CAB), U504.1 (CAB), U505.1 (CAB), U506.1 (CAB), U507.1 (CAB), U508.1 (CAB)
