Datamuseum-DK/R1000.HwDoc/Schematics/MEM32/pg_05.kicad_sch

## KiCad design Schematics/MEM32/pg_05.kicad_sch (2023-01-10)

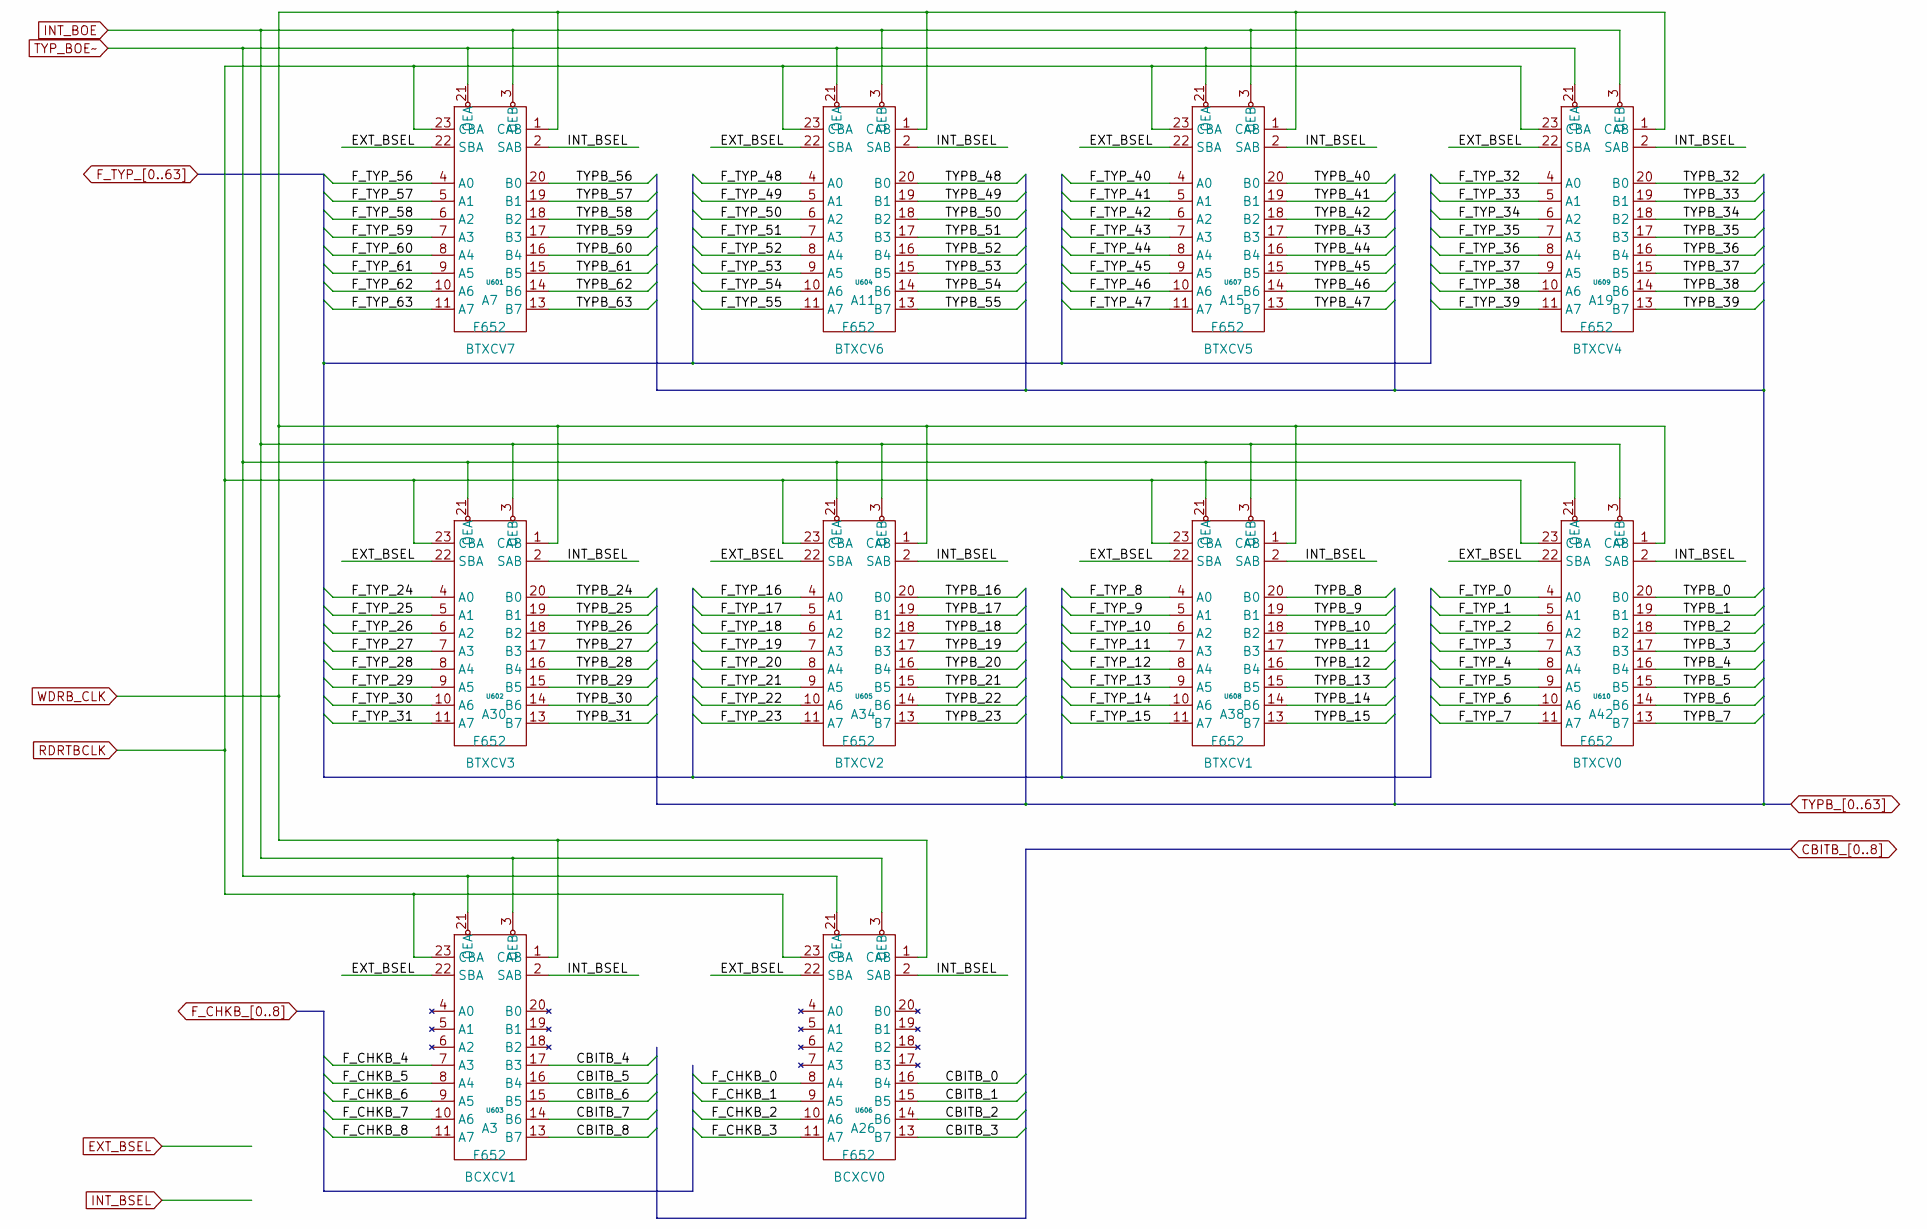
[picture p419: schematic pg_05.kicad_sch]

Parts:
U601, U602, U603, U604, U605, U606, U607, U608, U609, U610: F652

Connections:
CBITB_0: U606.16 (B4)
CBITB_1: U606.15 (B5)
CBITB_2: U606.14 (B6)
CBITB_3: U606.13 (B7)
CBITB_4: U603.17 (B3)
CBITB_5: U603.16 (B4)
CBITB_6: U603.15 (B5)
CBITB_7: U603.14 (B6)
CBITB_8: U603.13 (B7)
EXT_BSEL: U601.22 (SBA), U602.22 (SBA), U603.22 (SBA), U604.22 (SBA), U605.22 (SBA), U606.22 (SBA), U607.22 (SBA), U608.22 (SBA), U609.22 (SBA), U610.22 (SBA)
F_CHKB_0: U606.8 (A4)
F_CHKB_1: U606.9 (A5)
F_CHKB_2: U606.10 (A6)
F_CHKB_3: U606.11 (A7)
F_CHKB_4: U603.7 (A3)
F_CHKB_5: U603.8 (A4)
F_CHKB_6: U603.9 (A5)
F_CHKB_7: U603.10 (A6)
F_CHKB_8: U603.11 (A7)
F_TYP_0: U610.4 (A0)
F_TYP_1: U610.5 (A1)
F_TYP_2: U610.6 (A2)
F_TYP_3: U610.7 (A3)
F_TYP_4: U610.8 (A4)
F_TYP_5: U610.9 (A5)
F_TYP_6: U610.10 (A6)
F_TYP_7: U610.11 (A7)
F_TYP_8: U608.4 (A0)
F_TYP_9: U608.5 (A1)
F_TYP_10: U608.6 (A2)
F_TYP_11: U608.7 (A3)
F_TYP_12: U608.8 (A4)
F_TYP_13: U608.9 (A5)
F_TYP_14: U608.10 (A6)
F_TYP_15: U608.11 (A7)
F_TYP_16: U605.4 (A0)
F_TYP_17: U605.5 (A1)
F_TYP_18: U605.6 (A2)
F_TYP_19: U605.7 (A3)
F_TYP_20: U605.8 (A4)
F_TYP_21: U605.9 (A5)
F_TYP_22: U605.10 (A6)
F_TYP_23: U605.11 (A7)
F_TYP_24: U602.4 (A0)
F_TYP_25: U602.5 (A1)
F_TYP_26: U602.6 (A2)
F_TYP_27: U602.7 (A3)
F_TYP_28: U602.8 (A4)
F_TYP_29: U602.9 (A5)
F_TYP_30: U602.10 (A6)
F_TYP_31: U602.11 (A7)
F_TYP_32: U609.4 (A0)
F_TYP_33: U609.5 (A1)
F_TYP_34: U609.6 (A2)
F_TYP_35: U609.7 (A3)
F_TYP_36: U609.8 (A4)
F_TYP_37: U609.9 (A5)
F_TYP_38: U609.10 (A6)
F_TYP_39: U609.11 (A7)
F_TYP_40: U607.4 (A0)
F_TYP_41: U607.5 (A1)
F_TYP_42: U607.6 (A2)
F_TYP_43: U607.7 (A3)
F_TYP_44: U607.8 (A4)
F_TYP_45: U607.9 (A5)
F_TYP_46: U607.10 (A6)
F_TYP_47: U607.11 (A7)
F_TYP_48: U604.4 (A0)
F_TYP_49: U604.5 (A1)
F_TYP_50: U604.6 (A2)
F_TYP_51: U604.7 (A3)
F_TYP_52: U604.8 (A4)
F_TYP_53: U604.9 (A5)
F_TYP_54: U604.10 (A6)
F_TYP_55: U604.11 (A7)
F_TYP_56: U601.4 (A0)
F_TYP_57: U601.5 (A1)
F_TYP_58: U601.6 (A2)
F_TYP_59: U601.7 (A3)
F_TYP_60: U601.8 (A4)
F_TYP_61: U601.9 (A5)
F_TYP_62: U601.10 (A6)
F_TYP_63: U601.11 (A7)
INT_BOE: U601.3 (OEB), U602.3 (OEB), U603.3 (OEB), U604.3 (OEB), U605.3 (OEB), U606.3 (OEB), U607.3 (OEB), U608.3 (OEB), U609.3 (OEB), U610.3 (OEB)
INT_BSEL: U601.2 (SAB), U602.2 (SAB), U603.2 (SAB), U604.2 (SAB), U605.2 (SAB), U606.2 (SAB), U607.2 (SAB), U608.2 (SAB), U609.2 (SAB), U610.2 (SAB)
RDRTBCLK: U601.23 (CBA), U602.23 (CBA), U603.23 (CBA), U604.23 (CBA), U605.23 (CBA), U606.23 (CBA), U607.23 (CBA), U608.23 (CBA), U609.23 (CBA), U610.23 (CBA)
TYPB_0: U610.20 (B0)
TYPB_1: U610.19 (B1)
TYPB_2: U610.18 (B2)
TYPB_3: U610.17 (B3)
TYPB_4: U610.16 (B4)
TYPB_5: U610.15 (B5)
TYPB_6: U610.14 (B6)
TYPB_7: U610.13 (B7)
TYPB_8: U608.20 (B0)
TYPB_9: U608.19 (B1)
TYPB_10: U608.18 (B2)
TYPB_11: U608.17 (B3)
TYPB_12: U608.16 (B4)
TYPB_13: U608.15 (B5)
TYPB_14: U608.14 (B6)
TYPB_15: U608.13 (B7)
TYPB_16: U605.20 (B0)
TYPB_17: U605.19 (B1)
TYPB_18: U605.18 (B2)
TYPB_19: U605.17 (B3)
TYPB_20: U605.16 (B4)
TYPB_21: U605.15 (B5)
TYPB_22: U605.14 (B6)
TYPB_23: U605.13 (B7)
TYPB_24: U602.20 (B0)
TYPB_25: U602.19 (B1)
TYPB_26: U602.18 (B2)
TYPB_27: U602.17 (B3)
TYPB_28: U602.16 (B4)
TYPB_29: U602.15 (B5)
TYPB_30: U602.14 (B6)
TYPB_31: U602.13 (B7)
TYPB_32: U609.20 (B0)
TYPB_33: U609.19 (B1)
TYPB_34: U609.18 (B2)
TYPB_35: U609.17 (B3)
TYPB_36: U609.16 (B4)
TYPB_37: U609.15 (B5)
TYPB_38: U609.14 (B6)
TYPB_39: U609.13 (B7)
TYPB_40: U607.20 (B0)
TYPB_41: U607.19 (B1)
TYPB_42: U607.18 (B2)
TYPB_43: U607.17 (B3)
TYPB_44: U607.16 (B4)
TYPB_45: U607.15 (B5)
TYPB_46: U607.14 (B6)
TYPB_47: U607.13 (B7)
TYPB_48: U604.20 (B0)
TYPB_49: U604.19 (B1)
TYPB_50: U604.18 (B2)
TYPB_51: U604.17 (B3)
TYPB_52: U604.16 (B4)
TYPB_53: U604.15 (B5)
TYPB_54: U604.14 (B6)
TYPB_55: U604.13 (B7)
TYPB_56: U601.20 (B0)
TYPB_57: U601.19 (B1)
TYPB_58: U601.18 (B2)
TYPB_59: U601.17 (B3)
TYPB_60: U601.16 (B4)
TYPB_61: U601.15 (B5)
TYPB_62: U601.14 (B6)
TYPB_63: U601.13 (B7)
TYP_BOE~: U601.21 (OEA), U602.21 (OEA), U603.21 (OEA), U604.21 (OEA), U605.21 (OEA), U606.21 (OEA), U607.21 (OEA), U608.21 (OEA), U609.21 (OEA), U610.21 (OEA)
WDRB_CLK: U601.1 (CAB), U602.1 (CAB), U603.1 (CAB), U604.1 (CAB), U605.1 (CAB), U606.1 (CAB), U607.1 (CAB), U608.1 (CAB), U609.1 (CAB), U610.1 (CAB)
