Datamuseum-DK/R1000.HwDoc/Schematics/MEM32/pg_06.kicad_sch

## KiCad design Schematics/MEM32/pg_06.kicad_sch (2023-01-10)

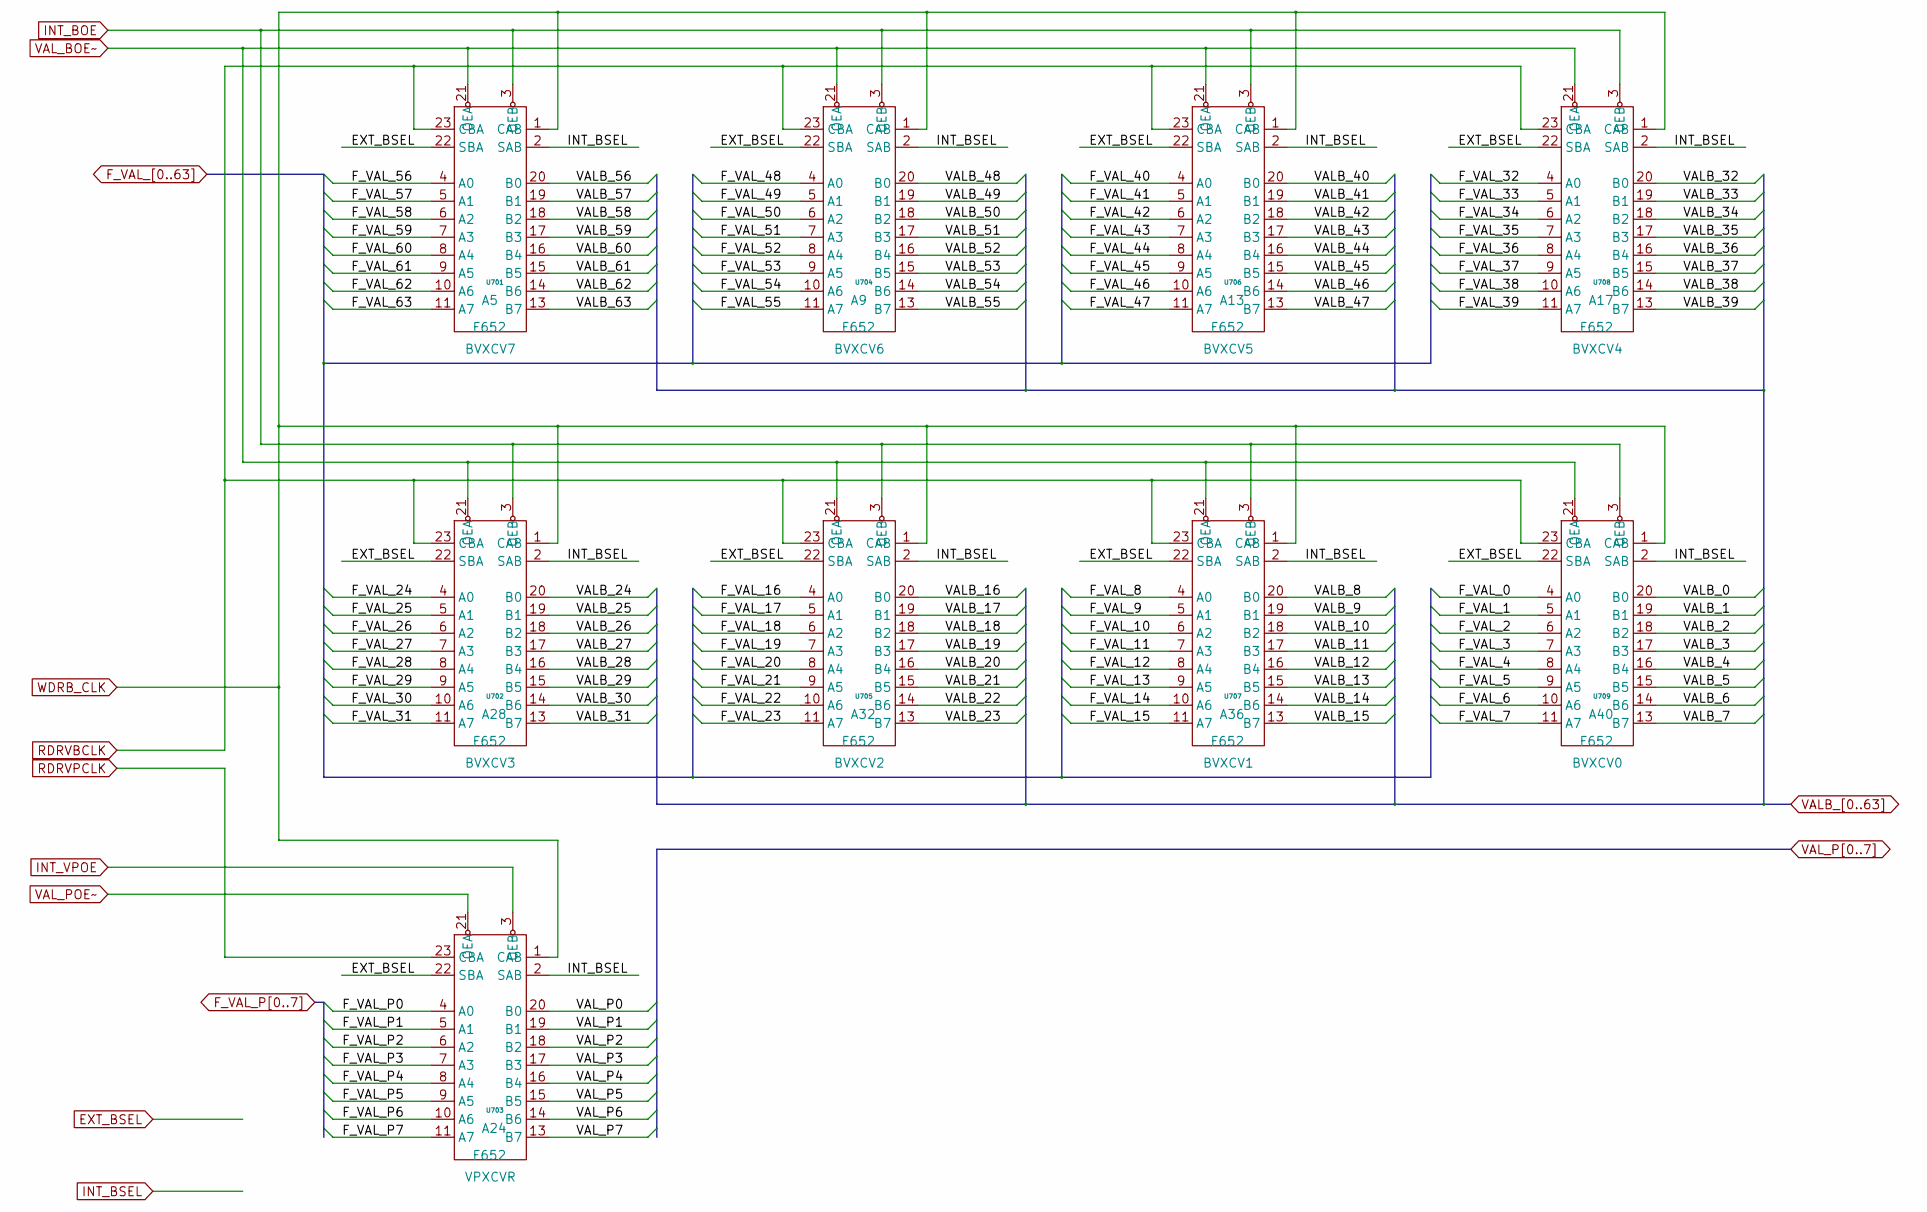
[picture p420: schematic pg_06.kicad_sch]

Parts:
U701, U702, U703, U704, U705, U706, U707, U708, U709: F652

Connections:
EXT_BSEL: U701.22 (SBA), U702.22 (SBA), U703.22 (SBA), U704.22 (SBA), U705.22 (SBA), U706.22 (SBA), U707.22 (SBA), U708.22 (SBA), U709.22 (SBA)
F_VAL_0: U709.4 (A0)
F_VAL_1: U709.5 (A1)
F_VAL_2: U709.6 (A2)
F_VAL_3: U709.7 (A3)
F_VAL_4: U709.8 (A4)
F_VAL_5: U709.9 (A5)
F_VAL_6: U709.10 (A6)
F_VAL_7: U709.11 (A7)
F_VAL_8: U707.4 (A0)
F_VAL_9: U707.5 (A1)
F_VAL_10: U707.6 (A2)
F_VAL_11: U707.7 (A3)
F_VAL_12: U707.8 (A4)
F_VAL_13: U707.9 (A5)
F_VAL_14: U707.10 (A6)
F_VAL_15: U707.11 (A7)
F_VAL_16: U705.4 (A0)
F_VAL_17: U705.5 (A1)
F_VAL_18: U705.6 (A2)
F_VAL_19: U705.7 (A3)
F_VAL_20: U705.8 (A4)
F_VAL_21: U705.9 (A5)
F_VAL_22: U705.10 (A6)
F_VAL_23: U705.11 (A7)
F_VAL_24: U702.4 (A0)
F_VAL_25: U702.5 (A1)
F_VAL_26: U702.6 (A2)
F_VAL_27: U702.7 (A3)
F_VAL_28: U702.8 (A4)
F_VAL_29: U702.9 (A5)
F_VAL_30: U702.10 (A6)
F_VAL_31: U702.11 (A7)
F_VAL_32: U708.4 (A0)
F_VAL_33: U708.5 (A1)
F_VAL_34: U708.6 (A2)
F_VAL_35: U708.7 (A3)
F_VAL_36: U708.8 (A4)
F_VAL_37: U708.9 (A5)
F_VAL_38: U708.10 (A6)
F_VAL_39: U708.11 (A7)
F_VAL_40: U706.4 (A0)
F_VAL_41: U706.5 (A1)
F_VAL_42: U706.6 (A2)
F_VAL_43: U706.7 (A3)
F_VAL_44: U706.8 (A4)
F_VAL_45: U706.9 (A5)
F_VAL_46: U706.10 (A6)
F_VAL_47: U706.11 (A7)
F_VAL_48: U704.4 (A0)
F_VAL_49: U704.5 (A1)
F_VAL_50: U704.6 (A2)
F_VAL_51: U704.7 (A3)
F_VAL_52: U704.8 (A4)
F_VAL_53: U704.9 (A5)
F_VAL_54: U704.10 (A6)
F_VAL_55: U704.11 (A7)
F_VAL_56: U701.4 (A0)
F_VAL_57: U701.5 (A1)
F_VAL_58: U701.6 (A2)
F_VAL_59: U701.7 (A3)
F_VAL_60: U701.8 (A4)
F_VAL_61: U701.9 (A5)
F_VAL_62: U701.10 (A6)
F_VAL_63: U701.11 (A7)
F_VAL_P0: U703.4 (A0)
F_VAL_P1: U703.5 (A1)
F_VAL_P2: U703.6 (A2)
F_VAL_P3: U703.7 (A3)
F_VAL_P4: U703.8 (A4)
F_VAL_P5: U703.9 (A5)
F_VAL_P6: U703.10 (A6)
F_VAL_P7: U703.11 (A7)
INT_BOE: U701.3 (OEB), U702.3 (OEB), U704.3 (OEB), U705.3 (OEB), U706.3 (OEB), U707.3 (OEB), U708.3 (OEB), U709.3 (OEB)
INT_BSEL: U701.2 (SAB), U702.2 (SAB), U703.2 (SAB), U704.2 (SAB), U705.2 (SAB), U706.2 (SAB), U707.2 (SAB), U708.2 (SAB), U709.2 (SAB)
INT_VPOE: U703.3 (OEB)
RDRVBCLK: U701.23 (CBA), U702.23 (CBA), U704.23 (CBA), U705.23 (CBA), U706.23 (CBA), U707.23 (CBA), U708.23 (CBA), U709.23 (CBA)
RDRVPCLK: U703.23 (CBA)
VALB_0: U709.20 (B0)
VALB_1: U709.19 (B1)
VALB_2: U709.18 (B2)
VALB_3: U709.17 (B3)
VALB_4: U709.16 (B4)
VALB_5: U709.15 (B5)
VALB_6: U709.14 (B6)
VALB_7: U709.13 (B7)
VALB_8: U707.20 (B0)
VALB_9: U707.19 (B1)
VALB_10: U707.18 (B2)
VALB_11: U707.17 (B3)
VALB_12: U707.16 (B4)
VALB_13: U707.15 (B5)
VALB_14: U707.14 (B6)
VALB_15: U707.13 (B7)
VALB_16: U705.20 (B0)
VALB_17: U705.19 (B1)
VALB_18: U705.18 (B2)
VALB_19: U705.17 (B3)
VALB_20: U705.16 (B4)
VALB_21: U705.15 (B5)
VALB_22: U705.14 (B6)
VALB_23: U705.13 (B7)
VALB_24: U702.20 (B0)
VALB_25: U702.19 (B1)
VALB_26: U702.18 (B2)
VALB_27: U702.17 (B3)
VALB_28: U702.16 (B4)
VALB_29: U702.15 (B5)
VALB_30: U702.14 (B6)
VALB_31: U702.13 (B7)
VALB_32: U708.20 (B0)
VALB_33: U708.19 (B1)
VALB_34: U708.18 (B2)
VALB_35: U708.17 (B3)
VALB_36: U708.16 (B4)
VALB_37: U708.15 (B5)
VALB_38: U708.14 (B6)
VALB_39: U708.13 (B7)
VALB_40: U706.20 (B0)
VALB_41: U706.19 (B1)
VALB_42: U706.18 (B2)
VALB_43: U706.17 (B3)
VALB_44: U706.16 (B4)
VALB_45: U706.15 (B5)
VALB_46: U706.14 (B6)
VALB_47: U706.13 (B7)
VALB_48: U704.20 (B0)
VALB_49: U704.19 (B1)
VALB_50: U704.18 (B2)
VALB_51: U704.17 (B3)
VALB_52: U704.16 (B4)
VALB_53: U704.15 (B5)
VALB_54: U704.14 (B6)
VALB_55: U704.13 (B7)
VALB_56: U701.20 (B0)
VALB_57: U701.19 (B1)
VALB_58: U701.18 (B2)
VALB_59: U701.17 (B3)
VALB_60: U701.16 (B4)
VALB_61: U701.15 (B5)
VALB_62: U701.14 (B6)
VALB_63: U701.13 (B7)
VAL_BOE~: U701.21 (OEA), U702.21 (OEA), U704.21 (OEA), U705.21 (OEA), U706.21 (OEA), U707.21 (OEA), U708.21 (OEA), U709.21 (OEA)
VAL_P0: U703.20 (B0)
VAL_P1: U703.19 (B1)
VAL_P2: U703.18 (B2)
VAL_P3: U703.17 (B3)
VAL_P4: U703.16 (B4)
VAL_P5: U703.15 (B5)
VAL_P6: U703.14 (B6)
VAL_P7: U703.13 (B7)
VAL_POE~: U703.21 (OEA)
WDRB_CLK: U701.1 (CAB), U702.1 (CAB), U703.1 (CAB), U704.1 (CAB), U705.1 (CAB), U706.1 (CAB), U707.1 (CAB), U708.1 (CAB), U709.1 (CAB)
