Datamuseum-DK/R1000.HwDoc/Schematics/MEM32/pg_07.kicad_sch

## KiCad design Schematics/MEM32/pg_07.kicad_sch (2023-01-10)

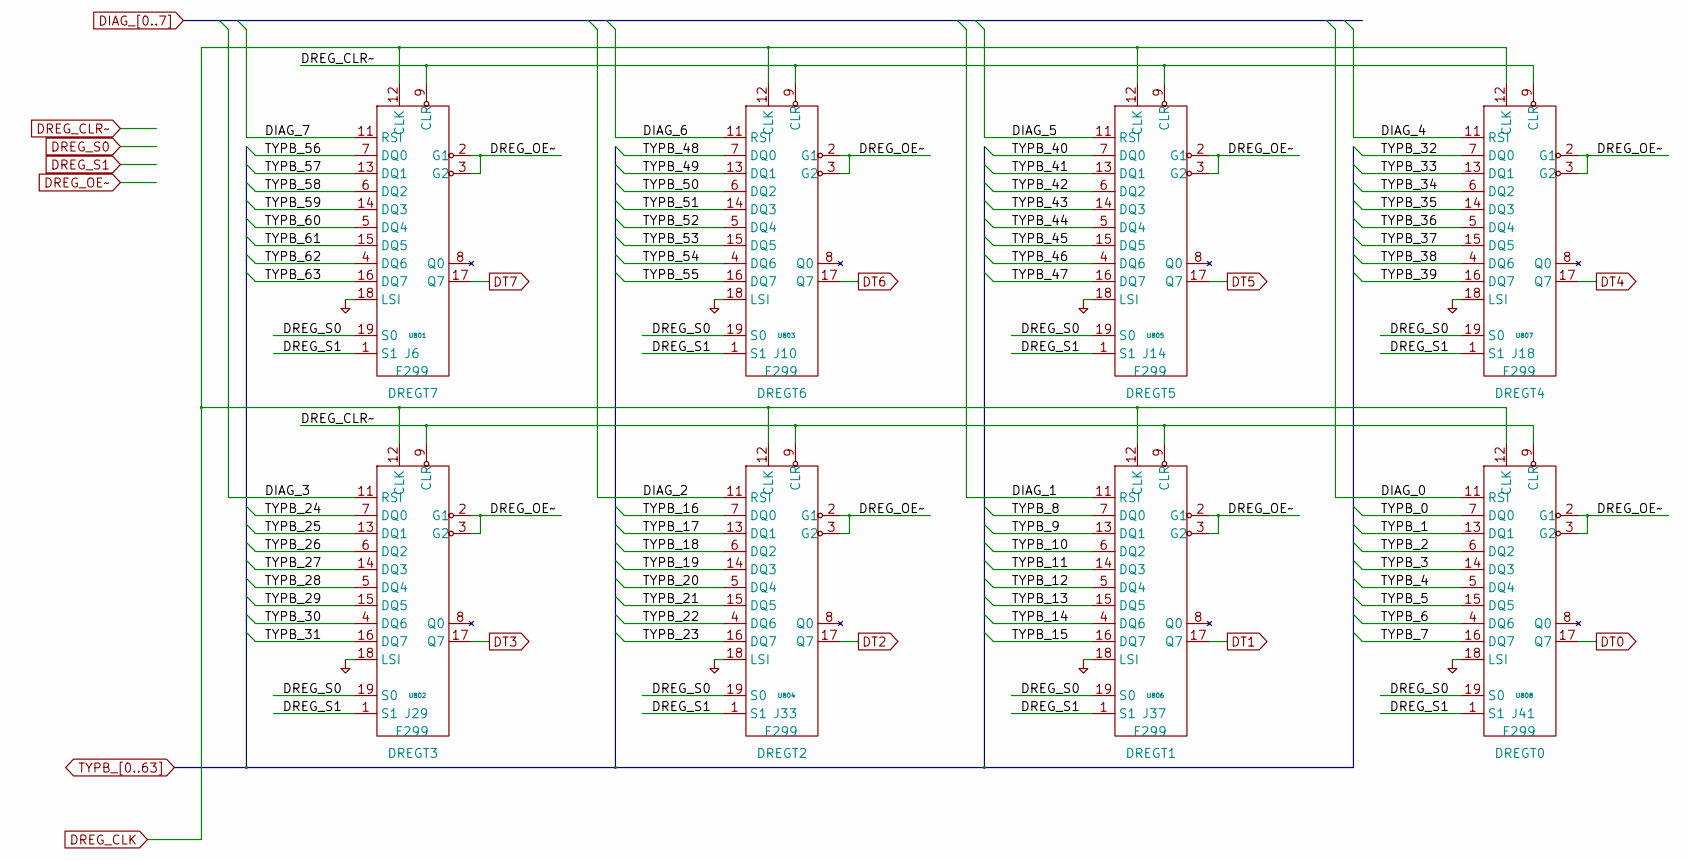
[picture p421: schematic pg_07.kicad_sch]

Parts:
U801, U802, U803, U804, U805, U806, U807, U808: F299

Connections:
DIAG_0: U808.11 (RSI)
DIAG_1: U806.11 (RSI)
DIAG_2: U804.11 (RSI)
DIAG_3: U802.11 (RSI)
DIAG_4: U807.11 (RSI)
DIAG_5: U805.11 (RSI)
DIAG_6: U803.11 (RSI)
DIAG_7: U801.11 (RSI)
DREG_CLK: U801.12 (CLK), U802.12 (CLK), U803.12 (CLK), U804.12 (CLK), U805.12 (CLK), U806.12 (CLK), U807.12 (CLK), U808.12 (CLK)
DREG_CLR~: U801.9 (CLR), U802.9 (CLR), U803.9 (CLR), U804.9 (CLR), U805.9 (CLR), U806.9 (CLR), U807.9 (CLR), U808.9 (CLR)
DREG_OE~: U801.2 (G1), U801.3 (G2), U802.2 (G1), U802.3 (G2), U803.2 (G1), U803.3 (G2), U804.2 (G1), U804.3 (G2), U805.2 (G1), U805.3 (G2), U806.2 (G1), U806.3 (G2), U807.2 (G1), U807.3 (G2), U808.2 (G1), U808.3 (G2)
DREG_S0: U801.19 (S0), U802.19 (S0), U803.19 (S0), U804.19 (S0), U805.19 (S0), U806.19 (S0), U807.19 (S0), U808.19 (S0)
DREG_S1: U801.1 (S1), U802.1 (S1), U803.1 (S1), U804.1 (S1), U805.1 (S1), U806.1 (S1), U807.1 (S1), U808.1 (S1)
DT0: U808.17 (Q7)
DT1: U806.17 (Q7)
DT2: U804.17 (Q7)
DT3: U802.17 (Q7)
DT4: U807.17 (Q7)
DT5: U805.17 (Q7)
DT6: U803.17 (Q7)
DT7: U801.17 (Q7)
PD: U801.18 (LSI), U802.18 (LSI), U803.18 (LSI), U804.18 (LSI), U805.18 (LSI), U806.18 (LSI), U807.18 (LSI), U808.18 (LSI)
TYPB_0: U808.7 (DQ0)
TYPB_1: U808.13 (DQ1)
TYPB_2: U808.6 (DQ2)
TYPB_3: U808.14 (DQ3)
TYPB_4: U808.5 (DQ4)
TYPB_5: U808.15 (DQ5)
TYPB_6: U808.4 (DQ6)
TYPB_7: U808.16 (DQ7)
TYPB_8: U806.7 (DQ0)
TYPB_9: U806.13 (DQ1)
TYPB_10: U806.6 (DQ2)
TYPB_11: U806.14 (DQ3)
TYPB_12: U806.5 (DQ4)
TYPB_13: U806.15 (DQ5)
TYPB_14: U806.4 (DQ6)
TYPB_15: U806.16 (DQ7)
TYPB_16: U804.7 (DQ0)
TYPB_17: U804.13 (DQ1)
TYPB_18: U804.6 (DQ2)
TYPB_19: U804.14 (DQ3)
TYPB_20: U804.5 (DQ4)
TYPB_21: U804.15 (DQ5)
TYPB_22: U804.4 (DQ6)
TYPB_23: U804.16 (DQ7)
TYPB_24: U802.7 (DQ0)
TYPB_25: U802.13 (DQ1)
TYPB_26: U802.6 (DQ2)
TYPB_27: U802.14 (DQ3)
TYPB_28: U802.5 (DQ4)
TYPB_29: U802.15 (DQ5)
TYPB_30: U802.4 (DQ6)
TYPB_31: U802.16 (DQ7)
TYPB_32: U807.7 (DQ0)
TYPB_33: U807.13 (DQ1)
TYPB_34: U807.6 (DQ2)
TYPB_35: U807.14 (DQ3)
TYPB_36: U807.5 (DQ4)
TYPB_37: U807.15 (DQ5)
TYPB_38: U807.4 (DQ6)
TYPB_39: U807.16 (DQ7)
TYPB_40: U805.7 (DQ0)
TYPB_41: U805.13 (DQ1)
TYPB_42: U805.6 (DQ2)
TYPB_43: U805.14 (DQ3)
TYPB_44: U805.5 (DQ4)
TYPB_45: U805.15 (DQ5)
TYPB_46: U805.4 (DQ6)
TYPB_47: U805.16 (DQ7)
TYPB_48: U803.7 (DQ0)
TYPB_49: U803.13 (DQ1)
TYPB_50: U803.6 (DQ2)
TYPB_51: U803.14 (DQ3)
TYPB_52: U803.5 (DQ4)
TYPB_53: U803.15 (DQ5)
TYPB_54: U803.4 (DQ6)
TYPB_55: U803.16 (DQ7)
TYPB_56: U801.7 (DQ0)
TYPB_57: U801.13 (DQ1)
TYPB_58: U801.6 (DQ2)
TYPB_59: U801.14 (DQ3)
TYPB_60: U801.5 (DQ4)
TYPB_61: U801.15 (DQ5)
TYPB_62: U801.4 (DQ6)
TYPB_63: U801.16 (DQ7)
