Datamuseum-DK/R1000.HwDoc/Schematics/MEM32/pg_08.kicad_sch

## KiCad design Schematics/MEM32/pg_08.kicad_sch (2023-01-10)

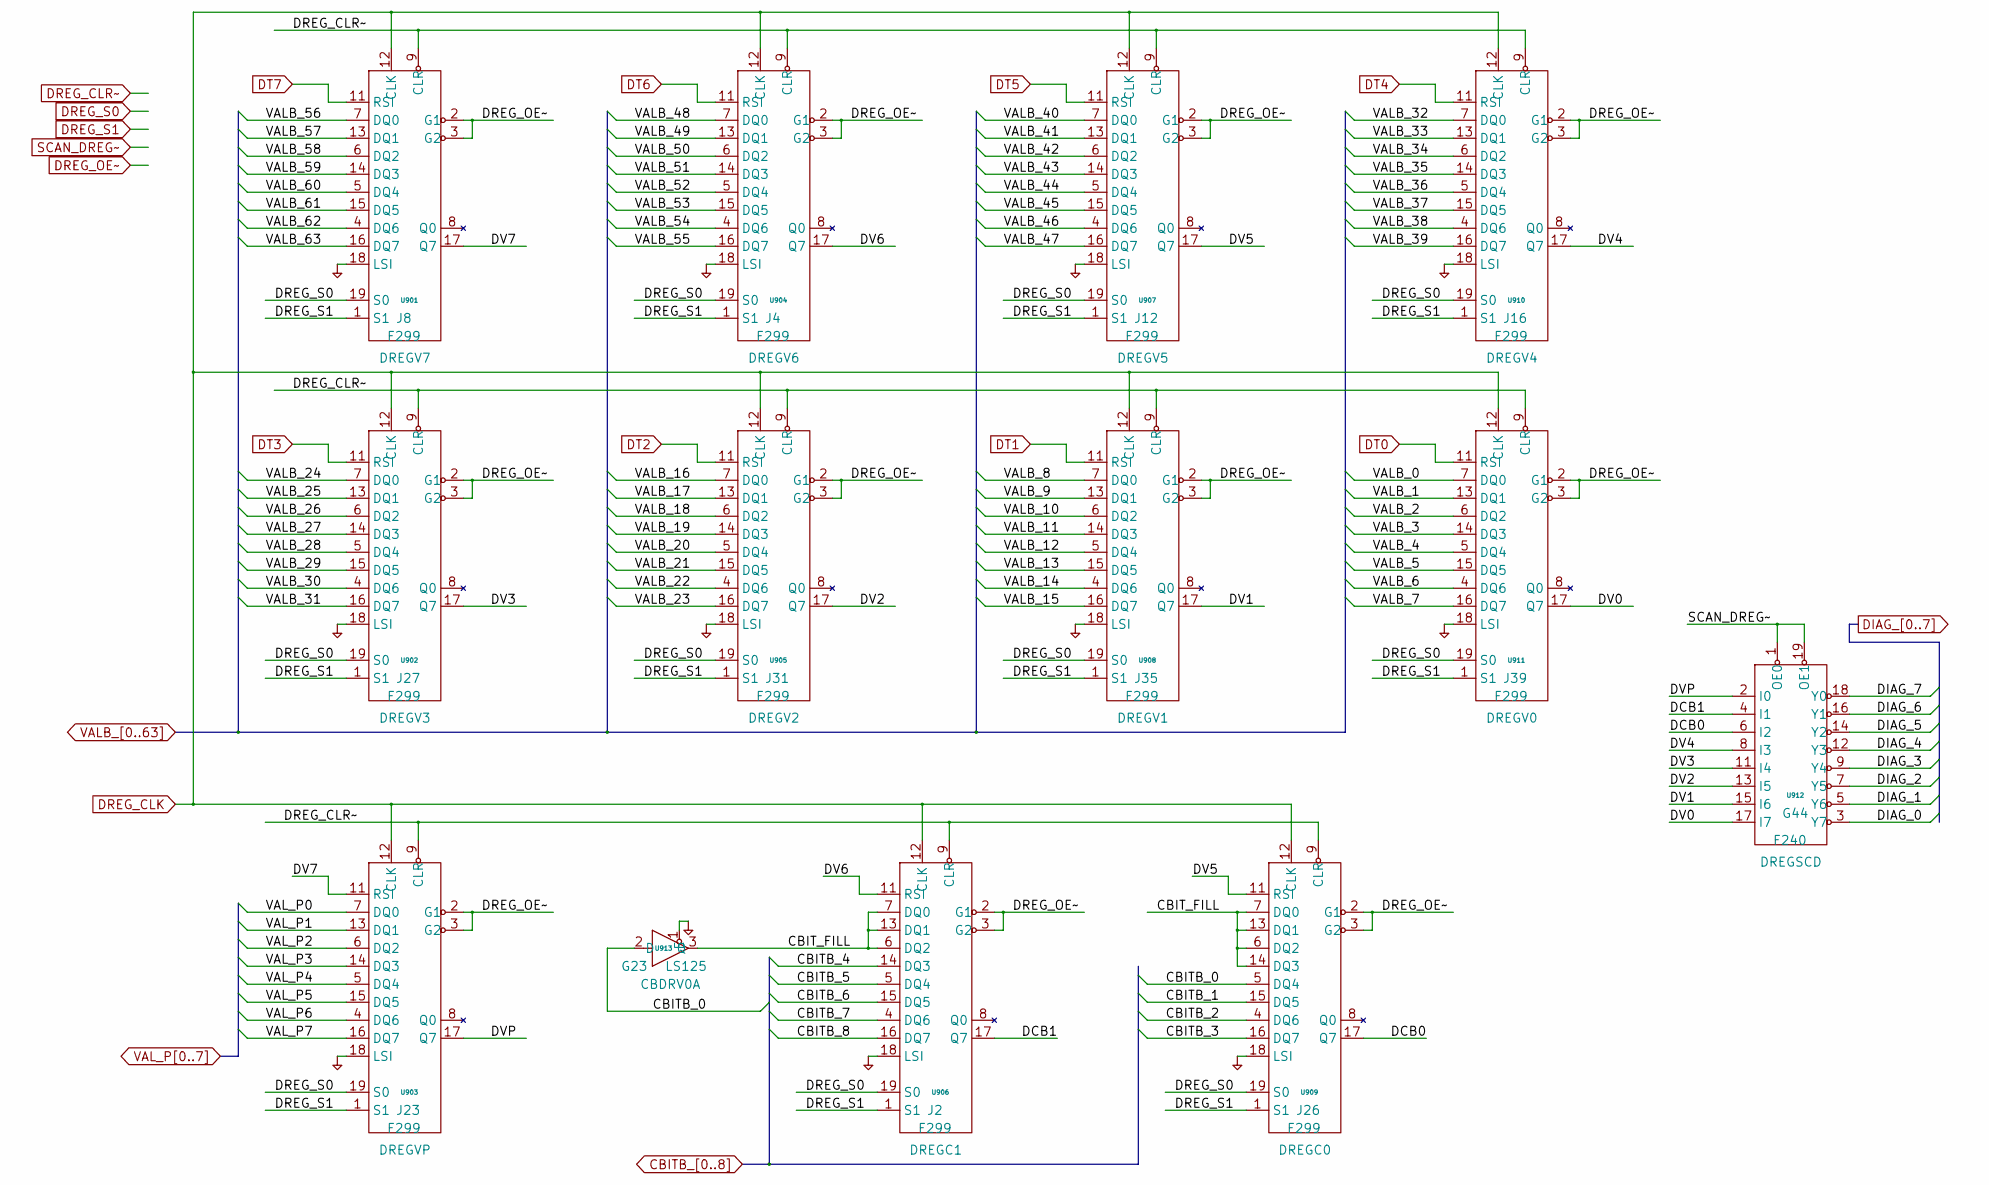
[picture p422: schematic pg_08.kicad_sch]

Parts:
U901, U902, U903, U904, U905, U906, U907, U908, U909, U910, U911: F299
U912: F240
U913: LS125

Connections:
CBITB_0: U909.5 (DQ4), U913.2 (D)
CBITB_1: U909.15 (DQ5)
CBITB_2: U909.4 (DQ6)
CBITB_3: U909.16 (DQ7)
CBITB_4: U906.14 (DQ3)
CBITB_5: U906.5 (DQ4)
CBITB_6: U906.15 (DQ5)
CBITB_7: U906.4 (DQ6)
CBITB_8: U906.16 (DQ7)
CBIT_FILL: U906.6 (DQ2), U906.7 (DQ0), U906.13 (DQ1), U909.6 (DQ2), U909.7 (DQ0), U909.13 (DQ1), U909.14 (DQ3), U913.3 (Q)
DCB0: U909.17 (Q7), U912.6 (I2)
DCB1: U906.17 (Q7), U912.4 (I1)
DIAG_0: U912.3 (Y7)
DIAG_1: U912.5 (Y6)
DIAG_2: U912.7 (Y5)
DIAG_3: U912.9 (Y4)
DIAG_4: U912.12 (Y3)
DIAG_5: U912.14 (Y2)
DIAG_6: U912.16 (Y1)
DIAG_7: U912.18 (Y0)
DREG_CLK: U901.12 (CLK), U902.12 (CLK), U903.12 (CLK), U904.12 (CLK), U905.12 (CLK), U906.12 (CLK), U907.12 (CLK), U908.12 (CLK), U909.12 (CLK), U910.12 (CLK), U911.12 (CLK)
DREG_CLR~: U901.9 (CLR), U902.9 (CLR), U903.9 (CLR), U904.9 (CLR), U905.9 (CLR), U906.9 (CLR), U907.9 (CLR), U908.9 (CLR), U909.9 (CLR), U910.9 (CLR), U911.9 (CLR)
DREG_OE~: U901.2 (G1), U901.3 (G2), U902.2 (G1), U902.3 (G2), U903.2 (G1), U903.3 (G2), U904.2 (G1), U904.3 (G2), U905.2 (G1), U905.3 (G2), U906.2 (G1), U906.3 (G2), U907.2 (G1), U907.3 (G2), U908.2 (G1), U908.3 (G2), U909.2 (G1), U909.3 (G2), U910.2 (G1), U910.3 (G2), U911.2 (G1), U911.3 (G2)
DREG_S0: U901.19 (S0), U902.19 (S0), U903.19 (S0), U904.19 (S0), U905.19 (S0), U906.19 (S0), U907.19 (S0), U908.19 (S0), U909.19 (S0), U910.19 (S0), U911.19 (S0)
DREG_S1: U901.1 (S1), U902.1 (S1), U903.1 (S1), U904.1 (S1), U905.1 (S1), U906.1 (S1), U907.1 (S1), U908.1 (S1), U909.1 (S1), U910.1 (S1), U911.1 (S1)
DT0: U911.11 (RSI)
DT1: U908.11 (RSI)
DT2: U905.11 (RSI)
DT3: U902.11 (RSI)
DT4: U910.11 (RSI)
DT5: U907.11 (RSI)
DT6: U904.11 (RSI)
DT7: U901.11 (RSI)
DV0: U911.17 (Q7), U912.17 (I7)
DV1: U908.17 (Q7), U912.15 (I6)
DV2: U905.17 (Q7), U912.13 (I5)
DV3: U902.17 (Q7), U912.11 (I4)
DV4: U910.17 (Q7), U912.8 (I3)
DV5: U907.17 (Q7), U909.11 (RSI)
DV6: U904.17 (Q7), U906.11 (RSI)
DV7: U901.17 (Q7), U903.11 (RSI)
DVP: U903.17 (Q7), U912.2 (I0)
PD: U901.18 (LSI), U902.18 (LSI), U903.18 (LSI), U904.18 (LSI), U905.18 (LSI), U906.18 (LSI), U907.18 (LSI), U908.18 (LSI), U909.18 (LSI), U910.18 (LSI), U911.18 (LSI), U913.1 (E)
SCAN_DREG~: U912.1 (OE0), U912.19 (OE1)
VALB_0: U911.7 (DQ0)
VALB_1: U911.13 (DQ1)
VALB_2: U911.6 (DQ2)
VALB_3: U911.14 (DQ3)
VALB_4: U911.5 (DQ4)
VALB_5: U911.15 (DQ5)
VALB_6: U911.4 (DQ6)
VALB_7: U911.16 (DQ7)
VALB_8: U908.7 (DQ0)
VALB_9: U908.13 (DQ1)
VALB_10: U908.6 (DQ2)
VALB_11: U908.14 (DQ3)
VALB_12: U908.5 (DQ4)
VALB_13: U908.15 (DQ5)
VALB_14: U908.4 (DQ6)
VALB_15: U908.16 (DQ7)
VALB_16: U905.7 (DQ0)
VALB_17: U905.13 (DQ1)
VALB_18: U905.6 (DQ2)
VALB_19: U905.14 (DQ3)
VALB_20: U905.5 (DQ4)
VALB_21: U905.15 (DQ5)
VALB_22: U905.4 (DQ6)
VALB_23: U905.16 (DQ7)
VALB_24: U902.7 (DQ0)
VALB_25: U902.13 (DQ1)
VALB_26: U902.6 (DQ2)
VALB_27: U902.14 (DQ3)
VALB_28: U902.5 (DQ4)
VALB_29: U902.15 (DQ5)
VALB_30: U902.4 (DQ6)
VALB_31: U902.16 (DQ7)
VALB_32: U910.7 (DQ0)
VALB_33: U910.13 (DQ1)
VALB_34: U910.6 (DQ2)
VALB_35: U910.14 (DQ3)
VALB_36: U910.5 (DQ4)
VALB_37: U910.15 (DQ5)
VALB_38: U910.4 (DQ6)
VALB_39: U910.16 (DQ7)
VALB_40: U907.7 (DQ0)
VALB_41: U907.13 (DQ1)
VALB_42: U907.6 (DQ2)
VALB_43: U907.14 (DQ3)
VALB_44: U907.5 (DQ4)
VALB_45: U907.15 (DQ5)
VALB_46: U907.4 (DQ6)
VALB_47: U907.16 (DQ7)
VALB_48: U904.7 (DQ0)
VALB_49: U904.13 (DQ1)
VALB_50: U904.6 (DQ2)
VALB_51: U904.14 (DQ3)
VALB_52: U904.5 (DQ4)
VALB_53: U904.15 (DQ5)
VALB_54: U904.4 (DQ6)
VALB_55: U904.16 (DQ7)
VALB_56: U901.7 (DQ0)
VALB_57: U901.13 (DQ1)
VALB_58: U901.6 (DQ2)
VALB_59: U901.14 (DQ3)
VALB_60: U901.5 (DQ4)
VALB_61: U901.15 (DQ5)
VALB_62: U901.4 (DQ6)
VALB_63: U901.16 (DQ7)
VAL_P0: U903.7 (DQ0)
VAL_P1: U903.13 (DQ1)
VAL_P2: U903.6 (DQ2)
VAL_P3: U903.14 (DQ3)
VAL_P4: U903.5 (DQ4)
VAL_P5: U903.15 (DQ5)
VAL_P6: U903.4 (DQ6)
VAL_P7: U903.16 (DQ7)
